lycronisxd/a-shift/basic design/rev1-centering-mechanism.excalidraw.md

---

excalidraw-plugin: parsed
tags: [excalidraw]

---
==⚠  Switch to EXCALIDRAW VIEW in the MORE OPTIONS menu of this document. ⚠== You can decompress Drawing data with the command palette: 'Decompress current Excalidraw file'. For more info check in plugin settings under 'Saving'

# Excalidraw Data

## Text Elements
## Embedded Files
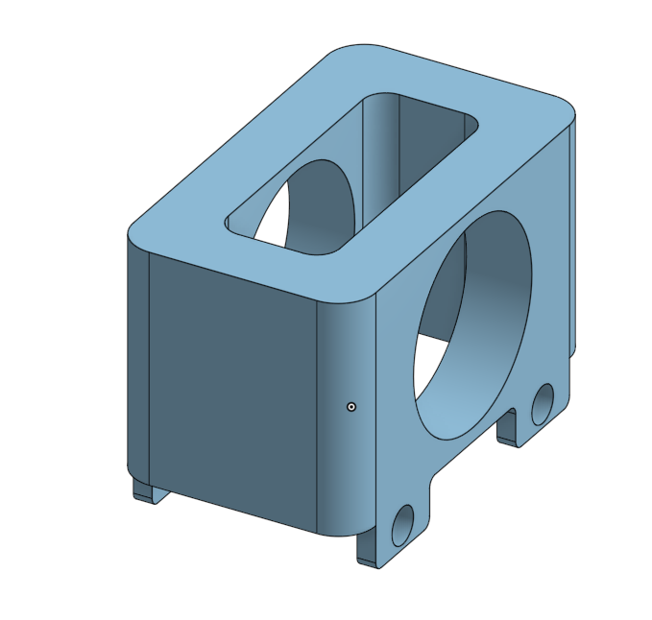
[picture p7: basic design/images/Pasted Image 20260602135400_534.png]
f8c7245b9aaf94fa687d6ef50f577c9f9da9b14b: 

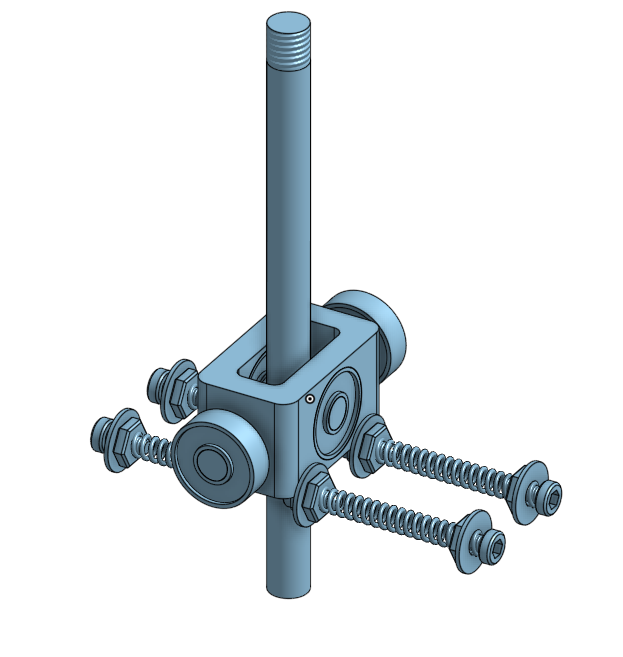
[picture p8: basic design/images/Pasted Image 20260602142242_120.png]
b308996baf1a3101664534b31633d5aba34f77ea: 

%%
## Drawing
```compressed-json
N4KAkARALgngDgUwgLgAQQQDwMYEMA2AlgCYBOuA7hADTgQBuCpAzoQPYB2KqATLZMzYBXUtiRoIACyhQ4zZAHoFAc0JRJQgEYA6bGwC2CgF7N6hbEcK4OCtptbErHALRY8RMpWdx8Q1TdIEfARcZgRmBShcZR5tHgBmbQAOGjoghH0EDihmbgBtcDBQMBKIEm4IAE0ANgA1AFE2TCMAcVSSyFhECsDsKI5lYPbSzG5neJ5q7QAWHh4ABgBOaqTF

6er56YB2flKYMYBGeaSD7S2eaemAVgPF+fj4k4PdyAoSdW4rpLjFra21niLeJXHgHA5JF5SBCEZTSbhgq5XbTVFHVf5JK5LNbVSHWQbiVDzSHMKCkNgAawQAGE2Pg2KQKgBiA4IFks4aQTS4bDk5RkoQcYg0ukMiSk6zMOC4QLZDkQABmhHw+AAyrAhhJBB45SSyZSAOrvSTcPiFASkikINUwDXoLXlSH82EccK5NDPM0QNhS7Bqfbu+ZEz184Rw

ACSxDdqDyAF1IfLyJkI9wOEJlZDCIKsBVcIs5fzBS7mFHih1oPACfEzQBfYkIBDEeHXbZbabxRaLSGMFjsLhoCamsvd1icABynDE8MRSXmNxnO09hGYABF0lAG9x5QQwpDNMJBfVgplslHU+nPUI4MRcOvG+6tjPpvckv9qosrpCiBxySm0/hP2wPIbmgW74GEhS1oUpaQOUEhCC0mD6pgMAwAAWnKXQEhAvT9PicqjGg4zVIkSwHCCQIrNUgKbJ

C/qoM4GynM2NyIiC8RLJCbzEB8/aJIsByXFc7EXNMtzLJCkjQrCUBTkib6BsCqyLBcVxtriAy2kGZa6pawr0kybKskgu7cryBZCrS+liuQHCStKWQyfGSqquqWH2o2xIWgaRomp5epWq5FTufmwjOq68KQt63J+vCgaQiGl4RlGsbxomCDJmgZ7/ouWYEeguAAIIhQKxBFiWZqdBW3BVh0kHafWd68LOSQPPMWyzl2TAjn2qDTO+nU9mOE4EoCGx

JC+QkZiua7AagoE7p6e4lYeGQOaef6Qpe163vCD6bPtPCrAkn6Zj+mUbZ6dJAY180IBBuzQWUjUQLZYYUC0UAABKVBhVUSDheJDJCeXjPEpwHA+AkgoGD7nLRYyItMyRrACiJHIxnE+e66xxFcixJDwraAgcCQExJUlwmgqnIhcCwE9D8R9ZM6l4WgWmlDplJ6aK6DMkZ7ImTyCWCtzFTirZUoyo5nqKsq1q2hAwV+ZahrccaaCDhzXkBTabm0g6

npOpIZURZ6UW+rAsXs5ACXhpG+RxjLaUZagWUZrlOYAELFYW4VoNBlXdP2NZ1rNAmExDEOAgN3XcNMZOesOvbjhwk5oMpSSXMC8QLmWS6rsEO0gduCC7vuxArceOS/ueZZbTeYd7U+T6MX1J3fjX2VlldlI3SX91QYuz2LAAssQI8AIoAPLLsuv1B+gAMacZnogzw1NbBsbWBpsdMHDinp0c4Wzsdo+PAgkbbAm2muvFjqDgskGz48c8ftdvB9lp

JMKU71+/Ilcc4dwEjsQJtcFmmllZc0sjzCAfNDJyi5ELcyotrISklg5OUssXK6yCvrDynpOYIFVjxXgUCdYKyVobUKxs/YP0ij6GKAZrYQFtklB2qVcBJkam7HKxBswSFwFSH2pU6EB3LAvGqJQ6ocwavCcEm9N73A9EOLqvYmwQkTmooaqcCRiWqF8R4H5FzTULrNW6ZdlpHjWp3TaV4G6NQho+e4dxlIdnbmdV2F1u6AV7pufu0iHpDwqNMckz

RiAAFVKgAGl55YSCEQOQK8yxrxRMjR4oIUS3DBpossR8qJbGRPMOYTd45sUxmrbghTiIokZoiC+WxwS5NKN/aS8IDHaHDrMfeb40RtmaZAQGBIWFENQbzQyAtFqmWFhZEUYsbJ2Sllg5y8s9banISQ9WZDCHa1WXg9Z1C/C0OLKbMs5smEPzisGfkdtkqOzLAmLh6UeHeNKJmfheUIC4Dno6cuJt/YVQkSNEOhC5FoBnMUjsGJc6lCTpwDRMdk7D

XhGDIEXwOzxCmgXBARc5ol0sQeaxJ5bEXnsbipx+12wCWuJ2S6p0SU+Ouv4sCd1AmDzzs9KA8xomoRHlSA4FAtgACllxXCFSqIVcBsDyjgJ7AA+nEioCTCBJPwmMBISJ2yTBztUZsZEDHw0IlRJGkwSZtj+BRdeFTSGIm0PEAxBT0aKXjuTH+Ml3QdK6Zk3prZHgQOGeQsZcCJnJNKEgsy5cg3i0WZgpyctAqanwTqbWmzfI7P8nsxNByyxG3+fQ

s2jDLbMPijc9haAUpOyeS7XhecPaCPqCIvN4jMImhBfVWa2wrjVDBG1FRsLtE9XXrfBgA6U5pwfmsRprZ+J9pgqYnF5j8WLXLpXGx5b7mlHruSpuLiJj3GHV+TxNbSg90XSyiSoQAAqWAoAABl6XFxZQPEoj1YLoAKnMXA9RFjMHmJgNgcrb3LgAEqoQQAABTlUKpIKpFUSGVaq4G6r5inGKX8Q6yx/jtWmIa+iVEkSgkAS1OmVEHjWq2cRM+XaM

SzC2IAsSrq2keqRF6npmH+n+u4CM7WQb4FGUQdMlBMD5noPsrKONODKFJo2ffYdRDM12mk4csKJz3QMOikWy5LC2H23XZw7hDK3l1vymGRtYjAUto1m22RYdfiEweHR2lqjBo9QeJirRLmx16ImG2USkxjF53nbiixy6rGrWJXp0l21G7OPbPa/Gn8T0Pq8bXE9viz0LS/lem996O6PvAmyl9wSJD4HfCqAAYvUFUl6CpXAAFakHqFPNguB4jAbY

CPfAcH0AIbCGqwi+9TjjQ7MRL41xAw4cPmMKipx2zTqHTcdY7myxcVIR0pIBiEt7pOJiGFkBWm/33ix2Y3SUTsb9Z6IZXHA3CYkHxyZZZw0zKjQsjB4mZYrITYp7NWt/Kpo1uQhTislM5poXm2dXpC10SONp0tunowbsgI8gz51UswWM18oVZnVOoGbX9Xg1mBBgt6nMAmjxViIvhf2S4lOOBeZNKTl8CQIf5xmn3c9oXCXherpFuuZKYuUqBKsY

EHjDOQFPezzLLTsuYDvcl26z6ijFfQPgIVQqrjgaSJIGACA4Dlf3nKqAo5mDRIABrLjzJCSzPXlQqr60hgbJNcZOK+DvQMeNcMMQWDMWYykDHFLxhTz0q2tm2vtV2iO8xRuZwGVCN17Tju0zY30i7ZYrtsxu3Mu7IaBPIMjbd9A0a3vSweZ93BWaDbaRTbJwHX3gc/cgLmuhEPzmaZhyW0MZaEf6eeWLsoGPcCxN+SVJtFn8c8EJ4rYnYJJjviEv

xWnJoZy0/pxrMGaINhtxMdi4LS7HsrqJTz7vUWHG7Vi2sFDCdu7JePeL9LkvS6ekkDLuXeW8VPsK0rjlFQrjKFN+V7ARYT2aYSQaYfQeIcrNMXAMMeIKAWkbrDAW3RDVeMYTeM+AcMGPdASOjCHfJR+ISe1caV+YEKicjT4TVB1SPaPF1J/Cmd1B+T1E7b1c7WPdPQkTPKycZfmUNTkQTfPLPQvV7MTEvUobBIHKhKvP7GvdNS0cQkHUoJvHHFvK

HK2DvRKeHCtB5Z2F5NHfvD5HMW9bHcqDoQOYFWqUORxC+dYe4N8RffsGiDzbqVfVALtSFXtJzN5ILDLR/ffMLKuO5OxaLRxHddsUSDbZbJLN/W/CACXZlKXfbF/XLTxBXT/V9Z6G0W9TQT6RYIVNreoJIGAZQKAEeIVMMK4eweIBA3rHgiAEGdsM4Gwm4feFqGlAST3btRYGYcaQ6beFDYBMgqmCgiPRpKPZ1WPA7ego7TpJg5PX1Vg5ea7GQ6BA

Q4Nbg3PCNEqF7UTJZCTOQhvRWavSpAHJYihNZSvBQsHZvdTC2aHK5MsHTAIytFHFLLuIzfQwREeIw7gPHBeCfcw0FMOCaB1NECHOFVzVPftTzZFd0Vw9YdYK1bfNnOInwsNA/bnR4vnIIs/QXK+cEUXVHV4u/JlfLFEhI5ga9WXJI5ExXNIioTQckFoEeXAegUgHgAqAqOAQgLYOAeUeUCgS9fAHwKopA+3FAwiJGR4USPqCaKPYiQ6dohIO1WUp

o0bCOAYlwoYx1UYsbcYughPaYpPM7FPeY1mdgk43jHPQWDYkWAvaAIQnYj7eNcvb7c480KQo47ZSQ2QuvCQi4o5cHa4i5dva5TvDQxHBUbQvvd5ARfKUcL4gFEwoFVtf49tSwi4J4S4UEgdaqCGFfaE3gA4e1YpHOOjLFJEkkglCuQ/DEzdfnYI8/QSY4fEl4gCYk9/eIqQRI+XAJMAGRWkiQCeKkCJZgIwT6UgKAVCVCegVSYDAqUgTATAFoSQc

DYUxJUUlJaqJGOje1MiTETOe4PbCAfJOYO1aGWcHcsEfqYPe+MPSgkY6g3U+PZjA007H1DjS7BYjPc020+7Gop7ITFYovYQ5ZJ0qTfYohf7T037b050+vV07CS4pQwMtvO40oB4jhJ43vAk92d4/KKeeM3HMfX4yfMIWaBYW4TEPGG4Ow3gX4PM3RE0WcISVSUSMssxB/Ss1dCLY/TE0/e8Bs1SO4Zs6I2Iisp/Lst/FI3soJb/CQOrT6ZgOVZwF

UEeSQckHgEeAqcYeULYT6dEH6K3fHRAtcmovKc4dAlYKUqibtSYYdY82bX4PzVsEEDEALUoEPcgu1O8p1HUxjQ7Rgw0t8iEwZT8s0r05Yzg1YhBK057W0oCh00vUCs4ghcK4haQ1KvY+CxQqMZQjTW42HUMmspHSM7CvhGMr5Fc4fX2HHH4swz/InMOJmHJbOGijDei8dBYR4E+NiFnLwjiznKs9EjC3i7dBs3VQs4S15IkvxMSrLcknLbsj/aS9

lN5Z6OjOVWoYDT2CgKeaYAqTQYDZwKkcDGAcrOVfQQo1cu3Uy2KQpdiCGTEASd3E4Oy6bE8i+ZqVSTeDOdU284YnymPPyyYgK18lgzjL81Ki0tYmKgCyK+K2NR0yTZK5Nd00hOTXZH0+QxvRCnK5C/KtQ25Ya0Qkqlssqz5XACeAi2q5M+qqfMOM7TYMidxRw9RDWIPZzJw/M8a98YbNihdfq3wrnfwomyALdAXJ8UIzeL4Sa3Q0S9s0kzs+aykx

agrZaorWS9ASoU3MMYDeoIwSoXAeYBAIVTAT2fQOVRYSofAeUeocrK65Ajc7Gb4RmCaUIiGN8Q8vA74Ag1sEmdqNxCHDywYry/67UwG2gp8hgxPUG408GsK6CiK2BX89Y2KwC+0hGxKpG/ZeCiC9KhO047OlKv0lTXGgtPK1QkM9QoqiMqtHQwkvQ8q3AYDKmoiuqtWmzRxFYOYC4eLVqzedqvRGcL4NGe4Pm3fDnQWwa4W3nWsrE/inEjEW4GW+

uuWkLOaik1/ZInsvs5XCACJRYDgU3RCLQBApePCB3Cdb4UETYZSe4LEPqSbPJVAujOIE7M7OYQBZSdU+o2YYiAmFSEEOjYdCYuOJ3LtFGIBNsGHNykK007jfyKG6KqZPPTYuK9O97TOzKout0lWPOnBykLB4qEu05UoVvfGyuwmme4q2uqMgfCJFuxM63KRduhqxxREJYC4FDQ8sE2KLMqEhi90AmTbW4NEMe7wzi6svvMW+swXOjdYCHQ9PvVe7

emS1aioCJJIS9CeGVckOrU+hAPoK7C+8ETozeW4WYAcdYK/PYQ4EmEidsYXbtTOHODwu+D0rtJGXVQ6WYDbTEFDCHEB/sQBABPzfdREOij8uBjgpOy05B602ZOG9BkQpHMvMCnOw4tG2vWC307G/0q4sum4iu+4uHau5HLC0m2tXCr5WoBhssJhki6ffGO4diG4CIyAHhwR7h0dfMwmIESYeOXqnfcRgario/aI6R7EiW/GSixLcXG/KamI+/ak1

I3e6VT2TQSQAqZcCeBAWoKAeIfQT6W9AAR2YFvWgzgH0cMYWIvuw20BQzcwEgxU3ljyPj+CRjJw21hiomam/s6N/oyQAcJhBCBtAdiHAb6kgbBndzjvgd0h/Nicez4NQbTu2IztENSeRpkw9PRozUxv2OypIcgDIaKbQpKZFprueOiOjPJoMsOWquMLqfx2YZkVYbjkzivmWFcZHRc2qkZgHsYs2EEiBEPNZ3YuRIkaGqoYgAmfnubgef3jaZiPm

dlqWdmulyVs3uWfbv7PQAiX0B4HqH1HWflFNxHgOuiWiQiU9nwGUHlCgFGEMoXmwgMdwiBjFN4FmCfgmEZhJlWD3PaM2GSFBHtUuBnCOBF2vI9OBDOGJh7raiBCcUfpaT1OxkSFWHjiT0aS7ThkicgW/JWOTphv4MSbRYwYxaSsLpRtwZxaybSewYQryaQoKaDNQptnJelbKerQWZpZzHQiqtERqtbuqgabIt2wuD9pouUj4c5oEd6nOF1VbA4kR

PFfVc5DROnp4tnr4ofh3QlvkYUZVZXrVflovU1apJJJpN3uOfoCgHJGcEqHAypCgGUH0AOCnkIGmGAzlSpGiU5PtvXJGHhH4m0C+AWEaQjbCP5amyNX/hnG7VEi1QWFEajdIWqXtWImuGYojnGlBefNYyNLmNheiYMmhridTtLYlmAt2PxfSdRq2VxZgvraIeOVLrORUOLQoa700OJpodKsqcbtwFqdKGtz+NptIsahssLPfBndZt4BWAFfBWOFG

JLLEYFtRL8LXS3dFrrMmcpQ2yOGXtbJmtPfEvPZVtZR1d3vJHK31FHAngnnJGiSfaEFqB4CnnJFN0ICMEwGAy4CdawjPvdcdoYO+HakxAQ9cRnU9tQMuDtQfAuDfEAVmAuHVMfg2yWBnBj3fnalmbjyYz/imAMSAWLNARUmI4LciqLfI9htgXhvLZScrYrwbdztrZOMIeH2IbUxbZQoKqropa7brpwsbs0GE9MJHZTI7vkSziMUJhop9cU4YJARw

OZsCyGfU/Xc0+4p4507nt3ecSlPjhoOvyiIWeUYno1Y3ovflqvY1ogCMA4Dqz/bgFqH0CubdZusImZzPiZlWAMSMQxDy/yXtTOHwxWHfBk7Bm/qmEBEBFy6ILmGKWTf21TYnViAaV3kaImEPLYLhcTtI6QaRZQZtNRao4Sorazua+re8ja4yto4bcJe6/Y/Ls4+KcKoG5JupYH2wDG6TODkm7ZYDG2F6enZov1UW/CJPj+AmpXf5olZGckf4+3dG

v2mbnajmCM8uhPakp3ru9gFIFQipFQjDBaCMCiXwGwFN1vTlXJAKnoHK2EQC56FdaMY9b9rtXXn6XGweFeqNUZnuafGS7RH6dHtQ62RB9h9+CjwR4WFS4joK9uHR8Acx/D2x4q8hoRbI6J/ia2LJ/Rca8p5dJa4yYY7raxeU1Y6JchxZ60wJu4/DMG9oaqdwAZ7+XM0YeZdHccQWGOC6uopZqp14FLIH7p3zKZjWBzjUll/Ho7KWiFq0525ld07l

cZrDeO8iKPTO+1730u4WskpUZWpgmehHmObYBJGwGA1UC2GiXqFvRUs9i2FvU9lQhqad/+hd5uY9ffAAXOEDHGjBDDZKsj4rhM+FHgfqFkUMb4JVkHQfg4x14+MQmL7jsbWMUekdamMajphDp7gTMPLrjxI7Z4s+YaZFiT0o4xoGuCoTFlW2xaZN2u9PFjgGR67kM2e/XTtpzx7YD4ai5kUfB30kRd9gOZEQEATDag0U/gLCMEs4QEh+smkETNbu

WVM6T1Rm1dWVvt1V5tRtg2wTXoyhM5r1d+ytffktV15qNNQy4egDyniAxArgqEfUJUCuC1Bj4HACgBEniANtrcLra5ufTd5ohNUJ8KBrfWwy+96IM+b4IGGpQx5oUv1K+r8H+C+4L4YIR8gn13LIhUQ6ITEB2HWBx1EghZOjK3FuAYgZ0eXUZJn0J5EDieCTOrkkxAqF84Kxfejmmjp7ZMsajbLrvmmZ6FNWeZLdnqwL44VM3ijdeULz3qYC86aj

UbVOvC7RkQp2pBEfs4Reo4dhB0/YZgoMV7acl+e3ClM3BhxURY8ijJXtNUWG6CtWl7FZndxgDLh6gl6eoBEiEAUAGI74aYK0HoAHB8AnsUcIYTf6LwP+HgkLhDBB6UUBw6IReoG2+B9RskobNqJ/W/p8RqUQkJHqJBGx4cH4tqeSPcHRTKRmwSrNgpkJziuFJB0zfIfgK4LFDeCpQ3PmQOSYUCmuRfanmlVp750OuFfBga0NbZ9dKGKwxvrsIbrk

1lAAwzvkMIk7wgFgNwZYI8CVYdMH4hZGBjy1nbjoBB68F8C+EGZyCdBm3eftt3DLKD1hjNQMFsM0FpY2yyoxWldws63cjB6AcDGGHKxJBlAtQUgEYFgD6gJ4QgaYLUG5C3pwMBUR1p6FcFBdPuiI5SHEGIjCR+ILlIHgjCEjIgWmjNV3IzGHQwCBIMPQPIgLjYZIER6A2mMcCwGMw/cGQzpNiJyF4iwQBQnjEUP4zFsUWpA4vJUPpGpVIKjHAhnQ

M66V8mepDDjrXy45hke83bXQr20ETGgB23AplrwL5HT4yItwRpJhjF4kxh04gnpihl8wojFRq7eQRp1VFH5F+GovdpsPlJ0pTuqrfUTvzJJGj9BqtQwUfwqDLhLArJFrE4NHCYBnAwGLAAVGtrHN6g0wd7q72+G6pEgcwNsLOFy7bB8YnuE+J0TYhohzgkcaPml2+AZcX42XGGFHgRGiQiugCaiCAgzHgI82lYXMdkLnG5C8YhYgkVFVLE1cS25Q

stuSLEINiTitYsvlQIZH5MmRvXOvh2Mwpdj66PY/KIQB5FDjxOxOdeFGL+CSixRD4WPDOLnYUQRsk7BYRtwgBz8p6C/dUcvxUEbDtR24k7pvz3HaCDxhovflvQMGqMzxYoIwDwFHAtBsAygS9EKiECLBagmAKeIsH0BGBwM5WUgG93eHGVrq/WBgmkmD4gic44ICGMjyPIIwQO8jV8LRghhrB1S6HWpFhwaRNIERUxAjkFRNK2gsROE3EXkIImVc

YmhA4kTnzQbkSqxVEmsXgwOJ4sGhBLHGlXxJbtD22nQtkWwO7ED49G/Y9voOLbqsthh8iQEIzCjzzCOacnESYtyBBLB/Gi4uXmu1kkbsFJgRHdpqNEiqTthR7YzvsMPG6TtWp4p6BUDlTRJdmmACgHACMD0BhycgEeBEmckIBUI5WLHO5OqJeSyIL4GYJHzmAOZm4nuPGEjE/qqRCyGIYpKHxWw3lNSVBMYolJBrMFY6mE6qNhJxFwisp+8QidV2

z4UcyJefcgZRMql0ca2NA+ocx0bGMiWxNfYMswNZGL92RPQ9HM3x/BtSh2PAzqRYU3JgwxsV5QaYPyOiLd3aL1EUWp3l5LCpWKwjcQdy3HLTdxx7fcRd3Wl6C9JJ4gydtIkDygCoMAegDwEkD1A6sgwCgAVBaC1AjAygSoNtQnh9ivRRle6cYxYozA/gqKJSGiCh4wd6IeMRIOsBnRgg6kLRdUpRnfArBVIwLccdy0CZR0XyEMojlDP7Awz8x8Mo

sQgxLEPYShBU0nmSOKmYyah2M0vrQKTn0CGJhMtoW2JJn19OxQ3MmjmC6w0zGWIncfHwI1hHYZOq3SErHHTgnwOZ//diJcA0HSTeZK4+SWqLmkq8VJUeNSRvyUbb8JZOkqWZtNllvoIAl6EePb0QhUhRwpAaoKbiMCjh9A5We9LgC+DUzjZzrU2W70xCOyyIwIOIfI2KQfTfgnSdeG+EzhjjrgseGAetk2zhE94u2MGdHSDnvk08oVdKbDLwn4ic

pBPYicjNq4iY0ZFEygVT2oGpzcZ5fUHE2zY5ZzmRzE0pk1PYkD43J9LQdqXPG5WZhxZFcaNC02BdNeW6cTOBzOIjnAlsKHWQUuINFyTFBFLQWar2Fm6i9hMk5/OZ2PGWctpE8mJKQGUD5EWg0wCJFPFqCjg6sdWDgNOUvTZF9QAHX0fGJNRLtLgH9DNmfMKR3ASYPzMpJHF+rAz7yoM+Pv5TfmzEP5pQTEWHNwkFiEZ/8ggUSNknECyhIChOTR3T

mQK6hdIkqcXSbEtCEFTE9scgu6Fc9m+/nDBQOLLnEVcFjULtDm0MTcsxRt9DmQQpfDdpJRYrSacuJVGdy1xiktYZuKWksLFm4sjsuwqPHSyuF4856PgGAyVBLg5WeUAgB4A3hlwhAPSmwGfyjgoAbQO6SKXkU+Mfu7UC1McHOBkY7ZzgPGJ0RRBD1/+VEIENAKBkh0tSD5V+YHJMXBUvkX8ixZlPwnWKM+hbRFrHJRlOLKxLivGdRLKnyZPFuTZo

blWznEyOhLAxqYEvYHN82A3E+mQCTYaGIfe/wKdjTmmH5lIpCIJityzSUz8FadC5YeuKUkLTmFO4jSWLK0nDySlG0o4VZzu4TxGk0wZgF2miSEACol6UgLek+jEBagcqSoFsBVApBulJlB6VSljb9N8YSErVGfO9qBi+oKwChXNzD6eVw8iygxV/FR5JSZihHUxbAzSmbK4Z2yyOfCz2V5T7FJIwqaAsTmnLSptI/BgXQgX0Tm2jEpgfctJkN8UF

w3cmpcxLnfFh2OC3iWHDGlCi0UU7B8BzPfCthfxjSHmVNIhX8yoVuSoWfkrhWDyilCtZFaPNRXcLOUlQWoAgBaAwAVQW4XzCPGXDzA3RVwZwKOB4ByLaVXaGYE0h952Yfqoyz6UUjlFtgu0GwNZTAL+p8rfKhi4GsYpFVrLzFWQn+VYulX49bFgCg5cArQRKqTlMC/OjRLTkqqvFBM4lq2LuX1SHlZMw1YXMETHM3lNNFht1LQB/ABl4woSdmXTi

AIJeIIXpBsFFZ9V25mS+hdK0YW9ydRvqjked2KUSUylJowyXaEwCVBKgSlIVBQEwA8AYAxAcDEIDv6VAJ4LQT6Cau3nxIeltKiGHEEEnh594vfSUcAO/7tggQGKHJD4N0ULKQZlagVZHSFWBUwaIc1AN/PDlSrEZ+y/KYcs7XOLEa1Y3tecoxquKtV8C4dUTLbasIO2jyqls8sboMhTVCZDqXOq6n8i0AKwAmMkp+Uj9uAIrEad0gPYTSwVkrTdp

6vml5K+5Is+FatLYVXqx5h/OWegHqDyhysKoX9YQAngcAtmbAKkLgGOb6BpgE8Jkp9DTXGNem9zO4NL27SbxiuZ8mHjvAjaX5J0yG3lahvDroaE+4M1ZalKwkNr8Nf83ZVVyI3yq45FY6juRsuXlSU57i9VRRquXeKbliC/xRzyeXNTm+uQTjYRTpk8aGZMJdiAHSXoib040cf5XOwhg2EHg+811Rkumlbdsl3c8WlqMU0FKL1AatTcGoqUVBqg8

oJILUCpDzA6svnCeMQDEWLAWg+KqkFsEqAhLuN8GYDXZri5AIOwFFBDrhzzXf90Y/wZLkYm7Q+bvKYddfqgMC01qUpOYsLZYojmEa5V/5UiUcvi2YNEtrXHGR4po2wLrleNUlmOv1X5ym+jdckVwPanhL3lqZJsBsC+Arcp2NW1maPznY+DmmtqtuW6pmldyT8PcrraevUl+rEVl6jhdeuOGmjFY/ESQPgEcGSBNApuLYAYHwCjh9QzAaYBcNkXU

rPJdm+4EkP+AqQSkh0aDSFLC5UVxls4P/oeTLV6KAal2/LkYpWW1qQt0M+7Vsoi351EGba4jR2sEJFTu1dE1Vd9tS2JbGePi+jbcsY3oUuhrGvLY3SECzqLV86vjX/EvxogWoU7HZbXKRRzs5gywMEPvF3Xrd91rW1cUoOhUKaCdA889UPJJ2lL1N6tCnUKkWCSBMASQYgBQCuD4BiAU8PQPMHAzMBPoR1VCEVHck+iHpJa+5qpCxAID9owuo1Es

DtQQC8YEHXeHlxgER83E8PGcIjzj4BbDs/ojHrMCx5crP5ppPDQ9oI02LCRWumLSRt11dqEtv2yjWqqS31il96WoddXwt0si85rEguQJ3JqejYFDLM1cVv56WrGoR0DlW/BEHiRat46E+AkBRD4TmttC7He1tx2dbFp3Ws9RTMKXE6+tpO+PV/gp0qh4gzAT2PqCFTgYJ4xYerDwGYDP5f8o4RYBxsA1Kp1tbvfeJ0XxgbZM4BiJ8LmqfqEQ8YRX

C4PxGnYFIF83K4Or5v0VoaU2GGoLUrru15iJ96u9VZrpjna7XtpG45YvoHXqq+10Cg3YOsznm6stucliVoVy2oLm+RgB3QTkiXtJr5EMZymLzvqLd/gftKiMdEx0tb3VsmnJfJu9UPhAJv+kSjHsANx6BtGmiebUH1DAZcASQeUMuEwAjwjA0SZwM4FqDYB8AxzLYPgAiQl70Da2mlcY0LKeNnN4IB4G+A177bna/EbNoyqYpzL3GMui7fEIV3JT

sNo+8VarslUcHV91IaOX+QcWkj+DH29fcUeEM/bBDTQjLQDrqlMaGpE62Q0arpKBhFDYnJ3dPifD+6hIGE5HbFFUhkLGV1hVudQvSVv62tYer1UwrairAlNROtaSPMOE3dydt6iAJ7EvSEBUIESMoqQBHgtLnA9QKkCqHJAuBb0bAOlqtptzhG3eSwQpOalQlXy1lMGwpIdHfhey/Gcu6XShvoP+bGD12xXbdpw3j61d2UyLblLsUvbyxqMsjVUf

qNfaoFdRntRvvENb7JDeq3fTIZt1yHyqmgFDN0YrkPxytrlUXlVsuR7bkdzhdhtsHDhKtQVqxww7NM/0yMVJZh5Y9Hv9VnsbDGxtFRTtP5GBogU8eUJNsICYBFg9AY5hQBHjjh5Q9AbkVzodpAcAwVEXMYzCl6e8kjZ8xIBMGNQCC2wrmmgxqQBOy6sj1a0E7kbMUbKCjv8qExrtKMp0dddpPXQIfRM1GqNFU+o6bsy1+KpDAS/Ex0YkBEnU1hW6

mo7t43E43wTTXVAaipOHbFuxXIxKkr3VY7ZjDC8PaYaWM9arDfJlFQKZDUVBagLQZcKbn1AcBFgYYDrJkHmC1B7gVIXkggCNl3GPJqpyAHlCOAnkOwoIb6sorARnykYdjWcLqhGzXwztodJZVWv1I5HIZeR0LWwchOe7ODzpssSQIROVGKeaWr0yvouXVG/TTRnOTiekO8dgzU69AEScqIRnzVShi/XHERBu6o8q64hZckmNe6dEHVEmEsDhIszP

CQejM6HqzPzHOTuZiw1v15Nmd+TOvQbRICpB05FgqEeUNEmYBJBZc8QckBQGIAmCJ4qERYG8NCP3HudX/TOMkFnChNb5uqV5iFKRjKQMOrYXpDm0nMVqgTV27I8KrBMLmVdS5wo46dXOyrYT5RxVYie3OfaS+KW4ozucPOMDAdLR8dQavaMXnZJmwEk8oexh2N4dOcDQ+2AdUPBoUxEKTSyff1zGTDCxrk3mcgvr1CzMFuw89HAxgGeAzgCgPwvw

AFR9AE8bAHKmUAUh8AulBQyqcA6dnRNmIH3EtlJi+ZhNxB+2UCGSDNzyIhYgKcxb81y7/ZmGmOsHK4uhz7TTap7YJYVXxytzBfHcyiYkv7nfT1U5sRIYDMnmgz5TIJYSdnCqX7zHqFxkKxGXDGAwOl+/XoiWxhDbZUx6TQrw9XGG8di08y+Bc0mrHA16xmywnq2MjwYABweUNMCbMkAYAwGA4OSCuDMB5QlIEeNels1f8G9GSDxu+A4atg1FXRCY

PVvOCiCpd8yugxaeWVzmMrtpsfRKodMrnijXBso/lbi3k8irYl2occREOaq/tjRmS80at0sa6rbGz5ESeqBNXejYcZnDnEOi5lEzxSPLmJJlGjjr4D4Jk+mYMPGXgLpl0C+YcJ08mADBZoNUWdgvoBJA+FqeD50+hyo6s0wGAEpVIB1ZFgl6eIPUE0DOBDrIXF8EjCWBGJuzibBuftrFsASn9KGBYEFP+OPXMjz1jizabFWLmMpvFr64UIEsz64T

G5t7QDYpFVCcmu5o3ZJZN0VWzdWJ6q0DtxNnnYbtu+G21CRvRnG4IIDxuREnGVbaTAKm+g8yS6v7tJrJnHSNS/0IhWoFl6m1BessH85rmmiAKCHKzHMrgMAZwKhE9iSB9rhstCzwGwDlZmAnOwi+2cCu1FuALUMLpMsziNJQQTss+UiBODC8bCSxgGe5Qevnbpzfeq0y9dFXrL3r2Vx7VPqIncHZ9rp+rmAspHVDqRtR43QeZtv+ndVDt089Q3PM

H7OjVK0JZDuwV3nkbknR4DZW3KTip+/tudsJERgv79DMxoC0euzNMLD57EGO1Nf6103bLFQFoHAGObRJPYlQT6Mc3z2aBL0nsIQJmGXDlZMA8QI/VDowMPGRbKGUDidmLXjZ8MQ5s4DDhnxwbBBSVwEylcFXMHOLb1/Izxc+vNqSj+tse4bccV8H3tol6oyVZBtonRDGJ7Vb4uXtyXgde+0Ha7ctzb3aZdxnox7ZGHhMnGrFRM2oY5mqRMQ6wQBi

HeHlh2P9Edjk4zUfssIdhf+3rTTZmsJ2QDWxwgFSBHi3oEAwGaoPUCgDlZTc8wegOSGIDEBfQVwG9sLbVOoAXm9zKAbqgzEbYqFNjEg8sBmDWU/gWXdeJFY7vpHzTqtmc/h3VvzmiHWtxtcPehMALKHQlgq7Q8Bv0PxLjD+e+VbgU1SR1lu5jW0fXu9DXb3sG82fr3tCP2kxwCLsuw6viit8Z9h/c3qw6gg5Hs/Em3fZAsqP/g1Bymxo/zNx3abs

13R0ndctCBuIy4aJNMGctCojAqENpVsFIBbAKAPAGzaXs+HBdnHz+zpPxAQ4/DHgbRPNU9IEEQcnwxMdu241IQxsgEZqdiP8DBgPggpqVtsMjEzbdJs2wfO7SCJWCp8xz8RxJ62uSd/XNzaT028VcydQVsnnp6SzqtkvQ2inztgk67btrlO7jLLUrVHTIibB/+k4u/U070RR5IYO5dp+Cs6cCz77Gw4EBw2fuqagDthxOxPKWum9okH0U2iPFqCX

pwM8oA4HAEkCjhL0PAfy6XbL23MEHGIcaJm0Zg+8699s0SJ0gmyiDwQVeyUXGLgGJiiY/EUmMA1R5pih99MTqjgO+d7OWo/3f53WPIdRbntKT/6/n3BdA3ktWTq2wvdyeVW7b7DhFwpeKeUyGrXSvh1gr564bSTe8F6uDw0NDGPzKOmUYTHOCI92r/5pUaHfJdybRrEomlxNYRUv36Xb9xl89GcDzAm6WwFPeYHAzAYhUJMK4EIiMC1AwI74z/iF

0cxxAWoftaiOHiAlfBG9CHH6S+DRtQSn4mXV+C+Hgl5d/ZSEn/qhNahgJJR9ayYDthc3XBxqh5PW1a7yuxbQXJtjGcichcWupLi9o86Oo4eO217SLkM5efmDrP/Xp+9F6ScCktFXpcStdS45l4EvK7/TKGCPoTc0Kk3mZrp2TajELvuTAzyywcOu4jPdWVQWoPa3JAft9AFAIQKsDYDjhcAKeg4BElf4ivNnvogm7jCfCLHsMP09onF2IyLHlgYC

P5YDOjYw9O90fbvbH2eeCqB9yfIfanw/ea2Vds7siPO48YY3AX0+4F2u+Nt2vN3nphh1C+dc5P/tkN48yvdqtsTT3yl0zGi5gfn797KKYCXPj9uRvuAz+jmZvDBhHYwQpLmTWyaUd6dRIUjhThm5U3B7proHnR+B/iAwB5Q+AKkGGE9jKAhUn0fUFsBAyjghULAPWmU9Lu7yG3fUXZ1+MBAJZlIAQhiEG1Fv/82oJ8S5xABgExTMO9SQBglMicBy

+7da0Knj0tcwmDbNr9d0J/AVUi3FTrsqzC73dSeD3nrkHRyI4nKXbpl7rjcp8qeYujskAjYAmfqfczur1UXvkd0D2Jv5Hybka5Hddz2qrPWvYD5LO0f6T37EgWzosFNyLBjmMSIVIzc9hGAqQ5IegJ9CTXxAS7bZhMA1HIBUBbmfjnJDOCzHPn2aPjwIViDPg9IW5OAhEhR9IRheq7Gnh2XD0PL+zwxwfHwYGPGEdQcNBXn6y6d4Pz6RL6Trd8Db

E/VfmHDRzfbVOk+HvV7lLE90paJND42vf+53YlzbB3AN1VJ9IYN+xji2anQIIz0Nc3bjNKXjNESYZ1m9aDVjcANgJmDXEVQCgJhMANbBKDzAKoiOMAPz5MJC+wApwGN8AjoyP6Hm2wUXy8HF8VQwAzgGX4E5BLjD8DUQlX2AHTZvSuq5WlCa2GV98+1fGvsDQ+G1+iOPae2EoCxkLH/0mZi2Qsub5MIS+OgzgcFtOCYoKKsbUUtX1MEeA81pS40b

Np2g98dAvfJQH36Bz99ow4Sgf5HiUGqReCQE2wbHu7iuDR+Sgsf9X779dxJ+PHs+VP9L/mBxAQEuqJbN2aEZ5/VfAv8YLFcn7G+lgY2WdCUCdwWpBRRGeUfGYb8F/m/LUVvz2/b/Xz9fZEO1NS/WBvgZHFjJIIP8t9O/mir03cpILaZd/CkqwY4PKKOC/io8S/pvyH/9Z9QuqJ8btEcBgYlBvclwYPlfsFEGIj/JhBiHalP9C5LZl/iHwL8VKBhg

nE2XIWwJn/b33T9WwF8AYtbgVf31914BPw5YvBYbFNRc/EwjF8h/b4DWBvZbtE2BF2QgmgDOiLVFuBRiXITvdgAuPzQDmwU1CwCs/SzwF8HgKv2b0UMPuTwkSA9XyOAq/WIzv9oWQEHL8bnE4CeA5gMSBYpmAjX1OBHqZnA6IvjchX18c4SvV+BpOB513I6MIQLBBQOBW3XxE+ZJS0s1feohSU8YKPGWA5gYPiUCRA1QMGwM4PTwd8wAL1kjgoGF

6j/9VIJQNiALUbAyiFfUBYFcYSgTbUJgvA5SCXVTXBwLOBtDWMyXUb4OpxMIcYd3AeovZTLj6h/ApwKCD3mPdHcDLAz42bcnqItXnwkAjoBQDLfASEr0RiEfw6J5RfX3jhQOTAOaJJdJ8A2xYgwII7BggxIOKDWVI4HKChlSoOqBqgvZ1qCEgtwOKDOiX7zRh/vKISUDK/V6VDZa/SFHL8fvUP36C+mQYOQCVfVAJ+4MA/f2wDqAsIN6CpgliBmC

/gIQNAC34CAJNdb4DwPWD/WTYImBZgrIPmDl/TpGd81/JP2fcTCG4GuCvZQILHM7gNoLmCLfJv018bfT53BAnZP4H19Hg530/o3vDsEP8Pgz3zV8pfIEOaIQQlED6g3g5gMN9DnXbCEgUQbNkBD0eSdH0CcCc8l1RmAk/30DZwO4G1FGVa/zAAQQO1GxCCkG4DxDpgZgNYDXpItWf0c4Q5038KQrEIAkaQq/1DYGQsW3owjtSUkYty/SkMlocQ2k

LRD6QiEJj81ff+G7QWmfDCEh5wCmweDEgEH0ZgwfTAMyCSgbIJ/9K/O/whQ/WbYHhDAQtUNusNQxrS1DmA3/yxtRzKBmwMmyNX2B9zQpbBIIr/a0KRBpwKVy3h0bPr1VDkQF0M1D3Q6UPz81fQECpDu6UjDBhOGBCSdCzQ+zFdDwfbULABdQkwlPg0QSAVaJvpGbwF9nQhMKDDZwJEO/FJgRmlAQ+oNqEOCKQ+MNB9LQ4MIuDPgtMK+kXEV+HjM5

GSsLzCawt0MLCQwxvzTCkQSGHwMycCARrkOgDsItCuw5MNTCOgHgL+Cu6TAixBTQgMPzDaw7sKyCzQcMjgBAgYsBEBwgCllYB9AKAnXBwMLcOYAdw7gFJAhAcpWW90AG2mwAtcI+l/txFaNTVxNAKeE+gqQUgBnV3Jc7wbBLvLyTMMz4WHh+lIUUnE9wr/WbEfNCYKi3JxVXWTBjYG1fQK+BAVRKUpCKwomHMYSQyn0yt46fixXdivEF0E90Zcrx

ntKvZH2o0JPCGzhcobQpy9dcfDe1DME1AimiJndbNnBAS1UUUfcxHF906YXNQmwAtibH9z/1j1Fn34gTgWl2D0ufHn2SgGwjoCl8RfHsIL8pfK31l80MQBCwItTBkOt8vmfVFnC9fS3yL9VDTjzow8YQmGtCE/Yv0WxS/Of3194/ViEMjAEYyJ8CkQlvzmIkvMP0791fZENciTfW6ylD6wyENzDrg1f2Zw7g9kLGUgoruhCi3fZhhTDLggX0JDBK

c/wvJv/F/wSjM4XAwVEvqScLiiTCMgKWDKA84FGNLfPKN/plgqgMX8FI2UOMCIBQ6EIxYlCwOECVAmqIJhdyRegOA+QvIKOACg3IXRCbI3IL/EBIOLBPhfWTYAZDt/O4AxBEeNxHhI+oorhJhpmc8iOBezPyJ1CcojoFBBY2Wf3OB8DeUPtQbI2/3WBtov3Ef9somSJv8pgU1yzEbgGbGBZ9oz0LGxDor4Cv0yIJENOA1gO70Ck/gLxn7p9IvAOn

Y3gq2WhQkQwpGJDGkObETZwGGyP9595JnHCJ58fGGYDwg2cCepe+fQKD8m/KwMxUckb8wDwVo2KLOiqwpcNjN90WYHGEbIkoPB9mg0W2OB3g/yJlD4o2ICcYRGB4CBB+kIqKb8M1UnEARkuWZXhDmA8ymvlXCbvTv9Vg73w1MmYndQyRX4Ho3xiAo3KJIh/nLdURh9AmyLfB7mRLxOAJgFqPIhmAmK0OhBNOzF8YRIGyLQIvBZuS8FvZEEAZCg2M

wxMj2Ga+j/NvfDEBpg2oWpE1ih0dqMqiBfBEHuZ5owBAeZMCJIOcB/RBgMPtZAn3jBgGQmAKf1rrY0KQlc2Jv3xgZgN3GyFCyN2gZD/eAKV4CCbB4HZU+o3nRVJVgfnR38CYPkKRhA+GIxJ8c4AZDj8lo0AULII2A2P50GQtMRoxRBO4Tagwon2IVtezBDkuBZlBkLRBk4wJ3GgTgy7VriNo853lDFbBdxlipwrfxD8hIeuzSFY+WMK+DJgUDnDg

7hIskWM8Y+eOl9nYwQTrt7qb8y7jT4F2l3RSIFES2AGQtYFfpEOfckAQvBWZlrjM43gIUQR/F2lOi5Y9aN50TGb2338nmM+M6JepR6jnFxoJ/y9iTCNwNA5+dLtGEg4jIOMkFkgM/26R2IFEDphrQ0DUS4nVHF0ldpaHIOuBkQZt0yQcXXmOtDFSGpF6ljTH5gaiBIK+lD8CkZDjfBwQChOeN2oLqKaJ8YC6xyCQraITu9TXFuW2CoE9aLBglSLV

EUhuqCxj6i+E96OfBRglsGtDaAvIQhRm5fzGCpa41CN8jQQFGAmxaY1aIJiNUGGUQiTgbQxkTYgNCO6RdErAKUSWMbERMTkI3hIsTtEjCL0TRfdcMhBNw10B3Dq6fcMPCIME8LPC0AC8KvDc3CoEwBmAckHwBSADgEkVMAM1lIAhAU3AnhRwT2H88R4XhzO9AgX8MoAHpTuJpgHnQRIuAYuAbBUhQOKFEgFEQYmFgicWEiFtCPGfT3V4dXSOjViY

YE4EQTqXUhUh9crfCIE8aHDd2IjzbUTx3drbV11tsMferxojGvP/Wa8iTT4kK1mI4nBGxpmJiypNJoKnxcJcDATR49P3aY2/db7ISOZ9RILDG8c5mUWWs8ppSSO24CYuSKUDrfIXGdRL7GuMF8hAgyMURsDf3V8w+o+5NUiFfSIxviREuP2RCdscEQw5BNZ5OUjBlH2XUilfQFPV8Eos/3ADgQWoP2jzI+yMElS4uFOPg+dPYPkYDg1FLsjRIBEA

xS54taNrjhg6vw4DPNdZKb8DIolKMiwOIwKajhIbWOHpDPfSLRT6UhyMZSsU/qIFD3wIUOWB2Yl/zpSBjElKUDNULMTkY6LFqBMiCUr0LFS6MTFLpjQwr4LmjiYIxFRiUo731FTiUpVNJSCYjX3GianKaK4CA2HIJ+ToU8ig0jeUzomaJ/gUc0Ek+iLuMtT5fGFIBSVU3sO99bgTpA5UyfMCUeo6fKEKUC7Uv1MdS6MZ1Mn97kkUTGwnkkNN9SXw

f1KdTskaAM5TFU8JlMjeU41Mmi3As1MdCaAlyOiEiYaMIfAlA9VP4hNUlqDJ9AQiKJd91/RDiUD+QqdAFTdfAg319QA6cHej4SR83aCJ2cEBCF2wWwllCKUvqW1EF/HVCGC2A0YIMs76GlJMJu/fnSJTDQwdMWAdgnFPAC8UqANlDJUvcl90iMX4FWAhAhFI/9uqFFNlDjUuiyJTolR4CEDgU7F23JJlfWOgD9Qw6N1RAGX1gNSf42uOjTZUzOCe

ToAupJLCGkwsWiFmAqXxgCvQx6IQCUlTSNl8Y0v9Kkdnkw6GuCfGWGFn9nGb+PpjoEtFPeSWEgAWg4f/P6MjCQEZASBAzIuyNwznZL5K0DK/DML9YwQluTQxnIkfxBSH0ruhpM0wt6PjgiXF2iUgwY5jL0t70tEPYznk6GObD8DR6JaYBMlENBTH0jjOnCQYlpx5pNgJonXhpM1jOEzwUqQImVdyN4P0Cy/fRNlisM6cJb8NMsFKfS1fJ8HSRyIc

iy7o94slIN9TMoTPMz5MjwK3IvAoBBjcCbQzP3i701EJcznkpGJBAghKMPaT1M5zLkzAsxoNnBOGHvmFEfMhzL8zZMkTJ6DYrJSFdisA1IXsyCYpLLYytMp0M5Dm3ZJU4Z+IbLK/THMljIiyUsuMKXDOwpMPCz/MyLMBCYeIXXl8z/DDjKzjMkoFyzNMizNzDCkCLjd9EvOixijfMpzMazqs+KMr8+5YEBBANUFYBei4UnrICz9fbtDtRznT+iy5

uiCqM9SC/ZbKazg/RmIClhROLHNROs1VOwyKMkEjwzBo8v0ow/uSI3t8V4zDIuz1onDOuyqMgjJMJPUJdkn40YHbVgyLUeDKw5b5VbJYxfs5yi4Su0QHMKTHkxDNWypga4DHEkI4EAjTP0rrMF8EcmYCFElUiUTRy7kuDN/SQcghPijEcnHJRzuY4pAJygconP/Tg/MnORzNYynLniPEz0C8TtwrcL3DCAA8PwAG4Y8O8TAgc8MSTQk0Zwnl0oIV

GIAoDSQDDBoMUJFYAJ4GJCpB6AS9Ggdd7CMgu9ckiI0DB/HItQmj7MUIMgAj4P1kRyZg2kPwUMQdUkxjpOGbBpjYzBETvji1UnCGUuo+4LY8IaJ0wodfrPpLh9Cre1wyckfEZJddJPKiMx8GvLhya8McIkzjIFkhZmd0TsNYEuAUMGihRBkzYiCSMZwEFSJsb7LJXWhdCYSLCIA8JVnUdLDebwgArk3n3KzbkuFKl9vguXzUjrU2FN2yLUwnLhyv

Zcv11SGU5VIMTysyFNhzY06jGFTRw2tNuDoo6nL7yEMtvP18So5zT/EhGVdN5Sf01vJoxJ/RwP50mKESRt91gMfIeT+8yfPPTkYXf0hhNgdiHBCm8r4MXzd85fLDDAMuHS/EwQJpLAzoA74AAEvjUW0mUi1R/K0D+w9+KnEBAtEBhyd8hDNBzLM2IGsDsYnvk94AC4HLpyBfCmK1DYswMHizyM6cEoylolc0d9aLCLlZCJop4EzhpM4PgzCwEDEC

+yOgNbL6lgnWCW2z8ChdnagiCwY1WzCkIBHlF/Y/1hvS4Ulfy/9YeIei6sBfRpFKD7UH8VJ9nZZgI4Ke0LgvPIkg02O3JznFzT2gPU7vIxzRCyWx6J58KfMr9UhV+CeZ3me4BEKIosQozgJCqfIlIfGKhNw8hIXQv91OCgwtUK1fDbGRgh3LPwPSlgCwoStlC7gqSDVgbHOYhXKR83OACQt/zuET05FJkETCEOMbiPaNOOZx/CqYMRTLZcZQsC9Y

/BXXgzgkSX5j1095g6IoYckIdyMEnogVFjgd3zhSSoigLhJMVfXxyLdDLLnyDCis/PnSR06dM4ChGcoq+lciqopdzRshzMZDKUsYNqiX4sAESLiMJeIPSdshQteyu/eopr8Z03ovKLK/R/SO567BWwhgGQ6qJZS6owTXL9PC5iFvlWIHNnRyxi6XxWLikVlPWKp8i6O4TCFObAzzli5lKOK1i7xiML1sw6FML3cDooJiF0tETiEB0rlinzTgWGGK

R+Jf+neio4gII+L+0h5m+K1fF+jmx+jUSO7p2wYEp78l0r4qHTeCkQKoSRIODX90OogaMFDdfWjAYLY2bhOhRjgFtJbjp/SFkEpSYdgNWz02ZYCxAlgVED74yS3ON+BKSkUVDZVs6bNIwRGH8QNNB45EHmjfpPcnJwAXB4LC4OWZogMQZ8LfLhTQNEuLmyOGAEGeTOY1rJ5jYjF8FviE0h1JzZp0ZYD6KxwxMKtC4Ug6Pv9jo0c3JDRQ6kOBYr/P

GCwTNo9EO8YskWI0BDwYZojRQ1DGjGhzjSm/LtD9PNEHRi1gtLL+8tg+QqMz9ii4CbdyLXD048P6SsMmCTgpmhSLQy/eIjKVCxPJQwUJIdBdKng4XBuBAnCzw9DYA70L/9CkzEKpCuQ60uBVrQi6IEKCbaTjCJh+XMOrDxw+rONLn88OB6RhlX4Dcxmsqv2hQ1SwgmTKHM8MPwD2GUBEAYkgjtyeckJXxmlKEsnLNoz34WZWFxX4AEOD9ZsDbPRB

d/QTVeifuD6NbAvopCUrD7sukrBC9Sv+kUCls4sPoD0YHRItz6c7HPMZikO51+AkQpsPbAWwyTO1SSgVpI1jCyWqPX83ylQI/KJMs2O/KwAPgvgTdDLOG20wQJEO/zZwocPuc+i1sGuDsQWbN+AzsV4vKzpA4kO+jRBS4AsCpCwYzQx0Q+cGBiZA/Cuwx3zDoH+A4gfT01i0RJUPnzaihTMoraMAipoqSgGcBUCJoqUiiEJaJEOdpsRJ4FmyFIDb

DULeKzQshZfsoSun9cciUT8ZD7H4rOAh3D+gzEuAkYrDKvU7rJ0y0YFGHbBIMlSr+L1KwEvjgkQvSqFEz/OfA5ZJKjQuvkZKwSrhSrM4XGuAHwEECJT2Qnivsr+K7QuwqMclytZiiMDypdl20kBIYrpOFSFD9EYyv1crgqvtPZC6K5nACktUa4GirkA1nLLB2c08M5zpWPxN5yjwwJMFzgk4XJvUk7aoC2ohUTO3fVb0VCGwATJFUD1kOACeFHh5

gBAh/DPAK7ywNbUfiuWAqAkmDAiJ2UHg2B+Ak4H6lYxe+GKLMA0oqOce7OOHczbrWHl8C9o7pJHskZdtVh83TBfSRMRPbd1okwbMQ1YcqrD1ymTw8mZMjz5gfChjzdCYn3vzQ/eOAfdXzT70jcJBW+h20QnOdH4js8w9UOTunAvMTzxIy5O59rkyvP195I1iuF9U0wlPTSu87SoL9a86AvhynQ4fKiiN/ZAvh0PstApQq+dNiC1NseEBHRqhND5N

Ig+i5QMepVi1qKaIGs5LNbhJ/HdKwC5/Ag1JgXCwbDcLDC2UNDTuibtAE1XKfeGiL3/JKPiLoA34sS57/WfzTj5y8rOPTBas9J/8ayzDhk4boy8ohqIK9Iv2CsiqQMXKFbdLMYzM0lWt2CN0zIqw4pA98r4rWw+pDSL0Q3FKNrEQKQOEqpaZbml5JgS2r6RDayAONrLM2KtZigq/G2OBmAqarKiyikAs6QsYgKQgL7AoosWDSogqNmqwgx2XayF3

PpkmAhygmIDqY6iYIWrvArzL8C4Ug2oyL3a22sszM6zzOWrJajHOlqkUoWqLrY2Rap8DAne1H5rAimWpCKOgV537jc48BgHB/89gr0K2amwtgKvarMTqRfarSrGzKsibNpqtA+2oMRHauuzLr9i/bJRA5xKQMUzHKZTKRyK3amrYzJ6mgOvKo+W8qYCls8bJprl6rQL3qOExgOmZ3ElVLLyiq3cLyruc/xP5yOcgkBCSyqieVQhVnMMH1AoAAqE/

UIkO9iFQEAeUCuB7+NEHarskzqoelEhXqpWCBq0ZQrdCkJoP39jQ+8q+9w+Y+ofTwuEd0FVXU+vMV8cefLx6T+POfS2r4fP3MR9HXMiJ9MavMZKXt4XU6rxM6Ikp06NKqQn0WSw4AY0TZNPdpkfdsbbpjq1fgZaO6p6fPmUZ8FmfPP7TA8QGpa1y86SNBrg0hfJbzL8wfO/SVIq1IIbXk97MaQ8MnOAGkX/WvN+T3U29Mwa0Q7Bu+T1Gt1IbyU6n

vP2zzG5vKhSrGzRoyqb67Kp8SucnnL5y76oXMvD3656GUB6ASwGVADjKkGAw6sKAF2MnLaYHwAYACeGFcskjXK6rvhUEFiBp2CUObshWQao7AwNZIq2FxoL23VIbQoDLvz6tUUrYtJiE+DOBHKcbHg5uyoKTwE1q6LSocKjMF2E9UfYZP2qKvWjTycGNHfWx9yZeq1dtKaa6vrpndQskmUjEPpy09BiCXkOgSyOHlEaO5H6qZ8/q/tIn4ZGg0Tkb

8gG5LBrqC5OozE9yDyN7y68v5JtSVapQpAiPoo5o7zuU2Gv3i869Wq7ooYlyP6Q3IqinMrZSiYqpTZ0sKLSjw/TKKj9ZSw4oArpwe4st8O0zP0f1hlfyv2L3ivtOXSISr4Oqihdf6TBCL/BEsXTPi8EpRKDG1fNvpEQDfI2wZSlWrhakS7FqQSm0waJFZc4h4E9iSWvFvhbkSpBPLS/pISCWi0RDFtBKEWnFu9SL00c3ZaCbc7J0rpfBlrJbrcoO

JNKGLGgov8I6+lpBLGW8lv2iTUIelfgJsfyUARrYqdMmLoWFpjCiN4y6L6hrolJvODRi4VrTrSinAN+iIwumBvhHzOpBdqwA/OvxTLfWgI/p96y+oxAWaqwp6J9PKGNXqT4NQ1wNFIPZsIKASo5sCqh6tKq+o/a40u0aPk/DPL9nANurP9QJJphUyoC2nKRqMYqYAiDWYwHgwSbGjHIRrM24Aoxjjg4MqTLP8jmNdKOVAUL7MVgKtpf9LSistxDw

mRtu99qYM6wMQhRUIWWB22uPxVL+y6dHVLC2/YuObEavfI5iWsodvayOVbfInar8jmMwLnzHtrDY+2pRppyl81RvV9m218ErK22rFLeTMahNvJjy26YMrasUxevyzs29WKFEv41ED1rTWofyva+sl/wjbUE5im2AY2lWvCj/daQr0sP6WOu98ZwvgJ0TPZUduFbf2+/MGMAO9eCA64/ZDJfz5RBi0spgQIQJX9/2wFkWw+ozmqEZmifJqdV0OoKM

w7/6bDuKio60nxizRxNsCPSAilhP51ZfBOO+y6OwURJDo+RpFo7GEpI2i8LUJjo6AfU/DtNQeatGHnrIOwkPo6eOrDErDXW+AQvqZsK+qxTxO7jpKQpO4oPjqRWLhhUzenUTqH8lOyKRU67MXsq5i2s3mPxDFOujuU7GO48oZzWSpnPxzzOrjv06rOsKvoq4hSKrSqUQTjr+5LO3jsrC7CpY2wxgJPaBYqn2y3z06GO3zvKKm7TMnhCsOUbBC64a

sLos6nOyLuHTK/GyvjgwJBEC86uWFLtU7h0u6mbA4jEEn4CcuiToM6+Orv2UD9Ot+EQ4CCUeoczX/Rzoi78u72MLIzgTpOmY67ZSDK6fO1rvnT/4aiFGkc1QhQS794pru868uwzqqiBsgTSgFMCTfAg6h/UAOIgMyzuOldJ/UDWowNsWZXGbCFIQPNaVg55PvzSgiBN26iyRvNC6vgr5rGDdWzbtm6zu2lou6lunIJu6Z0u7pm7Tunbqe7Fu6+tG

Lb6gXPvqVhfKq8bAenxpFzwPYgGUB9rIVHmBPYZcEkBTBOABgBb0HXE0A4AaJGUACfBJpySkm5x3vykGwdPIUwOJDQQb+AxvWUgn4oSHHFfqZdvIUQK3Avo9I6Ecui9bKWltJgg07CKh81zEiXhNCIqezNtGhDpv7VaG4PLYcGG1o1oi5PPH3mBm6EZq693wJ/WYKxeUSQEaZRTypEq0zL6v2Sc8qRiOSApOIQ2btJLZvLQdmxRvObiOmDsBYvjX

Zp7q/2q3v/obehxvHy4umjGtCX000tspzSmyIw6nEA0x27MOO0ooUHSnaIlrVYljuJCd4f2ga7DE5VqjKQhFCXHj1fDtPRQjuRUJ06ww+WqH1GkGPAEKwo6fPq0iMWfF3K5Ex5xbBxqKYSRabikFrZS6Wq7r7DVKxCtRsFwnINFasW8VrkqHMYZSr1d4SIxkTp/XdMBB90swxir0kNysmjPKvqIvTL4BEH+4Y+8rOTbZlROq7qGoyVrfSEwkmERi

UgsGHZUDQnwMTaim2/PtCH85yvWDgEGpEg0wBckJ984+ligT6KFefsUL4w4mJ8wxhfaPbLUMt/NQ6Xs4Vs7asC4CV39j5faKIyDAkjI56YW3/rp7sCwAb+DgB61rZ7ow0P1GzMq0oDcbcq4HsfqCqgJLB6Sq3xs2Mk7UcGFQkgT2HmBmAEeHKx5gIVC2AzqFUHmBiAPwHlA5e0uw6q/wjbXR5xmh1CnFkuQavDFk6iYD8ZTUF8EKbb+9MpjKBlBE

QL7wuBLh5aB7fNl49R7L3NIbJ7ZVV2qA8zppIjumt1wmSCnSXumTBmzo1gx5ej5Vup/+aMtapZOT8wJAeaJDj0MBrIy0EiVmv9zCIpBI3uHkTe6MDN6BfcGvr7+Oi/InzF2yX0JrUCrIX0bZIreuEyd6wIbt7oO6V2t6hB83p8Gfy5Lpa7purwYdbVu+9NiNuY23pJa3uxouZgEhxLu9i2+sEtxE+i7waKH50yltxKnZbohyHEh6Xx3T787zrg74

GtIdlKL07EF+lQ2d3UKH94gTvB4Ui33T7N6hyofWiRaraMdLdovovHbM2tvKD7Ra7aPFrnSjlOhq9UnlJVrD+30vvz/i+VI791hu5uHKfS4DNKbKwqDuCjXfNGuNKRB6MtN9QhuP3E7WOqPsy5rQm4fv7CYe4fV9JB2fOL7rhyMrv6My260+HnAb4aL63wP7rDKAel+t8TMB0HpfrwevxoqBTNbAFfCDgYDEwBUeurBaAHeW9FMFysQgAOBsejr3

Vzceh6WCdkQN+FlTSIemDAj7qYNhahtC+El6H0G+RGr7jipontyJlC1FaIhG1IXT4PcvCJIaJ7CoX10DqoQ29MmOUXsojxe6iN0Gzq/QYYjL0JiNjzp8CFH+4zEqkwKHuIv+A+o3+6+x17lmiRv17m7Ncv6cS82OyyrgaivIxyq8lWpry/B13tlaGh2YbhyEgNeMuyFUg4b2LIO4ttdH0EmtMsK600KK0arsnRv4gSa9tJxrIW/GoeAiO+3tiHHe

+Ie9j6awEuH7D0rFIw6He7uiTH50llr+F2Wi4DjGYhq+ETGLAtfuuAN+70d07khyTtSHoE+WolsfheOAgHlutWs3SPamgNNrPyi2JbHyO9AOjqZqiYMHqbM1SDszJ0kYO1a6/LUbCDosjyv+kGShut5S8hqcf1Lp27mOHbByplPJrbiymvZTScx8ts68cr2y3GHmHcenAORyEuHMMIvZzGkP6E8eai1ii8d4LwqtztSrhM+8YprzxvcdyjjCp4oE

KzC3sar7txmvraip8/5ikdti1iEMDeU4FvZHvxjoAGL+BlIvGhxx7oqmKmitX2/4JS2LrtaTgVCfYCeijCYF8k43DxhhxhFmNEgDuqOpKLF2eDv6LgRFOPIn04rFIeb2xwuuImuR6IXwleR5woc7JulIcq7+izifQCKDI7V4mf28LtrHBJ7JrAkRJscTOsxulAcgA0BoHsX4QewqpwHUAN+vwGJ5TMHAxiAaJDKJlwbAFqBICKeA4AkgY5n1BOSF

zwgbEmskdQqhO7sp9CvrI3LGFg2dfEv8q0iNyudQ8S3oTHsxwH1R5EO8OGQ70MotX5HcIoryFHNq5QdFGumw3VRNoXVH1hcZR0PMYanbaXvoiz3ehiMGYdJTg8cj5R6rrkCyRbhKQoGOdM+qxvDpwcGjR1ZtMTXc5VnOS5vC0dQGrR+RptHRh/oYdHHzAIbCHZSnqYHzy/Qxo0b/koIePa9GssbTSvR8IftR7G+KIj7dA+CQRij68etkz5pkwghb

c4qFoJrVpwTMayNp/juXGfm2aYzCu0FfPlb18iPyJaM+gtLWmsG0czpqB+hmuxAWKTzr2mZMh6fOnZQvMcWimgn/r2zTGuacemOahNLw7hOwjo+mzMs6b6Lyx99KlJAJtMKBmYZgDPVjim4/v+LTpw6Zv9b+1VuPzs2F7run9p9aZBmf/e6LgClUo6EzgqxrQORnsZsAH1b7UK6P3hjW4RIt74xkscCnoAhscNaWZ+aLZmGhzMYCnScMsY/7X8lD

owyWakjq5nM+2KwVqjW/mcJmHg/yc5mRZ7mblnmZm6JNaUwpSahGcq1SfDJ1J7AfhHcBiHtWZagYlU+hyQaoGIAtgeoEkBnACJGp1PoSwGNhMk4kZYHNct3mBZQOQdNRy/gy2SybYgbomDEr5P9Lb174abJCEERKOaTzVq+QfWqeDPnv6SyvaeyGS9qkXpSnavEPMmS5RphqymWGhiPQ9j9TBT7xifOcUf0HMebjKn0YHbGRTFmg9WWFHB1NxOA7

gIKWLyILVqeUn2p7ZoUb2hu0fVi45rwcHm6+nWdca76mEc8aNJk2a0nSqnSeegkgU3FQgYANgBgBPoKeDNxVAQgFgJKgZgDDBokaoCC8ceqBuMZow8pIBAxpbUU0CorDXx7oA+QdIkLNgv5gFL9K6ytcIgptARrbcyj0os9Ip76x56gFWKZFGPTdpoznQbBKcOq6Nd1wl75LPQbhtOjU7z9IT9DkTGafAhLHYnpmzZMSVBIYbFG8v3cb1qm8840Y

SAkdKPSA8u5svJ7nTevuaiGSWwacnaPR/Yc7yaZ72PoW+p7rMLTJ0CxmxcnRsYa782F7dt96CbWd16RGYDNq3a7sxabY7o+8RZUbhpkdNImvGEUU3h+26X0pbSfVkNiHR58bt9H+8t0dJqUxvdLMMR+jdpd6qk/0Z+mBSwQXzGsQQscvbkZperomBhiBLUM//Q7RMb7piIdPqf/CYfV4CO0jw1K+JpusrrvqVGb/8j+xpMxmglxKJCWeWm/3Jm7/

SmYzhZgNdKtq3a0rIwX1ohsbaifBFqCon+xmiYZN28sWbCn38tDqxTDuopfVnLonJZdpEZp2Oonpq2ifbyElqDKpmUllibbGba8kK2GThk/p/bWJ7peFrNovxehQAlpWbFiAimJbiLQl/fJ39L02fvGEixh6mFmne5MeenUx4xfTGf2oWdVm1lgbrZHHxuCvsXPFjDkiHaKnGtT78DQmFlSQxlAsxqIx2mZH9uR4tJ4WhWxSK6nOigRcTavI15p8

jEBcabDGXZcQfBaox7aez8mKLGdJmDG46d6KpZrMcQEJhVvsumCW66YH84Uius/8fxPqPUWho3OP39/axpcDqqKfvsa0Xp+f2ZrPmrVu+bpinIN+m2W2xfeWqow5d3GjmuUPmjWW6FmWjOWhVrKHSVmfzOwKVtgpJbqhltNqGUBWuNxXqWkaKZX1lxrWaGuWMYVOSJ4lFb79N826fnSmhpxEVXfC/OOpXCJ52tlLy0oUq1Tr+rabxqPhyFaNWrFi

tL+kq08CuH8jfMf0dUAV61ZspbV4UurTnek5uMaOhg/JzTFSrPx6Xpp5hbGj/VhUumiRG5Gr/a/ekReFFZV+dM5rtSgNN3hJ/BRZ3glFhkY1X+OpNaTSI02YAunES9vrhFs1m/w96jor3swDSa+la5WOW40omGQ+5YZWrvY6ft9Z9UJZe9K0ZiJZ2Gymm/18WjisZYE0Jlm/2OGSmppOgC3hwEY+Hh1hmcnWxBz4YgyHo+APaWWF6BLnW7h0WZQz

xZ8KfKXNhhJbJwfQqtPZCWe4jPZ6/MQsq9CD1v/yPXNagMO1qGM5RURBqyuWez6/g/chzDOMvcp4z44PjJqKGhxma8Ze0GPCfAP16cOLCt4f2O6peFlMrFnOyhIFZK+imTog2BlWbITX1oojN3I76YgsS4pA8DfdwUNxGCRCta8WyQGSS9kLEyQKuEh7GiNu9ZI2Vy4XBNrgKs2sejzClxv+6VJyeafrvG02cRGJAZcD2ZiAGAHMB6gdz3ZsIkCX

M0BoQfAGmBEFtXM9m8eoK3dASyAIJjFgWZuBQFgpUpLi5rrJ+VI9m10J2uc9KrJCWNIWDTf9k/gKjB8x2IFmIQE/55d2inFB4UfdMdq0BbUHM5sUbR9MTbQb6bZPffULmz3U3GVGbqxpl/pgnHyalE5OSvper8yKFqQkdkqqfwWapg5ObnI7QTRIKmp5TRanOfKhY8GaF/qZ/bdF/we3aKh8bqPagVkIYsCStxroubxC/utoXnRwZcgDXEckKq3D

UypccwWtj8bPHa+z5cNS+U5tKVDxVysNa2e89lY1S7Vj8s63bUrUrzXpHYbdeSG1sWqyQPqm/xDXbm1dZ1T11oEYsDfltvwh5VIR/rHaANm5cDiGy8kPNWs/LwNjHD2jDbHKanHzFJrjp3VtvTiN5ctGkGN2UIZarp/v2JbnRmTpvKPW8kKn8yV2f1emRY29K7HQK4yOPXy19fp8FN+y9sh2qN6HbCX6ksdaiWf2ijeY2ex6ANaXl15JY22gUpHf

NrKpm/xKW0MspYBmXW4nZY3yNrWvoy25x9ap2m/f7fdb5OtBrTDz6hgPZ3mdl/zETS+z6M3gwpKQIQrQOv/JnWffW7f3l7tnDa0D/Ww1sfBWmXnZ1TYNh0rmxvpmgOnrcapdSeZXk+WpO36yhRHJDHgeSpnqu+zFTG7Gu1MqHpRBjdbtrTd7Xel4Ygw9sW2lh5baSCTdhzDN2SyC3aUDs0iNa4Co1mgPl316pXYlTyS1kqaoq7Hhu6zRdmfDA6c2

RtM6iahsOek6udg+oU6Ctp7f7lpw+nYwxGd0mOV24/RrYoN2/J/K3XSl7/py7pli/2xXr8rte2HThjxdiMaCg5tARn0n3A3wKx+HcJ3C/ONt0aQV72JrWCxtDbUbN2uRcLW181FZ+3S1zHNsKo6mfKL7RI2RYQz9F1bKkXnhlac2H+98Mb2cpAl5r233mw7eFayt4mr32wwtbfFSoZqrPOX+Fyxvwaxp6/YnrvF5WcDGR8/eFH2Ks4me3qX9i5fR

Dcay7ehbTpxxfkX9V97vPJgD2/caHnp0Hfn9Z/SA9/2u/XDqE7R45Lk/3dl2Dv2X1o3Gf3J8Zzj3hXVlnMfQ2IwggIMtcDDVuiGVlvZaIPY9xvrF2OwRPcoPpZtWc9qx+n2ujbj9wGdOXUQRA8sCz204IB9AVs/fQKKQgbLAF3K5UnfhP9wrdacLFhmIFLW5wMVZi5sVRaHimC9ytoLSS0xcALHR8v3agm3ejFI90QhHYK3vl9tODnzPMaFhF/S+

drmH2FiCqvH0K8Jhc0yM7Q4Xbt24ivILZC8ircO7Djw/UUl438Rs3DhvrbMPISgI6s37gODTubdZjjY8auNzSe0nBTLY1Xl8AGQAQANqeyyFRKgcMDDBjmNmynhJAJgePnWBveQj5Uc1yg2DZXW+ZgDD5A8j9ozrNI1IRkE9KLXa+pDlSVYgfMQ8XY/pZ/SkO7N4sU9yYfZOZ9zWmwZKF6wFphw83Up46pgXOHfOb82fXV21uMkF0uZQXp8VSCPk

XqYqbk5JBRbj8xEOIZQbmQ9XXo5FJG/ckacyF80ey2pI3uc6m+hxrpkPep4rdsOJFixvH2itz/aUinjoadUWRt+49YXlGoAq+AV93Q6hrPRhlJMiZ1n44YWh8t/dRqG02NtDH42yacjH/96Mau36l1beROB9z4a6KCJ9CcNXt9nE5nRUTz7dVXCW9FeJP7l8rbJO5VzpKMWi47Zf/Wd94FbxPW1q9M4GhD3E4sDnF8GdQPIZ6k4xraTwfegTXdqY

YlruT0k9FPREhvb6WMdlk5JO2TssZwPcPc1HwOkTmk5ROZTkdblP0duYClPlTjvcSW4dj9IQOnFwxaH6tly3YJiMDuId5Ovt6ffVXG68ruc7h0sA/yHZ9kvYIDHYpIcYSnh5ac4P59gpaaWql2UMGnb5QlZDPA6uiZdG5FzVonGaVoidSiN9wM+uLgJuCbZXYV+v1lKShw0JLW+ox07VWbp7Ev5TBtuf1Y9a44fcZXmSo+W1W4jVTJw6wZlA4I7L

gfkvlDRzMYUeAE2CFLhnKx9s6b1FQ7s/RB9o0dYxmDTv1fmWuhkUWgjRzvU/HPe95xeTX3mEbBmHrdiXVwP1Tig82Hy1jDC97olOc/CXG9/pf/Xdzh/2979I8U9D7YjBYcmHrz/Te9TkD7moFO2zztaPP5T3tZYDqz7lb+G0y24e23+VwfsdUmTm0/KzF1mPHls0MIXELOKTtFd+2+Fhmaz7wON9bz69VxM4NXZ9kKd1zXY+DX6sX/C7Z2nrtzYZ

AHHKbOBRgAyyZf9PI+tM6WzXtvS3e2WwZ5ueWi07hZuWS+7jLL7DylmfeOzF346vK6AtnbvKptlWtZ25OoS6jSgT4nKDPOxpje7GUdi/bWHITpyKWzRdqxlRspxffeYuuF5nDYuls/1sXodsIlvJDHh6i+3gt9hoc935m6+AmwQ2SRaoulpsy+ku0wozacZGVA9OPLUzxy4sqX54zbcuEuNE4z9wVzE9H7HGOwKS5qXc7bBWLVoA+crQCsGP0Cuo

s7EkKorwA92mVaxfo7qoBAwKIqUrwi6xPLA4uqWr667GvROgrmK/Suc2qjuNzL4TJshLcrmMfyvtgJtx36+qqxn3719+y+kWXh5yu36nmSYqOgeEwKPhPLhxE/SvosogmUR+42Gcv3HIx9oQvJg8/p3It4N9IkuPjqS8Riz+rGyWux06/phO3e9gs5ClEG2S5YxI1YYhP1tkQuf6wQ1/syWB2lGpGu/1hC7/7RiAAf/5YBvsaK7C+6QdAvFC7o6G

ye/ViD6jYJo5e0WHMjYDcd4N9CXagtTHFc6iNF4aMWlP98WPBBk6n6V21E2uUtcQZ+9te7QCQ8HOjLiClIzZWnz/DuhRXzlWrUOj44ktYLezq86bWvT4YP7KXKPaGIglW/4bxmtzmdYFimVHvgZNFENm5UKOb9Vq5vHD/2KZmDna/vAvElp6L9xFs/Ws1RnJgy1oLfnO6KLK2l2W6L2IKhW4v8lbmmOZGRU1U7VaCZ/mO1uMOR5z1u9Wsc8iWJz/

WqK5tyLAOMjSYs4Y2jg+pbemH+Yu25hEWNp26n6D8hZZxvQbgmIs2BU+NmCOzh4HYZOrTkC/5iIj0O+iPw7os8pP4L+5pfGUqpitD80LtCc9P/a34qHckI8WyosTY+q+CuiihWIRDWwoQUuOO2+6/rTHr/eP86EsFhMPso2vYfRT9U/2ufyXNNQVkDQ43rfKy7gDrvTIJNBW3byZrjNJnXEJ5+HK0QEaTs4X1BHS9LS4Uiosi8MMFxgDGbghE7ru

HM8+V/ylEPuWaYLAky4cuZFpe+EmI2NiPeaAroBjKu0rhoZhwqMHUiy6BBRKuLvyru+4Lj785IovxTUDYoX2vrufOtityP7mJ70yGIyny/7qQYAfPmnNo3xnypaOxEPI0Ee+vrY74FIxtgboiedR4q+4AO8rlB5pgtTDB7CFnko+66vzLhC/90Q66dh37nyoenXuLh2u/yuKH/TobjznKRvBOmF7lKhPli2IDcrqOhLCl5hpiM5BOgWxIG6oSS6F

Hoy6E75eWKkQU8ZAmZHH3prvgxoFqo8GS4rnlYSC4vdfvb78h627weG+h8w6SruOzOiTu+70ed/M/3IMS1GC579vt506BboJKxhvhmtnRV4SNlxk4PSfr2Fu9wzUNPJEgjYps8E7nz1s+kOfHxLlSrMukFkvP7St28lPczyv18eIngJ/0i8dpJcQCo4hJ/Ce0RSJ+dvslpolyXGHsJ6Wxsn5J9pSQBhAbNQTDu+6Ke/HsNhnqoYrjPg5cl39cKfM

n4p/8f6nl1vT3Ad5YscfUOobrzKjm0S+52hL5Yoe625vpnZVLnIFMafv14bHDixn07omfDH6x5da89nWqZ3li1R71LkuSlAP7ynqMMqfFzwbtcQ+jjR4P7ydr/slmgW2R4fHWohR5Se1b/HfSebn32M/GxsP0J1SrbnteOfRHzrokeMMOhMTu4L2fZdkOuvci67JHoG5ZWvxwO/KywXsR6WN6MQF6LvSr6K50f+h9rsRfIXlF6uDhrhh+WK/niF4

Bei41u65Sr9klqxf/n5F9JfwzyS7jSRH8F/EeaXluo4WtL+e5LSnL/jqpfiXll4sCOCoMdHzXnuR+OKHnhac6vN9rl6q7tns572fsHjE7fvdH8Z4MerH6Z7AAkHqB/pa2n2p5ye01j05XGo4xmKHomaZzSlpHt/V9uLQX6OKZm/cG33i9NumF9r6o4xgui8oBOfHIOHXjM5BuM404HwwL5+EISBeT4G9ZWM4pEBpR5fSQQdSfo4odguZ9jOJAS0U

WN0jg1I0muBe432Uqsz6MCUNTiWmSffxbizqk7vvM31iL/FyJ8Crha7Hks7Y3IRuI4fqp542f1mER+eY/tJAOoGcBbIK4G2p5QKeDMllAY5lTh9AYk2/DIG0o++FY3ZIArc1BP/mfKeB78Rtl+JLGwUQ0uc+O4yDyBNksoP5grlIsYxcImNR3cfNNidFiBOaaaSvfnpUHXNqhsDyKI9H3ycfNnLW9dORTo37Z2GlUbDhAGNPp4LMFuxn2Pz4XLr4

jqpsl0IX66c4+F525laSy2ZJdwdj8Plh488GDG6R98O/R90e9SEPn9tP2WEx5fPz6Xvi8x2HFqA7jPPj3rqm7BJ/47HaVu+6l2wfeNV9I+fRkx/KGutkCehX8t50f63Ipcs4BBeTvBtObLuhC4185ohUK7PlQpDLHuQjnvJNKFRVqAPLuAue9eXdLtD7punSh88d8lHoV7Q/vno7GVWwAEh8lfXkrbdjLwH/scX3kHw9v3XIL3pg0SDix17ajXk0

z53jzP47qlXNF3Ej12X15C9z7SMSfw5PFl3G8PakLoDebGPPsMIU/3b3z9c//P011sG119m83Phblz6KTwv1C9lmDWxWpSbla50YA3X19z8i/iDmwcOfwBmz6LKr1qC4s/0wjhPz2hWGQt0//h23djcon3eoEuxLw+vk+Ynt3emGRdug/j3xd15I96JP+53UEV6mQOnRXcDerUys0v2+nPTXNV8suHa83c0Uk9nErFWKznbcsq9M3Q0ZqGP44qY+

PAweo/aR6oj4Em4ynb/YOv2qV772lTzD7CC4rwaLDq7A6Q+t8jtAVIrSRWCYKu+bAnGMgKPpggtoLkig99brXv8Atu/G6mvYELe9MIKO/h6jg6jPyA0M463tMl+d0DekAwOxB0zkV5BuBv0GIV2VMmfE1v+t+o5Zj0bTR4N8ad6jdlLJUikqj3DnD3dmebZH9dqCt7t4v93TUydEjYaA9Z4fXKv2UtzXw0ubfL2kOinar3Ofmbe5/U1sMMNu8D7c

9PPO9itZ+Yq1yfxJuIZ8m8l/Elvc5l/0YJ6bJXNl6O/rWWviU5WGY32x6dOq3zYeC+w+uq7RfUroi//WTfvX6Rn2X2T8XvjfnX/vOZhva+g3hy636U/4Uzy5PvNh9T/HWcg4N9helE+c+tvw7y0+AvPH14cjL+jegPK01z2He72zT40vJmbNxGC8cfJhDtSeZbl582HVd4PnV21zg57AGkB60Kl2sNwI5mHhnjPc9als2Z84uhd5zShi493/IYPu

6kS+6eedqGK13Z6ub5UvG+6iuVcM2BqO0DdMvQLW/kfvv8hgB/iV281LfCNpHG1Lz/dwrSDDivw9xeOf/++bv3GIoq8K1f6x+Ndt9uHHqIUcbAQd/lf68z9/yv5W+x/pH+TvEs1eqorL/rv4d2e/0x4Qvl/vqov+kcg/+A7m//gNb+Z1jOFp/qn1h/h39RnpP9TEkKxB/rP8Wdmz8C9kxklssT95Ll8Fw/mmMvHsK0sdnJd6kIo98Xso8RLghVgA

UP8eLjodnjkv8CAVACZ/lxUv9iWRtLpy8z/p/8l1E/8zfoFd0Xpb93/vbUkIopVxKqTVA/k68lspZUMIoZUd1Or9I7hH8TFulcdvvFUiUtG9E1s2dgnmTdP9u+0pAfflYZh79Z9lblB0tfQvmOR4ovoLcYvsbdnKup1Mrn0xMCLjsnnmk8YMoYCfcEv1O6qjZqlkzNeZkrVNbp4Fa6tnVPfgBtNZql9nAZVdgstVc+pDoCslhrNHAV4Ct+s1cYYJ

wxsCCqFAgcl8FZsCxEYqyofzOEwMuGcszAZBlnnpYCxrqUFEgYHgS1KiBUdujNQ/htc0svgpHVM1Akgi7dFhrr9FxuldjgiUD/Yuig5fnIDSbmgcRCl/N39qW1cxjatOViPsRCoddevEF00MJP5HPgjdaWr0DyykdcBgZWdLPl68Q3uwUrrs0xaYCStgzp9dIHr8NzmvMCSYvAILSip8rhuc0oBq9dGeqtcHUqNMzmoLN9gQz0gBt6t3DugdzgTg

VLgRzEdgaNdBZn9dJBMNkxhGattHmwD94lOVnGJsJ6tGOYbIhq81gQ0Nwbn3Ih7uRRnNOHc6PgSEjsi9RWmChsDcuSkLXnCsMVrSVevFdFmbhCl8Tg0UDXhit8biEJCbnAFM7gSds7hisbOqw8e6Ky8WAtCCMVowUqbiwUW0sSCcQZa8CQnSCiSgyClQoCCIHj8NwRhitOiDDA+kB5UM8hMBUXiwCLfvldfyoogKxtxk+mDgCN7g9cJQfyDXYs5R

0yOLYzhl5EWLgvdTvvochdDZQkip88x9rxd5hrnVGbuMJ9YgaZhLg0MdQYDw/WMRgDQdQCXlqxcHflaC0SrNlKnr/xsvn6c/uAGcvLrnULDvQk6Slww5UuScDfgW87/kHdHDrRgeaAZZSasMCaWpHFc6pGDemF8AYwSICgLmgCPbgGEvbhbFfcMd0vPgHcY7pZs47lChKwn2ce9v7V1CiSVLZJQoCbMMtXbq184nirUWoG44ykC3BseKLZ8gd2sm

9kUU5IOBx7nOGwNFKWCs/tBk5bg0NxoCHUl6tOgRiBGx7AfLM+ZnECl7t+JuiMq5tUHO5efqFN+ftc8Vajvc43EWRb3Kzcwwpc8JZh/lPmrEBluEO5Zsv7QPIietQBuz0S/p81EgE0QwOE0wjuBzscvqz08vveDcho+CEQATAXwTHgelkX87wcLgIRhuEJ5vEcsBs/VG3jxtm3hIADgBipb0DwAKAPKgtgBwBwMDgAGlBPBPYOpRokAcA7JqSNjG

L4x0CKyVGcJg8eBrMUABFXY8DL7g0uOlxDon/wiWu34AmKjwgsqCA/Ac3B6mkQ1Gmta4CIinMiImnMJjm5twFhoNwbDe9emkgp73sw0ljp0YhOHlMpuAGBuYkzIZBmKIEQBzJqRgQR4JmUAs8gaMm5nVMnBsq5qXK4MOyFB84Psx9ePq79y/DR8h/Oh9pTp8MrIS606Zlt8XkhmMVZrB1faJaDePpJMKuvNsKlkSsCoksDATmtcGXgVteAaBMFLu

ddBJFw9eUqKt2PnUMnll31aAX7RTvkalw1kz8g1nQ9IogqDuvlL8Vfshw1fsH5PLhyo4Xhjkb+tV9/ztOsDPisCeQegDrIX58c+kdxFjHq90LoSdZ9j74P+sikcLnFgPIqS12+iukXtrRs3tqAhOelUM4bnisZVrek6/oLt4zPFsu/N+c61pjtJoQeUG/jNDpfPmDr0slCq/oDtjTq+lE/uetL2mAC8JHWDKgc79b0gdDpmJ2DG9v6VP9qDAGviM

9DoWGFhwc9FNbjdC3Wo19zoUl8mZrUtuMifBTobdDq/j0sjwehlwOP1CMwnRt3tsND3waetEBiBCbtiQc7tthssImmE4ARV8EAWh92oboFvqF1Db1nRlyvrrUJdlLcivnM0IYd1lqfs086fvlcffH79dhloFSYbxlyYdlDlfuedZfjTCv1jT95nvxleUvx9OzvUg4QdJ1aYbT8FntFDk9ot9cDHzDWYWTDBYSFCrPk+NP1nIk2YS098ltD9iVr6c

DfPzD2YfT8e8t6dmttjCyvhs8OfjstXIYCx3ITrD71vAC5rjoswjoRl4Bp+CYYXaN1wZ/0JZsDCBpth819g9DzAdn8MgYqctThh9z9j/4xfsaZXDiJc8PrwcKgXed6bl619CioVP3r/Epfqac9oRTcplrEVuqLMsh9l0CbFj+d9al0sC6kDtUAdacHWtbVs4Xm9eVn1DI6tGd06k1Cs7riCmwX5DBxvK8yrjn4EzpXDLXhlDBXrsCzHlZ8nIRqDE

oXJ924TMDE/NNdFLpw9lLnK0i1qUNJ+KWCx7lFCRVsLD2PviVwoRw9IocPCi3jPDBUnPCiZjQCOXklDazvk8Who2do1vKCCXm6tBSpWlJmpFdzflC0G4UfDxtsKU8hEDsaQSS1GfrmklSkXCxWiXCSWlz8dSuXcDFu48o7pH9jSmeczSgec5lljc21utDbzo2tFPrDME/vDMqnghdeliU0HUGWM1AResdSGZ9SyqL9ovmqd4sPlcCYWgjoLm7C0g

RYDRwXAi6oShdAvj/5AYY+k2oNaE8/l2V7yLgFrYcX9bYf+sy/uOVemCbCGdijDzYYlk6LqRta7DttkYXjD2LvuVy+keUpAmrCFYfxdXoXdD3oTQEJEfTDEAbJcoduak5EeLC6YZLCLLkgCVEUjC71pwihEYoj95NjsI0khkgIdDDA4ZoilEcjttEetFKEV3RqEQYjxMlYjfvudENZl9D5wPldMAcojnEQzNHoRrcgKoYisAd4j1znuQsEVAJ/EY

4jzakEjkEQ4jKNpEjjuvL9UDtdFwkbEjHot4ixtgtEGVhnCLEQEivEQ59RodKtEbskijEdYiqutLDjliJctEd4jtPtqIFREUjAkcJ9B4YvDuETllKkc8l7ITQFVLnOEIBDIDgOjJ9uFpRQl/vpc5wI9IVrkl0JXjRcRLgICDKnPgotiAFPgY1crvpoDErnblXuha9nts5VCrnXULUNC8+4XwCKrre02IU8UQEB7hkVqGCk7uoDxrqolqUPi5cWrG

97HjUDYrItduajtdYbgNF4bvGDiofsVd2v0CV0qdcvgnGCtFpdciYtddFgbtcAUc592CmuMTOuwFYzqx93kYCj2Ci8CxrPzo2Vmm97kSCCuSpDcwENDcqAY1FdkdZ8MVrCCK3BVt+mEyDJxidM8QSHUCbvPh9yEc1qkb6CKbmyDmCpocz/ExcEoZvCBkQSElQZDAOkhFw2Vqh8XQfwV3HPCRCguw827uPcTblSEdbubc8DOyEBXu0CNYRjlPDg7d

EYFmVmAdfdorpfD9aqndGKlFUAgaUj8UVTUiipWCZ0KyUxpFq40wRpUxAcycELt5VSIMjlzUW0NOge6tugTWciirndwuGNUKIEn0+Ti2dearPsTgKpVPUfA9C7kF8nfuHDS7i2CRsIdFK7uUD1PldD/amXdo0W7pFbOUD/Ydgj/ar+NF0n2YWYkhlfETn8xwb2DO4osYvNCnkCEUusiEZrdnYrQl+waWjYZumiwkT2CXYkl49oCYwy0X7DMEWq1G

0WuFx5oD1ONpBDuNrPM8Bskck7BwBagJoBysHbwKALyh9QFPA6sKOBhtGAZCAHuAvwswMR3l7NvhHqVkYK4QGSqiJQxKUk0kJlljNqMJ7rB6QeoaUMCztl5pvn6lQ/A94BjlHIhjuuZqHKMcBkgJDwKJMdkptMds5mlNc5rAt5RvAsGIqNw5IYLwmoL6wH6NHCItoPxnqrw1+GLjYNsDG5TtPqMCFsls9IS3MCWoexmphz5IPjltoPlCE+7kW1LY

fVs4EaycKtvhiF6o5Cf/nfsgoYhkoVpRiGZiRjbsgQdqDvy9iOrGtKIOi0MVonCgitBVsHlctu0l6UE4TEVuMXXtvYumsx0qTBddrnUs4aXsVYXCixoYUjS4UrD/IbJiuYchxvZNKDoTnR9Ggfh1TXm4siXI3CSQSuMJ1mVD3hh81KXmUjrwe1DL4EqkDyMI8R4Zi0L0SIwOEW+lgxEdpnQeQ88ziEJL0fV8DAvhtO4mjBoTp5jLFIhtOkUhUsQD

ysxWt5i0wiHthvqpkcfkFi+VlPVTdomlb0QYhTvmTVUfqyt7dl7sUsTv40sQZjmQbStg9oN9MfiN8cflpiv8nQc1LvOEOwAVjyUUVjGwpYjzalJlFMflFSigFDGsTkirES1jq4WXD2sSrDPEd1jVwjqFYjuBC63gkcZ5kkdizBIAKAOtYxTH+g4AN+AtgLyhyQNYJ9QAVA5UHKho8muj7JsYwhUgKUXNCWEnVKfYnvLfN/RCHN9ULgYF3N/QKMTg

1I6CwgGmse8eId7kyGr7k2mh5thesJDzbDMdoFrKM/0QsduHJ0YeeMBiF1C455GPFhwtmKJ+GrBiCQC3ASSg9Vjjgo5c8sB9jRk/E1HOB8sMRJEcMaZDhfK8cJ9rB8xPiRi6TkRjxunY0nIe0i+drdiupqNi+0RBC4RtBCh0WbM7uOVgtgPKB4gHVhKgJIA89JhZlwPEAR4M4A4CBQBzBMUcPZuuiFNhXYNYM+BsctNEpONzUeBhMoIWBml8MHfJ

ZMOjDHNG688LuU1PgFCiByhyp70TKpBRo5sgFs5s6HJQ0aeJbYUfF+i6Gvu4dBv9jMposdH3gxFW+CPg6EBw1GoHp5vAo1MxRCcjtRkfIgNhBjmTDJIkcXr16pjNg8uB3NJrNhjbjtQsATiTjHjoNNXYf3M/tsHCnFgKjePnadSxkcCSATh9nRl5CY3HmUs8dcDFYc8dqRqPFjumnidFqFCnIRZD5vmWdV4VMCa8ZzCBSgJ8eYT2cyMT6NOalsFf

dNYFiAUY1rGgttw0ZAiyXumkp4el89PmqiWdgftnVqb5roRl83PgF9PQTu1HgYqijtmrjOoYmw5QfQ88Ael818ZjCN8Q5Dnln8t2/L5FXkrviNcfyj79tx98YWfjcLt1CK8VbtSEVl92Qo3i0Po/iF8cesRPr3sffLZ8fQugihrgfDt8bx9gkTV99PgVDxkQyj0vvGjVkrwV5kQPj6wVUC+ikCDl9tNs3SkMNiYEHVRMWwFFFuOkVFk3iOzhHhW8

SOdmVoajykSx8YofXjeTuCjRgbykEsePDLUZr8/4VLD8UdXi5oXYsf2nlEB8qXisHqDMgns0DBTg1s+dBkNKPnuhj1v2t9Yp/Qh1sstmDlgccZiZip1gMopCQisZCT4j3YQgFqZs3tPpl4s6Jlhdt1pTsNCdDMQDgwjcvmAN44el9WThd9c9rojcYZs9D2uYTfYZzs/oT09bCed97CdOEtEaxs0PnYSRDiB1qscOEaoWddhTsIdENtPVcsW8E8Js

4TvYbvtvCdf9EfgZk7loESfYSId5/sf81LsRB4iUTVEiX0Urcm98ICi5p9CTfteDi4Cs6qXV8ic/s6JqxCQsjVdFfunjDYZnjLMr1c0gqhtWEi5COZpgcaDpYFZxggUFxq1C88YJIVofGU0Wpvh/uF/jyPmt1hop1RUsr951cZlkJgMXjOCaJEy8dmVnfO6V8ygu58JoVjkzqOEv5isT3KmsSYJh3C6MTCFBhnmVdiQJiWPrQSiYEsTUCScTPSq1

CI7jvCdVjPgriccSf5nsSCtlqszDA2cniZZly2tMSZHLMS8CYOdBPm3ifiUGU/icMS/duN9wcZN92QnAUr/F0SkCigTBhnDxu8RgSwgj4DDkfBj/AddDnFl3j0CeUSMSZUTsSaBDPEmNiMBvW8oIUElGcbxt0APMA5UCj1okOSBgMEbxzHCPAYCJ9BMANEhKgMoANwMO9dsR6xwOPqFO4tqhxlNONDcocBtUDMAwia9NwJDUk1sOSDnypSDN3r/B

m2kVlN4CVkgOrIMA0NxDV3EoNgFi5sPsR+jxPFKMxIdvoJIdbopIY7iz3JwI2+Djg3cZ8BVgGoYmtJjYxBGr1KwFgEwBJritIdr1kMacdfqvpDqIZKII8Zm4o8SDVY8WZCLYdh9YTlRjjgU41H9qYcoyfYcbmk0iJdhZDNLk6s3mifjEPvjjMCc1DSQQmTqMdGTpgQrZg+IrZfdHcTCMfx00UUb8WPpWSu/PTVYDkzVhVrWTEydu1fUfICROnjjP

jvkD/YozR8YEAFsyd2Ty0RTMPYcQjIyYWSkyRhsAYkQEJfghcpfPzsOLlNCjyqosQOp18GDtUT94vOTu/rN83/t1MXYXIcwfmwcIflYwcfgniDyX98Q6td9bAtv9nYdRjE8XHVrAcYCV+oacLCW5ka6sUTiriG1vvmUhCfkUSS6p+TKDt613CsUFNkW4DZ9pitk4XEsCru+T/yd5l84eksNapZkjAXUgsrsnUofm1jmlsUFN/teSPvrkNkQZsTtv

keSo2ieS6sUmcxSbpV4fqt9srsc8LMej9m9HIEIYtzEIsb1DLiVoF3yrDFRsNEdmKWPDWKaoiBdktCK+oudyCXiUpgSetSDoDFZyf0NhKU7I14dAl80Z7DyHtJSlvj2SpDoAEePlJSV4SJTeTgkj8mkkiM3ppSZKQ3iGyYKsmyelilKRx9PXiWTY3LvBRoKWcBthQS64ZqirVvZiuWgOleKcx0pgulFR4pH40vh5j5Wq/D3KXCcACap9qnv5SWKQ

Wt4oaP5Mya6tp4Qt9Z4VMDdttPisybFS68VpSW4QqjGHmT9I9jKlqSuqicHhCsn1lfCPVqatKoRhSilmGt5SmlCc9gairKYjwUuOu134UL9P4audLUY2TvZM2S4EQAj9zvaD2yc0C9Kb78Q/j88joWHDIEVH8/zu8MJ8boCVWvoCNTnutCvngiLPlLd1bgWiSEXLMDdm7QJoPbDdCQL9Nhvrs6yhtTGytAkpyYQFyDjOsdCXBsC/hwjrCfrD/1rQ

j4NtkJxEV+t6/oJTS/nDDpdpNEVtgb4zoTX8RLrwj6Noxc2KcBUOKWRcyHr5lFoaIjuLoDSYYttFOKVCgiwo4TO/lDTnwDDSQaad9BsXEjGNtDS/xvDE0aaFjm+j0jusuxSUaTjT4KlViukchVcNgjTwASJchkQFIUwRn9VYU9SlySzNO+iJUXZOwxnwIhtBEYnlmkThUOAaJUOacpVDwRXtNwSeDJkfD9BATMihwaoSnod5cdApLTIIipSAAv2T

1KQ5klAe5UEqtpiBNH6jOybFdLyUsjbciOF6yTAcTKe1TTvhoCErobSkghljNFNZT6qeoDFkZbSvHEbT1XjXDmlojFHaTblnaR7sp8dFSzfFYD26ihSk6pp8RpnGTTgfNdkKcv1srq3dghoxiNkTBSirt5lN8VOg7QQH0xFs5VCSX4D65mMjvQaZcffg0MKiVnSfcfhdLlhmxrlj2kers1c+rnv1EBKKDjImXT+MRcisgegEcgfugjmin0G6en0i

gVRCq0vUDHvJRdc6cfduruc02gZvcwol3DN4T3CnrqPSFQTHTj2nHTzmn0CeMidcPIhTjRwkvTjrlfIPIolS/aegcNgTddjLlMsvKRH4yIIC11gcCiFgYXsK4YZiWQewVbgTAMukvr8p9mGDZ9oO11xrO12ifcTyVqZSRCjriNxnriwwl1SfmNEoRCkiijgD35rwYBleyXDIByec0wGW8DrwTzMUvn7RNbj8DBIKLViku5UjCf9ETqQR0RCuKV0G

bP5MGW+DustzSbqQhdQQdBVqZpAIo4JTTpEf9CCQpijwQTQzBJhRtgaSTSMVhuVXdFr5ApNvS//gnsNyWDciUXB1JpqSi5doN8GKa75fKfvFkbnCCSUbqhssTqhHdnPUCQmiDRiIa0XKD5hFGTN8fdr38KbviDL8DSj+jHD8dAlRTk6r3sfstSiHGMYytAjET9MtBMe0exsySWpNYRtPMGcVNj6bNAAwwJUAqBqOBlADLkWcTaw6sMcxLAPqArgM

bR8ISfM95CoF/6LgR1UMoElEDn1ycOGwNNjAJxwe7Q3dLGY0bKfJsvFCVSLitxUchRctSUe8BRg5thjkbY+IQL0IXEJCpjhAsWHFAtvNuaSYbAXNpIQxF+hCDjndLFIaURxFXzO1Aa5hqFlFAblvSQB9jPNxQUtso4wiB2BHYhlsVjKGTrRvsVbRnfc6ySwFBpgKFDTog1iAYjU1mZqcEiTOhgnHPTytsE51mfsyD8d/tesihMn9sllr2pTjuDiJ

lgDtcyB6USEh6aDTEsg4sHmVo9/9nxiAnPczX2g0t+xt2U9AijcOlkHDbme8yWAqFCjUezNgqQIJ7QRr4PibvD06YJjB6aQ8sQawSkbt79MuPtEeviEJvGIogrYlJjPmZ3Tk6oec0dgud0KZCx0ErCUIqbSkf8desjsCj87nrC84BsYSz1tqJuKfmde+FDFvqTj9zKW2kXWnjTMCHWE77vCydVoT9xgNuTdGQCSSWmizyYkf8yfGpd8WQ/C/btjd

olIhiMYkYCOEvh5/6NIc1oZwNyYr1dd+m1czieQ9cOrpi4HhCk4STFlznIgVeQY1SdMa4tzWT71tiUfJViZqV7WaIJHWcv5Csoho93q+V/4Z3tDQriyM/D706eltoIQT4J3egGycWbXZg2cv5p2pf4Z/MMpT8lb9B8V24fegQzpQRgluMp8iT9ib8GaQxAuGaAkhBIG9e9qHCIEWmywumiDHslEI0hKd94EQudVYjZ1ccqjkhRMH93zvqczhpKD2

km4hqXP4Sf/FTDPzsfBTQcZFX8s+ZS2QOyzhtzcTXhLQwOAkAxqTbtyoZ9ITYpGDttM/BiyJhc9PkuzwWtrdzUHe1P6J/tcEXZ92kmasd2Qg9E3msAUERBcj2Udhl2WhUEQpBpgENUD/1m/iGRtfN8Lv6CV/iiIXfDQiRaVc8IpuC1h2VUl5RGOzXqSyzowrh4ZhmkgkcoeMW2bcBhEZLYlKlupfmlWyNQjWygSlIjZOjIiSGTu0M2R5Us2eGxSa

QOFfCfp4HCFO0+ygmzpHEmzZ9tejlGVkJE2kcTv5q6znKnKzbMga59WVXTDWeDxjWfvE/yYnTTXOTENWZp1b5D+JQgXM1q6UayoYnYy1vjajvgc6ybib/MXWrTTDLuiFX6cu1aCg7IBBCtCXoZhyGGewVcORgzs2Q089yghyFIEhyYQQodmYqdkjEPs9GEayzk2RQyFSSk1SfKv0X2ayEZ1l2zsDKAky9o89L1mZ9j2fzEP2VYcRIP6USWQUCfnp

KjoSmezCmQf0J2fzEdUe51qerTdU2VDAKwbxVLyBGlXECz8RUtiztasaEgGImio0X1UU0ch8EOjlyjQnize9tu8TCv+Nc2liyo2blyKuf7Ui0QOCwEGNBezmVyg2flym0T8wWuYlxd/PtE82VWizitTE+pHs582fWzCgUUVhub9lCDB/tJbpuyL2UUVO7mRUsmR6DVbr5zr2ZAkmwctzMmc8xY+PtFXOVLx/atNzA+KMIC8Va0wOWag2WVNz7Cku

wkOXB1V+qYirufZyYwDTjoRnTi3GVSSPGdeEIAKzY9qJj0rgF54wwHKhJAKQB4gEKg6sF+gkgFSAXBEZR5Nl5ISgvDstXHs5Wsvuj6IMkV0CKCAJXM6kRwil574BhxQeIQQKwqVkAaXNVeIGeDm9LG5JihjouesQ0jcSMdXsWMc30VjJzcUlNjSVnNrcXV5bcfMd7cYDiGIsqYX3sFsw4JPwX4PG4YMSVM6vtFs6tOglHSuT47BkHjyXOMyzPAQE

W5EZCFaCZC8trjjq8mKjghr3toQsvj8rlL4O6V2lvmdrz3TnmSq4Q0Ma8ryy3fjjjVocqzQEQQZ3wKosJuYWIJoqCdSAVtTK9luClma2TuAo08TOQuJNbjZDsfjtsJWTrtdyQ5l5UajUlYsUFM6UciWYvldjeWn1iWTVkQfOrxUOVRZQXgosSCOqM2QqtlC2ZtltyodB2WV5jOWcH5uUd2yvOXgUiqa6jlou2lY7kEd47pGyDQtGy8uZLyOgA3cR

ubNzAxPOz4+lOst2cRNoukhIa/Ha1AAfTsXMZx5gLmmtCuqONbXr/l6Ae5U6aV44CaQcUZXuo89nojFQKaXUV8lMBFsLS16jjfBTvqqSfWROw1Xr9JfYvAkAeBwlTvrIzLOcod7Dti4qmhxdBEmGxtQYFzlOMFzPqYqxYEs3BHqG+ki4k1yXYr1zrCK5kD4gk8LwaSFqMH2zQigxM1WizN1BDcic1qk0C2mageaHDxrYjgZFfIHgJaDb9f4m9E3e

VIk3RnOzczkxAsbD+tgVEu8gvqAUj5K1ARGKrxQ3tLi0tonkUlKWD3qMzIwAh8Mr5C3FZiqX1X+T+sAMrNgXEBqge3O1TB4lMB5otOxhono1PzpwxX6BfMM2F4EzMXfdA0TI4XEKt0h+gzTikq955IIxC4SHzVOfhdEPNDcBsrri4HoZ6ERydBk8lv/CQJHAkNBYgluZm9El2P/wzDHpYKEknx0opwLcuFEDzos7RyFEMpweIQYlEmgFs2NT1uzu

AEkMmgRlECIwWIP+VMLo8EI0jPUldhjBDwTw894CMRWmA1Tn2V9JBBBJJUclxFoEnYVPeK4R3LtfBrQqhVtyHKJ9UGBJcArNhakNShvzERgaEbRZDsaag0ObDM/HC2BVzsaYOGDgjv+D3x5orV1EuMbttco0kK4mdMc2Xtko8A0RBom6MljOvhNamG9L4OVN6YO9MRLu11zUd2yQSD4FNauop+dGkIpSmBIl/hMBcYFEIDAnf5sQOIipgGiJCouA

wdsEWEc2mige3A4wmZuIir6FjY/HgTApBm+UZfMjFz4Hhl20WmFvcEqkZKUgJX4G+UBsu9ENFPKFLhVoEIyiZFvGHOAEMYADbUGz1BlEqlrKFIFkMr/QjilShWQprcdyAAhkOFywEsNSzOdul1W5sjFPHDI4kQmkg9PCsBiedShTRpzsKeWcL+mE7Jd1hZc6RTUh5wMTBCKjtsThbJ0qeRcLORWPMnGbTjxsQOjEjnPMR0RPIVQKOAKsJcJ07J7A

R4NEgSiFsAJ4F8AhUN+wL3CUcN0c45AnM9I9oBH5IomjyQOIdoPGDIUsDnjzo2I/BY+LUgM4B8NLTA+ZaLOc5uiLZQaUPriW1Hx56eRUyX0anNBeu+iamZ+i6mZ5sjqr9j0pnnNeeRHkqmESZWzKsc80PaSnaO+4CijRR9buLzvdOOhekA3EGMEhiktn6SleSvw4RPQl0cZhi9RBQsNeeGSteZ4SlTie0CcSVDkQl98DmqmL6xWO0attYVo4dWLc

8VxikojxjWxWJ0exUik+xVh9qMdsyDYZYVI4cBSAiUPRLIlPFFuTWLIiZ8kxWQZF/fMn4y/KotzhplD1/ErEmMW0SGot6dXwKRSMLlyC+sUd0Bzi3ilQiCSgJplig/m+dSWaH9XkfRhe+DuQiSjRsMwhqhCktI4O+bXFdWYJRnAYPUfQuAwl4r2dYuc5VLkQpBrkWuckGbEDwiKAyVAlKVkUSNkjOfxTREVBE8blSiCQUYyh5nzt/WpIzLsfzFRb

tDclbo1oBOY+Sg6f8IYBZ3zmuQG1a7Ovh6OXJyf5oiyGhjuD62qpINFNf0yCpuVKCjuVPmrPyq9ByLZQWF1K+Z5y0UO35FntAKVXlM8woklUIqm+Nq4lHE9+YNEdWljFOxV8Mdud3dpwQJAM4sEJ9UHpZ4dJAIIUjJMnAsohfGHcI+QtcKtQuOZ7vBjdquiijqHljzhseQ9gmH8ETsL/Qkcu0Tb5opLSYufA34GwS77mkgOVunC0RH1F6iF5ymgj

+stuXfdKmlhhuMgtliMEgktEkmJXEn+IGQqoKxzJZQeiCpBUWR8whRIfiMltIcnpDRgl6nG4A8LtcHwKAJXEJHB/dD7xb4p6F+AlyExzNIkcgnfERIL9JA+Iog2/qedaMg5hURA5FSedlyQYstweaERgHqO71BpXUhFjEPRa6ZedPjIdFE8j+s/0nWyncGm4mYtIKHViUgLZAwE2otwlFWVb9ZpQtkvbAiACWqOdEcvqhmoCYw/xJhd2BYDxqIVE

JsOTf0KCOfc6LBbVjSshkwAp8VbrE9RezragxsH7MvHOExg+colm9Bc4xIDNF9ImtlHKJAJMKhgl5xf+sTdrIFM2MxRu2QdyJlOZ5HMHB1L5K8Ng5jFlMKv7pX2ftEohfp4hUnjZI+bH11FA6E9Bd9F3+mkKCihkK5Ah6F9QrdZiCmpE5GNc0npIEcENGdhSCXAifpX+kuqKajmRTqkYrNF5LyH7gt6R6F/mCjcABD8wP6Nf0T8o3pApMjEzpqWz

KMFgJ1EifBVFGs8QEvRgH2hKIRINWUQYhK44tsCxZkTM85IDGjwJBKIzJcaUKhQQQi2diEuWRSKYjB+VGIB1SUyoTLbaVOgJaJX9/eDtgHIsZKshXAiLNtPd+pEqldAj8sTdmOYtUDRg44sHy6KkS0L8CKVvGOPSiEs2FIjC3IWiDgiCYM9JaZeBFB0k39HAs+Z/GG8Euubn81QjtLRxsikt1FDENTG4hfGOqM9oMHzSLNDKhcIjwX5Ipz1Co5Q+

uT+J7Ebn8BsvwNwuP6chnnRVvZDgzgxH9xS/tNlJXMLwUCgtwXWiBwoAdhw4AsHz/RDX46aXZlQfsB1z5FfB3mMfJBjGdT+hTvAwOIvROQXP9ZwAq404ugkWEghxS/owVwmNS5/pACC5/oyEIBAIJGVBbEiNpX4IqpHAi4r15yYnKEtrk9Fa7OGCcKgg50UDup7/EXEGonCJOkA9EnqPp5MukRslhaptOBcWpyYhBkZQY5hSYhGzaLlMAOEslESu

iVz1fL/Rg2FvAg+YJIiNnsK3EK9MA9INc32oh1d0PkUojpMKaMlQrIvDI5aFYm1fcG/4/gvGJuqD5giNtrLhlAlw8+lwr+djqh6YCQl/WK9F1Ci6ynGOBx+6XH4oGOgQXmHKJowtIra/rIq8yvIqSPAJzy4migHZDvAY/jIrfZtoqUbroq5/jc5MVMAyL/DoVNFaYr3aOYqzDAJyQYg/QAAkhFh6K9EhsDmLmwOeQ3KgJznaPrlHnAt0vFRO8EFS

q46kNArtAlazD5EzR9UKErNYgAIIlf4q5/i5Vm3AOZHSUsVa/t4rwlYHxIleTE26qH4aMFgFRbCYrmKI4qhBM4rUlVuRPOTqgd+tZsylXIqnFYoriFU1cPMlRYzDAogl/qwFylWYxKlS0qk2hTFdsPug3OTR1aLkIrA3getL4OTEgQs+Ys4Gy0/GOPyJldXEn9NMq5/qKEOWAyZ9/BwkCRQ3pgnJMrVlWKy0qkkJSYCf9KemjS9lShIVlaIqZla6

KB1qAMaUIIrcYMIqplUcrO2m6L/6MahbStW8wIRKLySRNj3GTKLpsSrhu3qQAuSDbNNAC0AJ4PqA2cahAeAGwBysOVh9AABo9ReLiuzGoJQBBZFFbDkhPcAIVzIjMojijPVuWKl5AOZiCx2YhJOidazuiV6LCvEk5fRc+jGea+jAxSzyaRBbjyIiaSvNre8mmYi4WmVaTlLFxIOmUskmQhBKaKDRVIMVG4erDU4kJFXdhmYltAPihiiFqs1RIoCK

zkpltMcUDVo8blsqxc5CCybxcOgb4MoyULp0ibHTqMoFCjQUaqTlmcyVsnS9CyRarxxcWM9xWKjyXvL4wBNXsk4cEUdtn0jUbKKKdFhViYCYSyTeaagKYTbT3nmFCBfECCwAht80fubyaruJjlFncTaCYi150gljKgsGqbecNMU1b3xe0q/Ck1VWSwqReis1fsSSCd1CIWdzLxuu1snFmJiwBFSVcCQMtpMVulw1dyCi+pGrolu6qq6uK9kWc8NK

JparNCdar14Y6DvVc9CQ+XWKzVdnithJrclIsmSXVWZ06Fn7zN8VuLACWPUrVQdkm/BGrlBU9de6pc12ateLGWbGlP9t6cnmqcjn6YS10UPBSnWg2qDGuCi+zOSzClhf4sQcZTGaqPLysfhTyKSwEH1WDsh+gyzQ1TLDvUu+qKVs7zczvmr8zk5jCEvkinPter9KXFTBUnyz14nciZ/gOdr4SVSA/lZ9mwBVSJogHtmfh8Dz4djx3aC3zDorlDmo

BCkd6Sb5r5G2z7xUNT+xQX458Ql9sOdHyRruPyBofRdQENhhr6dgSa1dRzuWUMCwNQjcINTTTBvgZcRkRvgtaVzVmgWkTmOWP1lAYfJhqaMsJCdYL0rtvzirrODGxgU9ROekrWrlxzsGVDDnueoDNrtqhnkVf0rqXrCtJQddxgT8io+KRzZYbFKJYRzDz6QQUQUdgrX1Uhs/MVBsmJU9d76W9dH6Q4TfMX+J/MYMZf6X2V36bzF2iU5qfNS5r0Dn

/SP6QKKq/MhtfNa5rXub2j3uZKL6cV9ygVZ4zNAPKAlgDDz4gNgAqQLAQYANgBKgAVBlAMj02AOnZImaO9nHATyKIK5Q7ymkJcMCzM71uNgaYoMYJKqaY1DBGIpxCDkM4KLF5dPQROJQHgtyqPEc9sUz3clFM6VeUyGVXFMQFoaTgxezyrcWL1Zjn9ieece5eVbMkJtEFtRmn0YdbuGwxeKclxVRIIuZZkVEcYrzUMZHZZlKx4ZmVTYbjmGSFme3

ih/N8FtIjr5/gpVt0iauKrIhRcuxbx9iNeP4ChRGTqtgby7tTnTglp/4e0B5DxugeqJVtL4tIrb5dIgLNzIX6rGFjOKA/OuKi1TeKetpFTvIj9qWFbBq4gp0FfUN5z/8VviWIP5hw9iDtTaUWo/Om7TyomWk04YtFGVpZS7GKYEJAjnBISZVSn4WDL6TtI5ydRfAGYfhrzzlT1PPqlD2dVRA4CcdD6bsNTy2SlyXdsly8BfEsiyumkgEK8l40RNE

veaLSfVVbtldd4iFySIjDyvCVD2prrRMuxS0bHu94DtLr4Cc792vlP9shCRgFbLzrPejYr7QTRzX/ncSP4SmsU0rYyJadMj35jTqXUUFLN5R4FPaVoDg+GOTHjpS1nxYUFQNh4FI6bYC0KUuMX1VkSFNXBTOlmktz1YerYCj4CUYlWkZlNdDvte5Figtv1d4idg2IobyGgqUEmggyKWggmCQWcurJsoGU+ggIdtZvc1S6YGrNPgMTz2oIcgWrRTQ

SfXrEyh3qSWiKyGzgYFJiRsFe9Y3rOir+LDWsPqEygME4dSmUOuTGygGFPqK2n3r/1gtyJgvwdR9bPrhyrSyjijezu9SPqZ9WdTbERhlS9ZTEK9aLYq9RZcA+ZChEOUitYCgXrpyhOxYJRhzN8BAJ0ohWE4+be1M9ZoDYZe/8BWX4SQKQnStkTnURLvbVu+mqcP6FhT9aU7Tg9QSKpObf8siZICNaVelGrixyT/pNTpwuHynag7TLyXNKG4t2cPd

gQDrdTTFbdfHTFqrBT+OWfUqaU18C6fHysSXFgTYWDDmNaNFK6WJzOOf6wlNcECUGfECy9bv4IJeNgVTtH9brBiguGL3sGOTsTiCu3lBua0CcyhIb6CjwSw0jqVA0vlcOwhnynZCqrZobTrMkfNDBZtWE1DduouNQNFw9bkJ3Md8C1ObT4mZCMMQwTUEXAiEFKJRgUqMNvA8hJYaVodiD6sb/rvgXobiyOobzXhbzxgmMDQiGqTfWZWrkQR4ao+Q

xL8yoT83DTSswjQTEFrltd9NaMi2uk1ExAuoFzAjwbwfBNcd+u3LkjaIE1AmYFyFBkbMAlkaoYHic8Ws4E6gm4FVNS1d+rrJiw9d1FXxRnSDkUSSGDdukTaY+qKdYjE6DVGFiYdL40WV0bmjVnTejZjcTUsLre9oXSE+a0bvYq7rk0uYj5rt0aQEL0bJWgRqqegMb3cJiSejaITkudcA1jVVdJjUsaoGYzBE8vgZsBLsbfAfsbj1gksFdYCBqjeJ

yNNR9C5wU4DbjewaVYToTveWLSC6eBLJrjkadEaDDBoUMoWDQ8j7VnprL+kkavNTpynCUCaPyiCblrgzS2GcbrOGKbqR6bIaXWe5VCfkADiDRlxYEd8DvWQohgjdwFcJeDEmZMfyvDZfADDUlivdrRzSZeVlVDd4byTTQEpkW/Md1CIVzDc4bNOct9PdUybe5WcDHDepyIYlYaB6hJrkDVHZ/NcZ1dce0T1aRP0RTYij4Jf9dF0kOMhTVKbD5Pgz

VKoQz8OdhLW6kgalTR4SMURDcQKsUkv2Qqa4qsKblTZwz1svuhRIkzJQ5sUEtTSFVTTRTcUOc9rnsjabFTXaadTRQz8QUl4CCeSFJTW6aJQWTlyKJIIGTH+ITGev4vdcybaQYSVmUSSVZHBSalGc7quUerEeUT2yQkXRTw4kI1iTfzFXQcKjrKG05KsVbqI8CQbsTQ5kp2ULFrDqLFCaUDSETc3A1hVaCP+cLF0MnQyITTzsCJXezV2beNPftrrl

EAJTSfBFz8mXuzohJprMNuOVhIH2bfUAUz92arq/2erqg7p7cRKoE4JRIgyggcgyFwbbcswfObiXP3wyZvLr1horrc6nOalUguaj5MZieiMLxenPdQ/CrnUIjjv1VlboKJdbE8djbnV4uXJLI9QzMgGYKIpaHFzXOmncoqq+aRjQGsZcZVyTUelyNCjTznUYFK6dVkjbUR6jzpQXcmYK1TudbtLoLUGjYLd6iv6LKF6jbEYTDad9mwWAJk0Qlwb6

AzrUjQUaWdUUVfxru8YwkKJr6YVjYjeVlq0XTA+iK1zXYtRb3DZ/su+TNySagzT2toQQO7hODduSKx9ucsCyqXereLRkybfHtycmf6rXauerDxUUVwJmFIfho5gr7gXDuOrPsB7nMVqZk9QpxMlcU9erVZLduCLEvv4P6MH0bfMpaEKfpbmJYZabKYn1MmaVSBxmeLFwU25JvsN1L4M/jYVrRaMcpPcafJeln8ci18jczqJ7i0UZlBnARWNbTyjf

EFXAuJNmJcPy3vHF032fx1MLS+L5RLrEkGvwEcXPtBE+Lyc/1QQYedUvc4BcfkEBWAFhpv0bT7gGF0QAIIafGSL+Oo/DA1iLrTwfRVq4tDcCWnoFhNcucI0tkhrYj+Co4PPgp4vFakDk1S3dXMb+hjbFgHtiJQHh9q3zTlD+dZ+boHm44lEGxDxbDgR7zQ2DHzbkNUHjVd1SQS1AnD2SjjZUFrCHFrOig3oNFHUgUjG5h60UIaReBebjnuDBi4r5

h0yB9sO0aebhDaNIo4MsUbrcksYxLT9LjTuaGUnubKXjw8s3k8wvmAIVUgQvD5fDcbGXti8AXuha5asubYgdIzOilP40dfwipzceCZzfC8kbbuqUbWGFWEfdsqcio8fgGo9dnvuwhzfDCYRMc91+cTbsBIwb/jQ4VxJfo9LHlJLHqShLddfYaDin090MLv4GRWqzwTQDsWzQ48UEmBI6YHgYo8Hwz+/pibGIIuciniMRCKuM1yNoSaMzY9IMnhfJ

gzbLbXhR7r5aeGbuTR5iyBf0wiCOEwqBYKbjTdqbCnka9moDo01ePqjLAtHrUKZ1KPMWbb4dB/tCFFbagst/q0YqE8+IHuq90CQtyiQ/qOWE/qxNfS0CMDa9k6ngZpeEvr29WPq3ihvF9+cpLZhcqUN6QMDATdU8XXkj9DKoHhaNfvTFgQuwo4vyD1eIl4VXMoojOqqV/6YEsSWiu95wCCJiyBainQt0dlFGT5gsqta77mIlrKA8w41lQDgmBFx6

7UxR67Dj8ThejojWtmwsbICECGYc5tUFEJjNeXbhzLwElIIDxiQsZdMUaihoKnyVZSiDwpeElwBBvCRjyovaeSj3RqTUW0TdhmVAxBK4b+QXzzTRQUtsjxLy7Qm9UcvwECZp79+tRfbi+WZT1CljECkchwz7eQUi+UNqzKZkJ7MA+zC8seVC+YNqqChm9y4jFkWKG/AhlIfdgHdxKS+Rm8LJVf4rJVXcfyrA7L7fA6RVgwlZ7TpsHbpyU9Tbvab4

KC9ZEm/BoaY9J2wqPbQ3HNhMVC3FnEklLrEiKE67b7ge7VLr+9fqYIuDOLLQoiCKQhFqgtdCdW4q5c3OhI40+Qux7NfsqiHZ4wniiYxBHYLLHfFnaHNT5k3ufrN+0clriqtSTYIegBlAMQBqgBwBokMcxU9LehxNjrJiAHpR5QEKhJNvsA+SQRCPWCxAQ6sPRr4PVpftZpsH4N5UOznuk/wX8ZZMNBL5wYdStcZLiprYAipaDSrofE+iWmkyrqmZ

e91Bt9jv0YtrIxXbiVtQ7i1tVvIS5omLX3o4gXqBny9tWKIFgFoYjjZg5DLArygPh1oJmdkg0QmrzPEtjjNeTqrfedRj9VZ9qUygxjTVXHjbTgDrKNWATO1YGdAdY2r/mUl4WEmAgfIXhS/DQ1i/tdHagNUy0eLo9q7fFHb4Xtlazaa3c3tXOKdWQ7zOTqfLJ8YfjD9qRr/WYzDAEbCz6UVfIm7XAiJ2XXSVLav4++QCMYykn0NfPfD/1jvrfQrt

dS1djr6xnDbvHWCjOosYbGjbtSnnU4DZoloba1n5LVqTEDnnb7c2dbVaVZZ86vAXVytnfucZrR86AXV879Iu+bLpZOFFHe40ktZ9zVHd9ywkhIAR4BwBKgCqBlwKhBqgGGBSABoA7HLNjRwCPA7WKaxytfqLFNi4QfUogUWnJECogU476Es3iPhgdtyVW1r+7c+BHwOmQHnJ0dUeHkzxzQOaimY9jSmeNqQncJY3seMcgxRE73NqGKfsY0zstBaT

VtRdVi5ILzNtVaoSCAIVMluKr5EK6SYcSigEBFMzkvIHjg9MHizjvr0AQHmazRp3NrtfMzhWoszzIdDrfgotLR7rWKjmRESLIsjrrIhjqj8e5ENCZjqXVnQq/9hbEiWXbbxunRqGHi/Di1oWr7VUTqN/AhaOjblaJJoOK4irLVwLdYtILTobPIWm7T0lSDljdNbIpbx8D1dBi5dRFDwbWzbsUrpbN0qg4aMrojJ+dmFkoaW7jdlojgWQISa3ZkU6

3QybKKTf84icnrpLY80y3dbayJVHTY9am6hMc3ULApayqYr6gHndXdcAdFEyyoEbT+bNzZ8Wil5nSn4R7aqbM2cagCOaYsJnX8ExsJ/auJeg70scsyTyvKEnTajB1mcTjSCo5yXyjOsM8YB07skyiNDjGa3ZQ5kSogCzenbTB20qSrR2TPUv1d1sw1ZtNszYIVMSmWrOigPrKeoT9SzUFzElmza+TmazjWnocV2TeNgEKN8Bqe2yG2ZCVT2RObQM

saVXOdhyhXbuySnYR7fqQ26swm5jnkqR6oufuy6kcojSdlrcpUWR7z2Uv8wDRqgIDZ786PQR6PLfsVsiX0h8DRnl20uh6AHXeMyDQmFDjjfRF8ZBV0SjBVhCmBLeDSUboOf+6DDiOzgOUB6TNSu68TX2lX3VGb33TTcWTbyaLDbKJsOZe7q2Ragb3TKbBsq8CAbrdctPmg7n7Ywy9TXrkv2n1aKQvpyiGdmyCQlwyzgjEY4lYcT3NYz1zOUzETss

ocqQeIbUTbcTVGcjAr3U9lUYPnqOOepqNFfoyMJV6bFQvBMo9aO6Y9RG6wbgGb/GFKR8gqGbwmH271vmSDscoGaivV1E0zfFd5AuAwCQgV6ABNgQavVQb6GZCaQQU16gzcV6WYSzahdmhKKvRWNCvS16tdRPzqPcBdGvZV7hvcGaTEbZzwOddyKbl17qvUEjj9R8aHOVN7mvTN7NNbeD5vS9z8vRt7uva17WflR78JE27JvUN7NvT16+KYuSezQN

7FvQd7lvaJluWed7oYJd6jvQ30iOeTSe0EjclvSN7RMgrb6vbayQQZ6aLxVl6DfPAb+3Wl7FZRl6xhGD7kifKyxxpSjofaD6PIhldyJdld0Jcj7uYT+q3yeQa+OU+yPTel6UfUl62DSl6ANVD6l2DD7/sqfqygufq53Zj7KfcT6nQhEbTieBTfvVt6CsuWUgjRqSkbm+7qboyCnQsF7j5Ima2kiJK/cfy8eHSO0szUKjvUbmabXQ8F4GT34vgSWb

/QXKRFXO7R+Xl571TfO60/Ph6RXXdkd7fplCHYWCBUjeaBCneb1yufbv7aA6mwcBaHUZlzjLk56f7QVy8LUVyCLYJM7+eF7pXH6ymwb+M82rZQ+latkiUV77nOcdz7Ck8BNjgogRQYdkLOSH6VDnJavCohkdil85g/I6aEvaTFdYrMUfMJpb+jP7qtPmn60ORn6l7lZaUuDZbTLan64vZZ7enEX7twUuDnLdPdZskH7Y/UodvfYFbSgsFbV7p9TP

fS37Q/Uvdh+YG8ejqhyT3QNq4Had8WJe7Q2JQeRh/U/bnfXlaqQnT86SorYqkYb7l7fvb9iknE4NLIFF/ftBlSlr693ShhdYmfcTJZthBFnv7VQTr6hJmVbwxjkgT/Qw7ZTXZ7+dMr63itrkMul8wIOOUgnQpL7NxvVbzwU1b/YlM1Rwl/652j/6HMBeDmrQAGHDV21oBh5rpDh/duraEQtrvy8hfX8FOrZvF4A9/dJAsI7Z8JfSxHYA9VKnqUxr

ZmwiFXmEX+tna1/cK19/PgHakEAwiA/qVcTcVk13XgHPiSA9aA88TGOaz6mA6NaaA0IIsiRvrD9ZwGCA9wGP7ZZlosrO6oGAIHqA0KDhA+nrBjQnyOIRIGWAzwHADXj7gDQT7hrUA9BA1IGiFYJ7faJgQrip80NA5IH0yNIHDybmUUiYj7chjA95rT2gRWFubnLr27YieV7chnxKazbhdpOgD6IYkD7yHscB8Hug8vhTHgNDQb5/9SRzYA1gK/aO

g93aI5rnvUC13rSGwnqA5LjduDTDynd6zHkS9mXt11pOmN7TvTR6tnoTadnkooQzfW66Mo26cg/E8VbTyi3FVOhUbTut4sbraHIuxE2IZwaVzc/r6Wg7aTXmoYHUE0GYJYHbqnp7a/0iEESFsO6pbtcakPda8/HpkzwAteCrjbuaIbUHb6KuMG7XuHbhyc6qUJIpMEtUo6PuQ28UtcOjgVYrB6AIsBRwM4A2ANY4KXTnoKAPoBUIKIBSVDwAj5qL

j+SSFw+kDoLhvF8KVYnbIHqNYCfmNWq5CjdjQWb8zetdVAsDWDEQ3SNqcIv/NH0bz0/RYyqAxeE7WeaVZ2VRzyFtRGLf0ctqcfKq7YxfMB0FMk7Xcak7grPw9cxfU5svvtqAVClwPnI1MzXYBYCxadrinQnlo/ba7I8VjjNVbhivBp07JfIXjM2mOKreTrz56b5gVyQ4ts2KodCoWSFVFueiOWXJrOQxhaDKUlwvjpP5vzuES7YQoaXFh6y2Iee6

51fXscPX6V3ebeSjQUmSbnUPQPeUNNtvRU8YwphcGneibr9UP1TOSHrDEqaHuAm27e9i+0wBT4SvvQStLmXllfmd1klOSMjuOa8zfg46HAQ3RyfmY6HPQymDvQzlk3me6Ggg2TSkKt971mbdkmzXzadEjgqhThkTPstwEsg65jsQAeybQ85jxvXCQSSWzlnGYbNXGVsH0XalqfufKAH+PEB8AIAhwwC0ACAOVg31OVh2IPgAWgNtjUVV5I0seIls

DGQcUJPVrtAm7p3vL6wjtGlwhHs6L3QPc6gnQAsNqgzyptQaTQxZ9jamSJDIFj00zScq7mmQk6LqitoExdiGheSMIbCN4KebRmLB+E6ijwxKrdoKfTkuP3TZVXslfSYaNFVfpCuhoB5rjnMyOprdrWncyH54Ujq1xXP5eQ2s7p8Rs75Q4TqF1SFS5yR1cBakOLQdaosIdV/ifjrU7Vap27IAl3QuyVJc7LbercKS2SanSTk6ivHrkIzAUDlsWrcI

1m18I8jbIWSNj1gyi7/lVKLJsWWHMXegAlyBwAjAPUAtgHKhlwB+xpTF9AqIDlqjAMcxHeDtirHQ24fA+HBzyOigaGfVrsmkl4nbWliIuBHMPSBMasSRxDEJAtVcnSfkmqJOHwQ4AsZw/qTTcaoM5XV9jGhIq6uVWuGeVRuH0Q68pBVYCQTsLnFoMXq6qYD0zpRASBbrJiB/MFr0RmQz4tOIWLlJH2TyamU62chU7tVWvTIan67D9slTxQ0BHW4U

8DQI206nmWx0ioaosK1dKHrDa5TyWsKHErRHrTvjXkZnQv5hQyVbAI/OlfxZ+67ech6HWdfQ8vW8VlmUVGlQ+4stQ2OrH+flGVQxOS2yTlHqndqG2yZlHKVsmGTVVEbE1V4H6nbWK4wzGqb6SiCOo9yG4Pc3qU+RXTq9b2qV1a/toWRFGl1VNHa9W9k7Ipu6UdZNGDCWCyCProddxfadw+uAT86RQyaxt5CyUd811kUizcugd9HxfZTdfC8x0hhR

91usVxdrsPsYcKRbM4Spy7o8NEHoxC6+dYAiLmb1jHRtSMODAh1QJeZji1QLcF2e8NPpKXzgsetzUEZtyeWZKGhUgf1dQ/SzSfgP0FVg2dlxcjHi3f0MuYd6bhzj4LC/FjGcfp0NoST0M9WkTG3WciS7MMTAJraVDxqQPz+PSfsevmDE+vuqS1zsDGU2Q/0GSkdBmFc7dpDXeKwuacNAnnN1io3EJTnSASLnV/S2qZ0bk/vNS4YzsiSI1B7DEjfi

sYaCsA1SnyCbCvLrWqRcerXVrTmVFSTfHcI0aQHz3IfosshJsy/DscLotdj9wGSkpZMaOHGPVYjmPbnqZ8YvyBNSmChNVFHgGTFHakUtlOPdZde+qNH1Y+XTQwzhUXLiYxPBZDr4ox7TLyUqEUlJUEkBeMUcIwHSH6N9QNZfGYgdvc6t+UAawKQzrv1UrGF+gsbsSXnGQPaRH5jbIH5I7VdcjYrHtFsi70Bi4yKSYOiMXaLlnoCwBTWCs5agLUBp

gHioP0GPAhUMNobjFuG5NmLj/whZsgbeFwYjGdh6tYGiq0pwwmaqy1v6MEGW+mTzUAJe71GXPghdNO4uIU9jdSU5ttqtpGL3rCGqvPCH5tdKMYnciGj3KiGTIw1YUVduG7STiGlNnpKjjmskXzPZGTQAiBQrfFbrw4NYxGu5GqQ8ryO4k+G7XS+G7jm+Gk8c67sPnBGAoyszIE1hGUPth8OQxAnMI72cN3SX4FnfESfBIgM3Xtu1bIon5ZxSn4NC

U2K6CsuLUE/gnVo86N2xVHCJWqQmfXYzHWxghHnWrSkaE9+G6Ex9dhLbGcVxWgmCE3HrBnQRSYE6OKp0Nmreobmq6naHq8gnj8tUIohygSRjPXe8SI9tKkqShyV94Qm6dxWN9gXdNESkfBGw3YGqJoyx8arRom0kVnG1E+hq0oZomRQ15iRGKzqTE+zqzE5lGkTSx9jVifCvVqnDfddm6/nTossqQon2SgozLFq4ntDe4nHjp4m2SgUFhpr+KfPg

Vtuo9bTTWaLH9MajqsbTj7JrZC7gGb9GWPgjqY4UknBRCkmS3fWq09dAkEXU9FllkBTt1bID3We/ASoxLtKE1OKW1ks7vPhf7cE2pEoGE/p4NG2Swk3UnYI3AnjaWTqOjfYnIo97F01fqGiyax8U9ojHYw40681aPDgNYHLvgbUSX3SXGQJmXHpk60SsOiEbeE+QGC/KMTMhuHgfHUnHVk16dBCe9GshtsnXad07KWUCzKuYsF5iVI6RDt+6enVS

zFzk9tzyHZaf3XcmjxeAdmPdEaMLsB75k2D6Q1aXGC40W0U1SBq+kwjGCDFDHEsdUn5liqyuTpBrUqeobt2oW6fo2ZSQU/CmKY6jH5VvWdYPe3knuROxFzjB7kitwEl47Vi0U3WdPiZimSvQj97GRP9pWc3jsffjHAsjbbg6dCdcY0OchPiT61NbUbiY1CT5QoIl0xY74WfTF7JzlFxSY7OdBfY4b6encCUA4Kn76NymyY9u7pynhz9/Rf6RjQcL

uhiKmpsvg6jfSvalWVOdhU82Np/db6r7VFKuU6qm9U5b6v7SA7DU2KKa3oWHiQMWHKSaWGdg54z6gDAAWgB5xb0Li7PoKY74gFKAwwMwBNABPB4gOBg2w3cH+I8444SJXo/uH/4qUES1cMKNBkgMFloZY5g3wTaK0aGoCERCP9SvY4HYRbTydSb0k9SSbiEfDpGj49Q1JRgiGz40iHueZfGBmgBiz3KuisQ/fHdw+QRBsLgL5uDsdLBueGhCouxj

tYU72TAAm08uHiMceWL7Xa+HHXSyH4EwImVodAn6k1+H3tZZDCk+FHXcqInDUtBGx06QEqdYVE503EnQ1XNg2Q3DlEEzotM1bymodQgnBE7yk2oxZ8fjvunHjjKzPw7rzJKY8cJ9QNjfaSRru1QVsZje1bejVG7+giTrD2vknAncongIzCyh1X+n7QfSj9o6VsQM2fDtEynzSo2J8003lSvmeO70vvBmunUpiLWg20zdWLqh8QNGaLbPjIMyxaYj

TiT308oa5k5mcrE70LlnZPrEo7ytU1T7qILf4nhpplGU3WQTXnQ0aV+TKGfnT0Ct0yB6d08AiKM4stDWsXj7LTPL28pBnUloO7a3ZDrXed2D43YBnEOCebwYwzGc9c+msddUG9CV66Z0ws6cw9kGJvRpmVo767rvTrr+vbWqMI7xcBQpjSIkY9F23UgmzM1UH8zbwFiOTGHByVhxzM+IzQYnhKGvc5nWIHZnNdi/9ZvpPxCI65me3aYyyvVSmzCc

tGuE2X5yU2YynA8ni/w280J/BrbR/lmmQFQ2KVM3nqks5mnKU8nc64wbNbU43HpRY6mfuWKhk1KbQJ4IQARAFcAKXcoAObBtRLNOGY+I1EyQuPvIAwlhwKwnOIf/k47oWBVL0EgpApOqejmjkxmO+f8Hxw7EHnGCdhhsBiJt4+K6gXPSrQndCGHXMWmr3hyrwxUq7AzJJC0Qw1Y0DPWnkcV15dyMwlCQ1k6202eH3QIypiTXLzdkj/GlmrpD7w6m

5MMI1NgyRclZGn5GwE007KncOqF6aFHbfjXr+Q9VGtmT5mZo1QdYOnd8T0ytCbk6cm+nfqGgs8mrRnXOI43V7DdmUuKpDSMtJSN90SFlmG+o2MmXEfF96oa+yzqdmHevQMwb9ZaHg+QTnisaDF3Y/XLgDhiFq6i6FpPU1QvWgum5UfymCypxjwCXs6LSor7H/UnyxoyHG+ilBzXvYd6UpVStdk6J62zRh7/ijj8Jw7YUk0W77Y0WCnU1WBMvCkZ8

vhd8qUqVdG4U+X5l7r2ZhcP8Bt4d/TNjt+L6JsnF4Bcahp0EQ72jWDsL4GmsurYVEEA9qg+HZbn5/Nbnh0lYGRqjYGEHvrnpYy7nRMeta+pJtb/Zelihs5WEmHrdbPrZNmvc4haQ80dbsBadaBFTCmNc8KE01n7mQNoqFfAnZS2PtBq2ySNbNA6A8xQ35SJk2Xyj0/fd3XiYahcOEnQqYXm4c8XmX/QbbuEuXna4+RH640WGCs9RGis7RGIAFSAl

5oWR6gPoBiiFcBKgMcx4gNEgnxGBBSAKQBFPI1mKtbS6mYCHUfMFyZHbbhh7nPcxjIjNh7nL/sU0wxxsUxBz00xD6VbvHMZsz6KJtfNn+Icyrk5EtnInfpHonRWm73iq7r467YCtBq6uvGpFoBV7jH3F/GcbHogmtp9QXI3KrRmWMx/40WKxxDCx2fEOmQEzHjXs8M74XqsyAc+OnbM1kqoWQm75M/rGg3R34XTj6Do+myiDY1jqHWp2kYM8P90s

2gXWsRSzAWX06sC6gWAI+/dQjT8tCC5QXdHl3rVnRmSX00qnD0+PTaC6+nl4VBrW0jgmXY3QWcY5xn6ddOL9M6wmIUyAjKMyrDoExVGyk0mZb0yNGD2ShnAc3JmV8SftDnUJaSC7+7rMymUiYzG6C1fnmUyl46bouEQk3VbmkLTBtf2WjagdtEnKo7EniLnN7tNctaECaByPwSYTtRApn++ec662dvnXC8LS+ftOatY5dzjQ4aG8vhByf2b4WLC9

pmMw00K2yuYWag/GHBLjQb/nQ4DmgweCZLl1jzapoXhymvqLMykivBBkXDEqoWOkVGHm+kSnHfubrxdfZmm+jVi2beJ82+RVzLdQ5nyaeFjBfqUm9MZp8nQ2FiSi/5KBC/XyKi4OFii0h68U3NkQsUUWqixnnhkzBqPvQ0WOi0h7pc6kXLM7kX7k9QXsi8Ui8i/C93LbaGmsVZmWck3m8s4Qg7U03GaIy3GKgLegBUEYBTcPSATcNgBmAJySYmrK

gEej/VqXWirPgCUF+jAes5bEFI6IDv0zgI0nwGWNzCml4XkPiNmScNAavabAa1I4bjj81K6meWfnZ7BKM19Ne9OVeJCjI1L17850ZwdLaTds8YN+wOjZOGF6SxRGKrP8wKJagrfIhmeSGBIgqqUcUqq0dD5HLRoyG7eZIWYCytCXY0bGoc7AXlPou6gM6Mmg4xJnMihZb3/nyG79dhHBnSIXvswtGac8CmjDWxnTDVHyWndMaBrbMaJQYKG/0ttD

7dZknb+UqWtBfzGzo97GM1mSELoR+cLGRqWelnH0zzSIbXrWzn2nXoFlS8sGRg4zmMqaDbxUX9aLLgKWeltMHfrbMHnS7czxS1NTCFJdbRDVyX28iaXnrVdaAy/qWO2ayWVoWWyHzROqVS9L81S4RHBk60nXtZFmDM5m6Mkb8713RFmyE6mX+OsHnA3f66j9oYanxVKWNoYQWjY6RnvXi0ToWbHy1C7eqeLUEsdSx06vYxgXh6c6NuLRWaHQQWWW

Szwmm4VwFV09SCli/rGDCb9ms9oOXj/EaX1iaxa66XgW+c5OXCM8dHPk75DTxeVEFY1jb4/XWqGE5FIXfpEn50+/sayzjqHMdy0q3Zwnsy7TGhkyLDQU2byUAU7mf6TsyUw0jnALgbmso4BSmc986/ExmXcC4hnHzG+X6Mx+WRc72W+E3x9uizm6NKVwXNcz+Ws3QxmENemWlon8iDGuen0sY+ndrghXKY4qHpC0S5Hy9LH2o3fcrC+hXNPnCyby

2bT8w1lUbU3sXW84Cr280cWJACrJysAhDqgGnYTJkYBvU7UAWqoSp8jo8WvJGBxMVY/psfnrGorMvnwRBHhukRvn75EaWERDeCjQzvmD82NrZs5CXUnGE7Fs6yq2eZbiFXdfm1szVYNs6iWGIvbpzI2k6UYm+4xeMdnnCEuo0cgHjtIbeGbs5SWHw8ZEgyYOnWFAyGbtaOn3w/OlGS1NNMcwdayo6DnPVfFnmCxGWcrsHHG6X5WCM4uXho+Vt+o5

zqny8xniMe5XircBWAk9aGYq8JqDONYXYMxjkPs1jmGZtEjJoxQXftbqd1Q27zv2p6WmC6pnlg4TD/OS+X7Sw8bPAdwaKq2PS1MztTBZrKWjqXYXjQ+gXTLhzmgiy4W9vQTFdnXqWfCxuC/C21WHLh1Wqq1wbVzSCCxK6NWVzdIzcs8o60Xa/VDi+B4kgAgAEVZ9AsiOdQ4AM4BiAPQAOlPUBKgEYBL0BcYOKxfQUJMQkn9ELsUYD4morDG5iEm5

h0UPL5gQzAJ0q+ltUrK5XwS2UzJXfJWFs/7ldI4uGonZzyc5pWn+mpOpspspZ6ABtrMXN31AbSIJ9juBwHUHBWEtjeH8xXeGrK3dnLZEAn6QxqrHKzB9wE+OT4Cy9qry29ntVZenT07OqJ05x8vK0FWbVfjXiK6gNSK9pB9i4VmmcRTpQMObRwMPQBIkpgB9AMuBNAFSACVNEhQgHAByVMdWPWJf57mAMKoUNK0l8yeRFpG1zkitOBLcmgaFWc0k

CuJayVPVRbpK2CGIS59XbXKfmYQ0pW4QzQ0y06aTsTDJ5NK3zyz3OLiIdA2nNXXuGG4gUg7I3Jw4E0SG52EpA3MKQtEa1dnG5vzIPIzCp+ySeHLteQth06AmnK7jWHMuBkbQ7+Gfs1aHKnc+6RZlBHec4FXCa53yo6s8mw6slCSa64bQoeuXTM9njoc+MnDy0Xng1W9WJQ2BXhQsmXTy8NN+kz2qcq91Dq67h8fKyVWn6UlGvpRTCv00u6Bo8yE8

+ZrFdy3VW1C2nWXqMlD264m6EM0SzdEzUSOS8gXCddISy7RQmmqyZkvSzHW0s43WMs6Or/swgW4s8VXV6/B8Y3Ie7ro/jDmE7Om5nSmWRS3AW862yWl8RyXVE7qrz61pyDxVMnw6wuWpiqfWYyTVGcE+8UKjV0EordFXFxRszQNZKWsLe86iqwtGNo1LGo89tHtWUC7rEyC6XTn106xo+d5Sx+mec5uXXwF9HVS4i6b1TD9LWrSktS1QXhSwf1cG

/QXQY9E8yi1kh9nf0NWCwNztjfFjYc63W0G3GWMGwnnM89wWMbsRnnUtvD0Y2Sn/68WXAG8lbiUw8SMYzZKLMeeLaUxnl26fWq+S/0N9E1wFTZZfXqyz+ntU9A3ALf2WlzrNtI0pFThy0vXYWmw33dVJb66TonQ40W0dG8Mac+cWowhT3Xmi4obBrc/j660r9vo1C6eqUhXwEdGWVS4GyY2TOq4ZYNShY2qHyNRTKyNYLH/fo9bFMx4XxY4uyJrY

ezD1o5KtC3LHD1nvrYbTjmULkdzoi/hkMYefjZwZl9mxkk3bC6OV3qWy1aQ486Em7n0sm1fqmabd7V+dRrcc25z4ae17EafE3Q2PPi8c47GSdsetDuS9GLLsEHvvQ6XiykcUom4lkOm/v4um2VWom7NXNg/amFq5RXwPDABKgNzYCoAcBb0LUByzNaw6cO4YaQAVBxUCLWHg0PF0yFRQdblgEl8w3oDLP0gY2X/WWRmgBeOaoG7sQVwwiguI9GiI

wiDiCHueupHpw5CHZwwfGZtb9WQxUuH6mSuHTa1j5fNhbXlLKrlG2MgsifEslGiE3dk8q/HMxQSAXqF+1wON2mKS0U6AE5NFbK2WL7K1jWHXTjWia2O1M6wTWFxYjmTm9i3IOg6G2kW6ruMaDr+y9W6eS4hHIdVOmPk8/XN0xEnaG4rnnK7+q0Yximh0K+qHtTDr963RnENfatg1lmXaE0RnEGyRmgo/+GOC0ASFC6QUMWS8zDUtJnAm0KXeyy/X

C/AUWYc7jrbDYkEldV43FW/x0mo0AS1WzmtRW+w39dTq3qYT4sZdWoGNdWa3ZBUGW/S5BpWoQq3zW3JSfrdyknS0AT8Mzja3qeX9MCF/iEUw43Eg6U3UJSZnzIcY3yNkkHjM3cTHExNtnE51j5i22FSdSSnd4UPqKi4JIeuZLahE7oXyNkQbCzViaYI7MXosRIyiTfhKly2hmjurV6PMz1HGuhBTkosbsPA0pCq3ZUnik2xV3M8W3PMw3Wa9WCyM

Tbm2M215n0MTts7QyuTog2TX8azTamNQCaMc7/Xwq81Wcmz63/yqGWpq90GcEWTmfS6aWXrb14F23qF/HQG3N23lGak+2tBM3eXOo7FX3y1xnQq/G1p27mXCKzLHz2zdkMq6x83nXw3b26mHjC87nTCz6Ho60Dt9W4smHVTtG+M/7dolIe3ECzPWkEZa3wKYdG3TtuaK3asGz1Y80pM7jbiCvO2CWdS3GE7zb4i5nsxweunPeNozvdhHyA0Vh3t2

mj6x3Xrn/y4NG+E23qG9fk0vk8cVeM7mEgA9kIFc+Xz5DmF6e/dZzGO0enKbuyDNDoAwxixeWPDmJ612U/oOGxy2hiy51kqrqi0qtKW3isyngSUQTw1c1zGLX1ysk1I3jUzOcPPV3yuZc3dRxmhrpU6qn1O/Jak/VBNQXmG3yilZbaBRwlSPGdTPW8RMzO/CC+iMAHSi1hm2vrYUDO5BNHzJhdpW9xV1JVODkGvIWwO1PlvO5CxfO7TXlJvTWOYI

zW288zWtjHKgIkM4BlrOSB6gIdBgMPQALxFj0dKAcAnLDURXBPDzbmN7hp2IHt5IMJB9mxMp6lZK4zGCczTm56w5CTGVB+cCZf4G0r2U3v0IMWK6ZK0fmda6V49a4pW57HNrVKwDWf0UDX/mzGKGrBY6n81iXeoOc5UEo7XB+JVMXazKJVUfRDf80jX5VZSHbs2drhcBhi1VWAWHK5i28May3DQbfW8W+FmCWtK47GNgnGW5vW5pvs0wEBOI9u3I

3Waluq6tlAWSoTW2v/LtdXK+JnHWnB3w7u93S28JbsGzvXya3OWeirTHnqziTKG9OLj24m3yfjlT0HgcyL2zyHjE6MaQXXD272x5XRtiZ2Ie3IXRdSNTnO0wmYq9q38q9428e1O2Ee2p8bW993Ka4e0si1cD2Q6TWx8dV2UJLV2nu0dtqe2aq9689qqvvTGau+E3D6+gnTW4T3dW2y8t60QWyewL3nW0FSkC8oXrIZ52tPrK3kof62HdeSF2yxnX

pG9iBo89QW+W8VSBWxWXZgXImWSl4mWiH+bwrXjq7DbXjobizG66sMbUo9hao1Vli2jV0mTC1/jlexxnT226iNyyh2L1Ua37Umo2Ora2ryW1f5YyysboXXPWJxX3VVJVGWGwTece1UQmrHmWMOY19qW/DH32VIIanrfa2N29H3W9td3NPsMGZg1W7GxZn3Y+/VWfeQn2CggX3k+6Tbcm763CE2X2bu8d6/jeO26bRn2ru4X3Cc0Znvoq1D8+833y

+217mzdTSLu0n3a+3G2ciwm2m+6G1u+4UWCzem3SDR23Lu2P3B+y236KW22q24akm2492PQ0W3Fbe22Q+64UHu6pKndTuSeiXm7a29FnQs6lmyPjknIdb6a+0u6by1eun/uxeTI4AbSvmIRhbe0yykKTl7UKSR2mCTXHlAx5k+OSpBX++jrYConqp3CF29ZhRGG4wCrtg1F2k7EYBAgCdRyQBPBpgFgAXuPEAhABWHysFPALJCN32wxfQffMoE/d

BH4LQXa9cVahVRzImw/pGxC5SQxxWm8qT6CJay5xnFkakO9WJXRCHJtVpHC04fGDa8fGja6fGTa/bY/m+bWhu67Z4mnfHMS/lNERD4JtyG/nXzHLpCS+6BOqDi4w3HmLluyjWkW0WLY+I5QaS21M6S5U7oE98cfu7lGdUmPd/xIFmL646sN4fb8M6yXWHgTGthFpRBHNGYOtOWBnGaE4OGomurrB15XVy6GrUNX2386yqsq8/EGKyV4O3Hhr8PHu

IDc6+vW6Ek42/B+YOywUn8b61EPQuV2DGLBuKlqekCZ1pOrj9fJLk60Cl0w1Pyoi0YOZnmoiBYTZrmowd2oYoO2/s7T2tOR/8hvortsflTWWdiETCkiXLbedAWQhyzs98zJyvlp0PD/tZlzA61ymh/QrcDQD8A8OT7yh0kPLFY+TNWSplTEsMPvfC4C2EY6SAs9UO90+YO5I6FloTjYO32gayyfaeS+h4sPKVfONESc+2Hy3P9jh0wOrW2GHF69f

0GBwiSakHaW+6xjFLhzazrh1LVJqxjE9hxynyWQPW/3XP8i411RXk56cClTXVlhxWl/aSDGf+9MP26rMPb5BvWC84XXq82FFsiWMOtgbx32PhMXFh0rW7Mhbn0U6SnOW1f8HA/Yyehwz9924B2VYeKzksa0OiXO0Oi2khW/WiVjQ9o0PLG2hXWi8P8YsQ0PN6ps6rGLUWTQopymR7FiWR452ce6b8WdpyOsftyPsPb42LfSztCU9UW9Phc72i/0X

L2d03bnU38Ri34TVR2VW4m3zt5R2APa3pRGVHeM2YB2LkVQKhA6sKhBb0HAAhADbxL0PoBJcjwBZ0dMBS3LlMp8zS6JcejzBIz0RaviTBLyGjyk2m1Am3L1JjItkIetWWpE7XNgJsAiIu6JmoHbhfhpHFNmomLmmYpppGC0xQ0i09wOS0/CWVsw0zDI+tm78wC3NAEcAIa2N2juAtEhmSpCLs6eHXqg5g9zngslu//nxB8rwv9J1Q7hNoPu5roP/

IzDl2e/b5+yyeXhW/2XeC7lXj04D3aq5cN9y4jqVg6YPxx9uL/MOmTLB9wtGtED93Va92FxwOrMCOjalURI3E4xSFWMfYOdutram9Sg3dxy4PJW/Xc7+x2WPB5g3A6vf2dk7Grq1SKJFi/g2de16E6R7C11izoXRQ4w8C21e2wh7/CIh0Q3oRy4nfy2e3e4cBOSkyLHKo2ahOWp/XIreUCxCf4tfnLBOIrXYa3C2c7Ge203ERx0FNW90Flg8tTUq

7C1re0SUi+zkP1c11FeG6+auzfLCFEeRPH21ROqh3ROSyzh3QibSPpDsROigsHUwClv90R0w36J4FklIyakVh0doM8/xOaffCSqVacPhWde2fcw8F6A+qTCDI7mHe2+32wkAG5Q9JPlJzlajc5QyNUHNkSCPoH+9TJPtJ8H7WO/tdDJ5pPDc9Z0Dxs2zuYlL37ewKtk3UbnrQYYdKIBmEffRpOHJ472xc5eR72YJ3L9eQ8b07wVY7jb5aBbyFa+X

7qNikmixoKiBejtBW6+cFLbCidzsBCTU9ddSnXez0XiJln7wQVpbXpDp2ALTI3KwsvceRWAhUcnlOMNRzrYBSbmCrWbmjuGVO0obI2I2GgG7cxgH/J/0MMe6JjZ+U7Jk6r/ljO8a3dGwN0AbTn1/aC/BEQqyO2rWK22ug91vugt0IDjyP0GwLrPtrrbp4kKx4ElZ3t24r3d+ZvFcSIfytYnhr5p/+nvYty6qUCNVW4HoX3ftQ3J/IfbdMvTAwxzg

jBuUMC/7QG1BO0vF/G4MZjjftaq61g6oUDg74SH3y121da6amw7o+KkYSCN/WUyna3zzaIa6asCJSMAUh39QjbDEm6W3Wx7XZoTlLchG9J8pc+tYXSk0jC+ekZfEhJ1BUzAP9qEWBq+EXz0ovEtYh0RsAr03DEgh28myHm0peypqZg2bMLnTPfW5P47Ck/F/cCf7KZm+Klyg32WNRzUUBY6hyDM+DAARG32+3L88Ap2kYjDzQRsMIjuzcG2oEeXE

vBJT7NvWjTONYAzbBZT17BW4hqm7337oT4tPGJlzJDRiV9ZwmHDZ2KdegljY4a9mF7Q0bqF2IiapHNAEIyqVkgxHU1CoskiGRh6KVMloKThUhEDOOgEM8rjTxbT22FbABlqkGihMyCDqn/ThUc21P2TwzjMxbM25F2DbJfnPaH625djcdozKblsxQpeDf37/hv3AfeUCM1PBjA+Mz9T/n7G/M5KyQ3edEnBZUFTEsLgCo2HHiR+P9EYetF9DhQZF

sHM187oAC989mnoEh7KYhSTL1Ababr+8ets5fq4IJJkLR566bx50/loJPv4dUDJxDojHHH+zAbZSbgECMEfLBNCxAMOIjEGUxRLNaiIE/uBvlroq7Fs4yoHc4zTCclcfkAOo8PJPa4Cd+TTD3hZMBPhdOszjW7bVunRj+BskAdlQHo7/EJ2mjREFcPFnqFQrhtWRehh2RVAJvAV/rQF37NO4ZHLrKkLpCKm+lqjYXqA7eRscYOvgZON3p4NOgvH9

WEQUi32ECMKRh0RSmCsJzxy/bcooiF+Rs1slKUoUBSVZlM4DqF0XrcZzQE1YqigCWnf5RzAQv/bbQuV6v2FSIHtAiyD0H5rqIG6fVVbustnLMuNokXGPxAijeXqIUKLZpOk9Jr6Nxl9LC/2lPWfrlF4FTdKjgY/uMKVJQk3SdFxUFDvuCxWnCOzgWLPX5rnwGQyjab02GSb8JJ3FqUN3SD9fYvPamgEj5AMwUuIJodNUGVI7TI7LAv1ErGNZsNZT

GIZ1hR3N9dO7b/KGxUhH/REOE+6Wc7+SMFZrEuF9HKZDcsTovfIbYCumFA8KfSy/KsXFCskuJglYqtCmljDWkkuUTfJzfyVYFL/ECzKB0+7Ix+ZqM6t7RKPublUhE0vTNcvT+jpZlOYijd/MLXYMygEbJ0GZrel+nrGYrvEvZbQVVabadml+MuwgjqC5GKLbmcGc4Rl8aEel9GP6iUVx/cN1PHnOpOnrvMutl7AVt3vwNoRBJJj+UcuLNa3V1Lfw

EZ/CKxl+zSaSlz0EJlBvgfWBHgV55kvriYxKRQtMKBoqYlE8tGFnAXYukyi6UeHryPM/M+BxjSCuAfC6UBsjqQF3J2lIlzCu9IrmFFSO9FwIqxBMMG4vp9R4u0V/yDm9D24FRJmxFFwZKzF6aEw3pUGJ7S9LMgaYuWgu2FM3pgFgEACbCJ8K0Z3ZIuGV3JBbrBQoNsgcueORIvdF1IuKQmF5BshNB9UOQY+FzQvi9YCF0BCjcPaHzcxF1QuwgYQv

pV06EO3Bd6BCmhgbbgXTWF5gvmsndRWSktEI4G3NP5/AvhRE5DwGJZs6JVBwjx2rSM9Wavv5/qVopUO4S1E8wFG7Qa4F3/wEF4cSLNj1ztyMAg+mKauvV+avDiTxUMmRnkDHluOBPSAPPfmNhfYjfRA8HfQ7FfJqc48/PcwoVLlFA4wCCPoED5x/2k6p9TdAibnCxGLdO4mvP4rqCXN506F/RO69EeK0cQ2zxzA9YldK17mEk4kS5N8HRLOi/Ncx

5ygbOSm9FFfLwF9tiFcgqiabmPTuo3nuXqZ+pebxaSFmUs/znWAoOFmwMTLWp4ll+5+3PUHUiBhpTG4eiIW92AdXOddpPwC+aYweOpBpCxDTO+aXuvpeAevDsmqESwivyZ6lOuLLpnPIYodkwuCWR9HvOAqgnpci554GkgnKRYEqOIblvflyG303Q5wnPjyiDxTuWY3aMMna/9aBubdYnOtPvK5rokLh8mi1E0aQ7OfZ8xBVsnFwKwjtgRqo/o2b

fCbHZ3/yGafGYaYDt1mcK1d7Q5rP4omF4XJQekd3sBucshLPaMPzmO3JIKV59+Y1k0UH+Z3wjBZ6TlaMtjyV2tTNCN39T3tvxvvsqrL44tqZWZXzPECgLPrlz+VdUJvE7hBWNhcDYuUymzP/ygjkQYm2EzUJ4rjSlpv8m/e6Su1OJYHuWFS2UZvjyp3OSak0QM2HZiWEd62Rzdpvg/JU01BVBxh6I8u0q1ZuGCluRcwX0RGk/4W0mpX2XN/FEohT

a0xHpCxLN05v7tqFvvshZt6Qdx2MHY5vZ285vjNz+VypU/EKFES5aM4ZuYt4h30t1p945aOMMBPTSSZw7DYi8H5A0f+VyIGBwlB+VvtqSfqqtzw9lgtEIJdGMqYXUkWl26tlJ561uEx8fksZ11v5wewvvsr1v4x4HwBtz8rSSX8rIB1RGKK6aPnoJgAhAEYADgKQAgjAVB6zNgAWgFsATqNgB9AMcwzWK1J3R08XCIOHhG9IsDO0FqgkBU474BFU

10yIQRBNB7XN8yaAAS5c3f4PRblOLkIlO8rpRtVrWPq2wOT81Uyuu3CWNVL13EQ+pWza4WPhB3SQwQKWOJBz+t0yniXH3MvgNkmxC5Er04EWyt3Ua62PXYk/ZQC+i3ns12PIC0unRtjsPmez6Myd6/Woh24OuQ4cz70/K2V2zK29o62WgCYzvuKqnXbk2cnjVXIXgqwy3ud2FX726wX+d/D2ojXmWNM8e2Xe6BO3e0d2CW5e2y1vVzyuRn5hd6j3

28vH3StmzuVCRtzYm9jGrdhru3jWrqh1RrvNofzb8W/eWR1ZMXKizmKYN3jWKh3GadGfuvIR5EOahzEvcDUJ69A2DP48YcPcfX/2LmzTv6icl6fh7EP+iSiut9QzvEq1gHRBGSa9SsruX25/6AtdCjv/abuJd06Ez/T57xdzzvg/Iva3PU1aa+TP3a6036WO4ny2YspmV6x34aSpX7UOVZ6a/Rd3898H4Qfdj7e67PS690T6G91WXJe+yELPZXvq

/Vh6a9wWXEs8x3jsqZP3x8S32Cx5FH7QanktyX3he/3vvslnuoboaaY9+cP01zu6FU+f6/d/1l7/YhL9ZUHuJffHvxTZkPAQkL7GHpTvCYuny6TdHuj2xnvcwiUvpMrXvYCiHvAAaPvxJ3wbvjbavmnZPXF08kEA93v1UGfPWPAoCOhrSWbE6wE5f+0/OAKX9HhLdh3acz7uwKcCPJbBnVU1+AfwJ/Em4fTGurXsy2mO4svv90ayMR1nmJgt8Of9

5HnHJ3GUH93FOIp8u73oqu6I2Dp2AO07yLSqSbM+b1OWi8+UMK7XbN9+Az5TXtOGGwtP1UzNls9wvvtfqQ3ce99knfTb7OY052xR99kC/VXue9wc6vG7KPJNweMKQb37pR4LGFD7RUAPZp7327H0Ge4VEJrfB7P+Yh7QmxDH9D3r7yPSq3gCWE29Do3zrNs3zfzsE3Ge/ofnzencpO2BdWe7lEYLfnc0LaWz3D53yk0UOhu2uypx2fIeVdTLmo0Q

EflYnVadzutOPzfaCquX+M93n8KuD0H24jwp2vt6ALEK+SO6D1Pk0jwgIMj2Qe3ExsVcj0xblO50V01TkfgBYp38j53riG/J3Kj+ke2uXAfxghUeeuVUfGj8QW0I9u14jxRazCnBzkO/o38Cw8Ud3s8Ukj7OPQolPl/D0rFBKFEeEc2bu5d+q9PD16jQ2D101h/3l/BxBVnD7+bPB+TWG+UWCm+SWD195tMbD1EcDj1NuCwzNuW81AOHUwtv1GNg

BP1J7A+XKOA6BvegtgGGBreBEhMAHKhPoGZHjt15JxgOfL+JFf5Joov7ZXOvhxa0g7zUKKi2tQyPsvFEvD9SwPZK+12z3vFMvmxbZlKyfGwd+WmId4IOod+dVYxSTA4d/JCGCBqiycDRRhs/IPLkO9FyKAAHv4/YNEW72mNB8pwrq1cdgE9t2R01i3yd/dqXXTpF965S2BxywnBHpT3Td8IXpPrcP8y4ftyywBmmc+Kfp8ZKeO1dFHdS3+lG93OP

7QcnzZy23vAM5OOjpsnGJ3eBGsVnn7fkyBMc69kmTx7GDkU9dD769/CLJze22y5eO8wVke/xUJm6yx2WI+44Xfu8Jm71ehOJY8lDne4u3nnU6esGy6fXtwGfbxx2XtdYHyj5M9DLT3EW3oT9TuxZO6hxSJiLd30XRixqfW4Vqf1+xTnhkSGHWocPWMzwb5/Q9xvGC9gX9tkn19+7oyizyKlee1u67d7h3sDWPlex6iv7AzOuSRyXrMsxSnpOcu3w

975nKTQmbL9wLv0TcGGqc66HhMt6W3CZsWFi08Om94ZmIzyxAhqzFG+q1bCAiyEX+jzOXG6V0H/T6uevy3RjLD6ZicLRzuIc36xXG3yOPG7aiDz6QWjz74mpd1BaLxycmLz9VSRWhgezp6nVzz707Lz7mSAK5WeU63ee3zw+e1T0nXXo9Bm+c+lSx6fOfFT1oLI6xaWFT6SFrS2HWbh5+3j65XXd2wu75GzrvPKzsegdY2WICb0mS6aaeGzzy3nt

SeKy29Tq9MyfXE2sr2K64OPVkfg3KLwKeiL392MM8KeyL0c7zLQ/Ww93gmqL+OXmd3K3CcUK26L5heWy6DSRm6i6SwyaOaSRAAhUJ7AWgOSBlwJtY5UGGBlwDbxJANowFgGGB6AEIAQjLgOPWD759DvsENZesVqLBrA0CIHwrGLoHkltFJgD6nyV4+xb92Jxat48mOd43mm94+Q13sfOGjSSpXUTwZGkSwWP1w0WPCyISeQMdfJsgcdmTQEQo340

7R0vPOOVB02OQ8U4M6YCRL8d//pg6xAXQ60S2OT9idf67ImvswvXO2/rEEy/YcXBzxeSoWmT+65zvIc323Bk0LuKr4/zcK24tmiUUOGZmrvH66VW/OSjGGr+Gfic0HyVyUOeVOaosdA4hxfpB7u7eQ12ajYQfVjwhl1jyfzdPYtJj917vPPSvuDOfu6zh+bvSCtIfu96Tnuz99lhJbyixJSOf6LIKXaKvWbrDl/3gG5o3ztmYf2PdTmDr2n5Nj5J

20aS6XjKnnclj/84pz9G7bCuRaRj62yoL1heRq3UfWjw0fd/GBeYL1xakp6Ny5uUDerS1xbij99uIb79fcotDfqj44zrUxcf8s1cexL+o6vQJ7AkgMHE+3h0pysJnpyQFSBKzFsBgMKY6jt1peQuN/iQEmu0F3AQUTseKTeIBBEq1v+VEVkrZVcTEXKdmDI4q5xCHL4fmFBnJXda0Dufqxfn5XZ5e1K/mONK7ieFRpeYBIAFfQcaDLEOBDCbI7wA

puydmluIH5fWtFe3I2MzAC55H9XDCIOx5Qsid6lfOT9TW36+d2f6wS2Ku2leNG1VkwWdAnCr1iDuT09r7fL8Oyr/8ORxT8EeTxz3SO7hnxnQRfXb4BrAhyy3Pb42fQ99M72WwSOcl1We+L7OmaD1CmyYkIWyL6hXkq9IW8SCgWuywdtnGytbr+nmf3V3Iexe4OyXuyJzZY1ru6WbCzLT4NvHjTjPiF38ziLyJaiPWC7jcsY8Ne8k3SZ5Vud1cRaA

rQ1v3jVlzvUsb3cJ0NewLqt6+75KtWM5RO62SPfkK0ZPS2VPeIKzBXpd3Ai573StubwaOwuwIAIu/NvxL/oBixxEh5QJoA8DHoB3PNEh41EIB3OLgBbg8PH7g844b+owVdcoFJrovzpY054UA5rYsnqDIMnq9oXsvMvc8itUUkx3IM+b4nNx7Mbj945wP3myLe9I1VI+u+fGBu0IO8T4SYyIHLfndNvFL/HYHTwyaBVb84Q94MSKlb2SXvqpZX1B

3re6YMBJDb5WLid1U6cLxL2lC22f5T1hfwM81ePz4NGVW9bzx70lbXDwRi5r1IX2R4GHRMixuUg/yXfQ097qDRh2N1R/vYSTiODXK9fxj/7vSfYHvALwMfrlpp8SA6I6O1hAf1C3cn9UxanJ95i8GC1tekzVXzRJbnvOC7Cmk83h7WPfR6KPR5OudcQfHr1fJ5IP7RA+PHfHeX+LTirdzbL2NycfrVeWD5p9NihBNh6FBMH151SFd51yjc9c3S/S

ZbP1yKPJdbLr+inX7AXk8UvbBuzdD/AItc0FancvkULG3NSy77vr7QT/e2igUUcEV/fiJmk/f7+0U17yjeyK2jem3rKLnoF2gEAGhZKgFPAEACqLTcAgBlwBEgtgFEBpgJaxybyGmmszffOqL7EDLC4KpgmjzQ2KBwWouoJU85l0fgwhfsvKo3hfv1O3cqCH7NqwONIy82OBxmOuB912PL/9XwdxLfId75fod6GZ94Eg/p8D3QYjDN2qx4txkuA6

FdXXg+dIT7XdbwtI6YN2VSHy9mTbyTvtVcOOlUyfufnwsP2S7NG7J2vXnd2BHgdRf5II/2eRd8NMjE8tf5jx/XUJyb5kL134OJ+w/wyhruwG8QfkX30bV71C+Vd4Lr1EwVOrr0DtVe79O9r8YdLC31PAD/BexS9dfpfGG3yn4lqjR/NXqn7sGttxfwF0eSBsAHKYUkscwrQMuBL0GvJPoPGKr76GnaXcIEPmIOl+jP2kMmdLXwYNjwlXCSV4zOqQ

7UW3MaMOERWLECXF+u1LkjBhwET212Ad1CWFK8Lesx8tnja4iXVwz5fjI35fJ8ztmy5qqMiCoLEp2Jg/iQ3oFtuvk7zXSdrVuxMy43E9vHsxB82TyHX0rxQ/NyUcD2e2NgXedWfyEzZnbd/2q+9+ePPdxhf5T8D9Xu4cfvz/Xf0IzG+ph9XG1y+5Os36C/7J9Y+P1c3Piryfv/zeVO9yGm++1mB2q37OsLrZDOHW7W+PAWNWEZ+9m2Z/jb2r2Jvx

ykh7nb5M6gl8bu++5bfNMzWe5i8otMNx1vgG6gW5Txbu02/BuxDTsD8z3UPK22zbHbxW2l+2zb/zyAfaz1Sb8Oz+eNH9u++zwM6SFn0wxoHuhHdYWfQXn5amdRoEw+ReuVGUHebDZUauHRmmOzwYFnzxHfrT7JPpwt0PGHq0mT+44H330Y2wZih7Deu2eYs4B/wyh71iuF2UXaB7sf369PdrS2FqbWB+yvRB+T9hDOzS6wz4P6XewbasGcOzu+q7

9VW/xvh/D37dSOb9/0135v2vN+GVXt/UWnSWBu5N3NzIiwxOqzcRu2rOxdXwORZEov7yg21xcZj+/8uMpx+IJqzEx23wi1cxZdryksZ0dA9VN1mEX0MlKzskfIk2P1hubS7uanEF7Pqzb7OelgbrCOaYkJbeHPAGTEfGG3xrW25v3jut+3C56Z/6vXkiAG0lb0QqzT7d5eva54+eNW3UFdr9Ovks9lnfDZ+fqOauvECQR3FARI+MDWn4L++MbXvm

7vBrzpaPe0hGU437gW9n8LEHgF/c1/3FtUMDMe2rzv8yQXTM6qIb2GEVa83nBPfxBMPy4yAvg146vJd5BW/y+lddVwIuFQ+NOTW1V/lV/wvVVxa2hD42CC6Q/u3C/9PIBN1Wnl9UvXiTuekZ4JIU6esvufTNfSJ2Ib5J4aY1XmJSybaOa5gbVl9DXqVRP/RtxP25rHDcWomkJgFNcSTDeP0LsWaZCiAtb7PcuE9FmbTd6Iafx/vgRQ7NFFQ66JgO

+EizIyV/byU1SEjSx3ybqJ3xQzRD4Jpsi97O3vxKC1r86aXvz9/ETe9+ZGfXvvTWD7u2wx/IzUwVO4pRBKQXR/Z30Wbe9s5PLKDU5mKNu1If3O/pfVBUIPdtpPzpj+kfwFyUEmdKWZ59SiN+O+k+QJ2OzYhth21aCLr9Fzlv+9tVv/c0DzfDpNzdeD238j+Ijj/LHnPZgWm03fxqwhcZJf7o+iJfgUZ3W/U+w2/0+9qjvzU0ENFH+CHCydCnzbL/

RfyjdygWJnlf8lU5f2L/raaS/K35r/9PNr+1f6+3byzL+tf6r+Ff8QTkbcaf7mtz+kmVHBhoqhGYfpm/7mvT/JzVFGU35C/9alT/H2YhtR99j/5PUIUNLp+GRT/zFTQaj/KjojB+y5KDnKNtt4RJj26d+5ymUbD+y56pLp03en3OQzlDx0ovIden/j2llf1ve5L5IDn/1QeGHSjz1Wwf5l6hnmX/b+f9/EvUOW7b3lfUQRXvr3aTEsC+tGm/0jff

lUy/Zt8aPWX54zagKbhVAGwBgMMS7TBErk2AMuBjmCziVQGGAtgG6OKbzfeYeCzNDHpSCmcNLWBsq9Jx7U/IZI994vjdkbQhkCXlR1UX9X/zekT5Uzz3uA/TX5fmoH/s/vL5Lejn/A/4bAcBWvHa/1jrNBUULRhwhFSZmTzWOAVFI4SQlzeLW9f4x1vb18zPER4fm5Er00cXyNjb2DfKdNF6jHPL582xRmTPP0p016JfrpTb1XVC5MoglEiQGMQ3

0eONJMkAJ9GcHsQX3WHBEcdFnKPWQsBzxxJGTtCCQJjOOsvjHIzFVM1O0PuCcskSWFwFElYeCYoJ5Myrz9YO3VevjUENmNXx3qifgCWY0EAzEVS6xMfEZNf0wDZMQCDygkA0Qt+MwPbIr8IM1kAtOJxANfVGosGuT5iGQCDQjkA40JNAN8WVHNUKTqTcT59AKEAjBEue0T6DOtO8TQJfN5Bmz85M9dir1sAzgD7AP6rCrcJmhgjWgDLxTk7GdtnC

zs5O4lBixTbOvsOEhKDXTMCtkoAkIDMwh0zQocWPl/HHb8MV06vSM8gexahU78xqgtDLq9fu0uTTJVENnNDM6xMgPd7PTwxiUa0K20OrwyA5IC292YOHj9EgPKAuc8e1TOvCIsChzRfSDpQe06rAICXeWyHRc4T9wqbRJtKF2HKcyJME1O7ZpNAy2SfddV5owH7bPsjAICDJOoL/U77OfsQ6RiHRAsikzX7aA58R2TbL89AX3u7WrZVJXMTZEcI4

TD7a2lTGxZCDWVgX0ULScVm2xC/AKsu6UApc4CVgIYAjTcZS1D7XfsfaTFPG4CDgNp3aF99gOeA3dM1jzp7A6MEzxB1APszb2p3fo9jnVyTHK9aX01uFdNR6wMbXd967zvHCvwsCVz5cxtTgPTfBi9juiqvI98mHxPbIEk6APSxeID6X2A/GJNWV3hqAkDpM10FOykJE0t7b61snxUKWs5oeypKWHt3AMa3BT8nJXkTYJMCHkaAs70iqRNWbXtW+

1nPLRsKA1JfWRsnNUOOeGdFznanIfsVi1LZazspQKwBIpdwyhl7Y/8tRwFjLsFBe0jDT71pi2MPJTM6PxTPFUCsny+UBg4DtlW6DYs0iy2LBrcLqWqaKLVfMTFA8sJAnzMLF/JLQKdUa0CSwltAxzRti3FFHv9Ljzm3aAdxLwOAU3BagE9gHgBL+FNwPl9+ECEAUHkyQHOkaoAF/z6fafNPR1oCLBwh3AzKSDRWtX4rH1J1X0PsDypCDEKaA3VEJ

AAPf+9tSUcvVMcNn3THVy9UTwXDT5s9nyxPA58cT0f/aW9ZJEJGM59G4HRCIsgEa2VvAks3SWeLKvQTtkx3NQcGTyIfBa0wPjRbJK9wCy1Vch86WxP3KdNWgNu7PP9qAItjCRZq+y77eft9uyLxDU9bgLT/F/F4zz1PCF8gQM9vc28PuzBA3P8twJNPaL9aW0PAhClwQKp3Z3cyW17FClsQ/y4TBQJbwIgjPcDRS1rrQpMNwMnKA3klwPmA1gD2c

yFDUftvyRXArRNPu0kzP1sNd3a2F38GHyVbMjsNgLn2HN9t0zzfXqMSey6jWhs34VOvRv8wBQfbNjN7P2+vOBtBJkxfYt9tQVC/Al8xCwEzFQCv3TtPVq01G0KrICcUD2vBDX8XKRozTA9ZTkJ7CkCmG3GLeFNFRyRTMutEYw3PJ41+G04bQkdxv2E7KO9ggL8ArTV8vkEgkTtxIMsJevsxPwGLSO91gNyA3b8XqWkgsSCog2EfJMNjH0TzPiCXv

2lA3A8WGwR/CW12O3ltb9cG22o7aNUez3jNA/sbxwKiBECX33A/ZBszwMO+AYcEfUrnbUt8ILjKRtcaYg46cl9FowD1EEsg9T8guF8MqyI7XL1thzmvcKDbbUigpN8wghAHAAdch2gpK+dfAkSgxIcC32AHRA8EuCY3UncooISg8hthL2ZfUS9+/x+5cDBnhF5AJYBnAGXRZwByQBtHPoBMAAOAFoAOAAazRf9aXTViA3oAOlKKX74btyTiV+UwY

jAkaIQ2bw9IdJkpQTBCD/Y2qFyZH3912VP/IB9mmiNfb6szcWv/UW9qwP4HE6ooxXidPy8CLDf/UFtZoF6cJaYwr12OL6wKTxZmR6g1eD7Agh8BwJefPswPqkDrZ8NA3xSvOADa30nAzh9e31h1A+tNryWjDi8BT0X3Fa9LgJcgn6D4X3WLAGD72zF3JPcr90gnRNJFn2pfWxoHrx8bAJsFTin3SED+IJrvCmEEALpfUr55Nz43a3dGujRg43Z45

yx/eoCqskQAywJu12lNGfsGgOgPMA8k9TBg+cD99VxXC9oaYOhfRcI7NRwDVR8ndzIA/l5GHWP+Ru1noVxbTR9R/VUONRl5ZhcoQqkGrwFzJ8onORt/aCDSCm5RWP9p1nlnJKCUf33ISP9h93hqZZk5PRB+BT0sSnGvME5ISiOvL/ke31VDXgopoKAXZa9rb1oqE2D3hwxyEltvJ2vGcT0rYPIxQR9zDmJ/Ms0DYIgbJM9aKnA9DEpYKgv9OOs9D

nD/ZWCMvFVgj39Vxw9gn8pZYLcqeWC2Lw+HAEDa9jz9TjtozX9YXmltx1NPLHJoOWUPKWCg7h3HfnMhYIxBTeM7IPQzYh4TJyL3NjtfbynLTPcNU1X9EKDkD3zjDyJO7TAEJh0qkhYdGuC/kzrgtSdAsSfPOVFkAyMfRSkEYxeYZmCRHVZgivM2QLWA0VkRQhv3I+ELxQINOuCJ4LSnXEDLxQgDPg4Alwb1cO96RyF1ZHs6YOX1KZ0gP297KGDYS

VIPOaduDzAFOE8QymzvCU4GaSi9Gpc/O1a/C+CrlwPZQ1tZHQvpTYE2YLgRXw9IA3/6C4FJUwNAq9ltdwtKduCq7wybPHNAQi5ghu1e7XK3DqE98RS4OVNnGEodCe0D2R83CuCZsgIdHDU5NyYNCds8HSQQzVMI4AVnZ6lWN35gs90mm1p2fBDnPQgBS3cQgwL3QfcS4LMnCy5/Yx76Uv0KEMUOKhDg4KNtYdclTV//H8pi4Ks5ahD5rh8g5/s6X

279JhDFATQPBhD7+WlcbhClV1kfPfoUlBEQuP1xELVpXTUL+i3gVflx9y0fS5dul2OuBZdSCke/Pe1q4KeuOR0xHWgQ/pBrvzgQ4z0oAwOBe4EFfXglbu0m4Jyg3652DzeBQG5RUzMQz+Ce4Mu/Ba9vPR21Tn1JaDGXCbAXPT4PefcPPUvgn5dfPXNNfz1m3FO9LIlqv2L1UL0w6js7GGkE9SygkA0QQWEZOJCniiyJQ+cSkBXfFJCSUS8cf98vP

1i9SNNhYM3jSj9i5wKQukoikNcoZYt5QIsZXOCNGWKQ1vtFZ2SDetcwblqQjeNKkK9bVLdYt1ZAmRlWkKA5Bz19d0GrZv9CkLzg9pC6m2rvZu8YkLkZURlckL9PQwtFVzBuPz1iYHCQ601ZkJRgvxDSMH4PDz0ZvxC3bpCo+VT3TxClz2C3OdtdkNtOfZCNTQSAs78mkNfpLnNKegc9O78RHzMNMVNoA0OBfSDqkKBRFmDn4IXYEj9bIPm/D5Cbr

i+QlD9Z1y+XOTMOk0sCXhDYDWBQ8KNQUPObWA92ChnpetJoUKiQloNBZnhQpPxoUIPg5E1Zo1BQ75FNl2xg205UUMWwbFDu4PQOAlCoYGVKf+DtPVGXXFC7/S7tRuCeYPeQweDPkNfVHScl7Se/XRDHkOcQiVNPNVIKT79tHyj5G5D3gRkQofd0DjOQsfdekJFgzW4WUM2Qw+4DGQMhRlRizR6rbJDpkMCDcWDv7kfdF70JYMfdNOCrKkVJFQ8QQ

T59DkELPlVQjOCkIJLNbM1ZfVsoeX173SUPXVDM4PKyKdk1fUIUDX1tUM1QpUkxzTNuerQXVxdQtVC3UKvNPY9bDxLBMHIMJUMZaxkFUPtQ269mKiDQxWUQ0PlQoC00uXt9cWxjLnFQ/OD3URQtLw9w8DVeARCuEOYQ+WJCuQruVNFiENn9X31Hin99ApAnGAwQ7kosEPZQr90/fRdoAP1y0MQQytCq4MbzT0CNgxEvMZsSoI7zS9BL0H2MK6REI

TvYUgY5UAjUIwBFgHqAeYBjmFvjUV9+n1pdH/kpPlpaIIduoM+Leoh12Vh4ak8njEhEYR9k01HcYRDNa1WfRE9DXy+rTrsTXx2fDE8xb2gfG/NuVRRLPy95klG7CQc9ZUXYDWt6nEhxLsDbI3uobNRzoKefMACNB1rXVFtNuwJ3TZoPn0egpKDh1QL/G3dEajgjR29CIzgjXYDW6ygw0FD7iSEgvzU+22gwrx9lQzgwpDIpgMy6EwF4q14vFCCWl

hibcu9Ddw+gsnZyP2L7MDCS2lBQjGCmPyaA7Y89VUowvIDEOW1QdDCmzVf1MsIJoijXCndYE0N1Cc9odmYw3otHMxdDdq9+mzxQyp10aVp2FckGMNM5JjCkoKowsIDYgMofEjC5P3UzBq8Im0IwgZMkyUwwtHN48xHbc28kqxA/eq9Jh0tjNMFEMLR7NKsBgJO7JpNDKhhfYRsdmUGAyzD2x1KvCHNaYC/JZsUEa02AqoCXMPpgFsVSAPjON4Dvg

KTvJC8/MO2AoOJh6zmjIA9NyyvAr35Y4NrbAuDy2zVjf6CajwgnOu9IDxzQgutXEHACL6hu6COaSCDUsM6TKVIOQKUTLADlyw3TOqd2dSD2F/wcsOkOSUC5kQiw0T40qxl7CbpwXxiw+w8MrVj+YUl51WlPHD8R/CNAzLpjknILeN8L/XOpNXYENn9vV11b5HgQ/LcK/h+Awj5aLkY1LGDRT1yvcv9QFTmw+jYJNyZ3S0t6HwXKFbDxN0U3WXtuL

1HqQqDe/xZfGCEanwqAMMA4AEwASRRqgE+POrB9qAukZQBiVH1AIl1/QI2bZxxFbApGEko1HkhPJfNxwXgxbtokIm0MAbMtkF9PFeMBkLJnHNNiwLmzeaCj0MWgk9DeB0xPVaC5jirTEGt/NkbA4NNcmBBbJMVxRFNQbuhqx2VvbJ0NkmwMTQFwuA/Q8Rov0MHA8Kx3n1gA3bs4Lw6HBqMLbz3JenCw3wDvbeDYWmWZfk847x1gz3lxWwSzBN90L

xajEUJvwK5wg0N1USPAroCjYNyiJL9hcMGTWF9DMLeORKMCvyRfaXDH+Qs/QqNhQL15QPsi3SIwvDDFfwjRRmD8XzhglIdNQ3JggoltCQw/ddsev2e7I/t21QKbIbcBIMKAsXCi+zW9cHUSIOZA3u8kXR2LOatioJOw3YNObBgAHgAWI3mAZcA7eEaQPhRlwE1wQ6A6sFEHKdD4wLXgBBxwl0V2VypcMBpQaYhusNbArwJd/3D4C998wIrjTY0Zo

JPeXiF/RRhwzMc4cNLTPgcLX1+bMPIAcWOfGW8rqlvQok8gbUX9aWx6nGLpP/86tCqFLqIboIefCytP0Ox3H185hSLyOytRwPug8cDPn3wAu3lQsNRAwKM9GzXPa4CGr0NPMjMkoJgw3LcdMOzfPdtIU2cfIDs5cN+A1w1UMKqjVfCMoLyTYJ93GxBzOKDxhhrfPF9Y937ZEI9aIOQg2XcMq13PKdYxgP6A4jDNd1hjX+Db9wGwhwC4Y0/w9Z0Rx

0fwkJsPpjv3aBIdPyAIr/Cw0Va/KPtsq3AIrdtW+W0A0895o2AI6q0HTy3wgR9p9xHHdJF4pxww62Cn92ozSLF4czQIks8y9xwzerEczmgIv/CPIk3fJVZf8Ilbbel/fzGPDusfMImvP4CZGU+HGO8voM5w7UsfQThvR5k6HxZ3Y8cgLxFRdwc7T1iwkTNvB1bgpo8+y24bfIIJ70sgu3try0/fbQ94XhIAgxpFgKsfSKsjcw18Bl9wp0KPYWNIY

KUNer8ui3SnBKdaUkYgo1MN8PELSW4zCJNZIkCUq1X6awi2p1sIvCs6Em0Iu1koJ2cIqBslAIpHTx8nCPZHee8sCIPZWUDvUlRfOtkgiKRBGi9D4JSPLDVBCNN5aI8Mk0RdDrCMqTPgi3Uaew5g/xsjcKCRSC9NhjfgvccxH0I/MasRt1DdBR8ALzI/JTCKPyt/eiCnC0kgqStm62YgtD89sj4fVflCIJUnHBClySgiUiCvCLoPc2d0O2w5Lh9vH

0ABO0Njz3gIsgFNR3K0BCcL8JM/RfsqPzjRG/C0aSfXKCkACOsAhz86zznqb/CP8KrnXs8D+zWItTCzjxIrCp8Ga3IrX0CMb2OYFqpPoERVZwB9AAtERABSAGIAMEB9tydmJUZLHWnQz0cNfHlcWB5T339wTUk6IHGwOIBIUAlEAJxceXb0Rk1mk1IMXfNW5wQNfPDnsXzTUB8tnyv/UvCcx3NfVbNawKrw6MUn/xh3NhptoKxwnvhXaEvIUVULB

jVvcxglQmS4RbsvaxOOfsDTPG/QxPkqcOxrGnCbb1DvAi9j3VnA7lsxsMZItnsWcNXgnFtXoLddMF8+CKKvTkjd6wZI7lC/oNAg3kto4NLfAUiWSKFIxECIiN1VcN8pSIRfE3stWwPdQUjQkwdPYeC8azlI0TMjPwKTYDCmrzt5Zt9ki1mvJnCOkP8A3b0TQw9dascLkLb7VjceHyqQpj0VDQXfKK9R32KRAuceqzl7YyCw5zDQlOCYiKsvQtsrP

whifc893zOTEpCAyLkIt/trIMc/IENQnk7g75Ca53YnPuCwz39DVYc54Iq/EfZYyId3RZ0LCNqTPJC250wuefV2+Wk6Pz90iOPOcXsKKRbPXMjtR1avc9873wDDNu8PAPKI8nMpiOs/Rj8wgKgpAn8823g5JICkORjPLDkCRTw2N0CoNEZ/Zg0RiMhgUSJcYkYtJ3COML2yJ9ckMnNwkMsv139I4k1dcLIbAkUkyOc/BZ8DCN97UA0ayKvXCKtvc

yUI62C1yIzVEEpFcKqNDYibILjI4QCCUW3IzYjLyNrLQM80aSPIsy0ZLTFIheonyNFw1i8FHU9w0ZsDiwmbXehPoAiQY5hqgFQganQCoGYAKkAXRCpAK4BEBzDAAqAdmFh5Z1gcu20vcyhJlAd/HFw3MWTw4JgHClPGE+kgcL5YTdDJRFSsX8cHmzp5AW8OuyFvWHCQd13cc9DsTxRIjaCa8MbA4Zp68JAxIgNAFyhbY8MDoPbTJTYjWlEFUnC/4

3Jwq6CBCm5Yf191VUJ3GkiPw1pw70iRSJpbCnstfDGwwO8sQL9vZ3ow7yUnfLCKfiZA4ntvXW+gsacfe16NCwd3wJawmP4o+HucQrdNxXTPfO9NN0mw9mcBLzzpfgjEskaImYZK7ww5C2dZEVwvD3tJG0SyGjcKsJEI2v5VILwQthMPT3rLSj15INWw3bCQRh8o7JsjkLS3KEFW7063OGdTtiN2cQjvk0GwlP44NDT+E0CkqMXw7+DU/mNA5uRMq

MrLLv9pty9A1G8fQOuPcS8XQAQAGABqgEvQNgAIkEZJI6g5ACFQHIAlgD8AV7DxXzSQG5ZDnixiducnHWNMaYgGkyR4a+hN5We3BQcYyOy8FRDR/UhI3eMQHxcvGV0WVXhI0Hcz0Lv/S18H/2tfBijixxFxDHC1jh2gtJ1RZxpaVqgXX1drBkVnDT4o0AC+8PAAqkpf0NmZEfCmQ1ZDW7t5yRr/VRY87zQvd7MDCzWQ4DCp7xXJfIduQIPwjmDdQ

IEwkTCOHzPwssjPPwrIy/DQ+TU6awEdX0TKWs0h3wz/NlNRrxwPfyCwWSCQ1YlDGy+RFACRQgYPHw0Vx397cCo36QT3BzsJq2iwtccU93cQ7X1YOzAgwxDd3TX3UEDLwMh1KVCAkIjfDo8HyIrQrFEDTWdQSQiJrUZo7FEBD0Uo8uD4ol5Q/EDdHx5Qq31VENMgwtCxD2wnOoiO9yFoxl820KKgjtCfcM8ZGTZ7WENoesxSAE9gE+9P6ipAIwByQ

FHALR1YwJjwj0cQYDfgTeI94DcwFqBCgyisEKw/wWgddI9JXHVIG7wy+nQeQgxB8iP/TVAFRHmtUmJYL0PeX7c90INfdZ92BzLAuajz8yWgyB8sqHFve/9DnzWotEiTnyNo4FttqKxwxzQjHh4aZW9dXQpPQrsGShlVbvDkawugikiiHwHATUkRKK27DFt2T1pIzACXKyFSA9JolDdGY7shx3QIAOYTIlwMRVh+yybsdy4UlDQ3Ej40ig1fX0sjj

Trqfstegjh4YjAIEnRAReDJC1+KT2QeqC/EJ1QVG1EebmpQEHaSBkUXjlRjW6xn4D36Azh+nRwrABB0AmhuLZJBJH7HX15PeFBnfJ5VJWgTRdZgJHswVFZnSUko8MpN/wcwCARlOGi4IcdHZDR3Zyg5fClI6BNpAmzgFTIYskgEfst5XBRaGh5MGUnTRGICMGwMDTlepDdkW7smrhRuZgU3XxaVaBNwxGU4IXYGtGKyNujZHln8VqBxqArGV9Urf

Gro9yozdjasa5DfYlNQFmZbA1fNfBjNsEIYtiBiGJVNGuiNFGxAMARnmkTYR1QIBEk0WxD9ilrlJedAnCwVOjFm/FYY+jBzYk+SSVCPmD2/VUh6YAQ3cKImTkQCLuiOSOFaNJBqZlCIMcj66NBWXujheH7otuUCQmgkXvgCniORJBJJ6KfiOVCI2CnIyEpZil9QaGBtFC9kaF43MScYefATGKhAxwJznGvodUknVF2ueejFZWLFb/QvTi3IUW1o0

R4Wc5CWAg8YpRR3ak2ETMFg9QItG2QI8BClUHhPGNCYhb0rQVQeFEIsuj1KdO9ryzXon8w2ri8cHC1aMgOgT+g7MDXuNx4MmITycHhsmP9qcFh34GPyMcxNjgxufsIoIkyY0pjJlEzRUxVjXXuodKJ++mKYjeimmJu5QNJIuB+kNGAOmPqYkpiljG6Y7bl/HDa3fqR4zGBGKfxOmKyY0ZjmJX1CPSwxpElcVuwYmLMYEJjSsjCY4v15/W+YNEIYx

C7iQxi+lXsYqI5NbgH0WoJklD2YpqVE4mDYBjd9Yn9KR0ldYglIYrgMEk2/MpAbIiHo25jR6KaYC/074i2TF5iIEjeYq4IZGM7orHkl1EeYkOhDsVeY+6U+IC4XMGIsAhEY8Fi/mJmwAFjsOWgTX5jnmORYolpeiLPgahjAeFoYkEhdYhD8F2innHb8aT4KB07QOuUxqjUtIljApFdo0lia0mBYsh0FEHkYgvxnaNpYkliHMJgJdRjhlH7iMNhCW

On8dlj9yE5Y0IobmOEWL5iHmKXuGljnQKFYtslDGLN2D/ZsRFyw/oopWMIqGVjhpg8Y1bpplH9KPkjhWjZY6Vi3aMYzGup16LmYxi9mJRVYuljhWOQImBciCD9HahJ+WNpafVj6WNBmE/0+jlPSAmx7WOJYtVjGgRdY6D9kUndY3Yi6a32I8LtDiLKojG87ZipAGoAYAFNwIVByQCMAeUActVQgFUBnAGOYAqBJAGUAZ95WoJeIkhUYlEQaODQHz

icdDtw4jCOgLOBEBDF5EajL6DL1JmQF2EIMT54gS2wITvZybSqSUCQpqKcvGajpXWZ5MOiFqOoo5ajK8Iymeii46JlvYuYxB3tfWzAU5wcFCnwjKwBUMZZKIQbHUkiLXX9JUawSFiyQakiduwkoukiq6LSxeSB88SUQOjEv6Mbo2uxm6OmUdkIkGORgaQYmWPACQ7sN1UZYsDhmWM4+Ahi8WLdGLOBX6VPYvDob2IvY/fZyWPRlFujLcIxo69i5G

JYxP9iseVFgxqtAONvYyMZuWMvgJmBBRGciT9jD2PaSdkIPmLFYr5hvmM0iIVJDx23Y2/IHXlsY4xiTmOFDDVjF6M7KOGl7FkEYuFiD2DBiJ6ZZmMaY01jskwg4/ujc4kF1a1jw2GNaGfAmUmw4wm4UGnGI/DBmQmRiKOADMPMhOpilEGGYhLAEN0VIfCQpSHq0Ah5jy0fBYMRA3kWMNwJ4U3vo/yQT8gjXQGijtn+YVypG7nUFZz9wwgeqLMQvH

C04nPU7qAWVW+QoRUCYmNguqAn9RYElTyxSV5x+JBfgJaFEvDMg7OALwzLpYbBnoRhCdB4vqGJSbQNvxFSESu07rBJA5fwQhTyEALdevHwPTpA/wUatdpJE0iPSC6JSYhWnIDlnP2QY+cBCpgvKdGjIOikKPsweA26oWRsO3AYY0Lj1GQO6GGcJmLC44QFg/DEYivoL4EkYmCNikCr8UjxRulhgGPYIKicYqI5RbUn4bqgjAg3XCtIXZC7cR9Dco

lyYuroH6NI8JQJaAksoN2tuqAlKGYoZgBZiNiI5RBcORtJnjH+JUqUFsAQ4yIR0MBZKfgYq3SZoV+hhhixqBZpXc19SAQReRXA0XmDWkl/4f1cnnGUJGfAZAmvgN0YMUC24ypoFIBcCKihXak26LricxR3IVpxeYNQqEkUMylcIbmoYXxwMEKJT/Bm4b7i0AkvwFxAPSm7dZNV02H+yMaBywkIqJQIeKjf9Igp7qDiMFfIm7DcCNqI35xDYJHjYq

jAkVHioZRDzcMIgGGtdRpNtMJY+bOVnlj7kI7RYK0unX4oTGAYtWVI+gL62KniHMBp4mThMWVlCUbiY8GeYZ1AHYJ9GNni9GioMWkICYwlEABBXYlpRGMQO30p4rcgRsGA2dQQpNW546pAAF23UGy0keLl40jwjuEV495N6iBJ6Ls5+0kwIDXiqmi14jlh3IRsbEQIoHUUnE5iM61IsbToFePN4h6ctpzUiM1BtDGwInFs7ePl47XjHeIwtMN4kd

WREHRIkeLwVYEhRuTswOutFuP+4ZbjQJCR419dHpF/4eMwEOCGBCPjG2K9sU2CWPgHuD2holCc0UjwQ8yauO/wU+KHQAXj7tVXlTDh/WAWyCaJKCWT4i+xU+KL45qVGYlL4z2RKRU/pPPiluLGEQvivyNbQiAdvQL7/ZWifuWuwslRTcH/sIkwoAH1ASzQ6sDdEVeYwKIFVX488ByhQJIQGAgXEJldY01G4qgxN/Ua0GG0DNi2QAARxaztlPdoVI

DoHKpBfGNW6dPJ3Lh5vAB9WuzP/A9DBb0v/Ny9ZtV2fK/MaKORIvtir4z8vWTZE6JSdRtMzm3/oRDt8SPkQfEiJBAzEKC4rUNpPAp16TwLol59R0g27a6iy6KDfCuiiAKH8duiz2LfYpdRKW238P+g+6MDpBnDGug+Ym2QcCGQ4fBRKWyxeBejABnRCKFAo0nvY2uj0EmrQvrZI5wIedQRKCCZLRui2GOEYmMR40k2wNyoXEFHoo5NEBLRQJLh6O

jjPA1tykiDNCTjV3hfuWjjeWOfw+Vt7okvoqDZCGPKKUViR6OQ4iVi0Pnvo01A9PFiMbuhLp1iYjZjJBAxeK3Z1OLREfdB82jyBNo1KOJGY6jjScSYgJuDJsywwH5MFcU9kX1it4DqTWgJukBvkXQJd61RmMTjI3mwEJ4AO+1fo9LkaUDQwV81CYFA4ZbhH6IzyEgVMdn8EtwS5fConaITHKHcEpa8/tniE9+ighP+9U8gmZBM4h6ovSLHaFwS36

MCEjwTLMhl8P6RgGJbASITkhOekAIT3BO2tPpc4gAgYxNgoGNMw3ISrBOCyGwTZAlR9O1JshJr8GzYvZFeSAwTcS11BVEB9SldKTzitlWReV5JVBOc0QMQQfnbCEiAUuO9lc/xjy2kEyRNLwUB4YBDSGMtld/Id/CHVI+jDczh0O6o5URBiFtxCxDG4snw2BM+kMW596O4E4LjdAnMYXrx6d1G2WgTXaIYsIStNfTPgdypGGOsIYrhWOKnosQIzs

hFCG4TPhPuEiXYcBPznb8wBNDlRQESCuO+ElyFQOPfYtg8FbE2E04SnAM5ItDit2KG/A7ZlSkwYvpASwkGwMnAEo2v3FDJdiXf9OuwYONhY9hj6lwZpWBjIuNhgbtk5xF0KIuJeBM9kdPIfTXAYpLgGhIeSfdVvWFKyEsJovA26IoSDDjcWbFFhlF1iBQStYiUExeDv6OM4q5YtXAzibQSNhE2YhDdzOK9okaofaM4YigMBOJz6M7MdGiCXHTiNO

P04uDQZeLZA7lcI43VOGoVy0RkE1YT0uPhqWgSnokWKVdDYZmk44QScUV8EzUofWIciP1ji81tEm1jjWiaEigN7BLMbdN1awW54+US+yV0E2OcgP3dEoMSj00Q4xQT7mIUXbX5FQiRybyVkP0CiRkSSCGZEl3A7SiTE7uddAnRNJgShGPhY1gTExLGEZMT4BFTEjdjCV0oEolxBsKdEtiABlBaiQJjz6LrE2TiEuCaCb5IKBKIYp9jg/lO9VsTGx

Or/WDjKWPRgHsSZOMmmfsTFHjhE4Di5D17EscTr6HEbcQSoOJRElQshBPrEuTj2xMt8WMTxRPjE2sSVxL7EucSi7gXE6LwlxKo1FsTZxPXEyfFBxMEEKljsxNLE3MTmmCwEwxJdhKkccOA8xMEeTsT8WOoEsC4nxLLE18TwOPQEjRiJBKWlGmBL7BfE+8SsOMdUOxiqUE7OG8SQJJTEqI0AxNdYneJBsO/Eu8SKxNlOLwTjkh8EwsQYJOfEuCT28

kU4uFin6PKEuBEUJNAktCTushSEgoSkhOnE0cSGxP3E8RlnOMQyKEUchOXEmcS6JPPEh8k7OP84gZRqi1PE9iTAmOpEkMc9/GL/A9lpBKcjfXIWIGndToTHSW6EuDRehJw/NHIJJM48RcIUGNS4xYSUEUUkr01lJLVXAPgcRMYgeRU/RKo1AiTwhPtRTmCNhLYhLYSzhLy3XTjpSCXqQdIkuKhEu4TnzHFnbHJgJUaTHFEF7R+4ADwk01ubeGk0E

j0CIVJECjwdBPJqMB8kjhJSaQs472jC1E8kkKTa2nPgcKS+/kik1UTopO3dfLinJJhE/AE3/CnQZKTY0nWExESLJOREgkVPaOykwajcpJ0kh24cRTxEy+AKKkYkrISd/BngokS24mJSFiTpyIyElzjTOI6E1PCxuU5YUjwCRSM4zISZRIEktkSIeGjCTkSapOlEsukNFDh+VFA04lPpccQTr3f+PAJIAlpaLziHBPa+JKTSpOs48WkZpJWkhkw1p

K9bGyTNOMNE8Y1ihKaISOAGDiR4UG1LROvo9QFfOIHcBzitfGGWHMSyJN8HBr81fyi4t0pvWJe4xwSQhFCBd6TaRM+k0wShmK6YiwTwjRQyf1g/+AyGZ/FgmIVE8MSVDWxEomB9JJRuKI0YZLDEvzAIxK+RBGTKpIMk6zC2OOOYiPA4JXykk4TsuGtpQ5jIJPDGAmS9OXeEnbpuynA4Aed+OlRkrxi7GAlBdLpBIDikhkZAmNA0Rjj7RNZiFz1Yp

ImgeKTAmI2iZ6SUxNek5JDXvHIsR/QIuHl8K6SVhJuk8zkKZMu2aWTLSIZmAwS9OLsksEILGQq4r2wd/EEET/c8hKqE4BBqJJkZbWS5RADXTWIBvlqkmUSWpPK4v+ckhV1k/slYSTuk+ziWwATYAkJTZJEjPWTYSSQaGkThJI0UH70UEn4kQSAgOQ7LDzjiROakixk4uKDklzMniixE3STEZJoZfETJvWpmaRwY5LwMPKTjhJ6QXnjjxIfKFOSEu

JDEXf1qZNuEphiMpJBBHRjc+n+kRzBR7y0+VJor/CVkttdtQXMYinUcXGQ3Jv1FZKlkhuSw/wCCZuSrGN/XD2SHZNuWP0Fvi1a4+UIpPn5zfuTzZNMY42CGiGP47VY9oGPKCeTIUEHktc1SyQ3SfVwoKWU3C5izZKXkqeTNpiSYvDdpeD1KeODF5MEEXeTO+QG4iUQhuI7LbhjJZP4GTuTjUSKQQbj/JFI8NuS65I7kjfADsO/I9tDfyJuPCQBqg

FvQRbR44A4AKkA9q2AwJIAR4D5cGyRUIHAwFoAE6Oy7EeNZ+NGFMhcyk28Yblg6IHJGT3g94F6QfcgmjgY4YyTlONMkxCRTpJjWC6ThqJa7P7c1n2ebYOiYSPLA9OY7+NPQlaCK8IEHOiiX+PWol7DdK3mqTqhv/yfQ//iAVGGUbAgOxkuzOk8sd0IfCATaMEHwkcDoANpLcSi7qNvoind3xLrotSJCBJxYqsSiGNUY1hYFFObkY0w7kk0U9fJyN

gLE0jjKRPc4l9jZGNBYoJc0BKpQHEVWeg9LGjj/xJ5YhOp5BL/BJDjtxKECTcS7mLHo7qFGZPiYn9ifRjJknDj+4go4mNxTRP8kMCQRuNiYzVil6KeAbqFvRKY4wUobZK+CfDiSBIWyMH1hZNvEsiSSkHD2MwTG7iQyPiS5OKrBTJTgZJNYyIVQhIfoghTMIgKUwTiQZNm9Q6SDRPYwSEluZNtY115HqTikZOU/aH8YFXtkQCeFWJSHRMppfyTYz

H9wN2SxvgaU41pZINoODaSrOPVE+7UBOONYqjjRMmKkyzi1RN5gxJStWKiUy2SJpPeiNzifhKMY9jihWDg/CnpZpNWk4tRXFLFE9xTvmOmk5aTMhPHEI5TOlkPE+jiPdR2ky5SdtFzPExSQWLA4gUShdBIUs6x3eJH3S8TRYTHEYoJiFPvyAQIkeB0U3FjqxPUUsIJAVPOkr5SCRMhUgw5PlKcjO75dFIhU7999lN2kq5TYaLGyEjiKRJEYtZSBp

Nc41L0QOI7o89iUBIYk9ZSFpQog5p04RNJUwotxlMWUnui7FMg4pfpmlPqQVpSPhjFjKTFblMJ+PUTvalqUvpBRRKcUuMSPFOgCfBTp3nKUpe4TlPFYxeDRONokvJTABQlUwVStxOFUsNERZPLEjJSFVOHopVSzlP3yYZS4lN72NxSpVO6hTUTglJ1Eie5JVIlEktUqmm2U45jlxw1Uz5iLVMcUzVTTlOUEq0FvWEfAexTmVLqucIgeROfgbugbF

Kb1LlS9Dm5E8OBfVO7oNYNO+ObzEqie+LUdU7CJAFHAckBd5k9gKkBMACFQQuwOAHOw/UB6ABaAaDA6sHJAPCEniNjwsYAjoClJaFASkHwUTrN0FM9QMOp42F68MUly2IvouWTgqje3eggpRLisP+jWajP4osDAHwLwl7FXmzAfW/iPmx67JaiawOjousDY6IbA4scVji2oj/jba3kQXpxQ7VVvRigtDB3UXxgSSOEU8kiWxx9fMRCJFL/Q4fCYB

IeguATx8OgLZFSlFNpmX5SEvFBeFRSa6LUU09S0xOJU5ASWWLPU8kThGKSVR1TMMAQefAT6iORqdMSgJWvlAiDllKXo3pxiIMDUzwTNmMwkyTiBVKdUw1TQNOdE7ARAJx0fPGSoJICUsMJJhPdoM61u6DlE9ZjYZO8YhhEHqgGE4wTMVM6KLxTNmO8LVRFWnGkEFxhhokdzLJTsmN6U/ITEhIP9P1ZdVJ6UyrEuqFlITLpdiSqwnejAxLdYo9NlR

Ny4LPlONLdE76SPRMJXJzivbkooCEEABBwkn8SwJLJUttTXvUv8e+DdxNnEqsE8VN/oxTTpNM7WNiS5VKpBfjT2NK+YGOUNJMbUuQSqDVcEhISjZMY0g0DrpKbUujTDZJ6bFtDkb2Koyp9SqPRvWNT0AEQgCgBysFqAaoBufCMACqoKADDAOrBiACFQSrAwwHJAckR4FOvvcV9a7CbcQbBRoHurAIR3JnNBSxTE+EwDSrsuZK6UnmTZIK1fZ2TuJ

ITYFtiSwOoU2aiO2NhLPcwGFIf4ntjmFOf46tMXbBh3DNjh2Pf/RqBBIElIaZkxRDLYik9TXD+EJ7dc6NUHfOjN1PAArUwCcLpDEMkbqPpLUFTVFNoYlFT4BIchbFSX1KhgcgTN2NiErmdZD0jdF5SSVP7ffdiKWKvE4cSblMZUujj8xPPU68SsUgNUh1Sn1KboocSfFPu1PxSdlOQ0gtIjtN20grYANKzk/3QP2JyQbbTv2MCAo1iGmPME0TItt

K/Yi9T6lKy0xpTRlMcyB7SrtJyCGJTstNfVRATX2P/YoHTFIG6UppSvVP20wCSEdLtEkHTX1VO0lxShlOB0kZSuWzlY6ejd2SVYlKFmNOR0w6dwlII40gSdWKmU77ShONo0nVS8dPmiQySimMKU2ZSvpN3ozgS3/V5g6ZSftOyUp6Tj6NcIfJ5BIDCUsxgIlJe0lJSnRPE4nFF4NMeOG7TjmLu0wecSlKU4sVTiJMrxK1SjmKQ0lB1VZK6IQwStY

mLUVEA10hA0szT6NNiE5t03VIwEhxTWNJVEzaTJlNm059T4WNfU+TSNNKk0ye1k8Tm0x3SFtPuUggIn9CjgGRwKyRPU5vC4VKAYrHlMGTV0+PFA9Kdk3GB7pNdkhaTScQMUnFSndNyXaPSXZLusRtt1tIfU6d1TpKFEsPSKYQsU91SmVLuUnt1UUHXZP3SHUCN01HSrdOKxH+jxsE00t3TbFO7OACSq9MLbGvTJNJoZevT4tQjU3YsDiKqfXviO8

xVAB2YdjBvYCeAhUFNweUAYFN2YfI5JAGXAGABo8MDcEkZniJBgemAAEH6BMnBKWVjTYJhMFIKKbBSJaFzAlTS6JLU07LwPOIhkmmI30MK0qHDD0IookvCqKNGSKrS1oLidVhSB2MbA2SFmKPlvWoJJtk4onqAnwDKmPBIvoni2EATPXx7TcAS92A1QCAQV2PLotdjK6NkiRbTJtMfY7RSF8kj0mAzr1NoY7sTiOId0jhigdivUmhi4DNr4h4Ef1

L4EvZwCIKwMh9itFNwMkulvVJDUjhgw1KQM7AzSDNahbHTlVI0UsFSuxPgMp7TQxKZk0jTKxOQMnAy7iWI014EiFRhYiihDFIRYs9Ma6i1E5xhPnDlRU9imRPAYLMTRDJNEkzZ1WlrvEL8KDKsUv1StuONUxQzJDLfU5xSPFIqU8QytzmUMyz5ENOv9M+TNEjEMk1TdJS0ErDS0ZK2YtgybDI4MohUZmKCUrQzaFS2UzXTwxkV0q9sFDO1Etwz9i

RMMjjiGOKZ04mB4lJf8BgztVLlLKMTeNLz04NS1DOoM51iRNOjEtutpDIzE2QyU/QtbVVT3BOTg3ISE9Pm0v2d99N00g/cLRPEkrSSHhO1VEITtdhMk8VSg4SO0xMNcNP1EjWT+VKPqWoz/lJZhFpTfgXZUvjjpk2pU/t8WhK1idyT2lIZE+9T/2Ls0yllApMGUzOFjdPq+PpSRsEWVDd8LdKb0z1TaVJt0iZTf9x6MnbZ+pPakilS1jOGMsxSOT

QeUuaSnlLJEi7SrxLqM95S2omhUxFTUOKW0oISVtJ9NPLTBAIGUQLimDJTBZbTDsVZEuoT2RNGkkURYVNbqH2ShJJ5RGLikoLo3LoSZuAOFJ6iRhJP08IgHmAm07gyWmFvUh4JITPyA6Eyp8JWZRAzmfXBk5EyoZPlorvio1OOwmNTdgzgAaoAhAGuLcDBUwGaUUgByQCyIU3B2SFNwFUBpgC2guMCTaKLU2riwBDNcWrcrw0rUw2VMSlvkG14bs

XB05tTqoCWkitJHlP2kiHDu1KhI5y922JhLUiIzX3LwpEjR1JYU2rTkXBh3IDFX9PLmVmJlEGAE658Nkm9kI+0DrwAMikMN1N24OK9s4A2AcAzYBMgMmbT7tPe0gHSqWOsM5zRsNLsM50sBTMCU6XhXDNCU5ozbTLg4/KFIjMSM6IzjjIPYy7THRIKMgi15VJqM70zgzJFU5XTCJJU4pf5/tJ9MgQy+jLZUjyTAzI+0i9S7NJiEtIS0zLtM30yG+

jpU6KSczMTMxDZNjKYk7YyizKjM73SRTMOMhwSKzJ20gQzSzLqkzZSvTJOMz7T1pJWM+lSWzKDM+szhiwLM2NIcTMjUlzTo1ObjcDxTcFIATcIkgHqAGAwhAEwABNTRwCngCgBokAoAaFVvGTaol4ingDecAOEmVHkyG7c8+L1RMIgWwANM9vRcjM908LZ/ZAexabML+Nmg094L/xRPOhTB1Pv42/8R1JWomOir0LYU4HF1TOJwQBcRJE7A18xoc

XCvcURshBGIF1RgAOuzXvDRFJAM2bILtRLo/9DjekAww9TJwPRMuRSgMLoWJCz12N8GNCyIyUOw7vj8TJHM3ehRwAiQKZtKgAj8YgAc7CFxTQAebB/qOABNADf4qLSxXxeIlzQyrXL6L4xjlye8U1AIuO5qGEQOsyPM2TBdhO440+iBXUjoEEyiCHkgEyIwTWWfR5ttayv48iib+IrA9y8KtKfMxHCltWRwxSxQa2LHZ3FMcIfjVAA9nGd8JHdXz

DWUY6CthFDYcrDPa3XU/rSTTMXYxSBhtRgsvdSxKNXY2RT0LO/STCz+Fl0Ugli0DKEMnFTQInDOVyzPxJKhHgTUjP4EzAyfLLqTfPTLdKWMrgzaDJrE45TFVOdUxeC3omYMj8S2k3l0rXTraWIM6sS3LPsMx0zbDIQ3eKzYDKoEtpNedPp0yZQaDJIMqKzcdMR06HTSajSsohiMrL0TTpSKrMx0v38PdIwM9HSfRPmiUHTYdNMU29iKlJmU37SGW

N2M7qzeUj4MolJKwlCsxYytGP8MiCT/FO108IyXVN4+WazF4IWskKyFjI9UovT50me06nSh6xSM39SWRLdM3qzslJMaZqybKAfPTLSGrOY40IzoDISMhwTRNIY3F3kpdO8EiDSBpmcst/CbNMIYusy2zItEkzTAeHesjMyUNJjMqozfEK7M9Mz7TIOkhoyS1DqUoGzczKTM1ySseV1zbsoWeJwqBMzKzOmM03TszKeshKzFFKD0sDZKhKzM3esh2

xxsizS0bNMOZ6z+NIWUwsz3LOYE+FivLOWMkqTVjMOs9AzjrPSEq2TJpIusu658DMzErBkqzNL04PprRLUYyvTwrNbqB4yHpOeMsIzzVO3E4oJhpMgYsaTJrOtUlKzUsnoSWppiQn6YXmDkrM8M7XThLMVssSyCoK/kxWif5PEvCAwKAFYjUgATpCt4OrB4eniSfQBmAGWxeUBMQyZMk7d6IDWAX14s/G0MGNlgBM+LMLwCDB5CHdQijDLURySS5

ObAVMRsRMDEMAR33DrU8hSA6Mv4oOjAd1ks+8yIHz+rSrTnzN7Y9aDH9InUsexra2bHFiikhXapZPJDqJlEEhJQPkzyH0k86PAsy6DILNGwKASrtTHA26jLrOQsw9TcrLhMsqz2ryRsq8S3MF+MlQz+bL5YpfDCrKqU4UModMaUlnSrTMJAqIzPROP3YKzZZJ8CK0TL1LHs0Gy9dMGE5hF+SxaMvTTKJIY02YDm7L+UvTTGzOtk+d91jPOU338y9

PcqBlTG9NWs38lJbI5En4zINPtU8Wz/dzgYuZoW4EDBKXMNdPJkq/xcuJGE8OTOPFZs4wyprJ2U6JiaslUkhYTwAiQ9DazklLrgoOzsGKlIIYsySho04qzypKwY9BJwHIMCSBy2dL6s3+z5hLQYi1Aw1jJ0jqzX7Kak9+zFzj7s/HTeA1TwzWyxZWaQskdMHNfVIhJMkBGk5nSWiAwc4IzydM4kvzjHjImM7ejh7MDwPTThTO5snBIBBMcIthymm

B22eZSopP7MksS9hJ44txiWVNaEuGyqNJgk/iygNy0FUVSiJJwRe6zwNNEE8eyr6KbUkcTYNIviab9lHJEE10SFJK+snc8+LJPouRy45X+sspT78g50njSR7NepPDSJaEGEv80EJN9YsTTbHOLYowTi1GCE4xyhdNMc3cpyNLaEqjSYNOl0rCSDBXWFGGyKNKwwKuY/rMqMspTw9JyyZeyP6ImtMRI/HKkchzAIpI7MlKTrdNpszsy+NWZsjqS8V

K2Mx0kM5zakssz6pN3srhyY0TgNCnpynN6ic4yBBiBZdbjEYmz00oT1uMhoriTmHLj0tWkhbNj08v1YClPs74zaHOcqPpyaHN/Jf4z4GN6Qd3A/pMe3Fogx/hALe/UIuNqiaZzxnJzkwkSABDfs5F55bIoFUSySHNfpOYTXYn/s/uDQSQVsvQIlbN6vdgosZNxEnGSNnJEssnxtnJEKc5ykZPxEpL0b7MWc++zCZM0UQsQQx1bwjwIhnMaE9A4jh

LIYmZR7ElacphyHpLZtPLiPhOhEgOyubN90iJ9UGT9sr4SoXOr08lTCnPoYiFz0pMRc/Mz0nOEc85p4XLC4jH8WhNhs0K1pHKpktKT/bIU48xzVdJUNXFyr+nww47sJ7Plkkly0XLJc5HMuOJMc2li4XKLkoESaXKCMs6zmdL+c0hjL/EBcpS0gZMqUopS3nIBcz5zraSAc0jpxXMFcyVzwJMoEhVjHbllcj5zbA1Jkq1T5WJnowjYA2NC7INiN7

xDYtzTdgypAY5hL0AoAegAqQF/UDgBnhC2AABxLHEvQY2BUITXMpfTwxEikUnxKnlcmaqAh4i1MebpPMm1SctjbUAZqMByoYBerFiF/jJFYYSTE0nP0sijkT2m1AdS47KrAhOylLNidFENlTPk8Ysd2mU/M+mhbxgGYEQReFLq0N3QHvj7vQ0zySxEU0uyDuCV6OtSbLKkUnQcZFJrsxyyodTREt4yMEjB1V5lF7MvY7qZG3NuM94z+yyddC2Fnr

PgAk8yMDMpbfyydrID0EPNqrJQM1gyBCSmMiKzSrNQMutUZ3JMyAUz3DKfs3ZT+rKQE+HSZbI8MwIyUdKPsplSJrLkTKByOyyWsnqy+dIZ0inSxdKp07ViM627sopS9rLPc+Zj+OLp0qpSrHMQklxz5DKQc/nT69gwkkQTZdL62W9z2dKicsISylMBszKy4mJI06GzknKJc1Jyt3NXcrwyKJIJs1IS8bJO0sWzGDJb0iTT21NPVPbS93IO07gJOH

Jhc4YVnlPZstIysPyqcgjz/dNhMyKzptOCXQUTmnJFE4EymnND0soTR7JuMjDjoeNbqRjz6nPo8iMzWzOXBKkFAGJKEpjyGnM5U/my1rI482jyhPO4811TF3IopEvTyPPL0u1TdDIiM9DyFNPIoLDzzMSO0TVzidIJTLKSybOxc9uFNPKJ0xVjuAnicomyDPN+EuiVjPPqM2eyCNNBeaVzXtKA80pSxVNA85u1KdKSU1ZTv3LA039zSR3heezyUl

K8c/YT2XMw04gSVlIc8v0zrrKSM4LzFWHc8sLzNVmfcsVzV7Tc80LyfkyAcoDSovPF01CiwfRPcxLzL3Ji8sH0xrI9Ug9zzPMVcrVyMfzXswHTO9UM8v4SrPO8sjGy6DIvspTzHSUHo1DzlPJQ+YKyGvKFU1rygUkHcoxSOvK1UpryLUna8xTzOvIG8l4yG7Pnc5iUWvNG8pGZl3Mq8izylXKj/XdyC9M0Y6Di5vJK87TyFXK084zzriiq8yzzHb

nvcoqzQZLeKPzzrwQC8sRyRdNXoz9zz3JdbOlz1HLespjT6HNB0nlT8NIN0wjS3insEjgSHGDwMR0MCXPCc+GyzqTO84XS4TUEcnKStpM8bH9yXRIUgdTTa9LU8nzy0q2WE+lzbNOhcncgebMwuBRyxG36JTjzhRNicsC5+hPsc/NpXzVs4kFzY9JFs6cJfvP8cyJzk9Lac4WzAAVM8m5YJrSJ8mPSAuJRFXTyhHN9owWyU9Py0xRBxpNU8/+j3+

2p8knzAAX6kl3S+fNgKLHzc9O8uOTyUfMWGMpz5PN5s4vSfdOl8raJofLb0x6RCN3w8pXyanJRs+zTkPO2kxXzIQWV8k3SdfMCcAczu9ODY3vSCTM8ZCeBNAFvQO/hsAC58S9BB811gA4A6sEQ8TEABeUzYpfT2ugy4czx2HSgEJfNwxGHoRXoBUgtQagd342Ak3CTyxJDcyOhMuK+MJ1QbWlwES8yKFP3QqOzocKv07Z8b9KDyROzqtOTs1Ny8f

AOAD3zGtJ2o7TwdGncRdijXMANdACzoOlX+NdTQBNLc4Azy3L0aAIFboNZPfdTR8JQs7K8OFiOskQyGrxHcggzWogTrQ8SivIUwz+zZbNMMmMsVVLSUlMT1VJUw3JSwzNNQ/UiEfLu876z0bLysvRSJHP6MktJBjJbMymyh3Pk0gpzmzJ483fyjFIBU+FSgVIukqzSiVI3crHlakCec32TATI6crOCZPIpCe5zE5Oqk4bz+vMXg8G5+ZLCky/z6C

wCMtdzbZK3kz2THZKi8nQScNKq3MixX2WbGBPlEHNFc0pjHEN4KFrjsGLo5DriHvN5cljSkAuHklAL2uLMMoez/TJHssXNcuHK0OeTu9GE0iLzojPbSO24RZnj8lsIZNNQkuD1qArj8wZl8DHoCsiS4PSP4kgKtliNElMpSJLwk52DfsnQSVAK8AtSU2CSo/P9g7uSPqF7ktgL+Atzk+Ljg5JFggHyI/Nk08iTENztknWTzZNRM0QLI/N/EiuCf/

MDwXySRHJ0CuTTl9wPSIII90AecYPk+AvEC1KTxLVpkhNgfVWwsvEzvcMt8n7kJ4CgAU1hXfKgACJBku2qAKeBnAHpJckBL0AiQXnJ0cPn0pCjKb350eiooHXqbG6DPizWyfuJ5fCFta0U4xA+8y4SuBMIo1HhN5IdqEAKLZN3QwY4pLNT8y/SY7MEhB8yFLMjox/jFTJq0lHDWmRlvEV93+J3DWdSqYGEFeRJWqEr86FtYoD/oODRTqIALASjIL

MKiUsVd1Orczsda3Onw+tyHqO78pJVrjNeMrtzMRPXcmQzArJ+slqIC3TEk/4pSjKfdDPSRjLaM1lSOjNTMkTycPMwE/JySnNlE/YLlvMOC/nzifOZ8w+yzgub0v4z5nPDc5M16RI/82Ky64N2c1BjPoXQctbytvNnohETM5Msk5ZyDll28pVyrbW/8tmSBZI5kpVNCdOq8n4L5Dnbku+SP5PS8q9yPPNo3dQLt5K9kuAL9rOu80goT5NAC9AKMd

IIc1+Tb5P4kBEK8QraszAKxSmpk8wK6ZLwCn1J2BPSC7nSM5K8CYmSHqgBCo1s6Qr3ojIKZV3jk7GTkZK409kKudIDSLkKKpIuc3kLTfK9wpWjXAo7zTQACoCDA+oBqgAQATHop4EvQZQBcAGqAUcBDqDDAHgA4AFosuHkEFOQo1OVLGNj4RSAvSU+LF+g2IWlIbokW6nrU3RyZdKvDIHxX/Kqk9LZw7IKC/7ciguv4u8zSgvjcodTGFIVMl8yx1

LfMp/Tix2n4zEitLPnzAtzf+LObdoKuKN4AKux12VnYsyyS7Ib81XgB/WsjKtzBnGkU+yy63KgM7rzXTMG8ury6GOw8m4KBbKcs/MKJvPmsqbzx6NF0kLzANLIE2ry1/Nqsp9yaNMQCmbzIzJbs3OJT3Pp05sKh8nWM1qykdI6szYK9jPOEznSvvMFCpbywrM7st9Md6M+8q4TsigrC0wDAfIOEnQyRvITE5r5WXO8cg5wFXO3c6CTTWwh8uDSWl

QSZL+z8ZIu/K3YFwo3C5lYAAspk1cLBdMC8x38QxNy8lZSJPUnC/kKRwoPou8Lqwqzkx8K6rPIc0mppXM/C8yF8HPasrlsAPN+0jsKN6K7C42kj3IzrVLzawvWWSCKqwui8rVigNJ5c/EK+XK2U74KrbVOslCK7WJQ8mKzoNKus6xz33IXc0TzuVNPCtxiiOjhE2/zPrMR8+7yDYQoiowyKjOA8ylz6bN48kGyyNOsElJyEbNLfEmyQfNt03mCJ3

Mxs8TT8VOYkmCN+IvhMrGzZPP18/eyeHIj0/MLqPMZ81PSeJMo80qy5Ip+c6WzibNkihEy7guec9o5XnIQMjSLxIqXgo5ytnLfnUhzSd2essOScHPGE9yzuzI+slZzsCEsi0kTYRIGsrxxmc0akrzjcHIr0g4Lbgsfgv+y0HMf8zWEVrML0wn5kuL2cvyLw1Kc0hWijsJcCvCy7uBpMxUBLgB/YfUBkklfEWdETpBVAFoA2SCdciUkwuBRiIRpME

0MvL0cgxxMFKyNRIk0hGAQ5eICkQgpUNkcde0KFXCwqOIRJ+AZKKNzz/yLw9Py4SMz8hEtfQqTsh/S8/LUsl3zmwMv0BDhCoh8dZW80mKl5GUQ3ghLCUYgegozs1YRTTIvwQYLoBLssiAyHLOzC+CDsMkMqdjCfpC+iB+cGrwqi/BQF3BUyGnSL9k2i3EI2IhTnCYIqmizUQ6KaUDrZKkJm9FpCc6K6JUjGZljSov+KUNgyDLeyU6LHotlRD/YOM

yc0T3hKmLB4MyJvoqaCX6L2EMJAgPR6uif1LVAQYoh4M6LwYtV3KjBHbO2if4pO13qdUGLXdAui8vYcCBPyWvZeZ1jaTGKnor+ilmFsCGsXQ5xMyFfIk/Z7osNXLGLnorjNVphSfDh0dKI4YoeisGLfnBJi5PS2lJdwdRdZlzAuGmKEYo5iiGKiEjmyM0othBDYdQErovaSWgpqorrgr+USxSPkrWJsJOcqKWKA9Cg0Fig64McCcBkY2RLWEH81a

VViqqLEYBHHW1B0YCgEBqKl2Cpigvx9orVi2VINYq5C02LuGgZGGtixQp/IpmtxL1NwK4B71HjUS9AWgFNwCJAOAH9i3WihUEOrXAAtgCHY42j7bI18GNhGGL9xTSpf/ycdH3x+pDYCS8hRzBhgIaDSEFjmZiF7sRHmZqLpLJjcucM5LPoU+HDh1KTci+Nga1Us1HDixySdIvysSOj4GV8LtXa0/Y4cxW2OGaLYr0ss81cLTIPUwez9BxziqEIR5

hdi7+S3YoxvBsxpgFIAcrBnAE0AGAAwwBSSJSgWgD1kfUADHTH0rKLHcAlISUg1BPB4eOKj4AgKWNhf6NlSA6dN+JzIaYhHI2j2LOAs4oK4H2T3KlcobQxfcET83m8rzJ7U6EiStJlMs5RytOLin0K8xyqC3Pyagr5VYsd1XRDCz/jUAGy4QjBtTMfcA0zDLMTlKRxa/MAMsASBtI0HLNcMa1G0tvzq7LGCtaKsQjZiumLOYvrciqKvlIPICDQkg

mgTC+LYPVTigL5mvMMQFw5vzAoMNc4BYp+ioWLpDicFLuVsWlIqVFIiYsRijqJsRCnQX8EhdD0o/aKWiFhIQPB+Smz4u+0fUF3HJNopYt4SzfB+EssbWQouFylKKRieEpQpI6K62U9tLtIgBNSMcmIxEoUS26Ln1lQ2fCRh6Ij8Iu4P4n8fa+LbKWiLHAg7rXXwSDZJ2Qi4y+KCWh5Ey2LSYrPNQxBm7CgYAxLmCiviuxLqOXBgRxKT4pcS0FZDE

vcSreIO+Iii3EyhzNwsxatd6GLHWoB9qH80mtwhAAkUDkhfgHcMQgArgG2zO2y/j39EFc5urVfgPrDRlC4Uneiygki8AZjTTDQS6+QwuIVEY2JsvDSlOmAOaQ0YiHBnQofRQoKqFOjsj0LZXS9Cx8yKgrv0pHDy4ofeWZIDgFts6dTGgsxcbs5xyM/0pdSNkk7QYFRceV60mK9LXT+qCIEvSTTC0vIyHzHw6cD7otKSsARykqttC+KXbO7MJ/Qp3

NZ3Qyp1ko6VM1AtcwmfHVAWEjcCSxNbCUOSgmdjkoqS5I0hGgz8DBJEfnXdG5KHWzfgE5KuNTzEfeQFshcYV5L3IjKSuuwrbQ2ieBIIXiAyV6RHWzWS25KPkvuSx51ZsgkSIQQEBBCcswk3ksBSz5LWDgDaXeBTKxSUSFLUUo2SoFLSlwvkTVlJohQaA+s8UruSl206pVh4GX4AKk+ihDooUveSzZKRQi1iqZduaC/ELRpyUphSq20TYtlIR2LGo

vsSphNOUqZSpv0zUkfvPJpUpxRSgFL8UvRS+KJ1OLP5ZYVA/CgjRRQYhC3YjjSoIztuf6QZ4gBYGh9Npn5BZbZrFRkbCfzw1SYgHrkakv4UuKMTUuqS34xzUp1c8AdBzJ701zTO0KordABTcFTgaDwUMD3mFoBgMEIAZwBBFE9gT2B1ABMcZeL6IGkCVCi1In4RUaQAxzo8Zq54YtWlCapo2EfBW1ofzBxZNB8gSyqStH9FXGZwXOK3QpkslpL5q

I6i3Mcfmxz8nqLv4t6SoeMGgptrTFwq7Bv8+5t8SzzciaK8oTNiVuLZkrivFuBwtkWSisV4LO7ijlL4YpoS7GL7qP7HahL2Yv7S2uzYCiuinBLWQg8cBz14/BYS2hK0ileigKR3oq/EKhLZ0oui0USyEq5lS5KREvkSm6LJEvMxPKKh9GtyJhK5/g0S3dLjouBTdhKqpWPlB2RXEpsSkEIb4oESsMYhEr1KXP8L4olcWxLAksfSzzl62hfSs4YQJ

CzWC5LSIAFSyCdtyAyQKDgN+O98f9Lzkq1cIDKPO34KMFK4dAhS95izkvISrdK4MtBSkkpwUqf0W9L30vvSkxKBqQh4BqFemF78FEdT0r4S89KQCORiojLn6WPY4P5CMv3IYjK1EpOi3tLh0rolbRLL7GR5ESR2iTfSoxKPEvYygAD+Zm8pB14D0utSJvDMLlF0R+j8YpO/SxYAYujaVSR5fMKFM4BWmBhgWsppMotbDDKr9BiyNPil7yUyyTLVM

rAFDeJ4UplSLHjMkF3KMmKlUgpiqLEyfKPi8mLnEquS0JzzMqcShoVdx1oCTY47OOjKODozMu8SyzKgUwb6eDQmaC4CAgJcNV8oxzKfEt8yzA00Y299ZmLndgcy7zK7Mt3HKzJMUtowJyMdyAUy6zLQsp8yhLKqUrFi2lLPEpsyizL4ssiQ17x6pNAQbFw7dNURDLLCssBCeWKZQQwSJWLkUp0y3GKVMppCMAVKQmAsnWKRGD1i5WNdMrxi/TK45

ItFTTiH0J/ZJrLYf2sXZUoxDjfnf+hBqL5w4e8esuaysbLAQl6CUkUfeAWtH6FTEuUy0bLKZhFSlukA9HFS6osJMt6ylrLiHmNnGLICeP1QXyzwygOy+bKtstc3e5giWloFTPxOIsuyubLNsrUyvR93nG7MaXjgQUayjbKpMrAFPgp5RByQJ6JuzhECq7LXsv+yobA6yglcWMLHAp1sqKKJQpiiinQjABHgLyw4AF5AY1z4gAjYw2hWQEAQaJAtg

H6S8IK9QspvL1gaUEhlRNgXaADHCigo5nPKXtAB8ndkE7K4sFqiNNtBLIK4NBLaYuJi+OL6koNxV0KmkrT8koLWkvDo+OzFLKYU+/SU3NLSyPIDgB+Pf+KmgpccHrlNOUMrDmRwOE6oV8L5eWgS+vzYEqIfBOMEEqezADDqcO7SwmKpUo6VUmAAGINimWKdigZpAhLrEp2S96KFRFISgDKYMsoSlRtQ0lAysBBeFSoBc+jXQQQyrTLPfnPosHL8Y

swCdtzPKMQcMYUqUgyrL+jhKmlk6CIGRUDyuI1Hpy4YElLCFAAY8mUDothILeBaMpM1drK44hEYQIMkGImy1uBbhXxDety8YHsKKnpaAryojlJV0rYywlEfgCw4XbK7mOduIdKMEoQIsG4Gcr6YL4VshD1aRvKOcqRuVvKtYnzxIwyZ0pYypvK94icC0JLoovCSu7h4gGOYCmgqQGqAcDBzcGtHL1KoAFAwAqBb0AngOVAM3M98+EBnYjmkpXpSD

H983JKYYHNokqKDekKaReIBMr0S+5tR3GTy460Cii/FbNLecuKCvNLO2ILSxEiP4r9CpUzxcvxPSdCK0tmisZo/WIdkcvy44CjCtW9cGNGwVNLpku1vXoLzqI0HYsUrqMrssbS9Bx7S9BLu8spba2LDYtYgC3K10gXS9IC9kvcBGmKoNGOSXiI7iXoSomBGEvaIuq4cCt2Sj6K7iQlICN53/V3nYY1SCsPSh+Z+Hx0WPBVQhSZwYHibG3i4aJRW7

CyEFVstCN9SF3KYYogyzQ1ZMq/aeTLHW09yzDLEMuwysNENMr9wb3LpCvgy2QrlCtRmQjKo4Fo8dGKTwtUKzTK9J1hmc/KEUpMyhrLStmUS6jL83nDbfLKnMspix1tzCoYymjL2vn8y5ui4RC4YFQrFCqwyzs0I8siMB+ZmZAHxDwq5Cs9+RLLoWGSy0vS0striZ3LoYvAyuMo48p5i0lKadWl4FApbgiPTEWLhhhpSlqI6UpYCOgqBQk4Sk6j/d

1wAnCiyspVs94SGEqPSigq5nIKKt/UiiuOUjdLAMsdy/IqLpSqKr8VsCoAcxdKIUuNMJL1KitKy5oqbONNy9WLL7E6KxoruivTaa5Kh8tQK2oTRYsrWXLK+r1iKjWl4iuBMrP0jLWxS+JUZMO8KqLLmoBiylk5K8swS6cIN1ypQFwqgstMiszDtiohisRJKsucyk0MTiuKWF7K/sruiq4r1ZiMy7VxMuFMyg3KUCsRijQrPpC0KtGK2bXAyGQr9C

ohS4UNIis6g2WdwIPuKmTKdGkBijNZMZV6KnZKMCoGK5lYRMvIKo4rz+yoKpdKOioRKmKVRMvw3VqFtkrei9orPfigy1DLYMpqK+3KKEvCykoBCSs3S4kqUPNqKh3LySv6KFDKqSsoSgeLdbKHi9zSygFtHLRgcjingTHLlAG7QB8Rri09gcrBNADgU3ULotM9HIdBX6C4GaJRttGmZLeKojifgdDBWwMqlM/LTyAvy4Yor8pYhWYqE8sIqB/Kk5

lLAmhTQ6LK0tlU34sTckXKuksG7QMKDgDrTGuKtLJVcfAwIMSydIKQKTyCqHwT4wrr840y5osXYiTR4CqDrKuzxtKSg0RKXbPESxRKNxR4ygJKH0sDKggdMSqRK2fZvjg4Kk6DJCr7kcIr1oq+eKjKHCssKtIcjCuMy54rTCt13MEraUgOy12oiegIIZAr2cveKl1ovEuPizLLWoWwSpyNcEtqQcelE0rvkhaLiUSECOsr/pEnSwMQNR2cK6aJDi

pxK6xKiEthIFGBn/nlWdYq/CppK0kq0MtlZDrolipSynFKmUkRKsorV+STabUrgsiFYVMlsio4Ssh08ivVZIlL48vXKxHim8UESn9KWElIlbmK5io3K+NIoYuBK2eNzyvZUy8qjyua+AIr1CumHC8qdSr5ikqEQUtGwNQqDCpnKpLLgWDCKuwr0ypkKSwrRytoFJmKNiuPLc/LWiEvy4f41isgqicrX8TVK2CqNSuH+PYrgxD7KjRRkSpaAmCrdE

rQqnsr9iqwqtwqWSvhyvWyMb2dTAqA6sAQAKeRTcDlQeIBRwDeAaJBxTAQAegBmgAxItJKL6A/oZIB9LGXSxQcCosTiiPh/BSdJJdQw/OxgXgrtyuvSpW9UrHPlbpAgJSJha0Uucu9FSOzH8vdC2NzC4rKC00rhcq6i4tKxcori2oLGwNSSgZLK0rG7erRFKi7TRMxVekNdQRg2Wl90EaLICpAA6AqILPLckkMK7L9KxAruxyXw53LkNi6VNSJWY

vLK2hKHivqQHMqkUsli7QwJ0ulRbNtiIQCyx2zsKrCqrudOysiqwYqSsrvykYrtwUZKuor6SqHiZrVL8AhQfiR8rkpKzKrdxwBygmxiCiLIC7LdWIyqukriquVS3qRVUq+Ya4olytYK1fkqktlEAZgZlGhOZgqsSuPS8NUExBnZfwQYzUaqmMrlyr6KGKxMyEUFG6IKeN7gy9KGCq4S1biGrRMrSqLovDYS+grcipvStLoaYCMOCsINQjh8oicJK

qvSxgq3LRIgS+RL/HQiA8i9qpmqtaqTGyWFS7FNGTMCIarSiuaqx7Ybqvkq2eMHgLeKLqrYyrTWF6qkuAUqjTdR8odS4cyJ8op0T2AOAH0AISAWgBfAEeB5gDgAOHpysBaAfABlwDHgeIAGtIjiryQ2IU3iMX853AVrBBp+yVgVOfwfTjrsPCjTs2EKqIqQSsSkT6qRqr1K4B80x0NK0rTZTJv/DpLs/NFylSyekolyx/NpcqGS1xYgJTF4XOyHI

yyQYpIZuwcqsCyycJgKzXL0xE7i9vyELNZio5KoHXAZZhKxitYSlWLYSrNypeJoFTIyiRKKMtbqPorbYrT4PxK3Eo/SyMrM4VRK/ErHKOsS3DLjEuAyi5YTarwKmYZCquqqtS0qqrJKkRL7audqy98SirGgOcBh+mheJqqxMpWq6cBNV0IqZQlGol9q7Eqv0qSKkKJN8B9q4aqnqspjEQroiujqx6q/aqkSsmq7yuQ1UOrSKlIqnCzx8r/Iu7gZU

EIAeYBCACnga2hLREvQegBJ+LHQ+klNAHFxOizF9IBDU6V6qQNMEX4b5jEgLEQJmjosG2Rl3l+KF5gUvjVGQUzg6AGy/TiH0OpquaCn8vUq2OzBcoTc7Sr38u6ivSq2avxPdEsXcRMqiQcmVyRFIAr04H/MjoKFB15iNDB/3j/zKArZovzyC59/9I7S5K8pav1yzwkCyvrcoMqEquVys2508p/aKDLMIkEA6zZSW32JIRoJoFSEX1hG/SZI7Irej

hnwBkoQLNHSgxoEyriMU8rKwul1KCoZiCvgJmQ+T2US5zRcakgED/Eripc+HRLOMqEy5jK3irnSy9oqysIMO6sxhEktMIINatDK/aFg8slIItQ4sC+chkraSrdq29IMKqrlY3VIAmEymOrk6sx2CPKqvRF5eMR/oohKuTLkytrKxYrIgwXcQKRSaiBKsDKQSvbKgRqFJ3GEBixhlhfKgwqJGtnKwRrpGrXXRq8QKtUSmldnRmCKlQEVIEdM2GYiy

rACEsqMZOJbdhrCvU4alRrXMqTS1srPMsvaExr8MmnQLhrKsV7KwLK4qroa4iEGGoXYJhrHGqIq5xqSKtIazY5yGrIubOlrIMZi3wqWYsPaCTLzEqOwHPpgiUiyxCqwmuQqtBrBMv0SjFKQisAq33SUysphZGKEGrQkVuiUmrnKoCrryo3wG2QdtFE7d/t3ysPKz8qcWz/qvlEKEpBISGjymt5ikESzkufqg8pX6vqah8qPyol2Dsq76sbK9priU

oqaoozBTQAq5YqUyrQS2gp/dCQdLRk8mqxS+cqViuNqi5j0lRTk+0EtGpmagprO9UeSmpxlXHCq0TIEKtCazYrpqvrpQOrO0Fu/XZq6SiQq7eibyrEatOrCiyca2KrfGsd+eBIJ2DRQDDBJokppNzKsshTSncSIeD7Meo4AcLeayxqPMpuAfjLE+Gk4cgVsOTOKuLKLiuGylUhstzLpHGLWmGLKnZ4jGoaIo+LGTFY3Bip4WvGaAxqkWo8RZsq5H

Nr8B/DsyqeK0KrSaXg0DhhRxgRCI5N0V0+kDMqSMtZpSPKAvnnALWl46vEa88iGWtNcJlrwSsTKoGLoSokBWcrVmvSas09vkv4Kv5Lc11tpPcgr3TwnYiYnarQysBjQhK8CUgxrrFr0F6KDarwyq2rvnPlavQ85SH38cCo2csFitdLK6VEiOTpdsHX/GBjk8uNavDwG8s2iwgqOg12inVdisota2GAzhh3S8jLzaSpSrVqlWsD4dRLgys0SvdKC6

T/tLwQaYkiMKVq32mIarRKrAXFaoNrpeOoTa1rZUiIK2pBZ52Ga2Zrd2NH6JNqgKtTSFBq2WrbXRlrPhhdazWrHyOemLvYOWs+GcMrDavwymhDC2qF2YtqEihla6kqbyOpcItqieSDeEoqyCpGq+lrs2urar5LshB+SzWJLH13XMlZG2ujy5lrU6thirNrB2s5a9TKfyv+K7TLfMgjyjtqm2o+KlRLGMo0a/tqG2qrahdrhaVxixFqWQlQNflrQi

sFax6lzitsKsVrUbijaofQPdmbK9zLPmrlaubIPWvUXcCpo4u8au5rgsvOaGrKN8DYwL9puAlOa6LKwXJYwWUgHc2j4OaY+moPKxpq4JScjfPLYfRdpV5wGmvmKim4zwR2yjfB68ols+VrezEe+YQ1WQTuytB5oMjEZCoqhitSq8rKwPT/nXgJUhEi8HYUGipSqkFICOtoqDVK9ZXfUqhqQrB36ZJRv9GZYr81ZSB7QBxhN8E/OBjr6Ej2/AkFH1

ONS/xwrUszSwRYasqY6jBxwAgK5bHlevG8NGmJqssb0N+BxqD46mdYihWp6IqEjjU6Dcjrb8so6qtFUHkhYIxC2WgEFTTrCip6KsZixzDmIWJVDOt6clDq3EHnwdDqluQpGUi465gVs4Dq4iqvKpe5UMF4eR0kkmVUXWJq9mrZtBeVPOqSMSuInCqfa1wqX2uYlDzr6MC864LqqDXea5NKFbCBa9zqA+Ci6oLriMExauaZmxhxa3WJIuq1Enn9Sw

SJaqWISWqS6rTopHW86xdqLCrpa+zqzOv06xjr4kVJq28rR2tM6vTqUQlq6rtq+CsIIAQq2LV06xzqLOqwgymrY6qq65rqnOss6zaZzat4yz9LBup66gzrj4LDav1rbUW668zrpuuE+TNqmuqm61rrMGoCqg1rCqPOPZzTAarCS3OqKdGIAAtx6gBaAfQBL0EWAfAAjHHsARShXfKc8YgA1TK3ys5titxMiDupE0LAiMEJh5NoKNDdE8tNMDUxRU

rryiBIVa3q7G/LjOpUyEeqbzNai/nL80tfisvCEcPNK5SzukstJXpKdK0zc5rTqUDYovEiJeB3UAgIzKyLsvrTEwo1yl59fMBPqofDhgqNvUYLUyutMjaLFasCqmBjx0vrKrsqxeSp662rE0h++YcrtdLRY5pqJsBfqt+cVG3oSz+rxbHM8c8D9KUVYiL4NyrI6H/wCCrja21rMityCUXqjmrMS4oJZuq1q8QrOCtjcJSFdsLzakhq3CJZa65rRu

ptqmgq46pHasQrqGqnKutqU2TkapDLMJlra5krtfkt6+QqHktfAIBhnkv0CZTT6MtAqkjLmGswwLdRrKFd6ujKaWo96pjKL0u7akVq+2v0LFCr8Kq4y3k4EyojqjXqD2Twq9BrkmrlLS5rXctnjaFrbsjECKLrVAT0KpQr5GpCy9QQSNgvge2IgqvnwYlqWog41MhqOWECaqTM/cr6y0lqPykp6X8xWSkPayFrj2rHa9dqh2q8azCqfGvC6rtc92

rSa1LKYmoHajvqnnBPa/prGmpdNNNrBWpva33QbOrmwdhEymo6agZrQgVwA5ej9hm0DbLKpioyK1+kason4IyIfzDjKTfr0iolisYERiFhKHZt3mGSqrTrqirOcuqLrKGF401xp3RB6poq0queBFQJcRJnlG1Qr+tB6qjrHfDzyiuZIOqSCVIrqUuQ4aYr2CiWy/Sw0DkUHQlKYOrc685oIBtLywZly8qGa1JqRmtfpBAapaDLy3bDLLnZauaZXE

Kj5DAb1HmY8bAaMKpiqsLqcKoL8YvKkXkwGpAbsBrxa6+Q6LBv88zl/usQ6wHqW+urKwrLmBoQ69Uk2Bs3a37K6+urylgaeBvgxEvrjCtzK8Cl4Otry1gaRBtlmR4rCuvL6rOrnAoRy4GqtjC0YNgBqgBgAKkA5UAngCJAx4CiSibQ6QAiQFoAwwBR6x7qXCDi4Clq8jX4kGLxW6tzEdurzq1wU6qAMKvJapvqRotSsURrU+uZUfIKGkp5y/Urit

OlM/Wsu2Nv05mqLSrgfVOzwaw4Up7qHHxnQFXpkzCv0Ja1QLO9rUWrnKuTCnoVhKNJ69MKa3MzClBLmepC/BRAhys3wEcrbu2jKukoDLhBCAmNJC2yKwxAtFGOah8T4Xg8Gp/UivQVq3QJpep2izIrqWqXaxwqK8oh4G1q2hswuBPqkmo8lNnLehuIK9PrImuK4NiJmhq2i+Nq7WoE/I+K8Gsa0AhqrWp6G1obRhv4uSP1aWIJao5VlepDnMlrG+

teCI5NsUn8Sstr1WsjDPYbPeAOG6/pXatlavv5zhopa2oI7nRbalgrWGvabYiEXBsuG2G5hWo660Vr1huP6FuRDmzFZAYZdesa6kpsBFML6r2wnI2FjYEaVj1iyi2L8GuL65qV6uquakEarU27/SKLs6uUGg7qtjCgAJIArJEpUIVAqQBaAaoBx83lAIwAJ4HoATQBKgHmAQuxg0up6U8gJ+lMSN9JqjmjSomFm9DjStLh9DgAa81cneTHDQBLYe

Pg4cap2jkLAkpl74slMttjoS0CG1/L5TJnq3SrWaqR6iXKrawxLEdjHEAGXZKt16u0sydi6tGhgefBuysSGskjzLK9K1sdM119Ku6CkEoDKvaKdhtUWa4bzeoOSmnqR0pGhL4bfkrD6/Mq7Rvpi6/DNCtRi2fqyyv1at0a4UuCqsvqXisvq10adipIwrdrsWp3a70a+0t9G7Gy4uqsaxLqgxqwa+0bNTX76tAa+ryP60Abt+qeo0Tq1HhIWfRzt9

ivq0cI88siiabKL/W6ahsrdRvkOIQa9svnS1nqYRFhIWNwCShpiItR/yhpaLm5ByrZ6xbpPzjViD7LvDXtFGYsSioF61mJFKjFzJMQJJCR4BqqRerDlUW1amqAazaYNUtncFFFnAiN6hrqTeroqNjqndmz1F6j6sJz6zwrECUtStqr2kgwFRu9EmrgqlSp4SAPG8hiXJLBG2ZQi+tuiMI8pOsFGtsF6+rRQEPy2hUQefkbJmJk6+ZC4jUWKgVrB+

omPeNMBRpGqIUaZ+pXuNDqF+vDVD8bpOpqub8aF+hvytfrVDCIVZsEHxuAmp8aM8rQKemBHVEv6+8bXcGgmkCbwBvD9ZkIkRRUa1qq5snaqo8a4OprykTphBtUlNcb9UvjEQ1KMOpyqppA7AjVeKQosbFZ6t3kN30hyv9J4rzF0lCpaqrHG9MhSfLT8ZVKIpEB4SLxD7jlSxaQFUu+ylO43HHIUDWUKID/oRsb7staYR7LlOstSqwgtXBhuGP0qx

vNBNm0VOv6qzHgODTYPcDrixtpgGbLPLUi6vEQE2Cw4frLaR0Gys+lmJXjqERgYcEdkycpsxsVi9Gw8yoJiLCYXGAvIYKJUfXTGxTQT+r79WKwHnHqXSKJUfTXK0Dq5/UWNGfAuAWdjb9qoKt1iBhIqUD9HMSpnY1IGg4qXGvimmbjMpvYYZ2NL2o+ahLqfmPSmvZkkpqsKo9qS1jSmhq1Kpqymiecesu3a/7gCqoqmxKbGpvYG2zKoWvymjKaQ2

CKm8jYSpvi6tsrepoamgaaQuu7659qKBswmdqbCpr+ERRkQmrOa+JrmJVmm/qb5puma/drB+rqmhKa5pseTRfrx+tg6lab6po6m8aaJirSKjMawpu3BJuwApqim2JlkOsmK4/rxml1ia6bIpvhOVH1n+uGK3/r+ihemiiA3prk6xjqcxvqytS1XJr90RApGKn+mhWK6sp8m4GafcDcmsGbpODLKTPK9vz6qAqqfpsCm6Kb7YscmoernJoQufybXp

o3uOuCixqmyyybypuOm3abmPXrgybKe9CL1baaCprWmvaaW13sKL8Qi6PAZRh5tchmUCBJMhKaQO7JJBuom6saHwR34gzhjkieKXo0/uu4G/mbchh+qxXo3qsPuE7Kt1AXNHNglUyDHUxI3pgQSUD8wt0w65safWGlcTqrJlxRgZsY4NEhgVSavxHUm1saZHlvaJ2QnhSdKVbJpJs+yofQ5JsRtZ4w5xG94asFSN1tm3sbFUtzOUApZlEV6R7120

h4moHLzchREKOIvpEdJE5jgnBC5SEoA5sH+GHL4sWuFP6QnnEgdNB9RJrA0FVLgEDVS3M48AjGqdH8DLBjEEcbNXHiwccaRJul8MRJGAQSfd+IDIscmAub6quLmyIw58z6zCDZZnM2mQSbC5uEm6E5fhHB4ESRMigZGfOa05qLm9ua9+U7mlxZLTSIqaObocpByvu1B5qZOQOcYjCkmroh5Uq+y6j8KAw7m6ebu5o89bKq1JpbGnWaM4inm4Yo15

tlmzpTTsoVmhsL+hhXmvebIAh7mvSbxZoMmnealni7mi+bAkIgG5mb+AlZm2+boBXvmkebMZq8EJybW3wPtXeaP5tnmxGbtYqzylGa35qHmmebL5tzCLyaoZrzG5u1/5uHmwBajOpf6r6aL+T6qR75yFCxCjVqHpoump6bV7TQCapi/Zht8DstoOqX6uKaRVjqFRUpnzG7aFzrHysqaigN5XCLINxAqFoc9FZrNpoXKjN5RHnAYRmgWAVcgqfqtp

oQdWBUccM6o1CQFpp8Kpab9mqkpb2gykCJXG+hSemCasRaf2p4FLySI8G9CIBF5FvHK5aanJX1MPJUQRUWNW98xyriaiRboPX7CCDQRFk+y0RaNFqMW6Tt1CkdKfWJz4HZkBmKFFtSmo1ZUmgxKXpwbrDz9HAanFvOagKdNUEVsYcIW2TuQlKafFpxjRgp4tO/MKxgnmAmmsgb+ysHiMJapOEVsBbJtdMfayabyBqCStEaQkr26nOrf5PQAV3zXA

GcALzgIkDlQEohUPE+gayQTXMkAfQApcs4qj1ggEHuYb+r93kFqz3Ae+C/lFSAJszj4xwb04C56/aBWmufAVMQWUpPlOIQh3DTAv2iVnxdCyhS/BuaS8erPQsnq70KzSp0qlmrEes2zZ/8gW3Ts5Ub5EGXo3u0DqLKmTWJF2CmS8yti7OSGstzUhp4XSWrkEsp6o9TtVVLatVq4yvkEpxKshmJU5dtV0pJKL3rW2oG6/Ma7RpeWrlquOJ5a0Zqu8

pFtFpVvys66XcbEYnp6xKqwRH6Q/RrMuojGqTF8ho7G30s09mDyq9qypprGuBIFQgRWixbDFvmMuFa6xs7GmIr9ytc6p8rJvNiUbnrelos+Jq4uivw605julpA2LPw+lqdCUTreOsvwfjqRWJJWnpa6Vos+NrLOElHEJpBlbnXS+1Z2VqS8TlbGVsU65lazVLZW2lahVsCyD6aqVtRWgoaMVv2mkDrDpqF/dsbcVoVWlAabA0hYP3A+V31i8KqGe

ov8QPg8YOIhG0CWJq/UsdK9VvBWqdLjdiGmuMbBsP+W46jygShWrPVWpv8q/VqvlthtOQbEUoUG14rNuvdWv0bS+vkGwMayIy708ULyKvZK+UBYKIvEF8AYACny2oBmAB4AUgAVQE+gFUV9AHagYNK67ADEYJx/ynkCEpIvRyEq25shvxVyg+LxwwHG4yJBerIdRCQdhvB6wvCoQ2LwjPyYeoRI6Uai0sWWy0rU7JwHW0qAEuZiXphfUCnYMhQbW

l4VZtKF2KNGsKwzlvNGzvz6MRW6rYrgxohivVqoxuJnZWrb6vLGpnqJ1unWrkScVvRWh+ggBstGiVSJVp56wIMtevDa/dL0QDLWocawOCV6n1qz0uFoj+qT1t9YM9bLMm3W7bq9iN2683zHUr7051KIAGiQIQBL0CgADgBjmE+gDgBqgBSScMAlZEIAWoAp4FvQYDAOapqWhtxUKnQxN0YbKWS8I3I8asuxVwrZAgu1cqL4JpnFRCb+6tw0Ksrup

tsK6tbe1M2fWhSZlqCGrPzS4tgfKW8a00bAufS1lqa0qcA5bW7MdUb6b1m7GFsOBPA6QdbfaxAMxIKB00kUzIaRguyGi5bz6PtWpMa8htaK3ArDep9Wn0aQxtN66DLaGqk2udaIYpKGt5aXhuIxAsaUX14K/3BvhudG60N1NsyrHcbAisuK1dbyuq+Kr0aFNtYymTbDMv9GwNbfJv5ivTa3pX4Go7LXVsU29vICuq9WoNa1NuM2+vYPRsylSLxnN

os2mda/itz6gErzNuHy4dqVxtLZETboxtV67lqoSr+WvTa5epD67TaLDyi2mTblNueGsOrQtvGK6VqaGpuG9K4wVp6aw1aVWqcCCTbl0tBWi1bCtu4A+9aL1tdauVb4VuF4CeFY2vsdPob+Vo/KQVa2mo26kYaE2ta2lpqOVrfqo9aK5XLWn+rBUtXW/2rqhpnibaJV+lS25vLpOwCCVqJ1erOlA/pptq40lPrRCuWGxMaq8p1643qt6JIkgzbXy

uAa2U53evUa5j1hhtWG7rbjxo4ywYbp3QfW59kI+sT67jKrcrxK22qvMrhGxYbAGFnC3LabRrBpeYbwRqHQI5N0tu6qtgqg8v8aqvr58CCah0aktqdGlVsUlveGhEIjc3/gCQrfluo5OdrB2qeccLbkRphGgulfxrYW9f5J2uBWwzax+qVWjcrZGqna4LaZ2rVpbLK5+rswT6kOhuFm7Qq2bQpWttEsNqJSIhVadtM2vzbDWqZ2pihsNtEGkKrvV

oa/Vfrmdp7QQwq1SrEGorrH1sDY59b9XIt8xHKtjCFK2oB+bFHAVwxlAH1ANAcoACVMbzx5gAKgKAAtgGDSxegq/CAYeKx6oXe6mKwOBlnjOaZOlt6gSnah+nn6m6D/ZA3mk2at5vNQQjbH4oCG4HcG1sWo9+Lm1tCGqja6tNDMBYABou08E/I6x1GSp7rG5GSWNZpONuefbjaWtVHWpArRisTGv1a1opvqqnLKtoc9KdNCEvq2hsamSP56m9a6u

mDWSdbzIVz29hghxuG2/XrVWstq2greCv/qmcaPImtG23qIgOr2mpq3AjqajEqk6sy2xvbNemnGlvbZxoStTTae2s66pPYu9sv8HvbuoVAayEqpCsXK49aS9u/qhz0gRu22qfbBttL2/pCgtpBWycq2tslWjra8dq9yvPrH6ppWl+r6VvdGgPrjtpiM9dbiEuz2o/bOhszKmErF1snSorbvNuP25drXSMJxZ5bAVrc2kwrbltkG6zb3Nts244rSg

SiUyZq8/Ss2gNaf9viq5ohrrDh4ePJedoDG3/b9igvitLFGOtJie0Fadtpa1IxWtrZUAPQuoikzewrA+pXanR8NmrKG7ZqSdvx25QqxtrF6wioJepAyhfbJxoDqmobFeu+Wifa+GrIOhXrKDr72x0be2pVbRLbaDom21g7SkQzqoHa3iiqG8g7ahruWs3qG9uXheXq6Dt4Oyz5+Dumm4PruDvF6pxZsiq02qHbpDhj6+HRkiufxBoboivDqjQ7uC

uIOnfaQtupTRIq9DuJNfn9PVo/2u0pLerhIf5qWysBa5CS9trw5L9rfOvEW6otV9sQymw7FVsJWuhaTxORin5r1WlMSe6bZ+pt26nbeJL8OiTjs2ECOpBbPpsBlcI7ze0ekFaEuVtZS3WKcEXPykFroTSosTnN3+sfSOjwJ2GBaqh5z+kBYxmaRmKvgF+bS13WykDJOGDhaqtcmZtKO1bKs5V0ysdyE4yT6MWapBpom/bLGjt8keHFjssPm+WbIY

EVml7a0WqgiDFrbsqbGh7KzZvz6zFRlhT08dWb4t01m8Y7t5ttSw0cyKrZK3YNE1ooAOrBWI1wAfUBP1prcaYBoCCJGrxJddoLU5kyFIWmyRzRR4mOnIARDgA+6yn1d/AclMVU4xE8KXpgoZPW6TIK0BCJm6maJ2Bd2qUyJRvd2k0rYepLi+Hrk3LlG5Za6SFBAQPb+NBSfUFJear5qqpBvvh2wKPa+gpcqh1Ad1KWi3XKKet7c6WDVtia27aK1h

otGmrb82oTrA3qytqXw+hKnkt9641AUo3720PrmH24a+bbbgk3wQEqkRs8GzHaR/KBWww7ydv1I8wr2dp0K/Uj39vEGjoCbioEG9q88NoKynqaPlo22mTaLGve0xPgdNiM2qU7Tipym4ire+p45Aral1vI2FHaR+vwGuI11TsZ68R8UxuTavZMz9vZ6oAbsdoH69hb0qt3W1preeo2mi065mvbha9aZ9qF63hbUBqNO5g66DuUJVhb7TpTKhHa1e

sZOzXrzTtTG61YTDq4KuPqFpvnagcNlxox2xFbI/QYGn21Inwt60nbdxq6m8U62+oea5M7DNugOmzb0MszO/baxTkcOow6kzpIOv8qFDWhG0tl3DvzO7l4Paud6yk7vlKo1Ss7Szpy2sQ77MuLOzk6ePUe2tornts7WI7an9thJG7a5D17OrobJetxOmYb2hoGG08bbuwc2jPqLEuiaocdcGt+2hEaDtoQ8kHb5lTiwYXr2/kr6tc7W5QzalYbmt

vxOiT8tzooanc7KCvE26grSTsyku4am+tCfG3rWztXa3AaBwza6lQ6ODo49Stqo8rR2ss7qDr5avhacUpM2z0aOdu/Ot0702q/2kA7LDoja0hbSUtTOmwrapvAug6bidti6mwI4RATO26SCVtoWgRzoqtym+5qC6Wt28Cayfy1O986dTrgm4rL6uM9GbQMgzvdO9gpd+oqmduIhV29O4M7F6XQcakYtgWCCSfqgLun62/ra5l5ialA4dB9Nci61m

rgZbI6ABoCxRA1DTv4uwWZCBqgGgUEIztR2wi7FCgku2gLmLS76mJa8psom/SaSgVsO3hVGBrYid2TejuTqfo7W9oqy1vqYLsZRTDrHqAmufKrsztAOpibfGFyq1ibj1h5O/86+TqlqaSbvqAHXMTzq33t6zIqSqt4m3RjuahEalk61ttbNRARxJo+XKkEuDufOwfbEwVTmkK7grWbax5LaztnwKk6oruCunDhQrpraz7bxDqF/DVLnGNFsY11it

uty02rWOqyQCNgEsE16gc75JrY6kq6ffN3Olob9zvO2psFLUozSvujrwSl6uq7ZhvruKCbHxumizraztvaur90+quviEybXjVauvE76rrHBAa7UciGun01yrv6unDxBrv1cFWFcSq7OyTbTOr8YLqJQ5QBQ5s65Nry2scFUHjWupk9EvC5bZQ6B9p+G7cEbJpC4riZ4MPUOsM7Ftuy65LrbJsuuurrVtp0Oxy1bCvcm8GaH9pRi3zanLs8tNGbbp

v4CSy6wLqumiKbfpoJm9Lrrsp1I7cF0ppr8buhYYBN6iFqOBolO9+5aMlGgbJBCPMXxBG78NuMu5G7Nqo6IB7YI8EGm4PLNLuQu1ANSpQTyfzAAGGiWzC7VTsOtKWa7quUJFJblLqwu7wNt/AeoDgJF3jGi3YqMLpVOuQ6BumGCRc1aZL9iKm6ebsvfPWaH6G6wg9IxbVuatJbzZvdwS2bFIGtmpS7qbt5u7l4nZuhEA8gfBGB87m6e+pVuqroj1

2zYWrqY/mFunW6rXm9m9RV+JBmXKLU4zqQu+U6Q5omfcfyI5rJ/MU7oLrvOiht45pNa5sBBIG3pZ26wstOGhuIAgj8WNLEApAMi6c7DsrGyn14A7sJVAOcfhD/O767AHPgWiBatkMbOos7yHnhlAhbhRCIWp66zYhjOvkJOFuoDDX0yuPkOiK7TrqLeCQUt1CnEG3wRFtPOkrbzzv2SyRbEHBPtRvS6mhqu6YaZeqIdVmTZ4lUW2FlZ1oC26Q4Qr

Fik4wNeVDuHGa63in7utmTB7odQK4azkoKCQlcg1SUWge6u7seG2Q727uUWvd0n9DUWy9V9qtmq5w157vHuxe7vnUR2uLbQXgpiaRaNZVkWwEbx9t4a4GKM3ikWxu7HwGbu0DVLqp3Kh2RzJUEW46zK7v6IDcTp7oeWs9jGHhxgGFkK7vgxT+6m/GuWyvbX7oAestSCVWdake74XlecW6dspMSZFRs4HuLUfyQOpVzamB6i2mQe/O60HpyuEk667

rKPChaMEjUEYtjRDu2ur7aCHq8of9riHpMIg5Z4rp96xK76zowtQh7aEjsc+k7Y+tuujN5mHvA4Vh7Pzoi2vkIuHuoeoA7k7q5O2B687vIUAu6F1gcuuO7wHvLuyB6q7o9W7/agbuFZDu6VFoPWDe7AgQsOwU7SfhMWqUozFuLIcG7wcqDzZ/Js/V4YqPg9GuFOpzaXFsAiY5IYcESBFb0LHvDuo1Z4lttYkpVNFCgu327QXnMoPche0D2tSKR3H

prKsaI7qB3gTJA/RykcMWEaptduzooZF1EmZfk8AMxutM7sbvIefzoutKcjCBJ4En8ezgbZSmeO18A30LeOjJ6kbqSekBIcntPGYaJA2wieqZMAapfWoGqsRqTsNgB6gDlQLYAs1KpAJXJyQH0AG2ZFgGwAbABlwFO6q2zg0r9oRgpyLC8cOVc5dHlK0DQGSiaCNsdkvCeOixIYnsMuIox/ZDxmibjKICY2n47xRuNfSiiPdu7YkIaEetbW6jbNA

DmASE7tLJLIIZRceRUhTUkKT1ekaWKi3OFqpIb+KLFqonqp0BNG1vzlostM1aLchuT6axKEDvoSKMEH6udGKDKMDpBIGwNCBPJOzZqxljb/X+reCvG2jcq9FxXW2q7Rrr6uvrZrroW22Ehz1oWJX1qVepYCbQ7yauq2tF7L1v8KvM6mzvL2mu60SsyKn3w0joKOrGxyOOt6jK7InvlbCTKmjpjNc/lyToSul5KJoVRaixh0WrqQJ86Trp022xo8W

s2GmMF/Lueu1lq2GrfOxlqh+gMO38qU7tJxfC7xXteNAU7xds0avi6D2ocSxG70zqVe0S6VXvq+a265TqYGmzjYpsgupW6RbvbKg174LuCayM7R+v1e1C7OmvaapLhvvQfiL/E6LqNOoI6QBtCm3BbRXuH6qPK/wR9NGVbtOtcaq87XgnoA6BbSMGhm/16G+ouGhEJ6AJZSp5xkZvZSnBr2XumOtlQLSmjejrLQFvCazo7YWsaOL+azYtnm52LQv

jdBCl69l2zevlKLYvcKgl6reo33cybiZppmpElyzvWEqt6vjqsmqprIXuEO95h2wk+O3I6m3sg6f578VkBepaJ63o+Fat68js6WPE1DEG+e8z4B3qpmzt7TAOW24t6GKn5Sz/bcwj/a+qLc3oZKcrbb9qSqzn0kZrZSrrL7UNVWjdaihqgW+TqM8hgW5WKrToFWyVafJpdenLLMxvWa6fav6pGs6d1lXv4W6eFh9q5G1XkGYote2S6LqqnGkfbMm

JM8om74zttumg6a9rcCD96FHtAurR7jDpz6LNb7nC+iSV7p2tl6hMqbp26ReD6JQ3YOyK7oPpRuQsSl1GxqPB7ZeqxevXqvor3O+F6CPoCuhOqT0sJO7Xq2zqleh3rRbPuW8PBHlv96q/bPepXvQ+7J9ou29Uqo+qobTy68suvG+EbIRv0iHA6T9vhpVc7jztypWlIFXv5214bcLiooRhqOyzahZqbwxpdWtlrc4jTyT/dFPrDG6FaVPsAu/JqtX

r52H26AnvE1H87cdpFSJ1bDGsauU17dSqE+tRq+zsJ27w6XCOEKnyrRbD8q2C6idus+tVI5tp+Wo+77PrQuz4bVqufu6GCAqis+3FEoMpnupj63Poc+71rcXtq2yL6/Pp6utq7MipIWuC6PPqJegq7uzvSuEL64rqd6+h7WXri+m16uWvYe2EhfPoK+7fbaPqS+rL7Abqg+rHbNXv/G1V6sbtpehfpn3t/Oo16TbtTati66vo1Wv8bLTpq+kz66M

RIWu16UGl+kcY1mvtM+1uoQpvFi917evo6+lr7cOoo6m/rMvutegZrv+uQW5wEcLts6iCasD0pWv17Odr+4IXa8zLuC7b6FvsFmKi6q2IcfOMpfXuO+w5dGLvP6rCbnP2AGm97LpsFmZd6m5z7iHi7bXpk4Ib6MkDA6wlUHSsDibwlZXsf6797f+ggGjDIpShd8Y26ppokGqiaxUoMm/J71XooZOWa9LoPkyzEHHoJiky7mJvMum+jKMp82+nbEz

XecVy6TGHcu/TbePul9eUQhvSzWHpA2HtMOjh7vf2iu1K7Yrup+m67ivv3NRrV/ilyuy38i7p5elVs6JsUmpAZUQEtUuh6ceLy+hq7BOu0muxhUvurOoX6XeqSupsFOrtQm7q6trqJKzK767gmu/2IFro+2ls7ThvHBAZT1rp3UTa7WVq1+tS1zroxhFulnknr2xr7rJvuui66zfq96ik6GHs/2PGbQbqCm7l7aTsd+1aaqpvR21k77kxRurZIuZ

sdoz666du+K0m65RH2cSbaRDmAOsXbpPu8DOm6/qqtuxC7dXu0uoFp+bqKmHisJXs/emS66ErFuyg9DZrcwkd1NFE++qAFvvqBaNW7GyBLII40fXuIun/qpc31ujLaeqrknRi6Y3p3e021dnBZiEKoOfUrewd7G3pYLUOaHbqy3Scp5LsGZC+dczndu3eIk5rH3XmbYfpKBXO0eFWEjeBJg2u2yto6JZuqeLOaeQjtaBf7bZPkgawg76Fn8CHTDp

27qwO7o7oMi5Tct/rTyhmo9/vWs4cwkvAPIRubwKhP+tuYz/t3+uzyE7v3m7DdD5u3+82Jpf2btfBbDWkIWzBaa5Jh+gHqq0m0lHFjf/ozu//7Wjr5mm+aljvXvRWBN7yOI9krRwBFKlpRLgD1kJywm6AAcM4wbfI9HWurC1OxgDeJPeE7iSWsZsGaWneAPeHICAZhNLFohUv6XZs1u946CuG46hTrmOvACVZ7aaqfiyUbNnuCGijbb83rAvZ6Eg

EOe+TjRpJpPeJRNRvHQTwVDcz3qxscD6rbio0aMijj2zyqExs266LbLlrHaCqL0535mVh5R7kL2l3DR3sWaixhyVr1OyKqSSqZmX1gQSDmVVF7U9o1OxfbPaq2a2l4YCWOGm5ah9sOaz072iTC+n+68OmDVJF6Azusw5e7Cmrre9D6Avqkq4NVCPq8G1OF2PqYOyBry3ro+r3tYHn+XWP8KYQ5O8r7s+tJ+01shzrAqwP7UDrwO61s0gdY+iD6o/

o82swrbPuHOxTKtPudW0srUgcf24oGYxoBa69qKgZY+oPq/MqQ4V/UiCDNWkVJhHq8Klw7FFtre7bbWLs1WoRoOPASK/07I6s16rL6nAYUOoOqJTXW+23atuJBewg67AbCCKYHQjuMBgF77yEI7S76TOoEJXQHEDpAQaVaq/tW+yMbe7pW+mI6DgbC2hlbj3qZWljqkoMYBsTqlOv8204Gj3sY6i4GJOoXWywH9TqOB2VbYVtrGg971bMWBuzrz3

o32vdb0kKW+shbiVovewEHegaWiLVaBgZ3WsEGbTsCDLxbLFv7Gp06H3orWrvqTVpaBn8dS1udO1EHDLp8EOURDEDKQB6rBxtvWmvqlPu0+8oGBtuJBl06qvsVe+gtkQfLWu9bL9oq6tA673qX2kkHSwXaB92r6QdPWyHUgRuc++IH/atA+zLgxeO8q/DZfKrWyrD6UPv7BQjBmWv5BtypGHhCBk3q/Tti2jj6MzpLOit7OgXCB6+61QfbOoV7Yg

ai6gUGezsqB9IGyvsQ+/oa7tqu28rrMgef2tKsJzoIqkC78gdgOk/YImv2YqJrJhr4GrFryQeRaj0Hxhqz69gaYxGHoFohpIu6ysxLXQYmGkZaubvg0dEGsuAaO0MHuFnDBofqIKr86l7aFhqL6wT6NVshB/oGFshTBxc70wYfJWAaiVrmG/j63trzB8b7rOpCOv4HQRoL6m8aIRsIaw768Op2+zc6xPur6i769geOB24bKGtfGtfNK/qO+jYHYN

1k+rsH+puveqnbKwf7BzsHqelsoCUQaFs6a58b3GsnB6uStGszB/nRswdU+i0IK0jB6xxbEQfa+vT7OvsaB115GaAxB7cHuvrG+lc6agZRW4z6ZvpPBxmlsCADBiVwv4hK+5b6PQYy6soHvQas60WKRwc2+w7bjQcq69K5fgc/Bjy6ogcyKxgG9+ociA/rZQbFBlz6JQcFmFlLbvv9lWKstQd5a5766ote+7i6qtvkOySrDqp++2OTXQkGidK6q7

HcBue7BBuvm9S7q7otqvjKMViR+s7LFZuK2siGJuox+my6WJoDwNV4yxv1O/H7sUS3pJudLooq2qwHc6h4min6dUCp+jbrpNpm2+1CxJoZ+ySaW7uEh/dVsrvZ+6dBOfup6xU791T1Svn7HGGXYnF7XgaMB5X9ZSHL+1SHDwwpK7+7GPt/uoq6VIeUmvSGZDpYajvarQWUhnSHTIbrrLe6rqqT5ayH0a1sh8CG4gflB4yGbIbOWU7zCzpEepVEnI

aUmryGaQej++u5GrtcoTNLtv2vBrPwfaIJB4MG6LVChs1Ks0rRB10DTVvyudNKwoeauzFbkwcjRFCavxqj0gsGfDpwmoCbcoeHBisHemEk63CaurqMMxnb5vr7B1X65rsmujX73gcbB8a76ofV+158LShFW5gGWVs75Pa6QhAOupUqIZqYB8TruoYpKk36U6PsmwaGbgbFW3WIQZswCTLgEZrOBx4HRVsuB2v1YZtBm+aHVJWuBp4HZ9Uqe6XbX1

slC99b2bAxDZcBdGEWAKeA2SRhqsMACiGiaaoBMLD6etloswRNmiOBdXSQ28+QM4BzYSjS06PKiq6L1AcgO58omegK4Rm7lbtvi8/jk/MDo1Src0umWgXKyNs6imUaW1rCGvgG3xEiGidBFugDwBXLCcJ98nPpD/xue/UaCeosso0ae3HSGvjalkq7St56VAbHwnu7h8uJOivbyIYavC37ThpryfrrVNtDfAIH2utUO7KMvPsYO7UHx1vn2vh7gM

M5Bu6yqMt5On4qgoYKBl0bFIfS6lqaKQclSiWH6voSey37VAZ+h4jANAf+h+H7EnvG6NQHlYb+h+uxbDuRWkabFAakh3WHSpv1hmWGlAelO5U62voT2s2GlTu1uqH7FBrHyzEaclogAXCxtZA4AfLVQeQiQF2ZdBq4QeUAQmQLce6H9Wiz1Sa5ErEPyyOVSDAmeo0DA6FkwWd7cmU7O0rb0SvFM0UbpqLYBt3bj0KlGuHqFlp923gG/dsvMdeBDn

vyaI90RorFEKyqq/IkxEDZC7NcjRyrD6qOSdMg+KxZPTGsXnq7ismHVkr02luGvNpHOkj6xztxS9uGiGqo+w9bTYcNh6u70vpWu8dalrvjhzIqjeTjh2u61A12huAGDXKdS8DwImnKzLvMwwEwAfAATBs/W8rBgFLp0U3gG0BOO+2zOPA+YD4UBCq2BUgGY8yto3C5/SnjS5o5FQaB6+gcJvtyy1gGDSvYB/470Ty0qpmruAcvQuBYc4dkkSYBDn

q43dGxbrHm4EuGt6tw0L2Rn4BpPHGH52K42lyqhcGHAoYL+NvJ6wTasToZ3VuH2yqVhiA7IZR1h2cD4DrHe+Yo9LFQEz568EaUYiz5B8rheruHlgd7e1YGlttHOtu7rAdBe72ruhvIRuhGhYUkOibbg6tO2xL6o2zm2or6o6qYR1u6WtuPKoYHwzqZIrwHhga0B0bahEYZO8RGLAZTyok6pEd4R3bDQHtphhxMeEZp+lF7qXqN+sYGoXomBvCGyH

pV+sRM2EY3Kq7imYcsh8yEhDoV6q7ityoOquar6EbmBsK7rEe3ul+719pWB9GBGo05hq+7EIeyTLYHx3oIRss65Qdc+n9pNYcwRpdhsEdNBsnbSXsph7Lacfu/BlkHZ/KKB6/aVMKk+sWH9SPM+rLqstorKihEyQZfBp5ae4fSyoy6FYepivTaZTr1h6xrJTuthnTzpbtiWjJHaevUWrFa7geiR5MaA2iXB7VaL/Sl8RcGfzCzBnVbUEbyRwilmk

c6R5cHukZ7yYJHWZk0BiEGBkdaR9BHAgi1hrBHyiVGBkd6Fmu2BvxGuYoguuAbNgcWR3xHyVvmRiXbdXKl2ueGZdpUG2AcVQBm0IVAOn31ATwxcAFHAK4BysFHgOZsEAHqAUwboNvx6CvREYHb8JldBIZvmFpbyAfUxQy4sbPLYh3azLryq7H7fHVw0YJb2mO8G7nKJlppq5+HU4Y2egE7G1ozhuGGs4fHUvgHjjtR6xigxoFVKXNzG5G/0WdIkT

vue7jaGDjROhAqzRvj28pHB4fsBmmG6IanW2WGtrvC+oyGXgYiq++q2uowh2xHGUf1W5lH/EYghw0H8tu4ht4GFCsAhsA6mUd6ajIHcDptBgT1DAc5RvIG+dpSRhfpJUZFRrJHSgYs+9d6NIalRz9YbweihoMHnAXlRisaHCVjG+w6VUeFR3VHIwaaBg8GYwcNRjlGFUbTCMFGrFr3ek07ChuSWm1HsVq+B4hLD3r3B6MGCCKb1e1Gb6GSWm1aDU

ZhBgEG4QZUgjVH8Qa1RnrbSVsu2QINQ7qlh18HDfsDRyNGQzJyBuJHHTs4/exHQOxSBgbabAehQeYGYgb3uA0H3IdZBrNHGEfQhmxGd7sLRhhHjFleWuv6BDoxtD2qK0ZzR/SGGPtxYwiHX3ucB9hGHtocBsB6aDp0R4XgJTR1R2NG9WzUR5n6+EfNWjd776ujO736LAaNRgdGAIfVB6IGxNrvSrtGdQaSB0h76UY8B5j7mQewBNvaVNrMRlMphP

r7OllHS0ecRj50TxvtB5Pr9QaGnAtGT0cu2yc6mQetB2MH9+XjBv0GHQZlRp0GqNRdBp9G5zqfBmNGPESrKoY71BLhNKsrbwZihvsiiboFezyYjYeGmspGZPvDe+4bFekgx21b22sz+hDH/Ud0+48Gf5yAxzVH7wYvBncHZvpKBhFrlPulhvvq+vpF2zR7aQZ45Sr6BUbnRir7gQcNe89G80cvRwJH/Wtoxs17NQZ4apMruYYjpFjHJfo02p+6gg

dAm1DqNvu/5UxHM6sGc8sHcLqSCNwHDIfXRsTH3wdKhz6llEepR+a4/wc+pFiHNIYF2rnbSLqyJftGVDVO+/fqAQEkhlzbT+rcRzRR/+BxqjuHFIbucu/qAOt+caRNtAaj5Zd77+vh4VSU1MfHRmz1bQjJiqpIZQdIh8bqjavEukvKaBqH0RS66UYIh+UIuBqX+uH7t0erR3W6AAbUuqtJD0acRoL6uGMoh4+be9t4xwIHMIYoh3S6qIYMutjGVQ

YiBim4Usf0utLHIYovR8UGJQUNlT4isfvP5UUG3IaYxihlKscBRuy6EPoiR8ClGsdsupiH7LoSRn8GQQSKxlH6rQbFRirHTLo6xiy7RUZE+yM1MfqBR6b9kkbfR0Y6GIeqx8w7FHuq+1EaiqPRGpQaw1t2DPeZ8AH0AfABuXHJAbt40jiiAZNTwMFngH2Lg0olfafxqZimEv7gPixuOr1hvuq3a72QORuzlQxAW5M2wFZEV427G/ESKcpMFa5cSK

JTHC/S1KoLiieqYYcLSrQYn+K/i/Sqf4sOgf+HDotHEK59OIj0sgCzQ3A5o/FGUhubgAI9K3IyGkmG9cubh6mHiXsKusk6azty+v3ql8OOut36XeQFh3UihYccukWGX0ZgOxd78Mb0yyx7RTusKjx78bJ1erS7Ezs822lG9UYT+rnGhUctRvrjqgdlOgXG6trVWkhKELtFxkm6A0eV++kqZTuJu4D6Btp3R+v6RccVxvV7W0ZyKwL7Cbs5xmXGsP

rAa92hMMBcy+gabbo1xi5qimoDaKejviW1e/nG9cfNx6RKSmutx9VGCkdOGxIGzQYMe24qN0fvRj3GRTs8bJNGt0elRhnH+MtQq7j7A/uFhsYawwcsS2O68fsmOrG6Iobdx1rHRPrPBs1AWsbX2y87TUbCIecA6X15hnO62Wo4a6dAasfI+kV7pvu0aoRqTLP6tYV60+vy+w8qUwS9+wK7ZMeCO8CavBDrxl67X2vk6kCH24gihnPHvfqsxweql6

iz5FvHi8aeuCbK0dH9KM4Ielipx+AbbuU2EF+ApJHCRtPHeseyx4+apMxmx8CkXLo4hkwFRYdmx1EoiOv4hsxh4U1r6lnGrQXnGv1I2IRKx0O6IbqWwvyGFJp7oYXBpmCFXeJ6Xbu1+y1KseQYOZmUNLqA+s3HbUTV+gaq3gg/x03Gk/tWuvqGBRvRrf/HE/u5x/eIAusDwU37E6jAJsXHXrpLWd66shCEfXXGlceitCKbu9GIE7sw4Cbtx7wNff

qAYIQQb/utWwD6ACYgJw61jqtN8HBlm9BwJtAmWboneORglsEXeaqaXcdFuopB9Zoluh5w1YcKR0kC1bv08dqkl4nMekbLPcaBafW60kOUUQjAyxlXxw15W/rUE0AUmmC3xq15R/sTmluQ5slTxgnbM5tn+nObMCBO2yfHm7Sv+4Pa80dF8qg6+YfLtKea+ZWOAzm6K8ezunvG8FtAByu5Ufzn2sRG4+v4eyh6jtH9iezBzPyHR5F6mTo4WpTKwJ

CJceuwUmiZ+7wnVOPoWsu7EBD6lBgIMIqcJ2n6i3lvuzSx77vUMQr71EZ8J/vUVHrXurZNtKSLxqvHWHXNNanoxsBquDDCfIdl621AZWlMxzAIgDsPxxx7pWRsW+KVQiDcqAyLH8fZxqx60RC0U4URXQMh+mW6nHvQcbz7VJGIW0b7fTq8elBivpTCID76miCL+urDYWh+41XgpSkJVQrcHvq36p77yHjoqJLgn5DYiJCQewYbBq77+hmiemIxiP

FSEBLL1gdf6pJ7y4j38VTYVlWVKYN7cxrPelQUinvNXbpEYn2uBwGbQ3s5+MWxIjqiOQipLpMWhyGaQ3tgWk1loJE4pc8geA3aJJ4nvJr+JufU1QnqQUD5KCHbCK4mgZvd6YERheASEpeSj01BJ097t8bFOWKooGEm2N3RWSIeCOEmXieN+OSA50aT6NEnfiZuJkiTghGhYPiqQKiah7YnhyhPIb/ixqgGUeRhWwd7B44mUymjiJpBpGp/uSlKUO

sWJqb64ERCE3bQS0jDYO8aVkcG+iYnx2WmyPX66lVpCad0A2sL+zMhi/t9+Hh52NPRAOZoUisVJ8YnlScmJlQsj4bZ6VcpmGLtO+i64ZSQaPEReAnUeJ97avp6+g50QJF3o8USs4GYhgYmN2QlIDV8pmXuY6FCXSdeGO1JBWnnGZihpLu1O0SS+IB2VXQVthOcOz16AvktevdYQ/CdKcihwRAgSTonqkd2pR8FIPoQEI1aqkZUu59lnaFvkUJG9p

Nu/C2G7YZtldRRRoDwa4BykyazJpe8nfFcCA8o4NMqR0LrkydupLAVW5TOsJ3YKyeZuzTcQYlkCeQCsQAzJhsnKyd8yINgPlIzWTbAM3RNR1JbGyff+BvQcLk4VOfAoqszJjsn7KPTYOboPaB26JrigYeNepbINolHMNLERJGDEFWSNycthkS5FSArGY+0Ljr37QsmuiePJ6LoMuCUgCm7pOkvJycnfMmQyESBa9O20UIG9waZumm6cshfJlQniQ

ie+HzrIyaB+44VaMgxx/2IYcGPsDP6gyaLCexgPHE/5CaBwWsB+vAbjhTDeH1hHMGdtJCRAyYIu44Vt/AAqHAhGdUAptdrsKbfKClIkLo7OBg4sKajJ4H69si9YH5haFT6uKickKajOxAFnjD9HQFQHClKApinoyc0Ra2cHvkOlDJZKKeAp+CprhR5oCuTwpF6B9DHqOTWyWGAdlX2K/olvSaWyFYB3hMSiIeptyGtJkjHgYgkFTDgL7gtCvKHZ8

B1Jh16hKjYdP0dMsjbHIEGC/oMp4b6LKlSaKVIpeCAQKhqBvqVJwyn+ATpBOIxccjCYcyn9KfteqynmOXBYLpUfGA/8IAbtSe8plUmsdtMYWUh2RIRCOZoxiZCpvUmrYtyCaUhMulsPdqqYqa++uKmihITeKpjhlVYsbL0LKdipsL9fXiJaU9dWClR9BSn0rgjKDSol4lPpGxkuvpx2lMq+lBUXbARIAjxZQSnkKY9paCQyCt9YJIxm8da+osnMv

s18dz6fjTVxz/HACf9atUJipUREqqmaCa/xijGYHgECX3Q1Tmmp0an5rhcqHq1/GvNjKXH1ceWpnjlbONM2PeiMBHj+6XHaCZ2p4IRjkjRsK+B+gXbJ78mF+hCsc1Bj4lwYj3YuKeopvpdg5hHaT4m3nygp4imM6Wmyeuw4EgV8FWEnXrEu+Y0Wt2coe+8r9FSpqUmujU+Mc6wLRTDYa96BSaS+8ygcWVS+KQQ2Sa2J2qG1aVQqObBmYgDaQ1pwu

PZJr6bjQiqaMJdHkoRA6qHr+oxpuI06KnRp5GI6ScpphfpA0WZkf/hnlkK3MknriYxJ1upmwRGnOUgpTQ6h497nifBJtWk7CgkVMhItCqS4gknBabiNccF0MCs9F8bcuEmhgWmKSZ45c0Va2lSEUcY1gbbBj4GagUfBamcxxFbsorKCaeBXDdcd1BxlN6pAsgfh296agWdoYtRnEHAZIaT+ScemoCHtcmd61iBIUElICGndSbENc+UWKD0sZIxNF

BEujSm4UK/lAQphsE6y3o0cBq/eklDN/wk0WMoMf0fJgcmo+QjKCDgmcB76Jb9eqavJ3Q0hsFqCA9IOBPRgk3HwCZ2corgkjG4ycDFIdQVxkamyCdtODtw2+PAYaVJdsIvxwx7f6RIgFuxm0hKQH3Gj8aeuIeIqIXR0RHhUfqEJ33Hh8eGCH7G3FRzLFxEyMeCh/lDZHg48Wun4OAUJ0BlnjEyQhNhzsDnpxFFeglHe9iVf6BXpnFyzwQEU56MiU

i3pwWZSLADywbAYsk4J+nGczvwZTxhwGRPpicompv7pjunLvxBiatVTsCMQdunqicPp/5hq7QoHZIpmCbVe9WG9kM/p+DZv6YIIJanK6ZpNEDh0QEn4Q9LMkFAZ9AbhzAn4Q1patUINW2GM6aeuPxw8xMS4U5Uy6fjpxcnbTiTiBLBJJrEdRMGHzu4pihkEHCNhTNgsFUepsV6hKYxWXnRAnHIMGXFCtwjpzP7GGVZUBDQukF3Iw8lA6YpuVgJq6

PQkX8QWFrKpkEEZmOCqDlheXVdO3DGHTooZb3BBKCy4KUoR4gkpuqmJBs1QY5InolYgU+kPaecph00EnlziIfRThIVJi+RJSc9p1RlaLC/uQXQDAhimoxmnKZ8ph01TGCbGQWqcQi0Z2xneseuFI+biscMZvKm0qa1kvAJECiVSW14giuEZj01EcmGwYuV/A14um0npGdB/aCRsuFW6OcR91qCZmRlKMA/k/zAeXWXWlhnoKbJBGGdwAgzCMxgXa

QyZr6nGUTneI6L8Wkdsq6mYsa8EFfSi1H+KbtJymfApHipABBzSDohJRJwZ66ny6ip4p9ijBICJ2BntGJikaFg2WgESHpm+QTSFc81nQKNmuWGn8bXxz4xQZUCNRbBN1nvp9+mhf1ZMuIRHbLmyVpg36fR+q0FphQESeZVA8F1EqQneIZECR1QW6TswYFKDmf1qf+AuqBbAJUqEsAPpoX9H4EFaZm5ab3KBc5m6zQ3XIENeAi4YJrjI/tfRr05T4

HUEzUmQKkWxtMmJ6aDuGNhXaY/jbWkelleZoX9pAgUmZ2kZSEdWtH7IbqtBL1hq5vTmzaknwcvx7UEmrha1fIpoKm9utnGjPvludHhZ3FZCLEAxoCGZ+W4kGhXBLTK82ipZun8QJGuRVR7lEDqZj24CBUIUCsJjDgjJoimqKekhvBVBqMqtLXUnqekh/kFf3hLUEpBhYsSZks1Kmh38DUJ5bE/3QGn2Lv1qNAgninIsLUw4hE8ZrynvGZjuVB5i2

QTyALpnGdCpoX9A0RLRFTI9yADx/MHtWchp3OpmwUcKV8BAGHnR/P7rWZMZ21mm7FjMLKIaUEP6h2mcFq8ujPiOiATXEeisiQtppYmU7hIgPvxtRHs7IAaQ2cFJ+u5tcgAYZRZDETRpmqGOSa/dWrjxqEZi76hgsa2+mmmvpqHoepawAmzRwSQgBqOJvNmG9HcdLqhquM2JlNm82bGen4QPHDeuI5Nyaer+8piTUAl0HuUh+iDe/mmwSaVpr90xE

iu3V2TAeA7tCWne2dTqKzJMKk4BP7bDiRHZjmnuKhKCOblPST4NX5du2fRJgNFwbmpQSn5nGKa4tmn4Sam5UxgeiEPkWwF9ShnZgNE0CEwqluB8MGxEBWme2dnZ9V47Cjh2yn00RClIndnCSbHBGKxr9AxQACEIoZfZyWn+7m1yCaA36DbmJCI6adTZvybWAkCE3udsDBA5r6bgxGdwL1cloichBYnHabUtb3Bd4GGlBRR8Vq8Zm1mDLR4eJAYlr

lpCPSnjGe0Zyy1cOZQh2YmDTp4Zyy1JX30FNejcmtqpn06UOc+MIQKu6BN5JRmGOd1icMJrKG4mbQnxfyVZl96XJosSD+gMwhWyhDc+OdtJyAn/eDCIb2Q03FMm+jnTSdxm0KV9/BGyLmpJGckpx5jfXjZM3BIKziNZ9KninxD8fslBsjBSe4zrGcsp41nICaBCDRQ/+F2eZObLAhjZzIq58DPgIQRaQiU0ywnbOZ9Zt177OfBubQoSyUpGCYI7O

epYzIQgghqQPpBW9VLZ05ih4j90Hmc7ME+GH9nR2f7ucygH0ieMXhLxaZXZ8knb2dZKaYgw/HyaAeVr2dXZlK0cDHM8TroZsiAW5I7Osram9HgEHlF/SNKSuab+lI60pq3IXOJgTxF4GrnU3rjeqG7UrSYY0IhWwJa5kBa2ueYlEDhp2EGiCBUp6wb+7d66udPuPBUAltEqbZEdJIdi+d7S3utiMBV2txj+JPSHgkcxkt683tyGXnRLOcgCbAx5I

dHCdbn5uc255G7UHjcQLK53CAtKQ7nzYuO57wN2ujT6L2xYjDAtA7m7+o25td7TwUXKYJwCbDrlS7mXuaO5t7nvwWGCISsK3C3gFWEeUpXep2L/uffuaQIW5HGacYRE+Nm53lK/ub9uwhRxazu8XpAK+PbCK7nV3uR5hIKbCEyTAVIfubm567nIee8DJSnTvRM46Q6weZzeiHnkefKlB6hIpAYqCLg53uJ55Hns5XuzIfoGTuZ57Hns+X9EEegV7

l6zZN7G/ta53d6i2m7MXMRYHJu/d6bNaeah3R5jrBUUIy4dUHhp5Dm3rUUlJHhxnKx5GAaXWeI53R4NomEgMcRFWDnwNjn5OcxeDeIfzBvBjfBdTE+pvlnuHmBEQcFEuE9kVqnmKcpeU+AIEieMejAfGHnJ/sncGYxtV1pKlT4GUaBhiwXJtpnYWnF4gaCP1x5pT3mJyYTpj6rD7XznJ6ICkAEM1pmYsZfyJ+B/YjXZFTK2WaBaShznzkvII3ZA+

a954PmKAyf5PEJA4jNBQimSGeeptrpN9L8wIuJ9/FHGI3mKLspeRRi4Og0UfTpCfOCpnVmS/rFsHMV+Ca1iJXnfWcvfQNEe+EtkcJcEhrm+imnQOYxtZ2JezC7KVwTXOdi529nLyEyEeDgmYEPMpR8U3t65kXnvHiQUq2jrdXCYLnmaeateIqKCbtjkmTbKZpyOksao4lyCJ1QEjvXtScoO3sv50gUQJB3IXRiI0kOJQf6gseT5n8QPeCcCcOVUG

xqO6gaiBuH50268FQH9d+gXaEWygLGgBYFBKOIxEkkkt0p4eItKD/ngBdgFkPxXYjcnJFL2wmQFmAXcznlcClmfhBREIjBIBcAFyS7h/vpaIhIVhwiCf7h5+ewFsgXqnhCsdOdx2A4mpAWoBdIFr/msKIg4ea1NLBpQrv7p3oUlWR5gcvnEAmYeudjerfmKA2TqLwoM8kfWZ9mN+dEFwp4LNmRpTLg/GE0ijwIwuajiTwpL8GaoSiB1bQlJmxmzO

c6KONNQBuNMImARuYiyoCm2qdXtF/1+yRPSGtlHedIZ0+bedDdoTub35QfJlBmnyaI0p3A7pWrtbto2yPzp+Any7RPIaRqemwloMzjDPsyegIXTGDP8epcI/CGDKonNmdTukHgBLSJaESBsJsVRxzbFmdPmuLgK3DPx5TigDphZ0+bHgnUVKQ4mYBs5n5mg8dXtDNR9/GLZTLp5QjuZ0+bwblPnfDx4NiQyfIWiNNVlffpMCrfnYFnHQef+uSAYh

aoWx7I6hbaF4IRdfG5iVRINmZRZ1O6BYnMCIuInjG04uIXJhdPms0LwDVw3FJU0heZxjIWiNN9XdOdi6f6grgm/boyQfxxivkTmusHTwaOpmamiNNIsCSaWKA+icFqk+bs8tRc5siH6NDdEyJoZiwXr7QsSN1zkwUGwTU63had55u0/HF/SYK1hsHpTEzn8qb5CBBw4Z3/KLa4Rx0cp0zndOaqGINhiyBEkNtS8/SQ5gfmIRcXncNLd0hcx/zn+H

pl8AARxaiCqZNmJ+ZQWsdwFIEHSMnACihLZ6Xn6ScEO4EUBUjhbOKU+aYBmm9nj7ogyJnACmKYoYdnUufZp4+6ThRXOTArbOpZFn4m+RdzunAw8mk2av/xl2dZFvLmwHSQabx6cUp3UGUXRRd3ZkVZHgg4+KCpsBGrkhfnj7o9kdor5RDosXLm0uePul+hGGOGiM1FYSd5FtUW4ibmEppgLwXRgTybrRdfZxSlnYlPupu7F9W+J2rKTRb5CVeUpe

FgqZqBAmN1F30XnjAIMMnBdJyFXYMXSflq4sLZ+Bm8CbxFm2f2B6MXXFVblTFLppTfB86aPOfbu/5go2jFYnmh++azFluJlAmvkbNRvXM15ojmXGaclXIJA3lAQGwg5SHLFvQWERdzLasXyWbR5+sWG+aBp/oZrogjENHjsCA1lOwXK+c1WOUI6BSGi/sX06fcF0e76XXz2NAUwuIZZpyVJ4isecuz1BB22MIWCnq7FxUhEUvAc/aisWcbp0n5kM

j1BPZxINgLdVoXR7pcEnFwiF2307oXfmZbiE3YYhQtu1qwrxfKF/vUiEnIa/eQHnAFSIYXR7spCK5VshBKE04XELlF268XtHtMYNPLN/SuxiYWr8dhaYtR+lBGkqMoqWoWFyCWNRNQqCURJXFe7Yd0mieJZ4VlA0XeXX3AzZLLPe4WW4gHuRzQZuDOtHZq/hfsFzoot4ClJHwrnBVMF3KmtecrFnGMgx39KP/wmKF+cJ/raRfppotpnNEzW9OaDL

BVkqMXpWX1af4l4dH4efUosecP5weIW7WMA3vhOOsnei/mSZqkl6CQ33F+kW+gTevP5iyaa3ulZV5wnGB/Md3M0uoAFrrpoBboFgKcXixhwMNhiQlyEYgWjJbYF0F5/cDIsRiA0WlZ8ayXIBoUu5Pnu2nKSLDBxpCFBFyXEBs/5uyXgmHu4isY04k/TWgX3JfBuUPxb6EsNeHnijpsltyW7JYilu8nlEHLunmbAAekGiVKAp09QdpIURFqiCcwr5

oix6f6jViHiN1sUTKn9fKWoAcKl6Vkx4yGig+4HIjf+0/6FIHP+uyXA0UZF2HgBrwftE7KP/qalweIquQvwXzAckGs3eY7TZsWO6VkX70WkT+q8MdIKSrGtZo0mweJhZVagEsh2HOZQuVLpXEieCJa5pbC4cgxE0ioSE3qvsdctNaXFbDGiD+4oBCuezbAbZvnm1aXZykOljoYfA1AQNfM7vDuyFaXfMCul0ImbRPa6aBhIjtTzYy4npZ+x9aWOh

kxuD2IAZMK3PaXLpd0e16Xz0m9wfWImZz2+/hDppYWO81AxohPISyg9pODEaUh6pYf+xqWn/sRl2R5HwC/aIca8/qoGuKWh/uT526wLZC8YHRIQxBFCCSWF3sRl3oJwJGs2UYhKTAeB1UWXRakbQUUFsnIsDMQ4dALFyb7Zep8EJIRKgipFW0EOxeVZqKV/eHhCZThHoojDQ8m+qbFl8CYS1F7QLMDrioWZ+IWpG3lcSaJnqE48SnyYka+umPGH4

Ti4YpIRp0s4wfGciailHGAvxE9kALc1sPSxtmGXzrGiMLx1BXGoFph94ql+nL7hftJxh+FHgmZCCRJXyeO6Zl6Scdl+qKVwxBTnJSV3JLt+ll6PZaDlv3NvbCbuhDjbzr9usxhfYnQWzEpV+Xphzx7KMF983emenLjRuXGE5Yzl+tJfaGzl12XvevdlwOXlifWwSiEzsxytcOWA5cYeltYlKe4exqUvMaFayHa7ZY6GfQ5XVwy9LYRo+q8J7wHAn

tyY4JUdyau42+HAntSabbRKAc8FNQnSDvblhW5iopLCcPAkYtx+4P6Z5fuiuxh55axHMemlsfIx8fU8mTnl3IED8eRZxCWbRIs2bQxMuBB+H3gIJcQrMNch3FB8RaRvCVXFhH6pGxexq2iykHex/Jm/BdwJp+XwWBflvFiSRTnFzvTgkvtSqp79uqdhwxxTcGIARYBNAGUATaj59NFcD1hm4AvkVFoAJEOusCIY8E6U+EJ3mCFEWti4xBCsVG439

Ta45l1zNn1aHFwPhkuKMhSk/Ijs68ya1r7U2Ei43NmW9pLncU6SnZ6EYZ/h/Z73ZmMqgNxBhGasWAQ57Ua4lXoQEejCuxhlbm6CvUboEej28tyA2lTS0+qH8HEvYDAD6CMAaYBXUx4AZcAOADCaKABpnHKwYDAAHGOYYMKnkbag3nRF1x9moTobBubGUHhX4GJLOjni1t6gZSGmFvsW+DYYx3AdZGlHpAzlJ+H/Br+OtOHOAfI24E6y4t2e1hXMo

uRh7WJHvgjC3DbElFoY3HC0ceOWjHHr7ngR9E64LNxxrML3noeoiKmZ2RiMM+XnoQViBJcJdDosHRoOZyqneVCifsHSExptIcfiXoUclYwRAgg4SEEoXbnBCokFA/l/hQ/KYVy6+wmaaPgqLDdrWjpZpLPltPJwRAvajrpZslomGyo6k1qVrlZLokc0KhqQeENCHPjq4hsOczoOlfqV0ZWgBpspkghUbtfgZn9q201MWCsbXm6Vz/Vgnoj8GRxFs

FZCh4Z1lc6VhpX6OpoFBeXzciZgY5SxIFlSZFiGkzoDTUwwxarsS5WUPOuVpZWtmo1CLkKe+G7OeqLP6CuV76chK2hQD5WyaP2aIajVnL+V8+AAVbuVz+03pG5teUJVlcNSIZWNla6VxpWRD2n8SfhYVatlIpW3Ygm3bJWRDmrp98VuzDBVq4Gr6AJVuB4CoYLSWUhhoqKlfwQARIDEdXhCVdgZCas04m/+f2hYjEhEulWWD3NCs1SBhTiKOCmse

W3dEFWGVfJVuLz0NIGuS2jSSZJV+lWyVehOOAV8bD9YLtEBVdJVrlWo/nq6RTRWQgvZxVWpVeVVm2UikFF/NT6wOHXm2bAYVfg4OFXRNySEa+VvzDNQQcwzU2NVtjrkUnhpD6NXCoNtEccyCltVp0p4VZwqIwV9www+fvJoVfRVk1XMVcUpsixvVYpkhDI3/tw8CziHokkElucvmEF6nILdsOU3CNXMok2VNGlegjcnb1yvbATVxxXI1ZTV+2Gsl

sdh8S83j0WAKAAYmnwAT6B7LAjUckB5gBaAP9BiADqqXp80aovoKiXycCnuJCRKejAiUmIpSQyQVgojCd8mKpAdlwg4Cfhm5C4YGMdQxYg4LgIMptmRf7HIcOjc28yoYeh6+FHPdvmWpFHmFd92lUz/dsvvX/L1lvTgGLoZuHRh7UYHqH/oYyIPXyNMg0aj6pHZImGEEZxxzE6e3PD6S+UnSiAQKz0NxRASN3AqLGR5P/yWYdg1EyL/hBpQZw5nI

mKVnFXA3hEOAitW7IqhvuRTCX5LADWslaA1l358rXyVpudThsRV45X5laobIGE4RFsVUEBRRNeVyFXQfDZuCpW30hBEU1FoyLfncYQQNh9YET99ImqQEIRmmA1CV3AlU3ytQTLgnA8YLllelcfMPaTpwEGwr6Q1PsXXapWfli9Vu5tJlWmVzc61pS+ZluSuFUWVj5dijUeVfgEn4C8EXhkkUugVSq4B1heE/ZXgVwUm2xXq0rT/SkIJakxE1rSLG

SNV+7xKKFy4Shj8Va1VolX9ajVCJ7jjLJfzCFJE1fEqT6WJwuPxvnQfJ1agfowGoiHiQ6IZ8An4fIRkfwHVlzXh1ecHMdWvNbdc/b8dkbtSs3y9oeqep2HNwie4YgAeAGW3K4B/NIngcrBUIFwAT6ATvAQAdkh01qoGtK6/ik3iw4AiMHpGQ+Q/toNMb+haMkO1S1We6AP48FB3WctlWbIVWjqSihXxlpT8iGH84rebOhXQcbfy73bV1ezh9dXc4

d4jTmrTKs6oOIR7FYp8etLB6HRgY0Iy2KgRr18CUYkVnIF5AYnArFXg+GCqWfw2f0pbIZWWVZI2B6hKWxfVrhgcuNw8flWmSLPBBmgd+jYibm1CBMlSEOmJ7LcwXo06W1lVrzieiCqYvk8TUtoKG+ghGAz5Pk8uNYGZKpWiNb5PKjW9Vdo1hhnKW3TCCrXyKCq1kHXytYtV8HXndtpmZJWFxBISf5NchKh1nSyYdfXmzUwMOCyEAHwfruR181XUd

ZHuDz09tbHSQpyNFBBhMHWCdYdOAMR53giJ9158YQB1nHqgdf8ueydXZH6kcDWP7NKhfDWeNb+15nWSS2WuHFMB8Xohe+6Ptf0esNE0Nb1p93MkeJNzOVWntYThqL5Odd+1nydE22u1vn8qSL+spwSaNZkcY2THjhO1wrtJBGyYgQyodatoyiABYQphPbW1DBIIQ7XXOdoCUp6PGAxU4OaZlY7qTjxttaOTcZXqNbnCH4Iq3U21ySTndeN2NNWwG

t9UpUIB7MpxSlXgnCKlXcnp3SU1/WIVNcVYZbWqVZK3dbXQSSJcDrMsCH/oWPXQ9fj1lgHOfR01n9ZWtLEF59oFJrj1tbXM9aXe34jnwER5yDQv8QyVwvXn9GL1ikLBVelVnHy0sxD11bWa9aCXV1X/VbtVpsXuvOb13YlW9YPmpNWHNf3kNPWW9fD1tT0faCGKZLg5mnaVx3X//QdY87ZLNdG6AoowPsGVzUwttd26I5NTYmD4JQdTnL32nlWDt

aFElzphol4m5VwKwjqTM3XeVct155IqeLFBp7jZKhoJKnXmmD11yZQkJuxlIw0XEDv1pls350f1ohcLtdsKWrW2IXq1iXQCrLRVrYQbtdV1uo8+EMUqBrWlddANlXWpjXhvRUqADcT8D9XZ4aNmAtWMb3lAJzxwMGcAfzSKAFxGs6HMiAXkOAAp4EcMKDbG1dqW8SM66IqtObowIi/EcjlC1AGYS3avWGXKNLSxIEsVkFGK3A66KxIOOutdVxWpl

uBx0jb04aBOzOGetZRRvxWfkHRRpTZSYBQ2UPbV4xAKukxpOGVccLYZtaAMwnqQDKF2VvCW/IbhjE7kEYbonvXqVd3gOoacCP0N0cYaVf32Ew30MkFAwGYLDYzCE7B19nvV0eTsdcI3AvX09fohOw3repaWigxJWfkYeMybDbMNnnWwNcNMe0MXDZb1/w2O0QIIQSgEBC+FLGx/1YdKUI3DDexhcnWrVbrlsmH6iGdpXzFYPS/+kfykYgPIAvIFE

A/V7E6OQk1MX7Jb3AGYVQ4DNYYsANX9BcNSKvXXDb71sfW9LC6oISTK9ZCN3vXR9chKAdXFbC8cDfBh9baNhPXw1S8XIaJdBJ0aXo2w9f6N0IoLEm1EGZQ+Bj4LHGDWjbGN2vWEJmMe85w3gm9lQRkajfmNjPWglyaCUvXBVhGRe0C5jZsN9o2Op3JKQgW2Wi3GnIyjjfGN7l5HZGktK7kCGdGNrY2g3j35D9IDykPY5TMrjcWNvW7dVew2GEUvG

EeNovXtjaRlvpBfpv+EWCam9biNvo2vjZFaExbuDai8FLhhQxgCPEHskHhN7VdINchNgw33DeKGWE2dEh4NhE2j6j8NhI3Ptnr44dpp4mGO2I2Vtd71sI2BuheNpyh0zN8NjE3TDaJNtrpbjcdae434MQpN6vXqTe5eIUlXYjTiJ+RwZYpVxk23DYNPIcnjrle9KyMGTcpNzE3RTd+FXlKheocZJlWZ9dZVnQXKp0iMNwhUuPWNj4dmVe913mIEO

MmN/9qAmdmNt0idTad1vU2Au3QIIY2nKHS50vXzdY8YA/W/9cQNzDAM2BbgfVTbTYv1h03w1Vf1p8V39ZLfKCWQDfrHcVWr9e9NkYhfTaDzAM2xVb0sJPo6KgtF9BJG7VqiVKUqp0Y113BRrM6N7fWeje1+LaIuqHIUPrkiKjTNmoWMzcd+LM2b31zN9tIF9eQV2wJHbJVV7jWFddVPcs2HUkrNrt6jJN1VhnXNdcDeMs3dVYrNihKmzaKDJI3jA

z0Oes2Jom7N2YC/nlDYAgJnVcoIwc2l9bN5h1WYUQbtTZiqAr50Lo3khCkp4NW5ph9VsNXISlMYRPkx2VCme0MvVfXN0NXBFM75EM3no27KNGkDzYt5oE9jze4qf/XnTYTyPuRaRTXNq82Nioc9ccEfZv8ka03VzdUSF83fVcwmWR4bZH3QQhjodsvN76hrzYc9XqDyClWNmwgtTetg0C2NzZvNivw5Tb2NlMEDjZyyeC2jzbn2sU3gJAlNz60nz

Z/NsC3XzbvhZC2CatQt/c3nzcItv83iJmWNjU21jaX+NNXWVeNCTNWtcxot6iBNTfotxUq41aSFXbDILZWNsAQYLZHyuHKMRo2xzxkldotczklXUsqAckAIkDCZOrBwMHOkSoA2AGAcPXbO2lctHRIjFUpy+BIpSSdkIUQQVado90399ZoeHPCdlbfyJPw/XKUq2lUWtcmWvnLn8uNKt+HATq928HHP4pLSqHHZkkNYQ57RpGiFEBLXzH/046CWU

iEaE9WS3M9K89WMFcW1lZLOTbqN7k39IZaWjZKtXHlEYI3CTaxNmHNv1fKmMXQF/MRsxK2DTyu1hE0vGHyxTjFTTdn11U3+Ojg11QxHGEb1rhjV9d1NtlXjMXl1wjXw4FFEvfWLdc9Nhwkbdf6VjjWGrZCED02jLY91dI3eRNyaC/6EJgMtpq3urdgKCTWZlCk1rvWGSsat+02RrfRJQeYo9b2Vp6hqVumtvlXXOeYNy0JllYguDq39teGto7We3

V6tgPXRF22tu03VrdEyfjXJlZMqY62urb2tlq3GtFt1iigkIiutwy2brbkg5pXjdaOgN02Vrcv1xI3fnBaVvDSPQMAViLX9kf2h2XbYBzqwW4A4ABOLDgBMAB8AUf8L73qAb1L71CMqwnLxSrygAzhK9AhEwTiBvBbq3rxnpEzlTSw25jS4HXXSNeFJfpA/ZCyCjHWH1acNvg2bLfnVl/LPFdhh7rWQTqWWrStc4dRcSQ2XHD3oxnVe1sJwty43J

UCt/B88YcNGn18XmGS8aRWPKqW1gk3hTfqN27tajZH1643u9eltg6V/CgKtlU2B8rltto37hQlUr63mrd6RI42tbfSqnW3ZrcmWBw2sdbQ5YEoSNYQ4Um2M7iS6U220bHNtwDVLbaeoOYobbfHLO23H1d6cPNXgFeyW8S8R9IgV7AA6sGKWtDxV5Hn/c4B/NKngZHpg0ozgEpTJFXYSjTYjcg8cQ7i2OgdkCqc+1bObRZWWwHfeBTrEpCekIlxL0

klcQcEabbHqgQ3oYaENxy3xkghxly356sJMHgA/XEG1u9Dj8g9Ep7d8S3L8iQQgEH1++yqDlvx6o5akwqiV1YioAMQR5ZKO/IT7KDWSOpCUjbWjlbmVrZWHIX1tqw2v7uw125XcNdtts61HDYdtz/Xn9CttyuYKNeuYzw3E+CgiHw3JddImZM3shFqYtFXeddUkCDXSthNSm2QSzfM8PmN/HDsycXXnyiq+Wq2KDB8nPDWazbqt8xgX7c/tt+3zG

ChiQ3WfBBHklcL0vnp1jXXoP1z/UHWOjlwFQFkJhJbN8B2HIlz/YUnqNY+JtLECjflbMB3UHcQd++2xdecmZ+2qe19mH7Wv7bPLEq2l0h9mx1tvtcqV4h2Mbh11x/Qadb/Vgh3X7d41l7WH7Y1lcwIJ2G0nSm3V7afV6XVizfYdu+2LphSt+h3m9EPtjzRh6KY1wLaH7ddyvB3MNd5SBjXxHe5iU4rDdfQSLFi2lbkdpM2FHZPtqA1eYky6luxv7

fUdo+3NHeY1rPWshhz19KIYIyu1r4xMrVcQZRCKjd5Hd1WNDLRVqx20FieMFCopzcrNvo89ex94BUQXHcwqCo9IDcAN9B4ldecd3phXHai6Oa1rNlznURZgnZ8d0J2/HYK6U43ZsnONubIYnfHEOJ2miP/gQYxwgy/Y9UjAkycd2J2HUnid7E2uDZCl/3AUwQsd/J20ncKdpoixEi+Yfa75sgVAn0ZLHYKdmx2fwuCEBl0A9C1iU4aNfHkd9y5FH

arrYcwTuyPyDGoYI16dhLh+nbpqYYIP5MlofJpGnfu1MZ2bp2Md5MZ9TGlcWmA6fhEhr8rr7bYdnM2BHe3SRHIGAj8YAy5rrB/toh2/7YmtfVBk4iv8KznK4lMAzB39VeB1vZ3LnYl0UF7jncvaKHXjtFcoVuZ3kwzUfoxnnaOd2R2ohN6Vk/IIJFbBOmp9naudl52AXb+2L1Xxh2iUPGwwXaedw525wFedzHYYXa2BKUp1me3SFZ2b4F9wWQINn

dyEv3WcCF9oBTXAZ3JKV/p1nZz1Ql28yjhkAU1NVimdl5gZnZowR16M7cEkYK7klCT40vWeaAQFbanGunWtrUwgGCdUdl2MLWhp8fxuXYgJ1A34AdDY9kr8AFQgF0cp4CcMOABwMH2MWoBCAEqAA4A5UE0AfWhKQD12l7HVlSHQIhk0FIK1tO6RzC/EPwNn5ljV1mIHak9FbLx4RV/t92ph0Ast4J084rnVku2F1fsthFHhDZXV5m3fFb613+HdR

Q7WmXK/WCkce1F91fGihyMWSfGdiJXe7axSkrgwreHt1gjVbZ9155pMrcd+oa2ZrZetw5X3bacNi23Ttaf13/W3bZXts22eHZJaBZ2JHcTaInWvDf3t402vxNYd7M3zqYEEZDLd7Z46KiwezYtbPh2dnYbd5FYhHffosDgD2UodgjWznZodqnW6HZ7djyD/1judxnXjwNodn9WqKDHdoOV4Hawdh52FCI7qAUa+5HxdjAEUdfi0inX+VhZ1vnX13

amFPHWt3bucOhJSHZWZvPpZzbHN+c29jhyCU92iftIwC93uaEoFEcd8Bykdp5rbFX6QfC2FIF/NpLlcHffdv02MAQwtoE8P7dOd+13vLgtdjNWVIAlaft2udfqtmTXwPaYtyD3gPaodt+3NCwld+eG31vA8ZQBq1YV20yYOABckFUBokBVAZNTCABaAOrA7OCBbXAHTjqOezxhTfGcFOzcwIktXLYQ+FRqQGwhoeAotjc3xK2g9hXX/7YhR5SqqF

aI2kOj6apfixdWtns/h5Etv4d9d/Z7bXwDdzFxNBwH9Xy3QEoEVtW9wOFdwK0KVDZgS/GGRbYgCON3paqlt6U2njej/Sq2zTeqtme3UQBSVxHWfmLTd063k3bM9hHXowiR1jUSIzbANnKmvfizdte2VBSl1x7WIUFl1yDLS9eJ199XONcId5D3mHa/umK231fmidB23DyC9gd2Qva/V9PDhHfSttKsJ3ZkcJd3bkW7d39WRHdmw1EB8deSN0+23M

Byt3+gsuAfdp1WvBJ3dgr3Z3FvwoPLHVfHN0r2b3byV0q3yHc/dkNWgPbq90iZ4Nca9oNWCLY496J523fOpiM0RLkA935h9Ii496h3ivZq9hc3hvei9mD39HeE1uc2n3euaEb3B3a9tyLWQFfEvcl0VQCuAYDAiAFxUYOLLsNvQQ6s/GUWxauLyDZC4FGAz4FcQFThY0lzWvj5phQ95otRCYb+xuMQEHB74WJQ60nzY8zZtzclIVoTx2Ea1u+KwY

ZUq6y3i7fa1jSq2kvKCxhXtnu9dlhXJPZ4AV/8ZPbG7fxafWDRhqkwNNmOg47tcgQrh/eqq4ZkBkW2mOJ09i+rx1qGVzHX7beLd8daK3b3toXZD7ERN4d2Z3dp14UMrtfPtxgJYofKMxb3eNZd5ZL2IHY1wqg1WrfY16cAVyXOt93XkOL6vRZXoIknQak827KXgpPXg3PIoT22rge3nMvWflf8i7VVTNc5V6WUKFSSguzWnFajVsozyMU+NtvWgt

cGFSdWEraVthW2IKlkVbERx8eLSR/ddfaIqdx3hzYit+W3oTc313/gCzZixjW2FjfMUz73j9YTmqF2Do1mVkZXp7efGXpWvfZ+9rDX/lcXtoFXA/aP14KXvfZYLKnWSba3tuD1Pfej9kP3iUy1iKp3WncP1qM3vvdP1xM3DHb6drR2tzaD95P2c/czN1sDb7c7dyP2s/aA4kv3NhnZ97B3FzYdKdM3XffeduYgONY/Fjo2lzab9ivqRNZBd+w4nf

eXNnfWuRWDV2F2MXdBQ/v2u/bA9//Z5NZaiG33OzYbNu33gF1Yl9npgxAj9zaYzfcqFR1QLGGRXdTWhuk01yQp1/Yn1y32xgWz1i5Xf5QJKTzWDfZ81qzGvlZNVxikIYo19nNWVCafdElWu9g9BObBq5If95NWn/ZVNEyLF2CNC7soLSklVlX2+FV/m5LGTc0yQEIyPo01V4APDolADhRjHFYgD6LhHibl975WzYt+VyM1YDjhrNPIAab1SjhI0q

ml9nHWFGNDFis50BbSo7ZXr1lMtuzcu5IIIFbkXGPID5TXFra6Mks0F9biwB9CJuLh+A63yWrcFVn7jDnMYVzWR1a0Cfn2ycA918JjAXqHVjK0otW59q5TefZ4DsQOr4AkDn62jddUdjFBRA8HV+QO3NejM9XXF3YS4VQP/NYUD8pW7XaI13QO+A4C10Dtf3eCKVoHaKhYD71E3Ungw292ENYZuQh3aA/lq2UJ7A469ky7MA9IDiinXA/q9sh2WY

nApBAPyGIOE7PrzA/GUSwOfykCDmZRgg5qtwwPFdayxy3Wog4OcWGY6/YYZkJDW7LJ8HzU3dEUDlR3WlZUDs010g4l0NPm4hNY1+6258Ac3D78z7YyDooOzreDVgTWplcV9rhiDNfLCIzWiXFEyP3X9wdg9f92C/Hb15oPMg8J8yPXdle7aDlTeGcqDwoPjNcCyXAPk9YIDld8mg6qD8YOyyhP9p5Xf5TSDlkoxg9aDz5XxKnL19APCsfADoIOkg

42D+X20A4aD+APdg8SDqAPgVaVV1X24A+6D4gOL5l4ibwPBaLRVyo3O9eR/M33nA8+GdvXng6dKSa39DhoDzJk6A9tkgfXnFcEgLm4/NZMD/QOUQqBDrX2ubiT97P3PY0hD+zXgQ7cqcpjg1Z9N9/2ejqhDzZVtfbNad1mN7UGevKLw1cRD6EOgBWdpIqaZPypBT4P7He5TSrlBjeOotY26MUpDjFXqjbotWkOsuHpD/UogA9BVkAPTmINNi9m1F

VUhHSSb/a2D44PWWIAtsGI+0j1kycoUA9v9qtj/OrFD/8oRrOsFhYPTHdP9zCo6pv5NpCJMMB6OZUPzlaWDtUPPmjlN1721/CCKyYOpfa4YQgP4ame956gHGGNDrIkBg8oD4YP37kNDqtI3vbtD+a3Bg/+yT+SQ1tdiyLtxL2iQMur6AB2x3VBqKp3Uekk5UBAcS/h21pO9/HoKwgAQQEoCinDYa73qhTL1c9riXGJq4EsWDdluVdkWcpVJTkOhV

dHCxOH/vf4913b3FbhR912l1enqpm2fFah9tNyeACJGDhXt1dXjav1dAnVGotyKT1SqFr0o3bUNiRW/wUvV2JW3BlJhhJXyYeDfN32StwNtnmHp3dSt2n2u7LPtwI3+daXwtwP/A5d5Fn2jA+Awuv3hA/t9qE3+32Udv635ng8RTY3ATbLGdcPA3k3D933BDSYd1cOg4Wt94ZZzA/bXe69rw4CN1d2gjdPDgz2PDZ3gSt3loXF9wn2qbfc9kfz9B

zvVwt3ifZl9hq9b5mp9qcOGHZAjiO5d3dUkZVw0h2vt6R383XCDi5aOddiDmb3nSwfD2lIUg50D7W3Oreet1zmdLwXd+53sI7laL/Xg4f11tc4sI8mtqCPYDekFFz2CI60DoiOqI9LdiZ3KNcIjyd2Kztrd2+3C7pFSSiOOI9694PpgRkniR9J0NYsDnBFeI9Q14SO9abCDsSO2I5S9pnWvgkXDwpX+Lmq9q93n3cfgNr2GvaXDzr2v3cot+9VZw

6fDoDjJ/cYt+NWh3fS9tK3Il0WV1uY2hT2cLuJJw4S9iyPLTasj5pn2DZVWMyPpw7C15Y7hLdWOzxl5gBgAGcyKAAOAYuwnHFpdUIhAIlwS0tTwsoTimHBgRB7oRrRElV1dOMQNTDenFmYfxHbA1KxcFe/mxeh48mdrR12pw0B9oHHgfZBxsu3l1arDyjbetdrDm9DtoMjMTrxTKp3Y2fH1RuEBl9C0eGfAGSouw8098AD5WQPQbHGADDW9iJI7j

0B5EeBTcDgAODx5gGsEcDA31E1doWx94fRqiDhG9BOtOOJ0xQTinPp/HCcQRK50bGJVfHlgmDkYR8wI8A3ee3Jy5UUQcOYrbe5YXKOnm3yjyGHXXfptkT2uAe8VsqOxDeh9sIK6NuL8s5sNCkmUWQ3gQ2OgjLC2egx9qQGsfZbS0awsuFaMkbSdcriVm9W6eqj8iGIJ+COKfstvaH7SEKduSfo+B994QjJWD0oTetAjnXZXXIS4AFcw1hRELugBf

sSWsqV6lpSUBdgSyA/ssZ79JzfnGyhMsiobLgJvmsvtQPo/VlxjoRgBaupjnzkcaVIMEhI39xrdwPY7ymQ4IeoYY2iODmPowi5j7caeY6+3deM9WjXpkmn+nrInFNkxY5r0BWoU5RXzcDhY3AVEFcGDQIEhwQRI2cCDKkdJ3EXSAkGUjfWie6JNY5fgSZiZhi9YVERlXFNedWPrnQT8E2O1RllIcmI4uP9YGSnxxEHF4g5B621EesoY02X8cGAl6

fHEDDhh3oqRFfNZZzrlQgyfegoIbViXGPRAL6bLLhOerKVPrR96CZQ1FUmiUsk5nbjNeOPeTKStsWJ02Gy4S7jn9Dv8GONLY5tBL6I8/oYgXOO9giuxggwz+zZXZ2PgLh12RlQTYjVJofpF2Fryg5WKQj9joBh4BEltDT7zKBWN23W249QZZOOcRDLUw2ITYh2XQ9WfnDG4gpCJMnVZnBSHVk31yeO9nGnjjFZn8mMFvEQsY4hSHio/BCcKMxghW

SyupIQl46zki50d8sgZ4+J6kHBN/YpT4/ikjSwq9C3j8HIb490nJmZ/an+YSUhL8APM4MFV1Vfjk0VSfHZUC43dWICOKiwLikkVs4ZNinJwCn3Lq3/jy0Od6f0qT4kLYsBBb+OmOuUY5/RrYkRySHIKZOiMUBPEE4gTv+Opcyz9ZFJNLREcIOJ32cwqROayGyHvUXnaLDi/EfmnI0EmYOIDo4HDDb8ghREJ53B/CbenH2wNxIYTshPjo9gFzGqdG

mwRfvx3mK4To6OnqFGDRgoi2M7whkVgNZITw6Pab1ETjOJBOeI8b2USkDCiGRPGE/IT+O6m3DdYkpqVyrUT7hP5E4zedQpinmaYdhgR/CETzpTZE6YTihOiJz1S/kVlSvgNyDLhE7kT5hPcifeXPbmzrSuGpxOrE6Q9NbJVDDnEiN4PPXoTixP1E54Tm6XTyAoMNBbE6ncHbBOLZdwTsaIOqaZlAn5sFQQT6bif4+QTqBPXA4NXZigm7lJwLTkwE

7STyBPPH19eTY59MiSMNQRAQQfjhkZb4+fj/+EEnl/4cJY+pH4Y6+Oqk6fjy+OmY1O5tpIk4JrtVdVKk/8kVpO7p2hp7GqI4AOc1dV0ujpkuQpU31elOpjYZyZoPxjr+m3j8ZOUuK9/OGUTUFPi5BXJ0H4YxeOQRWXjmPAsZViYhYk4OjILcFoJ4+2T4+O62UeCEXgEhPh4f8Xj4BOT5mQzk4llKpoUuN38AVJHKObjz2R1BBHoYPklKbUCTLDe+

GhN4+B3k4Hjr5PyhRrKec1cv2fdvuOb9VbjkFO2ylQwNBYs8Z68SDk146pQSI6guRoRHTIAhXV4TD1kU+mIVFORkU/5Uv5n8gwwepACHmc/cuOeKsrj3+hq4+o5Wrj+ZVemYtF6bweGCuOIhWpTt6YTFTeCYUlwZjVeMZRh46rseWafxHtDKfwP9nQExAo8PAjjrygo444PACD1hX+Yc6snpz+kELDI4/nU6VOwfPf+ShIvhR6QbHgnuYHaTuOF/

UDj1t2gRXUUNRmaWvfdp1kFXF6cAOOs2RHNs8EYYEV6VsJF4KTaOuOiMAbj92OKJLJyHyVcJsyQO4dv5e20EuOXmFmAxLLeVsYSW3XwKszjg2Ol/iDTogdDFwsqlnY3iZVjkWZmiEDTloVtDAgO8dhJbiljg8gtXBH59Ddwql+qlyh+4m+lO2OoUCFj78wBiLzTxXoC07Rl6J5aY5MiemOg9d2Kx2QNPBMtbpAaY5RgOtPtygZj/AE75Ti6XaPa7

DbTw1oDClHiLtP2mx7TnaPrKH7TmtP206HTzmbBLe9DweLfQ4xvYDAKAEWAIQBcADlQIwBbR2UAFoBSAAKgAUA5UEvQUcBJACOkYNKEEgtkDPIloQaVz3AXqFgVESZvZD+4aKRm4/HEB6gN03oBw7BROO2VRzROzj46adWJTOThmFHSw+v0hm2wcYrt5y256vlG2MV3OH/h66Jno0Wj9rTP9OMrHRo5lSgS09WhbfzyLLhQSIHt69XdDYHS+9a5R

G70L5nApBOQuVGIY6tNX8QHz1hjp5xL5X6kGuOrYtOFXdAmaHIzjECAggE0PC1GpZnR12k5wEWMYZ81hP3yFEQIk6blrI2KGwDu+/JJ0EE0QKRhlnljngNX6pxj1LKSY6dqUG17Y+1juDKOeaFSWwTFpYYRT2OCFd6wlBELGHRQVVlu9EY2f3FUOpkkgYjlY+yNNTYKKCgNcBUUccVqByPi4+kagNPP9SAS2fJFBUJp51PXY9yEceCLU6TTSg9br

EyXf2PskGtTyAWweAVsenztohEKZOOd1DA4NP5eDnuyWePNjnnjyVDc46fBIM0bnOdgmQpmqcZ7L6alKYaFFihjtBJcPWDk4mNXF9PihW0Y6YhzPBBDi6nKCInj3wECdiPlyAK8s6qzrC1JKnxaOHQhlCykIn9Ms6SMbLOlewfjsIPikm8Yd/lis+fT8G1nZxc7VJP1Ppbge8gus7QwLLPX0/KKLxONE/KzprO3KmqzxbPgk/0TlxOy5Iqz6qmCs

7Mht6GPGHdU1kIBBBnj1LP+KmJCcopAE5LpqXhLDUizmmBos/pgDl06JkOzoBPnbLuz2/rgZgzQs5qMIpjFsM04E+2z6ekLU/1T4LODuM+T5xdpGo/snGBeeJdTw+T5SNu99BPn7MjgML97btEiRzOFsk26fBOcBTqiLlggKm2q99xWZVkxXIJlojVaN/0P7PDCd2IgGA/jWwNNuioTmMJ+kCy6Utl7oj0zsvjqMH/Fy8hncGc5UcYxxDtKVTPiu

HDiItbuXm1lKlo5GA6IDuCMY6LScTP1yI/TxfXsGi8CQlYuM/hj/JpU3h/BWXPv0/OTRXPwiARjlfJVc+QVuXP7QLQ9g5GanonkfwwF4uiQH+pUteYACHlH2GAwcrBLuv0AIVBqlujDkKPEuBw8AgJ0JAUA07EgTwD4AhiJuw8dM9FWAnStRNh/MQbQ6y89+QJ5/tInYs7UkUaiw4fi3471nqAz66OvFZENyH211drDjiqGw/o2qmBDTBvBxHQOZ

B+ER5La2PU99XL2o6LFMapFpDx9vHGF8mcQUqL0Kcz8ffYxoEvlD3E7+grJGvPg7vcE4n7pmesoJ5K9yCGR0t8285Vmx9kojViqESBoaRfljKWLYQHzh6gh89irJ/RL2dJwVGWTGisOVIIDyhGCFlyKBRH9Nlol8+U4FfOGtuJ+5DIbLroyGjOnYVw+ZfOxhXV69E0c2mbsHd4GSkYA+xYz86A3C/PCUoB8UOIdyDmwVvP9oFrzjvPgovUKa3Itf

FSZt1OVmSnzuvPifuLymDoRSTKdsBn+88/z9vOZ87f+hlPBSkVmunHeCi/lVC21vnHVTn3eCj4gSZQcgThjhmHdjx5iX3B+dByei1KIuOjCMhtAhO2HYAv0UCmar03HOfAkZxgujagh8h4yLFm5FWaOAI2KcGASEgoLjGFNImoLjguXOgfFrkIKNx7ffgvJnnbSfsJ/aEfveDQ9PD4LmAv2C/ELorOWZlFt5RQYjGciRvPLojzKcMZmULaXcbDCD

B5dAkUikF4CJmYtC+7MHOCXyB/MILpS5WdLDQuTC8BUYe0ajvAL0bBIC+o5IwvJ4xdZbQv7lZyQPCpnwCyiXQo/MDU2QBgealR9NxmiMHM8ThJ93eRqAIvto6giUeJUfSYgCiAOGAr18QMpMQgD9E5/cDMFDhc7soz6k96788zhNIue88AGLEULZHhC8foyhVSLlmZ0i97z1H7D87k6THgzVM7K4eh1eGtZbT9KvR5jR244/NFExoviSgQKIHZTq

d7QTFQcXCQ7dKrui/cJlouuNVtaMlYYRDEgLovOqCaLpHh/pDvhYNgy/sBy4/J/OvFrL9kxi8WL+QTRi+aL2UhZi82LvYvBRBrSAIuW+f2KwPiJVN2LhYvji9pmRvO3MGbzlgUDi8UgLYubi9YWMQu0YDZm5YvveFWL0nwo0neL1phgSnHVFLhyLDHEEUC3C/uLuUgW88BLlBc25XQ13LjM1FxwlE3NOR8T+YN584wwTRnrequLueNep3EZmM15w

AbgiYukJgiue6gLQ5VUlkKC7SXqaE2MwIsl/1gs8ZSo55VskoonGCKXW0vkexbycp7oH9lai+52TgTEjfHlcTOHlyRCHh535LKLrXVFFDxB10JH9CfNgoo7rVyL04rt/CZdv3xxGaF8niqqkmfgGrVaLu/EKIRX85hFGLH5XBTaGmJz4HGg5Dry9RGyK6J9Q/SuBIvOkjeMI0vLMlCLqjOzcg8YXNc4eAg2WZPZG0R5WRcOY8nPMTGTS5AQPOC5O

pnnf/OMi8UBO0vBYk4SORhl3SkaIx424mcBMLgPS6MOYxEIy6HoKMu/C8ouzeJ7JMrugfGvEMjLktRoy4CNbMvfC6WwPmmAy4zLkJFjPV/ybucN2YSy2MudpXjL72QrMeOiG+APyi6pz/UyfHtLiIv+XIkjcgoy04SyzUvFXywtd/P7s8GMFRR+ZVbmExl/WALz8bMd1xkZI1Xm3DNePvhpOjFLz61AxElL5v8ukEsLqh10/qaVvkv1o4nSLLGEC

+qSXJnozNFtcERgLO7oEWOuGLwVSihg89DmbDlhZI3zigot89XjhPwnHlteLBiOMznz5IoF89PpIn8WZjwMcYRKegMi+ddR8+RpcfON32wL7+ajjWr0fUoES8A6ZwqLi/luAIJNmsGwTubn8VYL6kZD1Y08RyH4uHvE18ARC5hjrgvyC77iDGFvkiFkWeVBXM0msgv/afOXYEZLNbSXOpUTqpwtVJomcD+CPdAjuGeaO4uvdn4GR9z67gqizgJ2V

EOcGPK6LXDznsCAieTBE4upxDOLmTjPHd2u+f1EUhjwc3W9XjI8MfPm5Anzr91EjAMqSVw9Px4KyYviS76IfzrhgiiOHaJYzCsz0GZcS9pL3tAfmMmN+QCjuABwrBdrfCXLhzBiM88tKyuFo/hHRon5S8tiV3AlS5mhid59UCtovsxRxFP8qIWki9VE5dc/JrkgaoVi5SUQFIrqy4Fk9jE6y6XuVinDV2paPlEuQtluWjAQ2DfcR36QEnCsbEQ3F

VUlV1XZy9RO/vxD/TYCCQzBKCmYLHI3+evLvyvysVQwcz4CWh++FaF9DgVu9UkceMmia2JXqdj4AAZRZXO2UAoy0NxlrHk2Zq6r3erW+YeDzaZwK5USXSWPKOf9TxgLyD8Ef2gpgRfoduJpC/fztmbEcja9+0Xe6QIL6dAiC7QWNpPLQ42r98Otq8MqHauH6Dh4favkBiEt9bHvI5+5eS9k9EWAFpRokDp0eYAqQGmAT6B/PCsEI4Nkbco9+2ybN

nPmRlQmQjnlFurIUAi4r1n27ZbgS3IQy/CLmpxwy9hPXsuXS4R+bOPf06Th1tiU4cAz+tak88Ztpy2P8uqC1y3I8h4AJij67aJPAJxH+1kN5vyLnuLUUoaBbcefHu3uw9V4ZkmqrS0NxBLG4fPqqvODYVCYG/n+FRm58/I7vDx/KFBJrexSEJ66svAxY6ULUj5r5HlRYWOUzVLi/E/LzIv4PglryQVuiH8CLYQYukmDeH9xa5cQSWvla6FhHSu/h

H+KLTkhsC1rpWvBa8fgWvQb6f/aw2uyLExKSLwda7Q+AjBtuh6lCbMglzDeCu6wnp7qylSxPhBiZ+ACmXiZujEu88u7HPc3vNsacrXty9bmRXnyTiBL2Ev4yZz1UOvHpH5LiOvU4Q/LpeJ0S5GhzyIhS+bkUGbCCH/ZOUszK+UyOux2df94IJSpSGTBND7r8IrGXsx/vAGRSvWxS6DNUuvymwdrt4x1u34GdOO40+t8Ouu3MXKbb2vwGSfFWNwT8

7+2WuuS687r8x7Zygz8VIImcFvSDOub6C2/BsjfjQbOIKpoRXSVuOunoh3L1flQdcp6BevKkjgd/qRkq/uof3Tii/rkt9JvMiHVR2QJygUCW2LnY0XLt+hHK/XweNI4AgTYAwJwmBcyq+vwnk0WW9mgK2TrgcBHSXj/GS4Y3Acrt+u7iRHz3zBzikZ1dGCX64lL2lpnlM5r6Ods4B5rxrE/6+vrgBu7kgESC46+zFfSbelwG+XLyBu5C7YLjCvaC

6BFEoviQrKLjJPAomiL92vgi95L+AQTrS3ry4vFbBaG/hJfi+FpUeuCCYYqNC21i2WLkvbUjC+iUsFu65PL8Bkzy47grYRvogXuH+vKMorrjeu75ISruVohG4yrktJRG6NbPOvpvFtY6Evkhf4UkXhq1lRLz8vU68Ebp4pZG4aOXccncCjrwURD0sFN7CMp3A0KepBuG52LuYuei4vZg4vAhMTSI7hNoZgrmIuPa6hAz4zA66/ZeEG3C80LhnmHS

LIb7vYKG+KGtCuv84ELhyEH88+iD0pBmqbaBEvApFElXaJkG+fAVBvhGrMYIu4Ci5dpmwNt841J+IoIYuDiDYu5RAgdOpWiOmgbs6nqek+pPJuZa6mlDSFrE8g6V2vuHtKbmgFkMsqbwpuuVmW94G2otfEvXABNAAYquAAkgAKgVCA0cuiQDax6AEscTAAQgFHAF/SzBtydBzRsETYYr8QwImLIAIJVl1iLspXKuzAL1TYnEvKtcm2Y/LwCB1ItT

CMOeDHePcst8GHzo7a1/tSQffoVsH2M5BTz6sO087x8YMDDnspmJHIP80fcIuGmo+l4jLw2o+Ftszw+AkcdcW3SUYUB2skxC94Ykiv5C4wrlBP784TDuwvT5bwYo2vcG/8ZiFu61UyQTxuFbpd+EJv28+AeZ6F+QTobiviu0k3A9FuFC8Rb1JNli704sr5bTt5rsFuEW5Ib25FVa5nKJ2pGG4pb+FvwFWpb4IjpuJ/p/Wu77VBbplvMW6T2PWvzy

ANrwSvirxh4QOOU68dJMryIm4PKHpBeYP6LjhL1NidJcSu0G/ib9HrJdZ6W6wIhi8Fz/SGsS5A2R3dzIRlbtVuBmA1bx89aW/tSIFLVK9Z4gPgBi7SCPT8v200b0VuDk5VbkDZ9W+tb3JXVW8GLygHhVe9SPVu3W+db0yvPiY5YBrQvqAdby1u5W8Nbu8usfsFCFJoadU/rr8v4U1Prvc5BK1QyTcq2W4iN/lvOW7dhVkvfvF9bBTymW2NbjlRTW

/KBb2u3eeyQP2vAG5Jb6UgyW6jRgEnpZO5Lm+Bpa5xbk56nG6RZrkv0YGPyEYkPG5B8LxuR6+5nOova25chAJugi95icvZm25ozpyucjNsL8uyYW67b6tuW297b0w5gW9hgIdvu25rb0duKYarbyX2R266A+dv2iWjiO4UkBjiFFMraK/cL0wuHC/Lrlyg/BFVRZ4GLen7bqCJB27JL8NuQ7g/srvOekEvgPfrz+S9bq1u5pLSKYWu0Hlfb5/FhW

+bcr+v7W9obgPAqm/y91N5yNzVr+luzW/7ufJvZa4IIGJ9sW8OLhYv3mAOLgpuHubOtBVu4m4ba5VvgO7Q7n+mYnzhb9CuqW+pW5pv0O5ifK3wxC6Jb3GbYO9A7jDurgmvbtxvUO7g7sDumm5sbrYuUO4qLvy6X26gYHlOEqaJLjlvBMNdU79vuO51aPqJ327lb4OvFChcb8hvb29pSONv2i9VRWQue6gY7+bo1zirbz+45/E2yfcPx248LswvKh

3srxBuVy7oWLdvh/gmUccvgJHGzZPmCW4wrkFvphxfzkxjQk5AjnGAyfBaIQgwZC8Zxo4cGiBrL+KvW67JhsZRf8/TLv7DzqooDazv/Gds7jmIAu8wwEsvN28pb+6sF24uHLzu4q7qd3zuTMh0749u8GKISJoIiYBe6hEJj+Wk7wJvZO7faS0vfVOSLpVin25Fr39vGR1mdizKTrneqvd7hO6zEHjvx6QzrohuiMHDwJjvaO/I7kITjy4jeCsISF

k1aEqdy27CznWOw26BRiNuyY8Zibxg6W/zb751o2/RLu2vQqVzb9WuGW5hWL4vlK7CYDqI+W/JtWl25kXSbpWJeyf5KObuxW5oLNLvXXPwe97yUEg0XfOufk1C75lurAopGHfwKS7GgcxTPjJMipWJMm87WbvZ9yc1jbqEgG9JbsLOOO9r9txwi25etfeuJQy274SBeNTI/YdvwbM8Jo7ugO+ColhIV69bmNBJ3y5FbwDumkHtDFruu7Ta7tslxO

6GLwNvFEQQb1+vhohEOM2vHW+9bz9ug1elLm/PzV3Od3oI/W8BXUbAPW/X7bLniQswIJ6dGgTN47JKA25Z78H1iEkds1jOgRnp7y7uZlwWEwnuLS67ViVrDS68YLnvGe/F7vnu9S8Mfa0vZe99bk74me/xsNpu0DZEtn7kgHAvEDgBPU2ckY5hNACGb1CA50WAwUSAhACJrvRWEwJBEIpAXNCIzmiEEGkZoMJVsBAaby3agK+AbodwzNxw2zLuie

PSDuUgi7YKj85uio+AzrrWca9nq0E7Wbd/hwwYObbhIDgJMnUfcMppWNrjgf3owfC+b9DOX8kWiklHWa/OWlBHSdzEL/BvfBhM7xJvuW8ULgtJTu7cJ5gvJ89i7sJvSG79HYdo+UQJaUvuiO5oLvP1EO+eLvYuI/Cp9pbvsDUk7tnDqC7gLtXusuGu7rVMlmUH70rh18/vbu2VL1In7+vP0293b5uuY3HULns54BEwqa4qYe7aseMzvbMwm9fvGN

mJ7iBulWLqbtQRSm/0Bgk0VS8L2NkPgsn8LstOYG/apdE0zO5k4CzvnpbbGhrvRa5VkpXvGFtISNpav2+Qrn9v0gkMZ+zuojgQ4Fdv1k0+M59vGu8vBY0v/e5ZKOUgOu5abmJ8/e9qVWAfQB8xL2PhmO7o7qnytS4c72YV4B7I7oIriu5CrpHglWMQ7vDv4O87NDyvL+5WVn33ICZo7hAeKB4v7sYQr+5oHw3OQbcORieRSQEwATQAhADDADgAWQ

H0AcDBYemOYdQA0IEODTfKbe7ygK6I6hMtFE7slbyNyDFUjkV6OBboVcTPRa2ud/DbE9e0VVTrYtCvffNEFDBIg+4ujwqPBDbD7ptaI+9lGlm2ixx4AR4iObf9oNNsboKhxRJQNlMW6DPujkgj9K8N/m9z7sdbnXRQbtcTNB8Rjudukm98H85K0W9IrzSxHcg3FQjvdB5y448K7eQo7phRZ5XCHmAG9XPab1b2MbzYABABjmFaerYBCADjUItwtg

APvIwBqRpgwC3vT07RgaYheVtnZYbV5B+lpppArY+cYDaOz0QZ7q7ulG8tZjg3pAiNXAgJMYX/006PGktObl12jB9LtkwfEUdKjngH7o9rDhOino9ripDkIKbJPOE7xw0A2IaEXB7+qJ4Bt7frhlmudDZWiocOGSxM7lRtbu6gVDyVCO9CbzCucG9b7/YeCCw4r+iuoS4GmHYf6O4kru9opK+QLkuk9u4ALvvPyHwqbtju9i/77sfDLnS+L6NlMK

gHAFvujh/C7ze6Ie70rwEeMW7ulOhJ/27RL47vt8+MLidu58AMioQqzeNeMqQUaB/+1FTvCu7TKtTdz2/vTtOvwokxHrrvG67ZL31s89dBWZFuO29RbgmU3HCY2ov8isjXSCkegRipHtZ4khDDr7JAYsaFrxVhKR49jKGJse6v6TWMLT3bbpkeeR+p2a3xV0Kx+Nk7xulIHjAfyO6Lr9DAjxOg5Griy25AbgwJK/jFL8UfFR5VrqbuTW5fKXkfCG

5x7gUetR+wmZbu0/3Xr+OvV64TVCDvpu91H/SJ1O6jgTTuT3t5b/jvU2527oGM2i9xHxNunR/Zbl0fDa6aHjEVezF44r0eU2+27w2voR60b2Eem8Xh7/RA9VjI8P4ePcS8A21uMe/kb7ryLh4eLluAo2/R7r8vkx8cyVMfIS+4r69NEx6zHgxvJu/SiO4SzGynE9grCx/RL7MfRu7sCQUIx+91bi1vZW/Vbl3Xl6+2ycxhcePUd11uP28Nb6QJZn

aYHlZWfzCDb5seDW6bZ6GvRxFhrknTye+DblseLSmHMNuUxpDc5Gpv5nabHp1v5W9tk/cvQ5iJgYce1x8Nb8yhlC4ZFVQuOq67Hinuex4313ZucK4Obg6vQNVBHtNveqvKSaYu/xT5joMepi8h7laEQ4nEAmyvKlSNHyDuZu//Nny5GIFBLjvSCAOVH73vVR/KKHKvW/BLZST4625A7+gfHtnqrzWNBnpUThkeuR+FHmZDRMVeptLSmcD8weMa56

0JHz34xeebcbVaKFBNhhPtK+8RHty0sJ5InnFM8J/InqFuER+o8nY20MCpGA7YUJ8hb+EePC+o87JpXpFcCNGwYJ44no9u2PhUF/ookq4KZbqhwGThHoSeq+4Q4iKvi1Cirm+VBJ98bmSeNs4j9X62Aq51b+PSKJ+4nlyuq2uE5c8uR920nkSePx+srxaV+65Wxnbq1sYdhnXuO81vEQ9PLRztEIQBZ8sRVAoev1tqAXQbSh7ESOHhuM44dvbV5B

4gyVBjXEDv8RqZ29DbHhOuekTrY/Hv3W8IaP73KFbjztZ6FoMTz8sPRPduj0YeAwonUngBw4q3VrPOCyF8LjzRYhtR3NCm9WVEV2bX0caGLtwI+w5z7jYfXnq2HiIe9h8hHk4ejh6L779IS+6PqCie9O81rsvveGJv7kpByG7iLrlvTh4an5Tu3a8Cb/qfwm4YnjwuOM4Dr7keMJ8pxCieOM8Q7hxuGG6012JvG+7a4z4vzG+tUMpvZG05H7vOMm

6WiFRvfx5tH65itW/2L61Yox5wTDvv5i+xLxM3ux7lb0yjDG+1HvNuXymzE8ku022e7oF4rR51HykFg/nEbqhvrBthuW8eoe/nd6ca2q5E3FcrBukzH6sfThrNH5Hv2R9g11cfKe4l7iy4wp4tHsTvEZ4/b5GeLJ6fWqyf81Zsn99b5QFOMEeAmSEiSVnRW3n1AJIA5UGOYZQB2cWuEUoe3RblOibAcRAWbtpUsBGeaw7hfqARLk/ufhDKb7ZvVa

z/a5AezS4innoffBuhRtxWE88xr5Kebo5ubu6P0p74Bt/jJh60s+7jBwhCvDWBpxCajjJppBHdKtXLgrdcH7S0uo+JhztL4lZyG4cPD1Nor3vhH8/X8HVKh8j8wLDuamuTXUeHXu6qLwAZhQz+7obufe+pO0EeZi/5hh7uxu4FSNpHUZhxHlT3vZCU74zva+8hHxdvp2+Pzgye1YJuHmgI+R6PruNrGp4hH4EfpwivzpvPIS+C72Ofw59TnssjzO

+sZAZlXC/ank9u4VOCrygwkeDCrmk0uZ65r2BvVMYRriIIEfkrnqTuSm55nxpvahJ9L9IO2RpX7zif0u+DZi+U4jE7n80ubC4mn3uegq8SL8ueLn27n6SfPC7HLp/uC56o2KeflJ5nn8Rl+x8VLwtPF5+hb5eesi4KfTiu2+I3nhEeOp+3nuivm89MLVgeOm4xvZgBlAGLAExxnOHKwEeBINqqUa4tokA4AeoBRFHpn7xUyoiMtD1yBsFdiBzR90

H+YwqJOZ4InnDbD24hLluvIa6Obp12c0rOb2hWLm8610wfQM9xryHHq7fhsHgBAtmRh+dSm4LTFG58HIiBUFDOgrbPVvWeSfErz2qel8J0H+bbc+Ri7rqf4u7eL+Iewh4wSZOeFC9znnMed58uHx4u2p5Hn4SfGifBL3eerh6vbkaeB25ifUBfeF/YX/hfep4K7oReeF7YX9Mekh72R7Xvbq47zaTZ5QEqAKeQqQEmAONav0C0AB3P5gFQgeYApo

5n4j1giyFIXKZgdI5sGu+hHOaNlG/UctNS8cCuq5MzIAAIYx0yEE7B1y6iETnKmtZ8GqFHR6uD72BfQ+6xrkDP6GlENuWe/FanU7Kfno8AS4/iIWzWSUQGrBgloAnp8F8FtumvS871vQessccNns+q8+92HnweNB/Qbv4vja9trya3LNeyb2oIlNutr/mupa+Gn+pvW57gb4vu8l4Frt03SO7lrvP7zZ93z0IVUTM97/7vQG+N2IwuLZ8ibj4vDp

+tHjWuK+53z8/OrZ82750eQx89VCVuGTD6X86eoZ+/rlzLul5aX0ZfBfnvrhjpu2mzHo2uba7qX36ez69RWJJ3UK8Vr/JfS2ULb3euS2/7HNduj883wDKtm/HmnjxEE57KLl2kCR4EXm9uDp6J7p3Zw4GHr1jukO6qOuru4LeyLme4Qcgx3VZElK5Arq+VqOQ8r+EKOe4WFG8fxl7fHvucBe5nKY7ifzHRnu6eCe8V7+ufkYgR+e+3WlcoocoIw5

idLzCoG58mi1W4M273bi0EULudLole+5GpHnrve64Ebgle80ddL5247R5EdXkzDY+y9SlfMV+JXlkf36GWYwLoJoEacqXuDS5TnDyV167cCCdtYYEqcwIV8OjQiZFeXWnuXtruhdilLrmQfMERgIFeWdgVXgmwlV7eXzFQPl6wmyv5NV6zWSNP266Hr/VeAHdZH8VeHCklXwUv9R/5HqtIJWhZXsvxDEHZXg3xUZ/Drlcruu4DyuleIAM5LpduZ2

+uXk8nyIDP7+ySvh/fR1Pn126uX5cUnbPyaJWVamgazrJHN+6zgDG4op52wPnuD879XmjPrl74770eJl/KFYHvTl/jEfhjPe++LgmwIqcLKS+R8FDyrvl0GojqbwIuXl+XHv6yd699rwteQh5zn2GA816bXu9ozl9uL4ZfLZ5mXoHvO1+LbltfIxmeH/3AGDg7Xn2uu1+HX905Bu5VHt+cJ15B7veuNOuBTW8fBO6nJ1kfzR/dX0mp+i647v+u06

5OFQ+uHl6iTUXuee4cBBtPKzWLrvVf6g0Dns9vg589H6nuVV4AYACQS51xgJuv2S6kbx9cVS8hXrIRoV5/8E5fm1/ICQVf9S526EVfN1kTX8yeeOQFngefYB6ZT11eN17hnj/xxjVirxzB4q+djN1fskAnr7T0XcBulUnw0N/g39sfEN/rL10C43CcYZgdezbZHwjeCJqHLlOOtm95LzdeMN7Yb8uonF5Kye1nex/Q3yjf7vQjSLVBO4kLlgGFw1

8uX+ouu5M77hkE4gyPLydeh18A33OpbF5Tt7/R/8OJHzNuatxS7tPxpN9ZiWTfIGXdHu9fOi6k3nFiIK/sXxmgb1/jbjovL2+DWwG3Q1oUX99b9QE+gOkAsei4QCeBlAAVFWcymSGiQMQBsAB1CxCiicsq1WMwV83fmFpgJDIWbykJyFF8wSuVRoD30r7vz64GZAGHf4BarjQ7MjsRlB133F8hRqy2xZ/4NgYe3XcNrBy2So7MH+GG7m7UsngBUa

tCXrHCI/GTS8mvN6sEV6+BKejQhoRSPSsIX5YeG4ndojwfqp6bh0heAh7L75qfTZ8Zbwae2t7iH6hffl85IwvvUAOKb55eXmHlr5Pbpp/QnwINIh4oXxIe99v+kJae8W9Ss0Ie9B5iH0bYgG84byxv1SQbz1he0x4GtpEFNp4btN9d2whgrySvkS6NH4Ru5G93HDvuel8PsfEfHp9UbkRvix4g7igx/dNydvrZy4lhXtwqQ83/bynJCplSKXWv3t

8iDOXvO0Bpkvsx0R9e35NvXx4+3p6Sf1lxX7m1cDFO3vRv1G7MBVku2Va//KceSx7O3/Rup24073ejz4Hh3q7ZMd8obvlfCFCosSdI9t64bjbfAaS3XBUerKjggn4eyd/W3kUDKB5q7q+QGOxQ82bf6G/m32efPNcOS8EQBysZH0hWRR7F8qXv9M6nQXeBBt/EXoIuxp6wHqWhEvA2XFo2jJ4Mi2ziJ2dl3+a0pJ6XnlSKL5Wy7y9J0FjTGzXfvJ

Rfb3xhGF5s7mheFgb13+AQDd5ZbjhYd+7X7oXZWnOV395hVd44Xope9+4FElNoRd4cded8W5+5rsn9H++53/OuUyuP7mufeZ6kCdOe347StVxBf+647yAexa9/r+Ue6qRp3x2qGl+AlJpeWu+4BM7mSO/QH0Dv9YmvBXhvihWJisf06B4e57PeDN+vkSJSljAL3pPfxRO6hP0fUR5B3yz3K9+L3yxZ17sSFCWhft5GLzPfCm8b3zAlYx/vWeMe8B

8aXuvaNi9AQfTxrt4aLjvei95G3/hZFt+iHz3fb+4ab6peWp7bX3rff+mrnu/u255Aep2ee87a/fktrd5ybjG43t7UVPb9wfCoLpfeT3YxnkNvrg8PU7/FX15JH/duPO8z+G/eFN/JXrXvJXcNcq3zwMDgAYcg9vGqASQBPoFqATQbUIHiASoBUIHYAUm9T05YSeNNDBJREIo6vc5qca4Jo+F0tl2R04vD4TBub66+sf2Q2ebVj0xJP/2u3EWfPF

4h62ta2oo614qPKw6y35FGgl+h9yZu4fYbts8phte2W1HcgwXjMayNi891n2rezgmz79yqAW8lt+fD6p/7X8dbhF8uH/Me7eS7zt7v/MA+7sOeet95OIBuPMt/lCseZS2AXwHf/R7RHi/0xt4F32afz8JxX2NerSwr3+tvHG/qHyOfsd5JLP26Sx6OnwZe0wlD3hjKHYlW86eEgZ/6JBGvdsB7JmmJbp9PHi/eiy8UNgV2iUiU3wkDFG7pLtKu+r

fhIRxLNSh8PiyvoVcf6mTi1Gdenx7v3p+gdKqvq67+kazZpK7kPP6eq66oWtT1JEj1tNies54X7sXumS4JjZav/aDnEYxulI4HX8TfQe+XXo49f+QxQCTE2Vd9XqOfYe8ELhs3KKCuVDxF2N9R72woCK9x3R8xZp2PJ21fE57ylugvuEiTTy3H2VCAqA/usG9/X3KImK9L8n4QMImo5VA+AG6nyKY+hj5wP9JbVscyW7230DfZKq4AcXUC0rAdys

ARVA2hSAFHAep7qgAQgSyRT07REZprLKEfMd0GQa47lo/Ir18zwz4Bn+cIdEggry+q18UQ9Upq1Cihm5C+sPA+kt68XwweQ++MHvxfw+8QXyPuLB/WongAHuuoPhvC9PGQ6F5u/zPG1gUQ9HvufLu2ZkqHWiZkB13q37qP0l68HmvvJD9yXyQ/wR6YXk3fUu97XyJvup+rz0/fMO7WnhJvqT8JPtAfvl4bnVMl6p+YX6ceRx9TX1k+459kBbnv/W

5MLvnvut8Gn5hed27fXrNuUyvAyC5ee24g3r5Z+t+4CUPfeF+1coOEFd9hJQgeJ55oXSPfRD4yLvP6kB+g3rMRlt88tIffrp41VkQNEu5Q3up3xUfEF8jdvZGMb2PhEjvYGB74g2uF4Q7u5l4Ezvw+EOCZCg0xIi9zrmkvru7rgl4/hy8TSZtwdl8M3i9u29eY3wgxWN+9PlkvF+/ZL8o/sQp+4T4iDy+r74cp1O7HrxpJ+c0vL4kIuVid1tGlDV

/6PxQ9qq5zPlgpRj+rBEnvIG563Z8uHokXH43DP19XnryvxsG5o3Qvqz/R0Sr2cskf7vMp55/aJOkUry+LP2goGV4vqfsuincLP3s+0ChLP70vzQ4+U5XLt2mU3TcfzssauZDfPS+QBVFXGjfdoeBJE0kiXRc/ay4pmxgphIGHqGSSm56+RSLuCeK4579mHT5WGoaKJv0b0JMucy8rlNw/Au645q8/vC9IMAsvRsGgHwWegjzzLm8/Xz+rk7QJ85

7OzBeesN+/P6zk3z8p3ss/D+/QOdgZgL6KlauT017qPwTfUy+LLoLv48fk7j0f+mZ4NaPpzT5x2NXuxe957zc+zT6XP1ofNDSjHtOvnO9nyGGv+yirrcHfdK7vtAY1Wy9DLycfZ89dPtQw6L/IvicfKL8UP09fme8iXcceHS7hr09vQz8j9duOyL7CL9i/uYnwkmke+G767mU+paYIv7c/yNnzP7Ve28aQv08/t6UoHgce/0iHHoC+fC5AvhcGMV

82CZ+myy4XHg+4zbmPZtMuou6C7sQ0N1x/uT0+sq/WEpLxL4GYqRVhfYOsvj0/6Zbsvjce1BUQLm2QiN7cvzKucGOdgg8fBq94VXy+Pl/8vqUgGj8vHhwcsj5L19KvbL4Cv968rorcCS3HxylCvjKu4hQivzCZ02Fn6fyvI4ANPzGTAIj8vjK+Xs8gnvifhlE/VW/q4r/cvhK/MJ9isbCfSJ5dX21Aqr/CvytUjq9B1bpWfhDSv+K/Mr7a6IbA5s

hjldRJyAIcxwq+wr+KvmF9IScUmksJaYCQjpq+bL+qvnq+Buk+MSYoNbsxUVBlXL9Gvg0wFr6Fztxxvj4FSbha4JQcv/c+dLNJkr4+m4L2vpCQDr73PtKoZJKa4jnOED4TTL25TCrPn1If2SqEAY5gyQAQAZwAhUDCZAILg4kaQWgYR4GG0GE/nc89HQ7XYFUyVZ6XmXX8n0R5+FLXotSpn5i45CcuX+4REEQ+qi4krgweYF5I2wYfQT4QXgJfU8

/Kj+5uPzOJrkDFMBHtm2tLQEtbtmLZnF0qCGmue8MSX75uy8+ALbXKA3y4P8K3rh5pP2W2fG83n6jzLcv53pq0Z0BbcvyajT9sbgYwVGxLHm0/yLDtPwVvYWjDHu1vox+KGpoeR+5aH5j0hT6OHqjvom1JXpfv4z5THzhfBoPaGtM+WG9/yNgsKJ7LC3zJ5j9J7mYY6m7tn0W0W5AoqXSleRJq1DyVUb633jDSZNcRv5/uXaH3FTfeMm9dv6dd/z

/GzJ2/vb/e732+TN4yWoBWVvZ9tjG8J4FEAIwBlwGUAU6ghWAiQQ2Rl0RZIaJBNAFj7swbPD99ifmZDKngEfzeYeDi6NZf3aPvkLM+NOVIgF3jEJCg300upnhOjhLe+Pfin9GuJZ/aioYfPXZGHr+H/0T8VjSyk6K0stybdV6Vvb3Fol+A4Bg5CMD21Fg+at6cGYtlnawa30GOcM+XOoAvw57a3gdyVT+Hc/LvJd8n39renh7QngXeBb8IE9HeEd

+06QgTZb6THgxveD4BL6bZgj9CFA5fw574PqVsHu5JCaI/oTcPbpeeOM4Ij0GfKiiILv39bl7J1ijfE6+VmW2e6T7TiCHYDO/LPiY/BrdOn7vvEdmAfiBvQH6TjEFfK2ZUrvPt055lLhcY5V5jeIxuQS6mZW9IPK63UJQXmbkJLnNeSS7z7bB+Hb8S4l1uXD7RXiXY+x5q1NUvSH7vbv2eZ+6AfsY+0D9hmeTeyV45Ly9p8z5dpT1ee69PLn1e3n

fw38KeuaQEfncuEsG3r06r37+dLg+vhS7a7y3fCYwZLiUpVWgyrOUfxS/GP9+uw2/vvsMcYj8ED7IvkH7RiW3jz96GL5hmkH9p7jmaXx5ov9IzC23rPtkPpSDx3tRuD75XnhUuGz5sftnfdD+Wnj3Z1L7Xn5x+kW63v/m+BQ6PnnIvb84xem5fdb8onkPedH5MfwQQST7wbzxb8z9kfyU/+N+lPmOfwzjlPsTeeH/4bvh/lT9X7vfeS949HrTfMn

+d323fh+7xLxWW4IMKX9Mnil6YvgDuvy/3X+3vyn5d37vfgK/gftYuV+4KfiGLnb/2nhtehl9afwXD/7/1L+k/8n7qfwp/aF7L7m+/uphSfzqfhT/bX9m/Wt7z9YJ+Ywctnqk+QI/af97vXl5Ajq2+AH44zw4eIR6635peRl8Wf4efun4GnoEepn7EX7mf+FTa3rZ+FC9GfoA83+4n4GPe/74b7vp/AH6pWWdewJ7blRSvGn5+L6DuAUy+n56ezD

772r2fSS5XX/7eKd+9iFNeqe5Ldgx/GDY5B32e6x9N9OCDqS+sIIu/xlBYfx/e2H7JHjIysMKwR/APUn6kvvuukn4Ev7Qw9l9YgOnZhH/Dr0R/ZYwrX55Yfke3Dsl+UTagLu+j814A3zIM6X/g0Bl/nQYSfmtulH/Y3jjraj4jXrfu6N4Q33l/ZF9xnjY/8Z/A8A4AoDHHRSmep4HAwWkBZTAMmEg3mAG23cQeQb7ygcIu4vWgqWJRKcqJcFfMCQ

RCK5xgytdZf3++QUZ7P7M+xz49oDG/+h+BP7G+pZ+Tzr13bm4Jv3LebSSXqv/Lzn3U2dz15uFK3gkjkY+ENJYeJ78f8NyrTRs8HslHx+4XvgbeOF57nrhffnpVWvm/+M78f+tzFp453xtuiT8Gn65+RnRkb/HfEd+Sf6++z75sPkF+wS6/vrJ6oX/diBVu618Ittw6775hgTR/oTdrX1xufYRDPyuu+mFLBzVuPh4WL0Nfsj8ZLxR/Cfiun2xuzp

5KP7RrvGEkfyOuYS+MbsSAOjqNiQ8fHJZdpW7eJb5+kTB/oi0nfx8Bp3+tpI+/qn4Y1LmUhX6aI8F+sZ8HJ41/ym2jXjR/5J+M39dfN34I3k1+5dU1v9kuMX7nrn++u68kv3rv8X6P1VPmKvesIcd+DD/TPy8h2X+bNt+/ScA/vqR/Si8VX6M/ZTmSP5t//xeUf/+uLb8iPo9/KS/7fYx+fGFvz5ff4akVv4p//xHP7+2+aH63UWjOm9+Yv7Me/z

7nngC+py8olqsf5l6yJNU/v+41P/SkvZ9Bf03esu/eh0+I5GDGXgh/Id9NPzC/CL68P7Nfgx4vNXLioL50v9V9j7uov/WuAd50k5q/927/uwT/+W+E/jfdDr+uv46+mP64/lj/GZqcLt4/moAE/6j/ZG0owF8Tq9FhCcT/1P4XkxM/RAi3H3T+C36snIs+LX8S9vaq9P9iP81/y749oF/f0PYOhxeGrgHlASQAZtGwheIA1LyO8dWQGzGBABAB2F

ZRt+iz1X9j4OMd3BJFiMxeOkH8wP3BfuHeiS3Iq799L3focw/oHXi/OEnubf4+Tm+S32m3Lo7st9LePXfLtvG/HX7GH+5vVX4K3rSyfHa070VVnSqaj4tn6KVpvw5a7nrKnzNgnbRIXk2fJwLn74n6l75Cfnm/xd/Lfj2gIGu8fqPf3+84+VqeZt/H3n+nv+TZPk5/iW9efsr4+Cc23qN+ZJ5/HgZeVu5tnobeG37+35j/zGRHXyout99Wf1RGox

+zH3t+ti4gfgrZwX8K3Ytf1u97Nc+/fT+Vv5/Fxb+BLvUzgZ50WFD/zK8vv/B+FP9ov6XUs+WJLYgezv7Xf6GeVCq+/7F+l4jIfmcfRx52Eh7ugggm7YH+in5e/uIVtWzC34l+iL/02t9Xq3+Pf/EfA196YcLeSX5yfzTeT38KBhH/ce6R/7h+8X95KWfFo18h/n7+eG4ff71fSe2QzCH/vv6iqUsEDb80ZI2+76+u/rPGkf9hngje0Eh3HynvmG

cUv4D+x71vHix/xzyYfpBv79d77v8f/H90f4/jroWlH2juyfw8fhs+sslQngb+7n4PJjs+kb89vtXfub5Enz/uSu9VEpVj2kd7Lwc/PuNn3iXfYi/XvpAfi4l+xoEdOO5RburcfTWS/mpwkP5nXnuh3Z7PLp3/uKwYvk+15P4h3qT+5rfovii/4dBdPqp/0S9k620vvf+D/13+wX5LfuLdW6md/33+Vl/Z/j+AXbUT/kP/ExLenmt+gl2t/+j+uF

KUClH+nu60f6XfTf49P6D/Uf9g/rPSu1YN/4ge/O0L/h+/+301/j2+34HL/ov/H76V/q/utL8d+ev/s/522eD+eiDp7uv+s/7R/vv/wn4Q/wf/7P6Nzp2GGICuARDxLJA5rZgB9AGAwZcAPwjDAeoBIkg18YNKUuBW6FTXSwaij58wAxC1skK1/c7Q4cAeKu7clXkaQeBp78f/Zf6tfyHrbLYZq5aDMt/BP8wefXdrDwvzM87CXyUov/1720aLvX

4kEa6Y3bJ4l6013q/pErEhW+vNmv5CbWFDBN/GP+ZMM634yd12/iwXLJeM/tgh7WN2ZPofkOQut6INB6oAJHfky7W0+z5RH9y77wqfmj3MP+pH8ep5nP2zgBc/Z7+o/c4IKB7zX3m1vDH+Cnc8R4bBS93pQAoA6vDdH36k/0j3hAPc6uoaIE16HCkNvncubgB5/89bSCv25/p2PfIuf/duO6iALhFL0fMouSl8hO5SAMa7jIA2PeKj9mH7CAP/7i

oA8w+Y/8B/6y/w0AdIAvgB2gDr/66APK0HOnUzePoct7wY3i7zOBgCgA4Cs6sDYAFn/OcGK4AgGAJ4BvHmIAFTPLf+mSAUEiIDF1KKBfEGu3/BDHxVU138GJVXDQXN8J25YsUSkKffRqYaX8AfYZfyB9ja/NLePA4Mt6kHxf/tlvJ1+lcUVZCHPUMqBagaRCVJgEM58KS8NsNKf1+AMc77QcH2Dfo1vNmuzW8gW7hvyMNtwfMN+Mz9agEhd3GfsM

/NN+eb96gGdbwNPFEAq6u86dWSqLp3ZKpgAFAG5IBUICBGEFIHVgGAA8lskgBGADgAKbgfAA8EJPAFeuX/9IfIXQwhrsf55RCjl8DUgC80yB9NyBQP2XLnPGVMQAXdn+w/GEgpoWHOKeYo1G76JT0lnjl/CsOH8NUp7t32rwoGFHgAuitP/5Y4XMWF10UVU+QDUdCH5GLZsUAr/QpHQ/Xy4n39KqG/bwesXch+5z3zmftPPLr+nSxbn4AD0IEm7P

FUes39jta/PxNHvglMx+Qn8aP7J7UhnqQAt0+TJFTv47bSe/pd3JW++Jca/CECWoAdN4AkuOb8tl7lL0nChffckBQy95n6Un0m/qG2AkBqH9aQEPP0Vbth3F++HJ81x6s01Wnk8/TkBf39SP5bfz2nis/Tp+II8TP5oALIHkU3CX+T09kQEfPy97hW3Utu038TAjZ4wP3u9/R7+jXRyu7/9ygHjh/LEBLF8+26rfyl3vOkHdez7c917cnxBAZP3T

i+/J9uL6U41hfpvnQ8+GAIwgFcTxEnqKfStebYQ9giR7wd/jvfBfuEIkq17ugOA7nNvFN+TDcM16Rr1gDKBPGb+Cb8bEScv39XuevI1uMoCoO4e7B5fhS/fN+zH8A/7ThHzPkqxTj+/v90QEXr3QwHCIWm8Sp9l4RWf20fltvTOet9cqP7igIcfp5XTv+nB0TD5Lfz37B3/QcenB04QFgTwRAcViKx+jYDU3bs71xboGAtsBjj9qwFciTjfsikCM

BrPc+wEdgJ6nj1/Q0BbFR2wGaX04Ord3UEBlj9RwEzgPF9vh/Ts+AF9YAEofDa/g/3AXuq4CA75mgKZbvOA8TywG8Ve7rgJ1vvN/UJ+/PlCV5cr0MvvqAi3+w28dT5xf0HnhyPTUBInd7n4J/yj/mJfRj+Lj84J4T7x1PtWXQSQjZ8A0g4kmbAeGAul8IVhWmCHAKvipafe7UwEDlQH3nwggQS0G/sz19I77slUskJhYN8I8oBagBbABgAJ7DVsM

lQA6sDsAFwADAAYG+AX866pnNmOSA5ocsIcH0gt4LNwi/ptgBlQGGAT/5b8WU3CIJLnUu2AeqIyVSwnskoOFW5Ts7/6EHyh6ldHO1+2NdUgHkHwk9rWHBtWJX8AEqOaFJjqmlM56//8A7CrLivZiVPVQ2SS8FpD4iTrBszXEGOA4djZ5QAKUnrr/AyKU6Z4AGjT3XvlOmJN+3YD9D5MkVW3hY3baeeIDHji4gNTfsc/E8BLAQ7IE9rzPAcd2Nn+z

Q8Of7OxkdAVoXNyBn39h/6V/zLfvW/XfY8P9yIASNwBnnVcUde4xNjyzd10iDEO/Yc+2p44H5fP2igTSPWKB4M8zTy2H2vxC+/Kd+ov5eQbgvzV9mjCLKBy78coEwvx7/iP/U/EhUCPSQEBCkzBwAmn+MYDr97/+AUfhccdE0rR8JAGQEkq9E2/O+SC5cdgHqAKu/h5A2nKzsYGwFLgIzHrqAvD+Tf8uz6pkj3vlm/ex+Qu8y54UfxJ0qofHPcrx

daP6Tn0XoPn/KJ+/jM2t4iXzbLi7/QgBWT9iAGR/yD/mJfRyB8v9O95W/3T/o5AzMB5j9BJhbQJ9/hn/SF+qK9oX4tlzYvg6XRyBGP8iX6E/2Y9DdA6P+z79E15hQQFnjb/U+IjkCD17SPy+5kANcj+pXdjV5i/wtvgN8acBjZ9BkRfr3Z7j+vbwk/f8T3qmALlpBmwGVejkZjdgC/0UBJaXaXuoG8P36CANagfNcPGBwq918Dbt1Qvrj/Ui++l8

mV4g/05Pk6SBleiNduV4NPxWLqWvS7+v4N+57V3xRmkKArU+UUC5Wodzxg3lffYk+E58Pz7cwNuHuyAvlEHGcvoEfgMunsLfLYuHb8ZAyHQL4vu/WY0BuRQR+b4XzY/rWXbxE9UDO6gOAlznOgcY8+gZc2Wh6j0u2GnvI+IqDIHT7vpVQ6KEecUcjA8154q/zvpBfIKnKh9g3abhtDxge7vQeUa19Cr4IbRfFONnG9oSsCwy5H913Por4RUkh+Qf

eiRdweoIisS8gqDJg4HqmxSaGHA5fw849BRCLj2lRCQxTsuFIIE4EcxFcvhwwAI+jkZLr4hwPjgUn1JtoScCslZLrTTgW+hDOBRcCO2jnnxaGkNFcEUMpp04GhwKrgQO0COBHh9/dCe1zsQo3AwuBHkppYHKwI7LhXApuBPcD3YEux0L6HgFLaOA8Du4HD/AVPpcPc42+cC44HfmGbgenXQhuZsCdpRzwK7LsLaVfoue9nxK/RWP5LHA9eBmcCDG

h+jy4vjVKBuBE8CF4EHD1rAd9PdmBb/Uu4HnwK9vpFAl2ep8CC4F3wKOfhCPdN+NJo94GVwJBJqvfeteYLlP4GDwJrauA/RyB6zdS/RV2Fo3rgAud+9s0hr54M19mKAgkcut18BQECZxWDkVXdc+4EsYf40APApDOXR5wxVc0EECXyYAfevB00FhdmfjPcSR3rGfcU+AQcDP49xHOygusVh+Wt8Uypmv243gI8HbWja8vV68P1p/hQyXQuzYwVhz

QsCPDtT/NhBMYDot5DtEwyg3EXF+nAD3f4/l2FAWIfRX6SulaV78IP3VP1XXmBTqBSEFinzv3vzEFTekFcPSY4/wTbnk/K0E6iDE8iaIPQQUo3Bse9zQ9EFudwMbogg/RAaiCdN52LzMQeB3dB+D39oEH2oVMQVBXHmBaN9EAGu/kQrm1EbmojDE5v4QgPqxrb+So+e1dTzQ2QKDuANkXauF1dgkHsVwpPpK3d+B1+MhC64V0z4mk3bb+LtNH4Gi

/QC9G/Oaiun09Jf4vTyKKFMfLhgRPQepSAz3e3h9/YtC2hgOh4pcHucLN3Zi+addxwRYOGSWC1OKpBuoCakHqVy4KG4qbVAKK8W4AmgPVgZn6X4iUZtsvZdzg6QaLaNWBdlMOOZJmlcrm+xQZBu69ukGOWjUnrlfViIkyCukEjIPCmkqLBSeLEFa4iqwN0MNMg4G6KyD0uSnvkaQTCPJIwE9wxJ53tAkntMxVUBEO8SkH9czYCN9ECig924Yx7u/

znXgrA0IokE8bkG+zSPTO8PdABTyCjpiITx8ENT0IFQNa9eQFKt02frVxIrIIpIv2gq30ufhhXWJBH445q74SFMSAtTBqcMADNMSwoNrzgigw7emI93EGHWiOrogUE6ui10g75iH0xQc/6K+g9i84Y6K8WYzvYgqBBnVVpsgDMEtQFgUIHY5yCaL7qgI+qn1fLmIyigZ6jF5jygZfvFk2K+l5mihVycMqSArPGxiDEbRhvBOnLy6GcoXWMg57aIL

x/ojaL4+SOQA0jCiALbnwg9J+7CCKGyxVA3TMzMLxwVP9ZEHKoJjAVOIAMItSBbKrFswkvtqgvruKqCDBanEzQiBAITHWxSkTUGxuDNQdHaGHg8lch/hlB1EQbVA0J4S2UT8j8hwbaq6guRBEd1sFK8xBhEHFCP9eSqDTUG6oPM4hLoD1keCRFqQ1QN9QRULJUgDh8jFTm5B9QTqgswBYd8gbbyLz6AbsGZzepuBbAGFDyEQEkAQqA5yNoT5zxSu

AJ5YLf+DkQf+ANwRNFNcdVYB40RjTCfMx3UNfDLfiyGQXk62xiNimZsFiEf4Dto6ANWZdDEA4sO8ecLgHN3xxvsMPMg+gS9RIH3N2O9hJAwN2kXMMkC//xUhMNqT6OSbMIeA/AKxPjimSqenB8Q36AtxqJCp3ScBi+9hYEc1wNAevfcEBz98YjKDgO2UHLKbyBfjdYJ4BgPMgZPiIt+ObddG5TQOzHk8vCWB608vR6/IIp7qZRdZ+fIDg1TOQI63

g5A1Mkf6Dr6rqPwr/h9PeyBKc9GQFX2yrfm3/F2ugKDsO7N91NbKB/M5cWXk5YFd90cgTrAnI+3b8qL4ZQIK+A1A+xeTUDhphHwKtAZr3Ez48j98MHNwG5UpTAqVB6P8Ha6YYIIwZHPfl+Sa9cMEsFHIwcfkNMMrL8ef6kYLwweNLCjBGxYoYHYNy4wSxgnjBbGCwn4lgP4GLPAwTBdGDeMEwwMXAXDAkKBK9wq66xeVRUu7fcaBA+JSoEBQI1tP

7fF/u7kDCQH9QNVPtX/Igewwpef4ft3mJuDA1USsj8P664fx7Lj8ARleCPwLMG3bwx3tm/aXeTMDlSDXoOTfregziSl4CDL7q3w1AUKPbe+w4CR3Scr28wRZgwyBa98dT40wLswekrS9BKk9Xd7jzwo/vZgucBFoDNMEEf13AXz7bIuYC8DeKz90CHtgAlzQiGxzb4CYNOfkHvH3g7GCz378l04wYVg+gBlRMowGZrwEQWf/LUBr4DL35kINUQbh

3ZjuXe8CzqtKzhfgw/FrBWe9175cgKRnnz3E6BP4Cx9okfyQQd1g06Bef1bt6mH2vgdR3BvevWCYIFTiGO/pN5WbBef1ln4EoNFAWA/Ub+ye864JwYKb7tiHVlihe8B95zfx6XpK3fZ+M2DNsFV71pPk8/BDBeFIlQGdL0uwUq3a7BVBZbsHJVEiuJFA8Q+T2CHkEtgICwYd/NDB0JwGUFogIanJfAv5+02D+Cz7f3MQSNgyxBxb9za5ahGckkYZ

PrBmM8+e6Iv29so/XFF+UO9p+4+8DgyoD/PMm0P9tzRXv3IQZEfCn+jP8GMECbyYwZS/R2uvoDH74tQK0Co3XV0BNL8B2zdQPF/iUfRdehR9RMHHz1LAbezOC+jGClH6DQLkwVl7JHu57816484IdgYj3O9+iGxp4EnzzLASLg+jeDy59+7gX1UfrSnfd+iGwcYE2r0PXm13fJmVOC7l5yALVwU23YMBW/dSz66ryjBNevFhBzOCW1764I7rmavb

0Bt+9n94Pr2Zkk+vdVeYjdb17UYMABOnPAFeaq8Z35EYI17ru/RLILuDisFu4OtpDu/PnuV/9H16Arxnfv9gn0eypc2e5YFCRgea8Z7BUes7b7YbCjwSdnbGob2DCUE4VAhXojApPB92D4MF7YOSwYivLlmpxVFl57P0gwSuuBFemMC35yCPGG/hZcX3eZeD+Rx0gOOwXzcYvBcRpSYEgb3JgSxiXp+D2Cc8EzQOV7jL3B7aKeD1sEcry8wbTAt3

+8oCws6LYOUxpzA+L+G8Y3v4XIKZQYXGd8BfcC6YFrjy9wbJfTWB8Vc0kQe4IV7hrAuMua+CclIabydwXmXGxK1sCgkS0ILjPgHvS2Bnm56h5BIn/XlOvCjyjsC/RyNHAy4L1IbekGuDfL4+wNI3p2aF/BT8D54EbwIA/q13LVegv8KQgBnxo3kqHWQBquD/8FI3CwQWufNLi0nRlcGrl2cXsQg0Sqv+CDR5Gr1i9GuXBAhobcpT5cvxjAbOfLy+

yZ8F1jX4Ik3tm3RfGc58c2A0ILRfnQgihBJBDDy717ElQUZvNOuOBCkz5bjzxOBvgvC+Ol0qCE6nBxfGDgyghuBCmCGUEgk/rmvPcuPBDqEFSHzDAaPgxyBDBDDP7CENcQTt/fvB+foiEGsbxd1oXghZ+jeCpagRnxcXogQnN++6CQQRqEPQIUcmB28OhCFCFvdkrwYj9ShB3l8OCGq3wgweIQrM+jCDJ+DMILnvmTzG4WofgOlaTL2iQQ3gxyB+

49JEGzEyMMt+gjvBXNxnEEGIOlakAgrm4YSDzq79A1p4hdMbJBP08/UKEFwiQeEQnUBByDIcFNgjyQQXnRsq/20WCECn2U6hVFcpBr0hJHp74LoIcp1YSu8ZNwCjGoNKPkuvFMqtSDUOqoKV6tMTgntu9qCWQ7z+laQQ0g8je0uDysELMV6QUKEJK4Jld455a4PAIaMgtOKek8kIgPngg/oZ3ArBLk1fK7UYD15vMg0AhIMCUCEzIJyvpMQwKuzR

CEN6tENxmnJPRxYoJc1kEMzEwIdGAx36axDAJ6EryPTKKfK3B/mA1LRJV04biU6UoWVGD8iGlV3aKsauIUEWxoOsF2gKFQc/6H5Bw9R3/R4nADwZpiTiBYKDsMA7AU+IZ1XOq+QjBfajLfy78P8QkV+6x8I76bH12DHVgYDAPAAqlDHMFOoCcGKAA5KhkITHMHPcBPALKev1cEeS9IFjYCJ0LVOlOVNFCPyValL9wdDa98ATujK2TGgHcIUAYEgx

1K5xYDmmJ02SBeeUc4gHeLyxvokA7Mc1wDwfZieytfBQfWsOf8VYT6BXk70IbLXmqSnsAAFzgFrZNrPVDO9N90M7kGGLogCAiW2bN8eD7T7wvILXNRLB8/c6QEZzy4rkd5aAsm4DTkpBEP3nk6AwCu0h84x4DQX1IT5AkSel0COW6z4ObnoegibBFiCFYJiLwnAevfWseTxDaAE/wLvAVMGcghp+C9kxnoK9AVuXFohxMCm9Q+kICwUHgtqUBtcf

zAFVQ2LjegkEhNHlZoHJF1kfqZAhtuHmC3wEBwMYvvY3dzB0ZCwIF/5xLLvaA/bBXYDEyEZkPWvulfL0+nYDXH6c70cLhs3MBBgNcBu6fYJAgcZcUu+NVdxz43YJrIbBAtI+aBdVR53MWrISPgu7BkJRJq64F0Bjkh6ebBL2CJC6eIJVIA6ERI+w1pRCHdkKCnIEg2IhtQR+l5XwNomhePODSBzcuUEjQiLAYH7eJBK5D4YzrkIqPjEQsIhc5DAN

SREOjIfkfJCu3iC+iDzkOBwbRNXshwnF+yEXkNlAWYxekaiHV2q7fv1wAVNggquzZ9/W6tn3SxEDg+8h8UQDCFWF1XIXmqI8hm0Ng4GOXycIf8bQ8hcYCpf5rcxGvkWQ8vBd5D4wERl0dPkLNANofv9dK6pgI8CFufVDexn8UwHZgLc5gLA/U+i5w7SFZZQnwQH3CUCzICXv6sgI58kAPLC0Xh8QMEwYMAHtgPYAesHsBqRIYNaGFYzGihZv9y15

CYK6iNJgi8BfZcuKGLv11wUmvd8+ep9Pz584NFwU9A0S+fcCVcEzEJEVke9FS+g19lV4BP30CBDFamAU4hS4FLj0I3CjA2/OalDQKFHX3GgujAv3QgQRw4BYC1gQYGfGOO9oZH+7OaB0slAhCv0aBDDCFAbw06P95Sw01n8y76uYjbPgv0S0utg9HK4V+1G3FWfT8h4mQnKF6NBcoX5Qw68vqRYi5CsA15qWNbyhTxhfKFOTmvIQZwW8hzlRYqGh

UKcnJIXU8hY5CGdqpUKo0q5Q8I4M5D9yEWfzZXDlQ+Kho1klyH7NwcHIBQvOexlDbKGfnGq3NwXIiuSWMMATEP0w/soSTA+DBcQgjQ72UoTL/HDqkx96C4a81YrlR2HVekH8Kz62FCmPgNQro2TPsF6g8vxaquNQliuk1Cm5TVYJDAYsffqh81C8EhmOUHXi9aBJMnvEKEopXxqcK3/Bv+FgQdqHJX1RQKlfZP+fUC0P6uPjk+hmURBmoxBQ/4JE

OzHpzOPa+p9JFeh3UNmXiNA3ccFRDcLj0kLXXhpSHchPUN5/R0kMBeqY3IChUFDjp65RFpIbzEFvQ8ZF/qFedkBoVDQpzM1KYuCEWmzzYgjQ36hUT04/6Fbi+oUDQ6GhQR8U/6XUMSnA+PCj4t1Drx4CXw6gexQq6hz1Cnx5vUKZwQWvbahwldiaGvUNJobe/aXBF791XgVRROocW3KahGAJ8sEwP3ZoUlfOKhXNC+pIqlxwfiskNqhc1DGC7rUO

CoT5Qk7ORuZ2qETUKloSLAsShU+D2j6UVwyQcKwBc+cl94q4u0nqoYRXc5cKhpeP4vn10vudscqhwhdM+JGX0IwB2UDOURFQQiEAgEKoU+6f+Bk8Czq520OILgeQkYOq585y4TQFGsolQ3SWrcxUCHwEMMIR2bF9KfZDqRaTejM/uXfANogV8Bq5RUJCviaCekaX0QnVDqlBQqKgXL5g6BcOyHabz1KDYg6KO/OYPyH6IKCodEQ8JB+5CbOZmv3c

obmfFEO3CQFaFsV3soQHQgChQ3IHx7WslLJMOGG1WKCCLyhFUNZYrpPFt2EyC2DwyfycvhBQ7ZBkVddkESZ1FTBpQjQoWlCbiG5V2lSJVXM4GilDqBbWxEQngYqO3M1K8DoHPQMDgbAGEau9mAxq4A0wfAbAPe5M69Ceq4CBDt3gJQsv+BgYIxCX+AWrudYWeeO4DtMEn0Iv6InwRLwF9DKwFUDyGgTfQ+auKscH6H+PzD3g7EG9+R0w5q5n0Lfo

WR1VQBGo8sFYZgJBQd7afeh41dRf5x7zobjEKWAM89DLwQ/fBFAuqPaneMDCUrSZqF3rqcg+nBVO9494oMOWQQPQoCezn4QyGf0MhBgVVbK+flcFiE2cyoflWAscB2zF+iGd0LQ3DJgqhhz9DtwQGVz6QZ0QgGmZmC1eY6dVkrihuAZgvARRKFcwPyvma0YSuDdDY3BN0MVgSvQ1MhZForop8V2FEIURR3whsDsyEX+h2oTIwv+g3hCS4Gj0Kl4L

IQ+Wha1Cq6GxXzmvv5fAAh2jDJaG6MIeCEAQzZuVZDckGrUOMYVKRQqu2CD1z5YYHLocxXaxhd2RXRSMEPOylBAsahVjDOqE2MPrIX2fTyhGORlGHdmH4rnIw032j5C2q4YJAgSM0xVNOQTDZGFGGQ8IZFQo8ehqcAaFwaDkrrww1zmlTRg6E3kNDoUvcFhhHRDjK6LXQyoV4grKhfRDPx5mT3SYYUw0chxf5/OqkMImIQQAxYh05C9yGu0Lbof+

PHZB+DC9Dim0ISQayUcehkpA8q6JykkKB0wrchAJDiPAb0OLlItdAZhlVDysS/0MvIP/Qpau4zCduhVUIr8NigrEA5e9Tq6F+03IRMwvB4rUoIeI2nSIqHMw82hyf0A+Dh13wwNqQZ2hQSDLU5vWnjTKyg3+gmjJTmGzkOaYdyg1E6SpUK55EKhPIUUwqphhLweUFPMJrUkHQnAuWTC/aGvPAmMPY+YRYtE0FEEqF26QNW7UXmS19Doqn+GpIUoX

aOhiTDIQpQsKFiFSQ2yglZ8nkh50JAqIs8CkhMZoUuAaf1cYZIQmJQP44kWGUkJtPhp/f8hVDoFmHkkLfSCSw3Fh4G55CG10Mn/mwPY3Oz0BPoB95mmAGKYB/gr7Bbc6RqBVAFb3LYAygAkgA11TFKoF/dlgEZRnEqz4BL0tUcfhu8800brE5HTDvh/GyhzaZk+5A+BePgaYFT+1BNGSFnR2ZIUCfHxeIJ9BIH+LxtxGlPcdBuW8CcqKzwASvabf

5w5Nd5DYAqDulF+0X/+Y980M6uDxb5k89bQ2M99Nh4tfwTrA/A//gVo1UMHtvyywQ0A5RBxxCiCFIAJqAcmg6S+BL8XKzNAMUysw3Fn+hfNAZjL3yWIQLg59iO6D177AwMA/oaPCpejpCml680NvZqFgy3+TS8dKET/3t/tyPX0hRgDr843/zRgcWw4UepbDIGFqAMZwUtg0shPYCCG5gEKTnv6A9Mh4fZmf5icjjYUyfKMh4fYY0HpPxkvjB3PM

heh9oyGMANyftKgoW+w7C3H6A710wRBwNMhZkDoyGYgISIWnXBMhI7CdgJ3f1hLuO/edh+ZDaJr4oO1PvXvRthSZCrd4hPwWnpGQ9thSCQkUHbsLXYSFhHbBotpHsFnYKOijuwpBIP5D4wGdkI6XkOQle8XBCEKHQUIQbCiPYHeRGc/sH8EIQSHQnZ0hD5cMcFoUI5biL/N0etBCwz4yq0xoc7cK4hsHCDqG9/znODBw5gB3FCfQFugIBTmOwqmB

Z1ICCGg9wQ4XkQpDhQlD4L4iUOieI8QsDhzxDZsq/QMBGjXvf9h45pZKHpsPtXpMgmuwB49yg5m3wZwdDAz9hVmDVzbGANRgdOlSbBdYD1fIC90VYR6fGKiseCx8G+ZGsoYCoMTh9yCuyGkQkZYefPdkqwDRb0CP8AngHAAef89YAJ4DaaBscE5YeoAdJlT06BvAWqmMRb/4AY5gEDIwHfUuPaIZ+VitPOSfGX2cNzGd72grofaGR526gn2ghu+A

Gcm77EHxbvnl/Q1hdwDUSIZT3LSmawmXK8oQAsq13mVvIVhMN2qfcROiS/WLcgkvUAB0btKGYRcNVVP2HYyEg4cPWGRv3rwVOgMk+e6DBp4+YOadO3g7PBUjxKO6yP1WwVKUWUe0WCaQyJ73OwZgPGJuBXC+US230gocaPRCh5I9kkEigJRLuvdVUEc4APnBycJLXqBXZw+QyDNkHqeBd+NIfC7+3z9tGwnr2IwYa3Onenz82YFjcNzZLaAsDhSP

9QI4UoJjriGffBB7tYikEbf3RoYjOV9etODSYgXyxhXltwkGhjWDMOGWxAO4Z59KMeC3cQZ6lEO7XgpHOP+y+DqOHCUKzXmCQ3P4S1CBX6IjQvvso3CSh/pCNPqgcO+kBAdN8U/OCysEhsFQ4Y7g64hW5MSi7YuHlVuqSa5oiHD0OEQ8Kz8FDwn0cJANHnh44MU3vbOMUeeYCzGyPLyOIU/vTBSylCMsFbWhpXqwg9J+qA9ewGMMLhgcTwtJ+fXc

yeHNni0wZ7fKnhJP9+u4pUKFXi3g+1IjPCxEG08OooYPgyLBHPDvV5c8I1agRQhL+fPDeH4C8MsCIn/FHhmEcQ0Hq9SQ3l53f8B8S4Wogi8NJ4V7TNMu8EDFIRK8Jp4U+fNj4E0QhooRQ1fviTwzXhr+DgS4vii4dDrAlRBLdcxDSO0JfgTZ9NDhBCD/MbUb3MYb4wUHhgl87eEUMnJYSQg8jh95d/uGRtwq9PmsDeuzLMu4gCoN7QD7w/WoKdCn

yEwylN4Yi/WdhX3CEK6iCDeYT4gur2D0CuT5fmnWYfMwx6MEOCruH13CWPoCoYnqmhEl2HhjwR7mOCDmhgtCmfz7IIL4Zj3Xi0dSCqiFbXDL4XLfTPh29xcmFGVwynGKAo7hjv0amHqT3Oki78MPB5NptuHxczQYQhKMrm4v5XiJAcJYPNlXNgIZV80JB0JG74XrzY7hFfhqJ4LjRxTDtPWd+938TG6wBiWYVCgK7EQ7sVuFRE2WKNSgo5h7Pddr

gbsPwAb3w0XmIqDW7AjxyZ5sisbfhJ/CQ+anXwevr8fbcs1p8V+GrcK9mvqgzik/T0mewqrGv4bPwwkhQ2cTGAASHAiiwEI/hkt8d+Gr2l9eCSKcnAaPFH+Hf8OkOO0PEmozNNFjDAawtIam3G/hy800AhxCm1IKQJDG4FiD6+GCHQlIILpSxKhNtuOG6gNwEbA9dRQgDYnhgRg3WQfdwxHBjwRtorFkB2BoftQ+BFFDru4h8OFZMdgcg4w0oaWp

UNgo4d7wsmO4NxCzSUkIEKAM2G3hYPDiOHaSxDqLCIFygaowSV5NYIt4YPEd5mF1MLQh3k3f6KnzKGKXbCkwFRSlmwLOUKQQyYkiNSJgJfIS2sKhOMlJl46id3lXj0QrrS8ScC1CBOCaptNBUUe/GDJcEqCm75ogzXLo6n0a5Q6ANRgV3/FQU1SBUbBL1H6lriiShhT9DecHvwhl8L62au0azMORx2wOV/l4Ik1k9jA2WiHyD6lirJcYAQuCYhFt

TiK4MA3al2Hfhx6QpCM4OiRMIHesZgc0RBxECERpfYIRp5wLEi+FAYCH1UD/0tsDYYHC4NPOHJAP+g1PQxSZKjkLYXoA/+EY6tNL6fEwU+sMQkB+HOC9lRWp3gxAlpYf4sT8rArBzCY4rItY0IGn0uf4J100ESRJTxgmloQojIZ1UETGwjQRhgixTiRCD3SJMXYZQsgjzeH48NelOcdC8ogJ4pgSZNVt4TogoUmfa5F9ZZdAU+n9w8bupbIIMg1O

FuVtyTRz6n3C2BFCkzuoJooHvoXmQkEhB8ILrtKTMKOWawXGDEkUGQfTAh7haVZoYgu8Nh4F3EF7hcMpjHoy2hdlB1nWvhGPdSBFpVnlcM5QI3YO+dAmKWYJIEZNbMpIlACznCbcR1jvnwuvhOIi+EiBHhXUhAdcO4OAiSRESCiXUHOJADoXcQqREqyn1MGy/HaKwA8XfiMiPKFLRkCNgY5Q/HgMiIz4TiIizYzMcsuJtzAentCIpe8cXE/UiCxC

loKw2FgRSjdXhGabn/1pKQNzoIHDo170PwB4bgqTpS+HRtOhxxGd4fggs4RYNJ+wgRLQv8BlEcmMnpDfWwfr3VTg1zThgn0h71hqdzUEZ+/HqIMFMlMr72wI5r0gc1epWCRH5rCLcJKvkSHuHy4b9QmwLkobI/F2gEXFyIDhsEVmu8gnoR0D9b2ao5F+IqqyIPyFbgqu6yYLqEe/8BoWP69jKI9MMk5NuArX+xoRaRQtZEYgCxAFJQnvwk2gcMJE

gC6veLAsVhCDBfCn/GNwlE3+2pcDE400gIwPCQBXweBhYWS6nwEYbIQ6uI8aYwQoM525lusqUihsA8OxGTzkvZpJIRyu0Cpt6H6n0HESagRkoqMdnoZOx3nwavQoSoObQBlAaoGJlFBSJ1O84jJGGgGm38O9KH6QstZFNYbiMovkJULkY6g8xAhCpDnESmQw8R/AImIAGxEQ7MFUc8REjDLxGTIiXBC/0H5wlDFe4ELiP4BLI8cMY5fVVZzmx3T/

p+AyZEZxQr6F41H3EReI8S+FlRTuaHiyHfiGOe8R0lCPxESAnR4J3EbISF+ABlTviM3EVjtK8Y1KBYfwlgjuHP+IpViIGx0HCK9Gs5LiiJXeR9D6xEF0mUCAq+ah66UpSJScUMc7hRI2iwhTJQ5SZTXNjiWIyj+Fpc8FRfeUsmsBZTMRKmCAL66lxPIBVaF/MbIoflg5CMUBBUZZ+acIJ96YutFaEZWwzL6qTQZd4O73w3Pp3BwRt7N+kBv+DwML

O4cvBsz802F/4MsERsidNgDLomci4kHdEUDwz0R6gJHgiiGnutGyHDXhMvCwGLpTR+cGRraO8OqQT8HmiK8PvIwYn8GfhHMDo9R2EccQi0RVC5y4gcJG7DLWUZdaL7teBG3CK36DDwMgqe/gAq48CK94RFInq4vQRASgRxgE0FbaMKR8UiH25Ib0Kpl0FCEq8kdmBEvCKhzrnbFZIs5Rc0RNnAKkdCuWYoOW5ScDg/W+EbKIrPG8oj5EISClK6vw

EYb4gfC6pHB8I/si1meVYVaRXlhtSPKkSIUHwMUnxPpCWrGfMMCIpfBfPcbHQZ3TUEsTKXa4YoicTSzYHQpp8kMGIbKw5pFR8nPiIhELXiIfkypH40Jj4boaFXiAR5ITx7Nk94ejghqRtpwiPBfGFYYgHgdmMRHD4eHnNFQiG+TO2hkEhUeFyCL2Eec0NbIcyplXAsPEOGtMI8yRv9I0E42IMRSkM8EYRoDIw3i8jHIoBywKkEyQiohH9gPwZFrF

cFh0vBkGi8SPp4TmIvTkOBhm5A1ajPZLRIpihtFDZCFUUEeKIJxB2o2sC0JGPiIxRLMURKI56DrVYvDi1oRafFmSTzEiZSmGw6IOHA8y+J58KbqMMj2FFxuAN4PZQvWTXnz4/saBXz0IgRCkjBWhr5j70Q2hyZdEFScMn1MMxcUUkMX9uZHPnzFkV6I9dc1iUZKT4dBUamMoUWRt59xZG8MxEpjpESDiMIUm2jqyILLgrImuSncpqmgB9ADJsv4B

Rhll8YQRqk0nShAxMvanndV8E0yJhBG2zBLgx60K3AojnHETXfGEErN1AJ66GHRkVjIsiRgOcZGSccxaWquhc6K/8oDMHqnxOwKoyWR4/wgnYqIj3cEXxwlB+KrZE7bveGqbvkggMRTHD2u4UQybsI7kKdwu8RTJE/31mEaD+GXw+jx4sAxvU3gdLwrf8eNxgRCL0Hw8O9ra6RpwiJ2FS1BPKL8g1MwKQovgg/CN2kQ1jWuSogh07TKLkREV+XZE

RXDEw1wsxAGUNQPNlY0/DR+G9M1PIMiLA9gvHdgBF6mVQEd0HCooc2wG1CbgUXkavwsP8udwY3BfYRiyDBcGARWZpYqhamVeTi5iA+Ro78QBHLyKjmjpKeDQsBsX5JX8IvkUvI2fhhUR6KgoPT7JDm5B+ReADL5HPyKLrq4QEJ6sNksQRTyPUXARKJiAqsceUz5ymIEQkQ4eRwrQwAjEJB8KEBuWNsv7CdpGnSPtQltHEko4zQkUjAaxuEZlImO4

fEA4pCWc1hnMsIgQBsbDi5Eys37CPxXTxwIPDbR72iMNvo6Iq800s5IYAcBC1QHLKAwRXpw2eZpYls6GMdFSRcuCeoH61FqQVP8Ww8gYh1QSySNSESWaGKwezczaEwAj52GNA/iRXpxz5AFz0SuFK3CORsZDVRLRyONRMHMO2mc/Qo5wByNL/uRI21Et3sP4hCpA8cHQnNsRk+Dn4AVgivoIzgG8GY5MlFR4SLYtO10H8q9psXO6wSO2gSTI6C0q

FNSsifKm1DgCOA8R4Ej3UT8giz8Df6FG45KdiZF+KKSIYzERGAWhQ65SgSIfEWEoscEBAN4uhCzXQeCiOOxR5TE6ZbLHy6IW+0T2Rp5RE0QEYF7pPVCccQYiobMG6KKDkX2zaCQt9AQhbqW2gVGxItRRvvoJSAFWnEvhDwSv4YkjM0T2My6VlHAPQMicjy2EmANEUanUDNQfTA2si/0DoTpGI+XBx3J0eDe8BJTvogwuRrNDSFGp1DUOL3XORuNn

NFPorCNSCLMoui0P3EpBy8mVPpHq0fthhvCiiiZbmPZGhud9Cz0jdhH+SLUrnxAaloEBdbcqiCIhEc3IgJhmxRWdZbZGuxMdItURKCiAmExWEsUB0o5wu20iLqHdyMgJvGzazY30hp2JjSP6wRPcXnQ/KdzPAUMSxBKtIvyalypaZSmU3wrESIpERk1s9nAP23PgOjYOFsg8j5u4oqI1TlMXJEUelEkVFDyJRUS7zBg4Aeg3/RD8MJUdio/VSqIi

54zfUGZwNMxDkRS9wXxZ7oCcjH4IXFElKjHSTQKNFDhYua+Q1uoSxggqIRwRPcQKWvXgtqHdVwFUXK3UER6/o0kAjTmc5nEUXa4Xci3lHr+kFEfy3Ra0ErhG5FiCNukStNC6IEc07AhZ418kXjws5Rfk1z5CfEWFBs3RPVonbDVlFGyM2EHesaAUYCCqBFLwJbYdnI3IY3vlgbSSOSoUW3XVSR2fIezDuEF/EBbzSIRtQjelFrFlPgMzJOHQNj1Q

pErgOzEcnzFEQpip4ugGs0HZKRIkpRshCSrp4p0UOAHzLTkpiiA+5JqN3gLplWjwXARzYJKKmyUeYogwMX0g8CycszpfOuIsCRAEj37jYLjCDvTSOHQKSjfFFVqO8DPOzYxRqio7hIuKNugU2o4a0CQoqeQNxAEeM61QtRWaiw8DCxHxTimIOzu2MjPuJDqJ9klfABpMSwwdFF1iNKUc/6LzmlPQgs5otGUUXFg5IutSj37gdUVG6JmwZOoRI4+J

GWd2z5HwUZ84cRgI1Y3J2KEfbAwNRRbRFjAt+HXuo3EPSiIZCZf5ySPfuKRYABg/o5iTTCKI8EcnI0IMJqUyVGABD/4NwouthUH9PmiAixwthmhL1C9gieFH1sNl5u3RVwSOKIURBAaJGoY4I3R4xOc+FQJsD1lEhokYhKGiTeatLUFBMQ+feRUGjgNGjEJ15ngEFuwN8V1RhYaN6EZe+T3YIXMX27na0TERTw5MRmLwrMjJvDRuGBIboRLSis+Y

w327KK2iT2Q49IZFFHqOWKE1cfmU9dglOKsSMjkRR/LdRujw2spTMmGlGu0Z1qtYicB6LqIxtOgIHf0iiAFFR3DkHUTMWaumFd1ukRyiA7UcH/LtRiNpQQRcj3A5MAqcmIWFCnZEqPBvXEV0Pe4xwjMyEPn1ZkSo8JjmQ6A5aaOp1FCPmXazkVqj6tAoJGD4WkIKPgud51GEpwMIIJe+FCiFksBmCXyG1gepQ4y+DZUfNGqs1DEWbxYCQ9HJCyHx

Xw8YW10QNEz+hx7T7vHeQbNfIq+FoIfxy520tkCKIJxA7HkB2j6UNk/qYEZYo/ogHqijyWICrGcceB3hpe6HjkJlQeooXKqfIkI1Y+9Aq0c1o0YM58pPihPJG99F1ojroTWjwKEtaOjtD0qWw89qIZ8A1r260aNo0YMoGgGLBBdmsIOk9Zfws2ibr6jBldnDI3aVUGJcOYhraLk/rmcE4UkUg76BlcNBQmMoVLR1V90tEw8UhFBAIaaoDRwQ2QXy

GTgSZfSiAIc06kiKQF3IBvFGtewWintFWqPTIJmoaJQLThh3RqyJ5kUbQ/j+UcRUIhUlFPKDfFJmRM9CYr7JqiREN7aHzA1hA0Y6OaIsvo+fBSUHnVcwQe0GriJZo6mRJPx6WgamCdQdiEKpI0CorNF46OqeCf9fq+/Mxw4A46MdkWTojzEDcshiSWPGusObHUnRvGFczgA5XetjEoAz8/sDYlHGaOjtC/QVBoA4BKXoExgrUbzojMBPRAeKp5Yk

+DG8qfsRE4jRgykWEhYLeMJuCRYiM1EDiPl0c2TLZMWT951HKaKTUXDwC+Q9SAOx7ZiGflJJozdRLq8btH9UW20FhsJImXQ4sxHN/2T5kzIX1IxqB2MK0rUY0UEI5jRRGl3qDgzFgbjp4AUcAajODq0tGKzqLYV02dcNgOgiKP90V6wCxmrG5TsBdKJUoW0I8u0FydBdEfRRKxkRAb9RRbDTCa0OiiOIXpIZ4ObC7PICxDQ4lKQCCURGoc9HaSgS

eCgyXI21TQY9HPqOvUbC0LqgHvBouBvpBq4aHo1PRceiARZOMWmYWu7HboSMiUsERWDs8r1BQYwcmsLPDVKJN0aoos3REtBSgiT6xz4nqMDGI2mjMRbvCQEUVfFVCRrOisgaCHTAYBlwBgIKnspSL+d2ZkUbAoSkGYF12R/gnt6EnHWBBarC+CqZe3IWtbOCtyzshDhq2MKgIfzKP7BXJMW5BOijxlo2yJTKNn9Q5j3MKqGOmEbqc7SQ7GAi6MEQ

eHw7uWPLIi673eC3LHCIaSUYfDwmGAGNzujm0SKWk6iI/4gPVBYYePcFhSTCUXx9jx8YPUPJxgoUj4mFgsOioWXEKwStcxlEBCURNiM5wrLg/jCiJzQ5zZUC7QAa8+4oSDE75z5CLdTbNgEcBskChVHBaLQYor2GbxqYAJsE6XJ0PFW+GTDfmFJULoMRwY6pAyShmFykxETaHwYr2QfzCyDFhExl8DzQVy6CDNxDGIGOCvhCwoicdIo78qliM6oN

JKJQxMdCVDH0LRarj8LaRwIjAkR7/6MgMV8YHlky1dvGBKcyoCJ2yXQullBXy5eCD5CNVuFuAeQgJkocSl8YeZ/P7BdvEIpToCksoJByfFhVCCPoaOGOtpl7IJjyMz5K2T0sKodAAQp5gCTxjWJu4FIRjfoz2hDjCM3jiKIuSnp4YLI1+jICGJGI/0QlaeRRlshptHv6yP0cp/U/R2Rj6yQv+howLokBCBNa9VWEQF3ePjwKL6Qlrs3+ZjyKG0T3

QubRPAp3hQ9IAAEH/RM4YeWiNr7qJCLFkbXcYwabZcDD3aJHoSFo57RpPxsEg6JCa2B90JdoD2jNKF3qiIdN7gK2iU4whwg1rwNkd5oxYxb28/FxLYEn6BbI7fR0XcaHS9BBmYIhGEOGVMjadFs6NYdN7Xe/wPK12zY+KMrURmA72QFshAAI5lyN0dPo2XRXsjSfgGywvhtJzTNgFrIZ9GfGImUIrUexaprhw2hKaOYoSpootoHjAiUoiiLcJtXJ

cYAgmie9EtxDViPDEOG6QLDXdElCPd0aPdNAgHeUvhILsG6EWHovu6XNNCogjmCmiHLKYvRpPxzRTeUhdWNRgA1eFginVH+SnjZqRAHVAcHReDj/HmNfmso7iWQY5C9hkJFHGEQqZZRxCjVhF2S1yCBX0CDgw6tTKJwX3UEZaouyWG0RseRvx1diIvifkxj94SFFWqJmUCvmIfQhZdwuAOrxoUcqYuyWknMsWIMQnUEL2cC1RRMoVTGH2mxADmbB

eWzXc6TGyPw/2L8UI4oQaxK15FCPJMdpLTVAXURCkp5CHKbk+okx+L6jTJboCOOtA7IFi6vuikxHV6IoDAQYAViGGBMshLYHXUV/3U3Rah1ApaS0A48IAvPsRQvCclFFS0t4pDkDFRqEjUlFFS2uFM3oEyiPtELWRL6Mu0Xq2X4O/pQhuYT8Fy0ZbItHRTj0r/pqlz0SFpyGLRj2i4tF2SxPlsrBEduZcdGzHzGNC0T1LByg5wp4NhC6QlTqJ/Ar

RPUtMhDCiCF0hbsCFIPRi4KH/cB6lrI8CbA6DwpPiDmP0YWJ/HqWqDxT9LYuFlKpbfc7R/l9izGzQgHuE5QGe4GXIlzH5aL6MUasf0Q3qBXgR6bC3MbBQtLRjDw4jB2cMvMb84a8xQ5jTzEeR1gBhmgywBWx9TcCSAB4AJgAaNQjJk1cjc5GiAL6IbNQh8dM6GiJyKZG8wbKqrGc/pDnZSjhmeiH9YNzFXmiSMUamC84f+AwZoTkqCY1P/DQrQE+

mN8jSqP/wjopyQ24B4nsO77Q+ydzlOgrrwWwgd/TBK2wII3Ie24mhiV0E/N3EUjErKqe2kgSQA3gBJMhUARAAgoBMwAf/wpEOUwBUASQBsAAUKHKIIsAXAAuAB5QBrAC3AByoLR0wDRMQAgND+AIAQSSx14BIFYCQGIgcwAdwABIBY/Cd+Dr6OGQbAAZIBLmAEkHEvH4AKeAmegw4qs4igALK/c1yl6AUICVABaAKhASLSwrDSIEk4AS5rS0CPw9

GBcMDkQFL1panBpWoGx/kZRyWUYlI0VNKQPg3gpqSWSUD9uMZaHi8AT4EHxoVqyQgSBVwCUp4yzyNYaRY2sOP+UguFdeCy4Ts8UVUlN86tCIyQyCLV/bu28XD6a7qbAhGoeQae+WkCwY5z3wMHJ25bdimIlpgoN2QgDh2JVjyGIkf1j1WMiso1Y+3SLEVHtIumQZsq23ejkA4VBrJH+ULEhMYLreBXkgoroHG2sv35czGotlcIoWqUPsna9D0xMI

gDmIauSM8vwSFVau7xcFwPRWs2Gsxd8Km1kL7K4CV+xl4wPSOcEUvgpGeVi6L7cb8KO3l5vLLpWJAeRw68KYjlNn6peSCXJk1XcKj1ly7RJeUA0s9YhiKBpg0NJYWiVTMBFD+qlfxyfJSOVynJd5eAKjIl7VHjAB4inTZMGx+1l0QBEjil8gb5YNhXYt4vLOC0hsfJFLnyNvg6HIYBT2ZOxybSKd9l1PJGpjJ0k7jRYc0kliHLK2WxsVhFXGxvsc

3IpjCUcikqyYmxUjEQorvBQvKFqQyMSBAV/vCTmNCsfs5NmxioFlAq5iRB4j70bmxaDlebGsSVlUpExGtewtiPgqi2Ko1NIJMTk/ZJzyCzPwsiu5FKyKQPc2IDrxTurDgmZWxdNiP7JJOXYiqFabWkp7QiHLHOS1sqBjczSSHlk9GCSTGcnLOHnyB/k0pFW2NvsggxYThBxkvOL1yjxsVM5HSKhNiSYFNuDw0m+kGy4A6jPjKeClFzhUrOVqmSAg

7EUtVbEWyJcOx/xIYwEO2JeckQLOzulwUBlBY2NP6MbY4yK4ygilEC+TusCnY8+kvkUPgrkdwxse05HOxSENhQpIyWMiBHIkPSXHlsugymiJksfHGlSRXcJPJV2LntqYFTB4zklL5QojnF8oeZZuxs+4vJJeswhSvbIpRUndiEZGSoVrkvjMSVeDy4uFRD2Pf9DpdMTqEjFa4YV2ME8k3YyVCAViUYBBWLdgY3Y4US1dj7vRKMVXsUjqBexdTlN7

FjkiQgVCQzxkSehNsSHMAjUNnoYgASQAqRqckGwACd4AqAGd8JB6p92mFNso+DE8Wlc1pn+DCVGQuehISz5y2IVClGIMIuJk4Hx8XsZBSOhNOIpey8oMNTgH/p3FnoOgrzhw6DW76joPxvoV/XLeNpVngE933GaBpYYJWw1EKTyUdFGgNMyB1hUpDXB7SCN42lerI2elVjxgolWXBUv4gwo2ghlj/ILYLasSQZCGi36kMzSjuQPsjv5YaxkrUlwq

f+V9gpNYzMS01jvDIuGV8Mp6ZdKqf4IDrFlp2WRrICPhy/rF3rH3hUiUi6eJfysgkV/KGTho0g+nGey6slwbJNGW7/lP5csSGLlsbIzGXGMtUWVDS6gk4ly72QOUntJGWxmTk9PKQNmvsvf5aLiztiLlI1mTQVBiZSuWhztsTKV0nxsW6+V80wTBa7H/BVQZNg5FWxddhgpJghV/8i5fbkKIoV8DBv/WACgPJVEyN8k7qYCyTmlJWfGMGejE4YjJ

yQsYLvY1OKo1lkApCBXa4th/eKI5cl1VZBs1k9EwFNeSJGAN3xNySkCnXInj0+8lzsrjiCzZET+QQKbXE3jZHUIvkniIu5srZpiApAOIPSEdQipi/jBwHFX0Q6cYA4k/i2XD1Xi9OJdkOnNAZx4JDw74pD2QgbsGMMAtQAFLyayCgVg8eT6AUABHJAFQFt4LqgYvQW/9Kghv+GyAcCHOJkgxBHAiMDXU6uXvWL+gdiZKjq006zOZsGpxOpRs8oB1

jc4WcAjzhcDi4F4kHxuAUlYvzh/bEMp7I23SsfD7aTgGGQ4M6vN2RPoIwUJ2nnFGLFl50lCAbPMhxeJ8gQGfq3g+JHpRhxirlCWxrRT78vw4+DCKil0OItWPjXqN1VQyfVtZ3CC4ToihGQsRxYIk+wQXpihCnt5WC26/obmLiONJccd0AGxPhQrrHreRq8hkZe6xAllEQrueRdPMY46YSl/h2XErKTDPMDYolyoNiVHFXeTUcTTZaxxKC16XGiuO

D0ovYw+xnKZGbHeszDsZc4mOxizp5XF3+QWcp7Y3aqQoF6rJU2JJsXymWmxJIkEmLLE21cWSFamxTZQ7sqhRWlsZkeVVxMDlGyoh2TAKpTYk1xurjRDgCuVVcnHbDEKZ7kpXGFjRdceQxN1xOXldrGUQHGyt64oVy8mFT5ofWKzkqHJUBycDlQ7J2eTDcZMoUOSUtjWbHpYmlcqHJAJxdNjDXGhuLkceG4iYOadibnIU2L9cQhFeRxuwNPHGrE0A

crG4gNxyHVFXFRCHVpu2FWGxHrjrMFZ2OTsVaoyVxCWUp7Fb2KJsfQ5J1xAnkD7EgMW7sVaxDtxSokNfJI2N9Ok45D0SwE02g5keU18qM1awK4coMfzC+Rh8pAITRyq4kJbEq+XbUvEKBPwmkkWmBblhXcYppVxyNnlXvIlmQyEiL5aMRdPkDkL2BkRsWXpA9u0NifaJhwRo8pXY2Vxttjjgp6X058kXYo2R9RAXbHsa33WqM5R2xJbinS6i8SOK

FxnReCGtkTbFRfzW+hc4qtxeythhL6uO84jtvNzmlbj/wE+CyFCrA5O1xEDkxMZweODsT6uINxnzlmgJWxSjsUq4hDxegUQnEGBSXmjh4sDx8Hjvywx+k8MiWQBJx9VNcPHgePw8SiFWexVXEMZSh2OaIHh48jx+4wd7EgiBnFMXNShyrHi6PHseP8ock4upYsAUrAQsmKNkgB4ygiTclFgTfejm4fFTM/y0KlTNgCBS3ZvKYsiKMmt33EYqRQqC

1xNK0rjELvI5OWRcjqnBw4M8l9EDmeCANmk5LJycogb3EAOOaZhmzUzx/FxzbFUSUCYlZ44zxATFBsJ4+XcckMJFCo1AUnEDIcFkEhpJEoym7j/+a8FC88RLYy8Ei7i9xKsHiC8UuEbzxPGR72G8BX5sS9JfjsRnj/GKUUEi9mvBa1x08lcuDOeJS8f9Y1Gx5e9iqpaeJcYgUgXTxrnlM3FxuNo9AV422MwV0H7JAhVK8ndkApxKTj73b7BR9UlQ

ZSygWOROPEqMUYOBb0YjySPdQUKKMXScVx4tiWj+5u/J5zSACuIxJjxJgpEXHysWRcT+UdIm4IV4sCqHFm8T5JYjxh6lwXIhcXSkjGA6EI/zk5XJQqKeolt411x8vgvQ7mAIXTp+Y3YMEdsNtwqgAKgOPFH9AVwAzjD6gAtchQATlwMBAdnHVbmmvrSIkxgnli/HB3znfkfcJReMrPkcpIVpEi3i2pOdxqvkQYZdqVRrkVpFLeCQD4rFJANy/s//

fL+ss9jWEZALINhRYsscC2QmkyY9V5tsckZsA9rD0T7SA3+jr8AqvQmkJyrGpcO0gfn3EqEFilmvGuvE/otFZXIUvRQ35QwGUxcfL4OqxMtlvgqLeRtMl1YmDxUcUy3H12O7Cs5FWpA8EUMvIDQT/El5FI8SPOlcvG4GAu3nOFUCKWTFPXFd+GgikE/Zwy4NiJfHfwibCnIfPrYT1isibPhRnCmhFVaxbPjKMqvWPQeDMDFax0IU9fFGx3XcV9ZQ

uOOEVafGvsXF/M95fHy+7jyIqsOKmsfRhMJy/jkhXFz1m68fuTIR89njqhLYeLzCmv5DqxYri2fIbeO3cRCCY4y9DiRvFIuV58rezCxSC1i2RpBE2d0vO4m02xLiP1LVqiZshh5Hdxp1iTfGzuMPcUn4mNxpXjy3GJ+JB8e64+nSsvjIwx9mQGcgzY/txiK0ffFm6QdcUjpJ1xetjJHKCuPKtv6JbjSiEkx3HWeRe8h548gK1jlO/FURWX8pb4xq

kw9l+/HX4QN8X+5eF4AEUQjIh5in8XsyEvxG9Ey/GK+MxCqxAXlxhbjNvKrWMpccvNMtx6clreqzWJx0hp5a6xG3kxwrjWWsPpN5FPxeAk0/HruTh0jf5ZmhFywNrFe1UwqAn49nxNkUKvJdeKd8Wi48vENVisXH3XmG8UKuXKyjPjxL7YuIwsnV5ZhxLxkAAlyMCACSbPf/x6IkmfGtWLIXl/42AJynZj7Hiv13oMpAIwaYIBLsIDAL0ADorY2g

xAAJ4AtQAJyliQi+gam4lSAQcBH2vk0Tyx4NxOBiAIywkrRCY3xe3lTfFAlic8cl4oA2vEDYrH4WOE9vqwsE+8PjkrH3AIynovVTSyna1F3D7ymwcerPayqD8BBs4cbSUgRp7Bm+yS9LYgsWI3QRUAjJeuGdn/HA2W6sSP5TqyrykXIqTeJ6oNN4hkqe/i9DKr+ThMqAE9ay3PiiOJDWOEMpH4m7yakRqIpwBCGMpYFZ3xxSlonJiqXvyPYEhYKX

viJHKEuUo0u74q9i7/jZDICOPX7K3pVdxh9lKfFvvmfzknY5UEF9kqZiIBF45mTY4DxebjRHHW+JiCVKHXSSwdkcGIoeMSCU0wOnxHCcW7FreJLkrqg8lxC3kZz6j2PicXwxd2qNXij/EceP68R142uahQTavFqegSCJYxRegQmtivKs+I8OBV4lTxxXj//KH+OZcc3NJLxfVQXPFRBMdFKwKSQoR/EsvG2eMmMlNnPFxrXjLxj9BJs8Y9QEIJlB

kqfFoejmCSZ4hYJUzj00Gv7wXhrvQFwAjkhUIA1QTYABPAS9ASbQ4ABXAAngGAYaoAo+k68KZ3yr0Aq4WIuMQhk+50QEDwOrEJIwA4A9krwWJtQA6FO3wKERxfFYhRRrrHnJ5xsDi61pDoK4CbjfXzhJFi+Al8A0eRug4gBKO7xxQ6yG2G0pFwwRgimhIcjguLkCYAuSABZPi2cKaKRMCWtFOhxnDiN/pz31Rcf4E0FCluVcXGhqRmCXPfIgSfwR

W/genyFXJIWWfxTriPcrxeNFkivRazS/njkYiBeNnctQ4lM+zG5XJLmoEs7DOot8S+kUPESb2UmktXJaBMXbjPlKKeJgYuAxLvQhhiJiT++PACcz4h5E0Rj4BBVFFFqCwxVsK69kqlxAqF9nFt+Khq2KRA1JWY1LsYnJVWRoIlU/EQiRNCXNKCJxqsiDwpMuOVcrf1U0JeIk7QkneWtCXpJM0JLvw3QkbBLM3pmgzxkwWl9QChAGOYChCS9A2zBi

9AcACFQLgAcrAy4BRwD5byICfArLS2FZwqHhYxEoCaHNLDAT8R0NL6Wz/BNEEwsRaUdUeA8VFYwj7QO5sbATiNocBMSmAlY6WeDr8EfEpWPubhENDm2D7QtkzqjWT7hSeXpwc2cfo5zsVKnmAA1sEJglgY4s303QXUAkfy+IThDJTBSuBnw42Qy7DiGrxjWNw8sKGVWyHHEdAnJVHzUcj/HRxr4l5wn6eEXCTKpZ+4/ElV7K/+Kp/s4Ep+irgSOH

GWBIfxnT5MwwE1jPfGJcHHcep4o4yPdRzwlWMArcfUJfpytWDyQkteOfZgm47M2wGkpgkUhJsYYt4gwKCUlJgmWKWmCTYwnEKmT5pPKfhJfCXV4qAKhTjKZx4BQp8UsEsIJDQSLGJdG2Q3IsEuIylIS+gmdOOGcWQFO1SOYTD5ArYOC8dlxfScQwTsgmHOHbSLc4lJiAtUiImvsRIibYUVpxRYThuLYROGCbhExB4tESr5KHeLTQb6Ek7xnjJmAA

sAElyGGAcDAwWkp4AxrXUvMwACeAWlBlQqaXmfsWc2SpmalNSvTjCEOcS4QN9RnaAOXpj/GikEfxMaQOrVrKIrxm1sSSJB5xdd9jm6xANwsda/XVhtr8Kwn2vzbvhCE/zhfANFRquv0bDn7QXNECV4n0KD30rkCvcV3KaITVIGsqSDfs89JQJ+J9Cjb12So8jQ4sqMuilA/EthQ8ssIxUnAxxkz7oaMxv0OeFQ8KUElLwpX+R0aCw9CVqB3ke7L7

BTj8ayUbaxk/kxAozuNTduf4w6xPjA1HJKON9OnUEmhIwKU1ZK2SU0cZpPRG09ASFWLnWKscWz5FBaGvjZfKa+VrmgDY+Gxp/k73ES+VrcUJxdqJtQkqHJS2XPsqSFBvxonMw3IfSXB4PX4nmSnbi4gnGRWRsePqY1xw0T2wipuJ0iXg5eaJk0TRObTRNzcbNEi7ufDk++aHOU2cptE4dx7fjnHJt5XvCV8ZYZyfIUObEnRIuCkz5RtxmODPy79A

gtlpf2KexrfjfDr4SHNiGn7B/GYoSOpIaSXlsdnNNrepNkGolmOXVsVMJTWxPH4oPKUaRg8rYWOxy7nihhLRmT3CRj5WnyiHkChLn4xtCj4JBSAZnjrHE3uO0CioFMWS7/wjOKgJEJQuhrV9yx0SZHEUSJ9sVfoJrUtLRkIomuIQcqJ4vcgBddvDQ+ewgild5IQ+N1NSPGi5zFeHF5E6xb0kPbEE2L/NPS41mJAVQNolK2QzsSlEhLymKF7Ioq2M

l4VzElmJljizXF52IvKAR3WfxtMS7pG6STYgD71X2QxMSbrKkxKeuNiJdWJJkVC8roSS88pD5B2ew+NSGL1lVL2IjwDoUuukNHEGcVRcjHgNux+XtPAl/eWJcji5amSsUohGJcyKD8aD5HLOHd0+7ExxBYWs9EiUEJQSqPFVyWs4dRQiIJWvgZ7FjeJcoPPY2xxAJl7HFpOPg2AN4opK9+4c3EnOXoQfV44Tx2GwriSjCWWiV3JRoJSES5uS5xLW

cvTYus0w8kBjDk4H8YCXEhyKj7c1ImWc1iXqzTJaJEclBnFrsg0ifH/PVxqzla4kA23YiRYAhAGuwZkICoQGAwGv/RCABwAxAAQwHAVo/Yuxwn4Qt/7qklxgAKEX521kY6ICMQB+4C7IHKWbHJikpz+Wy4ummK9xGTkTgHNa3S/oZE+/+dNtsv4w+I5Idc3KsJvATLIl+K1WWkqNHKevyVwUHk12BcZcgbxcC403Il7sFcoOJZDSBfYTvImwuJki

gH4yGkYIC/ImlWWCicAEtfyvkD1IoAJLBLt35cKJFNlOHF9WLe0qFEqmyfKEV+xjhJ68cqUAaxF7FHfEOBI/8cL4osKNbiiIoARJK7qkLQEKsUS1bJVulgiWoZNQw6rFt/HawT32tmExiJX/URXKYhUFiWO0D5iOESmEnheQIirdZbDyoQTqEmBOQesqIJbBJ7gTWogCJJUcqokZiKx/kEEmOeRV0vuExxBXEV8wqgJJv8OVEo6SENkVMIqJL5Ul

VEwKJIAS9AlN+K8CRE5J7KDoCpbDdnA0Zg5EPTSAriIYmGJMoGqexRKJ3D1UcHbBWb8ZYktsa9/jlXAT2nx/BYkgxJZqk8okSOJK+B4k/7y+1iSXHrdGqUmDZO2JWfiGAnwpg0SY0ZLRJtaMKgm9BI7nBS5ORJ7c1t/EunlRido5Rh4ybiiiZrhRvCl0EjNx/rid/HVJkusfm4wXx+SSZYlK+LKYkUkpEKHZZqQnFJLoSSV4vJJx7kpfFhJKKCUG

pY0JTST6gnnaXocbAkzIJNLigklUOJvUryEmDu3iTaXH9llj8ZtYtxJ33YEXE3hIntEQ9d+iIiVgEk8hIdIlAqZ9uagh7EkXiQZsj35HqxPwgZxSSSSwwFqEpBJLVkWzKRRP6CLx0Jqx4CSAomI2WMSdskoyIkMj5kn9JO6AUd43oBnESfuTkgBVAJoAJiMOdgVQBzaGnysBgD6AcqB6ADAYAOYKKVdzeqNt2WAN6GL3Lc+C/aT3hkuCZqGLZqu4

j4JFGAQ4m8MU+kH0gVMQ1LkCNYlhME9s/FcsJZ8TErGXxM+cSnZPgGUYcUfF3oSdkNJwVOJmCwIp6o+xvgHMUCUhBC9HWHLDx5JpiE29WdYUG7IQJP4Pj15Bhxo4SewqKwUCitOEpKC2Xl58LKxLggr8VFkJujiMwGiRWfKLI2BtStgTfToSpKUSTrpGpSUSSkVKKJMASQ4SWvxLE9ZwFBRNVSVzdCvxKC05UnapIkitWZQ5SXyCXLIqpLdLkHE1

cJkqT8VoNuI1iFPZM1JCriHwnnRMtSfKkoDxM0TZUlapJfslB4jyKRgT2rEGpMJiArE98J4fiCQlWBOe5s6EnGSQaSjwntvXMksyFIEyb/icEkkhMDcb44sbiIodd3LpRJh4VGkpNJJMkAkmWhIKib8FJkKZycU0nStSGSZf4smipLkEXIZgJKiXEkx3waKTcYm5JILcZ2UF2uNaSHjG/BLL8at44uS5aSVXHV+MZCkiJLNJgvwdokPngDcjaEh5

y7/ltHHZRKA5ljRc1xLNjA0naaXFsdvElxxksSdbFM53Xcb9EnkIaItRokAyXGiTqrYGJv1jTHF9RMdSb85Xdx3fjYYnXRIUirakw9J9viPPFmOPRUteEqGJbjl9dKXpP38scFVLxC9Q/EmG2PqiT7EgkUr6Sg0FqpNRsvT5bpUrvi4bJvpKthIqkyqJ/6TwYm4V2qgQkkhGJvjl9bEuMCAydYE16yyjjDzrqpIPZmIkvRy6MS7PG/pNPcRofZcJ

46SMYls+SxidO4vDJiUksXI2OLH8cbEtGJpsTfMi7xNnZLS5GwJy/lL3F/eM2kljE9HypkkH3FNmTKiTbEiqJoSS9PFCRQR3GDEnYKAxl7WhfrlycvxkzMyhNk/0nsZKuWLZUd9JvEUpMmucVKAl9ElkKswElMnTyivSaKZa5SvGS7bETBAtSSJk5FyMmSqfKRxOLsXjE4pyHGS/OafGWocgekvTJfGS1MnxxIeConE6zJ2mSrnLk2K2iWng0zJ0

mTuUrNxO9SVpkkpyBmT/QgBpPCsZL5RxxxqTxJbhOOHSbHYqFSvsgZQkl6zDSaKFFnhHylz/IQMETSX8FZNJDO07pLlJTtmkzE51xmaS34AM7Vo8WR4jDxOWTY0n2tWLcdPyUtJTLkO0lFAiMirm40WJ5WS8gmVZLhQl6k9ZydWT20l4uXQOF8Eh6ggAdOXKQuSDgdGks5Oockm0kioUpCu/pBRUmspcgmtZJpcnzJFQmrPQTC5dZLLSW1khWSPD

Fx7GJOJayVy5AjWi2Sx7EJOJRSatknrJqaC1j7TOI/Mf3EzxkkgBJ0RUgHrAE2YfQAVxYMuwtAEvQNEgU4QnOI67aSROsVuK4chqvUhaogrALkNnxAXtA6CisNqFNDlscRPP6Jw1Eujh9ZK2EjdBR5xMDjIfHGRLZIXKZEdBwkCx0E1hNy3rRtO+JX/8lmJRKVVnnS6H/Sf/BRoDtgUIcUVYlSBH8TolDuDzlIazfeN2/8SGrF+pKoYmckgZJCiS

oEml/kmCs3BBPsO4S9kn0OJHCbh8JnJQLE/Al/qS/xMSE9BJE4lOcmEGTbbs+E5YJfOT40lc5Jp8VkEm3xN7DPfFjuS2UhJ8W1YfpQRckiJMVNuZCDxi6UQHBJeoEVyQFZAXJ0vi0bGW3zQSdrk8qyOrimbH65JlyYbkx1xUjEhwmJ6QZyfiA/tJRGoOUms5PT4kdEm6yu0Tz8iTJKfCpdEl3J19VaQoe5JOshKkk+aD6ZVomNKUb8eV5ZYKqZI2

om3MxYcdf5QaxcQErVJy5O6GHxYduyIviCEkx5KO0HHkkrRIhwBUnTuTAicLkmKJDoSCwEN6VCCfi4h0y9aTMvLOCQ5SSGk5mJZSTWEnyKXtSdTEvsKwqSOdLThQgSKPEVcJuITq3xZJPO8rHHRuiRyTFsAUwKEEkE5NJJEUSTElJ+G3boo4yey9gTbEkrJJrHqxk6LgE+TlkmzJOtidDE+9Jbug58kzJNJyipBcDJ/iSpklOaCSiXh/E8JGbBV8

m75JcyjRktVO3RlpklH5IPcUEEuvSZ4Tz8l2JNGgRO4odxz7Elklr5NWSdK47txzHlD8l35JIof1Es+ylfiEonz5PXyWq462xEGxP8lT5ISysLE02xQ+SrknRRLTidVkk5yeqScQl6BNdSZtEhApOiTFwnaRJbiVcDLzJqtjayQepMWiU1ksuJjOT1kkV5I7jgQU9nWPOSPAnzpLziZgUwhJheS0IlbEjIKV/idhJjCTYgnpxMgKVb4iXJyQTnMn

xBLQXD6EvuJUrtdgxXAAKgGPAHgAKoAIkCEADBVJqFegA+oAhADaaFNwPzYH/K8YTmswB4HqsjZsH/+uGA08g15SqIczgJmu7eh/BIbEzHkXDTG12Y+SbpIYpLpqlik5fQCDifOFc8iviV84vZ67EAsgFo2EhgM3bRT2EvBwNb+ynfiQdwYkofyNifHq8jS4TpA1CyaBSVZJ7sSOsrMmW7sFBTREl1hXACc25SiJiARqImqBKhsuUEuQxihsw97Q

V25SbI40RwtISNcnH+I9Uo5rI1x6XjSEl55IzASO4z/wxZBjujy+KAkpkZCtIcOCBYlyxIQyRyErQupNRZ/ExgO+sRoubtWsPBG8n0hQDSLu4mlAKStOlFZRNkckF5XyiIOQ4MkX6gLPkbErRyAzBj3GVCQMKdCUJPoG4SB8lTFIr6hJoI7AhhT5ikmFI0cphkyQQrU1TZGFRPHyXwU47xR2SfuTHMAOAAdQIwAxyM+bDWjkVMP6HeoAH6AVdroL

wMXsoUuAW2ad1z4ASA0KQTowHgsFQceIe9xKKRhrNZQ/shsYmoST0cf8E6BxaNdnnHAhPgcaCE2HJPAT8Um9RUrimDAAQGfSB7JrqjSOghrPBViU0RPCkM11WDJ5E11hFVjZ771uVuSboExcJDJZECmLhMpyQ3Zf3JYYZQilwdBoLDuEtwJWuSLwnM5ODSV4fCgpjJSOclR5KwSU14uCJReS+bIi+LyKbQPBhJxESy47Y6XDYGNowZJSQTcwlsrF

nCduFA/xRRSMbi/hVW0kRpZJJx1jZYnhmyyUi/AQmOZOldUEARU9QU2cEfxv0k+0kEBVH8W0DUVJOUTe/Ed+LKKTwI3DJvs5FOEvX0EKfqASQATQANjpPgHcMDKgA4AxABpgDLbifYDArJQpzjgsshNRDA/tgTO2QpGB2/QylX3ZKSQ9xg/zkLYk49T4sECWb6xsiSEYlmFJfhh4rKwpcPjwQnckMR8QZVbpuLUF+SHy3j9SL/wYJWjjoWwmi2mR

ClVvHWe498AY7RiGZvqJRX+JW6C4XFgJNZSeck7589uTrcmFGwiKcrk+spieTC8m+6B9YQYElDiROMAAr9xDw4uwZbxS9+9oDg+GQkMrpKXuygeSCHLMnT4csXNEVJVRTTjTU4x00m2JZ9JFMNVgoqJ2RiFhwNn2UGS2Mmr+SoZvaYjeWDMwZ8kHhJ48j3knjqcMTGIqJJNAKQvkq8pTnkbylpRLGSemk+8pCZT9yndJMCSUdY18psZl3ymtBN18

eS5eGJv5TjRIiuN3HPGUn8ps+T0AqEEBFYJc+HpYp5T5EnjcM2wFqYRFSWQgo0ZwVIL/vdE7NqNodvylVGTPKeD5dcGYVgxVzH4PXcQ0UrIoP0SAcm3lG5UpuUpSSO5TrJJ3pMGEj2E/Xxs6S5xIwZMcSVhgGnaW8TmKkkZIIMmf4f2mMGkl3H9iXGkgTEqGAAoSBdJjpOXKZL3IbOIHj/bGiVOMCuJU5jGAJQGYkaoFX9myFS6JPHiv3Hx2Mcck

7k9N0PHiICl+4CIEVwkt9y2K5GsldxMCcTlZX4pyKRi5ohRRYoH7oaOc65FzKmkGCfdHrEjVAJkVxfze5IoChZUh2h5sTUWgxlLJ7vZUoypAl0EureVMf1r5UrSpp6QI3TIBPM3uB4LnE+oAzHAqhVnAP+oH9QMNsEuy6LygAGg4kiBeAM6XQU5zLxOgETPRsrgZsC6q3R5m0xEIBuVlDymy8kB8dp4RFJy2TOszg5LBKUCEog+rzjvOFplJsKbC

Ur/KhJgHgD/w3/AaScJsJcw8NRpEFBqpmWUyUheOTZAnuRKdfFhnchx+JS1or2jAQCXcZXkMbbknqKYJLBYjyk1pJ8+FK0mOhPnwrUU9KMnRSOQrfeU2qZ55SYpEiS1w57lIgqazjTfJ6vUVyQn5JAZDJhQdxZekFymnROjsQQYI1KgZQ4CliWQlPjXEwJxI6Tx1rM2LCsTdGK4Ge3ifXEHeKeooNkibSpVT8DAznx/CY/HPiKamdPpBGyXn8ISF

UoJFwkA9IPRl0SGVUuGpocSEam2lNmcZ4yLzSnsBmAAqgHhtggQICxPJI/jzqSO5qBLFNqWg0RY0zcKnTml7VV2U/xY/lzD8ybkCcEdNMYAgX5jgiHhxDN2GIBOFiYrGlhKE9tik9khuKTzIkZlIRyfCUpGGHNt42D9SDASkn3c56TUcOzhN6GAAXTfEzwxViqFqwSENvOxYqAAnFiJADcWMcAAMAECgAljum4klGWAFyAHlwrWBy9QN6OmAN03R

VgzghK3BcgEZgDpQLYAIQAdQCaWJDrDpY3WY+ljvQB94Fs8MaIDG8B4Q3wgxhNzAOKYf0CmgArgAj8VZcFAAREAW/8SJgOHx3lCnRaeMP0p/MDNF1YilYrOmA4vNG7TlVxztkNgV5ogpIgVxJlNhRklPUyJQkCYSkWRLsKawreIAWU9fnE0H3QeLoYFEph/5joLSCm0KLSkuLhZ1Eyp785yYEclw1ixeJT3WEBFPHWvH4H04W5YBV62EiqgbrAgM

xktxdnDCLks7M9CN0m1CTH2S7slRSL3U3CuCzDX/AoSGGfMikRSBTCY56nj1No6EvU5qgw9T1EoCVwLxq5aBep1dhyt7Lv0xZhjEHhUK5xvDTYiEnSKpuHjI4mdAdGT1IvqQfUpZS/VF58zbwGzqSelPepFm4dZpi+KwtO0kV02w91P6nT1KvqdNsAbYTNRx6m71L0/F/U3dkA+IcChoiJ/lIcNB+p+9Tv6lVfCxAIukE+pCDTz6lINOgaem9SgG

N9scSwANMgaUA0heppXxLJp0SmTKhA0qepl9TiGkCCzhENOwU+pVZ516m1tCwfq/QfJ4iVEOUiMNP7qZjsV+OjLoHYir1Ovqq84QhpVDTg1iD1Pm6MPUk169BMsGl8NO1qoA0oRp7ZVn8hv4xrvlI0pIYS9SzAjwPAXqfOzBRpp5QlGmu0jSMRaFUy87nEv5SM7H/4bZVJYuqm4BoLINIzGN/LK2UT8g4QRaCSl9nawrUy7nEtyBJvH9KLW0EQEG

AhVZxwgnQ6M40/gIrjT6GnIEWT4CNgRa07nELJSYECYtmVowkCWMMX05eNIzGKE0/5IlBAJ8agCF2Vqw0zhpFCY7UjwxGcCKCxY0sDmh+gYl0yYaRmMdJpmJQChFsNNhtGxbcAQ/9Sj0gblHLCJnQ8BpPG5tmyRnnwwEekR8EqOQeDjirmxgd6wVTYJ8pGmmKdGaaVzOfMRETTpAgqQCBUqk0zyEvTTcsFH2nQlq/HEtQBYjFSkIq2mTtcfaG4CY

j3+yNzmgYM4aBepEXM2brYuBdlMO6DRpYfgtGnrNPJlKzKAJEETTvxZM5C2wPg0nYICTwVlai+wSaYfuJZuu9YRCRSjga2Fc0v9INzSCCSQC1PpKfTCxpAyx4OoisBv5v/U8vcSMphjogkBGaeDqX5pJZBMyAAtNuyt1TQvIk0Uozz6KiEac7BSLwELSC9HdNIGWAi0p+pDfsI/RP1J2CBi07+pKlR97hKCinuAvU1CoUDTtGnNgmSKMfrJxuJLS

8Wkz1NsKOhwQs0wzSaWlSkkRaZhMQy0OFs+iAmNNxaSy0zFpmEx9OY4Tiyady0slp/21naZSC3ecIK0liY4LT3mCotOHdFf4CKh80kTiGzNM1hFK0/5p5DTh0ggSBbkGr2PLESrTyfEvNN6KQuwd5pVURfij2Olk6Ak0y5pCrhXmnC8FuaVVEJqRQ05noQbNKOac2ECJpcQglSC4yxnUbYGI9IhzT+mJOtNlabf4OMwsWRvmm54nmaX+kRZpvrSj

Xi4GHqOME0ppppipxmltNJXyB8wIT4uaJsGkSTCqaac8Pxp/21uu7JGAX8Bc0xToqbS1Hjz1KB2HrY6VwQYJnCkhNJxYmE0s14srTRuJJr2cSly0jMYPjTMkAFtMunNdNRbAGOMN6mWNImfNY0nmmSzS+kz83V6/i/AfRpcjTdnB7NOJafSgtUmxiwUYAStKCRtlfR+p+LSMLT1GO+6DGyAgk7ZUj6Lg8FefGnUjC0aAQppQ10Taacw0oZp8DSc4

Q3WiZFP6uZMqk9cOmm+LhmaTnCfUwsM5MyhmtJwaQfJbtWPbTNVh33nLhuigcquKDTs6aqgn0aXTUNGRlLVzxgetLG+IE0/ZpX7YJSCYHRfEqW0sJS9jTx5Hv1KH2KB0wF62CoYmnsEkJ5HIzEpU/200kC7YEBcugEIFc6CMZGm8tKH2KdzNuITMwc2mCpNiqBmwVqaw2sdWkSo0OcLKkGnO56RSOmvTCo+Nh0qlYZjSl1BztJbWLs5dkoovpKOl

b+ODcmTcLJpnnwCMCcCwiTlO07eiUTSDvFPtOqtIJ00TOYkAROmvwRyaczKONp56RQxbJXwD0O2017huDSNZT4NM8+Mp0p4wqnT8mnBUQf6OUqQ1pLawdOl4uwLaRRUfdpdrTtOmCdV06em05wEq7T/Z6ytIs2PCQWzp5nTF/bdGwDHv40rfwpnSdRJqdJO+lSEdtmZ3MvOmrQh86Xp00FpidNO2kLXQ3aSZ0mzpZnS/Omd03LafE04zpeUZQul2

dNi9EjKUeiJTSUumxdN86fp0/VCr3guBbbNJJfKl0tzp+tRfmle8EraSS+KTpgKhPOkLMNNiNi0tjpeUZqunhVToaQsw01mHM076kkvg46SP4LjpVaIh6Jz9AsNP9tfQ4w2AY7EUdNOYm2zSRijnSv2wEdK+oER0xDpON0j8ifUFo6UPsPfk8pj4NBpVCeaTH9eVpY4hFWkgdM7cGc4UPWm3ThrQatJczBLLZ1pGpgK3D7kwTCMA053mhV99KYwd

M1WL+0h4aQfkbulmPGdoAUUVjk/20fpTnGz5mFG01/h4PBHbJQtOWdl5QZvej9c0WnVPATaTxvc2IwXTWXQalOHope0mf6tlB68jwyPpQXgqB7IlUUKmkaEyR6XMUfjp87TykiLtPCadx0+GoRbSQRC8NP+2iTlEjw0QhWul92jVCAOYM/q2jSnqAWZKA0qh0mnpFIxUMhqNPpQX20oRoA7S8unYz0l2qK/SEhKAS7uAHADUXrUAKS20YTgMAQK2

qwG4YXCEzgBmsCYkKcsRlUu5g9RMpmThWHdotDgVFRxK53FrKixUHs0cFYmMIh1mJZdI4NssLK7keHTRlqSWVFnkfEviBD/9OAn51INYc1UoupBKSS6kKz2RyVjhYFYkMAwHiJmERCW3hGUQlilEwiYlJbgJtkZvyvhTynSk+OZSWOlXDpgbSR/J78hEdFY7P7pnhIOGlHJiPqSh0wdpA9TKpRNtJDElB0t+pR3TddyJ9JzhNP4Dxp4nSiekf1OM

LjvU0GYYnSRpTF9PHLFvUy58y3SovioNKfZiz0zepJMda+naNOxFA+0zrpVExdGk89OC6YM0jeodrTr6lvTFY6XS0oXevvU62lsGV46ZPrI3pmFDh2nMyFHaYm2CWIQPSHghxNIzVuD0/8KoQlhpyjtJPdIro0NpvMF7GaJh0r6edsF5p2o1EBFV9JNKRNEAxU37TISgdUyzqTn0+Vsfa5cygn/CT6ZSuOFs3z1XulAEjFsCWnBppw7pPChCMEvF

Gs0odUn/TpmDf9OyKBN051hTHTkKplNMB6Wq06i25SRJdDatKHVKo8RqU795ZWm1cVkCAf0iDpoXwoBkytLvhCxgR1AdmA72kFQI06Y+01AZ/UlyFDhXDv6WJ8WuR859OulprBO6UZ2THpRAyO+ladKNaeC8KgISsUz+kq7C6IDQMlgZ3KDjogUDM4GQh0agZH0NaBmsDKkSBf4DgZS9clwg/kkvaZt0Y1ps3Tu2mCDM8iB9zGQZinTRMT0DPc7I

wMv7YKgyFOnJdKOmGQM5ec4/TtBnSDN0Gc60vrR+AyDWlr9NJxDoMozpZgyFJEyviL6VIM3yQpgzUBmzFDGqEt09/p1gyTBm2DOHdEnEJaYhotT2n8P2cGT4M0AZvxFJulGDKAJMIMvBptjS2Wm+xGcoKGo3nppWwohmadJiGeGqBlpdFMD2kufGwGSgMpXsvnFq4jHJHi6aVsIAZLgzztg39Oz6UoM0qEyzCQhli5mFaeD/C/pqGw3GkPkM4SMn

AzAZzXx6hmIwEaGfFEYNpn3lKBmbOySaZf0zoZpjDYFSnckwTAvUn1IFfTS2lllApyOc0+bpTICJhmpDJnGLP09KI8/TAOkfDCCaXX08TyY/SIBl1WSA6Vv0yrEkt8Rqjz4ECGQVsTf8m/Tgmk6wnqaQj00Qyv9TJIxDBiAGWg0pvpQ1kX6l8dOn6fbyTLwYXENukVDPeltdfKfpMPSnF6BHGg6b0MnFs6XQh+nVgnJach0vRpiQyQJ4sdLBGUcm

GPps+A4+kAdKQ6d309BpwjT0+mFDMa6Mn0yEZwXS0AKwJG1QK30jBpkfTk2ndihr6TR07Rpi9SW+lkjPUaTwqKkZu1wQRmJLFhGYbuPPpMTEs+m79K0aMyM0Ic/4xUbitDO7qVt0NYZwHSzIgcjM7keg4DAZswz6nRCjPP6YfkfvpRuxQVoCV1+kCC0w4aFVNP2l5NPC6W6RUkZK9TFRlIDPKaccMzDsKIyWekHckJtMgMrQZZ549RlX9MLKtwMk

QZxHTXPKT9PQiMF0tkxvkgLnweOCsGdB6AvpGPSYBl87GDmGyoLmIu7S/Vi7DPOGeYI8IgnTSrhmNUnmGRJ0oFINDSpr5HDOdGY+JfoZDQy7RkxsAOGbC0nUZcnTUGk79E+GXLKWaUKTSFmEEA1WNtAMiJpUMjLOkyjOiLMQM0QZtsDCxmqjNmyiWM3gZeo5K9A4ii/uMmMvd+wQyQBl6j0DGRe0n0ZPR9wiC4CjG6aoIqsZYoyQNwYP2p6QaM7I

ZxozfMiZjKZaZLcB/pLn1xxneXB6FM2MyHSG/SKWbx9OYxoI0s3p3qR6RmwB1GGbAuSGSSVxcenV9MpGRqM1BkhjTAunY5L0IWMCJCIUXSR+nMdBUaYiMzwZUfIV+mE9NMaaCMzcZ92dPmnwzAZ6acM95K6Yy0g6JBXKGdk0hvpX7SoRkV/ljYO/kMW4YYytiEWjOiGUCMogOBXTDhlFdPa+ImM+sZ0Yz7ULH9JaGQsMzYZ93SoJnrJnBabcMr3+

kuhMpTPjKHksi0nCZUwyzmk2NMwmR37ZJSbEBLxmABkS6av0pQZ5UomcC/jO36VHwNkZqaF97jtj2HdA602CZcLSgBRCJH+htF0voJtQz/ajpDMDNFZ06/pf85b+lKDLCKNIKbUSfWdQrD0q2paeN0sIZ4AywJm/9PUSBhnJEZR01/BlmGHdGQhMMAZQogIhndqO26QQMvQZFJVvaAkhACGUhMm9RGgzkHC6TPGKPYM0UZ5Ey+Bm2UAEGXfCAwZ3

1BDJmI2ne6dnNM0ZdRQbJlndKUGd+YEtSx1oFRmZxj4gC5MqbpzrwQ47dtGu6f9tR+ApWVPul92isEo9zHIZK+R9QiaySj6QULWKwJ/TJhnEmwF7uHXA8ZIANF3iPsUGGVWSXTcR2A3xmUsKsyFQ5YxpD3SypnRTOJ0ZlMso8C7SIAmljOTVCAkfDAOPSixkirBamZiJasZDMlkpnxYByGa/dOBOHylTJklzUGmSwkEcZZR40emYYDGmc606tp7P

Slxmui0c5pH0IQQdUy5fG09KWmZpMlaZGpS9ciONObadlM1CZTkyqhhbtLWmd2M7niwQgccLQ9KqmWdMloaF0zDpxXTJsoDdMj3CPQCVjp+hJ+5JLkOAAo4B6AAy5CeEKbgegAKoBagAn8A8CswAKqiOZS1X7aeFnPh88dvklrEWXT6BB4qpXJBBmtx8rFZ+DIsmTpM9jyaaUIRk99JGijVUiHxmX9Ut7Q+P5qZWEwWpq1EeSF4+HiAA8U4m+oOI

MSgjKhosU5E3dgk6BacqSAw7CcpA4apO6A0Ha0WLGqTC4usphRtvZoPCOYXDtM8UZ6IzSpkeBEwaUJMlWK1HSDxlK9SJGbeMtUZ+4yy+kLTHVGWI05jpT4zGukytmVmULMpUpNoyUenr7E1mXLMj98O5A/6l2TJ0acz3HGZ93d2hlP9KV7NjM1EZP7JexmqTJtmY8MzKSA4zdxmS4VNGYBMhfoM7TJGlJ9Mdman0tvGk2wQIi1NMbVO7MisZcl1h

hlfNOomezuEOZdXTyumSkEq6eA8aOZfXTSFT/9MVmW7Ms2Ztsy5/TaTIQGXrMhWZWsy/JrmTPgGXC0nOZ+IzaRkY1JPsT9yZgAt2EsiCVAE0ADrtRNitQACPZJAGXAA7nWoA21go7bX81bqg8uKPgt2NBGAD3C8rpGIcHWHvdJUirdH8kP6MleMcrTlC47dOtafvEqKxh8TuamYpI4BqmUlIBhdShamQhJLqSEvcupDeEE8gPDW8tiVMHBxTUcBF

LGmF7oNIEkvO7MznEBoOzGyWsPTSBJPiKHGTVNTSCI0wWZBsyzMISjI1mbnMp+Z6L4X5lJxhvqZBMpQZ/MzVLQw9NOGYuMvOZ/MVP5l1vn/GSqM7MZo9T/5mtj2kGY6M6aZ1oZQFl99KzGdqjKWZqcyOfIrNOeoCrM/LaqCyNhmO+CsaQQnRQZKCzS+m4LMAIbAqIpptXSiFkEjKTQjG01ppy7TOMSm+CjGcO6Tka1zSrWl0LIThAwsuCZFEyGun

EjJNGenM/UZqtDCWkCR2AWQEw32Zosz1XgiTP8YAP01WZDIzNxmmdjiGbdrd9p0iyNxnqzIpKvpMn4+J0yGZLPDN+GUcmNGZhcyGxnazJ+GbaMkVpbgzd/DVxB4mcSmEeZ9PSRWkOTJLaX2M0e6BfSwlwc9O+qsZMywZgUzh5mOLLHmXUUPAZxq5XFmvTIeSe9Mp5JHeYnPAWuS/sJegK4AcABfgDq7WIAGGAKAAW2J89B7w0eKc44MnwVGA/6Au

rHeydPGZzp18AKDp5Hl16VvxIoUDUDeumJSBKCHD0ndpegyQSkHxIMifPM8wpi8yoSmIOLhycg48mZalkUar/wzHxm1cWQ2wf4D1ZNBEyyILKWLhIACm6lgAKDuiMQJlJKgSGGnoalEacIst4eiDSJZnb7FAWaIlWWZCzDJ6m0jIoabO0nhZrBF9ZnX6LxGcvUrBZuoy+Fm+TMmWOssqtEoiy7RlYjPNmZq0GEZsizyOiJzNrOJYspxZlyzdlkez

LXgn6MkhZ4VErlna/EtmXsspEE38yUhkaLNkJFUMucZ13QqMAsCm+Wb/M5IZJAy6RmArOmzmCsm1enYzM9EHTNWRF8sqFZX65yxmHDT4Zi3nYFZ9nSHs5TdL1WAiszvpSnoBAjLDM8WWuMiFZt9SrRnXfXPGeu0yOZA5YcVmkrO+BPeM+OZ8Ky0VmIrPdoT+M3fp2KzGVm4rMIQRl07SIxyyjll1dJQmRGgtCZa6ZXll0/VqGVyCYVZiTEJJlMTL

uWcfUp2ZY4JUMAddP6mYcrA5ZvEzPib12AEmfsst+ZbXSJFnjjPD6MqsmhhD94Ehl2jKmWUQ0pSZmAgDJkbTOIVOLMk1ZdU0s5lFzJL6ZQ0nFpnzQ3BmrNLQWfSlB+Z6/F35kUBnMGT4s3bps9SxlmPzMpYQ3ofLOmgyTZkT0Vtaa8Mv+ZfdTKWF+tJNWffMkWZoczvHiQ9NuzvwsiPpK4ympnR2g6mcE4V/orwz4RlFsSsWaz0mG6+RQSFlH1OK

NAXPSlhh9prpkprOwjOcs9NZsD1+brYYH+mM604eZtMBPGk/LLUWLNM+/wsgz98jvDIbgp5MwQ6d0z9pkWrPGGQ4Mw/pRYt9aTcrKpavcMxvpfsz2BF2x0jCONMnMZ32SUvzdTOFZC+01KZdTTVBlsLP8lKAUfEGy6ze+mejL6kIx0ttZH+x9ulCLO0aUgs7zxYPTApnodJwuGhzMRZbxEMJmBTOG6RmwO9ZwXSBGmrR0wWRMsoUCHHT51kRNN2a

XP05aZUjYpOkBtMpWac0rtpkgzAnqCdTIdHCsujsiXTlMin9OJjAriZCoB7TmJmAjKfWUhsvk2Yky/yGmKi+FDUgKRZJbsM6lNGylWRrNGFpiEzApmkWGXIU9xE2ZzCyNZYmtWPWRRs/ZuVGyImmktIDXMBEdsZTgj6lrIKx9aaUMyVZrEyS3Zi2EY2dxsgCalLTgpaKTNSlAJsrjZnCy6jxCJC2WV+s+Go+SyWCiFLPpaRGIRlpmQysnotZEU2Q

hsuRZ+SCzrDqLPI2Rpst7WWmzMJgTdNGkhxMnH4CmzDNm5TNgGbas/RZbxQLNnKcCM2aJiZ1Zn6zPVnybIM2Q5sqzZdRR7BnGZTsWfC8BjZkmy7VknGzNMoYM7YZJxNONkOpCE2eq0xBwp3SnRnkbMI2YxM1lZVURwplbDOPWfr05DZWGyaTbXBHw2VFKDDZhvSYenxTI+6VbMyDZ5406txDrJjWbI0joYwGzznAqLJFaOlM61ZlWywNCm9Jq2Xq

g0pioIhtlnLEx/WVesoHYYrD3ERJeBnWcsTejpbbSxFlmoERmcms/rZOMYCOmnvlkmSvkcqZMUyCJnSslW6VmzG+KMPTM2kVTNimTj8ZTc6+BcwF7DOKGJms5HpsnSuxZoyMooAAMlfIe2yupkJrI1EsbHX9ZVbTkpmk9I56TeLEHpL0z6eLY5CzECZTOTZm7TVpn3TJg2etZW7ZWrh7tkCLVGmV00m7ZL2y7tmAbLKPOO001wpWQTZlpxDZ6TeM

8tZT0yRzAfLJLmltMuHZBay6em3LMOnCjsotZrmzPthnbOzWX8MrHZ+ayopm9oDm2c1smNgsqRjpmBTKRlksYNrZJCzxeIU7IFWces8rZq4y5fEttMp2VLmcNZfwyEdklTIu2aSBeQZ7AzFVklzW52S9M62I7kzXJmXTmF2bKs7wMNizomlgTIv5MVMkXZmcz0ZnZzMumeLWZ6ZUuzICZqLKxWarshXZGuyv3T9dJTmXTsitZ6uzxtlfuhf6QpM9

VZcvjJdmm7NTqHkMqjOGfTHplq7MR2Q8suA6ZQzEtmO7N12Tbs0SGPLSydnW7Jd2TAo/lZdGyq2l+7N52c3uPExIbTvtkMyRD2QswziUO/TI9ms7KOmYzspQZ/Sjc5oPjMOmQzsoPZFsDIukUrIZ6YtM1HZPBp8VmKNP+2iT0v7ZYOym8GYrJMaadszNa+2yV1kmZORWd1s2bZjUzVlmJZAPWV2M+PZIrRG9mVTN2VN4M/5Zyaok1nksy92baDQ0

Z2oznWk9bKh6XrsnQ8fyyu1nFDHDaQVM9rZcXj3lnDbOp2dYLD1ZlLD9+m2LLl2cvsufZ72y5SyhjN9aXVsirZSrInlkM9OZ2bWsyExDizI2l07NP2c3s+xZbKtL9kn7IP2Y6st8xyQ9DskCFJVopfwZQANIBlADToijUPKABXIDJANAAFQCpAESk30pM+YN4h42FI8IFJHYqN25INDA9y7qOOXQkMqXgWxb/uNH5NGEYy2HWdAtnm9NIoi1Fa3p

J8SCLFC5XecXikx3pcJSsynxACoPjCEwN2hFR18AhtXQfBrAGVULYTf1Yt0gD6Q94f3MwyyqrFxrLHqf7s0nJsQ9I1mldJZOLMs3g5GIyEFnxrMJGcQsnHZqayqFm6rM1WZKhTZZqjTCVmfLLVmTfsj4c14zsdkorP+GUYgIxZhyz6RRMl0t2W+qV0ZxsyrJlXx0J5KWs6bZiI099nPqhrWZSsl92i+zQ9kU6R1ma7MnVIWoy8xluLIL6S2sxwZ7

ojDOkgDLDWD2s1A5YEzxgCt7NhWaFsxwi5hyNRwuzNr2QvssjYHQz4xljjLU2dkRHJpDwykdkFjOlGbYc+vpyozURmZiNnGcGM27a1EAZbREznjGVM0oPkhhyT9iqPFyOYOMgUc9ey7ZmHjV5UUHMnCULDTpxlZe08OdPsmsZYRyUjlpgO9YG3si1Z/hz2jmBHLbWQmMjAISYz8xnt9J4Gb5s62CBRze9mOHOH2c4crcZQyh8Jk1bOsOZEcorZqZ

cA5mR8DEWUIVcw5/mphRAUUAhQJ5stlsNwzYtmSoVTaWhs8FZlhzxDnfZGmTvEMxKZYqz7lmtHLT8IHsxzZKZw9VkirNY2XfLcaZPdSRDlQgTd2e3st45nBybjnqvDyGVS03Q50CY3RaoLm3qSQsoE5BuzwhSurPoxHn0vohBedA0iV7Iv2DCcyViDRCfIjt7MEOVwcmaacAyAwSHdKGDFAsqNZ5WIHJlUGBPGWiMn45gayyBncJCe2Yic945mAp

otkP0FANibM9E5vxywXhxfgVCPscvnqtrTLhlqDNGWaSc+LEs+y7vD5rL9WTycu26RBBIGZlrIIaVQs4nZHCVNWJQnIpGSXMwqZWPT8MAaUPd2d5RcVZqd1btkXmkP6WysmRZZ+ya9FbTJdoNCITo53wyiSKaHMYFBTs4q6kgzfbjH7Ph2WrsvuQkizXhlrHJHWTyMxSkXPTmemJHKVGcAMrI5ilIIdlCNDyOZqMyY5OAyy4j49J2wNAsyW4oKyO

VlFvAXacGc/E5HhzOTlbrMUpLNMo/WE6y5ZQ0NJk6eEcso8d0z4elcnN/+LWM1M5TJygQiYqEztlJs5o5879qekPbLz6MVwLrZjI4KjnaPTnWZDs9dZZYzkjmUsK2jonkVPJphyGznILMIlugQP9pL3TvpExHOy2QFOHdZp3ou9lVnMbORtswc5V3SLllyjhzORQsweIcHSR/BF7OTOdOc0s5RUsVAjqknW6QicjVe3Ryj1nXrMW2Zh09MZMZzN1

lFHPhqEpTK+QCgyLTngyn9OcNMjoY3XTWoD3HImOcOM2zZk/ipOn3UEfWROM2MZURzKWFpbJTAvSQu0ZfIyzhk77KNAYRs3bolxzORmL9MfOUW0fzZi9A1BAOHNfiFosk05WT1gRAafBH2YDo1FZ2pylDlGNmOcbgcSyZgOiTlkZzPfhLRYdbsZXZp5kqnOuOWvs3ZuEbAI4CKTKkOXKc+fZw5R6GYFyTN2FYc3NZoJzTjm/xGWNjFnPTZ4pzS5n

1rD8puNQCPZnRzFlnynON+MNyFsaSeAjVk0jKEuf+sDaI6jc8OgZbMWHBJc2i5hiQQhKpx3fDvSss+pOCzWLkjrDPBEcaIsg4xylFQKXIAuaIkOaIkXBY1n2rO4udkRdLoH9VXvZWHMEuYpctw8y/M5WYaTPJGbZcwy5OMwwkGi2jxZDscpVZ0hyPQhvRA8qGiEf8ogqyvhi8rOD5OpQnF2n305LlCrNIuaFcoli8cQIFnHHMUOZpcnxE3tAASjW

VJguUExOC5KPTqyipND0CCGwJM5LIzDFlZXKI9F+I6Xg20Qmjm8tAXGesMpK5Egs7mJF9SLOQg2dY5RHp/mCwmOu2fNyeTpIQzyhS+vEC6LnzJfp95zcxkBnJtlF1cp1C7tQTZmKfXtmb/MqIU2fsezlyygCOducuOUxKCdWi71SsOX0c2hpB2zUz6LMWtZFVc3s5dRzYjm3Ukm7u1VezcnRyf6C6XM9OTBsD5gWsskqaC7OLERXsoI5qZ8n6ZZa

OI8AJchzpfazh7z3XPZQY80++pM7TVDlNyjtSKyUSzZQVzVyr0E2+uaX8bQRYQgPJkCXK+uUTswzcj4JbrSkCVWOe+sxriZezcfIw3OSWHDco1Zz1zbrm0zgyofaKH8530ixjmnXOHKG9DP96hqztrnVnN+pAk8BmALwz4xkpnJnObRccZRt9lWFn5jJOFDCsua5RGxvtY0BhwGT2M5gZIxzpqGgCzcNo2swHRi6yjRngXJfSX7HbmcdEy3zk2HI

WYQ7on9YPeg3+korMAWVtcz9JdMt3cCsCjmORHcMC5R5y4RQmoBOJNRrDc5q3cTjnS3P3FrEYee0ypyGliqnN8yLQEDMoVsgxLkbLMeORJ+A1coQo8tmiHIlOVeUf9KvWzKTnqXLEOdLc15wXLBx7FqXO5OSGct8oWlNt4AhrMGOXicvg57/wSghHyFIwNUM9hp1JyVLhGJyeau608kZjJzpbmqW0L2KPM55ZadyipI0s07Pkm01O5EdyhDlxzl8

Zs/AN/UMpyc7m0ijVCMByPMompz47lCnMUpk3YJ1qaYz9bnGDiROTTSKZ2+Mw7Tl2jMruXpcTxg2/9aY7pXO+OUHcvS42LdxpaZdPEuRpc6W5zsQHKkgbErOUl0e257AIcDDKEzfaUxczZZLFzpbn+iCJwrcKE7Z0qyU+kYnIZNHvyX7GBKznlmoXOUWehcgT0L/ozgj92KuuWfc8xpF9y2Vx/xHCsD0clC56hyqbkLLKKio6kFLZKFzh5lujK1u

QPUQExf/swukK3MquQKMlKhQ2AHvZYtXtOcOsxyZSgyx3AIjKOxLrM6J4Utz7OkwzjcWCZMwY5xQyOrmxXH9BNOxCZpbVyp9nsbJ4Qp8YSzCS7TBjlOHIGueVTSWUa7QGLDyHML8BQ8q85/VMikBV6Cd2Locsa53Ny21lFqH6ocaYKiZqdywzk0rM6chuuHCe4eAWdnKDJ72QTcuI0VmQoKm2Tm12bACcR5RDydqa++B2lLLcgG5JDTDzlwPM20L

tgYdcXxy1HklDK35NcKIXqAwz4xk2DK8ORsiO1Id8lztmKjP4eTzctlchQtlhTkQGJOVzc4Y5nDzA/K3ZB+sZFc+h5l5z4Fk3UyEXLI9T25Btx2rmmPN/BuNEOHQddgVdk4NnfOYsciq4U8pM+KuO1eOTA8jfZcDzE1bbJG5EVmcn8UoDyVhkVXGgkJJpUVZoFy/7lwPMqaCQsNsCYpyCrnGnKKuVV+FXikq1iNkkXJlWYPsgT0pFhzoqSOnPOXu

Mmi5rlyOiSsqCZdvFcihp5lz2vzHYHmiKowjx5w9z8TkbXDuoIkEb0Zrxze7mvtS+yWn0Ea5ETSkGI+BgSfBBsXe5RITDG62YxRfuLYYT47dyUUKKZEqEWRMieEWzzp6TU3m7MMIsLUyHByR7mL0hvXH+McG5InEi7kH3LknO07BomeGysvCS9QOeZ4aBJ4gRQhdJWME2eQnc9YEX0hObRvNKlSbc8345aIRQeDpOkhaUvQl55PzyzgReJSslBjM

kJBNJpXnB9SCbkIT0tuiIsUttlnrJQTK88qPkYXgK0itMFb6RayAy5SVyqkgKuFPis/cUVQ3lzWnlEvOpgEP0EpASeyrjm1PLueQdzVB4oggFVkvUC1Oefcol5DQt7mLH4lOeTkEN+52izUGSUYHNtC8wKI5WIJFblgPLekYtxFZc+woBNBUNhQeb/SKV5R9ggum9nCweUE854EQ2BBChj+C+eUOM/q5jDzngTuaCPKGyNH+y5ozxrkxwMSMN49W

yZO09dHnYPJxcuoUPIQHpzxVwHnL0eXpyVfIV0IU7lEalmuR9cuFytFhGc7VbPJeUvAlm5Xrz8GQKi2hMlnc0hGzNzMOAv3KHjpbxQNyFhoPXlbnKDeeANP54migIAK8vM3OYG8sbpkWdrL4OSll2eqCEx5EjzwGbtlHJMAacqRiQxzLRk2PO6DqMKDK0CbIcSw6vLwtJQ8jFEPDwMVyiTOeeQE8wh5cZyHvwXRHncFT02GyTZxGrkU3GnJs/EfC

QEGTLTn8jMyeSIzGXw1Q18nn8rE1uUoMlJQH2ExxAntKX4fy8+C5vDNt/CG/lvaca8g25iVyY9knkBxnM8LM7MW8cQrkwgnDzmtrN8ZBLyp7nJZ3S6OYEdc5aByzLmSXLd4ZqgG9idso03mB3OGeaiCAbIfkhbznOFMFOec87QhkQsIgiPrOj/FkLetoBGNW3lrRSosMBURiA0FzwPnvPRnqF+vJ5gMrTo/yb6W18BgciF59bkskC+z1bjlPcC95

3tzl7GG+HcuJioGBC3TyH3lJM0sUXiJRi5pCNcLkT7KlqPocA44WRRT+nsvPvuUlc4PgRSB3azmrKkYkacjQ55Tz9ULu3VY8aBMsP4+hycJmsgl9Jiv8OMZYryMnlI3PaZqmTPaAgczZXlmHMdORW8qrc5CiFRCyXNg+YX4B/pRjyY9lPSFvkXn0EpUKrzAnkFvPLqAPofqafjNKCB1vOFuf/cra8ArMb/SFHOZXhBM9FZ28i7soPVAymf689h5z

jz6Jm86GsXE4genpRpiHPlMrK2ZiKgqJiLoc3PllvJ/mVCBctm2vEWJmvvL6ufW8vV5SzMGe4QyLQ2Wzcdt5VnzPYIWJFYDp5ctl5yDyFjl1PJgUcgc3UELWlOPnr7NzeVCBAr5Q7NPhmjvP/OUlczFQ9FQUDlFfME+Xsc7x5SqJyvmWilsqqU87j5a1yg7itfN8OTFRQ25ZXyMvkUQCy+Zx89cZzHy6ulO4F3QBvgIvp9Lz97m/HIzWpN84b5nb

J17mu3IuZoN89c203yF7k+XIOKY8ko4pHeZ9QAjwE9gH5/MMAkgBTcAtAHoAK5vXWgtjh6ACbMHiAE8A9KpVHtRZw+4A3TF+IIuIPczeoBS4hnOIN4gno6pBM4oxzF7ijPMxLec8zqFY81IsKeKMRqpy8z0ylkzMzKT/FeIAxEDN5kgYliVFZHBT2+lktDBP117QMwcuNxO2ir5k/xLdYTVPdLhA8x8p59xQ80GXMjbG4AB7kBfIDgAHAANUADcA

r3DQAEkgJkACoARAA2kC7AAYAIQABAAyEICD6MgF5INz88QeEABsAAiAClgDEsjIAaoBZ5kqVT5+QL8hyAQvz9ACewCqWSJYcX54+ZJfnrgFXkGWEyAA/PyFfnZACl+SL836s8vzBflK/K1+bD4n7AOvzFfkZAHawH12I35GvylfkR23v/Ob8qAAUvz9j7ZAHKwFwgJUATwSWflq/N1+RkAe35UAAVQDecBGgOzAG35UvyN6BPiBhAD1AGIgwDQR

CD+/L1+VEAccgc5AyQAUAEkgC3wQzAEfyMgD1AEFADH8tgAcfyQgDPQGlALH84YASfz9ABp/P5IEZQcyAufy3fnG/NXkGlAdrAtoBj0CKwDdqcqAQLY/YAxxAOaGwwLkzQhqNfyyQDKgB+gCvFGIxbGARTLU2UgAEYANgABgAr3DtMAIAJeELjAcQBFcB5/NN+SC2ROiufy+QAkAG9+UYAAkA1fz5/nEADVALrgT4ALPzV/kjwDYAPwgFP5XTdgg

DqcCY0CQAMZAj0BPYC0gFbjMoALkAAAAKEYYBZAdgD3/OoAISAUDgAABKOUAD4hlABQEFgQHwoG/5bown/l//JVvESAZ/5VwA3/mT/NL+dkAfX5CAAI7ZQAF7AM2OHHwD4gswBgqh1qe14DAAHAAD/mzQBCSJCAPwwKqBweiQgDQBQz802YkUAhAAlq0zACaOSEA+gBpQCUgCOPk8gXAFnoAKAWUmSYAPv8zQAh/ynUpegAosq6wXGpaAK4AA7/L

3+WgC5gF+wgvkB9AEIAIwAGqi8BAUAWgHPF+SSAAwANliF4DlAO0kAmAAwAKoB0gBCAsH4AaIXnIJIACoBCApEBYP8rrARljP8AQAEcAMwAdAFNIBsgA3oBHgFkAe3Q6rBZJDvIF4sfzkepQMoBx0CoAvQBUXQLSEnsAbAUDACYBSwCwgFhQAtITHGGIAOXkFUAXALOSAeAr4BV4CxnELPy9wB/mOUBTACzgAPAKsIB6AGyALgATMAEABwAB1QH4

sSWAasAIABqwBAAA
```
%%
