lycronisxd/a-shift/basic design/rev1-shift-mechanism.excalidraw.md

---

excalidraw-plugin: parsed
tags: [excalidraw]

---
==⚠  Switch to EXCALIDRAW VIEW in the MORE OPTIONS menu of this document. ⚠== You can decompress Drawing data with the command palette: 'Decompress current Excalidraw file'. For more info check in plugin settings under 'Saving'

# Excalidraw Data

## Text Elements
## Embedded Files
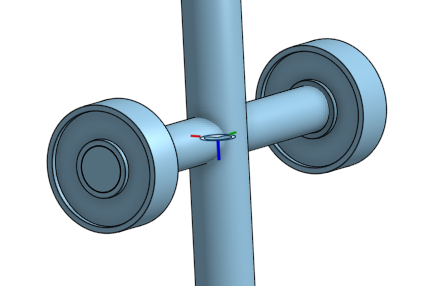
[picture p9: basic design/images/Pasted Image 20260602081555_804.png]
6c5930cf3dd5e4db766de4f270957b8e253dd756: 

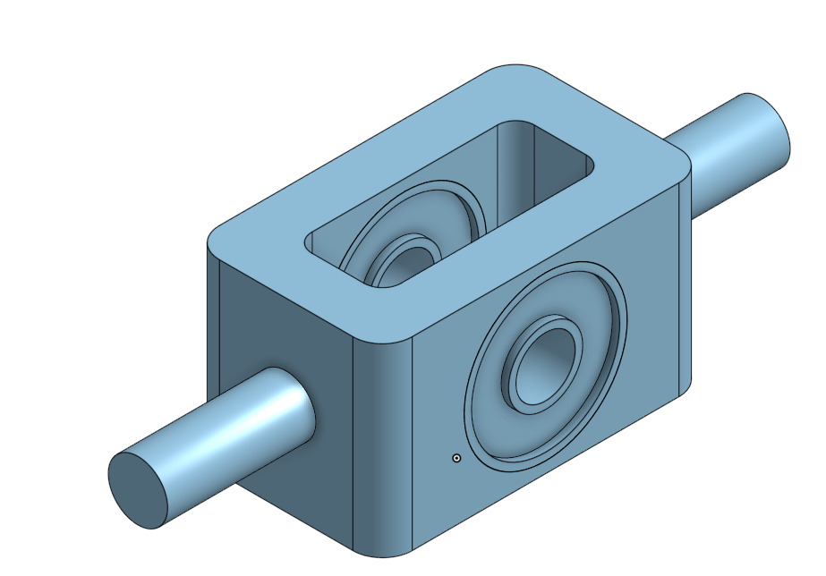
[picture p10: basic design/images/Pasted Image 20260602115310_071.png]
e10d4e89164e3038f68c5ba7f61fe71a9fc83959: 

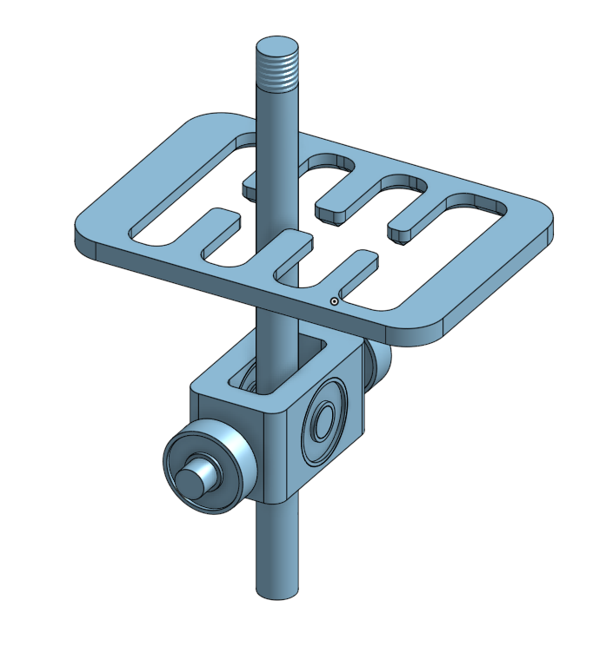
[picture p11: basic design/images/Pasted Image 20260602120044_715.png]
39c1952d884292da36e1c6d54deca9728bf79590: 

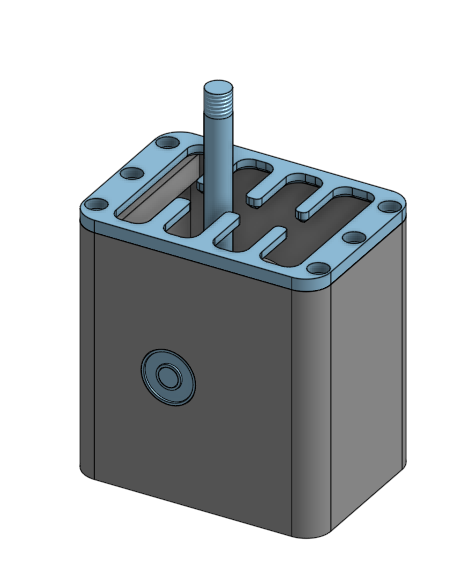
[picture p12: basic design/images/Pasted Image 20260602124540_501.png]
9b7d256a5d4b7ceee044efed4e8c3d3d9002930f: 

%%
## Drawing
```compressed-json
N4KAkARALgngDgUwgLgAQQQDwMYEMA2AlgCYBOuA7hADTgQBuCpAzoQPYB2KqATLZMzYBXUtiRoIACyhQ4zZAHoFAc0JRJQgEYA6bGwC2CgF7N6hbEcK4OCtptbErHALRY8RMpWdx8Q1TdIEfARcZgRmBShcZR5tHgBmbQAOGjoghH0EDihmbgBtcDBQMBKIEm4IADEAJUd8fAB2YigAQWYKABkKJKTNADMAST7NVJLIWEQKvsCETyp+UsxuZ3iE

7QBOAEYAFm2ABgA2dZ4eQ551hcgYZZPY7YaehoaDgFZt+IaXg8uIChJ1bibBraQ5JA73TY8A6vSHxH6SBCEZTSbjnZINPZA07rBrbHhA3Y/azKYLcPY/ZhQUhsADWCAAwmx8GxSBUAMSbBCczmjUqaXDYGnKalCDjERnM1kSKnWZhwXCBbK8yB9Qj1ADKsFJEkEHmVEEp1LpAHV/pJURSqbSEJqYNr0Lryj8RciOOFcmhNj82PLsGprp69uTCpBh

cI4ANiB7UHkALo/aa4TKR7gcIT1H6EMVYCq4Pb6kVit3MaNpjMhg0IWbcD47bZJHi4n6MFjsLhoA4NZtMVicABynDEgKSLwb8R63wrhGYABF0lBq2g+gQwj9NMIxQBRYKZbLRuM/IRwYi4BfEQEPPbj8e7D58CtEDg01Pp/A/ZmCxeoZf4VcVuBsFmOT5CGYAFGMJTBhBYB7KB8ageBEF7NoDSbJCV4vPEnYnAc+JwqBMFwZcYEEZs2h4jw+wYg0

8S7C8lE8C8xGERB8EQYhYyxJs8TxC8GLrEk7wjmC6xMQRsGscRHElLEgn3Li9FoXsgnrHsXbiURCEEYkLy6TiSR7HxSTxGhkLMRJYxsWM0lgDpemXkZJlofe0HIah6G8VhDQ4dsOKaexBHbHEnabEkmwvOs2y6R8FziShzkYV5Pl+ZJWnQUF+nji83GQs82wHEkzFkRR47eQchlvI247+dZBEvNoBWib5ewUUCV6FaR5EnKVUIVXiNFJDVJQ2fVj

VvKprUYuOzFcTxEVqTijZHAkLxDSR0EHORQafIxDzrPE6yvKJM3aNxvGqQ0i3PMcvFrTZm37Gp9FGfth0RWJ0GybsTxRfimzKW8zx3QRD3bc9e0HUdH0QXZEUOQ8TmLcD0HAqZokHGhXy4TxHXpcFqEYw8mzQjwDabMjEGo2h6OYyTOPMRlCOvCZxkjhCFNjMCY7hW9CQjpik7QaNSRNRNJxtaJHMlFzCQ868fMvALzGg09u0iwdClS2AMsmRF8t

ZUrBFU5sNPhXTkWralAUo8kst6/RBvE8xOvcQJB2+fsJtay79sK4b0FJNomHvO8Hy4cT0KDVbtUB0HtGrLxBw8Yxo6CxB6xxFF9GoUGLUNuCWuB8HCdfMnulgsxGfozRhxefxeKF3H7wrUnqzl2nYz/Q1nZbO85XlYx1XR8NBFF/HLdl6nRVkTFaF7TRjGhQ0jfFxPbdT6RsR7Kp8QC39XxhTwK/j4nk8V5vySYor2VGZd+Xk8P60QWPzen+v5/Q

dxQeQgVPRhe5ANj6v1Lu/DuJQdhxD5scbYoVQ40UtpZKSo8m4l1binD+EEIH7UVqJUSN8k4jiAags+YCwDhQavlRsh09o9CDOsIha90GkOJtoXiuJjL4j4v9aEDC35MKKsCUE0IjgHUqqTeIvCQH8NIsCJ4AkMT3FwuCfaR9H42RfsQ0BRVA6+X+pVXOb0viSLQe3IqGdTgnD4jRAqJtTgHGMSQsxGxuK7B2P3RWUdEFpWfigxhpiCKnAapRcEvk

cQfFop4koVkR6x1Xnw/xn0Z68UEiOWi28MYSLUUbW2uteaO1IScEE9wryWMuo2byCColIJtmjL4tNsbTQCbET4Y4+KRVeC1K83tTrUzqWbBpuMIKUVOgZbGFVTj5UqWAaJT8xgqx2i9SG70ZpBVCmcXeukJmvC1sLUWLVxZTUGZxIKIs1mdkuleXCNEdkNRFuNfZ+JDkzVGleTEV5wotOOKorx1sIKM1ZtlEyS18pHJki83e/1dafJOFrf5WUcrA

oKjNTaJkYGRSvLgwy+VYX41CjzLOMVkWsJ2CbfYojVJvHsVk6CsN9KGQRqZFyQzBGDxxHxJOOVDpay+vJX6SkVJqRmiyzCbLngmRMly6lQzTpzX4oJLKIloacVkVhUc3Egx1gbFrYqJwqJqVor9PESqZI6PkikrCYJcTLylWMNyCVPLYShHhGapqnjmoKp2e4WsoJDNdQ8esFrPXWp+THCCzg7UeUwo6zsYUXXkTNQGj1VqtbOB1QkT1ijW6GRmh

ncKIsejhPmpCFNs02Hb3lSOY4Scc2nVHAJYy8DVLFptSUZwPKfqKX+mzZ4Na831sLU275VTvFjGcEFKEqE0UFSeECQ6va60FsbZiId0zqlhrhVnLFkV7jbHnfmht51l0pt2fcya29jVgDRH2xdh7m0hpiWG+Z4N1Y4hojWpIGIsTb1xI83YKbjamyxpRbK77P3eW/XiAk2x/05PQnsKEA83qgcxOBnEkHcTQZbWAZwGi/Hgnwp9DOH6UPYh/VBlN

uH4n4eQ1+tDv7MOWRDNEiAcBAglhEOEfIzHWD6HTKeBAAAFNjzAOPcCpEIBA8JQgABUsBQA6FmZ8S4VwIEKAAXwWMUUo5QJB9AQDSSQSRSAAHlcCSAAJrMgAPr0CEAACTYNUXARhlD6gmOIdA0wqxzH1EsNAbawSQP+pFAS2UIRKogAGVAba1gmyDBkh4pxvJMsgH8Zo5o0D5UgWK3SQZKLcSOVIREyIoA1mBCIxGWEth8VokSDgJIPM+oEFaOkE

oWTsm5FyJAa4BRCkLOKJk7XpTkA4HKBUWRSsJjVPgW09oDRMidBWQ01pTTpYtEtlrNotQefm3qZ0whXTukBN6X0/pARBh+GGI8kZ9zMcTMmc8aAyxvinNmPz6BcCbALBuYgxZSyvgpN57grcnijgwZAFsvZ2yoGhN2Vs/ZBwebnjAtJkVMyznnF+H8f4xgQHXKKYg24MgTdu4eY8/HHuoCBAZa8glFahXfIpl85ZccfjpJT7Hkn/yAT3CBX5trzI

prTV5b60IeLZo0lhttMqy0CSEhFKEBGkIptpfDYykJdqC6l0+tWr0nhK9tfFNCDa+YmVwjAmDtSMb9OA16OK7lQp3mvMTfLFHfFUfeEVLqfMyp9SqpE1dI7W1Vy+DXJO5zt7rFip/b3PVyq6X6kPe9szW1d2hHtKK8lMZmQCTLvi5b5f5qF1vHee9aZglBZe5I30FJ/QBoooXOlcrKSOPleDxNK+0tHJRD2KGgRC/HT73qCf/fMS7w2XY6KgT96l

+Q8EVzqH7qvOpPGE7ibU4jqTfEQvBEeohAh7KpML0bty+NXYUUd8oUuvzMX4TDoG5KCe5qZ7Jaz/MfB3a1iwrHEOMrLa+qlpyp6xUJ6E39nFaIMYqo3hQpBJnYekTYsJd5yluIjgS1kJzdcJso5IJ83g4DuYDpjIQtPZQDk8bIYsikppSljhQdd1kE4kpEvh3gS1mlu82F2lFZPcCJzEs5Gx/ogx6xzgV0ZkyC1h8pXocQKothK4NhQ8u0fd60A9

hCCI21VlRkSk8RxVsYip0Ce4dgsJDh4MsYS0TkthRk5FLkH8yEZ4LkBJlJbwYFcIS1wU3koUF0ipZJMR6xg5fIeg+4nCGpXlIUPk3DSIMpeI1IMYKJmYIoS0UUSUf0EMo9dIipRpKFLoY1606FYjiUYEEjoQkiL0gQQQPV8jREKJjIS1hUPgngk5JptFyItgsVTg6FXgjEpdGwQRB4ngxU6jSJ39uoykDpSZQpKiUJVUwpd5PCvCZp0DglF5sCGI

qVSDlCOjrE1VJjNUL1CkWpKDdpqDPgGNh1+dW1Vjxj1UpiRwZpEgxC0UsCBD4Ng0jjQ1R1TjXgJiNVdhLiAlVCDDVgNCUCEhRi1j3iLitiTCzlzCsIqogSziNjPitiXlzgKV4NLURZHjA9jjsNXj1iPjpiAk4i0UyVMVKUYS3jzjNihVOjMJujaiDlSScTQTKTgTyTPihC10XiqiaTaIDk40a8OkEgcQQlDiMTniTiCSCQcIjg8E91DoRx+4o9t5

hSlDoI21nCgi+IQjCN0QSMIN6NjDkhTDDhITq1tJkJ1jy58RB4LUS1riREo8MQ9I7caUyJBC9I2DnhMRFD2STiklu8P1LTDInox8t5l93hlI1k8ohcq4XFID4EYFfDgz4oPZoRQpMJ4MSCniH1R1QoGi9E8QDE3iL0eIuoMkrwNCMYRYhcUU+IA1OEc5YdtJVlwkcYLk6dtlZ8m9GwW92l28kVGzq8RwgREN18ljMyU9sM0JWEbCDI5JaITYx96p

7I/pIZxwwoU1uDNkc5+COEx9NouyJowRaIFFbopcXZmiEN0zXhdyNgyY7CNV9o7Dj1bk9kX8izNoBJ8Q7zMQHzBIVcg57IDJHINc+Ix9yt9pKsjgPlaIU0I1TgHVksY0nSYYwKeJqYqsoKlTvSYIjc4Ko0ELnVtIUKILqsaJMKg8q85IO068BUV9kKGpwK0LIKasyLMS4VBygU8o+yaUiLGKSLoKsMddFk3pjpCL6LUKECmLSKHEtFRKKteKMLtV

rCthqj/p8QKyiyeKJK+KWLRSyEPDwpDIPkP1IoeJryPyu1HoEDHysM580jF95EBJrz9y85ajjypllTMFZFr9FZb8BoizFy4Zlz78egH5ljP4dFGj9EWj6JO8ArFo0IVyQrtUIq8zmj0kYqFz/z4rXYCE1zWImMfhWN3QONScltCBeN8B+MhNirAgxNSAJMpNmBZNMB5MmdlNfxVMSgNNCgtNIAdN0B6AAAhPoSoSQeIfAUgekPYGAAAKU3EIGkz7

AAEc7MIwABFNzeAHbLzWYcgeYCsd7VNCKIJOnHYnEc6n4KLNtHMv6VCUcbyVCcpH4NLAETLDONSfLPLFxKPSieEYrFENANEYjWjMjO6urBrMkS0I0BkQbKUdADkLrHkHrQUK7MUNrOG6AEbMbRUSbCsVUDUbbCoR0c8KGlbM0dbXHZbOkWbHbYm77PwSQP7Y7CsH0AUM7QMJrCAK7CMKMLjBMcgB7ZnF7XHLMYgHMCQXAHgemosI7J7AHJbIHNAA

yZ4ReBs3HSHNsbgAyOHKHAcDgIcT0OpPERqWgkWjHYIM8bgTnNcH7InXcYCNAA8CsI8E8S2z0S8WnKKS6JCyAR8JTVAZ7d8NgT8DnFTQqnnB2mMciprSCGCnCxKaNAi1yIXb3PVUi36KPU25XdovPOVQvI4C9CyMcsg1XQChlYmaPbOsK9dXFMKCKAlQSWi21FNNiwFXKefSvIukUrM1tJ/MWR5dqcyeO+C5KdEjy0dQSiGHEJ2e3e1PC0ey3Xpa

3IDemTqEqf0+PSqAadczOTcvgvOKELOziave4EyniKPUSa5KXEPTsXecPJ4ZSL4mlf8uGMu9XE2byIXJS7iGdXs1MhmDYJmTCR3NmJg2ffS6+Iyu+UykGf/BZKegmAfDYcI54HYHCNMlLEoDROBcOaEHSnuic1IhfDI4yyvG+sPOubeHYS/IRS1eiUOUmaeKcrYanMJeYserC1NLygSVSUmard6SvL+Q/DEESNvP6S/OREWFE/h0SQRohqhEh6/I

XFKpogsjKmRYoivTsehniXeL08i1NFRqK9Kxh0iFR3EZdeRbvCR6/Xh05PSUcGYoJfKSfMJUi9yzhooyRuxmRxxppCgkpPY8pRiKs1hGsjhD5bhApFg1pO+DpD4Dxgx2y4hmha/FZEZdZcZFqds6u7MwfA6DXcVSiBedJ05fOCKWxK+3J1PCBwy2+M+olVFPCEcSiOuz+8BkEUvF3cvHPT6Ak5p+htptkgx8hu+yhnoLYqo0VDlCVUc7u8cnDd3B

gjeT6FVaETEBKjCQSOZ8e1tADPpFexpT6P1d1S1P9KXPuh5NqI531eNN1RNM5/BhZ8dEKOui2TCRu3khNYyJNc56prEk+qi/lZqJuk1O5/1H5x5lOiiNOg1eiTOr5+5yFjNb1RFiFwNDDb1Ye+eidWNAJNZ8qUyXeZJbFGy2PDNZ4JOVpzBy9AljZ9VElnZrC0tfPOXLKKtSwqEHIgZ1pj5YZzE9tWvflQGApNU95DUkWGFLDUu+ldXUpUp0wqEC

p6gzJf5l5ydE2adVCdI9Js5BILJyZHFNfKdD9bVudfxlpFaOJxWBJnFTKTdM/HdGaX0lJYOdJUK4uwKQB4yB1j2J1vo8A++KA+MxsG5MaZ/A5c9eo3RNST2c4D9axrDS518gRTRpNHR8XfRzE5NyNkSz+eR9I1JgSMNu5CNgevNzBTskR1vAeNCEtl83NwokvEpPQ/Ye4Btet09Rt6Q6uMZiPXuO1hGX17dJsbJfAt2ELA6DM+ZmydVklWUmdHV2

Bx6eBl9RBrDOdk1xd81vGTKZmEBt4MB/5mVoC+V7SF+ulICj+/l3Sk9hlM9z6QFs+qdy+1Vz15+3SV+2VoFTXXPM6eaS6B65aE8/5wVvlLtEVr3de33EfberDMDztevHtP9uaC6K6YDxJgVwFoViDxRMfC9tXRGdp0D7D8DpD0hOdt5hur1aVgjt+n9kCuqZ8g+EcbKcM7fDd3FLds10hfZ5eumHhTj+10/P10d6CDc7OfegQguASuB59PXN9Uib

+1hheLAjh8is8vLdZ84K80iKt7ssRutrDSjBg6jUI5BnBd6fBLKbVHQjPQGdyQ/VN2h7RyiXR5SbVZtiFcOM2Q+JxCxT/C1E2anbVfJjev3AaGaLeYpVYIJp4EJmysIxWVBqIzCCKKLlCVgtpSZZfTD3SoooRffaEQ/J+oZH4sZTZbJvLgh0Qu0iQx0tF05lF+D8r9Q2WKEzlk5h55r0DsV1wyVmlq9BdA9ItG9mrzkmo7kx5GjVDUG8KblXNYbg

dTwyvIGsDUjdDeb6Vs0iYi0yETCSGGbjbx5Lb49nb7iPbq0ndoZIjdb3U6fdygq/8YTEqvmsqiqqql72qtAcTLnXHSQGTOTBTJ8K2lTdTTTKcSnCAAADWM0qDYAoAE0kDeFmqszYAAGkAA1FoTQAAVQaA6Fx82smF0xmB8x+EOo1woVpIWiAIeEupuAgVaJoiJnrDrsKxeoy1QBMjiGODdLaQ9IZwrARCRABt4HFPRXJUMsK2JHtE5qpphslA60R

u6wrH5BRv63RoqBlFG3lBxv1Hxpm0Jp1AWxJo22htW1et4FJupuN4dFN/psOxLGZtx1Zr9FgHO05u5puze9x3uwQBTDlpZ20ze1zHiGlt+1loDvlspsVqpwgIV22Z1s1sBqboYB7DbD1oNqpxcY+BFlwnRznAtqxzDrV9tp3BJ199KBdopwvBp1ZnviF9Zzauj+D99uDvZ1B46vDqAn3Gjq13+bTVhboiRKPtjvg9zoLwVQLoH/felUopw/I6Hvc

lwqSkPpSjVe9dohE+3SBBOgX7I8HOnd2bABzfLaLLo+/bQlQKwz4/qQFKigAb3eAYBVvGkukSFmY7Lbak7C1lGdrn7Z4g8C7XCdr5CnaedOmgRHzgfF6bpxd6knXONJyeY2RIQl8AyjfAeDQNLCaeXQn3AMKDws2+XJLhETQZKtzo7hSAd533gxo32M7UiAW3sqkMioYXaBLAh4jURtUu+LRjtAYZyNqeCjItoQIIY5kY2xjXmIIy4HCJXoYiN4N

ylmKUI7iAhDWNG0ir5loqpMblC61JjeR0IyXQotGQNRuJDgHiblDEytbsFcuTjDAq4xZ7b9uUrXP4u1y0L+MdigTNpME2q7jlGIARCFOK2hSDczBbBHLra3g4TceiPJAJLaUigmw7iWqUIWMTJJwlT6g3crvq0q6Gt4Oi3fdMt23gKsISFyKEn8zn6cRbu35YLu8ieoBI+uwRAblrB56ukIo7pQlqtwl5El5oWBOoS6T56NCBezQxpvOzaEUoRi+

Ve9Cxi+6cZHa3GcqnxgXDVV2M33VAL90arNVWqIPdqmEHB49VIeFQF4JuDszo8+gmAGbPQBqD6ABMUABoDOAExJBKA5oH4O5imBk89qvmZYJCDIjYICslUHoGpQZ7+Y4s5ET4GhHuB6xroBuX4OTUBpddkWVqP6qL1Kyp8qSGsdlOKk1bg05eNvRXkNnhqdYkaavXrKjQGxK9hssoPXhNgN7TYaaRNB3hiMt5c8UsBoTbJSJN57YKwLoRmlHx9oQ

A3e7NKnBdgrDe9eakw/mkmAD6U5A6r2MWu9ggC4BtgEfJmkH2FqlAwgX4fYoCPBzp94c0OfEMnwRz60PMMCNZLLEKzTgi+CAN2t+FL6458cW4CvrziFHO1yc5o6nO1BvD4ZORftIWkHRDpd8ccpQACL3z5y6UY6LEQfuSwwyUs/iDYZiKmljzhdYOSeYoTJEn5stK0iuaMSyzQ5AcbongmyAh2oqQcVipHRDt2iZbkVN2mrU1rOlIRjpa6+KaKI3

S1iT012inFUk2L1wX5b+8BQDObEf7KE7+Nud2DmLoInxTOnBFUtg3YG4NI4f/GQrfQAEP1IoNLZwP/3vr1wxu45VAdvCgHUC/OyhScrPBU5twl4oXSBHHgi43NsytTDAcZXvjapqy7CVYJE0ODViIE3USVvGTgQgdExZCIxmoPSqldsy942sk+ME6D8DBkGcEKDlfQvjuGxGRROv1WCmCAmsXdwTQWjEmw4gH+KxEFx/yliBWUQqdg6QqbpiXWXh

VHBkm5TVCJWjlFYlENuKwI4hoHMIbSWm4rFwSZhAoVcloEn9SY4LJrjCJWJTNPgYqTlHhN0q8Sa8/E+4OmKEnIjRJcEJ7rjiKrzCJhMYKYR91mHjC6qDVYXoDxarA9/anOTYSUF6plAoelQCgNgEEB9B1Q5mTHgMHpAvALJfYGcLgGqDo82AAwYnttSeGUAXh/mT4ChCeivJjaVEQrFdXxBBRmeefHYCFT8a45Oe3AcsQux46wiSsqIKERi0JAVh

ZejWDEVrwkAI1Os+odXn1h+wFT0AOvbGmSKmwE07QtNakebzJprZAaGIpkfbxZG442R8oqnCdjZoe8Oal2EUDzVKp+8Baooz0RKPFofYXgcoqPuKNj5fgzYGKPSIVg1qcBhwOojgFnyRwGQ9CisE4IX0xyh1u+ZfAnHbUr72jccNfJ0R7Qb42J3RLfBaaUDZwl9TpSkiOn30xLBiu6J/YMcLjjGVRM8WLFfgnQQpEx9+NeQ/tlGP5YVYKYMnCBDL

HYgDCCYAqPNqlTpqR9UI/BFsOJDiTi1KMnUMTCyxnp14WaOUiHZ17j6EB4HzblDLgxiHB/oxMQDp8CKj6dRGtbD1nQMfbYESUIKClPIhSL8DC2+aJRhPz5kwIBZhkIWWY1zKqN1BQg8crShvCrAWoLDZDp9HkEhJ7S4SDscewvaqyJkGs6Jpl1iYWCQhBsz9vtHlTGy54BSVIRsnohVcjWIUbjlWOeQ+CXCNQr5K7I1YpSPZ+LREdMxREFQ/Z87L

VoHNWYJCGSdYMpOHPdlLtjmfE7rpi047GsKx27ApJlN+ZKlFJfo8YaNKVHTDKqmkmqh5iWG6SmqQPFvkZK6oQ8RaUPaoEkGIBwA1qAAKyswvA4ANIerOjxeDmYBMMATsFAC4D3Ctqjw7zM8Ip7LARw3cQkoZChKHROREUrCEFPKTbRSY28MEYlLQDwyR6TqbiGlLF6c1cpkNJqa1lhrK9ipyNMqQTgqmY0SR42JULVKN71SqRnUpUZtlpEU0v50N

dqbtkWxdSDs7I53p6D6nu8osfBIaeGB95XTSg/vQPq30VF9VQ+EtA4HNLAXILAcKojpBjHnxbSkpW0naedkYhXxRInNE0cdJ9F/c+Q5fYnHaLUlk5XaS0u6TeGraM41h2Ch8B3zem+jIA/oxhdJBsg/SQZc9NfuHEsK/S4Z2LCRUnSrpRJ85AiwuVXwEAlzPu5c7SbQsgAA9q5+k2uWD3rlbDG5FQaTLjzszMBjQmPY0JgHoBQBoeUAAYMaGYDtz

cALQPYFAA2rjySenmXyftVxyHUooyQQtE9DCh8EO4kWRnptDUiHw9B7wUcBFl3k59TxWwbqNxGKarBj58I3gFkP7RLpchOU+rOiIvmYiMaRUrrCVPxGa8r5xI3Xs/Nxp+8KRdvQBWb0prfyIR1vEpQArpr7YGaPUzkdyIGm8ivew0uBUwrxrjSkFz01BZKNzANBMF/2NvpWFYXZQLuB0whR2CPoajdaiOQED/j0Q/ojpxfE6fwrxz0L7aRcyADdN

YX192F3kQrB6IVFejO+6w7RSxk+mBiCGoiqXPvJxaIVoxvyiRb5HU6YkYxJURsGTBCof0AVsi6NMCpLR55xUqcdqI7hhWgyD5yiEFbpWlyUUIkokVYMonBBorxFcKjft+JWCGzbZ6s+2cSsjRAqyVPMmuhnIDlJyw0gK0lVioIY1jhO18UTmP2wzsqEK8Ki5l/37oSwL04aWFUKoZUn9nAZ/cVbP0ZUT05OuuDWC2IUVKq9mXYg5j2MLqL0Yh/Hb

GBbGX4krpVnKhZv2JXrGq16b4mDlvQTGarsMlq3VSdH/aZilo2Y/Vd2KNW9jeZUM4sTDJTRti1VnLIsfmK9ja4VVQlfXPh2tmEdqYxHclcGtfSWE52hMMKCTEujcTOG8q/iMflxTprN8Walulv2HbfR+VcKfdq/yPbkrkpkc1lWMFzVGk/y1so2dSqHJ/4V28nDWMTARW4r6w+K9fkSuyRoxECDxVCGkiHEqkWWSKsECiuMhwFR1SccdS4kMjQtu

oEK/EFCpxDMQJxYcQmcgOUKCrEZeLcTvAN4KID84h61yNoW7je08BtMh1SfyH6ky4Wo/JhgePnhHiP09Ms6IzMZkszcJFArcVQJ6brjcxJ9MKFLMagyyP0FAvaZA3qa3jaOukQls8B+bpKaWr4qBPlnlSFo6h/5NDQVCwiYbmBFnc9HgjNg2chOQ7Hfq4lBZkIGBijYtjRp9Z0bciRUICREy4TPjGxUahBjPU/hcbHxPG0Cd+OTUExnOJRO0jIOv

UQQJNgmzylfnkQ7ElEz+PjV2tVXT1mEv4tKuIO6RW57+q9T+P0UC42ItgDwAzUvSM0XjwE4E6DcYI86djDNA42zZem1k2C9ZU6ymNqsNUJA3N+IVhMkm0EBk9BVmg1TZtW7RddiqEipOFu9X+aotZs8wcEM+DxadVAyK4uRFbwxCGJ4GkddZtc2rdHZBrHJt+OdWZbviBpfITvC4npa/NxmoZFRP8H1bIt/QheVLw6HObCthzVbrJJEmzMNNYMLT

ZJqDmGEkRA2zVp22/5PIxtrKYSTMym2sbt+vK3fgxo6LjaQ58k9OY6g1xXhkkNE6OZtoW0ojJUVsr4ChmI0ZJDpQc5kkkPjkSzPi/MmDRFDg23bYSuJB7SRz/XcJmZPcOxEyQ+1TEvt34l9dRDfW4zo5d2z7ccDEV0rE6R897YkJh35ab1ASHOVCx+VSqT1PtMFpJNTlFDHVkq9FX8qRnJz8d0IwnbGCUVjDy5lyg0OorLkqStFywmuVwrrlgBuq

Jk7YRIAODYB1QQgegIgD2AdBKgAAWU+wtBzMLQMXesHwAcAWg3kyebtT8kzzMsiQJmQJDxQlIICvw6LPiAzi1EgiycTsBLgSkdLAtc0CvBAXkS/Vhe/1bJfsDjgzlwQo4eDHiBl5FK8pJSh+eUtxFWiql5UmpZVKxqkiX5eNJpe/OZFAK/5zUq3vSIV7dLGpwCvpRyIgU8joF/I0ZYKPGVjSRRUymPiH1mUS0UgvSmWlgumXLLKcH9FxpQg2Uw5O

R607abss9BTcgwaZI5WaL4VvLrRhOW0ZHSdrXTHRNyl0SpBI2cL/ale16ScreWCKB9/fSXP82PW4tcdZCWMXasTxKyUBmM8HXRETiDc887q66CtAxkkzd9UUffZDN5QBqG8E/H7UzIFg04xxfyLflWqyjsxHt9YZ7VI1e0MaJOF67cofXpmSy3EP+2WZ/Cpl6F+442rfee1Q2XaMNqwJ4PBqvh1NMB7SbmSfzrWVjUkZG7BBRt0hUbCEO2/2ZHNw

OkRhNdZKJoOzY2rb6NKg/6BY0hBWNGJ34k/HQY40BtlKQbOMqmTEkEN2DW6egwElImpJ9gy86bWKrzUZdLWQQ+JmlqTaiqrm0hyIdluiGiQ8tkh5Q1Gyq1lMjSnE6ErJ003Rr1VnEZrXWilb/MKttudrTyy/18RUdPmlzUBiiir6Nt82uSYNu60RabcrhwHesyJZbNSWVh3zffz8Po6U5lO81TZB9h5JBy5wflUN2yFLo705W2DL7HhQJGju93O6

t0m5gZH4jFMmlOdwSZG7bw+0PI3bDiOH4ijN3bUiDU27ebOY6R6o8wcSO5Kb0o3So7kn1iFHEjdLQI4y26NywHYfRyksds8NLaQj+R1o1kaqFez1SLWzsTMd6M1HEjJW9IWVsdXWHwjn0aLW4LKTxcmj0sUI74ZAwBIPNoSWwfrPE38bmx2A8xnGxYOOG5kdxhTtgMoMgT+D45JtRW07gcya27eTA1hV+OFFIDD6mA1oZTZ4z44+6iOHJrGCCHHW

e/ZdsNujW9rltZazg7uyAYsx39qEGgytqEPYmYYl/K9kjExPsaUTfq6/fmNv2b8eVxJ6k5gnX3D57VsBnE7QaZMMbpFZY0tVSYY3E7TIJuZ3ObmBPkVQT6E1k5vU31Qnu2hY/9nnQVQsb/mEm0wycTDXCt6Ttx4wwg3VPYZx8PeKfNq1a1nHV9NYtfIWpJhkxhjBRtY9GLTUb5rTHHf5hog5SnIIitR0dJWpf74nxTmJchhiCdTRQzdYaUE4pWYb

lo7CIcecsoQk03HHVm4rptAI9SV5nAAGMdcgUnXaoATPZP6NGJdgEF3Y4hbVEQwlS7x5InhCVSZxMSRFOBymm/CDhXLRj/9W5A+kTNB2mbsJ5mgHcoXIZyFSoChTQUFtTg+sjg/pflcuNnE5wxwpDHoMOat3EaxCE5ls9OYHNznFCNO5SSJjYyqKGdGkwTFpJ+71U3luilYQZJoXGSigPOh0MaAaAdyKAlQGahwGnDEA+gcADoGLukybBpMuAVXr

jgeGk8p5qug6lrVRgXb8oBKlTnrpixRTIQIKVw/LHojPULdBE+0pIUVIRYRe6UtAPUL57e1q2x5NEd7raXQ1fdOI/83yED33zg9j8upfr1flJ7P5zWC3hbranNKelrIkBf0vT1DLM9uOAUfTsQVijC9My6adKPWALLJpi06vfFlQhswIlTe4HJzSb0kLDaSRbeBYk73mjraZ0m0QwoH3MZrl1ethSpB3IPgnpoliANPpoU98hFC+5OrPh33YyL9X

wGlrydBWlp/1f2spL/kX3kr20eKzCEOv5UeXsVKsqlbogUiKrZV2BxdgdBNXw6zVQat4yGqg66pX1OMyKF6oy2JbXVqHBaFmJP2nkWjqx/2KSbjX0cE1Lx1tG6ZZiNFroFa2sfXXrE0d/mU54DMAR3QIYzYzEE9L/EIPsd/T2Kjcl1Z/Qpkvgi6nrbqp3qdWP03Via6Qgk5iFmDB0FmLNczzzXxrGMSa0p2YZzw0S366I32d3pjXjaO15hLmcM7D

WuVo1ra+dd6sUGwmD4qg7xuvqnX7rPV3ayZswmlIv8tiQ4G7mLjumGrreZ1iOddbkTuIOVhrQFsCHZcOkZKJ8uGykM6HPo5h2oVLjivasErSOwlpsyGM51+1dyAlb5GHValr0I3QdKiwCSlCGjepO/TxG8sCxfLpCXeEHAmKfAyj7wCoyhou1DlEDlQ50rzz2JtRLULUbNRKaUPQnhbrpAiy3mPKmnetY+LoaLcIsS2iEINxg2DdNIc2f6pcKWTz

clsBnpzQZzAmmS2J03Zu6GKnVhRwH2cs84UWASUNrTJHb0NVqwpGdsKzk0U/h/Gwy1HDBHQdXnMvGbE+BbF+mnw3lg4YgEIa0DN4mBp9A2POyMhg/K61zJkNZdrWnSY2/l3TtAmrBwSTzaRQ5OYJ8mqS9rsUxFj+csJ+uHs4DcS4pLCm6S9tpXU7iSC6GbnTNieO6gV2imrdvA+EVwSEHS4xBwfuXebt/E9oKB9AVAwwM92BSk9qu23fARUy5ypF

bBLDsbu92l7A9rgvAJWvnA1rww8e03bSVT3q7yM8VKAKnywzyKqAuO9eKwGdq0TCDBM8+qvFz3Q4T/XEwew/2D8Q73TMO8kS9Zr4qOrV465/EAcpnw7sagClf2vYRmYoUZn27GZpNYCX2NWWznepFiZ4Z0Ttg/W6sKserir/zQM/BnNsbJ8rh6QDiQ6/GOq6roUUG16fATOWyZo/W09UfKudw2HEO7K94YS2NaeHZ+ly+TIROP5pb8pmPCI/YeZ0

E5mcnGyvbX0yO+H4j2yIRoQMkakDDGsHaI44eM2SND+wDb2ekcZXz9Yj0/WY9EeX6UOND9Dp6qwzBiMxxD4/fQ7+nUOAO9j0h4otGHbnXu8CtRQebmE7mK5J51nfovZ2GLOdDc7TFDxnAHBBqYuloNgAABauPdYG5M0AUA1q6oAAOJJAlqHQczP4tKCAXfFwFkp5AHeywgSyGhph8olqwVgIpsWVSEzLz5JYbt5ulqVTlgk+Umz9+LJaiEP0uOMO

xF8+aRetDkWVelSjXkHqJEh6n5DFiPXVLmycWJnJoNi10o4vJ7Sg3UtPSzVOx8W+RAl7PUJcmUiWllotcS24qktPKFaX4bGO214hbKlLgNMEapZb3x90iSBTp9pnNpd6Z9Ntc6f3vp3GW6+o++nM/t9qWWllNl15XZfn3fSYrMiknRIrJ0arn1vDvfW5eRfkUvLv2x/WWSkXAGnt0GqRo9VCsEb4DAtrR0LYxdYV1W4sE4Ptqs64vWK3rPEMCIdK

HliXRh1+/cbZe6Udj5xlUsvsxWa36r2tlhwKux3r9IHcA6uGbZThUOj1sr8VzZSpks8fqwk0xqK7VfCqAHlA0OwfC4phpdHsj/h4a8ftz3KUUplR1lbUdCNm8nMgu3uKxcZ1LXoOpLpjHQ07F8ogp5x7Q9cfHHGN1PcszsU/S+qw0gbrx247tv3j6IpMKWccDHDpjhnQbjDvWdBBlR2n4UVcmm6IcZuHHg/Xp8+PYHNmFTBVot948TOlvfKFb6de

m9jePdfHKigJ/uZmGHnNFx5nSf9z0mrDDJUTrndeZMUSAUnVmesEYGkyEA4AmgBADACWqY8Un7c3J/oDgApPLFSuoCyrsqcQBqn2xbJv5vOQFR6REUp3YdCjwsxD2Og+kUkvtu4OHO2eekdhbF67BL4gzAUtOljZjO95+U2i37souQBSpBIh+VVLD0NKEFke1Zzs5Ytx66R7FqPR1Jj2QA9nWCgZYc6gXHPSgglvc8JektF7rng1W59wpks1hiNr

TenhWFefi9iFnzoEKTc+DwZtL3eoF/pYuV7mwX7tW5fzBgSc1HlJHl6bwsBfc4AxjtBy/S+jpG54LR+PNBqQY2OmiYzpm6+OQjTSfByCS4SX1ckcD1f+jjqTwxHU8jhNPV912KjJLN6eHcBnm+EZ8Y5nrgMCAwAx2cTOx5N1MBIEUx6etsJIL+wYYodBaiWOEgrnqFT54YMKyTGpd4RxusSxuedgHnxJBDZC26Cnov6uaLOvKjjhUVVWs5G100KA

lP9JdwdYSv6PByTt2287Y0MisWao3Lt4GtbZO4huIrzcaldFe0jXEoQBlcKM9HODKfZ2XHBR6mUsK8QsqOgnKquR69etGTyJhjR8DErEUFKlJjg8ybGAHRbYRwB4nOSrTfGRo2nhVYFBdK+Q+GmdXECIjlPn8GY7wunrWCM+pIhtqsEw6mtiAhRzkyrjZhF5OPCn0N4IctCtAZiJBxwpMcqOdXSVvftYOSZSJ0mUjYhEd6UIKIqUOCuGElbwENy/

HET7QDi50VfW+7h+u7ZPSPmcXNatTnXGwDMWH+ihx+I/37WFG+pBTeQKFGnMP999S0hjEZcQ2D9PA+8dtOdAoJyQyEz4Xaxs2fGRPB452dslA33gFPn1+9Z8jDMytOlSfTp4ydvgnomHt6ef7cXnXlV50yf1QgCY9tgbAY0Oj3mpi7CAM1XHtsFwCY8lq7cgCH0EfNbvynO7/yVTlwhBxjaQZ3OP9CheRL/MW6jYCcBFi4JXg5+FC909HDEpAOQa

Q0ddx0UO7UQ+xlCYcYqQ/vUA8vTbFM5vl4jZnNF+Z3Reqnh7GlKzhqcxYZGsXunCexkds5L+ofow6H/qZh5GWwKc9g+hBec/w9iWpRuAekMR8r3KiTLVEarHF9KDUf1RHzvUYCAu5reCEzH4T1aPOWXTc91fYfSZe49scjgE+9v9ZaE+2WRP9lpF/5aJ1iv0Xo6MVwa/JXmu4WNjvV6i45V9rvoQV0m4dEnOn+ZVnDbG/R6UdCmkrC9LG/ycW+Cm

X/eV2VVdTAVwP9ZVawyEdx+dq1iMyrRTUi8h8GU39wgbeOC1tPTRI01NcOIGHesCfBawus4HL9nJNE1InWp9GiYLD/h6fF/Wf48TbtHG8VSe9wthOfUXzAB4zEN1TQ7ODn3wcufG2HHYzPcAVnwlKFB3sI0HOAXs8ADdszUdU0AQO9shApRyTNtxMDS/ovbGchkD2Zb+ChA/4f+GFZFA5B2kCYzWQOIEUudBnOhtA6cmjMNvYWXnwBBJfG3gTA1S

F0DzAjRiERSiJqAD9c7LlXoDhfJ91TZJGBRBVoGnD2zYCcHBgM4CmAkQVUE9NeWBB8pzdGBp8yAgtH5UMJbgwc0OkKILutCfL62YR7NIwRSDkAvuElc0Awu1r1dZdxhhs2tC42cYdZNxjsESrZwzpgAtLQX9IkvBQ3atJTEQwS9Gg04DC1f/ZlXrVcbeLyt1EvToOS8pcRrzVlmoDGHBsBgjoMDJmggK0BYH/EK0mDgtaYK6D2rfFyMd/tPyy1kK

g4u2qD2rC/2xcC+LgxcRkgkwSx0b/cGVPVMELILbwcgxx1C8xBSIIC9h+VyyODP4WCV8C1NFRBS9DHADU2DmESQWcCxECok/0oNUA0Fk3tfNhFlGBAyBsDQQ7/QhCdHAwMiIjAmIj5siNQW2QNzON8VYE8NeBHkcWVPoMrY1A3+BCoAEMezYM+vQkNkDoHHcVSNHVd/xohZA5Ti/V2GQkyxMlvEoH7NIfQcz/h2QgU2kJRAtsyQF+Q//13UlmWs2

oYFvbk2AFr7XgPRlpQqbymsJKJAhnRszRUL9ZOQ5gNSs0MENyRNNQhjSbVdPTfh6DKxJkK08UbbQ2NDKQybwNCLQ0tlRtrQx1VaDP+S0LPQnQk/jVNLCI0KAD3vaa0q1XQh0KtDfQ0H1qCAwygN/tX+Ak2WMqjWAIo5X9X0xoCJXJhylcmrKgL/towsh3gF08RiGMhl8Glh9NqAwGFoCFXUPCVcQzfNXTCowksM7h2A4IJF8CwhMKLD/7UHSkDlA

vQPtCG2HTxDCH7VAyfsGmVEzu837EN17DZ7JDUTsnDRilVCJ1fYBHD87fMxM8izSdgVDT7D4Q+QCoP107BZQ0z2LM+AwfjLMrKSsxKRxQ+gklDHXICXiVA/AH0FR97IUKk4r1es0kY+nctwAkuQtcx5CNzbVC7M67b/BMdSwkKA/Dr8ec3g5tZcEDCgKHOiFvV08amWgMCBJCRaRNWDvArwJ0KCNwEaZSExa5qtDiVq1sBcE3Qi4I+IUMJciccB/

wKIVCPvV8IumUyF6jRNzpxd4eS3IiYI/ASojj2VW355AOPWEYioDZiKfUsKYsmNoK6WUj0IkiHtlkJAIoc2lYTkLwgfoYECw35VWze8KANpWd8lvJBIe8g2RSEGszLg6zaVlzRImJtEuRgsbcKXC0ZO+1YozSDL16hWYWuEsIMzZdSzNZw2FEe8CYGsk5dmZC9BYDYURcmJhwsdWDBgX7IcLXZKfMsXfJVyB4EzV74LYIggfQ2FFCjHgMECuRIo0

hBiiZfbujl8QnBX0Z0u3ZnVV9wnAd0vMjFbnVHd0AbYGkx4gKADF16ANaigBtgQamwBNABoDF1nADgGkwBgDgAGB5lbxR8kKnZ3wQJglRNzwRr8cm1KAz3WICGIJUTGAgjQ/K3hgDRje03t04RJKUDgSNHCHOA1RYn0KUIaX9x91/3Cixmc75NGloswPepXJEi/D+WQ9S/OD1/lYPW3kQ8WlR3lAVa/Xiwb8YFa7Gb87sNvzucRaNBQ+wZwHvyss

+/VEBiUE8H+Hr1fnCHAz5dRbPlChTgArCDMZ/Hfzn9gXAy1Bdl/cF1pwwsc4A38vowT29F4XXf0RcgxQVy+UAGS0ydNcIG03uCmON0MbYabbgJRldwlcO/Ej/K4NrC71JiMfUQfA4NeCsNTslJDNAiDh+DmbDvCJdvA7yjLdwkD9BB8eUMEOlkKXQoMqDrjBrw0caXa7SxCk7LCP0NatQwxNC3Zfr3INydb5iykQw9/wNiYYZpB2B2kdSiQItvCb

1o0xQ7SDioRvRKjypVTHUJjVtIIjHUCGwY4HVQMTN2JAD3jc7w2BLveSyMhMIW71XYg47n06Z9gcn1Y5gozEi9CGYbyJx8aicQ28g1HZOMCg4owgkuQn/JWxJhdjP5HKxFYD/A9JLoNy0LjzcEVz+RloyAidQ2UGGJDDZohWDaMGYeuI1xcIJuIbAW40qzmj24wKE7jVonuNDZUo5jD8ddzdt0V9S5bKJCcWdKuXPMDFDqi18bzCAFyd25ZgGwAl

qYgBeAJdIQHR5ceafE0BBqA4AoAYAATAd8IAHanJ5QLN52Qh/4dgVkZZ0b6xGjGeKKV0gWeKDTikOeC3TWZoCT1ChJAOQZ0BoHBBiFy8wRM+W2j1nUpWvkKlW+RA8jo0PROjGLKvwuiFeH+VaktnO6LWddnbi32dXeDD095XokaVw9PogTw79cwTcH+illQGM9BGZKEFadFLSGOhxWY7ZUz46PBsEbBCSBGPxikYtjwX8W/K5TRiuPCF06DHpLhS

n1t/PhL9EPlMT339HLdqxZjzTVTxFN1cMU3XVKITKx5jaVR3G8hRTV3Bzp/2NL3nVLCL/z0TTcF3Atwibe/wHVgrIr10S1Es3EMT2rU2MwhHEp3HUSXE8lRdC2VKTycSrEmsNbRs4xRPJVhXVfTCsuVcJPSsEAv3GBkpcFH0IIEmeJSkJc8A/gDUI1dq0SS1rdH2IlQHJ73JiqENwIWZsktHzeAMfTsK7Zuw3INR9kkipIK0fDFejE1iAj63SDM1

QUJ4JhQh8OwDNrNpKuQP1b2kPE2QhJKbhak3JNSTP4ecKM5oA/uLbi5jT+GIFh7azgpCidVuMyNpXArmk1pBCiFkEag/0JsM5ZUQT/F9NEVRpizvY4MMFbgs4NcS//GUPKDrBK4y80W1N0kq8CQLYlEM3WCQyMTUvC7jnUMvBdRcEYuKgg8FNEl4LS43goZHhts7S2WZjM7c2VS0Q3ZfUYJEjOiVy0UkD23WC/g1myy0biNFIEIqXfm3Q1aXdWMh

TktOQxtZZghkPxgmXOChJY3DKFItlKUrA1uSlQtoKt0yJcQwxhTvCulZiZIS42KC9gnU35dXoKGBrs/rHCRC4BHXK0gCyED4NU11+fzylTYbPgUsDRZByhB81k/mDgDwEFgVw04ENSE4c4wme0Q10DZDWmNYwuaO4dwEFkMOthk81J6NLU7VLAAVxShgHYYwh1L9gnUvdRVp4TZMI9NGrZUMEdmkk/kYd/UnW0DCuwn/hDDQ05hzTDIw9/RrUGHF

BFQCA0uA3gcr2G/ldNk0/INTT0HRfiP4/U2NI8cj9TN2M5s0lMIKCbVWJJHx4k+1JGNPU5hGlM4k3ZLrS7TK1KrxC3Zt0NTHUgpAwCAYTJLSMVjHtPwDL2cukzTB0i1IbTSYgpMU8F8YpJiNZk/JEqSZtZtXdT60pdMHCo4ntVtj6Yj1I3Td0ncOXCzIoV0XStUpa3PUukpSKzTgbHNPDTMEPCNgiWI78Qk4cw0cCQJ4pTBBtS2GNThnFFXChxTg

j7ZhE/skNLlKwxyHYM3hYsIVQOEYDOLmUF9AOGKGoI6kQokWSrOIgxHC2wswKogkQ8jSWT0MpB1MCfbNSB0cmNQQQgEQNY120ZCiT41E150i+Gtdxw7AUBCZNHZMdcpk1fU2SEoljMsRHXCe3PtgkNmQ0YfA+VOURFU1cN4gfXDcPuBPIMWJU14JUTMdcDwh8iPDMlITOvxPghVPPDnrWiOTdeCWTLgk/A9TRspJBIrhhAtQrxnUyRMozJLcGzZ8

MljCiOVPkzrM0HV001GXVyU1hMpzImhkqeWUeD1Gd4LTYgQ1jJ8yjkiIP8zMEGjPrI6M8Kl8zjkyIIsC7KZjS5jXMxWUHtLOSjVHsRwutybNXwshF1SPxdgQNTjM2zIli/KaDOddATcRmKynw0rKyhysrshdcqsxjFbc6dPcxniNFHKMWEwnReLZ1B3FeMKiR3WJwqBNwKzDF0ZwdHjgAqQUgEIADgduUqAeAczDF0ZqATAEwOgGaivib46eTvje

AbKHjRzydDRD8mnRnmQhVydlH20t1Sjy6creFb3zgvkQGGUhVULCzj9DaaEJIZYQtu2lEvdcZ1j1L5XPwA99oxBNz9jopZ0L835aDxL8MEzZxgSmLC6Jr8XeUoEGUXorPSb8znfPQucUFMoB+jpRSoBoSMcuhN4Bfk9WXygwYlSxYS1LePgIIfqKMSnB/nHS0tE6FZGPY923Tjx6dV/APz48YXDHLhcLRd6VkTRPKOgUSJPdl1ND4rT/1UTPE5xO

sSGTe2LuTr/YUwlzAk6uLys3XaDjZNZTMtJvSK03NOjdkxCtFThX8LMJiDSA8tHiC03dJLpMsA/cP4FHoYKxlkzE/ULW0s3PfEepiuSEFyy5VHbwxAPQ5llAiv9CCJxc4zd2P9jvxYZGy9HBCBILMuxTMzVDHI+Dj9RoZKEmjEtItuB0jWIkW3Yi2UGP2Dx3w2cyAiQfWiBlRvIRcQO53dF8UwzUHRwmUi4gfiBcojyQej3FaQhQOlYdEFqBvhpM

ghBgR0JPmI0Dp8QWN0iekLhAMjDHT/2w0SIvVPLcGvL2OWhGIYpB+YQHOgORDSBaImPSCGFbx9c4sSFEZkR80jOsCV85WT0jB8lwi3z0JHfMyI4Q5rNl9J41SSESO3WeOV8FhSuT7c9FfKM18Bs7Xyh4DgNajYBNwXHgMgEASQFx44ATHgOBiAAYEALmAdUHiB1QDbL8VnfCdBBBvhD3TUpQkLZWadA4DvHOthKBDGmiueEgOZkTcn1hATuePcn4

gBM8PDcQU/NPzItdo6ZwQTqlIHOQSQcyDzOjo9VpR+yEATBM6VoctBLYKUPfBLQ9no4hORy3o1HMFocYyhIlpcnXHJwVq9OeBRIlEMGOYTNRcnP25bCa6GNFacljz0s+9FGI48RE1nLET4WbGIoSt/PGJ5zTlOfS+kiYsAM4ZVPKzzzQ69Wx1ZY9cxVDjpLPD3Ws9HC1fBnSM1OdLcLGUDwocKIU140Djt0/wuchAiwO2CK3wu8MvUr08lTsLIi7

Ziw1G83znpD3HcznwNDAsgWiykIfTLsyBoSzSpi9jZCWBSjjOHVX5o0Y/xkh2JLWMuQdY0HXddwUwbn61FtM7RDyGZAl2Mcool2z7QCoC7SlI3rEjhANpZX/THwSjS7gO41HGWIRDYNabwtjkya2Ioc/ZGlJZdpSfsh/pdGYyjsIW0ykInRVi1DnnyYYKSNSRcQPNDUhQoHdOijnyCmKPsiYD+n8phvIKlyogk0/huKt8NHzCU2UJylIL/XcgqDt

HVEJJhgSCzSz+KSNAEpP4IAtzTXl9yMgvBKri5oyHSp07SBBLoETsH+KESrBnLSw06VxhLfi9EvhL8fLOFfS8wu8EyolyBKmCpXY59OzDsIN9PzCx8E4upJZI5WkuKiS1DTpLSS7yEZKByZkvOL5LHZi3M23Rf0CclfI8y6ze3UoDPNesgqOidjFIbIkABMFoDgAYgbYEqB1gbACSBzMTYE3BNAegBmoYAQgGMxMeKQq6jldW+ICVUQSKB6QsIWt

nrw4An3311lIOIHGgWmc6HjIIlJJUZCiQ2P0Wj6E562AlRNCJSgTU/P9z+y9ougrmcsRPP3A9TosHOL90E9pXL8EPcHNhz+Cp6IOd6/IQpOcUcshLRzN/K50787MaQvudq9SDEmRjaevSb5h/MnM+dikNjmedeE8wp715/IRSMt9C50QxiIVCJX48pEswt0sPpfnOEVxIYmJU81Xaooop/VC3MxLlHKxzJkr/Cq3TTy6Ck2Jk5yy/wDzvCgmEKTK

Y1cq0TzHBcsRMmwjMNeLMUnyyA1N07tV1CSXL/TJdEQ0SLnFVxKhmmLINWYrGLKZdmO4jOY68tliXtcA0wRUimAQxSXy28rmL6s/mN7zAEdEM0c1YnDJxDx8/DSgrVY9JRJTO4VDIyyCEPUKpDeg2QNPzaEc/L2K9Y6kM40Ay7jXrIZy70pwrXsmhHeyCQ7CrSyCDZZMwqRcxR3oq8MzLIUkWs+Xzayso+/NCdJSnRXV9l4jYTfy14+Hmh5MANah

aBWgTQAHlBqDqPR4lqZQGHkxdIjzNLt3C0sWAMpWRGYMIiCaOylccM9yChnoOwNSViWVTKuyuebmOaKiC1T32h7ItUPX9No4pRgSM/eBKz8DowkWjLgcmqWWd4y86N4LLojZ2TLsE1MoCq4c8BUzLIFbMuw9TnPMrEKTCwstzAvJMvUj4K9AGLj4f6FfkVh69JQp2Vx/DsEiJDIDpCbKByhnIES2y5hVr5REjGIhQwRXsqstuc0qoEU5EgXOsLQk

x1WDFzEuyunCUCPfJEVxy3lJlcHcbqpXUqsZ4O0TrK1V2Gro8idXHTnPe1x0SpqpdR6qxq8eMKphSm/PaymdeeNyiesiJz6zhKuUqKiFS9ACswoAOzAaBcAGamNAlqdHiEACeSoHoA+wUAoExiAbAFZA1Kx3w0qqnGsDRBb6EjWpIB4GC04RWEfIk4RSodJRwKrS2tF4ZLoS9x0EgBBaJwteAVotO1gyr7OgT2C1yv90qLbP0OiGCxZx8rQcmHIC

rIc4Ku4KcEmDwgBwq3qUiqM9LD1DBYq9tzw9xCzHOL0PsdbJSqepXvzj4ksHYFThEa9WhYTgcF51rL8qinKlj1ZDQtNE6c3nKA9Wywy0qrbpVf2SQeyznOeUtCwcr382qoXOxVArOxMf9ho5uhGDKVJryitqvKANrUsKnA3cSbCgxmNgP0PfG+9eIRKwsSDEqXLCSwfAyEegGwKhmwEm0+MSiCdYcHx9qofUNUVMp+YSALoNrN4E+t2kpwqVMo6g

3PJU0g3AI2iP2Bxgnxe8PQgCC8C2n3ICmrMmNnSikneiNz8CunzjSuTKbyFw6wzwIIcAoheEpYXKLYBrqgguuq4CfNHgMZi+qvcVrrH3euphM8MKUP2C+6xgJpZuQ3PIkiR6tuv7qO6tmOgjPyjCPas86uIMIL6Mlbm8J60KiBjqzrBDHTriQw/HAryQ1gNKS6kvJIWTyNbIuZhci0dAdrPvcQ1aQEslJl3yUrUIpTUpNLjO2SeMktVtC1tfItqy

pY55Iq8zaqr0KIUs8L00SkDSFTCUQvANgC4YoAUmGJ6IOmOuDA2U4Kc1dysFIYh9BNBuyDrkjopGLfyyENQakgvBowabQ/1GKZ88BJWEDO4G4PcRyG7Y1ONlbC5NcQrkxhpDTsSotNYb0GrmM1dEMxsGQynEUhvYauY4DNNSJwuhtwbRGnMzUDq2PMzQgHguLJioTxNcPZRva+BCYySs+t0AabKBNwD9dM1CGIqvPWohRJNWMTNB0uBHN2i8PmFV

MSzqKrImKzs3RXBsb83bEJw0CshCpsy5EY4CjxLY8cGfEZ7DlJ8I1InsJSozoRC37hsBcvKEDK8wfnCaeISJtrh7ymc3kI+QmygSbt+COGSbFwm+z3CXM3MgibsodZhNINoOBiQN1mesEgpHwuGqRJ/G0ZHjDf6+jSdyN6XN1saR07vEnxPYZuDvFtMgxsti9MhOsjr9ckcKUyKzB+mPDZ6Y3AVyNE7e0Xt+Mvezlzv/OV1kaYMxrMUbK3OxyKs4

3e+y84ZyB6lIxoxO9nfoVy0HX4bamrm3CgHTZq3eZ2FdkqxgKkLkqXF+rCZjY5D4V4s1T6casU8i+XQKJFTlkPsWYaZrVjU5dhJQyCP5I8sMIf4mK3bWZd2U80wgCLYb8tfK/y2+qBafVEcKaLsGyFv2TBxFBrRaoWvFqctwVaL2C8h/YAOFSNYROL1r5gg2sWDlCF5tY4u0N4RLVmKgb2uaqwv0x/qZc1lJVJKOOsQ+Y2rK2qaaSTb0xubqOMei

FLWs6eJ4rxSx/KlLBKyJ36yjqwbL6ooeTcD2AZwGkHoBlAPYHXA3FUgEx4ZwPAGUBMefABeBqgGAp6i1dYgrIhzkeC1fh4sYGudKZ80LBWhohdUSSUhuWGovo7wNBiIKuWVFFJQVpClGJynKkiyxqaCzPwD08azyoxpvKgv2YK/K1gv1Aya+PRTKEysKvTL4cyAERzoqxmtzLma8hMr1EqiWnR4Sy0jzQA5EUmF7jRazUWBxG9MWuhjJ1bZlwIac

mWs1qyqnQqZyRSiABZzOy1/hJRjCvspeVmyhFysKSYu2sFzj6TtO2bEUgarcM+0ksXGrzHbFvySty4up3LGihavoZGIH+znzmwzMIIbSXcENAr97XtnnF+IYeuPaby09rfKIDD8ohMCI4YpPbRi1FutT9rIZJ/T4QkCvvb/yo1yAdAKglIxDiUnR3EabxUDN1jksPbUOKm2NARNSIO14sZdLSWlNZc9OEkJ7zj6lYpQ61io4tQrTxd8TYEvGihsE

gqG7lxhkyNOCs8b8QkFrI7wWijvQ7D6zDq0DaOrl3o7aG8BAAqbED23+RQW6hohb3yheqfan0qlP0g+O8jo47nU6cz7YFxa9tE7KGtjpoalHBSLiKnPZlLE66OpTuMi8mpmPk7SOxToE6I0qpKjSaDcTvY6lHY5qI4eOjl007DOlk1VzEAuDmlz9OsFq06lq5ZvVdnOszrc7G3c3K1NLckju867OsVs5akw35q3T36wPLfr12EI0Ja3NdM1gwTI8

zyzD7PEkuJZuSk61iLHPNR3AzzbQDNXML2x8rdTDXCjMA6qM9CQfSeIrmL4zK7RZrNcv01TmPE9GvpqTcBmoxobyAOlM0PgvwwNljJnnGAknM5A0DTSKMUl1iXNxzR6kFMhuyjO674OOiT2guEQgxfEuO2btA5yuCfBtluiPdo67SurrvSLmWDGwSiKux9sojeIvF0jssoaO30qw0FTuy7uUAlmxBGIKtE/9CzHTp7qodW0se6FcRytbEg8mcokl

22HvC+CjIDlvjSwu0DldQs64Hsuyw0SzuqtuUSHqB71+EHs2bPHOdoR67mKHuR6Yek/31dX/PF0R7dgaHs7o8ekMIB7EsInux7VuJt3R648zHqR7lEFHozqCA5cqICeJQnsoRGenHrF8jy6sIx7voLHq57K8H5oh76eynqF7A06VKRa6egXoZ7fIJns7qGYo9P57Ae8Xvl7ueqTqy7xAhbhhqHiX1oRrx66TsvanynXp5g9e+GsiksNSrq/LqIs3

qoQLe/1r2tP1W1O/bQORbh9aHewWv/bduukIxT3e83rR9LesCuY6+8t3t177ewPsd6L6qjqI6aOsPrt64ayPq978OmPrxC3HKVq4qZWoJzlbusp/KXilWw6uHd38ioCSAjABAHR5BqTYCsx25eIDF1SAfQAur8AOzFycBMZgBNKrWp3xta20K8BQhLES2PRgpivXWhBAGIvK+81vHvChrAwdmPXtaIbBFKapS57KpxwOu+A+yQyqgsmco2typjaP

K0D0YKiapNpJrU2pMvTaQqzNoeieLOmqOdG/EQriqJpVmtLaPsDoAralRDKp/Yoeqso2aha5Qro8vIV6C3wSq+nPlrGcwRPbKWFFfwhdG6NPnqrYXaRLHaCYidpU9Ry/qouCcdXRKThGidFHzxXi5RLtduoCljFxqWALxFxM0SMSXFhcfAapZ8UslhKgKB0gYLdZUYZtcKDHZwvzo/jDUwjqUxEZuvKgWTAOrEWWROq4G+bFnrlZf2XzqnL/O8iv

FaIHM3PEHeB0UNlydcvzrkHFDM5N28xB2kwkHI4y8tG11BngfI4lcwcRkGNB5Qdi7cW61UbcOBlwujq1088m04kMFXLwHwxAgaoG602wcQxdOJZuJgCmOHywH3+Rgl5dr0kcVrMoXSCAXa/BszlMc9yvRzkcNcoIe0iQhycuMH9B2IeARghwbzJMx097p8RTw+IdTUpBwVujSJQ3If3b4UDiiQtwhhIZPQJwHuD8aISrCmTzGICIfk0/uiodsj0W

6FtaHtwttODymG7mDcHLyC9E+aBYYY36GdOC9BjTUwgwfMHshlANvTPXQEr+6Tw2Ya1zW8blJUNYkZYZxK1HB3OEMNhvIJWH5h5lLAcBW9hSWH9hrYYJThBhjgY0JhtAO4H80gsT2HECA4efKlBpfhM9uh/7t1zWBwYdPSvmogdoHqWSXoa1pepfQXbgRozVBHmY8EYvKRtHoYyKjO6ocT63EfFp57ModinbpnocIsqL8KaHxf1jhlqwKHsRhGUP

l0hyqwQc5q2VSsr31NJNkHkh/YKxbIdaVHv0sU19FYDqRpkfgCsGmIYZGd2mkdcgwh4lrXKHXJAYcGohi12f8pPdAeCxZwz9GJGMVeRWzIwxUXEoHWDDqtwH00JwdVGPbHAdR6BBpgd3LiBiMSBG9RxgesGX2pIZLF6B2XCsHk6x1Th6H2HXMsGfh8OXAcCh60ZYHp+O0fU6eWu0LFGjR5wbVGT+XxNx6HcaUZ8G5RpVMhGLakMQnSgULTncHC6Q

UcCHUh4oarTuRw4fqGihlPISHTylmzZH7msQKQEr9PQeXawMi9MUijakoDh6K6QscvSqxsAH5bCRu5vLGte4sbtiAUBFGeAsR1sc6TKx/lSqGEo5EbqHyKW7vECG67QfhGsxnIZzG2hwlqhHeh2WFGH7BmpDMHqWghk04KHRMa6GuHKcfIoFNXjj+Hhh8LsnHNIrhsmGVBoMJlsZh84djT5B3lpEC+x1Tu2H8h04dvCnxu7qEHR0kQds9/wihkAE

gKt4atHz20PBk61xH4M9Gk6i9BdSAJgEa1G6B98b3pnxiopJH/lGExTTVh4osnDGk4FqX0JxuEZnLgxQcegjahwiZKGMRpaB7G8J9drxRmxhsSwnlvDIffpKRlF1NVUB2kctGRWOCZVGEJvNOhltTeascGeJk0cfYWRs8tBwIJ/UZn5bHYWJ7gJJ/LweG8OGSa6K5JplL4imJ64eodZJ1mRhb5LE4c+ZlJjYJ0n7xv0dEmmbFSeMnLxyNPWHmR8y

aMmCxk8YImSxxSYC6mG+cZjG8xTQajGBxaYcYnyRjNKyHESpcYTGBh6dL0m6JoVsXH4xrcdCmOx0ocxGEuVwZCmxhypKRGL6FEZsHkplceaHouvccxJNxi8hSmGkwRwXHIS9ocMHipqXvXHxyA8YhGfJ6qe29VBmyeaN3JkNxDG/QnCYxaOKy/I2r1JMUu7cJStX2fyNfZstXjiormhgAkgdHiSAZwZQGYBceaoHwABgegHWBBqegHpBcAavtcxP

q6+NgKu+pEk6JeoTwhtijax0prE0Gfmv9IEmPFEn7eAJdpBYiCnmFYQnoCdTiDkLcNu+ybo2BMKkIy9ysByvKvfsTaVQKDzP6aRKHPYLD+3pSd4MywhKzLBpYQtISi2/Mvv6sc3ADF1n+gQDj4MYKxl48qyn7prLv+8WrY5P2NmAAG5as5WAGKqh0TAH0Y1mFd1QzaF0kSGq2Aaar3lIcvE9ja6iYFGUBlfVRHZy8UdUc+Z/gbNHvRuGWcn+J1yb

+k1XRUerGNJ6/kCnQhnmckUwp2idub6JsEaVmZZxsZZSDQlCYVG8RkIspbtNPWb+UtZxFoan0xiav5GbxzRCYQV26IelcxxkUOoHhRj1wSC17YiLAFS4e2YlGBkuwPbC5yHiCFiLJtkeNT47LAWDn7J0HEo7q0yqBsRI51kejnMilBhRCyBNEO+07JxOcEyhNEipE0yKhOfEns5pTRc4eBZOGljOiqOaLn27bRv6cisjOd+DC5nBu4M+u6Al7iC5

/MaTntgjAnmJWSDWHbnANTuaGQGgm9xmCQ3PMYHmq5mSAT8yig4n7nVJrYgZSEUueZ0mcU1vDWtxUGuAjiDHbSdDndDQ0nORtY22zxcK5rOYRIFjPwQsMgKsSY7nJ5y9Au6WmL/S+Hr5iecmZERLkkmhl53eY+7kdYHS3t65necHneipbnyUFZjtMznG5mjB0y0yeS0/nAF6sYmLu8fbkSbYF2+dWAQQZfApj2kASDU7mWe6YuhEySdEOg3RSDEQ

kFJw/genWvEsgZZyyJh3uHyF/BY2LmyQcx2KtjHiTwWbwmlCdjxDLr2wXXhukZoozKVSMsoHyNogtHSxihe4pZveSmYo6F4sQkWYYFvIR928m8BPL2F6bynzvhX2O85ZF6inkXETCyJd0ooAyAM8dF4FgYX0oC73VlPINxFkYUF4/GcjiYVyM+pTuDoufn55371YQGwOdSB9VgEEP/mQ5uBcbGefeiA3Dn0aG23mAl2+aCVim94E1YJMn9QiXK54

/D3IloXiDLj8sUhcwarZzkbF9S4/gl2hA0dEp9nVHDuNBr4La3E6RebLJdXaclxsfepM4vgjwgfCHsMZHpXXyBQhEDcuA+o8fF2YFmRRuqBdJ8BWuCdt/UTFr5Hal3bIs1YEIGUDsXFwSb6W3Zvq0e9xEWhG9pwI0BY5HpXN4BBBkuDQxCXFcDZdaWBxoKFQYo8CvH2hmoOTsxdxlrZfqhpMl3HKhpGHBfvsjlvq02g7kL4GoQ9ZTMZeWblgcfKx

9DR8VbyubYpf6WhYZaNnRawPCC10b61hz+W+rd6m6844tVFOBqS+ZYzGBxjOAsZDBSKHlRfIUFcWWQYZCCUX9cfpGmTt212bEdlYMiBdxARdQJrbLoOxepX0QApmygykQDKZWQYRIB05YuRiAnRJkJ+fAWb5jyNh8/mjWCDnEl0+eVgTly4rRIgwJ+M5WNoO5fjYVED4AMIt5/xaSXlYd5Ydh5VvRHBbYVsBYbnhV5WGBADbcEHFgiei2bMnjVl+

eVhA4bhPTwEItbzJ6T5iBZBhDdCQgfF18d4FdW3FleaNhiVyHyZhjINVbHm3Vk1aNgaV0lAogk/OJtcWhVu1aNhYgVua9nGwE4D/mE121fcWjYRICf81KWEPHBCYRVcpgopA4lpSZzRlclX3VlGGiV9IbhL0RoCcNf9Wv5ymHeWKMyKCA4ngEtc5gHVuUOLNHoK+cTWc1lGEN0PmLFGI1UkVRZbXAlgyFBqybNHxUQwcHtawYyIEgSLziYPOFEWs

1gBdvmGwBoiM8zlydjBAV1sAGMhMJNDAOh+CA1ENXx5kdefg817EB3RawahtPXBIBqBE1v0QcyqYd1yJfGH6oWEyR9uEd3WnXh1gNYDholJHzd1pMshVvWI1pNYg2UIV4B0FZGJVkFXs18DefhgQRRD54PYetA0Fq1yNYDh0CkKnOB3kHOFAW71zDbGAegA0nApGhvDVHBT11SFYQB6DVEB9iNZjbIgMMRg2UgXA8Jc1WpVrgjuBoobhCdRIJZtb

A3W1sYEOgQQCIopR1cUqGY3NoZLF+h3oS5F2LHVKjek2uQ9AvhIiFlJFgRmNwODlJ4MIIV1RQNjDZ02yEIMGrz5UYwQB8Z0U9b4Ibye/HjJMUA6Gc2e+2EHESmQvwK82jKqKAbjurM2C836oahHOoC6OwjRW2FmddvnGDVhB3hLUfoohQvN9AvIVXkLryKLBNmtfvSM4B2EvodoLYHS9nNruBWh18PhgIRWFu21eWlOZCHaQsIaTi0dDVzZYSDUB

C1AXhuE93WQbeljFengNdOGuSRGDe4A9tWt6eCMqzNj3UEhbEMZcpXrZzuHIQ8IHykrizoOuYpWFlqlaU5NoJOAqYi167w+ACVzbc/gcycFuGJJcl3EO35t61MDhGrV1h05E065bm3al9CFOhTCLYCrROUy7ee3AkUvHLgQlGfGqWHZhIMKQ24ShAasmoFpfhXN4RICtQRIOXD3LIdp7Y2TvBNqASBcQCVE6RXisbc3hNob7rohF5MASx3atqB2B

BiWZQJdx90L7eR2btw+VjqwkLrUB3fZzeAzhfVtFH9zwoqnYSD2bStHCid0N4SJ2odyZNiAt8BAkBgsYR12J3K2GHdbzAfUSAzWZy7HcmT6oH+FlIhEXEHaKOq6WYNnwEIb1Zhp8ePCREQfMVy1mf6YKEXkKUO+kh8TZuRW12yEccFuQEjSAjwV9uyT01nbd2L1OhF5C7jOKREEMON33dp3QzU2V/lEzXNdt3ewEYEIOGCZ4fFLm9zXdtidJHmBY

XbHzqOw1f92I9xIBTJuvKllzhNNqWfD3mBIKDvB5ejvH0TLDaEYL3QieqAeyJurFCMW1HdPeYFcdgwgmsTIKhmt2EdCPeBBHkRhMah1cbtYs8E95WdCJgQFNxg2lWQ9g73cRiPcDh0B9ErFQN5P3a12I9jOHCI1Iz1EeRnl76WX2UiZCDOAWoSDDh8oQKfdWj3dxWCvwp7K1BJgfl7fcr382YqDkgSueXEImd9+gS4gB+gQn5Q8vLmcwR6IDYFBA

l4MYOAif9zuEwgGoQ0RwhKxesD5nwoIvcEJcwoQ2wGUiavbbYj7VqBjQYD3SEy4eYNuChQdm6dvAQvgbLSsCz8tPZSJUYCxnlXCp6rY5nCDrmBaZ2oExAlWQDwg6Lh78c5HGt052FPoFV9l6ZygTcnrZYPGNNg9XFOD0Bcb36BEQ7rgxDk/cT36BCg8egSkbThoPb9ofZN2iD+xusC091/fzYHoZ+tIPuptKKvzMo7PoGn5WgSuGmhKzqhVbi+iQ

EIBNgYgFycUnPYF7k+wZwCsxiATHnbkoAZwAEx6QBAGMw+gDvu+q93ZYFd9BZfSEbpICD7Kupc0O2WqJFUQ7VKA73LjtgckasXnXx40IEQzXmS6r0+yto0Mp2jwy2gr+n6CgGcJqgZ6+JBn/Ko/rL8T+imtCrz+ghIRyiE+GZzKb+pGfiqS21Gb7AMZqvT2V+4YxYxAqyi8XYSoYjzFlhcuanLNoO22fy7aLpKmaH0aZ6qrpnIiLZWgGuclmcAG2

Z7Wsnb2q/PbUPbdyJLHK79pCClHvBzAcjGNZw4/9qaB+CcIHB9jzq1nhZzgYNGK9m4/Fmb9SWZq3BdxcuAaxgk2U52VZxOU83et7Ja2XPc89CBPYR9E3Q2d5v8JanqYHyKXwAfSTas2ETk4z6GsplQ/El4N/4I6SkJz8Zy38xjE5s2Z6ses/nST/cUIyhA5g5vafysA2IbO4Fbpd2sOQhsZOdHPmKn9vhXODg32Tu8vcazxEfHjmf2u9vfbQ3VVM

YFxZC0YZOBTgLMK4XcmEG/36TlFqZPwEcBpOSZT1U50dTNPFCUg1VlUxVPf28U8SCXEZAqgkaiZFuNO1Ty9GHnQtYYK1PrT9bRiZEI3+HI8+F29rfabT2rnEIiJOwOtX5+V9qIb1tMBP+IOuK07FPvTxEgkJGoQUig0Izr0/W1xSPIilIDvBM+DPxjLokm4P50U8TPGuAnVdX+Ts9ops60MaxnILGrTeArIz6bwQWyYK0g9PZT4s5hg2InoUj9PS

dM45OCFgZtCX0Bl0yNPqzsfDa9SybkhI1KyXM4zP+yFJGBULkQwgu4OzuU+BLq8rcSqa68+JXnOmz5bxUjPyNSO/INI9c7/blvRReBFG6OUgrN9z8U5uzvYwQj9ivhos4POxfAxZbwjF93QI3HTgc728Q41vKvWD4ZNHHPOzwKD+8vFwH29pfFvk6DP/zhnwl8k3CdD89AJ8C4XPETVONiX78V3v7O8znOOQYC0WrQLi/zhC7F9h4+H2SLM428/g

uNzsXyxXOlt3QqQAz4+jvPxT3bM6CtddvXgRpfN8/QuhYd4Wnw6cTl1mXw1ui5tOwD8+gqYdrHeEnRzzgS5OXsZ+aB238iEi89OJzoWE2g2BFMjVWu48S8ND3lvBEmJT6GKjAv5LiC+iiIVrNUepTPATe/FRg42SZkEVlCDJRXEXFfxlLhm2RAarLolfIgb4cMllY44xy7bVxg1fQxgWV6rFnQM1rCG8vKvFy42huVw6C3wlESVl0haKs0J9KSgc

EHihzljEH20q1qDojkErpR1eAuoHhgTgvcxeXivRc7VeSBE3QY5G3qiEyb/qQYM1dqILVyKRcZqr3Yfk1A4ULA/Q2jU5DUm+TEVq1CjgeiimhnZN9MC9mr0Vulho17dBOA416zt6uGNVCGCV4fNVEeX3dUa61CaIF0tqrFcMXHxWNQmq5Rg81i1ZFjGDgHZI6iTB8c5g61t1HuZ4uCs59Gq60ycpgzV2GNxXEFqSl2uWr3tY2AjUCrloQuD50MhO

3NOdca2L3GKDbhgD78SbVAb7jY/Qw4X6HwcQfSG8rxz1n/E7XfVj5DXUrJ4ztm1ENrFDuJOEPEENOFh3Kc0iSNmckwGU3FZM9DFh0eEN0vfJ/2MvZIrQacnhNty4c8D6EMNqmuCIyr/g0UFJH6KOb6m/E4VN3VGMqbWYPwMG3NPRBDjAOC9w8Qv9CW8EZDgBqDWWE4CMh2vTBzqeVyIDUnZ3gIQfqHrAG7DW8EdJb50sPhy19fHAoQ3KEsEYytiT

MJksoYNKwprb6eHq3ILPleYvfZbyZYbjtsaOnRYuCxmAwPbZ26U4YdjAfiotWPuLi6bb8LeKZIUK9w1IFb6eG23kkH9H6h78IO/KnJbnMlu2vCe7cNXg7qB3q3Mtt9PgQUMRO+h2QQT7pPd6PIAnLuoHZXaDMPgZC8x267/8tJ32oOwgp360Vu+ZOWd8JDvg5LBO7XTPh9mTIhWWVpwspwkbtORLJk6XaC3I8AaJnKhhp1Iu5ToXvdGQzmUBeXvL

rXHbAE0lrwYy8rbo8ZXuZvaeh/Q60WjULTUw9mVX3ohPgibv/XK+8rSFkh+McWIKyVifvtc1CrHulocCK3UU8+5rS7xWJPZkIgwWhDl23UGcpfTOS4liubQiTPeiOvBtKjz2qfWksebYHlDOr258tDjFwQfaB/QfgHqvZQhcVpRC8GwQHLrQfcwjB6b2g4FvZ2s29lut7GOSgh91hmBbvaxAjgPvZMgQw/B6ofCHhZNH2k3Jm22h9Eih9S6YH/h7

LtV9uW6NJ0MLfd0peH+ktYf6BPfdwgD9z8nRRj9ph4ea+H5R/zY3IBeF5RKWBI0AeJHvR9/2H91xEcW/kkN0UfSSuB/zZ395DJiEoLPB8oelHhx9/3YgVSBsQYbiZHBvHVOx+of6BOA9MJCYaek6DTHlh88fQDlA/ahtNEODj2TbcR+ifCiLA8BFGhQeCgpbH9x/se0nvQ5IO8Kw1aCfJH0A/oOYltHfKTy9wJ9yfgn/NikOOD42j+uT+Ep/MfQD

3g+El+D+tEEOaSlJ90eYn8BHKg5N01nrBHbD21aeBnshCGei8zbtTg2Vnh9qfSnwZ+KgDRCiHxUMMHJ7Lr8603IoMVn7I/OBcjkcNHr8HLOE409n0gXWe6IeDI4D3IU54oM3IJElKg5noEB7CYmmM0kbBnh58vcE2MEHmeCM/2awyzoTjT32l4dhDGf/nwQPefsBY6noiuEBh4mZRt1I7w7CDjp7he3pxF867qBNI/zZUX16YEOhCDPoyjuK0w86

zzDqQEVaDq6w6L614/UuIAKACgBpBNgTHmUB4gPsB4AhAYgAaAhAE30wBKgFJ2COtsy0tb1/9syrOA2809xrA7Ia/n7hM8CqFunbhr+6Kw/S1AAYuhljlDZW6cSgrDLoy/7MjKc/co/ot9+4GZYKkPUmuP7LKjNpqOoZx6JzauRVo+GUSEsZRvyWahKtRnjMPo/xzLioSDOBcqlPm54IsMf2hjyoBSGSQyZ05V70FjxWupmqqgwtpwdBYY4ssmZm

Af7Ltjyws+VEBqduxUkUkJBVm3RlsaUTZXZFOXTUbUWaSYsWo1DqmrVGi9Txy37bqeG/EVOARUW10k5gmFxBuBsT9LvC70p4O8ObPo7/Tt7Iu8sgjo311A14pxVSL+84lPND9VP7fGzyd84z02Lu1fO5g/i51PfrMzV/DDbld4nfxTwJG7nFBMcHx7PLKs/YuhkOiXXnNioq47e533d4xtPbtYJPeFL25gp1jYpt6k3STvCxThsENs5Ps5g5t56L

qxoc+oX00WhaFGNttdppRUS2vOKQ1z84IT2i37SEUW286xBUX5RnFgQ+LFzOBTcL6HdBYnaDxsYcXkN3YGcXEUkn1jjFr3H2rfsKJWYnLolnyNmZ4lpfZo/BqrLBtk84qrHkfhBJooPLclhqDLijUL/HTx0N4BlVrTE0pZWjG+Spbg3jE35PS8woAFPSgKLrRy6XqLvi9sSSbelsU+Ol5T6ouZ8tT+ky6WhxLqhiV3FYlgdLk6/tHTagE7eS+rEz

6/164FbZNjramdDNjG1QZYHhhljV6o+dhsa9P53P+DE8/qcKj/am/PzCQ8/1XoL7anITtgdC+7EAL4i/Rlww4njepikFlazD3PoVbLDgvqpeYnNVoqBeMUgEkB5p5gDWo7MUgENLjQAYAEw2ABoA4AGgaTF3cynXaetbts3iWsiC6PaHkRYCI7LQAsD17RNgOEYJDzDPSi3XW7KITbqOMA2u06aCIsNfu1eylX6e37/p+NsBmIPY1+TbTX2o6uiI

qho9BmuLVPQELL+pHPaPEZ3tpdfuj9mulFL4rmvml0qr8AmRYYgtFJz62qto+zA3pHH20UyIxbDeWyymajeljmN4HaeoJPkTfJ9ZmZTfyZtN/kSdazme4PuZm45gOjloWe+GvR+dp5mMP/EdeZ9JyKYOPlmjH8PLZry7YrfqYq8cjYzuzEmpHif1cc1ucYIn7rebZht5PWwT1dqp+/xsCcfo0T+E4A/PbHQIDmUcPS5vebT6brK7VutC6ff/jORt

gygTYDugqcoefpT7Y542hi31J6lyJSMkLwfoqr6jBmw6YOulKfrCn6U4IroOuFr1/HA1M1c5eBUzts6GO+U/N/S53xat+DOm348zxYnRqi/VB8cw4zssl8Pd/SftSi10lGsLOXeibo2dFTDk8ILcyNUzO8EYNTp4K9u6giQRrmffnu/AQO7C37LmU/qZ9znXrR2405j75hFwrDfqKfXSz0zX9TnmYeDGnv90g+oqyFGj5vz+w5/sNDhP7u9OZPMX

pvJS7iSiR9zDgNZM196onvh57+nemk6hff0ssP/TNkOyr9nIXwOZa3zm7VyEbBOnuBn6vZpOHgy3GBf52sUm9n4mZ/nl59Q4PyfaG3/je3f5sokX6CaN7Hy0/6tc+wr+w+eyT6CJX+5+lrfYzGIp/9PhVGiTPXCNGmTOH+AX1BzpOiZjGaEbioOvf3kCI3V6abCB0ybXQ4yy/T7eTjWnQLjTJg2cC52kv3WaWO1j+4WQV+Qpzjmyv3vs34X+sdgS

w0i+VS4SBB66zc1yg/XRQqOqUvq5f21+IEQqCYEVUoISDSeVFTFkhNx4kvuT/uLAOMa4TDzm1Bng4Y3THM8iFygvAJesXxiQkrgnksDaCjM1GWz+EgPg4ZgnLWEtjR2YgMDK+c0UByWmUBr8BIybAJnec3TUMrdkW6HBF0BkpySy3KHm6dyDuoJgLL+S+XoBoHEsBl9E68OxBjmOAKV+J5UcBxgJcBjHVr+11gsBhgIW61gO8BUDh7eTf0ABPEjG

+YAlNYyfgvgPvQ7+IeUiBE3xiBD7Uf+ns2f+9ggyYJ7iiBW3Qv+hXXGYlN2ZYiQNKgk30Hq8SEbemETOQG3WKByQMV60U0Kmb0AyBlQPG+1QPp+hszFWxswqBG92aB0QNaBaI19GjuU6BoIG6BOQJHS8alrGgwKyBSQN6BRq0gmggzW6mQKqBPQMKISPwmBiwJGBmbxq4ngKCB0knc6OIxx0/gJuIgQOcBOwLoC3HyriBgMOBVgOOBAbhR+qYjX+

mgMtY2gIKuRg1LGXE00BUgJgIBp0AoLwJcm/3X2M0gK+BDM3YGDA04GHLEkBxSABBcqCBBE5DOB8ay02/wM+BUIL1U7wIhBiINkBMVkJe/jl7aW1TniKvkGmeURGmHOmpe40yswlQH0AzgCMA+gA4A2QC2AVwigAmAGUA7ciMAkUCEAArxAsQr1QA613wwk4ihQHqD10RB13gU+ErQcWCP+FYDvcBgn+87eFfQOPSVeyNTCCqVEj+WryKOOr0W+u

NR36SCQqOa3yqOJr3uiYM26cnIkT0PBSaOh31hmUVTaOMVULaZ32LaVlgf60oi8U+33L0iyjxyWM3YQaPh2A9eirmYx2b04tWtMWjHpEVCmOUiMXmOILj0Kyx1jerMBogATWHa4P1HarMyh+rVT2OutS5Uuo32OnjFhB7ljfe1i1E+/yQCG27wM+GnyM+qYIMY+tQLBZNlCsyY3JUFl2a8MY2USrLUIqdFSrSAY21G3LXuue13s6QkxIGDxxaC0X

y2ItwLmBSandi+pheOto1YCBd0DOnEwEm4AWj+owKqspSBgwY4BDqYDzDqJQw5CIYQS6C4O9qS4L9qxb20Mpb1BUp9XGSflxaGIyWDgYyXKS59VqBcGHqBOJy5UB4PPBEyUfGhJ216J4O5ISSUPBx/yK67byySoyTfB94I4ybzw28NSV/BKSVgB7fwgBL4I90OST/Bjfy/soC0WYp4OAh9SWj6iv1HeQEKghIENsBpAOaenDGDqm4Mh824PoEegN

oQB2z2SNP0lukWQEBMySjuH9UgkP8CVOhq2cAQJWrmCpzohh+AYhIXwXepmTYhLYLOuD12YhzuVYhsIDrBpBmyuNEK4hQkJNqraleSLXhzmXnlIqlELzBBXnsSZYLUB8kKGKf7x+S2YPk+0LyIhNODXBVlR4+Q7yyKdAOMCcHw86E5VHygMncBaHzRcg1SdciRFBAvtS3e6o1iBff3iBLkOO2SgUBe4hxhGZ6jyBsE2Z+1jg3Kj4LZuzs0Z265Wi

KoPixOMUzGGh20MhAGGROmRHjgcUOChjah7BKUMihPnws+j2w22hkMZCGuxyhYKUMhDo12gGUIP0QEzeB4UMOCNLBKhfEDKhwJ3686REpO3Pyyhfq3fe3P3DMuF0HeB43Uu24WXGN4OVkKsTV+yFRuG2Y0aGD2wZc1KRw6sHQ/BrqS/BRvwOK50GRePPxH+gEPeuvn1HCCHRX6awzRsNfwchv8GaIM5SYhNANtUauVQhjk3u8mENRCW92nBnnj4B

OfyXuDfzN+5D0VO3EJSGzwy2G/9XrcF0AH+Sjwy6AWRqy30LW2NTz6ef0Kw0mAOD+LT1NsE/0gyOmliyQfz4a7MS1cSGS3+4fwVBisghe9gV9samVCwtWR+hNlAAh2MNt+L0MEhyp0TMhMMk6LCDkh/APUh5MK8hqDkoqZgIcaJEMH4FMP0CtALsBpkNZh9MJUCyc2S4JkOaemIKni2ILS+pLwy+Fh3z6lLzGmJ1QgAkYB4AHQGUA0mGqALQE3Ac

AHbk2pXR4rfSswC7nVAs0h2mm2XZBmlSVo4FiAIVLHTUO6h6+qAHuAV+BtY4tgeyCQC2UXrUfeBl19KyNWGQZTBcYecEdw701xwc32VBC3xKOS3zKOK301BcZUhmJSk4KBoMr8lNWr82bR2+LRzhmDrwRmTrw+iyM1del3zckHrzj4vHiZsIPy/6UOE2kVHibaEx2Zk3CBZgP31Y83bRAGStRH0cb1tKEiTB+yb1jBqbxaqw5TR0RYNUO5kMGqMx

SdOshzQmzPW/G1w3qhJP1kYQ43SmI4wp+6YJ3GZVh/W6KwmqhkNbe4E0I23RSAylAhgQwSBtkoe1i27UMusaAMqy5K0rOq730yPjE68tiy6h87xUYNslzC4URCu58JNO4Ehbm8ZF/Id8O9OXAOYBUUAxubF3F+U81KKcXFnmL8PW057wYo4SCveX8JdhNRUyBHug3Cr7F6he81gQX3i/0xkB6eh8J3e3p3YknsMQRvEAJenFSJeWfX6mYsP4q5Ly

y+UsJEq400wAn+UswlkkIAfYHCgRgBnAI1Fx4goHVAYumNAbIN3c72CjwmcFcona1lQEr0ywOiDBADEDsQgFAfBqWAt0zsIug8FgDad73Bi+R2cqkbWKO0bTVBy3214q3zDhRoL1BVvCjh/8g0R+32hmtrzza5oILaHRytBacIu+1zmgKN3zSqtCQyqBIFDWFyzBi9Ine+WtATwMbArh2hUjeqMTDBQP3msecGjBTcM7azVXZmBB1jGHkLOO4e0R

+fyz5mNYzw+ISKbGasxx+YsxhOAmjImHw13GqSLs8H42fBQh2pOylF/oalG8SYeyH2FkPYyfcIshhfw4BPx0pWhkIsyPDGkYp8KY2gUPnKqULs06727Mm7wV2U8PuSwSCYB/uU/h62yKhLSNtO7QRHmqwV/WGwSf0nLEXm8hn0+jZ3liqhhuIF7xARGqzF+5LikRWXlGQUCIMg1cAbOsxXmRGsT0MB83qKR8zZOpF32RTWnPm/XHveqyMkRdunRs

lyJ9k1T2p0OCKxBm1VFhO1XxBe1Rfyo01IRMsJcOM4EqizgAGAmAEx42AGcAa1Fx47cj7A7cgOAzgBmoVmGoS+sL2m22TngYxADuOwHR26aH5BJyDh27bBrIpcFumuXRe8T2WVe2xCBSf8LbavsIxqhRxcqm/RxqQHmos+NQNe+fi1BhvHDhMCUjhlrxTa1rwv6poPpq1/VO+zr2tBlzlRm0mCzh93zfSpcHJaXoO4AtcQhihM2z4aGyUgqkHcR/

CSrhixyX83iNMsVqAZm1lnVqPCgh+FhVbh+H2OOZBBTBfiWY+Y7wMhQyK/8ewN5mHbyUhhtUlGlqKAaTl2s+MkItRxSLwBoKjcSZiVrBv/lmutKjtRiFGRsfvzUGnqK7hY72OhoSKnBULWLihuBdRpEIS08aLhWSOwkC0SUMmp81fqRsw9ifEy+OM5UYhg4LJGS5WYmcEJC+8SIlaPENXB5EzbolE0SmVtTZarnwkcTUyhOkkJeSIDRs+ySLXYeU

xpaxNkK8KkMqmIIyo+0uBk+WkMy81PxKmw6OtRkUO3uNkKqKg1VnRZkODRE5QaG/gz5mq6Pwwsh3x+WJRnG40O0O6PxzeiE1Ch3SSqhhqGmBi8MVIo21reYJmn6aQI/+y8PxOf/0yqqlEVyD6OxSrkPABQHTfR55UmSe8Lr+zUOYQNXX7se0FgRyEIKYCzRAxACKuhac0o2EiMHeyTAN+lSOPmR8Luh4gKDKoGOLmdvwzY7Agwx1c28Y9SMzquGP

VO8MMj+RGLIQBAJwkdiAAxwjRjIlANbmY8VPRu7S2Ib8L6RaP3g+h6K7mPSL9yh9GvgQs2m+QwW6uoKnNRnEH4xo81BS88KGRlumWCoyIdOGkKzByKhzBSwT9IMmMExvaPU+/aKf8SmK8WKmNYCVYPNqzGMYB3GPpmumKs+dsg9RnEBYxPGP6R0yCFh1+T6md+Rz6hCOlK+1VlKxIJlhNIFwAj1UIAuPGh4S1DYAewGcAg1HpAxmGh4mPAbAHAH0

A0PDYRvUXqE9OAsocFG+geuneAtDz2gpuhyglsUSU4iJQx/3EX6WPjJ8CPgTis32pR6/V+yKoMDhyiODhqiNDhqCRjhiZTqOFr1P6Vrz0RNr3jhubXte/FgtBJiKFRZiJtBqMyJ4ViKdBMhUBAoz0+W8bHr0u8Fo84tQQIcuwVQqqODBuhWZyHZW1RB3HpEGxw1qcxyCRuxwzeHcKDEhbw4xSYJOO7GOu6CaIR+TSLfUrP3gCTYImiLW2vRHjikm

e4NxO/7zZscs3GBxJxXhO4LPQ5P1xO2WOwmxt3LmP2Jk2FY2QmUGL/+M/35+ZGPsh8jT8BIOKhCTMPYB/2NQROjghhCOIHek7z3ecxAPeApELOiON1YahHDyAJGk+O8MzO1JGzO4sCuWuCyexMpE6MrTlgxlOO0gLZ2/emeU6RfIwux1YybIkYOYWdOAF2c21ZxtkCg+K5xi4XMVuxiHy2gJK0QISCNm24H15xa+TDsTlxeg9aLnhLP2mBTunHW5

Dzd0QiMlxWDV5xke3G+h3lRusSPy4wuMw+fngv0FKGnQiSN+WPOOVxhHycWvHjmWhUKtm2uMAu14R8W5SDp+x+FJ8ccQKxCeE1xjuOVxnuIo+FPhbcPU2laIsJJeHyLJezmO+RRINy+ZkgqAmgGkwSQGNA0mG2AAwGiA5mD2AXh0wACACswzgHh4mgH0A0WJtabiANI+GE8IUmQiwUWFyuCeGw+CuAKYH2S9a0XClIiuEik+eGfci/TJRMWkOMRw

DT4fsNpRiiK36FWKjKIcMNelRzZRuiI5RHSm0R1oHZReCQO+MMwThZoKThJ3xThwoi6OvWIzhmPHFRlOBuujRChAHoPecxcMBAFpAyQKqPba1ChkSQA3Kq/301RgP2WxF9H8Rmx0NRs+mNRISNNRUzTU8nhUih7+Ph+ERRk8URXcsFYPmWUDS3UMDXJaqaM1GwkxcGWaxE+CmO0hMSSuxXYJvajqM0+7YMgJnYOgJlnykhHaPMxSYmdG7LEVwxVx

YqQzVBBhBPWhWoWHB8uDBBmNxXSMX0oJBBPuBGt0dq5D2dqvYPwJdwPzu8BGYJX3g/ILtUbBgI0wJnDQQh6EKQh4SK9RrxTvBGEI2B45FTq21kesO2IIYshIesr8SVGUSPLGWz1XqFAVUJaaLH++RHLqBdR+BEsyges4liCBBS0JraBiRoCxXqZhMnMFaIgcuhNMJFdVB6nYzKGIKAcJxuScJDLQBubjw0JNhOjEPUKYeu9UWsOLRp+pU2nGr4JE

JF4IJaa42R8P4MiJoiK1USJXyQ3RkXB+EOUokeSSJZ6XC03BIfqP3kBamRP+GF0L1MZiUXR/zBC+64MnSyRPIJgpnNmukyyuJVyi6OaJ7Rq+VMx1YIlUiN24GCwULBYZm8JEExMSimOUIrdC7GHdCIGQXjAJS4jsJRI16WIBJi8sDV0GvwLh0n+KCKS4m02VGIYmNbzUJQh1tRqEzwgkSI7Bxo0EJSSJtWswOoJQh1qhfuwahLKgKhRxIjCrYOaa

6xO1C0XVnhCI1+xVU1I+Jnn6hbGL/xhni8KDPw9w+6ICK/+OSKBJ2PR8RWAJYxPc8hvX8hbbyHW8mL+S8BKX+DthCCcF3zBGmIbGuSLBxA6SwJ7aPdRMYwxJWMKxJRw3rBokI/Rw3S/RznV4hbYLb+cQPAhZRJ7BMEKQ0oC2jR9kPyIjkMOh2RPvqrBLAq3JychM5UkJohIl+h9R5J7JMCJcdTwCgpysh50MH4xzwbCrgMlJIpxK6bkN84prmwB8

pO9RedhJCCRjDIATQKUYGLVJWO2IEqqGROR4jlJI7wVJoOnkYNuTVkjQm5JPjx5OzkOfUJmVehbuTg6DGVNSGy2RxYALJJ3HXIBZ0F9qBuhqIKpI/avP28hC5jYQUjBcCSBHdm5J2RJ4IObxVLH5q8MURJNzyfccZJ+oCZK9o4BIf+Qvlnq6RVsxJh3wREePFhRCMlhrmNjxOvghRM4B4A9ABScRgCswM4CgA1QBgA1QEIAmgB4AxmAXADQCswRe

JRR3kAaI26EPcBtnCkwOAtiV8FvA7xH2xYiP1BfMS1J6XTuQj0ydJpMMgSxWPm+cCXpReOEZRcbSqxo+NZR1R25REcKnxXKM2+PKOaObWMThHWOMRgqNTh6+JFRGcNYRA2M38nrw0MRWzE4BMwLhvXzT4ziN6+aSAeo6ogDBALiDBV+PVRN+OESWqO48eUG1ooP038jVRbhwSJh+ltTCRl2IEJQYxuJM7RBBeuVOJcP3HBrwMnBqFNlm/k3vYpUI

eJPn1YuWFKCmdQLsGA0JEUZw1tma6IeJTsw4QixPsKABPIiKZIIcTFKSKvxIW2PML0CHFKBJXFM46oQNghfFJ+JkUJZJwpPiwIlK/xxAOHeZ0Kc67x2+J0lOgxy+VGJpLXGJylLS4hyxJa0DUhJppLkpX2K4+2lNAJulPXqY4XdJqlJ0psXhSKYEPJJ62xmJZLSw0bMIspxlKsprFPrCqZOmJEJNcpR6KLGjFM8palJMpB6U+JzlNmJWZK9CIVIc

pK4PY0pFPBJAVO8pA8PjUc4P8pllLmJtkxtGVBLIJ9c1gJfyQUQvaXYJ33UJxcJPS8uVNdq4YzJ8jCU6Jhn3+8PJnOOGAzjiFVK/GPlx8eESSIJH/iDROxLMuenUpJH11bQ6e25Snv3ap+s0NWKsH+qVUHDsv41DGp2KYJnJN4JyIPtSqRN9qJPTDGFx3qpBuI3GXtQh8i1IQJyFI9s/JPbYnx2nKQCDPBIcA16+UOMJOATkJKhL6BdxJ3Q7JSCJ

4pLKaTxOKerSVwC8hN+xiUOIhE0NHGJhI8JBhNKBo4mepvhM8JfkNAmxvUXE1z3cppnmn+BJI2WMpMpKgjDgB6tzOaMZPcgBBFtJbJMkpBMJ4pP5NgqKEPkpdMJDJRGWoBRkJTmnMOwh99kJhxGX1+aqWIhrz2xp2GTUBl4Spywb3IySpNDwy0KphrkQO0KbhZpZ/zQERqB8eusFYkskK5pdaB5pwMOfUM5O3Qc5Ji+CGJppekNWaP8FnJy+HnJh

ELhxSUMlaLyOFhbyPDxeIMjxFLzLJ8pTy+ZbQ2m9AAoAM4Hbk2wGh4KsKPAHQHR4GgD6AKTm78SKJa+HIIG+nuzR24UAnQ3eErxDbTiAIz2sQIKGDgmWP1BF4W5p14TT4L7myUtSKkYfDAaRnugKOJWO+m2InKxDKNjau/WqxvlVnxX005RjWP3JKen0RrWLte55IZqXNCZqpiJvJGOVtBuACixD5NZq+OXtIqGlShMqNwsh+IVRu0h8eh7HdB5+

MDBl+Ipm1+K8Rd+PApxGigG+qNZwWx0h+r+PgpMaNsK+niSKcnlFGng2YpNngACy+0zB2VLk+46IjRwaN2JDqK6JA6KWaO9M6psqj0xoDUXpNdEDR0hLIIrUMSsy6PVJXKhC+9BI4J2aPaBuaOwpCxMjUT1JnBV/CSpVEONwM1MfqI8KxuraJmSG4M2py4K7R7xnnB+rDwhvtXSJaSJnhDENwh4DIIhmSKfBYUM9qYDNDqqDLZ+YNPmhqyQ2p2DP

gZnkNngKlF7IhSKnBWDK3BxDO96bNJ9JJVioZaRPd2iNLghzJNKRn9JzR+plHyfdhbskGJuSl9IvqxkLJpcENPpnaJFpaGI0BD71HRcBK3pncAohtMNlUiRSBJC9Oehi71DgOGLOxI/F5xC707s6jJZhNyPgxaf3t+GjKg6i0NmWNEN0ZujH0Z/10agtxU+KCajkB1MIehmfzlpMIWXwLfw2SQGN4ZY5xTGH0O4aYGJ4ZF9mP4+ZOJehZL1pxZKj

xhIKHc5ZKh4uTmkw2rT7A9IBScFABUq9L22AQgEF0YulmyfQERRFYCa+BsPYRQMRZ2ddDZ4VyC+AlKLfib1H/25DxTcs521EYoI6UN9PSO2SjW4V8AMaaZDVopQD7xCiLKxSiLTp6oIJqO5PURtWLNe9WNtehoJGZxoIXxZ5KXxF5LLploO6xldMzAqM3Mw2+O4AGGAhAE4BJyk2Oz4BKl5UsiP/JstXDeCtUHpytVH0M6F8gj+PWxgFJ2OhMUTB

sPyKRkaNvpHVIBJTzP4J9x0OJluMC8cVNSptF34WlULspXlN+ZzaLDReaj6JsnzE+PlPrGz5WkZ8JNkZb4WhJS8LEWXROqp0NL5+Z0EqpBYNRZEpLNJ99MGh2BIBO4Vwiy8gPQxJBnqJxBJ+sAXHaRANkkGbLXNCbKWkx9p1UxAhh1mVJJkgaFnq480DCJPV36BPVMvQMiJmuvLN8+7hhJx4QkeQq13W0GOiDQErJlIZZxDqMrNpsNEXaZd9EkGA

jLqMwNCgWKrKS+61VDxOtLCZD+QiZBtNfyNhzXivh3WA1QHoA6oAoA2wFIAAmBmoCAHiAmAE3ACADN8SQHhRPZI5B+rE92GSGI+/NXxmVwD9p2gitQjWxS2eRzvcXjKCZj0wox9dnRqidNXJP01TpG5PTpGoKGZNWMaOmiIaxu3yaxBdJaxtNT5RV/Ude70TXxd/XTh1zn5eddJMK+OWeuzuTWkwtQ7An5KPxVbQKgEIDz4c2KApniNDBQ9POZeU

DqqY9NxizcMnpcFPuZCFMUZvkIOxZqLHZk1KeOx9LTBRlNCpS4j6p3ySKpkLMPpLzP7eKBO6JU7KPpDENEZuBKGqU1IbRxJIaJChOeYznwpZYhMjRVaIFClsxqWN+2xUHEJWB7VmjRT9IKpL9Ii6b9L8mJaKHhHDNfp+pkmJ+b09qcaLlR11PimdaNHB7QxTRjxM4ZSDIg5wHNDCMRNKCZphopeGC+poKgzRaDNBJnHwWY0aIvR4NJ/Z77K4ZHs3

o8YAjhBsqg4h39DIZBSI9qROg4hLJwCCFFXqyUOLgybaP+OZmLxJ7DIfefaOUhmmMFOgTOXs69P6JCJMEZpNKwhcEOFwQLKzJWCBE510LnRlwQ4yuFQVpDxNcZb2XcZjxzvpHGXkZuf0nhLOOmBnNIkZCkMrOdOPEZ6gIM5bCwBxgzxJZkjPMuQ0Ku0I0NUhNMK05ulGQ6uvzQ6sOOnetNMd+rnWC6hB10hqnLpJLaNlpJAJk5RRJfQYfwCZu9j4

ZQqXaBYXL2hTHOl+8f3DCbfzdJN4huh1EKfRlHNfRRt2lSbmlw5+DLKmaXIw5vlLBJ+XNxabmlqJmf06hWXOVSNaOGJVEzSMBXL+Og8OAokd1K51PXypmFLcmrXOeZGKiJgO0Ji+2xKGpfXIlU5A3gmwXENWvHWt+knRHR6FJdGJBjMZ6xQsGM3NR+OvxN+rnMUG/zNwp5FDsgIHRgqhhPzRZGPHeE4O+Ox8yM563KO5zOKtxEqk8mJgwUp6nL25

h1IeJh3Jwpx3NBU4nJ+ZWZOm56VOW5e9MM+B9KdGS3KgmrqKapYjLNcyoxIGY3OEh5LLapuwLXZ3QSPZ57K3ZsPIvyRhxS+73H1ZfFSGmpZONZbmONp6AHwACsPwA1QEqA0PCEAa1D2A2ADWma1C/yfYBpAcqmcAHrKNhO2QegCWN7ia1nlQQ/RdIAdJDZYhhDpVvAVerf1lBGR09JH00xqX02xqgHiTZAzOZRsZTTZe30nx+oKPJuoOaxvKMXx/

KMLZohRLZ5iM78uADWZ6lhnQgpCcRdbKthvr3GOw4AigF7jGxPdIApfdIjeIYMWxYFPOZwXT1RSbyfxA7KNRQ7O2x47Kmad3KvpI5V95q7J65g1QG5psxnZZbx05EqkXZUjKJxMPMG5P3NLBPHNOBdxx4mEPJY5bqMsuEwX9GtAxT5NyTpZiVxhBSfPB5ylCvZDsUT5+xLFw2fJ8S9JMz5o3KL5pyVBZu0MR5sfKfZRaPPpFLV/ZUiiAJsqmZJj7

IHBX9JIJGFMypvfOg5B1K8mzfL75CVNnBRFO7BAXIv4BFJ/Ga4KaZnJlA53YwVxsVlZZfLMq5wrSFZfVyLRkPJBOSjnK5qfKapRLMROoROHRp9JP5mJ0qJ/MGeJnDBLBaJP5UG6NQ5NLVO5gOLbGJ6PP8RuNwZn4ICCwmNXst6OI5dlR1Gfs2fR5DOo5uPx95IQOS520M0Zi1V/RazX3h3ONyhQyO4ZEXJ8Z4yNZGVJwjZ/HO/RWAo5honOoxatP

c5inLexj6OM5akMc5NXDxO76OJhajKsZiO2QFYlKMZ2GOsZEAtQmFkOYFXdhMZZFNT+abEsZujDXBf/NlSfAvT+AgvExSuIcyIguMZrArv51Ap/RmGO4ELArXBqxO5+OjNEF3ApsxWtLsxqX11pBrKcxRrJ+RJrPGmB8SMAm4CSAxmHGowWIaA7cj2A0PGqAuTkpAI2U5qeTInk6lUFejPN4IYTEpQbbAG+6XEthrvhzgsByEg6qEnJ4ImnJf6Ou

sC5KT+d+A4WXTJXJ/sLXJEvOA8lWNqULKOGZ6bIPJCvLzpx5OV5p5OLpszNLpOHk6OmvI3x1zhGAFbJ5qX4EYI/vxlB1Hm98X5Jhwk6hp8bbP7pwFNOZtcIjB+fHWOfbPb4z+PHa6b2op/vO3p7AsGqqnjKpq1LghQgpG5UBJQpBjCEFL7I65o7MtR39NPYU/ISKk7JA5WJhipVIy6RRnVoJ7I12F71LAiSUOf57gUOF5FKvBlFIOFO7QXhQOO3I

mS0/5NwpQFcNPYpS6JGF/4PpphJNnpywtMpW0JCwMBy5OdpN5JZSLshYXBHe+NLYFgfI4yQXJgx4LLHRCn1/2vnJkFJ3M0hMjIRFcjIDKTNPFp2ONRJ9iWxZtAvEhZMJP4F/Iz5BIudJRIsmhufNkCi5IPwEkIpJ1aNUZhIuGpOoRi5eGNd+tcxa5ZEMT+gMI5FVf1L+OMMbM5bnxhKY2OpR5G5F7IqFFEtNQeF1OUJAITTYTIvcJ+hJ2exnKxFE

dIhp7dVCCMIpUpGrhRpXgRxZ+lK5ilNOJpm0N7eSNIJpq0IZppJJm6rJ3y45/1mhAUMVJn6PK6/1LSGrNKdF2LyOFA6k+pLWztFkDJDUbou9JHooJ+QrO2FdtiNF8njPZVYkxhfPyppHE2e5Cu3DFd2OGaiwrDF9NNjFkQ0QJnzIp+iYveZMwuwRIeMz6YePR5C8Tz6MpWx5MTIqApwCEA0PGkwzgA6AMAAGAYukqAuAHiACAF2EykGkwxmHRmLt

M76rX1k2sjGfWViFFweulxAl8Bl2Msm0EYbQsqZWCkWWlAwoAbW1kPcwEImeCVB/eN6Zg+P6ZKiNSFMvKzpE+PYKudKzZ+dLnxhdLzZqvILZycKLZEyh6xt5Ouc2AF153PDUiKBCnFb5L9ejBh2ZSOBugen2lqF+LgGaqI7Z9vK7Zcby10atRd51zL7p8YLbheRSGFAuG957wtk57E1/x6nPglK+m2pHzNmFQmI2FMwIEGKYrD5l3KTFpBMYJjwr

wluYowJ6EuxUlP2mB/qN5GxEpPZZBAolEfLXpYHy1x0wLBUOhKYlfuKu5ai3EFejl5xFpix+EU30hX/JC6CMAomnFCiC9EujEHRPYlEgv8Jx4ILePwpVIpRPWFCkrDQq6PKB8kvEJq5nf5xXO+FmkpOsiLI5+fM0CCqQMAF96K2JuSNAFalFTIRkuF+e3R1GmEtTQdHJBF5phNFYQJuxc7MipHXWgF8AKypgnPhZE5A451nIJZbHOG5gUq6pDIoX

yZ9lq6C8CZul0L3E2Apg2SuUg5qaASlMUvdSC1IgZkUp3sEGIeFSaWEJZSSkJWUvma0UtylUMJlFe9Sm6qUtKlqDyBpf1KKl4GJKlo2xeFc9VTwVUtG2bMPQkbUoDFM3SDJE5C6lfNO8ltrnilUUuAx1Uvvsr/z3EYUufUYXFWA51A9I06C7yEQuY54mTFuMSw4QcHNTQU0rtslpPb01pNFBdAURp4QPjcmIvDpc6im6h0pa23vzvw8vxqYQlMYy

IWQj+qWS8lt/3ulNlGjZHSPQkF0rkEzjER891HlWz4svEd0okat619Ie0HPQGhHd0n0qBlCdlvWLp2Xkbp1ZgUMu8lzfwuBdXD9OmFiRlL0uBlGQMORxpDMSkOKl+TWRDyd7zTMBMvQB93UREGXlhuy6E6lI0t4ZY0oFY/8QcI6OwXwlUrplU9gZl4kiZlLMj7gVCDZlQjNIBlfxl6nE0Tyw0oFlRgSFl8fVLOW1nLOg3QqR0sVyUcrO9q6Ek05/

3TpsmrIuKpMtVlOvQ1ZyrM1l6Ek4Flv224etjSWdZwO4WeQnIhsoz+xsvNIiCyu4MEmiFflDqEtZ0tI5spfEyOJ1ln6A1lDET3EHstt60sth2IdXQkfstF6/zNFldARDlIeW5lgCVZlwcpIxGMMIiVpE5sX3iYChjHjlEDXg44pAgIdCCgwBssdl1Gl64DyOokpMqtlDv0wiuMs4k+MtLlkMMKBmsSORiBBVllnNM5tcrDy4CQJxJ+SIhRfx4kHL

PRlvk1al+AollGKR7lGFj7lfUvZlGSgxScMvwUE4ERlk0qWl8XNA4U8qQik60xlZlJhlaZI5YreKTJB0psp9DMXlRSHjJj4kzJZAwo5+SPXwBQLxcTePTJR8rbxBXVBpV/wvlArCvlm8sTJH3LUlTP33l2TGvlW8o+5SkvhBB8u/lr8qXE1tw3lLeKAVskuJuoCozJt8q8JLaIMpXgmflYCuPlzhOX5IxNRlvpxHlMYz4l4UwSRZPWHlekAxlyhE

sJjQLxxbco6493LMWUorxctRXrlN0oBY+VLeOWmxJlGowxWFMvG0VMrygNMpj5IfNvW0cpZlfMtb5eOhFl3+M9lbTKTc0C2rKJ2MvZNst24dsrdlqErzFnQnTyrZ0FI37hIlBxLIlq+RDI+6lwc45nRJYPI0VHtjQWk6EeAs6CM8nCAUVpEqMVQ5y3ELkVsYlisMVdQnZxCRitIpeQcVgYyMVJxWnOrTkXgfBIzFO1LqETsUxABKlh2HGQMVHirq

E/OMPIMH1kC4SubBVeWcoAuIUQsSoL5jirWqz3F1Z9mI6yRZP0FxCMNpx1Vx5LGAQAg1GYA6PBIAAwEti1QH2Aa1A7JxrXMwrIJ7FIR3ew7AgaI8sGNwZyzT4UWDQWhBCiu2cH/gCbFumrkrv+YIijpsqM0uqGi+WG9i2U3TLF5dKKSFm5IzpqbN3FkzIzZ4zOjhGQpzZKvJmZavIvFGvIL0N4s78WbQJw3NTu+lOGOFjUG7p+cL9e9YHfFE/nKE

BSJaFtvIWxvbX7aplgaao9NAlBqLd5L+I95gwtolsEqhF3XNJ0eLO30Twsih2m3kmjGMMh13PpGGArPKH7zlmv9IMZk7yGJZQzq52JJ25dnKAZ+wpW5qHQW5rxKHRmFTVZNGzGhdFP859fNlpRHI3sUJBcZLDL5FXzVcBfHNbsHjISCCnL85vTy7+LD3+hLvzqRcdMIx6hPH+EGRVcP1goBwbAG66/2RhgjVRh/QUZZM3wlVAjUuaC8zJSCNg4IL

Ww6l8xnS83smokTyNTFhNN5hR2hny9HklY+yDEau8qDFQiqRYr7z5pNJPZpRZBdlSC0hg3UrK65qtsg2ipVouiuwW1xN2a0MufsjCw5x2xTbII4Qul5JThg3Cz5WvC1jsWMphloFFnFdlW0okarXlvqppQB+RAIR+WCwCar+F39g/OuuMD8+uK9VFP2DVgUEI+MZ1/CWjxv+iaoHCkF158oSzVgofILVPqsrVfyBSWOWHSWKOFNVyMvv+1sI6Q+y

BqwJRBe5toobVWavSgw8Uk+4hmecTqpgcy0PaWTMDWUytD0+E6qxey0PP2HsH/gipEriOqoppnwqUcqr3C+usEi+8qouai/yFgyy1ZgytFMI6aoFVEeCFV0IMEu5KHXw80Cqu2jyAeZJTqgf3jvVIl2XwfcQKJ7aW2WMwT2W4m1BOVXLKCQsEkuJsGwW6sBBYsUuKJfVjuWC8A/wvUAJgoCxC+WBxg28GuDer2NOuEUuiiSl3lQKl0/QI1zm500K

WhF6CIOylwSwy6E5lLRNV+tnO0cbywNIEytvoUyrIxRBw+WnD2uMd7KoF5nNP44ys+WjGtn6eci0FBZIcx6X1yVWPMMFOPLjxumBnAVmBmomPEt82AFx4NIGx4ggC2AjL3MFesJcFPima+vYo5B11GF2B8CygF93VgQ/XKwvhBw+UJDnqYQvj0oZycECQCjZvXToxIbF7x8QrXFAcL6ZkvK3FCziWVxNT3FOdMPJ2QqV5myryFhiOXxnWKvJxbP2

VVdNRm20wdBqVUGxpZWUsiiE6QhvJe+VOGyqRcPbpw2MgYg8EoUmhQ2xrQv/FLyqWx3HhCoupJekPQtMK3yv6F0P2HZM9Pw+wfNshSB2r5iise5CwsH5iFI1MFUM25ISIpUc/O/Z1x2v4K1PpQmICOaiKrWFjzK8GdVOG15pn/Z6szspWfJoZYrQJGuCskmIswlUJFJhZAPJGakkvShZCzkW5ix6JM/NCuHaI7UsCopVdRP35O2qO11RKu152p2h

8XU35If1fpTqQ9y12qNuH1OMWvz1u11kxAZcY0uF24zO1P2oexBDHfl1Yke1ZUqyR7YxVI4OpqlWMF+pyosO1d2svVjhLqlF9JDFjrheFdzz5a6/NupWNL1VULxQVWwsdcFMPv+2CtVmlaOtVdDN3E2OuW1FOvLVmatJ15xMVp+0PtJV4AoVN3MTMYIrOhNiHZ1sKs51slMQCPOtNGBEpa2WoowYHo2wl7WumlA8rIEH3OmFVitLMncqSOjfOBVW

OzDpYtKPwc1NB06uqvCrHCBVNuxa2OuqpyHNJ75iZiN1KbmWhL7MYVz6nN1mupH5FlGFF2upOlGur11aaSuG8s0gBotN11U6tfGc2rN1zuu91lYREltaLElnuowwp0qXVvRIQBJMNpFdmr9FHQJsyLENj1c41a5LTVohyeunhPaTT1TIuQ5ZQI/lTuq88qotd1hXOhZYetvALuuWhF6Ov+Beq91xupvRJkupV3s0bs4stl11lJtVVGQXsbgNHeDJ

OxlNlEBFGNPlWPevXlA0qjVSav/aHap9Fu8up1sXMJlB8OfUJOuwEW0vvsmOo5p/UsNycOqVFa9XC5OUvGedwvHGvHIi5lGvHIBUyuFjHNn19fzRgH2vkKhRCX1ScUFu4+tH1Pkohu3hK9JlGXDsCrJCB7evf1N2tBxBJKOlfJipFb/zvRTesyul2pAmD5XyBF2sahefIYpOkq25rRN0Qp2vreeepnKojKQNl4M+Gx2us+6BtP5f2KwNdshwNSVz

klQUpxJBBs1k1xTgV+eQQNJshq5rhLDkjVNeShBu1mtOvsJZLLANE/IpGoC0X579PoWVCvZcxKrwJW2ut1WFE5ukQ1YVAjiv1qJ311nexGG2JwYliaM7+6DKvUg1NV1iou2eW+tB5qSoiVOovZ8kNKx1/3K+5z9Lx1FoqBewuoH5hEsTMhavmJRhM71+pN51ZYxWlJAkFlKxKXaALKABSurTMMKocNljXlF5IrMSXhrcNjpPzl7uQCN3Wvy4upzC

UkKDlQ9hsCNdtnAk5p0+A0EhiNYRpq4omL0EyRv7VNXGnmcXB7xGRr+BZsldOM8pQihYi61mRoQVBRvhlRRq3CZhoypFhu7lahkIkmCuG5cStIGBwLRlTRpUNjWraNGCoIVo8p/xZXEyBOXnblN7KB2JCt+IZCucExxPuxY8xs1EeTd1TXIw1Wm1mNwxs3K5OtYN8wNblYZ0mNtxNQVbhImBQxvIV8epi6CQMGN+OMONE6Oy50sWWN5xowN6SLGN

6XgmNceuQNyzHz1SxtONjxssIsBqw5uYmuN2xsBxBkur1bxs2NtmtwiAAsb1dRuZY+Cq5ZeJIX18ETVQlRuQi1RpIZJhv/1T8t/hqElyNVoudVcV0EBIyKZZcHS/1OJtA4i4sxxygl+FpotRN4RsDYCRrhg5BqS5j+pRlYEnXeepyiN5aDP15Moya6cvEE7JsQFNTVxhbv0ZVh+tG2NItdyTxrLs48sSlzXUL1EepQyEprSlVuXVpTAgP1O+s/+/

MM5hknLX1XrgF1fuCF12+salzOtZJB0N5OgppVNI+orVQ6vFN2Uv1NlOqdF0+uwBTKvlNrYU+F9/zJlvJuMN//1pO2Ai+lOhpzJjtn0N9JvNNlJsUJP1M315hO7ehJs2eG+vUNYZvxJ6LKDNMhL31UOvvSYJtn6Zko5VShsPo9oofogJqEJcQxkoJev7GfgxWYtxrjCRZvBwHUzwNmUxih2UzaB77OaJx+tgwnxI+xZPyj+0UOvBQepcJ7dD2NSU

2rNHg0x+OCrp1f2qbN8xrGBa1IbNbZtP1cYvzSkGqrN7ZvwlI4NkNvZuWBmxKHNchukN0+0XNc5oBVPCu1ZGSsLFerOE1BCMx5ZYvE1FYokAU7jWo9WCSANfRaAVmB4Ag1Fbkg1B4A+gA6A7clx4qlU013UR01jPNTQAkBsuDhBCwV8ElYSWNSIbiHQ0ny0Dpgyro5RBSf5y5LjZCQoTZ7muSFw+O3JaQtl52bP3F/msPFOQqC1JoLPFx3zC1q+K

vFSzKmknfjuEsWpOVNiPu+5SHDsPRRbp3PDbpeVWhi9aG7iTrSt5RzN++A9M7ZZzNpwf8FMMzvMbhrvMCRtzIQGfyq957cIvZ27L2J4Hx5Gt3PeFMSXENA2sgFaVNmBwhvj2bzLzRD3KUt8lpHNVVkWNkItV1tBq7N9Bu0tgKuxVJby+JyltrNp42cllb1wmAyPBO/KkP5pAuo2FZreJp6wCJYi1+BzZvP4jl0SpogwoNSOsyuebwMmewosthJlE

lSFiMtiKARuVfNWNIVotxd+vH5/ZrWNUxIDiw/N0tnBqmGHk1cNKRvHN1/OS4oalKNfJPPGz9xUt0xrrG/YwUtjlt0J/4xhJ1VtvZGOpTNJHMAJESJ9NWajvRIivdNlksCSnRvnRWO2gt3Cq6NNpu9Jdpo2JZfPiVjotGtqcvl1aSuR5yX0yVOguLFu1VLFLmPLFRtMk16AE0ALQFCA1QHbkpADswKTjF0AwHwAuPE0A8PGUAS1AcFQR0aV7gp+q

fwlk2jMnLgxlAVIfxkdKu2VQoLNioQdYBG+3Tn4i7XmJYNC0vsOWOVew/RaYvUGbZ+iRQqciIjasyoHx65OQt+rxHxaFuWVGyswtWQuwtgWuPFubLr8BQoFRRFrz0JFu+iGcMIA94tUo2rAG+KWvfJ3PGe+TFo8w6r2MokirKAeWpuZTyp7aN+VeVJWqrQDygq1MFMHZW2LEtDzNx+k2plG02rQGQ2qUQWlImtvE00N0tqQJhnKEN0k2sN+3L210

5WuadLPzVTnMjFDamCSu/LYNjUItlCXUv1xwu9FH+rDQJ+sTGZttHQDFKP1vXgENE5CcpNBIstq8szVSGritZri51jnXgVjU3O1HcsVNJAqi5dZodlPIslFX6uCmS5pIkeJrlV2jyK5DYxUIdcrxl0YsBepOuxIIJE2IBpokp3PxWADOKaE7Zxso8sqOaTJSbu/JUog2er8NRzU0ocavm8TJoC4LJuXwbJsGJ+3mw+R3jEI/3TSNQZEGJAePjin7

BPKvxrFN3pgIuYETSIwSG5QyZyiIqZ2OAkkpPVq5AWg2uko2UrIEk0Opw1fcHI1Pm2dlJssmKiTUklWK1suhJDxWoCzQW8qzL2FyqOg/hMiuVLEsQ/K1eAqBqA+gNpA+wNsfQOqxwgoIEquA+2PYt9rLI99s/8YNvKuL9qhtmtILFuCKLFh5pyVx5rWtp5o2tOviWokgB4AUAHVA9ABeAHQHoANIFIAg1EGomABEA+AEqA6oGcODPPut0WEcWEfg

voibk8I+0sqZ0WG2W4eCiu1CDags4Vum29wDa2RoxNFsKpR8Ftc1iQoByKQq81KNp81KysyFWiMV5uCT4K8+IMR7WMKF5dMWZJQoOVuYGfAFQtOVWtAFIpUDotdQobZmWs9ADhE/Y3JEeVJzO4tHQpIihoiuZXyuEtEEpNRyEv7h4ltltMlulc/Ru0JVjudRB7KJ0EKtvmDWpkNS7N3WWuqJ0iuwsdtjr6225uGtGko0taBMGRpHLwpWEuTFUutY

mg2qm1WAxWFhFLqh0xIW1tuyZ1CTpr5tu1m1iVsexitpi+6TpxF8Ytze2PxDClhPydAkr8telv9ZmwuipL40ANcUyJ1VtoqdHBlDFPLJupWoRh1UtkoN+E3u892srwQw1v5bTvr5gN1JVm6Kdt2hhy5iZr8p5Kp+1ozoMleHImdwDJNuzVqAFXTrRZoZOGdn2IRpU+ptFLLPttQysZJdTrt288qJl4UuvZepuAx6AqOdJfPFNLeu1FoBugNjMOIF

7KqpS1TvIFDnNpZ8POh5tAv4FGgqJJIkOPZPKsFFMQsKdL2PKdP4i5NhZFKdnBrFSG7xpZ4LoCmNGIgIjmvFVqtokGCsV6RVmP0+eToZZymPxNq2teOStqHmUdoExkuKuxY3K0xgwTExKTuT5i2r5ShmO4BH8KJdiTuwED8IRdvhG4mhfPd2TLrFVLLvSVSklR5lNHeR4TNE1J5pjxkDqh4kKIRRLCPiA+gEQdfQAaAmPGkwQgCswdmHiAdvjYAe

DtCOfwjAOU1x7xrTmEgztjOmrvjbwkPnhqkYLT44oOpNPkQtOdJsF5LTKXlCMr+Iq4p6Zbmo3FHmq4dMZRQSqNrl56NoEdAWqEd1NTjhp4u2V54pXxl4sJtUjqi1GcPwAZNsvoWBFH8RvL8FVytN5vXzoYsj20df33aF4A1pwXyBYd5Ws+V49L6F8AwGFfvP+V/itSdRVo25ZRtBV0tpJd8xuB5Q5BxdI4KipDTo9OGLrCtu4OVifWvlmgaSv1yU

P1tRFRdFuQz2do4UmQtuUvWIPm4NgpLohQIpFJ9IuOdlprxp3tpqds7tAOSIqc+2ztt1Z0sHdIpqVOj8q1t2zswBO7q2d2/LXetdsiNy+E68g7viNFrsSNlp1WdLZoViS4pwIajkRupLpWCsmJsZ/TqS0rgkT8+xBQefTsmdSWgQiCJvdOSzsBSXeJ/dT7pf1mLu0x2LtvdA9AC0JJtgQy4t/d2bEg9IqrNOV7tpNM5WfdcDQ/wddpfWvv3/dgfz

UYB7pqm9+rZF/Jt5FIXL1wK9y3dJXCPurU0Zpp0t5pQGvqmrAP9tDzrKmE5oB1wnLVNBAtnNk5vgFk7oH1JVt3RCSAf1biGigG3AXdzxpMQxZupJVOs2dCZu0l6JKcll6rqtIjFyytkv7+anp3+mnsdt0pN1FA9WRNHpt4p7psxJLpv09wdg2djlK3VGaopN0TVs9fepJCmdrZ1v+vRZGy371RpsH1WJrslthtxZoEL2kw7rVko7tVNThuuhelK9

t1XRl1y+Q0pXMItJHhsY9LuuY9Nev05gTUZF5IpI9KAlVlX0Mo9ieoEhGerRhYXjegmXvS9S5MhdeHusBfJv+dZWW6RCgkQ9j7oel6MPC8L7p0xjXqK98WVA9BxnA9PXSpZP4WC4Sqq/dM82Q9VJu4MNJqSNnXu/d5SGG9wgkvdkEmvddJpkg7duZZG4lm98kEw9LXpg981p1Z+5qyV21QFdYDujx0TJFdFQDQg+tHWA6oGUAm4AfNmwE0AAmGeq

PACMAHQGYAuTndet1sNh+Ds2lNKwaa1QuUyfCIoda622RAqHAophFumZ1MemC+oddcNvXFCNoWVKbJ4dB/V81gVQ4KWFohmiPppquNp2Vwbr2V6OWWZGcMLxcjqotlOE3sf8CZt1HlJ9jbKpw9HkjBPj1TdXFoAlPFtZg0CAftjM0EtYEt/FfOQFtRbu8dEBMzF0x259/M159rVocdOUMF97ismtMBMl1dCtCNFbv75tRuLR7uv0tuC2Ktjbu5MM

Lridc10bNchrV98/Nz1LxtedPztSkULMLNvbvrUFsqr1JXtWNicgtl9tguWpkpANRvyh5OtpWhJntn+rVKd9Nvvf+9vsedbzqd95vqgNVxPPSynqqdPvrN9YzuK5ITLwRIDv29BIKsO0sMKVUAD7AbwDYAfQDdA28XWAHAHiAxoF0gHABeApAABRarsp4PPDKYkFHSIaZFQKYRzuAjyx9iaPhNdt0wkOINrdhcgoROMNs+mSPvF5nDpQt24vddvD

rRtfmoxtqPr4duFumZ+Qsx9hFpDdrfmvF4buucY8gott30J9x+J6A51C3EOVVuV9CW9oZClp9bQt0dGbsZ9iREMdebqq1Bbpq1nvKFtoTpcdG5rU5LzJYVNVsv9Q1OtGXPxf2pxxeITfodJEfuAd2Suj9XyKiZyrQk1Ovkx4g1DgAS1BnAcAHMw2pRnA6wDgA6oHpAlQE3AHQD7A1QH0Ar3s/N5pTut6roIdLCHs8dyHiweChgs81wdIjMm3kZMH

l+Vmq54OTqIKQ3nsgYavhY5D0h9bfrmVHfqRtqFp3FPfs9dffu9dmNt9d6PsEKRiPmZXWOvJYbtx91zlVdBPudBX4EmQA3mCK9FpuVGWrptgIGTgSBAfIm/sK1HNuK1o+gfISJpzdrPqMd+WpMdb+KMlkfJ4F+fLYlWxJUFGSLO5GDmIdvTowlT/s6130GfYlgYYh9fth6F7H0g1EHFg26DMdWszJ1CVsElvx2ElnZpit3EqZ20OuY4A1jeaLLSX

ZqlrxdbfPi4BTDzCP6HXZ3lsBarU0SDRhIyJBVuPG7ViKd+RIyD9ZpLoQLs/8/PI41p7JYN7o0y6WcEPsf/TghZAf0l7NIP2RCwrEkPJ8Dx3Qb1qZq99a/NKDb4xVI5DA4IZNmxmJlsPZA5ukG5QYTwkFCPsvjSaDBTvSDe6SyJcPKGDZQd+6K7H0SphHoieXM4Y2Qex16IxD1aCqyDBQZeB9gaSIVgfCsewbFGilsrBJweLdzgY7dFdHnNcvtdR

o5qUcZ1NSD+aIbqzBmAY7KCopJRvLdh4y49Aw2eDatvANKOsX9/weRdbnpWdnHO+DQTVaIwXoGgAQWl9gGOi9mlJBDvA0S9uuuS9jjtytC3uEFIdoBdyIfeGMWVCyxHtYCVuuiDrSNG9GHugk69OmN97sxxtaTkxUQboJS3uJDfYMVQGXC/lL8uPlQQZKWFrHhN08ut0pduklQO1XmPRoqYXIbBWAxuBNECTFDhKwOR+80TtkQepDcCOwiFhCpDa

2ryEyocQIu5p5di1rR5Ufr0FB3u/9hfTPN6AE8OAEDF02AFvNUeDYAptOh4M4EGoM1BpAfQHLab3sKZfwkC0vdnCITMnrow5P8wmrv5q5cED618EGVnnvtJESlGVmWF91JwLiFbDsddHDr1eTKORtzAYR9g/q9dmbIH9vfr9dIjqLpIWrmZRQorpAgdItuYDgAZNoUQNDQTeCbuhwtDS9BKhVtS20G/FvdPZ97bLt5RWod5mbvFw3Qtzd/bOMdU9

Nq1Njp59O1MEViQxbd/PrQNWIb7DzBpD9pCHHDIX3HDCUJNtn2r7NKuv8dq5ojtQ1v6tnQ1ODEmJCd31KD91/v3K5wPX1ehOjNk5icdGGWdN/hsxDCu0Gtytq0tVnvb1Y1oNMY2vid9OtNFn/mSdL4ab+n/hydGdqndbFpp1/EpW1TnqFJv4azt34e5dBch1DfLt0FGPJj92Xzj9m1ogA8QE3AmADYAuPHiA5mEkAMAGMwnIGYA2wD6ASQDWocTJ

bFBfteEStxrawkEPIuDj1dV1CGeezLgwm3WOxJAe4AuXPbxyr1B1tAYV47fvjDW5K79TBXW+2dKR9B4vTDrAczDJ4ox9QbrH92PoLKqMyWoZNv9ITUFBiMgb9epwFX9qAB9iKBBlBhzOEtbNurh0bwZ9JEQkyHOU7DvQsP9WtTuZJ/pHZkTu3Zg4dmtHisHDJIZi+BgexJCvuBdtkY5QtfJudfbpLdlLrrVu7qPdYvuuxQ3PXNp+2ZFxN2CjpI03

NAnv59FttimAfNUN70MZ+L4lN1EOozNcdra1EJp3DkOuUNXwfO5lVufG6toAjg5pqe0zuT6raFRVCU0jNEBoAmECug5tVvZ+i4hCJk6Mqj6nsvRjUfct4EeUUkEeLk0EZLFmXzE1wroKVCEb8O9ICJ5ygH0ADQD6AzciMASYDWofQEkAbABnAkWJIjfwkxAxKEMoVukIkuAcSAbuT7w2EFKIt00/eGeUF4hWHDDKNRjkadvhIHEfT89Ae4jiyvh9

/EcR9abTTDX0wEjXAaO++bV4D4WuItBYeJt1zg+qs/usRogZ3xCUUSgdbWptTJ2rDdHmhDFZH+gSgebDKgdbDjPqogHYa0DB/u7Dvyq59p/vw+rWzMdE5QcjrASEF74eUlekqX5q4NxjC6PKm3LOsDJMeTNrQdX+jgcwlsZvBDxMcCd8nttNinonZKkondDWTdNATqstNAKudSIbeFZluedzjOFjhloFFBRSvWFxMK9fmRrl6lv5j5GIc1nLufhp

loljnGLq9CxDpDjzMVjneK69U3ol2fgZ/hshhVVuXGhOn0ChNjDxct1m3dhcocrlpixRDGqsCIF80xsXlrSD+JG5YUdkfm2vqcgwLpFZ1RDFZ2UMpFhUeGDBqtFZLEiDjABpDjCweZQ50ZZIXhAit2weeg/hljk8JCCjSOlTjCcao926RTjF0azjLHqrer82h0oJHpV7aVTt8cYt9Nswwm0rnLjSQkrj/xvvlc0JaKccbrjZ4dIZZ8rFMucYrjbc

ZAuHcfywxOIDjEcZ7CVhqGQ980GYeQZ8BPMbr+nsk1VixkvmneodNzPogRFcpwiqpskyGjU7ySobqKmofztYbkPCEzR6AuOPGNWxopF99n0arXQO87XQtjDRvQsjpDLtZXp5D8KRmRVXqljB2s4gTDqT803o3EV0qZCsQpExBLvJd8TVBdWAOpd+73q9nVja9cscEYHLt4MXLqAThIaellLNrshALWJ8CcelzXtljyjXljFP3elNLJy9odp69yCc

oxqgtLlXzriNbSL698goxFTjIUBNdqITMbOppbjORFOCYoTKCdUFntp1NIKtYaj8ObiEXs4TWOxgT/XV7iPJv/Rb0uVjsCf3qAZtdt30owIqLuMxr+pF+HMdq9eDFpdQYbBDDMJkTXGNUT0II99wBoyjLCdFVEiZ0cVKraD+iZG9tGM5dkieDJJho2WgifoxYHWs9hCfFSDCZ892nroTziY+l5Js/DTiahdVCZOhKEPNJiZlwTfiZJpvHuC57id8

TVJx/j0sZ8T1LJCT8oPa9KjTEThiaETViaVjvXrYTCuzsTTmppD4Ce1jz6myTvCag9ZLrGRWm0sx8iYm9Q3umK5SbpdcKRS0z8dxNi5mEBHVzSTPp0aNd8ZRB1EDRBthDBI7xpPjsMoqNfIfdOR8YeN/Se6N7SehNvSZXjKof2NZxr+Ny8btjq8fLliyeORiRgFZlEiLl/ghnjzsauRG6oFYY8d5YorE2T88cTl0BAGgpEXBiYKGOTrsajlCQjUe

fPGe62yd8EuyYxSHPWB6KQgTt9seoiusvEV9EUkVECMlDBOPXttsrNlW9oWR7Ro6TZ3A3tcirBT18bEIEyatjPjkAdryN29uIP1DsEZIRRgplhuPDq++gAGA2AGNA9ABl05mDBA+AGcANIBAKxoAOAM/oAsrgq+qqAcOouVwxQ5UBUgB3moIMFkodHHx042rE6QvPMsq8/xRhV8YX6yrz055erRDf8Zb9ovLoD8NvmVybMGZ90e1BG3yxtbAeejS

Ptej/rvEjBFsvJBNon9RNoI8nflyAIgaGxoCRJgcc3r0+wFUjEyAnF3CThjzyoRjgEqRjHun39XYZ0DPYYsjdWs7h1kZGNzSO3Dnqav9svoYJrzK9TmltH5clrv9mVtWFz4bDTPCuKdgEbVjBupV9jrEadfqfDTrbtfIfcK1m4VNgFR2wJV0Y19xjVsz1fsCODhlLTRuvtdF36NnWgztOFXgjkFgSx6dhVPcddlq6mFadvmWaetjgS1adWHDi2HZ

u6puOvbTqCyfDbUKs2gS3SjDab/W4UZDRLafkNwvopxUm0CWn3IZDnP3HTOUfEWjuoVtw6ecdYEf7T62px1kca7Tc6ecdUkvO0mKto1jROe1qBps5mIRqJ0f1xVLLnzQbUeVSnnP467KGmD/2r+D2ce00r6eCpCXOhaX6a19w93SRf6aXNLKqAz7Zt+heTwfTkWlqt5YXJkZiU8tyNOgikqq5sQqdHQR6YQzckwVVshG+1czs3MgmtCZeoZgjX/t

j9vyMKV9AD6AYtD7APmIaAAmAGASQGXEzgHwAxAB8xmPEx4X2BdDzvjbQsmxeeDYDcswXDroMFhbyKiGO8y0DsYt0wzW6CyDpRKRvwRBTnDXooXDRWJjDUPqddMPrlT0vO79yYYzDT0bWVOiJTDwjrEj3AdC12qfH9KoGFRU/s78WoP6wlFqBjzEYPg8WA/S8qOptrTFUjxeSTc0qK0j+Wp0jGqNApDqeljXtOdTJkfRjnPoktWMZTT6sf5906Iz

BD6MmR9kcvDg4fOJg4f/ZE0ASzW/EityceglILNHhJEx/wuYKe1BHJyzJXM1uyUrGFQ2t8GAGcQZ4tuidVx2/ERQfsdUTtFtpWcUNx6PMqEaJFtEY0xA6/3f+kUPMS4wum1e/wy5ncfc6rWcuO7WZGtPUrTMxWcqzI2Y/DsEI1GgvuZ1cXIXCpfPQJc1q1NajV9cuHym6LRvltz6jZVHwFmzASqlN90K+M+2bQlwpobMJ8P5szRq0N4vqCTrCeIT

SUeuzrRuSTFidgT3XyWzc2YYBsiaMxQWzIGW2azF4kiEBNug6u6IvGty2e0Nn8vJRsWgqZtjo+z+8pNj2dgSGrErBzN2YiBkCIB82yJqwJ2Za18wOmTDcua1Cuvg4zCvxzK2a02BycfmEurW1bCsNV5yYe+nhpZD5o1uTxcYpINRu+5ocqNii7xuBDCoZzWmw6MVNhW4eRuBTExCagMXGvcAuelYbqswWy5k4eYuePYCxSIWsSxIWr5Of9xVrqEQ

HylINiB5s/XPhDTisLyWxVbIQWwlUxCskivJWLtun0nMRuePYXC3PQ4apoDRCoKDkSqXO26AHUfK2hzFhPtzVeXMoBtye6O0CXEFufMuldvQobSFG11wbHNNkHt2bbGQ+4uM3jKpD9z9oxTVG+UMiZWtHQseeJFU+Tuys+VrAwea/ZHuo3Yj5zVxxiydTduZDzXBqbteuNw+htpTzDLksWXs1RQnD3Nz7ubVYxaq9ypaurElebLEzuO8WIF3EQWe

ZcjXBq7t3uMIMPeYWNoeZjiEvhrVRkFt2vWuzzivpCi2WG0YP8Em27uTbzrFFziV6w4+s4UNzDebYMI6oqWY6tdz2GCeDG7CU+GSBU+++MGJ2ts1tBDGXVpnwc+cuwmJF+aw9nF1U2HeC0SPsKZUk4Z2QJ6v6gySqpYBUYN9UYqTYb6twQ96tEugpkPzZRNh8uyxvg4mywV4BYhusGrVktwHQ1m6YfzOyGXt9cNUugXj/zjvsvzPxh41bGu+WthN

QLSbABW5yCBWXtC6zcBedCiK0NIqPnTI9+Y1tWHp3tZZD3tIcC/DxBdVMxK2Q+NEDJWnTKW1H+YEoNKzKZP8C8WxlGwLVvqOhZEBhuTUEAoGzEmQ4hYNtR0JTWg5CXgPMGdkfivfz/+aahAlHPtvKxCWVqBm1HBfE0oq3fZpOqoLnoRlW8kagszREMLjBcbESl1481CC/iBKgULAfsbEdV3CI7CgD8V1IPzRhcBKDqx1RA0FEQxuFcLpvqOhbV2E

gj1FxWFmh3TdhYEonq2ogAaB9WiOfMLTtyDWvcUhY7Ak/6mhZwLS9wmuX+mRIcMHtyfhchKUhbvoRi03W3nv/DWhdwLMRhTWH4mwQ6a0t51RdyL3sG5WFthra26B8LZOokL3sDLWSPijwmCwb5ZUZKLTtwA2CUR9wzuDfz/BZqLS90uutbUbWskVCLZoVqLRsCeuk2wDQOH1iLAhasMfa0PSveA+5qRY04bV2Nou5yLUyxazkhcBOy3atacbHDhq

FxZ44hcDXWqDA3WQBDlIDxYALrpjuAoWDhquDhtk1YiOLmJGRu2IGIw3cSGIDBZ2L1WYA2ocCA2+AmjzORd6LxnEg2WcB/+ZCnYLcRddM2G2P0Z+H7QRBYxL1WdJuOlW4ewWABLu6ejStN0XkT1rNgZ+c2DR7r/4a61mlGEBioMQkJ1ApnpL/5t42pbC3UrJf/8f/BE2wDB9eh9DTMrUL/420ddyDhHjY7CB5LqvrAyiQFNYMaH1QtTJ3ThPzAy3

NxJ9/6mW20perqYGQA2ucEHI0mUjBypbpLYGWiUzkBnlnKVc9tJeadPD2w2TNjqQ3DwVw9+ZVLZDj02XhAM2BRa1LuszAyJmwGK1pImQ0xZGLzpefS+Wz2jnqEqYTpeNL0pOQgEKjDIkQQ4OnpYGB0pO42YD2qIiuHVQYBbJLtnDuA6EHXhy6igBCZfuJ0pO2jgXkMofm1/z5+aDLiZhagbvjqQuqDIwlBczLGrnC2G4QQIqKzBqBZdyItnG22Kt

yNEsbHYLlZefUzpXciv2z5Wb2cR1QOqOe+WwFIViHhYm6zMSnafy4tt2KabuWCoKGd7ou2tZhdrQ1IV2j0YnsGwzOKoJhvtxwMZy2fEn/gXLwgggQB0lfB02z54YOo3LrYXqgS2xcYUPiwINUfPTilGTuu2wrwRkERz8GfJhpOwhABIEXkGzDfLQdsUoN21bwd2yf8cGeINlhuQgfGfe2h9HSQoFZstZ/yLugoMpQRTDSThaMgVZ/ztaaDB4YZy3

GgEqj/LH9jGiM+W7ijBjwQS4lIrdtjWAlyGEQ30CwIlysfQsFY/sMO3bYUpH06kPhQrBE084QUCigF0CwR6SANQvFdhOnnAbuZm3R2cWCogYlZSREleSAUGk5SgiPyIcle7RV4dx2H2zpdqZsFMtFd2a7dxvA3tT5qUeDUr1HqvDgcAZNGgZiDqFYAcNO3DgdO3gQdyNYruFYAcfdzOKvDFd0ZSFMrYRT71D8Ve0vUAvogTG8rCetB0PPHHuGqDs

I8XT0rFPzQWl7g1gdhDjpjUckNvzxzMAlfOKskX1wPNiSr84ev1OZmV269zV2ZNmyrcmdyrfet3uZSQumFiAlUsmZROKVb71o+21YRqDRISCOKrtVc+DkyVvuybgIGNbVarmRFROoXGT2hHTT61Va7EyVfarZdgQeZ0H24bqCVYvVdoQ/VcS4Re0ziGhkQBsXDmr8mdC49UBX6H+AgkwkHWrpVfHszeyetbqFOQwCtGrOVYWr49nYeZUFlIbsBee

+1curXrln2kMGeAC+wfo16eNtJVcernOukej9HTIF9DQwD1bqr+4QMel+xIGQNfGroB0serhiEe7xeSDSJwurwNYtJTj2D8ZMC7QJRPOrX1aRrQAO8eoIElRCMCTzWqk+rbVdGamewgO6gRnQ++aNtCNaxrkNcIOcTwJuU3AwKENdGaW1eKaviynoAMqJrNNZJrpZgKe8tKqL5tsxrvNfztCh15OhUw+rPNb6r2NZ2z5TzgoPLhnyLNdLMIh2Rjl

6iVr+do6eW+UoYkteC4iNbprUzxBeIz0gGzkGrENVelr+tc3WvfXtIDfFDgh8fhrutdprI4Vd8XtPf09TH+TTqmFr5tadrskB22JHJCoyuu5rDtZFrg/GSuR+HRgxHyVYCLU9r81Zlr8bgyg09HN5qTG5V0RKDrXtbvED0BiE3CQPw36HVrIddRg9EUFBTZkXDgdeK2jtbvEXMDRQ2/ALI2FbNrMdYtrBUH/I4qBpwvj365tdY2rejSrgtFtjqrJ

BYrKddLrwdcsaM8CB8KcEOMI1eJradeMyXEFsVHdArwf8ZLrY1ayyOkFRQSCLDOe2ftr/dYnrJbnHQSv2ogtWlzrljQygHzGapErCsr89b1rWWRRQKtDd0tJGC4+9drcgiHms+ClxIVNbbrB1csaRcG+8E0EvAbqDvrjpPMQn5DBuF+myYv9btsl0GQYeAzeEOWrTMr9e+rz6jnW+GB5syG2mYIDfvsYUDCYufFJQ45ni6MDdjrqDa3gbxAuKRVR

IiY9alrddZHC+626IbyAtWJGjoV1NdTrZDeSo1xG+E8RFUg7PPXrC9eSoqyEzoLz3OKIiBQbFP3fWkVAzU/K2cdODYtrc8nDgDwHZrxSHdrdDY3rDDYyaKKFmljwHvI7mT7rHDYyagiDsueA2qw0gcUl0dfbr8TVkQ0UEK24uJe1YjfIbuaC5I4sFqqJDfobhjZcyRGEX96eHVxZKH4b4RvQIGqCDM+uOLrHtfHrCjbAkM8ASo3JCKq/pB1r8jYc

bQSa3gliGqInLkjw7jZm9zSHYE68K7zE1LPrZdbelqyDqQykDKglcSxDcjY0bYEkXIUjfOKIG1TlFja/Ce5DRICBA4+Td2CrxxqCT2lTbL/qH6SZ6bArb0tzQBqBtkunxgrLlZDytm1Q0YIHVQNWATw9TYnjWsneEZSBHphpDHL1lb4rIEVWQbuTWsMl1Pr2GHPLXgmrLE+H2QPivVgaZnWbuYjIjRQSqCIKH3L4VpAi5WF/gEpFdgDwD2b95bKT

71ArsXTVtk85bubnAKIwL5xpwZsASUpzbbdmgneES0NegAsGoQPzfTTggMe8EIG7i6gWzEILdpiggL+8b6TwY/xWzdqGdebzLAgQ39c0ahV2wr+zZEMe5HeQoyH1Wn8RhbvlsEB75D0I02xG2W+HaJqLbxcGEjOozgOGuc9bWbNLaflxKzA95SDXrIQbe1IeUC0tE3a8lRf4IxLfFUpgikL1BDGGTRb4L65e5b8IMe8GKFQouDgv0k5hxbexj+8T

tiSg+Cid9r2qCtPLdh84m1LhpNlub0rZ4kwyBZ4LjFjq1KjvLRreZY3gk+IkcDsIi7ENb2rfhBSl1/03TD9YlradbxrfeWOcAyeZMBEYQrbBZigLNWXCXCiy4XybyrchSDqwuWXCTNw2MEdbE5dME71GyYRnknWPlADbv2vhBSbckzqbazt4Orf9B5o/96KaIzcEZIzCEc1AuPCgAVZKMAHAFTxRgD2AAwHbk15rCglQBagy0f10XGZmrvGfPVvt

PUs5EAJUWMlQo2EDEzeIG/gTIUp6IgMjpHeNizIvJpRsYcQtzrsRtCYaYD6mYejumcEjKPpejaPo1TBmdzDEjv4DkWsEDnfgaVAMfi1lbSpwgiMOQZ+IrDqIBVJkMfFqa0VDwtRFtT7NtAGPmaIB2RZZ90FInp7vKCzUEsuDUisVj44YizMWbcW0WfSzQ4aSD/7fwp2ecdGIWa1tnQaSz4HfKjYHMHDxExqG2WYnTvXI/TH7MVm4hKSlcHKolf2r

bS+pkI7eUs2G/jMktcEp09YNJMrfjvXD7Vtt91Ku/xnfN1VvcZzgVHIiSLHe9V94d6lpHY/sg6qUcfHbtsE0sQlVHdPsVptOdgna47FP29c3/03CNVIUN8XvY9nLco7UIrL1FAqnD0nfy4pCZU7AHbE7PhvwxfKsJYSY0U7t2YyT92cw7XCbQ98LpVj5YNM7nAJpd78KGRQncvl6Js/jdnbw76CqNsG8w2QHfPs7Lcs2R6OfPQJHa07NXCJzonbU

7mcs9jl3XJzdHbk5VObOTY+RNVlnZPKC9uzgKXdEVwXEaIQKHzgGXZkVrsGvcGEESxcXf2B0rBztvQk9IeXdlz6Cx0VWCxEgmnf87W3LlzeDCaYP9A870ivftVC3VzUGinYJnc87x7HZxeudYbBuaq75lyLtZxTNzo3ftG43ZZKH1Epc0rCtzcu2oDDY3HDeJUVInxD54itfA7a8k9zxizhgibjizAeckognbqESH1gOKH2m2cWfjzQ+WPy23bTz

PGREYmeaQ7eedd0BebUblkbLE1eewQteYT5wwsi7jeeVuFdGbztiBpLf3fijarH7z1nh7tfVvi7G7GCW6gV58E+b9RoXfHIdH1ohdaEmIQfJc7K+bnzdKwHgESGnTHXbYMq+ewuX3mWhSOeYleoTyWPasE+6JT3DPEtX5DLh3zSkD3zg3WvRsKHqWRplohEqGcd9Eo572nxPzunwezl3J2Qdn1XVnazvz9PfYcRqB2Q/nzsQe6sugUvfOxjPYlMT

+Ys2WQN58Sva0ZKvezYX+Y3kZNmazPjo4lOyCALwlzN61RC17Z6LamkBYWg0BbU0V2ZF7SbAQLAXAQ1QIAd7UuJ17ulFI1uGtXtWBc3DEgrQL9Gt417GrZ74fJ2QpBf1wn5AoLv2bD7SbCMugpAMLxi0NtfPaTYNBcNEecUEIlvaYxOyGYLOK1Ges/Sz72DUbEQhcEaIhYZWI+XZ7ghYCu5rbix8hf97DPZDcrvhoaqhfeguFEL7MvYEoJhe0GpO

pT7qpksLReWsLGqHb7nvYIYw/RJQ6SH1wCMFB7RvYD7AlA8LtsMpbcNaWzlPcbEARYhB14DqcpMsr7qpgSLsbHUSdYHxl2/fK06RYhUFqCyLLkqP72xjKLi1wzUxpvr70vZH7x+vqLsCEaLyWADr+7KJ72xnaLGyE6LdEGrE2PaFcB12+uAkRPc42ZR7MRn6LglaiuEZMJ7SEtv44xbpgMN3VwAZY/7cA6sM7a1Lwna1/uC7PAHaxaj2GxZ6Vo8v

P9pXd2LX116gCBHOLa4dh7VhjHWATUpQAKF07vVNwHAcGeLhMGz2W6ynDTxY6WLPFd0yBCcrcHZB13xcPWPDCiBnA+M4j63LQXuXGDlyY9TulDnkgG1cMcJZapSJaQ27KAcKEbmUHmJYBEy0BxLCOoEH45Fo2bnjI2xJeQr4Hdo2gfm0ieGhW7f/BOyjyEhg8ZAhgg4a2Ald2MHmyG/wHjpae3G1cQWMi5L7tfHDxwFZubeyUQQpacHYpZhAEpfk

Qejf59+0HRAr1eVoQxG+B4HetKYOBCoGpaNITg91LYDzCwtgg0L+g5sgsmw2YNbWbZ6SEtL0Q+FuuuOZc8n18b/g9tLqqHV+iRpkH/g9dLlaEjgHpaSHPpaianQX9LkWbIcIZbKgYZbFbNkds2MZbvoMVHjL4HZc2PDCN0dyAmgHg7tsq0bSuDaBzc6ZaGHxZetJH/gX2qw+CUuwByb3CFo7UHZs2gW1rLxTAgkPQ7Oaj5ZgEP5YP7Qw+7LKwd7L

6uyGH6W3N7iPaTcjw+SAuUCcuDxS5rsg4vL0ZYkykBHz4ENRsjXcAa2YES2uphoOHzkFBqx5dsIqlYmHX8EGSa1nLzdtchHi2wu4z5aoYr5fhHn5eUo35f9Q+WbDFFlcZbi4ikrBI4ppxTMchJEQ9QyLaYHjXYLV6FfBlMzCmuMPZIHwdnIrlKG68tvZQHxA/tRADg4robfh2+wD59S4fo7ADkkraO2buslaoHrI8sN9UBCoOw9lISiGBdPI8nTA

DgMrKSH2QFxX2HYPeXDlhrsr+N0Os9DBZHvI+DsblbZ2PGK8r0o5NHiZm52/ldl2O8BkHKo6w7adjHu/EAnukVbAHdI7zswuzJg2CGBEeDGNHqo9Cr3j2B9IjA90CRNQH+nZtHc90eW4cA2Y+TYAHwggLys3YyrpFDz5To6s7lbHyrnDw3unqENtiY43Euuwy8BMHN2YqEDHzo9Cr5VeumkGCqr5Y8zH/xgarEpCM1uQ9pH/Xa9c8FcXkwDGIdsU

jrHBpNfuMIHJCP+FgHUY+mlP9xuukEkiI+pgzHBpMGruIU/Ew4/+7XrkmrqFE/w5TF7Hm1YQKVWGIwh7HjdOo9FHXriOrByhubqSnXHiXGur69zurxNOnHoXGer1CAJKi+1PHINeKIqK2vAjqFKjkY8XHQANBrxTCv2tDYLHKAl2yozxhreuX/7zA68e/+36KSCIJrYuTAnoBzJrxi0gOlNdqzaA4tJoT0sQgFA9gL2v/H9AgZraB3FgzbMfHFpL

ZrSDylir0G+H14/zt/NbcZpQ5FH1A4tJYtaoO2nFXpXo+EEfEEUr6hYVrVNewn9TyDgT/ljYatatHQY6ABmteCw2tcInZusNrP0GNrikbijuo5t1Xz3RGt4Dcask/3HZuq4gc0S9ojNs9HbY7UnyQF9rdlX9r2k8/7Nup0gVqHhYcSWR7LE43EodcrQyKXQYKiVgngz3jrd1Gtr8iGTrrY+Mn8bi2rNewkyPGmQnI4/jcGdYge51hwQzE50nNuvz

r+qBEr4SF8bFE7zr1eAQIH8JaI2Fe4nEWSLgIn2br8n365qU7kZ5iDLxpKCgk3I5yngz07rInAWIvdY8nKE9rc6BHFsvDBzLwo8qnAU/vsfZOCwERBBQs9bCnnk+anS9dikzzna4jA4/H4PYPrMhBIiXoZaQqzbinljUvrmBFGQ3JFvrgk4rH99eIeCUUBQSaBwHVk5QEYDfFgJSEDsZftAnG07MY6BHxkb0A4iCY8cnP4nwbVFz0QBCGyn505hi

V+E/Q8PhA+f47un76zA1uRDuooyDIdtE5lHcDaUb8bGIw35He7g07kndtg/QmXBFQ3Zgy8+0/CnYM6sbk3BsbwSoXHQ06CTnjZQw6ZFw+sU+Kn5GKSbxdu+tbcE6nVU4KTWTcZkG9DybMM66nOCcEQdCAD8gn3fHk06CTOiEC8Do++owvY97Y8wGbJrmGb8CCprvff6bkze5ts8GUCw/Y5nj3i/r/Xt1ubM5X7IEWuILNiR8erdD7jveJNJyC0SB

NzywuzZFncgj3IRzeuMvUop7xvfOb3cDJCJC0iOms5Aiy0VhC2IBRWcrxZzgPJAiDzY1wTzdfgFOdxdwOq8EXcFWnusFAHTaPoVWTrHmk5F1QSCP1WpkE4lXObdnuYknIm9kaETaDY1Ls4XNYLYoQBMEEIjUDyJi3MMN/YK02X8GSQtpUgskRBpHvs/TnaloFYECEOAl9Fzg6V1in+Mc0EJy2VomLfwEnOb9nmgjuW723er7Ti1z9OfDnuLcwkLM

Af018DSbBc8XTmgjJbQkClkyWB4zcc9m5oHCKI5tkirfMHOQE89ZzIeRzITNncgF7hlGC87tnU8/eop9AZbHCCZbC6YqtggKxWFTBkrKcCjDz/rDnY80CQkOaT8A04PnlOcUBX3q9p1uGWuLUA3nGc+NborfTWvMAQofAw7nV89lbF7wVbwcHfnRc/EkawD3V6rcA0f88vnpgl1bpDw2YBrdAX3OeNbJyyburugNuuiBgXjc8UBdyyqaG4WNrGvX

vnrs6vnLrZEB4cHdbyC87nexm9bjBms8A9DpzsC6DbHNimuojD1w2C8LnKC+tbwbdYXreHYXZs8XlUbYiQaSkQHAi55bWbf5uObalnBs8XlWKzzQfkTuLSudBz0s4cBxKy7IF3A8rXWb5nWmx54BWBO4jCQ0CYi50XUhY9gdiCTgjnCMX3cpTW/cAYg163jIli8hN3K3ksHLbuo/RQcXeLmLIbsAqEhRVxW7i/wkUUkXEESGA2Fivv7yvbHmQ3ln

CQkCPIF9j8X4kjXk0ryfhbbD3Z+s9n7DgPeW5SBTIy0AnFsS82BZqypH9XB5pOS68E9uzIU9HkWIwjCKXuYnt2y8jDgciDvwlS8iEhukea7yA42/c5SXDffsEJ2QbQAKF88MfaVnCQLXWIWCQHCkZtO7S4f7MxqkLmuk0s9vfd7Ki4SBKaw/847Y6um2dj7a3QWXY7bB2yy8sX+bdRTvFV6jEsKFdR3sGjOvnbk0PHwA2sOUANYvoAPABmog1BgA

kgCncm4FIA6wHR4nUWQDbgve9aAa7gdeTzcYMqD6/grNI3YyEgCjHTWt0z/2FMQiQF+kpyAEmtdzEcv+Tcauj1BRlTDAaXbvEaNeiqYEjWmaLpEzIzDb0fzZWqc+jOqZMzk/sPbuYHoA94rsQrZG+E9egmpd7ez4nDxJQs8pmOP4tZmnmZApfbVUDG/chQMfgEtX7fzdZkdEtmMY+7PWomz9Waqznjpc873L6XyOaezUfOXZAxPezB2d2DwUvVkl

/IHnkvoYhDHNtnr7IDR/kZXTH9On5YaIGp+q5sN+HMvKrItsDuUaTRlxqHztbpl944jiJBUrFFtq8YN9q5u6L1MupreeoN9slLqUZs0J9eZVXiBrdX2ZBzFMee9Xdbo6YEZo+L2hf2CI8ZmLrRdnwM0rWiqisxz5+fxLnjp2li8kYuxRfTXVI1o9c8GjXqxYjlwCeBnPRcULUZHAIkoIDJlLGFLoxeLBtrqqNGZdzXd/JoVxpCXgha4LRgbRJQ2c

qoYC8FrXza+LB8eQDU4coRL5a5GC9qsHg3ebTXkJaJ0h9owWfDClzeJZnXJ9JsVkiKQbRC8BL4ViCV6SiDQTa+XX6waiVrlHryLRcRLWQa3OFlHUiRVQ7XKuCO71WD1nm665U4edby53fFxaS2vXIwQPy6AxaQ6RAanvhYHXoKkvOzbNmlhBhCw2xdmLLdEfOIKFi46GHfXriVLzYty6FlcRdXJ2uDXZUerzIqFCbi9quDpBvbUqG4PzNuIwwn1E

VIyG+wNeG7HQBG+I+vHmI3Jq5VtriQ7zwF2UodLgvnW2pwlPqMh7uPnTHbkdlXtanh74+e/rFWbFXU2drUqcXGi1RFVQJ3axszaoEYGz19iE6d3priSk3sjBk39TLENN/tcS1PYxnFyEg5pgZbog9tGeVyEk62uaxsnPao3TSwvOW+aJ006souc6suZNEx8Dx6DF7Zn0c+saaKjZHMc3t+bZW0VtD1FzDl7gXzkQXm52DPiSfzdYGK2BJVX0aHeH

GBaPBX4iBGx59HzQJGuY4aU1Imx6GntsW+hXCW7GgSW97ggpTwzkfsLbhGdWth3p/9xocQjg1BF0ewHpAmgDVACAHbkxmA6ALwCswBwE3A6ZlIAiunYzXfRW8fcH6+8tl10lsLYn8X3N2u237gYmf96EfTvAjQym+ACfSNM7aTpXEdKOnfu4dSYdXbmmfNe2mZnxW7azDAbpH9EkaMzUkZRmGcN3clmbn91mara4GGBz5qZN53oOhibPH4YWhOZt

sx1ZtOjvp9ejrqpvbOMjlWsCz5kcFtwq+npoq7azY7yEFf2+GzAO8ZjLRor5GIdhZm9JBzEHdNXEIdxFTqJHSdq4LRo4fjCVIqB5rq8aakZfODga5oN5lpGdUQTB9m6TeDvIP1rZa4D9fUP/T/DL1XMnpIQxfIUGb/KyjcBp9RZJfvKQIZ9YoaInLblI1FAQXI554Y53wDNlpqnsNXnO9MpQXtIw/3n53+wvRpXnq6QdfJF3epP89ku+dtfMLC9s

Irl3Au7Y97nK7lb/hZ3RAv0OpDD35ihcYT5gKP5GO+N3ZGTj5D/PN38OPXZ+9N+71Cdr1FuuZDkO5XZxLOlNFeoJjjMfXdRJsMDnEL8N5sYUF6etFNAv21OYkP93P+oBhEovsy2VrAaJa7ceoMIgzmCYRhSdoABjLuZNp7q+B82fP1cLogka3spDu8fnw4biPCKI5Ia6Hrm9mHpfjADQMxYCYWIfc2ezNnaMTuSdr3R7wBzENnG6IgNaTTIfBBXS

cXQ6IOKTr7uW9uYiUB+iGbgAaA290docBAQKuBS3XH3hLu6NRgOsBTqSkxWLon3SKZR5XUdFKBGf2XJZMOXxW+O9EgCt86PBpAFADgAVmATxdgrF07cgoAPoFOAYgCWA7W+2y3fRh2ffVCQ5TNhT5Dsclyt3nwJlHzwkPkdhHSmExsK8ywpedzV5edjZ8iKUzcYfm3jAbRXY+L3JOFtTDa29uiuK+3b70Z4DeYckdB7cLDEtHv3J7cfJGVRUQkKF

rZqWskDDQu7rpLmfbukYB++kdMIprH8zH29dTGMeCzP297DtVNFtktuktsOcMDo6eR+KuYeJRMY61E4fA3xFJx1yaenpEbZglj1NqjDxNfrPbqEOMUdihDxNgtfMxttwAvANLUZmdvu+alSieYPzvsxJ4hwUTvnqU5dKqU5IYeBFSnI4TgdRgOYuri9gh+U5zMJljosdoTvu/zXp8ZCRMdNfjfBt2xXMd4FOId/jTHxpjncH3dllp0tSCY8T0Ltv

9YWaka5IfL3+e/jT/Vqb3rJHyTVkdCP+LqmCrXsiPjWrZDN8+69mR4SPj8cKN/IYb2mEraTt8dFDeR7k5IyYON2MFstW8doVQadSPZhmuT1yJ1jjR5kgY9slIBRFqPYccHjTNYCPrMZkg/8Tzj9cdw7Ax8vQC9oydXyhKPispll8rIqPCEvVZXsr1lMC3mPKEt1sIKddl59Ef9gR+rG5XZ/eRu0wlc69q7UuaLXqnaiP1YzlzCPdLgm3m6PMMA/t

I5wrIPkJ8PtkEG7LZGG75TNuPy3hm7JduKPzx4oDcMGCVIjfrHox8Vja3YPIR69g+8R8qPKJRvI252EWTkE+P1Y1vX1dujTWR5FxbbGPOeKPDwiJ9sgn66zUdOBoQOJ8A3mizwgAsG2PYx5VxATXzzHzZxPOuIO8oB+O8px707Isb+QIB5w+jJ5y3yKe1puy8cxBoeIzWKcKVLQEGobaEwASQHwA0PA6ASQHVANIG1aHQBnAmwBnAfYFwAwgfeX9

Kc+XlPD/NJSGEowNlaBjpVMgIIFmqmlkEa09gaZ5fn/nRBSs3OnznVSPkRXG/WRXt0bh9S24xXj0dW32K/WVIkbxX+Fo+jGB/3bOPuwPW1qDAZNqWgi8FgO9ejYSDQsuKqcBZg/oJZtNvKe3LYbfbsGxAlqMZdTNzN0Dv2/0DbB/+3fM3HDP0nOn/0mSjKR9TTQTrU3qJ872Wkz/WGadt2Rm6hPIUdid8/KrPeQ06DfuoMtCabimqWcf7yAw+OeO

9BbtZ7kOUh/fL2aau2UHMHPjGOHPzloctBaYQZlqWLTG4kl2JKs1yFwyHPtSy+NhsdLT6h/qjawa+ZvjpSBy/z0T7kvXPxnp6tszTHP320cTy5+R2AnYD33MYWzc+qqRdjpNN0UrOdDuKnPPHvXjfrks2i6bSy757529bp+G1u41pf59R+9nLFjWVMVDHzvUFzCcydnC9lpsEguzAjCAvUEyI9CcrAvaoZw94R9wkiF+213CeZdqsYl9aF41jKia

c71mO3hMF/eSU27fdpF6/PlSYpRm2rIvdSfJSZseYG4F7PehgKWRm80Kp1F41iZyC2RwXc4vLF+OQnyaWTqF5IXTya1VSxhEvDbo9jrXZi7GaiwvrIbm0iXeNVFEHkvpIdpYLcdxIIx7Cdol4iML71+YQ6a4vdRkpsy3Fikql7oJdNne2QRDdxzF4IvMMBKMwucGu30DMvRZD2Pqit/e66cMvy3glzC670VTJ8EN9F+0gzXeIWeEFhJnl8A+XXcG

LPXaSIzl55KmxTePLCzROYV5ePJuYm7rJVeNL56FDk5zIkqV81lF3IfPjsWG8VAfjY3xu9T3Icg+jufPwsVxny15+rG5669z+3Z8iNV9sgyJ5kWF5/5UT67FxHeSQFO55hg13bTVsu9PPuJXu7M+Ue7R7UVxmV/SgL3efOJizavwcRzV7J9btTV8j2JuO+7Ni0aRkl//PH5xWv1izEI61/wvOl/SgTeYAOXyGE+Al7F89G+/QjG78W+16kvDPmx8

A+ao++MbI+Y+Yl8SPZivgUCQun04fI4ZHev6UGbV8+d6gDsP4vtl8RMJPfziZPcSvZ18bG1PYE+hS1CvUN/rAZS2CQLPe3kv17+QJm7LBr0zZQS14xv9N05Qg+5K7/Z/RvBp657LbIeKjZ4ZguN+575N46j6URRTS1q33K1r6ju+6ND++/QAmPAkwhAAaARgChR0p6gAxwGMwMAHVAm4CEArUT+iD+901n5G2HgFYSoHyHL9myhlQfKxgIbSBIiB

0aCvCuZCv0iOaPsiJmV0qeh9sqal5iYZXbzp7XbWK623OK49PqB/xX3p73bEWr9Pv0alEmgExAUbq4SSJFptykdERdK48wx3kJISufu3LK+2ObK/TdtMyGI2XfoPfNp/bX26FXPw/dTKo/k3ZZ+hPKk4v9fZ/MdMOaVXk54mvBhsHnNl5F1MueQJkHew3veYdj+IdHX1IVdGUwenXWhcA1DvuaDFZax3XVI7P1Latbf7o136beoXOUwytiwaaJj0

IY9bTZsrRHa4cU4+ircg6rTvTe7veUey6YzYV2JiZatU976zfcfhLczfEro2cUTzzRZbGpIQF08brv1pdC9Wv3IEld8d91d/cNynZuBfB7y9igq4Fd86rnnJoQT/4mRnButiTlCdJO2M/Rx+UDkTtSdKvDrk0Tb9++zaiZtW7jrDJK+8JdFZ6SW3e/1jaEinNsO55bbnfA99Z/610D/hzFggSGAh+NbyqoRzTZ+jjAHJ0XbF+ARHF58twrdmTHxq

bTHQ0If/ScLTBsFnPPxr6TIJpop1cemKfds+NYfpKv3F9IVZD8RJjHdMTt6wYfIAv6zFDIC7x8ZofrifchqOcBTNxqkTr4fuN1R/7t/iYalknfn37F987j57kfDwKzsSD4j2iIdsPqD8QfOXASG9h5t3jSdlVwD9QxJnIUZPuUc7rGIsZkF57ChSYTIAovgvZ8LQTTXuK9kgsM79jAQv1WSj3/h+QvGcvPvdAoEF3j81OKXpMfkrZBdt98Cfx9/u

dA04STUCd3vAsNkCkcptHBzo/bxGLCfcf2mzjJICfaT7vDCnvBhce/nv7Hd6tSe9IxDHc6zuT9SfSScPDGh/fH0T6wT8e8Z36JLgvBGPcfvjJQ5WjVcfvjFbNGQa4ZOnbDtMwcKtIF+cPnXLP5jjKOzpLILjLqj13iGJB8zJJsP5NKStnd7ndsj+8ZTJJb5k8dvPrxWZJJh/St7fMMPbicDt2gy4Zp8oKfJ5/2fI2kI5CzrTNQz6ajWZqRZA9/Kz

RvuBxraUHvbQ2/VlD/7ds43IfN/Oepu4aON4ze/5CK57PsLYM9dMaAFAW/RV8+v2svD8XvPPWbPkx43E14ca5/lqjTlhoE79ur510usFj+9//vlZ4L3kT/W0taYJvTh6DKDVtGN0er8f7Aim7cDeATuWWxnppwb3QidmbIJ6anxc4ovt8xfvH8dgfhN6En9RsWRuD8UfXL8WnIj9Yfgj4i7KM54kArMpfzLGFQxEWUvwM5fvQx+7jJL4lGKvUtV+

l5AfWaP9lbtiLQUQ7+ZVq7D6wNEsv3i+m8g6cFzs6s2Ph3HbPScc7P9OOUVjOOOjHTvkrZXdtfudvdr9abqE3l49V9XdofcwzUcxistiLXYumhvYRZjcYdF5l3VvMl6t6Fz/aDfEXDfgb7b1OT/dfSZHlzEb6H1MAuq7hCwDfJC15iST9eKfr76DGt8hqypqfPB9tjfWb9i9cz9vYpb81vkz5pp2u6a7NXfdVdXelzxj407SioaEdr76ELb5edpr

9Nl5r+t9PT8y7hr44oOjkaffKuafIeV5zJl51fvh9sYTT4cfIeQmPSOLyf8QiZzl0aKfKF5DyZOYzUmT4qfxMu1vWGmCTqCZONoj/mT6SfoTHSPkffL8XkkLriTR7//lg3tovN76fvDpLMfX2e0TODXM7MbN9J9L9bmjL7PfGF7vfVL/KfmnoSfQRpLmSgp3f2Cfy4u2ZHf52bnfe1/51mL93H/EIvvejJ7CqUqXjwgvA/l9+HjqL67foF+yf7Ma

w08svyfL6IGzJzuWfpH7AFHGVv1Cj3hX1Ua8TwlOo7P/N2fwj9h1VUfqt7D899ZieDNJUahJIb5hJE9/31INI4/tz5Bh9T/kiTD7EeEn+9fLwyE/SZouFxHe+fMn8HReafk/2UbTTQL/TNmHMrqqCvBf0opU/8VoKddUbwZNUJNfzH4BfIaY51g5Yuf4KoJfRz1s/WGkLPm6vbjxz/7jAr+BP4ZpyfNkZYZgY/jviT83vkQuJz4Oa1NEneWfWOYJ

zjhr3vyH9BzXB8Q/0nJgxVC9GaK7qS/aes+dV9//nle6BhDc7IvkCeUaIRsy/Yic/fnibTn2d6ZNKSd/fJ4cK/xJvMfaLoi/JOZ4kTIb8/vkayNMD4Nj9kemRqqslfHi5wfqFGWRtx2MDx7+FfcxuxfoD9IfIr54NtG5ONuOboVKD4O6+77Bf1r/uRs8ZdjXyHwfgbdA4W76dSw95q4W38PGKQai7Ml4fm27/QmPr4S7Mr4uTZDCk/536NVl35uf

l6Ju/NOeS7XH/3Pj36S7heaPPUL5PK0r9u/tOdTf/wtOTF37+/az/P1o9ui7x35XuGH8o2e3/LflGwlfNb6lOSGIFYra8rlAz7GfQ34EfI38D36X7J6nX4lslj+kFuP7a/ED8j3vKrcf878znrL5cfs77HfFP4c7b7+Iv1P7J/HT8fvmSePh8H+Sy1L6Z/sdPJ/CH7A/WGJw/7P9p/fP+OlNCeJfdj45/iupPvQv95/UXrC/kbNUZOP6z36ALR/V

nJRfyMtkC2su6tX39h/HWc6tMlPl/OAsqfm5+spGv/U/mZqEftJLufM59BNIL8ufBWeufG59M/UGtACTwzofLv+jiFxsJV6cc0/JLYpJjd/W/Gbbuuen+VxkYdXdwetq50wLm/Ld6l3kD6m/uWYOf4dQPT9HpiJSr8FmZWZt/3X6BLo96z/dH5+fkI5nvoL4mHhf5HXP04ijK97slzX8n1Gv6r/yv8QF9X5C/8X7CTiX+C/KOe2lKX9b/3G/91Yv

7IqDf7b/zU6kFEH87/22dAb+crfjsX/TviZmCPtf6K/577wTgk/8/BSfETDL/m7U86p/uf9SN6/8/vbszhNT8a6/maMbmu//qT+/6s/6L+tbaD7UfcD+a5l776/eD7s3xn687Cj+vflr8j/4S96/Pnef/A5/abk+95ft//5fXv7U/R/8r31tqA9IlPxv/D/8QAJChWO1piiARP/9P/1pjPc87fR4/Ypd3/0veSADuKVc/Mj8+H1c7bR9EbC9NK88

VHz3/fH8Qfw5NCHN2WxJ/GfVSAKXnLf8KPyCZb+8iLwsfFXdov1sTO7MXEzc5fXc63wEbLn8ALwN3Dx8KPVDtVX9m5QH/bD80P0EA0x977Bg/MQDKBQ3EWZ9NfyblcQCZOzlNTD9RU1bfM01XbSkAq8NrPR4AzgDFy0hfBe95OQ8NEz8WPyYAuJ8jAMs/RZ9F41AWWC0lH0o/DP8i03wAs38f0wqmKAUGTRWfZK02Y2mtD2xed0wA6j9E41f/Hh9

9APLvASUgDSQA8bkw/3u/TQ9vfXmDLoMoANL1Mlla7zd/M794gIrvUADnnyCA3BViHyJaYK0UgMCtBNtltAD/F/80VSW/HY0CgKM/Ep1YPXDRT9l3dSRVBP8znzLdPV96uVT/OP9bw2L+JT91X0P/BKN/iTT/L+8Y7WhZboCd/xKffX9+gIscbX99AOGA/RwprWtFJz8VzXV/VwDxgNktAL9fAQzsbf8RgLTsHN92gOFWBeM0BSUcGs9Qv2KlSTs

0X28NTQUuT20FXUN8t233SJl+T1/9KHhJACskGAB6xVx4RsVcABScaYBHwDF0THh6QAOAVZkJbx/NToJToEnwZlw1vF4WPXQXnjiAeCx2UDegA0Q+UwvAOD9hfxOjRfpYDQlTXW9OIxujaA9UV0W3Y29x8VNvV09zb3dPDC09MxxtHdtxHQWZX09pI0u+J28paCNTBLVPQBw+Dlt3bw2kXCwwYw4SKbEcNgFIP8lYz0bDArV4Y1fbGg9oNxRjPld

TIw59KO9dD1zPTCVs3hORQ3EjY2o+I7E6L0bTQm9kUlPWccN4QxizZX0Fp08/DYNLHSuxDZB0gIlaPv9xcDqJBICs72wla68G7ytfTiUz72f1TLcx4VImIfMkXwFuMKMD73dkG7wnAKIHEUs7AOr+FFtm72z/Rc8KOyXvYokQM3XrXKxXDADA/Rtfg0UPXxk6HyTyUe9zfzjtZQ8LPwY/B1dRPSGdYF9EAPBNMxI4wO5hHwCOO1AzK4U7PU/DHMD

LbSAjJYDXXH0bIDkDSSUA7+09bRWlH88zijbvZL9FTTSYbe9e0z3TfLhsvSbAsmNDs1S9EJ8ydzIMFZFa3EH/QX9HQP1iPsCgjXafeOlbQMn5ZF9RwJp/WX8JwJ/pcbVnkROAoTVzgKZvA5dwHQGjVVoEI2cACgAf8iswNaZF3Ce9NgBlAAoAKABjMCMAG4QjfDbbX80WdmigRJpafDetKBRRxS8gYjQ3e2bgX60reGsJYGlhUzdhBV97tFyHSVN

Z20gPedsVM0NvZds+IxNvFbcxmTdPHTMUD023TVMbbxJAu28yQPEsJ29w+CpAs9sUCCvWBu1r20BoekCrt29vYPxoVi2UdzNHtzTdbf0Q7yXWaG01sW0DNM83U2+3GO9K3RlXESYSz1SXebVTs1uDRecPLyhvXYCuIJBvEDlIrW7NfO93Yy//c1d3oHwNXDczxlE9eFgffwsA3extGBkg/DpMX0llS0DfbXw/QZ8qbhXYYnd1wl8bGp9k9349bj0

hkBqTKj5rAJovDE01HBMguFM15lwfJEhzqUM/AY0Zvya6Q8M2dzDNLtcSFgh/SfZkdXh1DQ1lUCpIIH8HkDUNf1cu4z/AyqNnIOK8Vd9pMmDxdfcdvQZvFcDPkUK3Q0McvjZvCAAlqC+AATBNABYzBxR1QCSAFJwXgDWoGkAUnHOEdYArMDvFH4CPvSxAPK48EHMXMgs/vT+A7TgjUDvApftkjg6UME9oPjcocgMzu0BgKPNORGRA66N7TzRAniM

MQPAgrEDIIO2+XECYIMtvOCCiQPxtYzNdphJXf088cFbbdCCX+lYUXG46ZhGOJkDE3W54IxYsmmIgjkDWV3jPe1NeQJobcO9v2x+VX9tJD359JwM0KVy/Cl0rFSv/GoCRfQHDe/9mxm8yW6DDFQdfe4w0b0U/O40c71uvWhl3RR93XiCDr0oA3mMbr02vWgCjfzBg4C8EfxN3Da9oYIgvQn8voJSfdBNwnzM5SEN0L0iTF99kMXRgwi9370evads

ZVSAfQBMhIJeDR+Nj/w1sJF1HY0sgkyhrIMGLYu9gJllDGrQZkzdjUmDlvx2TH2QqDWLzMS854yLwL8YHg3VDbeNkALDzC4MJQ2G/IFM+YLKdHYDYAI3mGyCfY07dMmDGL2rTYWCuYNMg9zs5YJuDZRM8YINAnICLMVq/FgEdQNDjUvcf30SXC91WAIvfCoDmpmRgpx8sn1qA2E5IPyj+Xu8CQxRgm2DOPXDtLc1Sf2q9AuVqs1JVOT0Z334A6Pd

egKqtdd8fHxpKPj97YL1/UICn30yTFPdPTRz3HhM4EydNfHVZ/ln3YmCUX3vDJgI9Y0m9GggF1TA0Bi9TYyVgy39AKmFDbzsf6FlgtQD7PSqPOZM3DwHVCfUBYPqPPMDhlW5g1b921QZNe/5XILsMEplHXDjXQY9fIN+/fyCK/196YnE/IJUvAeDc4IzjYY8e4xd9fn58zkp0Fr8NxBL/AlFdL3ZzM5g54PyHej9OP0NiVV8V4MBpAT81xCpxPnN

8KnE/VKN2jFdsPJRD0EPg3M1UxnzNIy9gFnPgqwCfYPLNS9ALL3KEYd9IowMgmrxP0CHfXKBORUd/YoxoU1BTR1VsOydSQ6MVFUSNI6EyPQuPBt9Jcz0VCD0Z+UTII+1oEIjVC2Dhi1dVJN9M3xCvBSDwrxAHSK9hInbvYMVrS0HOCK8hIk1zIlVqd3NiNBDgr3SUTBDUEIzfShDbbV+fNmwq3yoQl0CYxjzfZN843zfg2KNyENoQgt96EILNfKN

ArwoQ3hDd9TDgwRCeEIjfCOC0wMIQ7BDiEN67HOCRumkQ9rxuu1wQoNVB1Xv+f618FBwQkhC/PW51QaoNEMEiDXM5ENxfDgD3+wLyOK9OcWDAzsDgnzZsV48LEOygLL8ORVivJhYA1UsQiJNb325+MxDnEP1zexD69x4MVJNpvFsQlxCfELX/dI98TScQ/1VvEJPKPH8EmHCQobsdig8BG+NOWX9OIshAkMiQyR8q4MG8NXMtEKMQwuUVvxeTLs5

83wkQw79A3wh/RhCoEJ8vJBCmJDfmUnFhaWbOZ18BeD1gBLtej16IP+CNjwdVPy91L3Cgy0ctSANfF+Dv4JVfdFg1X0VZYy8QFlN6W+D5oEJrcY9IjCykVeDhkPGQmnEgoM0vMeZ1ZWWPd2sRWWHgvZNb2AnXQfppLxKQ8eMPIKhTNpD6zibgq5F88lcve186j3lDNPJ23xdfYrRqHylDfLte3wdVdYx7kPFgw5DZFQAQlFJUALvAOmDHkM3tFyC

8fwLgnpClj1+TfWVVYNyPfV8QULoiMFDCYOg9Vfcec1Pg6nE6EBTg0pN2emmQoZDcYO+zR69fwJR0OODcL2mKZiQ+jzxQ2zswfyO/ceNMgmX/Sr8NkzyQx5ED30pQk2DCcwW/TWCsUJmNIS9VkxRQyi9a5Rm/CfpwUINjHGUVk0KERIxAUK4fNlDBUOLg9i8y4JxzAVDzcBeQmb8RUO5Q47F2j3B/fZCJQJq4FH9D5jCgoHR07WWTJmCxULmQrV8

acWpQ9mDtVRqhbZCtjyNQ55NaUJVsepCOIg6Q9uCvYxO/GlAmEL4Q2ONxtHfmCIQaUCyQ2RDor1OTZpCPUOOKXXN4ry5xCmUukMntAq9KA2tzZbtpikXfH4p1u2dzZ6BpiknfEBZY0KdzKq8v4zDzM1CwzR27IRZL123We0ZM0PavFq83rmq7BBCKkNtzSRY5KDnFVq9OuwEiO+1Rzgs6DqDlFmm2HXNzEKCQ3xsOr0jzLq9AlUKvSNDir3avRtC

Lu3AFPiJD11XOFsdbIAHQrqCHc0SVaJU2oPRPZ9dOoK7Q2m9jDnwzWKD9aTyVda1jlyh4CgBceHwATsBceCHkGcAKABeAQ0oGxUx4YzBbMGJgK8DjcH2sN4tr4G3kPXQvWXSEfaAHWiqaNW8k3yuPXs4+CyAPKnBD3zotHqCkV31vFFcBoLddIaD4D2VTddt+/U3bNdtPT0DdAlcfTyQg/bcUIMMgCldsmAiIeT569GV1L29gcDVCcTZKDy8zDld

EYyRHfzQToP5XIUDBVxFA8mNNBzkxOUCDhye5Au88hyLzGDsArQYwlotDQJYwtHUAgxX5OYcDGAi3ceExBz/pYZ8N/xKSUq0v7ggJOZcWknz/NKkH/V9XUT9WowP/Ek4sYNe5BeCpfUvDWwJjz3c/Dg0r2B0Pero9ALc/aF8hD1StGKBi8C0AwoDjLXElXz949ShgYzCa/1U/IrRrMLmA6c8G0nsw800lHBqzZzD1AIefQAwvD3cCBF8G41kwnM1

PGF8w//k7f2jfJJgjnywA/TCLJS+/VuoQsLoVLT1aYG/1Zep14L3gxj9XpSSwyTCbz1B/CCE/GWvuIt9lH1AZLp91H0N/ZlVrV0JVGwC6ALNXZm4IYJKw4XcwcCyzCgo8sNsAqndOMKitRrCKsJz5TB9QrRBg0RNlVyYw/udXTR6wxSF6MMEpCfU8QwZg/6DAxUBg2VRTwwCAvTCx3hmwl79QgOlDHNMGdwzNbzCFmC8dBc9yOwvGaiV8r1SA0s1

BQ2CDXNM7MMOwsq8O72i5MSDTsPFDNKEvQPIlec9+IO2DQSCJVylAiQ9GpxZPG7DPW1CdZNQrMJkPG9NHjiGzWUYRtUcwqolDRiegxIC5PzeguyNPMIPodbCINEvne78AsOxg87lZsIiw3N8RYI8At/UpsODjKu9ZAlo/K/N3bXtNbYDqEKk5Zv8K/gzufxt5M20ApH8T0jDAms0LOR7/IQDvQLzND/g/nXsfGMCEglHfcn8zAITAzBBQP3mHQz0

WpVCfZ2Dd33NFKeCIR1QaYr8Ij0mA1e8o4PuzBuDGMllwr98iwJZ1XklFcPNg8TsAkzshX9CFdlkAtXCpcNWzBL8YvWDg1GC7bF1wiX9af1ifYRkCfyUFS3DROQ0AnRDBdTshLX81gOAjYT0qcK5iMw9DoXKwyGDFgJVwr3CSANBgtODvP1Sw3vVpcMr/dLlAgNHghRDFsLTA+RCi4Kd/B+VVEPTgw3ptJVhwkPDo1Whw+4hcP1rg078IcJdwoT0

vPR+DXIMFdk9wv8NjsN60B3D+E0yA6T1LnUNwzSkPoP+aPBCfOQbA9/tvsMuwkOsA9Tr1BvClkCbw7ENPH2ljQP9e8N0gxUFAXz9/TswzYPn/JfkBIIGDW7MYjzz3GogAtyewpf858MtdTHcWsKXwnZcYoL29Itt4oKuAkrdtgAwjTcA13B4AZgAmgBeAOUAZwDswXWEZqHiAOSorwPfWXDQ6YDsRc+dHSgdhT3YhjjVWQRpMMKSUQA9ToxJw1Xd

g/AdKf9C7T0Awh095UydPYaCRIzNvafFkDwmg/TM0D0MzQlcZoPO+UoVHb0OAe8Vv8DfA+zN6LRU3F8VNoLiwJ6AB1F2gh7c4zzIg57cd/SRHYpoSMMFAzbFhQL/bS6COIMrQE0CXiV1feMU+ZkSzW65QnVewmCBiH1cQwwMMwITvBY9VsKazeyVnj10TUyVzkBxPeLDlSQOPMQi4ARJIVY9U7x12A51LECkIqH81CMRDBwgNCOKwyLlWj3ew5Qj

AvwHgVQjTDxUI4oCLoPEffsIFCJyRFboZ8JYIwSkeO1wzJcCV0O3wgrdmb3XAo5dNwJOXXKC9gDKVUgAjAHVAFKCWgDYANgA1qGqAaTBlABScXUp78I/rHV1miGdkSRNX8IwkXwhzu0gkXRhoQM9Ac4Vv0OA7Gbd42RTpJC1YfXAIzECwMN9daAjBHSpqGDDttzgw229voywPB2948TUge8VGiEx2ZPp6LVUdWQNPQC6IAWR6w2t5TkCg73IglY4

kR39bKClWagjvM6C6CPMIlg9Y72xnIQUGZwyvH1N1p1hnbc8tw2lXYJ0r0TBVFYjliK1DCCNooLOAlwiLgIMFDcDbDnQAQgBraWYACxQ7MEx4PsAZqEwAIwAHMFycTYApdG/yU0pVT201JpVlgBanfBBIomEuCJQosAYgChAVoG3kfQgXcDEzRBVoFQIUZplUQCa/HIiELTyIhdsCiLUzUDCdQRKInECYCK2waDCrby9PdA9qiNDdWoj9U3qI0vQ

8D3rpDKo6cCAwS7cxlVUjTVgqg00jPaDA7wOgnkCXty/+fkCRiNOg6rUEwXdTXM9hgP30ZH5QOyJcXg9vg2iRcz8hDg4IhvZUpmtA7LdwiiWJGhpMP3CSCUjl6SwIA/l8/llI+ekmHFk/Jc8AnUlIwchMP1UPFQ8xnRdQqdkNSPlIkElfKT1IjycDSJVI4HDZg3VIuUjzSIAAs0wlSOUZG0jzsLyzSBoJOUbCLYNauU0VBZgZ1AhZBVdEX0nA5QV

EVB9IoTkpMJUmSZEBOSDI/yVsZwXTPyVod26zErNmELlXDelXd2Y3G6DEyJjIi8MLQOewqLwUqUOLRstdsPspdSlAdQ13IyUKm0UIicoCm3PrJq8KiQopQsCwES7eeCFmcLJVBaEiNU1IVSVowNY6LzkX0xyDGsj30wmdOxkYpC27UMC3YNzAqyZ+yKJgQcjnK1D+dvCVIOgHO4pYlCILAcsRDQgQv9cffSPvDSDu71S/IBCKZwBw9aMPbFENM49

QZzz+R2CQyImRXkiWENn5PrCf4LeJMF9PSPUQETDW/iINJ6lwM3S6GlgZSKfVMx53JzPWe8jigxQEAVMpVTXLKTppnV06CF9Z4H1wc6BD/lt/VMDOH3lw4GUQgNjwuZolnwV/T79I8IVNSCx940WHdZ0QNHXheFMP7k7A6AFL4wC9VuDLpU0YaxpkAWUncT0GdRa2TJokmgWlUklsKJEQXCi3EOffVeEsKPKWTeFRthsfNJMosJQo8fCKvxyTCPC

5sK2IzqMdiKgjZa04oLcIordWb03QioAxdHtpJahpdDR4PsB4gFwAdUBlwEkAfQAUoL2AegByV1KgtANyN39pM6BVgzJsWZtX8JVxHJs4agO8YIhCUWhhCDJHnkemAu1oSPYdYCCDb081EDD0V0gI/ECIMPYDYSNPKIqInMNiQL4DBDDS2TQIySwloMxmJaQP6G2gcFpzUyptZkDFUUjwKEhSUDww9ldObRdEP0cUM15XZkjSMNoI8jD6CPYwsv9

h9lowzbDJiLole7CQZ1UnabCX/QpnImdZBS41WYj1g0vTWlwFiMpnbFRnOVW5e9NO/3B3Nfl7bSRzYl0PI0r5dp1OqP6oonR9yLTvUt1EOW9uPcc6JwIZb9UnUijIhh0VgK5I7LDIwIDTTedyVBqze6CFwM4YDajF3V5LZaifX27wlNQY6h0eDx5fhjLA46jn1UmeAQiJMM5Vfp5cgV3gwyUekmYeO6i4KOgop6iTqMT3Yz19Dwuosx5JnmkIk1w

ogh2olwDAzRg5WajV4VGw0rDgNW6w6HEx+Q3IgPDBsJo5VD1ZIIgxZ88dd32KFsiOqOqw3QiOg1haVDpMaOho5aVsd0JSGjUZBx2dUPC8wUF+HRxLPSzIvbD/nwjwRHDXuTKo66idhSlAv+UlhW7PW0iXDGCQlmNg0ydIxP8+ZjbTQQi1jxEguoCcT0Fo44CooKAdAts9iNXAnfd3CL33aSiJAEGoDgADgH0ACXRjMGqAIwBjQCSAI4R8ADF0fAA

eABpAew5yLVpTLTUCmQ4ze3ZPCGC4A5QyFB7bHbIU1gVINph8wkkDL0oH83s1SXCiAVtPUrFlMxco110E2l3JJEiqalKIn11yiIxI2DCEIMComoj7bzxIiQAnbza3QkjK2V5qRJpDK1iohkCXfApIngtdhwOZGkjyZj6I8giKILSWDKjqILRjRg9zoMggQcNgxGQ7bzcU71o+FLNHsNsIos9zj3g5LkUcTxKeXMIpCJeFAggpCO9NQa8Eglk7dRo

diE8gJq8PDyr3ZzY+cKRwymjw4JhxCXC5/yIBcSCg1wpQj2jNLDd9a31gk2Xok30Vi0Xo2ej16K29Pc0paJ5PETU+TxLbAU8EIzWoUgBiAGUAXP1NAEwAeIBNAHVATAAGgDAKLAAGgCvw3A9TaK/NN4jffC3LINAMBCf8HldfiOLIZnxTcDSWO7c73BX1ElE3YS2/Q9gvaOTpCABdXn6gu6MICOKIoOiUSLKI2OFJoIQI3dtEIKjo5CC0CI/NFPR

HQXwPJaQDUAB8RsolIzTo9ACsMM2Ua3BSZnYtbSM6SJrhCgi7KhCLYYiTClGI1kjIJQmIhiDBs2XpASkjAxlXbUCwPgLIwKkjQIfnfMjXSLzvDEMuOVJsURA5wMjTAMjpGMPoWRihwIDkZ0COsJxwjssWwK5Ucd1Ay3rvMjkkaM9Az7CDGFGoqVsjGLQ5LgkAGWpwOsDoGT0YFBk5SCbvMxjsVH5JNLhNGLXBJQkMgg+LNRiU6g9XWUU5GPV9GTD

QoMkY2VRPwNR1FMiyv3P8cBi9QMEY6epdDTrqf01TSJ6zDg9Z8EiY8DtjJV9NE55loXFAiQIQmL0HJl8D5AVA96xapVyY/mZxMOCYkM1jww2AleEd6jFJN6lWCINXdajHVzPqMdCaxm0wtFpGGUWpcpkXN2igDK5AOX/pJ2otdFOpOujhiSXwzhgTGLeKK0D6sInhe9kDGMfIqcje8O5UMhDcDUuNQ3cvIxLNLPVTd2cuUkUq4ySAuHcN2R5sC/5

U8IDIl3cw4AqnQCiHqIZou7CPJULI3c8OrSWwoRiJGIEo1HCXSKlXVj9gHGuFbMiXKWBZbt4IaPEYl5j4aJholmMNSL4Y1AUUaIMPPmEawKHopTlncJcPWECucLMhIFimBVhYmRh7SNEpMp9hcKg/M4UrmJEYqRoPaMA/WdkPmPnZYlDeDDftekN+iRS4FF0WUNt3X7llGMxQ2l1z+WoNNVdX7wYAw+h6WJx3RlijIMigha0RKO6jMSi10P6jDwi

jiJh4JMBjMDYAe1kuXigKGcB6QGIAaoAMQAEwZQBnAENTF4jzaK76GAgDT2xgYBhhEEoYqBRUBDAEV6tBizgoKsMf8MnZb9Cd1Xi+BXtV+hc1OdtYSJAg1yj/aPSFKAjUGJDo9Bj4COtvLEjsGJxI6OiJCgDPZ2kE6MqFSnBVyCplaft6LWFHKhjhlBiULRhkqODvAYibZG4cTKi2GJZIo/02SPog8cNpx0HDVNiPPxB3MQi/s1vItUDF2na5CJ0

5hRKPVTDxYzRPTTD/GJLY/I9LfTHXPmM2j21mRcjC2OePbgj02JFozp0HiXFouwjm6KajPmYFDwaBJQ92yKEOVc8dSL4/GA5tDzUPL6iYaRgOIXdfdy2fX3c8cPdTSyFwRRrwrhj/8OYAzA4V3UowngCA7UP8L3d5AOkAzmMdjyw/fL1g9w3YyWM8YTTwpO8hCKtgxJMtL2bYmeiAP0UwrN5GY1W9VfCT2MIvB90IEwrYxO80j0MfVOD2aLGPTOC

qkyFmDl8+UIeJQpBcANVVIWZLYya1Fh9MfzeQ7g91UOZg7g91k1A4jo9EiDwQIWZCUJzOIQ5a4yWQoWZF3yFmJNDb0GgOUDiVkNBQlY8ziUzQjpDgxBAQjt887TOJD18m3yo4gpDubSIbG49+D3uPIG0wWJpQVJD3j31rajjvjzNzaJFFux4Wch5okRHQmD58DmnpbNC4T3UiO898Phm8StCq7WrQwwMO0JfXRdCziTxPOXFCT34PDRYfYlJPCOB

2CKmvVxsMWPdTOk9m7TzVMwNETHQ3b85p0BHA0J0R2ye8W3F3InYIi69XcWYI+zj2N1+laDi/kF43V68iYDIOD69v4DdEFC4l4Cxw/D4ssC1dNJY8sBRwMdim1Uwudj4683YImG8Clj7VSzj8LiRvQi40iAC4rT45u0aWb6gEliFI4/NZ1W6WKj4iJnc3NdU78z5mU1j5exGWSYVMJWq4vzc6uMbY8riJe0TcV9jibxnVU2USuM93Z49LT0F7a09

37E3w3Yi0U1cItcDJKMSgxWj0AGh4dHh4gGwAF4BTBXbkdUAzMG8AQYBiACqiGcBjQHwY0pw6U1eIhlNXhBiHCdYJkFPoeMgwRCuoSOcK/k2QJLVoVFNPePQ4MQPOb9CIuKWgPHtJtjgtCA89bx9ooDDEGKKIwOiIckdYjgNQ6IwY11jECPgwnBjEMLQI8W9fWPkdT0AxwFnCXhgcqku3cnIn/FbgM5ZI2P6I8ME2eXt3ONiR2k+3XKiuGNFA549

8eIPYpyNWz0rYliDSXxro7uEqqJxPHuFqziavZfNJQMPPFK17N1mvUzDAgxZ4ltjHX17o6vChcVZoxUj2eJChS6j800zveeooKPpjYeivOHootj4hYPkwhDYKKPs9ZzZNTXXTGjDa8NWUAejfzynTKQDnNmrlcuZu0xl/Fn8NeMK9K+F7qGEgZzZgk3txWdMN0ybmF7N/ENPWJlitYNt4wHNlzEm6W3jgOOugIdNlePfjC/8l5gN46mCS4J+Qu1C

7uN3eaWDS4N+QusjB3lDyQLtZ6x2RMjFbY3gRNth5PgOeW3jkOO3TWwwHUKCFW3ifvye/EeCU+LxsL7pubSBQk8ihNk3gwZDt4Nt4wjiJkNpxZP8aMC/g6y8c+NaQoXNCu08gSvjLeOtQ10geGAbQKi5T1iOPRt9F1y74phCy1ThVIjY7jyIQwxCfyJl4+9Yvj11zUu58F3wULviBOLSvOE5l004WHtClu3jYSzYPeNqvCq8Nuz5WKpou+LqvPbs

m4nX4pfi6KEU4wPNi0MH42XjDzlFxTtDrwDC47TlGeKv4iPM1ONv4oXijsOW8Pq9N8khQOnjhr3uyOfJX+LOw/RZndAXzdr54zUYgnq8rOKw+MvNGTyWvL7sdrwLoHniH+LF8I68ezFEIg9iHOMQ1YHsWjxJ4r9jETGdxJhJqVDZ4Wk9POMKxIgTGfD43ZWhaT0+vPtBJiEJfA8jSeNBvXHtD6he42k9/r2e4oG8hKLpvbk8t8JG4/Yj10IgdSbi

8cHoAIwBNADmmAYBBqHR2TcAoAEx4PYB25D2tATAlqBxyXSjDqCSwVzZOHnmgDpxgahw1CzR3iAUDf8C73DbAhv0MjnVVVh03uJRAvqCg4QW3Nyi4Dx+4urFRoNRI9VNAeMxI4HjsSN1TH6MY6IDPXJkCGLi1Ihjq9DcsYCQNoOhweoUKfTjiYPxGZFR4/Ojo2NkiYgNi6NTPcCU6IOjvQnixjyA7MqilQPs/EDsq+IzY+mDHhjoE6ajvnUMwrrC

uRlLPU0D/AJWAiYCZyNbvVaidV22fIO1GCKqExoDBMMqE1jcacMKw2oSmhPWpV596gLYI96EVqNP/I4CUox0/Q4DYjW+pURDehKGEin5lMM6E+pjRcPUw/TDo/3rVZPDNqKnAuisTMNGEvK0UBAsw1YS8NzJolLlWhILY+tUbMNU3Rq0YKJ2EzITy4PzAiYcNhKmokKNjhJX6QvsFgP47A4TRGJIXG4SQsCCY5YTHhOTzCzcHhIcw1jCH/3Sfd0l

XGJeE2zcuWw/dOv8t7xBE/90wRKC/Lu9Rzz2AxCjl7DnvBCjLAMgzVj1bcPC9QMDvf2MQwp49IRREwuN1OxedXET7LW7/UZ9e/27It9NwwKCfDTsCwN7ItfcuWP3o7gS9l1loy4Dj6OuAioAwkBmofQBsAHpAGyQnJHtZaTBvDlIAKzBpMDgAbsUlWORRXTV3aR42PhcgLTDQgyobgFg1QDhBK2SQQwhTXUaZeHtoLh7gIGoISMBoc/Y0kB3QSiN

wfATpUwTeoNAIhBjHT2+4pVNkSKggsaD1t3RIxwTw6LdYyOiPWNwY+ojFBMh4+f1vyRZTRogySMhEPCCVCjeERAga4HCEhM8aDya8VbFebQTYgVdC3Qowx7koyKB3QHCL+xmAv9idyJidTZoAHyEYhl03hNwlGVdq3TDXDt0HoNkFeHCD72Z4xMiobwWYlrD9P2LBc08iyIPLXZjhsOwwHb8vSIJgoWsDv16w3vNX0zAAuYND70KDftit+QIQkYM

dPyV3fHctJQk/N9lTxjvlWTDIgK75Zci0mNuY+CiBMIiba/V0JHCw3wCGGWHI9+DU8BXEjjsbGPJEunCJyCnYonR2Ix26BN9ssMSjF20JH3eo6ADzxO8TQpjzmPdyAbCAWM8dUdjFpUMIheUImIFwma11CP4Cc8NaZR0I1GikmCCwseU/xLE5buCx5SQ/MTlS8MFrPJgNHwrfdwJLD1wBFyVZAKQYcCTaZXAkoXAHKMilNCTZ8AMEj20YJLE5Vw9

8ZSQk2fBok3vEoiT9gmF5TCS68M0fTxhtcNQkqiTYJI2w59j5vRfEL8S1ggQ9Zvc2ZWAkktAoSPqlSwDmCGJ/TE1eJKJw9ohLY0IVOgI52JEIUSSiB22EtN8ArAQ4vVCd5UcAtYJ4fx3lZPDRiDdQmpCgRChlNST2iBxQ3+YT5V0wp5j2iBjQ3uoo32l46dQZj0DlZWVag0nErc8ANwLQicSqnwCCGjj3SE4iAcToAJVwBjjF1yjApMCC+OTzS48

eziGIKOsOhJVwDjiv7UJE5tMsgx44+JDERKiklK9ZuwFKaxiRgnn43K8UFUbvFXAUpMSk4sS/hMrBbdcQlTW9L1d8xK2ogxh/jwkIHdcrUC5sLMSAN3E42dC053TEs9dYTwvXXc4r11zYlXBz1y/IKygfCxTYhTiGKCrQ0ig5N1mQmPMjzhaQLE8KzFqEsBdH12GkwOwpG2XUdAJMyJPpTTibwHlxC8ii7w/XVbwSTxvOS4lsKhVwXTjrzm84QfD

WAkpPQxZjOOF6Nis3/CM4t7tunUpjYdEzOKgEsQgKd2AzLGw2TxbtYF1B2Kekz85TcUw3c+cYilHE96STcQw3H85vpOzJJEkGwhboazizcS2sZZ1U9xboCjc3IivgV5jbKUs3WGSSPml3UMMYZMB7Ij44ZL+o+CTrISxsZGS7cU13ExCCd1c4rvNjRWhYyzcSZMY3Y0UCJJboSmSsVSdg62CRcNisOmTT0zCPTGCC0WSxf7xO8ypk9bR2JN7mFvd

tGJZkpjdFvSp/WmTPFhdxUmTnTmJ/f+E6N3Fk7mT6ZNYveFMyj2SQluhiBJ9xOuDjSB7wVWTyPm7tG08nY0tQk1DtZPuvKHs9ZJ6Pd1DxWSxsNWTTZNjjUND6OStkjyZy+MNQy2SdZIevS2wlWVBQvdjO7Rdkk2TWEPOQ5oQjZPyxH2SiyACkwChezjHePLEvcSDkxRDhzk44gOTI5Mo+FJD4pP5KNkpnZONkhOSQ1TKk/KTQcA5k+2SNKFjVM/j

+KFcSXOSx8AnQghA0ljjkwPFCsTHwXaStFkyDHjdvZPTkwKALpJpPVOTA5Mbk43EgCABk83EF+WLkotUMZKc4q+AK5N1kmMYI5Mrkn3Eh5NdklOIguOQuHbZHIPrkqC5SOk1ErMlWPgDY0nsJAnF8XnwNRPSIZeTkuN7VIcYc5MZ8LeTYLkpvEm9TN3y4nuTD5MXk7eSaWGvzez4KuLZWbWSF5Pd8Y+SBlmcQeSxM8GAwabZDpPVEq+SX5JA1HZZ

be2fnA5ZH5M3k3+StRKFgBAsHlnVnHC4i5Mvk5+TwFOw1IPsCCyY1VuT45KDxPqx4+yhWUy5NV17kjaAuC3O7HgssYDk4tjcG5PQUkGApCyZCWrjgrgPktOSyFIiuXngL7T5WT1Br7QnkqOSQYEsLRqA0rgVWVBSx5OtkuZAHCxJLSftxnXrk2hSq5NquIOB6rlagK1YxZK5khjcFZLmQCIt7qE6uGIsZFKAuS695FOlgE/tSoCNQM/BVFIlknmT

nYGv7V7sBWwFDWWTZFPUU1mTKYGf7MfRs4AzWejkhZOJpUcVtGHzILIscm2qDfGT3ImdgeYsG1j6gC+C3/A8U+GS8B2dkUlBhIDsHdeTwZK+kua4Ti3IHZ9CSYGYfddAIlMBkm4ZWByxAYrYOBzBkyASGT3uk0eBobh4HOG53IAJ3Z6S81V3UCQdUbhfWB0gIN2d0J84TpN3UaEs5oEUHAeAh0IMYI6TqlMuk3dQVNmQ2A3Ru8BYUtaT84A2k/aT

R4EJLYwdp8D8UkqTFpIJPWK5d1BM2H6hfGiaePNwdpIHyZf4JlL54SuAGS1cHZksqY3CscZTNJxWUlm5GdzXBGXFQ8C04yZSuCDlLGohv6wSHBZSEsOOU3ZTxOEyHVvJFIAqYUxTKwW2U5aTK4HKHNTYKFFVQCQJDlKWUnZTz0Q6HMzZsuAs2K5TZcSWkvaBz0T6HKa5r+H5qUZSANymkk84pUXdmerZAR3c2B9URGQRU0aS350pkNYdfNg1gJRA

VcExUmaSxpMpkC4dj3DzQRKid2SJU085sVIgMW4dHcHuHM0UT6WpUpFTtCCeHXLAe4GKQBuiSpJZU2aS2VPeHQRoIJBqbXTFeVJJU47Y/h2XLSrYi1hFU0XFMT2JU2lTP0i3LHaAYbhrgL4UeVNlUkaT5VLa2AbZL3DVQWNg2enWDUVSFVIW2CbZ9WEAbL3wZVIxPTVSaVLa2GO4IQH20VMgh7iyDI1S2tggrey4WmGgrQlSNVOmkm1Tp4ApHX+A

qRxEgZySXVPcIfCsBaSbuD6gemNnXENSK7gYrPBhgRDxQH5Si0JjNDogydk7uTBYAnhPpZNTgdgsrDrwXHmXQPNCs1PzkySgYzXZsWKRu8DR8Agg/JIsJbNTR7iDgN0cIq3lQN58Y81rUvTgQx1lQIxYfKGpwx9d2pJ3OTqTLrDSrdlAL9EzrEziS6F7U+E8WpKV2YJRNAgN2NlAogmk4pqT+1PZkbvZZ1OArFlNnJPHU3NDLrFn2H2Ig2Gd2DdT

GpI6kkRZAMQ7HWAkfdjR8NqTD1L7U49TmBH7HYPYu0C3hA9cr1InUnws6wCnIcb5imiumTZCe1OfUrdTmBCweLccHSDogPC9Z103U5qTX1KCUO+AVKzIeeJTk8zA0pdTQiCOrZ8Q83GCwMd4F1KPUjSI2Hn98RuhYuFaIVVCFmHQ069TMNNCIW8dzFza7ELBkd3g0m9SVHmfHdR5RbQH40DTf1PA0gv5oayf2QzVKNKY0hDTHHggneT44NUIEkYI

qNOI0/Ng0JwQOM/A0NME0ydTf9mInTJ53gzj6SsEJNNfUjQ59d0LWS9TzKAw0yTTQDgaebogmnhEZGqSJbGoySScwXnwcA9Tp0IhPMdDMjiseNZ5DnkvU0zTR0OoyUydgRDI2EfAoLx/U2zSJOOoycdBhQRsQMCId2T00+JRONG8nDhBVyCpyXzTHc1ag/TTONArrJhwurCDaDjS3NNqktKdG6wLwfU5m2Rs0mvIklQi0igxSp15UcqcflL808zT

5rg1gKwtW8VAEohU8pJEbSqSZECnrC6AZ625UgDdytN3XV9T1rmAYANBKoHFQHdkGtIqkprTD6wNgQituxmR3TrSCpIEQUaAOkHlnfIhTCBVwQbTs5IEQB+syMEvWc3AOtOG8QE9GtIBCWRBsFhTgYVg0NMyky4oBEH/rSFBcwiAbH5TttMfgtZAKEDSQKg4JKAykpOSrpxO0tBtnnHS8A+BitgYxSsFjtJ00S6dWSiIbO5ArtMhsHK8spPCoJht

/4AJQH5xvtOyvBKSdtLMYDKA9EGEbINB8NJLoV7TtEFGgR5BByCPXVpiLCXh0sxh/p0AtHjZOUJKk9HTwqGMbcFIMUTlIK7TW0MiQ7RB4ZwX2fTjJOMfXaKSucXJ0xStJWAnUCzZ0r3WDWnTIOX+ER5YQhVsZZI8SpLCk+tCzEGibLM44m2Ao9YM+dMePMxBriEnwQyhWnB4LTyT30MCk2Tc+iBJnLtBcm0voZHcQ5NY43Ai6GiqbCLYHcAzUHdk

NdOuPLXS7NGpnR+gp7AmgA3TykM9fdEkcQHigZpsiLjl00tDrdISCThETgja0jNY6OMrBLySYEJmIM0guZw2QOMhnJPOQtySJm0AYL5AE2Di3ZtTYemD0i2U4KC2gLwZulPlQAWSCNJj0gpBqyzNLZZtE4GK4FXBU9JmIRchhKwekDNYQNJPpXPSLjG1ncEBIUB0uPlYc9JtQpnEZiAubY2doVhubGvSbkIaQ2PTt4E6YY3Aqmmapc9jo9Nr0sBD

nWDNIDRdSUDIUC1YVcAckkQx/m3egQFsK6Eg6SsEJ9MSQeFsfmEL3POcDlIX0oeYa531QAphcoDkvdohSOOhQkJ81KG7nWLw5cH0SZBFpsP30oBtD9OnnFOBZ5yLWZQVLJPbYIOURDGWiLyBqYBp8MfiLJNPgpWVjVMW9bedvaFPwPedlBRMkxJB/9P4YA1YksBLQEAyh5mPnFhgxYFGDBiFyehL4oNAouDZbcB8o9I5IDS99JNQMgER0DMQMvSS

45FlEyFIn5yqaZqBHkE/06NwCDLsDAIQv5zW8ChxMBnUkrM5A41OY7qBiUFCne+4o6myIINoUzkzoIgz341Vbdgz5Vk4M9ogVJMhSeBd2vEQXIUt/CBpQk1CouDQXH29zW2agYkN5JJlQqLg8FwSiZQJ4rH1IE99pH0vQLlgeYA6uChcPAxEkxJDe5Q8mLlgOriegPNAGF34kwD0hk3zgZ04eFwFIUud1wn4kh99mHUcMlhdnDMkoTtdXeMEkyNt

eeBIY+PB5q2UFHiSAjLQOU4swcAeINAgKgnfYsk09jAkXe+BTi0T4sAgV8OYkqLg5F0DsCLYU8gYhDCRcWO5+cTNPpzJsLNRGhlyMiiTIUkyMlSBl/lKMmxh/YJq9BIz4oCyM6ozQsNe5EiStiHZsfqAkZ00XcnEkmAIkq4g1F0/QQ9AerAkCFQCCRMiEAYyujK3GHozXuQwks94JjI0XKYyRjLNwi2MaVn+8afADF2+EJBhToUdwtwxdFzWMl3I

FCACCcSkQIxondllVjL9bFXY/4COM0CTZYGrwEkcxcEc4YzCFhMiEExd7jLI083iwsJ/EyIRrFzOANQQYzHElZ8TvjIkU34zmiH+M46irxMiEJxdqcEiNJu41wSPEi2MoTJubIlhfzgKwnsiipgRM2E8/GjAiL9Y1wTGYt/CctA0MdFJ29CHEtZ0riACXeiQiTJIvHXd7bRWgLaARUEaCLeh6OW1tPPlaTNnCAggdBEZMlZiGwQtjcky8UichQ6T

mTKlgvNZq/WROHEz7g0lgq4hhTLqabEy3GHFMiF1ITOryaEzkTLhffIMVYIxM3ggkTISoFEzaRO29ekThuMZE8SixuISg+CMdfFx4UgB8AB2Aa1kpBKz9aTAZqCEAbYAZqGMwFoAXgGh4N5d36JQDdU8yPG7gDXAboAKwUY5fiJ1xd6c2EDQYGicmIyVoIZSd4BGUj7JTo05kn2J4sAIEkvdIAGAI72ioDwsEmA9BoPco5BjfuOtE+wSNtxdYpwS

sGKdE1wTcSK9YhaDniK8EqzNjU05BfU56xDDPVOj8INlRWxBDyGhzf28Gw32gsgiQxJe3KxBk6yx4mMEceOjEvKiSqIzYmyMhJSHM0b9MBW5+VISuNWJ4lX5iaKvTAaSwgO2dZz9+DUWY/y9pMI/TC1cjVnXM8Z9EuSTEVd5nyMMITvAvhPY/B+hbKKn+Z6C400Tgi0V0xRKA+uiW4JBo0UjJmJ1wizgIWPQA2ZjYROJEn3MKW2oIVfQJz37Avw8

6sgtIwokmKLZ/XPC1SP6bPWDIIiPRQXiwH0hBPvcRPxajC5jNgVMMjo0E8MgNdJCiHxjwt6jckONQlpAjukeY1cTNv2VQq7pgdjXhNijVyHMkm2TPuk0sb7oaQjIsjeEKLNvWN5N1+BcYf79GTQnfcPpE+j9aap8e6PMuM1Cp10E9KeNHxOJFb3TgQLawieVE33EQuN9vzzk7dXia0KUQ7JDEzIFjL/41eLOKHXNXWBkiPtB+B2bwrXdu1OVkKbT

TAV0s/PIFNOYQcmTU8wHyVNVN8m/QOUURAOtlY9gf+IzzVohQvCN4qWIRf0+7D6Su5MhkjGD3EPIqK2SWTJqTXjEN2CoEjHt/Iig9dvcWkxNiPTciLmCQPODoUloExtQWuPM+QBFvkI4vWXs35PV7LZsUB1j47Zh4+O9hLwCbex9Ye5hozBOQ2lDA+zI1H+hl0Gn7JVCyUJIs8PsAiGqgi1TGPE1QkmAaLOe6HPtOiFoLDPtH4NeIe5MnugapTgs

3LjzQFi5hF0G4fDiq+1pWa/gjUGfEVbhHZMcaVUxlC1WUDq53oFsQfeCchCZJBaz/6TULFazFWV6Q7Lt+kJ0LBhS9Cyvtavi+kNr44wt0FnfZYGdWmSy7Ky8SWMBKfvsj7H5bQYtxihNlBy9EoCZJZVZL3AB8DUTBvHsvRviRUHsLf4CEqHQGAfpTUNes/6y1yJENJ+0IbUboNHZpvD9kz3T/C2ryN+9QcAzUOHjBEKd0pt8s4kUUlpNoiy1Cbvj

EENE4+IsBrj37M3A9CGm8L1DR+LUcDEAtoAyLM/sw1liQ6fiuMj+fTmAjFNAYanBdDM8Q2wQOCGZspe5v+2W020p44B5KH7SwdJZ0jTggBwLWIQzrcBTQyq9Nu134+AdPFkQHIIsMUUEWSKQD+MBEWDTpYAwHV5AsB1erVfQepPEoJTjz+O2MPYtvXg6cJLBq5IsshPNDHHzuaJSK9M/ic/AlF1xPK2ybuy/42/haB27GReTJmmTVVbx081GvCQl

riwXWUG5cwkrwI6TgBICaVuAuB0wEWG5s4FRpBmADFnDs2adDVjQbaOy8oFjshKg5r3pPBa8R8wDgIQc2kBEHG2RM7PM48vNC4G5Wb9AkEUPkMCJg4m2vFrT4BNLs/3xJBzOAV6AnUmWvIAhVr12vEHx31gTJCI4UyD/fdASge2Ovb9SDBzqU92BMILkgBmBkBNLVQuBkSzxuWA5miz+QSeyQe2ns1QcUNm6U0Zs+5Ke8EtUl7OM4LEsdBzw2b4Q

CwjwE+MzdEH4010wIzPI2IyIALnFk/AST7MzU+oZz7JMHR4Mj7IMIW+zHCMlo+m99TN5PDFN8lU8IqHgKUw4AY0ArMA4ACgA+wDswPiBpMDswKzBqxXWANahtgGUAZ0MxRNdpRnkanGNoTfs/6Lu3X4jDBzBwW4A5yG2uQZU/9jtJfGs8wmRbb9D9ELrQ8XTHKKtYuBjVQU3FP2i1EXQtI8UVUyQPNEjYIPzMh0TnBPdY4szPWLZqJDDkqndEk7d

KfSPsf196zNlRN74KfW4eFecQ2JIg0gi6fU7MphjZ42oI/szj/WTY4eFf8RTE8Vc0YIHec5EpFXUcoTcMVVl+SxSdHJ6zBrNAuls6VuBSqRKzDRylyPcA0Y9dHIv1fZJIOXjE3rNuhIOoj/FjHKsc5fUkYUwze5QfPyn1XjsoROWAi9jy/1Qo9yNxmkjce+9XHW8afvCBnFCXHoDyv2t4yr97/RDmPFicAO7wJ4FWmAzIxHELUPEvVsjPhOLzFV9

BenV6ftdOsJVM9Y8PkL7fUkt3SLoNfPJnULXvCZj0OwymAbteSk0sjHsSKzOkrblS5JUWCKTEtFhQBOyrIgjsonoOxJ+ggHsQoGsQO0h0dkFMNzC4e1IU1jgNpQmePUJWBKYEoG9HJN09PUJh4iM8EjRstxaDUXj0gSTYXzcEvk1ePcQtxPPlNqYgCw5QfLBIJ1JlCXjyLInAQ1YUNR4LJRBoFPOlNRC7nIj7BeBGrK0XCSTXLgKxYayBCDIGfuj

1szUsg6yeVluAfQsIQD9tNCjlMgmaE0jmAnn7E6lfBAmnNQV7flHUqNYekFM+QoswkDzlMcD+VSsMSAcK1gfU9CQzeKtuO2zZIlcif1g6Ak4o6NI87N+LZcIViQCsqkzyKHBnVkDdB28gk4g/DOT0/Icwhx3QakhOgkRzH04/eJmeKB5mhxmU42gaWOjccrheL2j4jVxcVLsDOdSr73QRBBFtIXP0+Yd2VJHLPpV0xGT41sIdVOwQcCIrUBWJKBj

YdKU4IkcfmCKqByBYyPWQvuDs+ODsASsH1WIbPFB0xx6svPj1AmrUvSh9R0IMTrx6PCu5May07HbU+KtSOlOQdMRZrLhUvOwV1PN2NdSeKxWIINyNlkD2RxZQJnTwfTDOM3qMGvi7rOmlJasP1NL2QLw0zHZsdYg3rKb40Lhrq0FBL2c4YiOaP6zvoHes0Lhfq3e2fCx0MKIVNiJ2+ISYCgT87W/HIx5r9nNzOtz80Abc3vSoa3IgR/Y3cmf2I5p

RLKJs/cIUa1jqaigzEgJsstDNbMY0EdzP9nRrAdyhEKKQ4dyeNKIcwUFBTDYQ9BCEyORrZdyoJ2IctdzanI4E5dC8txlow0y5aPG4k0yoeCEATHhceAQACgA9gCEAXJw7MGMwKzABgD2AATAOABEE40BNwHiAa75EHO/NfB1YEA5sOjAHsnAwfgdEiPQIBVBQcDJPN6073EyI06MroIAg2bdUQLTM9ECrBIDoy0SUGJzMtBi0yntEyoiI6K+jZ0S

wePqI5wUKzOO3KszOgnMmFHjyGOhwBHjPnET6R5ZqSJII3oiGGL0jF7cMkETM3syAkVLo8Yjy6PA7PM82rRrY/QjpQOnZXIzzhTyYnc0rsLgFHITrhKXQ3l0eWMZvE9zmRMxTVkSJADF0IQAOgA6AcdxjMGYAczB7ACswGByKADWmB9yNWjbbIcgkNjeINzh/2FkRX4i58CB7GtoD+xaIu9xJyGQ2GKhbBE9ICBjX3F84xHt/OJgYubdkPOAwu1i

GHIQPJhzoINtE1hzCQMwYgKj8PK4cl0TY6J8Ism1YTFntYg9qbXB0isNyckOhTOJgGzoYjzNmPOoPVjzJxUUcrjzceJ482jDAd2WwwyEU2LvWMDtaMMq80WI3HMscvRzKqOnMrM9gd2eSE9NhZKE8uxyuTJJJNRz3HIa8tGjVyJSVOW1/s0fXRqjduXUVRv8T6VG8jRSOvN68+bDA+JtOJxyTHIh3YdYqvIvZTryJPMmqHrz6vMzYonjMz348oWi

lCPKo5O8M73GXGf9fJQjI2MicY3y8O3c47Su88rw0+VVXLZiZ+3J4h312DUsdM4MogO7EpJyxvxndC50UyPqkzDUl3UtXLoTZnVj/G8NQ01tgqehNzLowqB8rnxtXRjDVpKefI1IEfOHze+D8pTqSfakUfIeDO6kamO6LenjePz9XPwlspPKAlMCQZL1FX4SSfKvMsXD0SxKc3D8o12J8y8zZgIfMhnzXN2E7dYCWfPWNOETkRI58tK0DcNWlY0l

F4GwLEsSlO0oQK0ls1yF8nKTPzLFTZml95y3THw0k9VdyLUJvA0l86cC6jMAsinzGfKA/dFjinOiAls9yE3yM0ktYX2sfelCBugl8ynyyk0gs2Asw/0AfMGVIyUhlHnysH1QfdkMkFT0gM3zNfPP/Owzl5QcMt3zWfJ6/JWSkkLEknIthfKBNMWCxHxGLI3z+UN1Q2hs5fKYVa5N8LI1833z9k2Is+wxFUJXI3XzSnLDjDZDfc2PMvFw+FV5lAic

sfMlggZCE8i6zfHyvBEf0y8BrJPB86z9mWEv0iRU6c3mkviJ+LPNc+z82326EO18Q9IMNAHz7RkHctKNW/PFzBdzpLNicgYD5LM0Q71D+uTu88y5KbKivW6d9vOm7QvIXFRLyGKyF/0GkgNCpzlfQHxVAUAic47z7RgMsuLM9/Lq8ybNc3xMsgKMR/y25VtTvI0i/cy5OnMu7cbz+/0xIQ5TLLMuQayzxpK4XLbkNFmbgSjR8VWug8JiGQkg3cjw

hEUmE2HysDHg3S5BENxi+FHdYUESU7uTEdwx3JyJ+5MI3AmTYApQ3ciohZOh3B9dUez8sx4M8yLYMTzzn0CZbN0C1WGCsvyIO7VJjNksgrOnkr68aBIy3RxiBDEU3e6g6IEV0338CHzVYOKILKOFMR0iPsLyA1gLMLnYC43BOAvfM7/82DA03BIwtN37nRsTZ2Cis4e1vh1kPF1z2lly4r6hZ+mgQB6SwMyPzAXtiuOWrFQKRyLKJRKznN3efPdE

0rIs0DKzX8xTw36SyiVS3OiJ0tyNIuICyiVN7GGRB0AjgVncvIMLkiG4be3GpZ1yQ4CcC0M0n3VA1TFAVmxp9ZMlIaUPwHZBIFMec6RhA7C53XMkvAPQLPDVKrOYQUdjA+1Y1SZV+NShkmQI6rP7gSPsPnJs9JOC0UB2QePtXq02ZSrt1EzSCuPsiHQKC+Swigs/1E8SyiTT7FwhEtCxDf6i95QhuXPsZdmapIN9vmNcAxsR8FI8QA5Q/3xkkgH9

VTBL7dyALVj6cQRhIJMkLAK4qFPy6fUUdjOL7SYK2VizdKDITAOEZRsQNrJb7OXYMIF1/YFz07kvtZhStgtVMXQtQXOOsmGCHD0bELvsRtGBnPR9AL077FK4B+yes63113XRDT0JPrNSQa3AYyyw0R4Ku3KSuART6UFikDVAvfl8NJclAbPBtCq5/7TD3IEK5+wkUiAgpFLNbfBNcQwEoNfsnViWudGyPYM8PDm4cbKiLAdRzMnHopOJd+29WSIg

onxxC3Sh+rh7xUmyfViifCI1TIDPdO/ihXBP7ENZCsg/fXD0M90q9W/h8iwocYOBKNHK9ZkLz3VZCha5+4DiwLdRKYSYkivdb+GsU79BGEiFHXmTYjNpDdNDc1g2uAWztrk5YPmSkPWpsiWyjriLWZJ9hkVCQ+FDISjxc9K4VdJ2Arvdb+D1C1xSxC15Q7OCFbKLWONtlbKBksDjeQy98v4hvYG8Us4o+oEmeO0Lv8HsMx0Lb+G1swUERtj1s4UM

EUw+adYtOvEC8eJQsYnBTEUNEU22MYMLNkD+ILBEdgIYfb2A9ixTuY7sHZFeQ8M5b+GiUtywNkF+uTlgVDPzuD2y3iFOLdoLsrMFg5OzA7JBuEoywcA1kr5NXTArC33Yl1iUs/lkAiDWiUEB7SGnQLgd11nYHLwgjk0QwZvN2woK46rNclJjs5Ahqz1Q48bS0zmM4alyj1iiBdrQJSDQ4ycLXTDLszKB9lmROAeNzZK0YgwdSlJiULUz5ekWQ/ST

C4CikR8QEqANuA3l9wsIM3akR7NikIkzOuHRQs5ho0hns2BB8bnnsziBvXOqzDpSHDBiEcphD9LfChhxd7Nw2IZcuEhngq1UtB2Zc/eygIv1Q3FYrJM4IxlyH7KjM2VlZj29qQuBplPo2A+AYSxms7/TEIpgigMxbB2yaNfMMUUG4Ovy/kzweNZTDyGoIUMgXrKOQqYp2SwwwWR4qoLAeSiLynOeQvktWbghM2Wx2/NuQ0UtToDwYEN5wMGCsVvi

OIoq7dy8WnjOUuIdFS2BnbvjAvBPtBiT8hzVLVIduEE1LDGz8wgJUU5AjoD/4e5T9SxyHYOT5dNDkoYhPZKFuOTY3cgrwbhY+DMgQwhYP0L0iqB4PlOYMPezgRO4Q7s5dIrY4shxrIp04XDY7IuW8MXTQPjIcWod8FGvgV9APEM8i/8SAzGaHUEzGEkxcyhZa0M/tetC/+EBUlLQLNmjk4D5oorAyKFTeCB9WHBBYkKDQg3NbOGjLfEcHNktQYmk

ubLiQwNVsotUEucgZh320YWzQdOTksWzxhOTLYDzlhwhQDOTBjIq0wtT5h2zLCZAf4GJYT5YU0PC0yE8zmjWHWNyCiyWLGE94tP002zgBorw0zAjJnkI0+E9iFPy4HvofWCqwOwhitmh3A2y5vGU4qssjhwcMXBhgixjVU/iS1Ix1LaKyoDUoXaK50KYrRFTZpNs4I6LK7NOin2zrlPBU3mDpSTJUmogKVPDgCzpXlO04p6Lpbki2ChRG6CLID6L

HorOaelSgtLVuQbwAYr0s38jgYtVuZWhkHxrk/Tjp7x1uRg5wLUaiz2J1pL04m85bOERi+/SUtiBwya8qlOpPGa9pSSxi5LZUkFxiv5Bm5MJinUy96I/s0Sj5PL5Ylm8JuN/sioBM8SgAM61KgHOETcA7BWwAOzB4MEGoUgBtgBOEe8lf3M/oq2EYdh4LMQxcqV7rV/D7dmumNbwbWGRweV56wsXWMG54QNJRV3iDiB88pDyh8XTM1Dz7WM8o4Oj

/uOdY8LygeMLMqLziVz1TUsynbyQDEjzAYyrM7oglArwgifwkvLioj75YQGmXGM9GPPbM2RzDoJe3JupwxPe3dhjE2M4Y4rzLoLFA1Rz+fVMDdIT0TiztRbyPHNORVHFxTjjIo/z56LPpYf9hvNR7QUy9QLP8lcz+xNK/Q+dQfOV3POKxGNOfOKUi4ueEn9NkpR4g12C+n3bSGHz4/36E59VPyLriloCoYSKY1lzHw3yc9q02KUFwqfNEfKp8/Q9

YN0I/Ua171zrXGKt2fKtLZsD0PwrAwETm9RUswFz/XCSkkJyi9wfofmpF4qCfIvVg3jXi/8z+8PdyCQLjcI69GEShArM7WejSThwrce9Psy0TJzsusz3i2FDwrMm6WKSEH3tCu11oGwMbN+tsH398swy7G0XE2BsuUOlQjGsKcLfi8V9mjxfi2nD9a3tQ2S8ghWpEikStNge6VqzGEh8kxsjkwIXfcFgS/KXEZmja/Mwi6CLJzHQSvFwiIphQtsj

fJMNWbNymIvtlEcTj4Lb8r95c7SdsjqwzArDfK3SsbInE0KDJLP9fOhClxByY9ndpWGn8lRDGEucC319BuyZs4RApugSC43N1/PMIWc4x0NnE7uLUdNsgKbSg+Q8CKIKp0PS0mdD1ZG2csnzXhWPYE/zTJNiYhRLpWAv8s1xhEuPYG/yE3PkSik5+8nXyV2zJkMkSoILpEsA3P2ya9nJ7JmNoZNzzIAT+nKTs5cS+dw3YUAKLUD/olyVYTU8Sjyy

bOK8sugI/EpGcuxVKN08U48SiP1hQNAL8ZQPErAwrZI2lRoLRfgZCBJKXJRnYlJKyBL84+T5huXSS+JLMkq887JKXxILwtGSKApiWKgLQrPEk5z0QI3IqRZyF82WcueVXcMLw2KJ4uPCiRKJ/1CKSv3DMaTVYEQKJe2BWDpLDTRKStVgpAquQZfz6pX1JfnsFAvbwJQLtLKAkzXCkOiK4rriyoF/EuZLRewaIO+TWuKV8hdjdENeKBriDnKwVLZL

Zgr2c9KyLnMys/5ztTWFOTz9JlixAE5KTArok0nChY3MCk6hv83VkcstKJPuS6iSJTDOcoFAHCAojCFyiZJ2QNwLP2A8CsM0jqEMApNhfAukuROBt5TNcT4KQwnuc5xJHlj4YCIK9xFhSsqyfewqsruJG5Xd3cVM4UvwLZIKPYCxSx3c1RSTYPFK+NQJSvcQaZJILeqzMguBWLRdKUrKJfIKo/CT7B2UFfPohdqz0yHT7K9YAfDzlVlK3oRqCmy4

QpE+WJmQ+4B5So9i2UoEoboKPLiuHU5iuGEBC5PU5gomsnyJR9L1nP3cIQsGC+YKgrmmCugJ6UvE0NYKlrI2CiRLVUvlS7YLGFLBcgCjZUoAstdMLCwus7QZS1xHo7L8zgtuCx6zrcGesilKx/y+C5gJPrJUQQRFF5Krld1KObi9S3xYKYlFcuOVynxRcjaAfgq4QA24QK19lZd9VTGhs0EK4bNDS7Xz3CyhC58tGrld0ZNLGZPDS1q5kbKRCtGz

J82Hwjd8kbPauTEKymBclIkLR+wxC5RSbpj3EbXDGxDxCpIsCQqm6etLb+DpCzIsGbLrSifDML15C6mACi0DIIotCXO7SlJz8pjZsrukKeiHSg3zvYDFCxaBW8BybSdKT4ofYjcYZ0purSUKh0rSMkUKrDH5snddBbIcS4UK4j3K0NUKNwkYOXQzfzXNdWI8b3Vxc5W59EFNCxXsu0o3Sg9LtjAQHa0LncCBks9KH0svS8rRnQt48EGJhuX3Sz9L

tjB9CtdVsB3TEZUKGvVv4dYsHYU2LESIViDAyj9jSB1lgM2yPqAts2DLpQryTWUKUYCzCn65NkVAytDKtYwwyymAsMrSEWhA0oyNCmgc+PjDgQOxeoHaC66hRZOM4JWLg7OrClYh1YoIymjYGMqrCpsLyCHcMtWCZPI33W/JV0MNZPgTDiLXifAB6ADYAbYA1qCWoRrclqHpAHgBqgAVPdYAaQHOEaqJ8wCUE4/EFrKB8WOkHSms8jKB6UBEQb6B

UVlB9ETcboDE3YrgiCiYhBDzciOocxNlF2388+hyPXX1iv7ifKMYc0SNjYoLMyLyiV1mgi2KeHLQIn9ybYtPbZaDKcGegLGRZEWo8csM8CIbMmkDpMigBboiOLUrhZQN6SKYYmogEiJiEgLNCvIHMvHicT2SErFj4qQjiwMj4RTJHeOK9mPt3MczGuWP5J7zSssPKJ51+fR0Y7hjmAstgurK+aLqAwcMxwXyoq/lbGKIZI44jqUQhTHyDh3cY4Ik

kh3KYwKDi/w/Es4dRcIHii4SzVUyYoETSdVpfETsrhOtHaXU3xFmlNs5U1yCc7l9TcPI0I0kfNMF81qSsRLF8u3JxJx2za3JdpXF84fzmijL1DeL95wize+NaRU2S9MEHEJ9+LPslqMcfRJM7Uoey2f972OkXfcNfUypNA3z35zaElb0TfNsfMuLzDVvWeQRfpUBnXrdQcruDAx8XoHBlfVgZkuIXMHKoFRvlGL91V3CdSizPeM98hGVijRhywNN

xk2VkwPywmI1XDCy2H2r8s/9qFVFQ2hsq4vm/GQy8LO7A2nLzuhyIGMgc5QwwKqSuZUplZOU42A5y8bgY5GZlfPy/317iprkCxIJ6FBLh11L8wUiOLL7QH/SA10vIzLtvZVkbOYStkP/gzY8BLMLvEXLipIf80vS8xPlygfzMbO8kwvz5wKWE+t8TFWWXH4tzTGVy1fJV1wuKddcs3Kly+fyQ+PqgqMlCpL1yppynctcVUZKg/JV8viIvFQ38vLA

t/J98znzd/KW08qT22FsLWnzFEuXOZRL4ukLCP+x7hOHQzjTqNInit/Q2YATy8/zi1O0oFBVU8vGgCgzH+PnQptCE3MZaQax3mjqED/zgNxhkcnti8vCDPs4//KqUqDddUG6gbDMwg2ZaWvKsDH/8wb4SoHqbDAyxfC8S7nSkNz7vUWj/Ev+kwJKsNz9Az6CN2ACUyZ4z4vb5aJK5ZLkU0C5u8vG5VJKl8thQPAK1YH3navLW8qQ6YzL/NDrsWKc

t8qGsLyIguNE3ffKHGPRgV5pt8oPc2TzN9wEywV15aKkopmKD93iAGagZqDWoJIAYAAaAZJwz6LOqFJxMACWocdwfMRM87wQLtDqQX4sjVQfQ8wcuK0iINfwG8SyxHHFtRN5EdqKWoE6ijCBPQWTM2Bj4GL88r7jESPQ87My7BKw8o5U2HNw8x0SzYq8ytwTLYr2Ae0F/Mp8E5iN5IGD8FsyyfVGOBoUdXX6DCJRpHKY8jsyfYqYYmchIKWb4AOL

IxLIwjLKQ4rayngjThOw4/vyKeMXaRvyFY1rYq3LDsQpPa3yyyJY+IZiigJCPQTzuCKEFdtj7z0p7T59CrXdxVUi7xiHPXnFtSOMK89FksIe/Mwr69R2cmlUrCpRwwiyTvLCXBGSmgvGvU7z08NkkvQim6IfE2tg6tO8PA9iQWOLfDQi1sykyY7x+j0VjK4KPOWUKjTld2PJPcIqB3yiKvXjlpA+M0LNS2N5wrn8pCNbSqQqKWPffaniWMt+PA9j

3QvJgl1z5hWD4/r9qeIlcoLsYEQSKy5DawoO8vGMSZWp4vb9qeMz4978c0q4YnDiS41A438KO2KSMM+DtXyN2E6y9rOiuaJFS3JFzJy9+DwRs4SLQnQnc63SmOLEQlhLhEOiRLhLtEP4PNnSPj1WK67SbNyE4lfiROKnc6jjUSllsl3MRSJhPNTSiNLmi2rU1oukWY2yO2NU4hdDUPh04l2z+rya4g9jbEoe7YDydvIpPCmKPdHa4iAT5rxekjpD

b2IgEmuyfuzcs6mMKTxiSn4qxfHXyt69P2MvYxsZiAu+vTz9ASrF8WpLAbzkPHmja2JXkrC5wbw3zSErobz4+fJY95KE+PErEbwk+XfNt5FYyt7Cm6PkCzOJMb3xvHri0BIWS0/MelgE8pujb5PF7KvTf+Xq4/ZzzWLxKq5Ln8w17ZVyG2IPY6LdSOhkidO4+StN7YrZzexTc3SUxj1/VKAsgFPQGPkrfAvA1C5YrUrlKxWN4Upd7ZAsGSvlKmIL

fexhc5EruNSQU/FK88qpK1IrG1Dec8gt2UC5KxtjGUsT7Fa5YSuFo6KI0+2RWQ+AW8ALRIQVjqGxWOy58+yZUzUra2KGeElZCFMyXL0rMJX8uWlYmOnL7PEr/LmkLGvs5C1J3LQq9UpcndQs9SsVjJOBDrKOCqPxYyvOC6NRStPWyicpkrnksO4LICA1QWMqXgtVWQq5QSsfY548x+0cLMgsp+1jKp+1JiDb2a+A77OFKsY8G624ScHRCCEWs2Mr

q0oSMLq50yqDKxtL9+zf4Z0rDvJpsoUdT+2I0MNZu2PyLb/AB0rCQBcq+QoqLZa5suKsUt3wX+ywRN/sBirlCnLUYqGAXNLjtYAls6oVp5TaKkQrpYBNC2sBHqPkPZ9LJi3VwDPzBzO1gb9LFi2SK6elngEvgTAc/QpPcbtjIMoNQQgdSuOdgZMKb7EHWbti7bLOLTNR10WuLMuJbiyorLjjn4BSU14t0lKUPYcK07L4HY4rc7IPWfOy/iyLWddF

SlNBLcYMWbKvKs9Yjws4QL9ZjKCjUjtjAsFxuaDZVOGDc2rVAsG7GVBhA7A0HddF/wtdaEJpLyrEK4jYRkEPgSMyKNhPK8wc4qwY2UOA9iswlEWBwDkpLPRBqS1iK2tiWNkfENK4BYHSQdzjZCsE85wctTyZLXzx1Cqbo5wdsdJEYfjYGjw0q/ksghxgLWQiD2JiHCOAwsBdwSIcLKrGPGId5SwuUpUtW6LkijNQFItXSLIquCA0i7IdmyF0qy0q

uQlNLIyLih1wQMIqFKo+U0W4GK1bonyL7Szd7LATG6ICq51Jmhz1gZtlv8BUPQFSc9hTsIUqQkU4RUPAEMHcrdNY8Spc2EYc8oo4OIqrbNimHMqLMUGHRKYUFhxTLeLgZmA9S40rVKHIgHMtUCqgBMrznhWQK3Msuovis5RdliO0Ibqr2qqdUqmLtQ25Y2/Lj3Ppih/LGYsFY40AbfGYATYBBqEIADoAWgBbkcnl4gFMANqJw0FrpYWK9uMywaMs

sQBWsK4xlIAfQ5a8nIHtUqDRwwunFNABbdPEqxxYZZAfoMMNF+gA8oRsHljMnTWLzBO1ilDyAvIcylzKDYucyoLzXMq2VEgqOHKLM82KKCp8y+ojLWjCo/o5DaGKafzRYYyo8msA3rQaFCvSbCwBlVsyeiK9irf0IhPR4uXB211YY7Hj0suUchIS8SpTYwHdzp2NK08NOqrs/btMaavKhfkiNvOKhB3LKqJ5IoWyLzMT8l/kVvNq8qfCzQMzBWSZ

VvK4C4si3HVDInmqmstbYuVcBarFqpZjMRMlq0Wr2av2wm39+avlqhIYpnLh3SejM8I/5KRiECoQsk39Z3lD3AiztxOveA2qqgqiS42qnTjYsuCEaeNPeTLCqAO1qhOKhflYkimiTapV4gAiHkudqi2qTgqXwFzSmxK41UYyCP3tqjWqEYJtw82r3zgZk69jmQz9qzIqParDqo2C/EKpQ0OqbatATS+LWMX1qz2rYUJKTHHTj3i41ADjaLzTq2Or

sctUfHR8d2Sm8wxz2WRSs3ztWvIMc9ryI+KenKPisHDbRNrziaVLC+uDG6urq5urNXNnXUuqa6qaKtuqkKjLq9S8iIktcniqp8ybq9bQqDPzjImix6uAi/S8q6v7qmurZrNMvPurhoQHq66zk3IOU7uqCoso45HdN6vhs/vT/ZOXqkmiCot78gErtuXbq+YpB/KzfOeqV6va8/RDlEJWK3rDp6r9VIqKsosPq+cysr1OKBKTnlK7q6jV36uX4iND

V+MqQqerz6pls7fiE0Ovqo+rpvEE084qCNN3qvaLepKNslwKf6rnM0DoS5Ov45/jm0Lfq1BrUYvMSp4qIGr/q3q9fbLeKhtA0NLgapuT8Yte7FuTH6pAa7NUs7P+Knerf6uwajuSrFlrsun8GqMYasbzDrwxkreyTr3waphq/kAhKrBrOGp84mZye7T4a4RrETGhK/zjxGum8tHtfIkRK0hqOGtka1Er8exdc0eqaGr+veLi180S4oRrZGt3k2ns

yNzPq+eriaVJKyAhR1QpKn5SyGpy42kq8bx57EzElGoHqvriNAvnVXRqB6vZKpzdKuNca9rz+SuMC2cJnJKsa6KJp7VWWc9VGKtgahxrvGqlKkAtP1Rkatxq3Av/VJRBIbJKkgJrG1FVK85ZZ+iaqoxqb6uJpbUq0NVtykRlkmsfwA0qMUoI1ahrjGo0uU0qyUvNKjuKUGokax/BrSqj7W0qYmu8ah0rCgu/qybzwmuyat0rjBA9KpErMmsga6y5

fStYLWfommuJpYMruCy9nfBQOZKmhFzlv/KSuIYLoyseAaoNpmtW5WZrmAgoUsohZCyBEUnc2qLxVZaEm+xULfVK0yuEhebk9msOC3YLjvFai5pTlmt2akVYbUpG0AsrNCxOa25qSyudSuDBw5Oua3DoPIkrKgq51VgJ3GzoDOnMckGAfgqcLPPgjSom5AFr7/h/tfVh3kAHSjsrmdw06CFrLCE7AKEKF+zHnAUyEWq85QFqNoERC85BkQtX8/wM

guixa3NLS0prSvqrfCwxa/joiWrmQMcqybInK5rDCWvv+acrg1g7SipTdVxc6SlrGWsXKuLA/Ip7y8lqFOkxazlq1yqWuXk4WwQZa2yJrFLTWPcrRWrMcxlr+bKPKrospmopa7lwqWulgM8qLVgvKqIJdkDHIiYhNQqcU5QFTQpvYrVqPihikJyBnYAfK0qBX0rXBI1qfYhNa3Vq3ytdC1gJrWrnI9LEvFO/KnWzfypzYiETtWpdaoJSLEEAql9h

h0Sda+xlTWqNgUCqzPHAqtlqxWpAqsgdCWFiUq5BpWsRa52BaBwwnVNsTIATagVrLCCBuG4t29AQq9NqOWsza5CruwuJ0yNqZWoLa7gcRwpnQNprqTP5a/Nrd1GnCguz8KpLaxNrR4GXChGBVwvFuJtqM2pKUhuyylLuodyAOd29akNqA4FKU59Y+2pgasggg2tta1fQu7M/WMJAqKvYhd4obWv84zUL5BxhLBpSQNgHa41rl2unamez6KrbgUJq

J2sXa51qh2ufgD8LWKrUiLPBN2qXanVrp2s4qllyR6sna7dqplP4qoksozKi3I9rg2pXalCLLB3Qiq9rj2pXaikso0Fkqtyx32tsZLdqb2srgXCLlKs3WWUgF2rA669qfWvE4NZSd4DcHGIQ/2s/a1fR9Ku8HQyrKoHxa0xjZyIw6yuBTKrE2NTRNWo/aqdrK4DCHGyru4nmsODr8+HA6xDr04FEihUsmQi3kR1ryOqfarm4ObHVLDyqknmmY+Dr

/2sw6nyqMUT8qscTmsq4IIKqihzUiUKqxOtLi9OAIqqe6VaUJAhw5GKr6h0dLWTroNS4IZKr3SzSqyrC5Opk2DKq/S1byAIJ0OXTgKFT43PDLCaii4jg5YqrcorjLbogrOpriDjIKqtRUphx0VMc6g5IIDDqipYc0y3oiDzr2dPgwVqqOosVwNArwOTLA7QhcVNLLfFSjStM62sI5SwNQXYdS51wcHcS7TEHiCAx4up2HSwzxzCqa6siS/nmiCAw

jh2C2essTOr+GNLr70jJUtpgKW05cFLrZjA2SQyBvovSIX6L5bNRMvLqyutrCKGLGVLghT5o2utXsYmL0SlJikirsMCBo+9JVXMy2PlZstgaYn0DcsIgMEzYPhxUWNlApmNvBb8j3ZinLURBQcHYHBiFhuoW2CVSKtkBHDq5cghywsq1tuq+ucPAmtgyQTbrluungJVSDNWXUR8UDup6Ez9Ijy062AO4jFnu61xzjtm1cobZ9VICCLbrrUlDuSko

jyGXMQGjLuqU4U1TryzRQRoY3upeGaeBHy3RHC1ZMRymKgxhfuqsIO1Sc4HlbT+IT6hB647YcRwKwfm55UCh6z6ElOAArdyALGDTIPRACet9A67Ydlj3nEkc0dgu6qbqjuqp6nO4PVKQSw8Sses/Sf1SC0Hz4ESA4TPZ65k54Kze2WxAeCQLRZHqXtkwHTCtMNF56hnrRML0oMNSnugjU+5QJAlF6kHYKK05HSuJnytHQZXqNdFtKeNS1RGmMpxi

+es46fkc4dm4rT1qCEu2wxnq9KBtcoStnZDc2JXrDer0ocUcm7gx2T2AKeum6/8o5RyUrVSqlRzghZXrNKxZY6+BUzTHeZXr1R0wXYytfeod6t3I5NjixfFQC1JF6yPreJGOi2A5DRyrapHqE+rNHAULPKxqig3rpeofIu3Z4KyqaSxB3TCxQN3rLevVQMq4PyHtHFpdS+pl6nKB61MjwRtShIBr6vPr0lH9pA3RnnC5sKdyGyNvGd3r/jF9ciQh

/XKjC2VRReuLIXKl4sE/IOeBm+o2SZMd1wmHUu/Mg6lK6+ZJK2EHUtOyJUFoiGrrVjB66u3Zsx1V2X5gASti6nXYd+o3CPfqC0TYZI/rcx3V2U/rVnynUvXYSxxFQMVB0Ooo6vTg5R2LHTdZ7+qxy3Rj2WuVal00ixxnU0scP+r5ar/rwWhVau3Yqx0BEGsdDCGOalsjVmpQIN3wKqwgGswi3cw6azk4wBsxidCBEBuqap+rJklDcgGTLdjN65XM

dasrYHAbvzjwGuEM8TkFqnXZiBot2Awh8Bv6qn7LeYkbHc+5mq2p0hZgphVPuRqtcwhXCgEUd1Md2H+AfKGkSpRlUWPZkHgaMDCVYJmQ1iIJYzyUOq0S2LqsL7Tha6C8kyN9I/4xOqxYS2Lh5Bs41dTE8RWETUIhT1OsWbsdiOPu88rLoRV0GrsckiCXqzyNuTLLsO9T37iHHQd1I9ljsuxBFEDAtfqkA/lCIMcdwMAnHZwaNzIBaBZJ3BscG2PZ

ORRyJLklQiFnHeCo5NKimDKUTqpCGuIAU9lj6Fga7yPR89HxesrLsbx56cGCYPRB7SBx8vpJamJ1SVIbl0Hi4DIaOXMBDXhKQHgoUb+DPyETrdUUoguYESats9jVkLpL+4qxhG8zUKlqG4rZ6hqXS+F8pspQyNNyS9lWrIez1hJecwvZ31N6Gr9TRtilpW8AVaUC5ADTa9h3HaNyCOhWylNcuGSCUGvYVNFmG0L1tstrIGzrINMAtRvKO8Gyq6D8

TsqzXQ7KiHm2rXYb+ilG2dd1yUoWSQ8d6UGPHaRKjUsV8pEIbhqsQRf17hraMrDSe9hzHS8cwmjj3LDSx9k62PDTDXLZknyy/hqTcAEbXEUdcCUF/SQ/oGtdmBFI016sqWHerb+9Icq4U74dYpA/WO8c3qw4EOHLbfLEQCMdLYjCYP6skSAvoMQ9Wv2d86BV0coJGtfYk+wBrUkbyjRxyxtdmBF+reasAazQwQnKA/NHlKkaPEBpGkkb6H3TC098

DKFo031k4fDTanVCNQwrIEjJVHiO4jR4yUBPKQ7oQn0FGyPsW3O7iaYos5UNdKrxWVWbcn6BjHiqa/2MOFS+8MvDu3KAnNjTi2qqQtYgBcqhIAvz79h7cuiA+3IduENDvlJ5lS0a+gr/2A1RR3P5QJizxcvzEUv9CDhnctGsHsmL8iXLiP1xrSCdwyUFBMZDcHCwi1lUQxuEgMMaD2p2sqFCr9N/0xjR4JzQ1KA4FZXdkg/TkxtgOVjY7sgwnaIR

UDWb86F4RNLd0MTTUDR1y3/YSxvzGrQj9crACxrZxUGI+ZA4ikG2bJmsMDgH8s3KzWCM8eTlcJwuWfCcJuvtGG3K7FX0gJsaNbI5rF9BFuuVkZxVi8nFwL3LYnmwOKlhSJ3dgVA0/crES3xV8nmIOAWsBr3MuA/z82AYnJQ4B4EKdPTTJbjYnBF5GDjLgB5rNziTyoTTf9hVrfidtyDqEPRLNNN4nL7xKDjzgU7tZVKhIZlx3KwL+W8bXxoMG8y5

P10N2H9cnbKemWF48Xm6efPJy8oOeSvKDNOGeKSdwXmcS8dYG8oYgUIIhnk9IeCbjNKgCyASEN3puWWk0JtBeUZ5MJuHyzuTR8qBky2sZnhElJSd1BtR7KfLqMnOeX8JaYEua1igHFL+o/y4rHgYmr5tfLNEakVBONHUnBWBNJzWWNfLuJrz5F3A9J2ecAydv8DJajeSY3T2kYJV851Em5sy/a0kmvUJd8vYENYgYzUzKmsgitgsnZpKprmk3RgL

jdKmeTzT3oBCQdBgGXJx7TbpuG34C5QCbJxMmiOtRtNhQHpLT6D6SigxnJx5gfSA3Jx46YZL01jRG3K5Huz5gXXVxuRM3PLjZ+idwwLSE4EX9FNwgpvUCxZLxvgC0oKQgtMim8RB+e0640/N3IsGeIKcUAWzrIoaOLkwkeugf6CSIPHMhNEinGuB78BinQwLp8EnwCOARJEi0mVAopzKm6xBP8xOoSFdzZXi3WqabyyrrZKc4UrsCsDVl0EcCigw

otIuWMuJ0kGe050JAUs2QZtkNCE40dKcm6zACryLXAqQ2GIRBaTh1VQUG61E2AJoguCCir3sIUuWmw01ONDynMMgCp0SNfYar81CCo6YkUr6C/q4lGO/IPPcTprwLEZAV7WKaqqypngOmiFBO1mOm6IKKmpD7fabgoEOm96bW+3SC08tREEX9DSbXppumwqcvANILGTQQZoSCfq42UBy0nusn3SMuNEh5eifrQRg4Zq7rICcyYCfdWoL9tJxgSck

Sp0AYMqdEZvZSzkc8ZqLWVPy2oFuQU3Q6p38eLwCWgqC2NoKsNBpspNAtxADIdOL7oElS8CIfywEQIet1/U/iagggRvk0IYLJrOVSiQQ+ZtSUAWbuEizidZrArnZWc8z3gmq0tqcEZVWCjmxFrNTK7azFZs92GrT2p18K0ftz7Tc4f4K9EAEQJWaxJQrwR1LtoCJ6akhQ1ndrcqDWpzNmvWaaphMLK2bQWvLhKrTbYBRIXPYAOEdSgUoy4gUgB2y

TZo9mreR29G9mgSgXgqA6nfTqnz7Jf0lYQgwsDm5I0pMVf4KBEB6nVrTV63jmsq5n7UhtJNKZEBTmlet+p3TmkEK/7Wzm94Jt6wprBaBLkFTS81YYQqfbGRBS5ql8WrRV+zzS3Fq0bMk5UcV8VH5gPrSelNVMHFrUbIroVuaRtN5UEJZm8Wxsm8glFKHKizRhtO7gQea0ONT63EL6KClILpZAyBo9AebcbhnmrOJPVgXmt3Ql5oBCaacEDhvrbPq

NxnSLMDVr+Hi4aHdTPP3Ua+s5pwPm4/U2QrIEeXobOqeABApjvEqLOsBKSu1gIxSpl0FC6kVZtPvgTnS6IGpsj+bsZnbwb/AZtOWnV3IMWCDuFdKJQvnSmRAYiLjMp/S3UDaLeUKd0sVCgRA4FrI2BBb+xshKbdKCVEFs3R8tpwAbA7Sy/SQW/NZ1QqGbL349tJ2naFDqbJvKytZqRSrgWLgVoiQWDhoxi0Vsl9KnypHfBhaIG02PFhaNOHNapAd

UUCRxI6d44BOnUVAnQs6YKSdr0EvcbRBhFsQbBpCW4nbWO5AK6C4QdrwZFrO0uRbTp3EWsm5imicBVRazGBngSlAMIBPtC8bpYBjCh2A3OCMKfRb0Gwe04xbbbJiG35JroCMoMBoDFrbwROBVIpMW7WAiMpzCwCgHjBcWmxb3FrsW4vJsMvgAoI93tMIbUexe8LAbZmBPbOLC8GEwlpzgCJarbkLCqjKHjW0QZpAV4qenGhtywvnWSsLGwpj+dJb

Hp2obfBRk7MLatJSewrSWh6cqGxoWAAa0Gy7CspbGoKCPAHTIpFnQBKtkfHQq3gd8HAeMJpaWG1aWqOyVVI6WuOyIdNe2aIRKay+nZOy87O2gBBp5JrenbhtRltLncZacKsmWspBplsh08Fo3quBEeuzSMH2QC5rmRyGW16qlEDMneuyUbh3C8jSwGlWWpa4RG2R8ciqiWFPClWhtEHOW6HTDluM4a5aTwu2RO5ahlvenHhtr6yqWKEtWEFDga8L

7iAeMLhsRls+neZbC4CvCtnhAVu0QbpbciGG7DAbaKqA2Ujo57Pf7e6dKG24Qapbk7MfCpFbKoBRW/dZumvCWm6dkfCxWyDAcVpj+WRalkE0WlQdcbifC5FaJBEoWwBtiFpUHFiqulPKYffNQQKGiGEAIFuXs5lavwon2DnCf5qfrKYg35uYqzpTeVrw0gRBd5svmyDBr5vUQM9qWVr5WgRAetI7mwPx+tO5W0VbUNnFW2ubM4DLmziQ1Vs/CjVb

17K1mmOavZo1Kxly5VrFWw1bPKAlm/bhUJCFmmjZzVoNWtlaMZuJmz/ZzIIdWteynVpmmgrA5pq2mkHV3VtZW2GbBps6mkaaHwpXs+VbNVqE0TKas62K4b9A9VtXsgNb4pv8m4LSoprjW8NbLVrkZYybw61S4cya5B39WhVaKDAc07Saa0kxWsNaLVqdWvibXa3QMRHqgSzzWiNaIsgUnSibba07s2tb01pReZ6ZOnnheE3imVvVWj1bWVV/GxQ5

/xoYcFta2VrYnICtGJwPG1Nay1tZVKicVOS3GodbS1sdW1lUextbGrBb6hmHW1lVUxqQLdMbJ1sXWlIgYxpXc+MbENh5W3db6BFY0u0bTRvfChdbe1t32IUbD9kl4CQk72vAi0mj2lmpG/6teRsLgR9bAIufW+Eb7xyRGneztBwAi7iriAUEeHDT0GEPYcyC4Ioo2f9TiHjIMlCbzhuQil9rhlKg2oh4Vhu3HRgKENqMHQSrL7IWSHoaVq1GGjDb

SNiw2yZC9CG9Muoa0qD5JSDbsNpSG0B5yhsKG6NJKNuI2kdsPGjiG5HwGNv0CPwaY9kiIPjqQdTY229T3hwHHEPZInmM4FCKrSA7wERBLrBUGvoM1Bs7skTaDuDE2hWbK2BEGvdT+Bt2pWTbB2xEgJYLsBsAYJsdmBtY2ujZRNupHTTaiBrN2XAaaBtU2/Ta5NsM2ne44BurHAMh4VrU2s3ANNus28aBbNvQGzljdTJpiuTy78qPopTyStyADGkB

NwBOAKzBOgGqAKABgtqgAGkBBdFycA4A+gHLM7bizaPFE5Bzs3NGnDi8WGLlEzLB9DI0iJQQhl3/3fUFvNlDC0+g5XMnbEVNaJMocoCDrWN9oywSfqpYDRzLMPKdY7DziCv8o6aC9t2Co+ojLEX4csjyHqvxbH0T4+ACExHjIXBmnYMTuCoogtmAk8w48oS1iaqTY0mrqiq285OK7CsP8wTcj+PsmZ+9mvITEmX4ymoscubbTGWgGzJjVtucc37z

6d0qywQLRIMcjUuMsJ3OnZHr6qMyjZ6iwYSOyk8yYMy1S97yihJs/bRKx6juEqprHEv1VLvycXzDwxdVQ52T/GbLMnIdqnsJ5soIG4HatgNBYvxiGz1ni1XjAXN/+XXLqgK1yg4bC93Qo0AEjcvkYsPV8KJ/MoPLefO3itXz3chj8rXzs0p18/ISNerJDBJzElxx2x3y0Wzb3ZpN74od8vXzXOw+BXvcekyp2xna0TUeBEfdIxGKLKpyKo3ZGz+K

0pL5qsUaywuwzLLdGnL3fenK6sI9bTLMGnInG3MQDXMnMG+LXUOpzVoqaK3acxmU7kydc5Ucldp8gsZytdpe6a6TlkM4s/Xp/l1LAhDk/kJhTdXK2mMKwxN8Dcp905Qg1aroSqSyy3wd25brVcxH4mfzqzDd2zhKPdu4SgcTG4s8VKfjwiHwXbotWngNUrbkmShac98QyEo+ol8ju0OnzYrYY9oD2qPLwTzryeLow9qMVTRLug0WeO8AHxszy+cV

/do/IoxUjEvNMDPay8seKqyzBSCT2ovby9tuyYhrHsmr2rlUeOj6cllMI7NJ1MvbEJssiVva3EpskpySsJr88OTaHDB0WlZznf0nyhALwksCUugIJhLny8xS3OPxlafbpnNEUkxtVEo4fMXjpnJevApLrsuOck58GQgRK6gLtJN1uG5zH1NnzLV02BIVqs1xrnIYsxijiexaSiYtn5qztIbpJeLHyRyaCSsh8d6ck0AP2ssgj9p46antfR3aQS1B

rxKY/IZKMuKHtEZLyJ36CgMqyxGCmxQLQkCRyiA6kNV0C58lADt2dI5K4vhq4rz5QpRzfCqaBStOSjpL1nyam4NL9e3vwSxLvCrfE50IvkvgsPYbuxjwOrLCICwAUwqz/UGKshpLiwMOdYMYdptrgFaaXxC+ciBSARARS6BTkUsqS18TWDpBMIprMC2emlKUKwMBmhqzaUrOSriSqUoyC95yZDruSmsCmlOzYFpqKgtkbEnCVDp2StPtPtS5Sx+D

QUpPvdqzsVlZgOxAz5z+S7ESOPRENboKYbmYoCCK6Ahg/BVKDNyVS0YLCUq7AiYLpCymChTbAJBiK1Wbm+0OatvsUUt8OgSgUyrULQI7tUoHAtD9GxDOaphTjvFFS1D96BQtm1+k7UviKvvsnUpUQF1Lk+1SO8TRA0u+s31L4jvJfH2r7oAEUzCCkiH3YAo6lfwEoFsqp2ChIKWIS5UiOxI7IQqrmy1ZYQrdS2yyxBQRCpube5vH6Co6rH0bmklr

x5s2S7I7AShpa8kKpumGOyEp20vpsh0hejsRg3kLhvnZsxLA/Uuxc8d9tjGsUxf0pG3VkcY6kWPjpJBactT54L2lKJizSwgNr4UPIPmyQ4l2rKWzNQrTlGNgXLJvhJe5aFoNC4467jrOO72B+FptCqbpL4X+8Y3jsT29CiRaFiwda547vjqliX470Bzda30Ku1grS+WQXjtBO8rQAKs+IF9hONy+OnjMQTtvhBDLUUACac2zrsuRO047YTpNsmNr

SXI2ZahKEkxhOtE7ytGTaj+ECxsOUWNLbjuBO+46rixyWhsKVYqBOlE76TuM4UpbN1nKWmk6MBjpO1472TvLajCrOlpZO3E6yToYcetq8KtJlHE6fjtFOkNJW2ors3Bhp3wnIKU7UTr5JQiqpB2bs92VoTt5OvE6Q0muWnuyKyEG6ZU62TtdMEezohCjzQ06tTtZOvk7XTGJW58L3+xuOnk6rTp1Otdar1u/CzU7aTqdOmU76hk/WoDbhTulOija

6Nh/aq3Q/TpVOwuBAOsMcfBBxDpJO7U6vTtHGKDr7ByXgalduTtEnT06oHmQ62JZwokn2s1wjTutO59IvB2g0O6g/iE0OnM7nTtHGLlzeIvI8sgYSztjOgMxmOucqu1LqzqgeNyr18Ec0RFzGzr/4STrzSwo0Ks7LTpFOqB4fIujdA4hRAWTOk47/Tpii/4CB1FmUg5ZhuXbO5KKJFOSwYYLYVJHyWc6oyzs2WMsxh26IEM7jTrOabzrUy0aqqE6

PTr7OrMsgupQKkLrE4GXO3s6xzulcte4/iEK2lpA752jO1M7xopvOnvA4anvOz47LztDO3jLxqv4yyarBMv5YhWin8vQAEIj25AEwfABjQBeA9CNsAAoAXw5zMFIAGwUYAGncNtst5ACIc9AnbEwIToIH0JY1EmBAvA4IYNZ6HXta39L7KJEnbeQI8GIDDArfPK+quzLM6Rq2v6qnMqgwsLzgaqa29Xlb+hLMyGrYvLFRGGr8chhkBKIP4TBifi0

Iz3PoINog2I4K7GqEssYYkbaFkAK82iCmDxfKjkjxCt93Zczp6Wpq/g8Wavs4pQqhSNUKvnaHiV4w5Lc22PV2z8rDdu7Yo8ZeWuDER3bBDw72gdiLCqnE0J1xCPnEjErBPO4owSjJyoshS/acKOP2sErwitySwMrHLu4OhbLDvICK/LCiJW+ZHMiZKWCKjeMrUUlXUK7N2KsO7MThGNyyh3d3DueY6K7Ffz6O+5i/mI9g+x8aysxYyQbrmLSKw86

rzt+YlK7gRuYo8MiCsqJYlf8yrrRFJULILMCstMiLvM5YR3iJukdwKq64WWh3XOqocwkCb0jyroVg02MYUntq4rKGxn5cp/87OKrExRjN2QBTSPjoEQbq3ZibvNlQ0wgMESVcsgbxrr+5Jo9JdpuTAa65rtT4iBKGGpw3Xy4h4OHq/xq2WIqyzpDqLIeTfqyiaNY5R7y3DG6K9hq9ruapVayUjEHW9pr7rsZY5+ChitlKpJrjrv1s0YrHLzJ26pq

rrv2um182+I7clpAMmoZYk66ZiqxsrrzfnS8vS+qMEK7Et7yPIt92h+rBgy+85+qBEsyXGG6EeTZxTYrcr2xu950YYGE4m3Mu+q1Xcq99yEOKwZgpmuqyy8bdu0MIJuJSbszi2SgEGoLk9eSmbppQEvaCbvpZO6L9In6vTVd2bsIauvaRr3eKrm68+TDs1xKbIlFux4MilLAPKW7q7LbsuAS2Gquamm6kBO4azAScIDlumOIl9pZKtG6kbqhK/JK

wln5ulW74SsoC6gSwHnea427HuNerJZz0Sss3AW6GBLY+VpLHVm4QTW70oH0awpYyNzJu4m85uzpKuxrXbo64g9o/7G2a+27H8EQOtrjEbtudPqweSpGWOnB/brc+Y5KfkpMCuO7H8D17cUqOUDtWz/rJ4r6sSJqP1UfVZrCs7rqgOJq7e2AUtlqC7v/k05Y1SvSahflddx4O1DUkCzyaundzrkKah6bZRgXwX1ZG7r4hZu6kgsqatm77bTYnBQ6

bSpVoDu62WVP4XQ6USC5Sjy7WqJru10qBUrz7fe1h7r5ZSMrhC3pWRZqF7t8+OMqmQgTKrZr0WtXM5gINrLfST2YW8DXuvq4YjrBcrua+xLLu+TQ8yoQYDxbyxMvuuZAHrIyO6mAAStqy3K4Cbm9Swg6ABrvurDV+FKBsiftnCyZM+20oWtbKwltqJsPauBDxFNLgVFrvCxJMqRxc0p7K/VA+yuNwWB7zkmxa0ebcbKxCslqtW3l3SmApjrnK1lr

asLB8ymAuWoxc3lrsHoqElGAx0vo0VpAUHsqA6WAJWtf7OxSNOtd/SmA1WpAHLhJmHs9/UtZr0qgHIYtWGWv6ymB3jstazh60rCNgQi6m1hEeyLpa1nBO4DLXq1xMgR7PrkQyzE7kMqaq6NEHgBjaqCr42r06zTrR1goylNqGByjRBR6sGFgquhAc2oWgfh6bHLPWVgdXZRO4pmRJHpw7Kx6BToGW5B7tHpYemjZxTuPWK/rLHvPWUjB5TrUoN+a

Z8ryzbtqUbiIqjU77Hv1MGdqDdBlkBoNi9NGYox6z1hHs2EtGlMMe7x7d2tRLG1hwnszas9qdrAvapzZIaKK0XdR/wqVOYjIMUA86mVJDB0I2i+z0kDKewG5v2pTyRjYF+oa5GjZwzqpLEDqanrIYeM6n/ETOsB6MRKhomTZ8zs5LIyr2nqI6wIcSOqkM/J7JqJk2KjqSUBo69HZhntOU2IdtWClIQIV5nvE4Zs60h242i1RboTuU56YshxE6w0t

Vnvk6wyKpOpMitcFWssCq3voKh1RWSM9Dnpk2VTqcoAaHErr2mMyldOBtOtaHeT500UIZahlbdj/NUzZMqu6HGxjIhqpdZ1JzOoGHQqq1xI6y757cIhyixugHiBqZWgaPa2eenBlawhRUtzY3Op3gLrqvnqYZXCJdzoaq8VAmquQZTrLcIiGqs87PlkBe2BkXnri6l87ZXPfO8l6UGWBeyFBpb0S67LrPnqRehl76uoY2IyhDbFnm7FRCXqhe7Qh

myz2kFRBPSsnuqJIsXrgZd3Ylbl0IEGKYYsxetl7JXr665GK+vPtqcV7KXtXsUbqf+z6VOl6iXv5Us25PhwW6+PrEhvKSZIbawlW64oIRIBnINCEnVxNe61IduoBHYKhSdz2pDXolIBO6xrZ84Ga2apjshtfUpzztyx+YPRhREE9e16lvXqe6+SwTyzFwQN7PV362A09dVN1ckbYI3t8YkO5iHgB65EdUgh8YjxjQetoeB2Ea2gh61gJ+soepT9J

Yevu0/MhArlTe8qUBsuO2VHrX9zFQVdaRmDTe8t7P0hx6vbYfywYhdhKYzSKII8hkcGArcnrbxKPDYbLjtmNc4L18yDp6mLD0mNlJI1ykNjl2AXpjvHiGrRLR3vJ8jnqe3MpHbnrloBHetRLBcJe2BCshes+2ZJjRsvcIBkcmoCZHUaaqRkBMqBx2RzB2KitAYFsCCbKoHG164RAQkD16kYzjBP/KY3quKzibT67XuSfe5k5rev1QW3raiBGM30V

67lOgIMwH6HUaSAgnjLoZF1V9uEUrOsBvesSIcD6AYKbYf3qWAQJ2Z9D4PsmwpthQ+qMrLUcQJK6G9whc1MzVAtFGgsg+xPradgHURyt/3sGGzeB9R2T6+nYeXp8wyj6oHAz6jytNJ0I+0HbOOiY+9nYZVuelZnzGPr7bdytOPsI+0CTy+tikXCBSjLWQAJ6IDp/6vytK+sjwSMzWPvHiythpPvzgWT7q+o7IBT7/jFdHVSh2DhmnJYz5huTXD0g

1ssrYH0d2+rF2PBgtjNNwfT748C4ZWKtQxwSrU5BkJM8LGEAdsps60frUMLOAUuF9IUzXW3IbST04GMdx+o8+9CTDhu8+76cddkHU72oPkDTHMTlYUvZkML6UCuwkHmxQmGxSmXzOTnP6wqsASoeGszIUvrXuHMc0vsI+94bn+uy+3frN7kI+8oz/jBf6v/r7+uyuxiTh0tUFX/r9dlLHKr66JRsfPoK15Bc28Aa7NuJDCHLZnKhytEbWvt1YtAa

qq24kkcxcRohlGZLYBra+gb7IBvaIUEib5WhShscTNvCiG5tGa1sMp+LGRr04HAbFvt8II+wbSBQs3o12OQ2+1EhSOh+Wxx1uH3W+7TbEsE4QcpkaQq5UFuq8ZWXU876uEk68VohiQ3lGy6xGBse+pulrvq9I177hBod2UQb91K4MvZCSLN++k9x/vpU2xgyDuG5yrhVpBtHsqTaA/CiCbEgLRpiuLnZJNqIWaTaoDK9G4VgfRryyEwaJUDMGuyS

9agr82WU+Nr0QPQb8frhDPBKfZRfufjbUNDGcoFysg23qvjag9jjcsMsW9MEi21CT1Jp+ln76fq90+hLDcup+5n7b6As60KSSyFsVRxZAOEEYGNzWiCF+1n7kpIX86caXcqZ+2NyZfp5+2dcVxpnONcbmBA42zwbH7hGCWRLoRW1+pwbdfoak0aLJbnsG6PYdfs2esdSwtIy0s37QhtT2XTEs9uo25jbhq1U0nNDmNNKGtIaChuieg5THxtyGmjb

0hp9+r1Sn+LuK2/yFkjyG2jag/pGCEvaahu9MlccXhqVYUFTrj2/XBdg+6OXHIFAE/tJ3Yk9P/JA3VfV0/umrRLAs/qgmr/zV9Vw2z9Sy9no5DvLoNyby0Igy/ozc2LgMlN1xHCbIJEC5Ov6+hvo5aAKgkrLsaYbVhuA09eTaJug21DagNPr2PRT5ZMXylDafmF7+kf6sbBiS6DbThrg2lpgQFJCWLJKmW35qGDbeGAX+u6br6VUm0zKdIKywfgb

bhteG+jl6AvmsQStDJpLxA/6XhtOrFug2AqsmvFBlAP3+3ucTq1SUFugnJrECpEIC3O3kM2A9F103EA79Nx8mwDFP/ufQ+0sEXrHQaA6pktgOvuigAaLciXdjNximtKb9AmgB7/7YAZaCaO6MDtBG0Da+VokCfkqQt2qmjlAMAfH2QEaUt2amtLd2+JQyEDbCAdcRY9AepoVIN4QFRuthf4bcNKoBi5hxpuX++wgCAfBGg5CfElYB4FK+6J/WrEa

mqu2WU5ZIUs4OuEaMRvn2REbsRpaCM6bEUruQPoKX1u5Gt9bMhouYUQ78NWemrkaiRtZGq1rSUu+m0IhmRp5G5QGWgmRmtDAaYBZTG9b99lZgNfgijoZaXGaddFKgAv4tRt/HEx4LmAZmoVKCQocBi/Yfx0zQZwGn2RFmlw7prJSIM9bYayYm7FQN7tZWTVLvDt9G17ZymVncnkIg1FCO1vtNgrf2bdy4xtYZU+7jgu40whyd3PDG7XBr7rXYS4K

wDgrIJmQH3DS4BiFkrhzRAoGqxsQOU/qOFL9mrOBvmxCeXMb0J2qBoNRw5pI0SObiP2XW9A4a3tBUesqDlD+CmNL82GInBcbOa1P6hNKi5ot7HCd5xrHGsidT+o8LdNKfrTxJJTTxEHtslqyogm7K4TNujoZe5YGfmCiEtR51gcHKvGySMj3GglQB4FJ3Jlrv8BYYZ7wz5pPGhg4i1nPGpBlAFoFCvFAcKjlrM8bcDkeBvkLP5peBlIh+1svUf9A

cFq2uHbY0nhIuuypHqqQZI9LC1nIWlIhQQcoYL+69WpvS28qzQpxedtatazIupBkhHo4WmEHUQdEndEH/0HEe4aKUQfoiNEHwQfxB/46fFKIung4cQdIu0kHvzr1M2mLvNu/sjdCgLogATYBceEkAMXRMAH0ASQBjQAAc9YABgAOASoAYAD7AOJl8ADWoSkCXiMfACXlqnF/VB7IsZFanG1NLYS9pVjZa4HDIe6gP2TDMq2FIxVc+b9CuyBDiVZR

sFn4ChTNjRIAwj7iwCIRIzMybBNGZAgr6tqIKtzL2HNNizzKUCOkdWLyt8QrZXqhxgDpTIdBh3HCo6vQSSKEgMGJF71DYxwaoyQY8gO9c6Jy82/EGfUegFRAmSPjY7KiRLWEK3ir+fR7Am2pOWBpst6BqYHIWuugOBMpABUAoACWqsUAswFcwVmosgGIAQsHHAHqwR8kogFIAVoBSAGpACgAEQFwAbhyywZaAesGEeCbB7hyAIHwAGABlADTo1mZ

FPJ/swVjKqENoyoBtgCjAQagWgFycTcAGXhgABAB1gFNaATANNXdMiQApQd6iXiQPyF8IXRBUUHlvNLVtoyDMe7IfBTw6TUHfUQDaQKQf93VkaBA3dFe42G13uNTMqi6cCstBvArbBKCqbyiGLrgI+0GQasdB5AjTM1JXWLydqpoKtAAPQegAL0GQwB9B2Gq1IyinUshxsVA8lgqr4EXMIbbEstpmT2BaVmkuuITZLsyyiO7VGLfM2lhwtniUS8H

P5LnWxcC0ojzB2sGKweLBzfwywfIhqsH66RrBusGGwc7ByiGxQDbBhiGQgC7BpkBewf7B7Y5BweZBwVjAtvKiBAA+wGMwYjz4tp2wIIAiADkAaUHAQC5YQ/5f4AXgYIcQQL/2NWQ8FG0EadB3wLpEPPygEhIcmMyC1G3KLXTLMphI6zL8iNUzI29cCsxXei61UzzMz8HmLt2VVi7uHNtBJ29vgITo4CGynG9BqszBtUSaexckatwsAN4KfXo8elA

nUA9i8MHjmS4KpCGVjk9gcFI0Ic5AniH+BJZBjoBpgH0APXxLzSvicSGZ3DCAXqJkrnRKLeRwImpwf8CulSG8ayzkCmDgbyCTwcsWQfaKkCsoxAr+7NJClATwDw8wLatYgxG2CZgsoDT4MwTTROwK80SzIZdPOrbDYoa26yGxHWa2uyGYvIDPctlnIdAgECGfFDch6kDeAGKQFUSAhMhI+syVClPOs0sgobbM2kjQoYku8KGUVF1RVLKGDxuZGKH

hMvGmXABnAFwABoBqgE0AeIAYAB/yOzABMBGoCnlNgFmoTcBRoZXB9ABUockh53wvyvSUXLA3kDE2SAqTNnVzNBBOEF/ibpxW7MXkKFBF4A1IC09F7JOvFPwGodEee5RUkCM8KzKsCofBzqGnwfMhnqGAavAwvyiBoZYu4oU2LochvYAdeXdB8aHXIbAhqszoCGZnRGqcIO54fu1Q2IJAOm4pYtEu9aHvYrCh8MEiSGM1Qmq+zPy1A6GBWLXieyR

1QGb6fwiZwBnAczAjSmNAGagooDwAN6pOLt2qz0zcLFJ2TOIKmnAiKuzLYWqIanrs8HQ0anB1IYUdHCqaXNnCxAq6X1z3VfCPqvah1GHCiK6h7EDMYffB3yiw6K/BjzKfwbmguojYvPKFDrbpoa9pLlxJ0BGOP0TPnC4eCdZEIc2h9mHXBE9vXaHA4qjEkmqYxL7PbdFGsuZPdD4CZqO836cdCo4lO7aURWji6qjmX2+xQgaxqOxzEg1AboeutOK

EXq9u7OGr/POdQ7b+GLi/YMYdvGNXRVdTsw9/HvD3ewrhp25tns1Ayf9q4ry62uKuN2zike9pevszYEFUyO0/IB4h/nxytajio0J8r8CScuLiqstDPTRpbVcJpM6G+nyKcr6E94SiKN5ywsd1PuB8qYSlsv2AluxtGFXhgCc94yhcrhTs/M7ijvCkvrH2aVxhcux8sl9xISV8jALNp2CNMDcE11eyqBNB4uPijC9NLFfh5fCKdvurFRiwi3oArWC

Z4pCQ1Wo6duHOieKOwLIAzWUZAVZ29sDyAogRuCzoEYhE4Wq4c1W+xE1BTG4I0o8ORqwVdBHrjQ2lbBH0wo2lHXaFkyj8gmrD4v7vWPz1rvj8yciPzJ4kBXaH4pgS3uCs+MdHQhHTrpas866Y0FNrIy7hZQp6TnpkyEnMP8yeJCJ+5/SzduGfBXK9ZSAIbpysgL4s1XKkFit2xIl1xJpE+0YKxut2tEze2JLQ+ddndKgS1RG6Ert2sSzEwMQSl1z

13MoQtBLexIHGlG7yKM16kxHiRX4S4PaVp2rEHBKH/PV+zfy35UsRviIdxvdXIP0U9vC09Pbrvw9zd36uNPcR2hL7Rj9+7DA3pMMS9BrQ/rMSFiNy9twayvb8myiR/vIhbt/4hvbe9r1qzvbD4G72myIR9p/5LCam/rAC3CaJVHiRtVhO/rHy7PJh2LH2xzjEAoiS7PaykdCS8X6J9unykxLYyQ3YFibhuQMS3ALhJpHyNpGMko32/AKhEtGy4/K

ykrNu0gL9Ev6R0pKLXSGR3nsQkpv20/abbtRQdxKcgoxZDdhc4iduhSBtRxDXDxLuktf2zTdZhym6KZGGQm8midR5kZRNaKbJkrM3ORK9kawMJkqzcxHyC5GQTDDuzZLbkdV7ML4zWJju/ZLHkezYNXsbkp8FI5GxcI8W0UrnkoN7Eg64kpBMCg6TkvZQHJLzzzoO0eYJprkgU9KkkukSoQGpLl2mqfxP9s8AkILeDqgU8IKhcvgOtFLHprEO5bo

CALKJHQG9ZFy7bj7pE3kOwFYGmqasmg67auDGdQ61kE0Ovy7G1DHuugtuUuYOoSzCaOoLWe7TDrFeXmcmUaSuLmbegsG6flG1mu4i1KKRgoCB4aVtjP4TOYLPDoWCuxTBuhxkqUldUrVmzazlrNMi2ZKu9UCTT0J0gb2CqVGVkpuCioHSZSVR7VGRDTyBvXA7UrIk86yXmqfusDUWJLwkxsRcjp9So1Azkqwk1UwnUcIO7kcIip0A0fsE5oGB647

vUYhioFqM5phs1+0puhI/Jo7JFJaOmuaHDrBS1Ux5gYauH60QUv9q9SCRDR7m51YUQphS4I7u5vQestKJ5qCOhnCFAOJC0Y7m0rcO6xCG0pJs/ELybIKOhUU20tps2crQ1jz62VLeUrpFcrQSHuXKulK5UuPY+Y676EWO1Nw2jrFSvlK20b5CvtG4UeiTU1b8pigWudL8m3tS3L1D0uQW3BbUFrdSy1KPUvWuUhbj0o1ClyVx0dXRx463FKxc6Jz

V0cxBwRb90bV8idGhXAJB04ylTrjSr9KZHt1skKBjjpifP47tkXdayE6F0q+y72B4Tugy16A30fZkpML7FqQy5LBrsujq/E6gluIynxaf0Z8s72Bklq9smjK8jMXSvkl2MryWiDHSrv5OupbOTsOcilyavr5Jdpb8lIzsrtKp0v5O1OznHsLS/9K8N33WHwhcKuPWddKy93nwsjGPHoNhzDGP0slmIbiGQb/O+/Kz3NLbHXwXgMkAMdBqgAOAOAB

NgF8AYgAxdD6AZgAj8MckfEATPN2yLawubAGiYC01Ycj2Hwg21T9msmKpyS0RaL7ECosyii6tYtocqrb7MtouwGr/qpthlzKcYZLpQaH8YfshrHInbxKgt2GMIO/QfQxHYshES1Nt0As0L0xMariyjxFuQMDhgdp4+IkyKKG4wXiEyOG6iqx7O6dRPIThxbKLeMUG4MjnvOVfa7zfuRKy/hiPvM0cwa6qvzpqhg0cCSwVFS6LBu68s7lGzml+vZ1

DuTyx1DRqEMvh/0i64akejXK7QPw7S3K1Lrz+MGiodvgfMjtIISdXKIlw/Mjy0UkvXsqciP81CoCgonyJ4vSkruLrEojLCsSMBs+2jsImwIGx37by8BHi3nawOTjw1MxRdrFI8XamfMooxbGnzICcksDxyyl2yLcIduLfNbHZdufM/AwNhvWlc0xdLvFI/bLTsuOGxBGxdrl24x8rst0rKsD14qY9fed22JYxrza2MZ82ocG14jh4aTAVaKVhCLb

0eHR4XJxKt2wAbAAmyWeXPhyXod24+WGf0MC2bkE11VsVB9D9xGBUVJQK8CsBA6MY/sNh4ZBBK320JRahc1Nhs0GzRIth9GHuoZtB3qG7QaYu3GHbIYsx4aGFoKOVQhiiSKWkCiAVpHCyhzNXxRIclgrz7noYdgqc6JCh1mHvMbukWcIaZ38x2Cky6OTB0Qq+PMWI9w8lLtq1a+8JCpkKkJF5Cv3YxQqI/JculQr62M8uoMqDLuTBTCV+EZ8upuj

7EcuYmiVYgON9XbDdCqwstfazceThwuCXCpZo43HbasDwu3H2Zz4TC5LIrvD5GK7rAeX7a3GiXzV/J3HzcdRCs9jfA3txq9jH0atxmSVvLJQxsPGG+wquhOqo8bcKjOqB93eY53HzQplk4K7/cdJScDimLzjxpwqIwsDC5bCIPlFg2DiMwuzx7Xspkz/i5WrltoKMzurWauj5Pphk/N30uWrK8YKQTDi6SBFqpvGZ6vvCivGJzIKQRernrtqorOH

4FmkR+s586qTq2yBJioR++byL6ud2hG71apdqyfjSdN44yOqB8eSvEWzqos7XSfGeooy0vqLkGrzhtVcZotk4xRrXrshu7NT0d02Y/WzObo2YwllIbo/4xPMS6u+u+OyKGumvb4rL8fT5THwZbo5PU/Gr8bfxj6T27Lrsl/Hrrons8fasZIFMy27BGvUY9G67rzbkoPFk7pNumJYGPlQuO277bSxKhLiYFIvun+7ePm7VWG9UuOPu+TxwAbM3aBA

cCZPk1KbdPh1uxGiIHqFgMO7+hprEwuLoomC3bi5P5MZudXciHsbUIJqz1TntWh6GstvVYAtc7vfe/jrVIP/kv9Vi7uVKpgmaCZSaxaazlkagKu6OCZQQ73s8UbUB0Dr+CcQU7u6Q+2kJmL5+7spRrILVCZI1TBSTLgIINVTQVGQ1LpqySGuerQnlYG6C+SAJmvHa6gm23WZWRVKJUaF+0wnyFI1S+Waazr4JnB65kASBg1L2OvIJq+67mvzKujr

3CaSuDhS5VnSuMtECcKSub5q0dl+axwmI0r/ukFqmypEJmwng0bdKPVZYWrI6nwm5kATR6ubA2vCJ5gJ00eRCwQHciYbrAY6jge8JxQnqWsrRptKD+xiJ3B760fpC+crEievGVmy0XIjraa4aieaJ4b51ypFaxom4Hs5gBh7dyqYenonUHtYe+UL5Wr/7Qgm5QvXRqEHi1lLu9AntYF3RpCzT2XttQKQrQsfKwRaJieke8uyKQYke2YmgfNfK29H

fyt4J7Rjp7s5gYMKXrj9bJBruqN3u9R7FxFja2Nsj3ura3OLKYGTaidYDHo2J5+BEMZVi94maNg5O29DFWt3ulOz+ltwx6tap7vttcjGfixnC/4tviawYVtqebDsXNRrasuBLNdU0bi4Qd5qwSeuW0Kdv1n5usEnEnvXa7AD4WoBJtJ7B6Ng2aEmz1hbW/SKOMPvurBgfTvw2P5qwSbY2/4mniZo2Op6xKqt0UkmpKsZkTG80fEYJ/O65icUqtjY

VKtg60knNKsZLNJYdKuFJgZ6fByGeoYm6HudSSUmcOpIWdomuQmI6wUswIiVJ51Jyzov0PiLPca2x5gmuQjrO+IcU3HVJ5Ice8g2eq1rcidEgXZ7+0gNLOaBjSck6pQzFNlFehZgQvlk2VTZIqu+U40n7nodLeKqeMItJt57UqqM2Vx7G8Ogmf0nDNlie4xiWRR8G156yrnx7YFTimEkezczcqsdQRc7KToTJqMmUXrXO0YdHNiOJ7DlIycpVVF7

phw82Cx65mLBMXF6GotUevMmwTGQKgWA7wCjQZTrKyYi6l86ousFII0q28MpVQrrHZ2K6tMnKVWei89rEqOLJi7CeyYa62W5othSeksntCA66nud1dm7JsExFXpxiwbrAnpO2sEwNXpeHHoHQgYbJymRZusFUqyVLblue9V6BVPNubGZbSYmehP5tCDNemcsNur3Jqwg7XpXLKrYwuq65OrZXXrBHcgpb7vOeqwhruu0EEBF9Cd5e5uGFtie6/24

fPFe6k8ndzKsIT7q9VL1cjfrh0kTe8x6vuogpiF724ZXuBEcWGEGIoHrIKZnuT9IweqoW3jxh0QWoit6wQPCIHuBAUD86/ajoeqU4Qt7ltg0McXApeot62vryEGgQNHr47iwejPaYev98e1T0epGqm6ibtqeaJO4P1i/LPHq1GuYponq/lpJ6tky3kFzeobK+sc/SYnrO3rJ6nNbbrAkp8eGqetO2HVqxTF+y9wIT3s/SY1yztkCSNSmNsI0phbY

3VNGeFnq1GrGxhwJ+3oneoyn4WFZ6qkZP3utSTnrGfWpHa4zcPqU4eynA1JXejpgc8OO2Vynl3qdJuiU2PqsIbynFR18p/VH4RLq6BbZAqccphz7YdpCK+Hb/ygF6lMIPtmqe2fBgARUyFIoGRz+2Uu5NwrolDTHC7hFeCqARuDLubCTO8OxFUNTwDnDUixhFepoYQdGC103gOXrGhAqppNxajM9gzT1AtBRCeqmqIEap2fBSvs46M97KK1t7f66

z0v+yzeBeqbV6iHYK1z4o03zhqdY2Dkdwdkve9ogOWPcIEanZqYGp5fdrdCd40BH/yiWpi96VqZm+1vFKRpV6mantqeUFBtdUEcWp6anz3v6p5QUpJLxJA6mLqfV65QVTvtPe86m+qfup/Ug5ULOp0HYXqbGpkQy4/IVG26mvqbmptYJaEampz6nRqcBpgKwWitlfFIotqcup0kherNosj6nVeuWp4AzMfog4bH6qeFBp5GmS0EERqvzNqeepsGm

Vqcp+22b/qYJptfSh8eCsM+b6Kx16+97mKx+UpRGjesruO96mK0TUx3T1EYYS2NTqaeZp+M4Rglqc9whb3sYrBNTuaayDZYreuz5pxmmBaYfeknT+7hsR4rggMhfes5Y33oOUxxGA8ou4MWnYdlfehHZJtNDyrOSwOnlpwUdiMi1p+yBltIqk9whv3pxgQkzXYDS06PKj10lubHHbXLxxy2mBNKvGjTTOOjNpu1yhcxvXfPbmKFNpty4d4Hdpx2n

nVPCRwvLYATdph2nEmvhUoOnB0JDp32nccYtptci3sYmqngSmRIOIvmHxpmqAPP0GgGPAOzAHQ1x4XPEGgAQAHgBTl2YAeANPBNEhj0zXQ3PbPTZbMwwEAXkulV4kTh5WG2WgOLAdYaVoT4mQ7KIKRFGlpo4O2S4CcfvB3TGdYuq2jTMHWOthyyG7RMa2qnGsfSGhwjzYvIl5I7dbYvdhwza/GmditOiGsNS8ujwu0C/WbAjmYYjBjaGWPJ39WcI

9hpFx/m1uPPFxo7ahPLtRaOHssuDxmOGxMO9xtbzZvMIFWbbFtsfptAlG4YnoufH+w1rh9LGv8df83vCi4f8vX/y8hL1umHd64smhGkzi2ILiq5hq4bKyuALvBogC8Nc8NzfJu+GgLPbSQgLvYNz6tpYcAqPg2PbDzIOk3rHFKfGY2gKEzTbisM1mEcaR1GlW8O1xjcRQ109Fb2qXXKI+5aEe2ItrUCSmGbnCdeGvyMIS3bH+7F3hzWqmdyIEF8z

ZLM0aLwLjwyl/SFywnLR2m5ipEouG4qmk3Dq60ZHT4aJS1lNUgtM9Xx8b4apoxz0onPx2gk1qgoM7HeLXSU6Cm+9tfMtqvL8EYVRk8w8QLJwkD+HJ4wGS8xneKO/h40Vxgv/hllCXcYQkwB81qeauriiTUc8/d0LCjxPcVZsV2NMA9BUEU2Jy5Sz3kpki3PGics5Gxw7xvyRUAwCjDuF22hUSEcRFeJmcLINkhnLTLJkZjd1ikLcglVDYZsyZp4K

pXwYR1XbwQuNSs0azrr6s9hGSme7RtnNXgXRp7dGyehxp7Mb6mdERj2TsxsrS5WQixqno65D2frr0jGCKvR5CtRHjj3t2tmT+ma++sPN++Jz3Mb0AMuJFEWmmwqNhqZm8N0KizG6fCyZY99iedIcRgchvFQDyrMlVmZlCvhLNmf9ywwgdmbIy7cbtaYq0jlCyWpag237P3RyPEDiNEudplZm8iodzU4qX1NNkBkaijzz2/aKs8oKPID0OEF9fG/z

OWCg46JHebtiRgpAgWYSRxhJ69qcsjZEi8ZqPCFnp8iSR6FnGYPFG8bkW9oeyHvbkWbLCnJGDvGb+nS5tk1bC2M50NBNiYpHbQvHCie0eOgH+3ZDciHHtXgyeOhaRucKeDJCwOln58osU3ghX5g0kwOMTYiwC88K043X26tUV/vHqrAztUIh7A26N8slZO8LpWTGR9HsSAtvmJAypJBNiFRqXuIQirBLmksduu/aoB0gWVZCx3Tf+nZHNWbI4kEm

BDB1Zlyb6+LNfZiKN2AORpJ0C0ImShpYYDtcG9iLKEqEisd08Cfy4/Wy3VSki1SLwma0+YgmbNws6N1mVIuK2T1noonuRqfGHIs10ikn47rQOvzcMMeH4yKKHj3mm50JPkcTu75GIooBtKKLHj2wO3xqUCoyiuxD9a3+Rog7l1As6ZWnxEtOcoLR78EoOyRdE5NESjX6t/JN7UtnznJ+S8FGmouNpgqSAUoAU9wLJps5s/LTre3EJkQG9ppGipRK

zNO7Z4QHkUYCC8q8XmYPx9FH7ljCCi6b2r2ganZLVAbiC+BrDbNZuxILKoPxS0lGObu9Ui6KzzgpR6Q6vaA4INBqrVJ9UpFSpDppS/dnkxt+U/E8dlIRuelG9pE7wOGKMYtT7DqzOUrsYNmwH2e0WJ9mOUr0O19mH8dVxShrKYq5R7FZWgracAsIvip4qsZqDKG5m/1Ai7KTPLoUtLyXu8VGprMjgGDncWfg52WavDpmS26TUOcb7dDn5UcEICtR

ikdGupOJPCZhkAsJCOeGpXVG4jq2vEiaIZM+AYalzUY1gYGdqoYHkj8rR+wY5xaBQ7LAJ61Gl4Feau1GPFln2rvM1KqTiR+6oLD45rW6oCZIEsOaKoKDS6C4UB1Hk4eTG+z9R6NLNQukmgxoYLhZTQGzx+yjS2EIVOaQueAm55MBKcYGs5smB9KA9ObiWBAnPQiyJ6NGwzTka/TnBwsBKKzmM0ps5/68ouJA2JdikrnyJluaCwhc576GMlmmfQ4H

MHoZgMG91836OyItSWoZgI1mvaArR0kKq0d9WCLmtkdECnZHvYDwextG2lki5k3L8phS5pmw2lgORke1RQu3Kt5boFqxDJxrYptIJyEop0fRQLENb5O00tbx0sStuQEHw8FqIb0I7Phq5ptAnIHq5hdGgQfP2iNnYND4IEZs74BIWw64N0ehB1+SplnoJ+vZWOeP1BYm70tymsbmP5Im5q25pue3VVgnEvIvVKwwj0ZVsuqAVubWWNbnytA25oGS

uCbN7B9UcyZiMC9HvQhzumUqFFvJBl0KE8EvRhUqnoBhR+wgtFo7WQ4nwtx4ByabLiaduT9HCBzz5e7n22Z9sD9H8Bygyn7nt1XYO/wKl7lNs5R7AMcNCMHms9I6Qm4nvrjAxkJbH8Fh5uHUl7mgx2Ja+rFR52S4GTuBuJk726cLuntmR2YQxxk7lYoJ58u6kUe7pzh5r8r4ynEEDTKmqjjGT6J18IwBSAHiAM0yMeGLKHaY3ofShm1opKsq2T5Z

ECAFkPXQIUEB7NMgU3HAtQZV8vsME6Ol6md7p5yjPuLRh6wTnwetB18HVUwtvW2GcPJshyemacenpgM8brTGhiCAJoYmOcmHpod40w2aRHKraH2GpsTroTSwkzuZXNaGd6f5xvenkIbOAaNnP2yyomgjT3ONMzjGoeHVAYgAWgEckehE3WW08loA1qHWAATBpMBqiSoBjMC24z0GtNW55qSH3aFRgW4A+YBGvBpbHSgiQF0pFEEkm2sBORDvcKXn

vwIyOWXmytrvB+XnzQdMhknGrYbJxrGHOAzthrXnJIynp1rbYvJi1QCHUABch0CGxgHAh/HIQkCB7FoiyfWmLemGhmy6esMGHeb5xnGq5HJd5+fAv0NDhwQqjTL3wpKDlSmwABoA2AGKcfYAPzE3AduQeAEkAc+IPgMwAYsMdpjXBm1pbdLNLax4/HmlROun4K0wITdA9GCuqpqDunCZc7Esn1tYjZGo5GvKS8Mg5eYq2hXnicaV5jGHq+eMxwGr

TMbxtPGH8wwJhqzG9gBNoufEGcbb50mGO+YGyX0HhsW9qPRgv0LJ9INiGhS4Scs4pHN5xzi1x+eG2raHHuyMjFM80spkusXHvlFAix/mv1oLCPfbzbtzBuiHqIZLBkwoqIdFoCiHaIfzBliGOwbYhpiH/efbBxsGOBdZqbsHOIehwAcGU6cAuwViWgDswF80ZqCWoYzALaTswCLFcnEwAGcAB5ClYzYB9eahxw/ntsk4RaN0wsDUiAQ7yHSQIcWT

IK3irT28klCw6uOJp3o9IKIbpeaSkK5GBuONB28G2ocJxjqHv+bQ83/nVeeYchwTx6bMx4AXMD0sx8kCZBOI8dvnJoZN5jCC3e0S8nrbmDApIhK41FXt5rGqWYZwFtmGfMZiUTwgj6cjvIrzT6ZvpuUn/zToisOAGIsCgGwXuuJoF/MG6Bc4F4oWWBdrBtgWeBebBzgWKhcYhvgWOIb7BwQXuIeEFx/LBWLF0WoBMeBeATHgOAEGoNagTfCPw6vo

ZTyOAYgAJQahx5VjH9w/oVjYhyAuc2apTuK1oE5YuEGK4aWkDZk1BzbDdQdyUfop5SB8eOqHW/QcFvumXXT0xmi6h6dq2v/nR6cYu4LUJ6Yb5nXmm+YDPWR1bMcCy6wWhyDfSZenAhJo88Wp14RxWq9s/nE9iuIXxLud58KHRJxSyiMSEwfTPXsNPAy6yycqtZnFyfRJkB0voMEWBvxQhdZnayo5o8q1J4b9xxy1BhO/JnK7aaKqA1DYummOmI4y

yqIU8XwoS6g284c80GZpo8ASMs2AZK37zsuHPZhGxlwAEis0ZqlXUJPHKRaihJXpTInzx2pYN0X16rEW2RdCRtPH0RfUPdcwhoi5FuRmhOlO6cSUyqNMp8HFSRbPPL/UhOaNx7EWRsI3qLptfCCaq4qj9nSY6En0AEAy5pUW2RcshOcdCsiDx5UXQkzdq2+7NRcDRqUWpQNFTUxpfPFruOUWNkmYyL+pqr0dFjnDgjTXJvkWhRfDq0PHBRdfPO9i

0dhugFNwvaTFFl3TpGgYaa0XEBPc0PDKkjwY0tEX/Rf/jbUK59zdF7I9yALi0FMWyYIMMuKqZ3q9xhMXy6txSQkyOZtpF2pZa6tGTdrhpyO3YmwNL0BUMhopKxeRFta7/q0DIRzZ7Ob/Y3mjOIFaEENppeDhF9cLNJIJ+nXGqxY6Ki8LuxaXgmogry0FIGsbWSrbPEs5ueoGKBUhw2dIq3oqNhdLnLYWCONPgpcXBimDSBOnfzqTphTzmhZmqteI

8U3bkIQAZqBJ5eUBBMGUAKAA2AHoATQB8AHiADoABICvQqSqfCGobJtAomD10QLByXASYJEztWDEzZsTXYTF4ME84Si42j/mjIbhIkyGwIMr5kaC3BZC82AiNec8FoAXqcZAF3wWkMMjdLi6Mqk6QD0xQsqN5dyL6YZ8ieExMBe+Fx3n4hYFx+vgDRCEMlIWxiLSF0gXDA0ACTg9JSQhFUJ0Y3Fp6eXHGarOJF7FTmkEPQnb1LtC6YsIquNCDS/K

j8v0u6LpgKtswvESZtptmHBhCZEdmrs8HKp8RryrdarBpXkW5z3WIkAUv2gM5uYiIoVN/SyturwGqiUkjReI6VwrNJdYqNDJ2Kh94t3cSRMZw6C8N+MPYz+oyiFcCMejgExCBqgVdeIjx6ODKYJLvXWCHkgFSPvGkcOHDT3juMv2IDAblQN6uhHMiIaV9HGDFZIJM2IQUST8lya7MmE2MdF16xNu+gwxeWuCltmC0mZOTFmCAQzrxoNpJeGJIW7H

NhObxkrxJjAD41UDv5n9sLqLtmCyEpSZi+PlZ6qWsQ16KpFDpErSlxY8dSDowcjB3JfGw5bwSjC5sOchyjD0uWKWx8f3qxGzksfrEqG6pc3d44/i4bsIWN+8BvGWKMyXkboEienBNkHhYWUCppdxuhfGdijWlrVYP6r5KG7S8r1WIyqLP6rXx8OLlvGJuqNCiT3OlvtCiT1RKICXlsZuK26WwSi42sTjHczuliEotxbp5r+zi2182pKDSADWoYmB

AA2CI3Hh9AE2AUgBCnE3ANagjAGOtOzAjACvA2GJuOoHJE2sx8tfw8xBCCGm2WJQcmmuq7nh0cIe4sDmjRPsFk0THBfNhi0Gf+dJx6CWbRNglkzG6+YuF3bdG+a15eoj8fTuF+AX9qqq2P29qPEYKin11puYBAOG/hfZhqkKrK3G2tn0AsYwh0ir5LrUckaoszBzsl8qAZBHeRpDQOLzwMm4Hshyod4kB4RsQQFA5SCDMdgjdIc3aD1LK6N56Sta

+JbGgaWVTUyqa4MQJNFFG+Q8uxEoQTSwxNrJa4MRXunlCRCqtsPUZMQhjNMcPE3HHnwcumNN1DySwYlhXRcnF8s92H0XqZ9ovZanFibC39Rym/y6TdkRpOfS6xeE8sCouvjroI6B9yr1JfSXw9vcPYgQ51GAICDgU5eSZ3Sze8P+kZ0W7JYeJ7GNHMkMyCbSlOUwBPsWFCvCKs3jgqdFfRKqjYd4aanj+UmObecXz6drYjq6k/AwGkorDAT5M1AT

/2OTsLZB/KvoEq5N1rp9JlIrR5bvmFnK8pfaEGFz5hVRqMrxgsbcMCerRkGp42671KqboxcW/nrnFg6XdJZNZp5Dh8ezTYqEY9KltRgUaoV78tc9z5eY42aXSYrjFpOH6BoSi5aWeFiW2oviA0M2l7i45+LxugUou+KdiZ4oxvD3416Wnpfuli3jrJf3x5qTwyf3TFvjmbuXZg6Ku+KPOGIJ9VNcJ5yWMhJ5uz5YW51mh1+Xctnf432z1vAh69uW

WpZwV27I8FaF6uS5BpZaUgmLn8ayl0EM8Yr/Zp/HIYQ+l/l0d8Iko73mmeY/yPoALhEogaHgkgDYASaZcnAoAKPBRsgoAOC6JeXyZRLayoIO4jkcD9jvgWRkUZY2AZ8l7iljs29tXaKN88gNz10dwMtx1RG0xz6r+6e+q/TGjhbouken1eaplzXmaZaQIlrb6Zdi8mlNIBe8ExnHq9F88eRBmCuwlxto1HSthXuJf4x5l3Lz96dMgZRAKJY4Y0x1

xJYlxsUCpPAllytqS5cnlnASefUlJOWX5JZUtRWXHSb44otiKoV0YWk9cUAJgUrVhFM8KxKq48tf4PUWS01NFk9BjZcwID7ayqPNlnSW8xc7Y62XfYhS2N9YUEESaHvEV+EmlnaWELN9lnadtpbflkXiKIkfSdzmtzPWl530EKrcUghWN8fcK+exp6NVJNOWUSSDq12qs5csMrtb7vP5g4x9IwWmXQFB1YNcjWCR48E9+BgyJYPlMtmSnnGXwW0p

23WnzVyNwJFWnfiBI7O2V2F0oPSLWSiYZZANgmONC6q4SFId/Hl0p3rxVFZhZ9X5gCCG3O5WYgIbFyYgpPjOgP+nwgKpZuCgeyBpkb5WChJ7gtYhUlGMEP2mwgLeV6cWxOjdkICnsgOCAhMay8DsCFWgwpajjdPyazhNlTpT1CkX+5IDUVftZ0bFTJoMoazp4VfIQo+1qAx4zIFB9fVJ2imyqFkAp1ZZg/RxV2JDfVlY4SYhtYOJVtfzc7kY8Zhi

aRbKAjIDw0KKLL3wWUx6aIlXhVfJuq9ocNmqwQFXKVdputGthviq2cFWgZIXUjRXcHk5Pd+yuBM/sw+imQdihwVjsHSTxSQBiAD8xPYArMGYAZQBlAEpBOcBzMBzxW4XRhfEVtANsQB7c5PqL2xiB4XmwG11rIZsyyvCQYMNNSWlpSYb3POjpLxnuoMtY8rbQJZtYuhzDheW3YemTheMVgAXqZa8FxCWfBdpxp28VT1b5v1jmI2ZgFInxsTEc1xW

4iM5cAiXgoewF34WvFeQhzGBVaX4KwgW9ofQhkgWK6IE3bM9HuS43LqiEqqnl3qiGXRxPZHLJ52XlveHhzJR8pHcu1fJF7AS4SvIeldIelZmI+ZAtII+DEeXIlb8bUhtImxHVl0rlEd3ExJXnj2762il1JV7V9ySbAu3V6pGx4YLqCKk8ruzILpGRfQeY4JKNkcBZDK6L9shRmAl0yNRRqYC4RWqu1eUxd0oqmKWUWW0GxSTy8Uk9N9WU4rVXTaU

qkoH1LFXhcgG8/pKXPUXM3e6ANcaS1nUINaZJ/uVpUddxkrGDkplRuBnhuVDVjkl+mMAZMZLFd3SlCl7kXvg1g1GRRR6yohdkNcQ1jrGg3q4OwDWZdx3g3t7JKezISCTgNfmi3d72UZsZtKg1VTTFK8ch3WhDcXcEXoYZiFHAvW4139WzhMbg7j7X1bnasYaA1YmGvPgJ/P0oMTXYQwNNZWlpNf4179WR3Xk1ukHPNsTp+nn/zoZi89yKgFVo+By

EADswfoBNAGwjaoAAiMmyGcB1QAQAJ29kLqc8yDncPX0IIzaA2QVhmeANhZ9ZejzVRLy25ssZbii2P6KiChFJ9ZTfPDyObRWzYd0V6i7vNQMVwzGLIYTV7GGk1YQl7XmkJbTVvYB9+aZliCH6nHerZR0jeUN7UNje4jlwSoKvhZLV+LKvMd5lnzHBtQH5mfngRcCxuS6t0Xjhq+nk8YbliqiH5ejx0oT08vjiqZWf/NJy1DXE0y9LaoSlybwZlxz

SKaCpSndQ4MFVPLpIgbOY2ySMXgXh8OXV7zXjQRnYqeXdFJn5fMQBcxcyKLmZ4DHGv1p2oHN6dpg4ssWHkKlQ4hHvTl7xjMbiMDtgfQhcVhqhNYr9a1KksYFE9tRivpT0Yu84cipKWc0ayLjfObbVF/bu1T/2kFBVmxwB8bnppNrZrY9vkqoO3xt1Cb3ZxprxrIXwPjY06GF6djnIwUdR6Tm8jpDSyB6o0YzSqj4+yV/fZqsOCHznDHWGiwGJwQh

AefiI/1rfWgP5AkHJufUQNU6m7IKYTSI26eXWYTbAzvqe9CLu2qk9VpwQ4BdcgIcCUAOkFOw+QVHgIkmYNgyek0tjnq7O3BAaWAqegSqqnthpGF71zsc2EJ8OSbpuFv6m7ialGVy7zpLuSDrJheg6jjYenogMbzWforluW+YAtZQ6jZSqPiluXXSRyb81rghkOu0qzAj3NupinVXWMZ3FhnnWFeU8yqR1gHMwaLaOgC5EpIBBqG2AfABlAAGABaM

UnFIAegAEQDbbXWB40Dl2Vjh/UGWFqLBXEGKIRgh0kHsrW9wOlB9KslBgOfcBi08HFOc1RTNS+c/58vmIJdJlqvnyZdzMsen+oeTVhLXU1d15haDZIzQlpaQWXBah54XpIeeF8nIo9adwYgjCtc8xu1MEhcFxueALUD8VoOKAlahVSTEuJWYGe9WI00yGJ9W2rryGJppkFZrTFa6Esb1x+A0cdxB5Z2XN1a4+geFgeT3ZchmgRDGZmiYnQJwhnFH

kENgvf1LysYceotL0kH+u59k4MsRF9alwuvNCnvEUiTw14F6MEfRldJp5qUf16s8axYzu9kXIXuxehlmaWZMoET0IiRaxiMdBxeoM7rL4iRuuiVntTKax0UVWsafgxFC+c3MG9BmgDbPqEA28EvblvN60k2IS01mj5cUNe6ksDfHxrIa06gvqnRG5lZG12jWCGfGl8cxGvuKG7wKBIodZ/Y98GdCYwfGqIuQWTyC6DbRVw46D9OMJEhmT4JGQoji

fCQPV4pi5WYLOKoa3tvHg+OMQdHGymGkexeYMruC/HL60apC5DZeEoaUzZM0kpSWUBH8p/2MNwo0NiUkFhvmlb04W8b+gXjItsqc+gNBVUFkNiONdDfYArRIjhp8+tQ3lDasQ+7HLDaZraw3A90JFXLJtDfUNx1xuqZYRzOMpDa/h42DJqdql0Q2L4s7U8uBURp7xhA2p32liUGUYB1G+k+Cfk24N1HKf5TBs1g3PudScj0KHQs7wQg2gmeVk7hB

4ELZp5cwaDd21qR9MkKoWchz42aFfWFnObO20kVCdDMG8AyynJa8EfMLN8eUS7fHUc3epk4q/EefQ3u1qcsG8Fq9pJZqKnCJD2YLyi7ty5JiZlY0FFkjp19cd9dKNjJDLbPui5ZTpYig4jxD32avgN/8P4skIAo3yGroV4zigpd2p8BVaGuLs6ASUQUPlVI35bq/OWjmiOfEkLr6SZkiNwAmKkYn2xUhv33jqynar7IE5nmTWfws7D421FNdxE7m

cL1s7fjm/jclk5EbuvoeN3439FJGhME37jf+lCjgAlJeNnEb4jcRyitQETd1GuI27Aja0+3zmGs+kn84bjbJGsQgOQxgVTD4/irzVfnbtjZahd/GxCHJNx0gWoTA5oKXHqfJix/H9jdZQro2fbIe1vaSNjdJQoH7H5n7nS9mblOliKoh9Rp5ys6Kb+IlxQMbspemNkP6m0ImNyFCxFWhQqn6T+JZupighjYPl/5CLZUuKqtDVTapVoo2JujfIK8a

rCc9Q0X611zaQTD9wFYoHXN8i2c1+/tnrabs0zxGt8Ys6LtnPmeVN75n/6oBPMPLs5OBZw/JP+MmQm7Xm2c9NtJHk22r+2o3v5bw6xsZCOcLZwNCc2b1CF7WY2dTZuNnfVtR7Wf75ioO8BXS28oZcKRrCkqUioZn2riEmnpHa1VyyFyTHWYGRybU98rGcu1VyabYNngK9JqU3RgK24EeugQ3VWcHMO+4YYg7xyVmeAssmls3f11AN5IRPteGmxLn

jWdHjFnLGWb8IDdh0ufW0avGGXHHNmsKNUL7N3OABza9oAMKictf14QKEud6Sxc33lYONIwglkd4Cu/7uzZwR9uWsSr4C1s3hjdWTEs3ezjUmg5WSrMNkqVnT8vLNv/XOjwAN8827zavNxS8/UOMNvM3+WYKS/+gJDfu0euWRGu1uuDlGpcQNnyXWKBXyzg2NZUPN8C2SVdAQg+qRWcAt11mdIs10pDpoLbjNmOSv7SEmhC2jpb2l1kpl8u4muDk

/TY9NkFZF9ok56HsbTdT29zTMLdItwfMYFfWi7U3JGtFZifNCzYBZuY2RGvzNpi3/osWUq9mXoDHdHf6z8stsjk3a5IGZ6ZGv8IYCpUTlcXpNqns1zecmjc2STboask3zWb/+6Kzvh1ukrJSpZcRMZ1npkoI5gJLrjbucygnQ7LRNp900Aci+R42wkrhkxE3HkohXUgGIx2Y5ypG6EB8Connu6bm+1W6njfMtqprZCYwLeQnTLbqRty2kZoj8FGb

TAcsFheygCaI3dy3XAan8KAxvLcxk0K2cZtnutPXIrY3ssy2YrZp5n87Ppb1V76WvsfGma4RuEDgAc1kOgBJ5QUGOAHVADgBcADtVngAfWMdVpBz8HWvAXvop0DNwN5BdweKQSBAwdji3TscxMyFNqH69XT/wgvmkzPDVnPXI1cq2gen9FdjV44Wi9cIKqZlRHTL1y4XEtcr1p29/o0zVqHjueCJZo/BHMdQAT4W2cc2gtmBzZTb10fnS1eK18tX

/hdnQC1MuYc484gWT6eoluOXAO3pqtNjI4oW2nwZN3MDqj+mZvPjIsFqQ7oF9TtWsIcsGjrXURZzUXImvDRDgTJ7DgIBt4CmtbhgZs/G0KY9AmF8BvKn6gcYq4a10H6im9q7dSsie3tPMyhxoQVYZ1d6pGesCxSINRf0p4LC53tM8TG2hseUZnGkr3pkN0XdBNfE1sm33PRcZ42g6Po2w2ymzRb3vZSCnxOY1mw3a3yDRqfa2bfMl8PUXdQ9gBG3

dHk/IjL7VlGopnvqy+vzXLKmyRJHuU9i3fkBtmW2csh3uuDW+8K0ZkZrYPwAsm9jrau/hGyWg90y+rvH4VRITLtHdbbVx6Iqz4dkZiQIphRsPFm2O2NI1uOZ6bZklry7+aUpttTXYlYxw7E1Z1bhKrfXCbcCVn6S1sLCqwTy1JXOAHE9SyKEOKdWDnl5BXhaQkXlUT34SSqwZjtjh1a4IuG3PPzNluBhp1Y9IeyrFYwxt4+WhkUztwfXIoURAppX

u8extuIoPUvv5bjl0SU7ozm3sKS2u4oKQ4ANp7+nX8ecKxLDXvMju6xmeSXf2t30RJpNRu23dqLLhgJn1TS8A3Im+7ecNYnCI0d618Tr2bcR/B2CHyZVFU6V+bfdA/kUZ7b5tqprReolthZ4y3vzelD8dbZFtpg3imOFtyfrBse53KpmjbczAmxMj7e3tqPDbVTPt/e3/hIzwskVBIUlt4GjVsbux2e2PtqE+0e2ufO2A93CuGfC/ZYLh7aREz+2

Zgp1Nbu2saOUAsw927f/tyHaKbZ/Vqm3lcPWfRu3WLcJwyB3x2JjFAE3BLLgdwIK66i7o2B3s914Zj1LJPszan2DA7eE1hXCPiWG133D0HYnRQptQq3YZ0O38VHXCCO2N7xYOzUKo7fht7B2Vfx7t7UsNcNCpk08yAr2orh3ufKrYsu8Ydo02AXy4OQoqURnzcEux+w2wba/xiR3bDeC++X0HvN8uFK36Qfexh3XtNemq3TWJABmoevp1gGcAXHg

4eE2ANahCAHIAMIikgDtZJagxdACqMRWqrbQDcQxWNg8GjlBQRCSxQKQLEDQwOnAkSCtdJ2FjmOixrIjQdoMhpyjc9aJxkmWXBbJl5H1IMNOFj8HKcamt2mWrhcsVgM9FWIWtj0SXfCiuMgtVraliwS64sT2rLLzSIKd5g62+Zfv+nm0BCsq1kWX0hcSE3WNqvz3Vyb8W4qa1+YiumOpIM+XDpdHwnlJylaChSKE2yf/46qEtAtrIu9WGrpJt7DI

J9ah3BwCiKMGd5MiDCKYdz89R9cft+Xis7bEpc/5TpfsIiD6psMYVnqNk6aEy1OmZYWNAfQAeIEqAA4AswBScfQAN+eMwTuQlqHbJSoAbiLbbOOIe3MQaIynMBCSxTMrc8nRKFvAVCRWF2DznqrB3RbUAnaoclGGwtcfBgvWoJfCdt8HInbgl0vX4temtivXrhYWgizMfsErM92Gzk0WsnrbXhehiahpGPC3prAWitc71kiX2oANEOfI+9fDhqba

gsayVqeXFvIetpdWAro+dsM3siMv8iMRW1aWIx+W7/MCjdTW7dbUdrTX2Mad1vzaKAGNAY0AEACMAXHh5YStVyoBsACScaHgxdDswfAApwcudxIINDHjHXFYgrec1txWNdACrbOXYamsov9Jr1WDV9ZknoRMEgmXTQb2F2zK/ndCdwvXAXbV5vECTFfgl0f1YnZmtyF2nb2PbJJ2BHKr9LPSetrUbYMGjmfR2dkDCJbH5stWowY6FHF2gxUFlmiC

61fOtiujglYPRL/WphUv7Ml28Yyp42Z3CHB3hBZ2SmJkXRwqunflAkJA55goGjuX8mNTdqLNparPpzW21kSRypxykmLD47Ry+4ZOJRUWqNRqa6bzm4oh8oBnhwPHc71dNYEP1x+G99dCjBZ9/A0ni6rGt4rbh1Lql+sMY7gLrfzmSC+H47bqxgq0t+tTBlz58TYMHB3rhco314yDp3aZypnCxbZl67tX2WHLdpT1bqNu2zv9omIHhovbG1fKpdS2

fbZwZl9U+spsotG3uMJNsNV2z3YxBXLd3/Q+x/VXDoZlhIQAUnHR4Gah6QDlYpagAiIaAdHh0zGdZQag7MFmjTnm5YYrpwStbYD9asqBGCFpXGPWwGxkbfwZQsDfXG7jLKi8+vaURlUX6QxHhEJAln539haGtmNWIILjVsa3bQYmt7MMzFZB4gjzrXa0osm0cm0lBTDCwsqt55i15AzW/HJ2ZHOIlkrXu9biWOMGiarOtqiWG1b2ygOW51au2zXH

BPIZF0vHrrdpFjvtG8b+CdN3PuW3MmOrR8ak95JyOhtVMyt2B6rk9pvGoBpma8nsdNxlJhrKVPe7xuW26pPk9gtFcKe+21T34Kelt3MWOl3eogPaU4dBUIlEKwms98iU/yJ1cJakfFYltC67PHUZtltXhqKpGGwi2uRwXWNcFDcGEtYTIkuHio8yl9cbd/z3BpRUtwUz3MN7eVQ2djXAR8/x5CO+HbQqAJIC94qYqHc8dHz3unYUR7z20vZp3WcZ

qbe8hIu37hSOMxz2HDCu/Xg3V3o3+JDIfHJrttaEksMvd4lFnCvNmyz3d3Ztxlr3vwQwZ0iyHCIhthe2Zta66ei2S6yDAmzqfPb09/r2dxEG9hsT4nplFzEWlid3uz23ggrmDJ5rhGf9XVW3ivbzgI0q83a7eQ3GbvvIGnN2OGf0RxAy9ve659rLV1dZF/eXaGc3rUOWp5ZS9gT22SvXvfsW0BNjt7iW9GPUutHcRDw1x8Q8HvfdTW73DLtASlWW

PZZK9mA5qaOttxxmLD00Iwbr/pFRSyuXr0bsPfdLQ1iA46WS35vmFfMLGiuHN//XFwqTdq3seWcnqwyXS8bRYVBLRnaUGmSBGmbovKLH/JWusxXKUcQ3ZfEVWpa4NoBtyOOQJD9WsDe3qzFlCvFp97qXKzcAQ3eixqtUdzTWvpd3wlkSStwKcA4AZqEIATHg7MFwAegAs/R4AGjMkgH0AGAB6wDswWUQ1MsDAJLh8+B4YNwc/vUSaRWyvaHToZob

NQf5co4EZ90QK3Zn0MumVPq3dhbL54J2K+f+dvD3jXfcFqyHonbBdy12IXfidhaDDtxhd0jz3YfsttlN5of4RCkiYqF0QWhiYhY8xv8V9re9d7xWebAxqirXPeZBF9kissvjd1IS2aoSGKczl8bT94HaFzPW2rJqFOxnTbFXlva5fRf8wGd3umcyY/1EJsTyH72w7ELs5/Id/Yb3OOxr9puGCiS360v3F3cO6mXr/B1Pdpr2RssQzbxy5XwPVBf5

avcLKzz8ZvZgnA6dTapC9+z3hBCy9ybKHCNP8osXx/bGzX+nVEMi957ET4as9Ff2tpOyuFQ3vh24I/oK4vesteZsb7fV6/b9zdqP9g97svegS74SK1X39ndFGyK3VlbHYve+HAUWH/csIp/3rLurlzQ32GcKR6h2hDs1Chb37hqh/fp3FkerAwRmF4va9+4aUqZXim6mXnMx2/pp6T10M44zhPUey66UisMI1gpow0rsaf5LfEPjgy6bs0Ygshn9

/ckRYltHq4M3/JpNttbG+5pnOk0gRwEFY9wwDo/90nLH3VyW5cK87Y32qCKYDpXCf/1bwVgOV7lIx/7otgQ9cilCmMa1VukSNNe3F1l3Psd4hteIBYuwATAAriJaASoBiAGNAXHglqFuXIQB9ADWoFJxBqDPAkzyv4GKQcgdWksMoYXnddkfoeYgksFMHLGW82bTuwUFHpmRa9MtC6wnyC33s9at9oJ2nBZCdvWLDFfjV013E1dMVmJ3zFbpl1Aj

6iLfomxXYXbPbCsws8Du3dmXFoc+cKWJgVFDeRj3OCrydyP2K1fPwEhzY/aUcgl3qtedKy+nkJUvpxiUS8ex9wv2wzZ09/W3G0iTEu66sBr9IrK1PrZyxqrL2sfAJ4Bmq6MC3MgnyieO2w/2h+UHJ34YwaKvJ8y7h+od6v30ZMNRtgDJxtacusj9rJW/EnILmhpVFkGjG8HYZrQ7QA6tRSAOj4etwpd5xJR6tkPHan3Gp+xm13gmptuZpvoCYeBH

EhxKKTPH+rumw66my8aj8rWSfqYoRn8KoDZRwCH6s/PoNo6MYlYCsZizlEFYs5+rMou5o2dd6aeavL2nrivWDS+WYObUtkRlrEZ5s2Wmp5MGRkKys6q3XM5nd1yIJ6zcChadp037K8EO56UrjubcN5PNgkbB1s9nty2D+sY3X12ZWeMqDblr7NDSHLMe7JFn5NHn7bF20Wsb+sAQdOC6HJtBnYDla3/sKg3Rk1y2UZKNgF4n6ByygC2WRFOotvPk

EVpRLYkmBddgU9i3+Nz2U0TZVSY2WyTdGBLqSk72QXvnO/KqIerEuLGxpzcpkOcnSYrkp55hNLZ8If8FUerjuR1SD3YPzfIXNApBppGmjqYc3NZKOSr0CqBxqPocrCTJ2IUTZl/M/GvZkVL69+uPQJ0PBSuIBQ36AhuIBwg6rA8Y288cvhv72K1rU7p/zawP6BE3WxCdJ0HYhMMOXkojD3cagPsUOU4H2Qr9D6C4Aw81/BtabaxxgTVq4w8BRzX8

fa3Emi1BlJo9DhO7nQ817Vyb5FZcnDybHaita4NnONCjW7awPEA5kk0O4poGmuqbSpqbMAJ6SuYQB2qa7A+inOMgVHdEDtK2jzXvdjZ3ClWMwXJwD4lx4X8wOACdMowAjAG2ADgBNwA4AGFENWmhqoD3nfGiUdTI5yGCVHOw7aLCwYlBfnjWeKWJPNfj0ImnVYrlBHM7sCJC1omXfncV5w12AXaEjf/nYtZ8Dl32/A7idgIPYvOuAGvXZLDYQGLK

PQSb19emRTAMoTxWkg/+FisoPsjSDybbg4rKdsmr88d5xCryqqLTYkkUqMLtu426U2JnDMb3RCty6sz2UwcEphrXchM4YVt6Egg+ymJiCbcFwzT39gkZtrb25ijQ+zHCVpM1yvJWNsIA+3IDtsb4wmL23JUOo/XBOI5E18HDwLMy9hj6EALnE7CzEvaEjjwCn9uv2wSPPKYJosg7cvZkjxB3AisjXJZ3ZTXCu+TtCvYZhe3Cd3te25Ellg6iOnt7

AmPNw+xhjOwFtzd3MroIxEyPTPcAzQ3jeTpKNlsTp7fyux07Tjrsj8fKuHqCPT86pG3SJloPlbZ5/O9dB5OqD2G76cIslotHjieNuq0WYCbmD1Szjft1ulu2QHaWasKORUZndsK4Trvwdz/GG7boo7/a0o4AJw2rMuUuupR384ZuY1fbdnLbE/KO1V36D//Ggbow5ZPbE6q1ttmj+8cz90SWE/hHxrW3fvd29rjUzsZAVsa7l8f/Zair6o/a16Dt

EduYjkQhhlZpMSmjmo/ARXpWTPdnx9OqyePmI8aOu3ijI2iP53jIjmT2tbaoj6jCDPav0MaPSRe1xV8Zeo+zE9PH8EN2NSb3jStaj91MQFW9tg72l3cwmXO3TAq4puPbcBVUFBfbDBukhaAPWKKv2/83ag40YkZX2LPfdQImtRYmdzt3wWNADwVXtmMG1lXiVDtBj4QirPbUg9H9pDZpt2GPfceWE2f2jI78j8nX/mMCc1nCLI/8j/h2AHfMjozs

cY758yGO1bZnAtGP6wLEZkAFV4tRjpIryY9CcymO8SWvDrmIcqccjlM7nI65iVw8QPw8jsg3+wOIDzmOCrtcst+yRA+Zd/n30rcF9n6WBBKEhvsArMEwASQArMGZBZbIqtyyZYQByER4ASHGy6Y+XCumcyDagUIWcuwOafkEiiC8GKDcERu+nQ32fvsNh+H3JGi+diNXMPf1dh8P3A6i1oxWvA9fD812dtw/Dq133fadvWGXfw5rAbSFtkX997ng

XFfaI3kR5UGCsTDDt6c9diP3vM2jB0AxFw39dkujOPaTBi62NJfx9u6393eb4h/0Ao1pdtrWnrblxkg0Kg7qY4ALi/aVt4d2UPQ9+O1n4vdgR+oS/sX61nczQbYP9iWrkDeuj6Vxg7fINwYPJ/ic1073v01J8rG3NaphcmUXJg4m1phK2Hfr/DB2dEtxjhZoeGeQd5mMInzpj1Knmvcm9ve3zMlk1p22UAd0ZrRmzGendcfChqYV3A0VXjZ4TY0U

xdQnF/AOU6oD6jSkj48p/MgP1qa4o9+3731RBFnbDg55t6XzsRV3/XxnvfNK9WPUtL2f11CyA8dltyY2w/J8jqWNP45UMpJmcWKZCqkL8PWycnmDKEdAT8WBuQoQdseXcLKl2yZmKQwR9xlDrg8EDmjGoJFQTnn3tiL59sQOBfZYV+fmBBJScTQBNgBpAZhEWgCuhoQBqgE3AA4AaQHpAbYAaQHMwCApQqM3D4vEVNnoKvJsby20y2VFD7VCwW0b

dbjPDyyo41yyIznCyY4w9mhysPb0VnD2PKI8D/D3yccI9rbd6+dd90kDZrf+gMm0ybAlsUM9vIZ/QyIXY2ALoJm1w472tzF2WPdIljFFzA80DAUD0g9gjpOO21b492l8wsf49qyXNo/Oyl7LkVUTim7LCNXU9/7bs1jDIrxOVmo09iBnyhL1JtPzDMNegse39Oszu1LMEXrfJxcmh8qR8qCmhyL6fNowDzOPdgJGlDRhc2z2LbBX2zrNUHeEj6r2

pVQaRpL2ExX2sMCjzeRta5ZLuHcTNgYaUY4iO9o6yE29VBSPU8DETmmPAdpPR3yPWk6Zd04D7dfEDscORBbXidHgKohpAfQB25A1KL/I1qEkAdUB8AGkwSoAaQDLiUUTKrb/cux2xYqvcVc5IiH1jvfYb4C7iJSBog01Bu+rskJgyqwXAaCjciRObMvhI233Hw/t958PgXbNd0F2LXbdjt32vw62tNCANE9F2IC4MMKiDqbF5YGxAdZP4g7EuyOO

CMIdTUedYQjxdoQqI4cyDl22AGfziqp2C49AZul22nbM/a4NmpeQj5p2Nv3cTm04c7fRTv/Qw/Q9S2rKh7cHlQd0b48rhjIm/YOapgj0KHoDFyDGq/Zqumvd+ZKvIvzRtNyeZiuKgLeiQg1mGzVv1+Y2PjTO23sLEE+qGblOHzYXCz6Pb/abj4rwOWaHjEMCqLJ/mOOQcxYF4tr3v5n8NmVPoY7lT595l4LDLGjXDI5CN2eC5/m5t18Lbg8pdmiO

Jj0pd6f35U7zjcIar/afthw3xU4gdvbG3zY3CqeK1I42zAVOJwqFTqd5Z46gDiOx0fcfNzH2pfOcN/WScnL5T6+GMvXOD8Ub1JdH/dW3ekwaNkxmR8Opg4JnNlJm9LDGlzcwRjmdarvBVVlPYja21q+P1tBOZ2+Oe9ygRh+PPJYxxcBM692QRrI3n4uQTi9Kh5V2+yZM9cJ7Sg7WUWbhCp2U0E95TlFbV7e5NnJngfsRjyyW+cqHqxhHiPzjRxnN

ymYRp3+2CU64Rh4Z0aZFR3orZcrYsjxbJ06jG+B2jdplyudO6vYGdzV8oIqf03GnOlakZiMa108r85Mbyo5qZsdO87YsKxYncxFgSthHlOmPTz+PIaYuTO6PQSRLt4Gn+EK8wsnpwu0B9mHCyelaN3B330/5G3Qz87ZpN6tPP05fj35nRnUOYwDPPQoq9u8T/ZwzTjxnsU4BNT+Omro73YxN5GePjn+9VEzEpcMUnGdQz+N8EPr3j/FDp05a2Zr6

+6POS223IRuBy+QGNHytt/Xz4Ma0jixm2AL+dQBORwlK2kq63JZozkr9DIJjF7LbjfO3j0lIApbuZuxmgjZByjPGi6viYNlODmxTTj5NI07CN5ljXdHBVV77YLO6TfNPqrPiIDH2XU71jA4PoQS8NzlnQM+yNnH2zU8hNKtPkkLbNs4p6jdD8098RDa1TyPz608gipFDD1qHNmqyU/L4N+ZC5rNuTHtPimaszg+DKNjPTipmdgKjc7dOp07cztay

WmYVNtZCfM4t2gBDY9JCzwZme+OGZlVOt4LVT5hLCkKH8zVOZkKISkWnDk8lThVOGvFSzugkJ6rNTlZ3eWI0dxnnndYgAMXRoeAEwScHf8gN8aTBk8W2AcIA1qACOHYBbXfVjtU9NY/Ix2KqIoPMWxSHtesdwMMLHlic1vZPQQ5codPAA2mgM3q2nA8JlvV3zk/z1y5PRrYd9mCWWHKid84XfA5I96Ly1E5GF4IPvfbsx+0hBiwmxHRPKGIjPReT

gfR2t2IWiJa9dqOOfXbVbf8DoI4Tj8FPMId49uEryapDdqXH9RYu92OHDyOPeFP2k/y2aD1Qt/pyjfqOQGZqdrqOGo7LY6HbCHvL9ztj2o1honZ9cmkdl/zq4OWf93oOuva4iYToelZoS+6OGSh+jsTk8bbNFtioMKnojkX5epRTRuGP5I8f1G/2hcOJ2mYPf/Y4yehpHNHElQAOoPQ5Sd1gXI/7lB1PQitTF9AyJPoBckIqwA6ODoTOKUnZGTnO

N41Wbflz+5eiMxNcBGaijoXOh5ZdkMXOWc+5z+yDy8eSpg+HxGapjzFnW6v2CRYOqzGvNiS9z/AFz+Tstc8ylnXPp4r9TnmCJ5fIlLQ3JzdS9jf3jc9W/KgnVJKp1XqVvBHHl23OdMIWRnYCLc5s9hSnmDebCp3Ofuod6x3Pm0+dzldWe3ZrjDsXOtCwe59lQ8+JILB7astcg4Now86XxoHPbM4GETsWOKdbFzuXF5a8MKOH44f9jLbRM86Z9qql

P1eV2yr7JtA6Q/+m/DYng8rHNzJ7NrS9keurzkKCSht/N3DiL7edFE1Pu4w2xxbN0s4rz61ODgJHF5AzoDeOyywIDsukd3VO9L07xpw2X7cSMDeWKflXtwzP/rtnRp7Le87qlwxnidtnzn4aMA9XzocPhY/wT0WPCE6F9pKCtaL7AKABKgGUAGkABgD7AMU8rwE+waTBkI2cAIPWTPJps8Yh42AK2PhS9T0CkGc5I3AqQfVB6HXbRnlqUPdJRAYw

CbDVQLPWTQZAIu8OpE/C1hVNZE4djzwPxoJBd5337k+Wz8GrQBfJA7iB4vOYUvvmjeVghin1IpGTgWUhVoeOziOOTE/yd0rW2VhMgUFOcqMTj4N2CeKT9tN39vdW7Bt2sFRb9+DtQNZX8u5zcid6oyUkH7ZvGWA2IxwXTEtIvtIPt6ob0dvH14ePwRMpJnPK6WqexpL1N8v4lplpwfCnco2GcA74Rv7DOA8jCkJmhupQQSSWI4ENN9LOkfoEVWd6

RI8txqfyzEbSzwGUfmP9zP4Pk0bQqEexcc9QOtV4Fezd5k4hW5euMEgOfjGx55y2sSHZcuFLbAYTgewH0xFRSQsXJJuiOrMrzmvBctiQsIiVYRCsHqErm1HXFgau5DPOpjGHRvtKlyt/zmSQ7k3pYSqWuC+aJ5IvuWoeq/w0AC4Dsf+BN8+6Tll2CE7n5vfOBBPiAIQA+gHpAczApXTNpe6oDhGIAB6GbfAKcHSi2E9a+OGb9QJzHN4AsUBBAteR

AEnrgOlAezLNdLjP/xeyUBdSRdl3LKWLbw4mz8CXYD2mzuRPZs4pl+bO4C8Wz98PEC/IK5AuUIJ1Ke8UdhwIcC3mVXkYtF2L1mShIMzZi1d2tjF2X2yxdlRZ9u3Y97mHrs4yD27PDAzjvIoOZiKYLr0Xw8fWyov2Do7vpmLH0/2mjguq6Bpe8x62Zo7CY/gv5mNQjj0YIS/sao/HzTHbQA4MqivqD2KPzA0RLma60Cb2Jp7k0S7Ie8okES/UZBwN

1Sb4LkZwBC9BzpInzPdix0kumibPp7+69iahFyxJyhgCjnG7tLxRyiqOCo5StK0xbijm89qPvveGj1/kmRfsqWaoxOVHMq6PaKWsp2y7renpu923l1cWds2rSBXTdm231chejjLHCZMsOnUmvo4gJujPA8eJw6nOUgh7vBxyWU4CYB1oxbnuUVJPPyNLFso2xDd0jqlm486jzyeDr3piz7sYzNnHFr/Wkkodz9YWd5YrsebGK8D1ZoLP7zItTuy8

ufY6Q/B3Cjed68MhlaChjqYP/S+mly2Jb5YwYDz12GbIctNmY1nbzzULCos+D5hnxI42lrxDF8a9L3qU0y+jNmODxse44qM220Ic/HSOx3qNN2NmaFmMMpyCG88rL+M3qy6/15Hru+LDIeT4IiF6fBCm2bFyN2uPtNwvD6hDt5dnFz0uI9wdL/kh8VPPwPZ0NM6tT7LHAo+nl3KXBhHpQQ5W84eX1hBO3bwOkVEhI5ZxF2d2z5kQwZEhmxZlUPLO

6YoKz9l2koMNooQBirbKiI/PGt1HAf/1JAHWAOcHpMDi2uPmP6L2q3gBAsCc0kObtmGqwEECOiCm2LRILUClkdIjeAH4Dk32jk6thQj4jjDJ6nW9LffGz633XA4uT+2PwMKMxm5PvA5djqojOHKQL5CXHb02AN0S7Xfch9VBCpv9j8qBVI2OFdQJJAyMTq4uqD3AjvmX8eyKdmtWw4bBTp4vRZe5Iqtx7HDzuwwND8pVhgH2ZaqM0XOXOlaKj8Sb

rDwI6NOWpS4Cu0hNA84r9qeXVqYZzvzwWxdqdnPHkWciLyphxUAMKxfOCdGaNuHDa8fsihLPFScejtmwrpdCwF+nFVctIMmBpi+Ad8cE/s9uKwvKyMVsSkhWq0BxFP7Ow7LOAK9ppILGV3vKf8cVuoaO00nzjly2CYAgriFBxK6EPAv2uGqe8PyvKrNvTGaFqOZYakEqnPnRo7xOgQ+zsuNOM4tirgJPj8ATspyvMRyId7ba4q9FNjBrWVaCrpU3

YFZIoClXcaM+apqKirwMr/xObmtiQqNAW53LgcKviNRDLqLP1tN0mfKugFgNQ4JU8q522ouNbSgyLrZhVWRraiTodgKgYtfW2I5CT7KzFK5VYMM3n2QCL6KXglUz+LuX9iGpsrV3v2MDsMQwSh1krxly/c+cLvWQMDZz2oW2bHwWeRr3244wT/jOewjK96VU46vjgumlQKMNLM5Yj7Bjxhwd5scg+g6u2k+UTXYI371erkooeM5+gb+2kKMEzogC

Z9ZQEOnOFK6OgJSvKXY1z72yk8/bT+wwRq8SurHbBmiSz35h1K5xhXxpe4BjYkJ9sDdKMPqXMuqjTxBMdTZzNwREGM4TTlNmdrA2N8NUcM6BNkVW0MF7QiquavwID0+PujeMr0k9ptjMrxMXgEe21jan88s6vG8A5M/vj6EFflL8aNDApSEo2Yfd8yFH3VaK081sridB5924Dijg0q6uQDKvKNmArtgO5LZONm4hNja4D6fcVa6ZNj5gxNmcrzKu

Q8mVr4BDP10Frxk8RdL98zWunARArwhraYFNrwk3gmRvd6Wj1HbZdohOWQZpAS/cX8o6AYgAPFHXcXJwpMtlj+8XM8VlhxZORYrb2AERpml58G3RFIfIrVs7VIcdqW6YLMr/wnUuPEFOT4yHQIIWLhCurRJgL0LyFs7wtB0GHYYsVp5O8cE2AR8vMwygFrNX6En558EiaYaW8emGrEDDuI7Ow/fmxa4vTE+xdzk66YauzwN2uPYmHKK7PmJ2ZoJO

PLymdxrlOmmzqCVXkWXixhsYS49vYBguzqKnCUaobEpnrstNadw3oid3IKK6VqrpB3Vk1sQwQmm3qJt2aISCyb+o96/ltghMj67ZkhBoEh3gsbUvwxZpzk/WuGWTrhh3R+2m99pn7oGm9ouWXAn9lkuKdHsD3A+uP64looWOSi5Fj0cOMrckD8aYRWIoAVnmNWmUASoA1qHMwJahjQCqLl4AJKmMwMrPQ9cnIGGIC6wSYXG5+i7lLA55KWCMoTGB

QfQ+a+FobKlTrsCX064zMu32Zs+uTmLXa+bfDhAuXBIwrtNXNgEA93Cu4XfjwKiAOZdS1ICPxak3BrllctQ9d4xOW6+IL7vX+Qo+VOivZ+cTBm7OmK9WPbIP5toOHW635G5GjmrKiG9N+A4cdmrvTfTDfpAPLxkHgG4NVteI5o1AKCxQeAD7AQgBKt2NAZuQgwAgc4unY+aN58unnfB19gcdBEStiXVEoFDRAPwTepxxdn0pNQdayk1jUmskJ5qA

YV1mL2CviZfgrwLzEK+i1p2PaG9QrvDynQd/B+aDSE7Vj4R1y68Wt4N5F/QxquoVji82g49KcqB5xgRuKK/ww1KiVFkB8WuvO685A+P2VHNjEymqZiJll3eOdo5YlAI0KyAQjliUHRkxgJpvH4Y5L8RBka/099vGmwIkLjW2lG77rZkXZTeAajbayRKS6MlA78aU99ryN1a0LyOAmTOSrvGiE3NgNT0WSgxKr4huUkbBpLpuOMKC6Z35rbWsurZu

+3YpTvZvpnQOb/Dqjm+zybSUVm7IIDp2EEvxkOEw5m5nJ19Nxm/20K8mx1akMXbmCGSaepAaYO1abkG2ZUg4LxdjGnocjy7F6JZRzt8my/LIIN8n6RbfJ+HOcIV/J8Z3vYjJCFjpIc4i6TcyF3h/rgJ7H6W2r0ihXC+vpf5rOyMM3KXPU7EGDMxkw/s7zyQ2XU/Ua0ZuD5d6lw2xVUHmjwd59EOfl8NUuS+XxwCXgFYKl4z3C7ZyriJH4E4LnDOP

djapPf9mqFb9F5rWcTZZ4VMgpGzabqK3Qq5ceu7PpS6CWbiaaqswlVTnyBKKDiSVITbH+s6yKRb+LnyuWZAqQMnqRM7TElxPVa7uko0Pig4UwijgqTcpGbRu73d0bh93ClU0AEANceD2AYzBubxMd+kAK+g4ASkE+wDBRX7HQ9YsM76y8GD0mu2icxo/kqyVdYEgsKC1xI+/Qh2Xu6lIbqNWDhYi1ka2li+obyJuAeOib0grYm6dh9wTi65EhpJv

bFcToqoV/Xr0D7ZkqPJUKK3R+bEbr+hjd6eEbsxOt8giwUpvhZfrV8DsFG5azAJJ3oALtkoPZs1Bb6n3q7fezXtuU4uXLjHLy4unLpkuV3ZHh4P85ierdmvyy/bJL8wNN4esctt3vm77iuHzquQPvDput2iaxtv2m0ZyVhNJlP1jqTrHs8sTCQ9gD2/upHIbmW1uwgnyKDa9zuJPl727j4m3B8vvbxoaEY+ER0JXXpim1+3OQEo5F5Lp1/ZXhsZu

3uk+roWsu6mV6LpPlwLtbsWPMrZlhXAAjNb2AaTAlqG2AdJwjhH0AXABBgD7AegB0eHoAduRXYZDrl8uICBsuVFYADMfiH4jhsRh2Q8hulgAyPPmp8UuGtzG/8JL/SQMgm5cDkJups8zrjDzs68pllCu7k9djzYvnQbMzePFNgAQc1huQhcBqKPoIsr2UQP2XcAOebOi8m471oRuqK9K12MgCBasTmCOB9ax9pjEhMI0r+VdosYkroiPfJeZ93P2

WqIrd3fGTruxnWrLsZyM917PGtc2ro16TqU7oIg3I3u79iiOZrQDqdkwnq8CThXHGHY5RzbG8nKOVuYblsss++lAedrB6U9v1hrMNk7HGoyGbo0OEMSHzkL6NC+LgWZvpxHHzpe3JzFhbs+NMmauG91cakakL3XUMu+Obh6ipxNtb52uJA70b8aY4AD7AaTByraWoegAOAHrJCSprFD2AKZO9nd2d0PWwDlG2nYdBFpIc1xvsNhraP8vm2RVzu/m

reFBh3E2YAqqhpC55nh4JDKjGO4Gtr/m3A7CbrOv5E5r5jNuuO7QrsGqti8wr/jun+m9jmkCiWHirKspVMdDY1M45u1yb9vXw/aIL+TuRG9omcgvJG8YruCPjbcqSFvKPLiTKiMr3YgozzsqM7cS6HToyNyEFXDkR6qmFRGksHqmFTTkv9apq7FuICEI+4UvCisYvQGvRPemBf3OMpakYSMX6tclTiqW+q7xK4C2TLwyNu73EqqLNts5GNYuKoD5

mW5cryFOV8aqiq6c/babo9luCSjWOPK94rq+YyYuTK87uVmuAGaHrrmuxTbJ9lnvqxklrqqB8Fdydftuda4y8dKvqsANrlBF4d1QJX4r5LfLzKj5d2RHk8CuDW/8roxVF681bs9U/WsgV6euwvZHk+2Toe8Edr639brFDmBoO7ceDMbuXngm7pDoTibF8I3v04m/QHZLcibka8buM4nscpeBMNdTnP5ALe84VaehwDeANzHxXe5N7ne324tt743v

7e8tLisuXe+nku3ure6A7hi29e6BEWw19DcGOeTxMzej7i7G7Ddi7+TmHry179w2g0+BNmtoFoBV7kjOxi71b57wQzA1wb98q1xhG5DnjjbNbxKuI52G+5E2oyV/ZgXuFa6F7kWvBk20z+7XGEilriMvL0DOD0Y3ua9V7tVD+jdVst3Jma+woyBPm4JTQt6XOW9+V/1PTEO20sno1RseWDUbqq/QoeGbBTa5yn+gU5Qvl+G6wzb1Gzq2aoQRsvHu

vBA6t9fuRTeBQtqXQaF4VNfvqZQzggovKpf+6I/ur+8G4Yau7+8v7zhUM4PYkCauqoG37+/vX+/Ez0ZA0hG51zHvOcvYVXfvYrItkZ/vgB+P76H6Vq8hsC0sNq6T8oNoe10X7t6vHklIoAhWX0+iPb+G4B/EkdAfWkQ9o2xBR+9OQ0LwmDElLZ4O3jTZNv50NMmUQI1vVc7u+1K7jGQCr80uFjboH7DEGB+775geuBVYH/TP1C8Jz+sgv9Z8ZoDP

0Zt3YvgfDjeQVTtP4fGmKEQfiTex/dQUGB8kHjwuY6UoH4P2UjaON8OriB6sYO1CMTYRyuvv2A+/wfAekTcxNhI2Hq9DT2lsa+4MHlE2tMWkrllMyek0Hu3yZkoWr8pBpihsHrE27B+iQtu1TB60H7E3C8Yq4AAfHB/cH2we1k2aPB+v3Zz8H5wfRU48MSbQEXuX3Eb7zB7xsXqvVaht82vvPB7arvoq2uYkHgBUiTY8L66y6vHo8LTOy0+Bunpm

LBYGTd5mV5RTN9hCdK42NEzPObIJ7smuie+m/P+Kl+8goFfuCB45g7C3Tc1ZKOfuWcsQH3OVyLYn75/vzRqdG2OVGa6H79VAWa+jQ1GmAYGx+zU2jbL96TMaGffdrKYez+KMVRn6eW6sr2saCa4bGSyvB0Piz0xVvKA5MxY2zYDtr4WuW0J+Q53K3FRwag4eMFaOHkRLRnkOZ6020FalIGvQrh8tzWEPQlX2H9BXHh4voZ5mejevGnBXba8uHz4f

m8hmNrq83h4eHoWuAR/ss9aSc/pgmnvu2e96c+vKAAq7ylYeth8DN5CbER4rQl02+WDhHpCaER5r+9EfCq8xHsDvnCKK7vpOWhbXiduR9AGkwGAAu5BhRSoBmG8IAMXRcoLF0MXQyu/R4HDums+hxiump2CnICWwqHROi0NuwDnR2FWl1YDNUsTN4M4isrW8dy6bF9cvgC51d0Au5i/Ib3WK5u7Y7hbuXw6ib5buYm8dh7zKHIc2ABZP1s/npjCD

6ZlDCnrb0m+wLoFtuHnWt9zGa28SDs7PvFaMMq7vym+m2nJEXO8VL7g9KncEPBd2/CrGPQ0w8RZzqVJXPvamPZ487IhWqZFO+S+BkjmIl6gv4sgVP0kvVkXu/s/hRhXvkBqCabeut6g9SvpqCGvGVsIbUx4Kapm3AmePTDRq85awDrKuUq7UBO0WPQo8W8FqCW7kAkxo0kHtF8sf8W+fTSmEiU5BMQe2rUb+j85uh3lT6fVI4UsHtrevN6nVF7se

SU68/WUvP67ce4N8AIknqWGvWg8iTkUvEo1vrl58f2/yaSHzRx8IZyETqU5VmTdv0zbnbqkv/s5rd5sfBx+nDdguam8i9ErGlcdRTlBC77okL1rWve3YL5hHo0Vy6pLpFx9r99dukk/2LX9vt24e6ixH4u4JkCOBJvayTx7a9m48R7q0yk7ur2LvUc8HE5vOXVTAnjyTu85/t7PbAJ6Xi1HbIa4AnwJH+f1aaVxpOMtS7rgD1853V03G+M7eN4I3

0k/AnoBHRzA5r7CtMJ9b3S+PoM5j26CecE+EovBORw9AdEkf9xfGmJcO4AAEwOrcxdHxAJahmG9ytiFEOADvctahg6/ZHsYWOQXKSDpZLYhw0ryH0tuiwS0mU4HMXe6hn0LphxvEGFJJQJVLoEDldtYXe+m/wZWgbyyKrEvnnA+m7vPWM66VH/AqVR+Qr52P1R6zbzUeIau1H3o4tu5Vee2y29gu3VSN64BGUsCObR4rVo6BvfCbb0XGg3dSYtdZ

CYCHsJ1AZFdX/P94HYSUgMjYGquhBbqSRkDCwSAg2oG5GwrKp7qG+d5oGGDu12jDL63oLNzgqNzoVFNjbSwsQSME5PkFbVJiIqH3UKBE3iHaClNjSp5Vocqfhri9wJmRS7irQTdQ8k72bz9hgVEUgQDJG0ganoKerkHcVneg2p7ZQS0g7KjypKDKDCAJgV7t+p5rxHaBVrAxr2Ke3e2WexcQjPBiw6fB3GB+gZNdSYnanN4ReBEDZk9XwDhxsPX2

Cbhm564okBa8GUudg3mB7pzywZVY4eu0NUfynoqpe4FygCxBFAgyIAGAKUisZs9QBp+mnzqfjMIsYfDALVg6VRU7Lp92bPtzYxx+nr3FGtiRIeawxgsvgNHZbDqUQQNQOmF+nvuB37qhnsjRyHgSoLxYZ8iRsRGfwZ/+nuyriKisYU9v9EEnH/cSBUr+nlGepSzlkdWQnuhCwXBAOjcCwsmfkZ8hnymefrGVRChQmqxzcMGf4fAhngGfVuHgrB6h

bG04QDFFnp6un3LADTkG4F0gb1kYINlBc9u/El6frp/FnjLgdODagH9BoZy1DuiV0CBWn7fg1p4uoVQxwySvrLJdqB/dXT6eOp+GnrLR9Z8wIQ2eF+rDEwqeO7mTG7HHEIm+oc1sv7syn+A4YzHiwTlg7lhUplgkEojVL9csTp+XUTh5Y2ESMXe4NkANUSdAmrm6CTaecC9mlJfcAVi5cffAxeZMxVMg3EDeEB0gzdLjQRitbyxntU3PdvdhAMiX

Ip5g4TOe8GGzn8B4Aq6ccLFZfPB0nwkggy+KIT1z3YsSwZurK5+0nmJQa56fmB2FP0BaYT763ZPuUAb5W59JQDpDtowYOWOyC0DhgGtBe57UKXSfS864RUjY9CF8WHZnm577nqPWKNJuQAOe76D88dnLFWQnn6ueB5/AQtVYHQ6SICZgAKPrpkufSjLLnjO4mvBqZfCcp2GLn5RAz5+2RAKu7p6vnk6K1kZ7gungtJuYW3vDqp/NwAHxkNjWQ0Of

pdNkIaRTyxhNnoafbSk9kL/RHNq+8X2eFnlAXmaejk0gXsTahRweM4ovwO+JH+1vxw4QjBoBCAEvctvppMCGoaoA7BWMwY0A+gFOd6HhqERsx3DuYcYu0Cd6/9yDUn0NosBFW6ZY1UCmFsTMvZ7dye5RE63+8M8GAiATnx6gk54Tbwa3pE+Tb3D2qG43bcye1R/gL7juGG7W7phvrYr1HgLLmZbS1IcVr6w9BT5PmLTW8P0F3J8BT6OPhEDG2nyf

j6e7rg4cCzwaniqB+anuBg/v6IK4gUaf0NTwYJnP0hd1LKOoEYZMVJ2WiDX3nrdRIpHhqEYy658an4Kf3FfFCXVif55WnTJWdhW6nnBA/F/a8/LZRg2gYI7j1Z4VMDue3PLknz9gmGAyISyJtmFe8Jt4El9TIJJeOaTlLKSs4Z6VYMjdrF5+XLuervtYBPnhv8G5ILNQyyD/IbJfefBOrc6Al32pn83lX9x/3Wpfh5/KQUef5Jr0idKgiglGQZOe

Ol4aXsefygixANK5P4n24dWB2l6GuTpekEXznd0MEutsXkJB25YpUOpeR59mXqWTlZ4NEf6ea3Em81ZeZl8aX82fb4Etnn/Adl7Ro6Oe55+z2Q5fMBGOXv1qQCfOXtKel92F2ZeQtl4JuU5flbvuX3Aul90lnnYdFl6J6am6Pl9jntPSgPq7ICqB+F8mXqOfLmxjny5eA2GVRUITJ8H6X1loAV+hXnOYrGFaYGrB6rerulKetp8+Xgv5/fHhNKpe

HyEAH0KOkV/Sn8U0fZ6mst+47l8hXi5fSV7b+JGeeZ89VC26SV8Qp5W5gZ6TcfGx51Ninrochl/znKJfKUBiXg/Y4l7DXPZeeV9GhQJeDPGK4EJeGqJFXm5sDl9gYdxeYYn76Ju4pl+5X2Vfhl8/4PRhU4GcX2KQrapvOmRtSl+e+jafqV4eX9fH8587n56Ayl/w4FOeg2ASn95Aurr1X81ecl7YJGxfbcomnpywwl4bn/xfOoFMXwgwL9HI7kTy

PV6anxueeTBzPGyUfF56n5qeWliZkbRg7KknwCaIpTEDXiJeWp7wJcKetPuIyTbnTgUTX3qftW+JFOaebV/TngtAE18Cn8Jfs1+TX5g1mV6SjLNfI19XnlvBTp6DnzefM1+LXz1ec16XI/efAUEPn78si1/rnoNe+p87ES+e75/8ewtLw15LX6tey0l1YkpBM4kaCJwcX6CiXMzItk/qnwmAzF79XvMsZxDan18dVeKdsV1QXV/Gn5FWEMy1ng6f

1p/PYa1f4p/Tn1FAIzHlnsWeRGAICmefUp5xX89fRZ7en5WgtPE1Xy1AGVh1X+9eEe8vX8HwGNEynx8RsZq8XiAR6V7xn1GfkEHFX2qepV+9VIDeKZ8VOvlf/XBMoWJe2GeMWPPh4EHhnhoLNZ/AwSqXGFpf+GGfkN/30ZDZmEDtaCGBD4HSXuVvqHaQ36OyQOq7IkIEoN8hn6ppG7HRnvRceM3a71QJyN4KX/DfFdQqX53MTA+34NGfoF4pXmEB

kv04341VvhB43wiEKl8SnIpIal+a6SIdkNg2YMv0CZ4TYNFfIwU3WHsIVIguaz9A83DaZopAHk1pn+uhFU+IxamftoE+KGBbWZ5JLbwUfCGMEHzJDN4WgPPgTN7Yz0ZeQ5rBX476l/2VRZJAfZ+7hb5e44ldXv5eeulc3urChR27hJ5fIiFFm4txx8L83icAAt92M56xHakaGE5f9N6VjcLf3N7cMNKtn4guZMHATyn5nidBLrwYrAIfEF6dqGBf

vpQ4efiBOJCGugBeBiEJr6WvcTW3X+Ew37yJQcpIP8Dz4DC7O+/mXn5fvN9q3j2N6t/K3preAHW1VgBvt86AbyDuQG5lhZB1qgGqATAB1gHbkbAAOADF0ZgBnAE3AY4AqR/iAdHhcAH6xDovRJ5Q1U2Fwni+WXANdW3QgBAh/4EBEQZUel40sDmfstdOjRxfilrOn4OfBF5m70JvfqugLsyeaG6W7qReVu7IK3ju/weeTvzKFF9oKm6r00B4yKsp

fIdcVkJZshzotcivZO8orjyf/hcjgJ7y449iEspuqteeL5zwq1+DXkDtU1/TIdNegZPoL49e058DIQtekOxvX7FfAV67XoiRzF42crOJuR7dn3cPMZdB5H1ewsA+YDaKyphtn4R5pNfhLvVevN53X+xfYN8Gn+BeC3Gq3uxfDRVZXpwtjBFMXT/xil9a3jnfTVQqp83oXnmYwt3MU565sLbOPCh7CGO4XoDygKaB9ElG1eXf0FbvgI/BVN5vIHgQ

NnN1gWIskV8rQXzfgsHZn6+EaMou3uteN55dL47eLd/uoK3fnph9V9efzp4E1Jwij3PQXwbeSu5lhJbeRk44ANahmAFwAAYBpMA6AAYBpBI6ATABmAAGAOBvqCuEnp1X3sD1gPSd0fH1YVocBMwWXMsFbSltkOArunHynv1lNiwOkGJ5dQbK32GeMLrDVsbPdXeCb+8PnBdY70yfli+L1s4W86/th8zH3Y6Lr0hO494LbkIP7haraTZkwhJ0T2uu

IzxnyCAhuF7+Tn4WAU8Kb6bY3ZCgjoEW4/YR36RvQxGR3r1fn6Gx3geh5YphZLJfSl+ugI1fZ55NX39QN94tXrff5V8oIRVfQkG4eAjQZV66XsVe0fCCX4rhIVWs5C/f1l6giL9BMN+6gNgukBYOIGZhNu2FkcTfexuWWsteLt4/36+w+VicQNmeOCEt3vcjuR5/Sz+IQoBrjTzfE4Han2We3YjVWKA/2UBAIIVCVJ5eXwQh4t8ynlA+9bJrjeFt

rl9i3x74+NGQPxtZUD6SoqrRbiAO3y6YdoG6QZuB8977K9vAz5jy3n2eUF77Xm+UfNIoUEJc68c630velbxIPhRAyD7wPkOe3fB+cRrf+D9k4Ug+KoHIPkPPRD4a38KIJD9onzgS+t4Ynz/1vd4dbhCN4gFIATAAWgEIAduQWgGUAFoByE7Fd5QBDhFN8JUprHZ24kSfGeQqYf8h80GDeFi0/vRwwI8KL2upr79BAK4dn6isamwLoY8HTo08XRjx

llsEaDTDowxALlMyq9/ALg13a95fB+vfxrZPJJvflE4eT1RPrXc2ADcOhO+73raDiqQtHuoV81aDji9wTKlZxy0fsvNrb87v62/DsN7dxG5KdltvjF+J3iNfg16MlMXf2d/hMexfOqiHntlZtd8WnzyuY8EX36ZvWj/mnxXfdd4xkbo+rx23rGnwykCw41xZ995HrZUcRj/B2IREsi9lmB/e5V5CDNeert7TkE0IbiHrtVZReJWt3wOfbd4g9TVf

FuhiUbqBqWxWP+tev9ddnr5B3Z+p3lFtTj72Pug/EC1tnnUklW2d3y7ezj/Mghogyp9/nuqevCVuPt3fV16mn02fwF7TXFawc+/GPqeG2BygsIKTgCE13wcgFd/OoJXeP16F34PxFxFF3tnexp6aPyXe9UHt6GXe2lwCn7tek15B2mGeOVcNIOW4bIxOQMnt/XCSwOtBlgVp30neGd/b/atzxxfV3zmy815PXwMgz185NZpfeDLpn7dVnd61Xt9e

B1DN3he4e1T8eOAgmd8c1u+Ayeky31VSsESdsIGTv54lX5DYyWsCQUZfBZ7lPxDO2B1eQbOdX9+HMKDLvk9yi5kJBd7SXtvBSN//lekOqDmDhle5mkFxnlGe6N8n3Ngh+ukFBU/6WN/yXlDfCl74D56w/R3wr50/zOHJX0pcBN/8BB0/oCCdPhtfERR/3gle1ojwVT0/HT8kHSma1N8GYdFeVN8DPlW9gz9jPhIILKxxZ7k+9N9ZQ24hFIHAoHw+

cGlhX8zfbCD6N3M/2+qqwZJeRl4eoRzeJl+c32uUyz+8PvBByLygy+A+ZZ4c6zCIGz/zPps+lZ+eXkLe3l/wkaM/Uz8iHdA/Nl77P+LeIFxTPlHA0z6uXmLfRsRGlvTOgz6nP4c/0mCoPnhsjFm8Zgg+vT5DP1PybW29n6Be2D/3lc0+SkEtPgpAS9/EPxSAkJCPPsYIr2iKl9+eDC32OyDO9T8TcA0/KSDvPxOeMK11Pg1B9T/s2HYDZ9kRbJ/P

vaES7mr9VT6RnIWfbQr/PywIISYjgLmJ7d7APx3fRrO7gSC/D1mgvqzfMz90314SIjEYrGjq2kBQv6TfFN+kiVChLdQgvzZccL6Avp3VUV4Ivo3fb55IvwC/bCMK73pOMF/6T8aZzMH+llJxuIGwACHiocfKoaIBE+ZVeQLqt5D9X0PB9lZgsKuA2YEfEAxOjPQG7rnhqSBDiL3xZb3aENRXbB0DIIitt5EcD0I/YGMHp6vfZu/u38JvHY9gL25O

Xt41HwuuXQeeT9ra0j6UXt3sUAj5gD/pMm8iytLUdXJrybReJ95RLDWDq1eU7m5k8wagAIQBowCKVIsGqwdqkEtkIAD50RoRyeT6AeIBiAF3iBABxwYaiaEAxaDwjfcg+IE0AJIAC6cwgCK+ubFTadwAPMGkgXHQPWGYwd6ofQE38XmGmL5lhTHhoeFycPYB4A2s1gTBNgFwAXABNwCw7m5s7MGtVttt8FBlQRjc/oHTWBhe22H98P96HKG3QA6M

WdlgOWe0M4n4tU6Nhdk6CG2a1kF+Mm7ejJ4obxYuHt5iPgj24j+H9BI+eO7ib52Hnk6EnzveNs/SPkchLeiyPuN1aPaRwMfoOqfwLpuumwzO7yHf2YbcsSxB7R7n327uwRh7tcFIHudkt8LMekAeIIBakUpicyEcp5sOntjhtKySnqgVQcC/wA1uWUzQj3NfM2At08SgPmDizRStCWDvocRUyC2SzbbPHvniUU3Rz3eJC71k9YHQXSCxVMaYHHu0

Amg0MOwMEXu22QmBT996Lt3swBwJvjHNCDIRe5aINTMVHInoHw0lUam+0LuJv3alFK380KewVe5wHVm+ib9PoXjWzSHkgKoMQUDo5mFQ+b7CwAW/2pT4+ZWgNmDnUqNu3XAingNmJkKBQWRoE4FCQYjAacG1rpUYlb9jc1pxVb8bsW2tlxcQyxHNo1g5S1oh9b4gDt3xVngxnr8UpTF1vi2+9VmkZ4Pw18xQK9AQ2ewdvghUKhEfCb/dz7mKVlVL

3r+z2L2+Db6ATeawwkBEuJ77mjU9vlW/mpaFvnOxbSg3nw/tiuD+vi1SIp+HMDpAc4EhWgmB9kt+vh9tU79UoS8/gBrbYL5AdBCSjZO+87+fXAu+DAVpap0vP1Oc78u+m4krv17uBz9xsnUkmi02zBu/ARCbvjFIMoFv7G2Wp+3znGMRO7/+v1ZRm7+wHuOBsIH3uCRy4Udzvxu/XDCrvoiyqGErEdCB7lFAnu1pCILnv0e+MUm22GLgjSC3wFqs

3XGHv/O+x775y4SQ1JrPoT4opTCPv7u+Mem+SoAhJizbYK++N767v+e+T7/L873Brbr9X28An75xWl++t7516Dfy68FPxTD8h7+fvke+075tldsNC0E9QFEgf75Tvm++nX25BDxAuEH5gBxLZ77/viB/qu18FA/YjrcMDw++wH+PvoxUWCFVQCX6C6EHv9e/f7/Afhe/jC7Ii3Bz4tyxgOB+K79fvwPa2dlNYNaIDRA7jmEFr7+YfnXM6MHXhCaB

hKEYfze/MH9OZ2GEhiHlWL/P8H8ofwh+Hc3iQ9hAYlGxmIR+MH+of+0Zk7hodOL6HCHAO9B+qH7fvsPNUYAu1sRg1ogv7bh//790Smy4jvCNEb5KlH50f4vbnpjY4HPvRzGMfgh+EH7CRudQh96mKXZbG3GZcN9InIFhCc3By9tkiAfwT9Ice6XBvH8mvvx+me+dswJ/hr+/QKcdxr4NWXx/x+vd33re0F4Yv9Q/MF518MIjjgBmoLskOgH0AfEA

08QHkIQBCADswegAYAEsPhLbbHfewdAZWIsziZLh8+GF5ljYcWcQyI5Sc9+s1G8hKi19iBlB0RU0n2NY8wnN39KL9J5grpjutL7u3gzHdL/Y71YuDL/WL+hv0K9kXtRPVt/MviCGL3E7bBvXMsDaIk4vMsB7xEh1ju8uL8HeCm85XNsheCGn34p3Z99Kd2xOXln1OC4ohZ6fKWG/Ib4lsaG/JbkDv5W/Lb4V7icAJbEzoU8tZaWefvW+nb4I0d5/

NcxCE0wvWHGTvvlBiuAhAu1h07k9ING+4Dfifnx/jcHb0TvvSb+dELjJ9WAalm2EQb7knp0qQjH9+Mshl5E/Ci/hM2Ev6g+N9o+z/ETeK9MoaAac5Szcflpg2yDWsCMwtPp3QDf7R9yf4KF+2BHF2U1UQr3TQQChXYBpYJS5kNNgQQwg1vGw3kE7cNQhUDlK/8BTIIFcfofywZXfrb6BEW2+kfCukm65qGjGDIvJ6zCtnISAwIgdIadqHHdy0Ia4

doB+GiVBlVoIQNBhcgUSpjrZ0lCDL0S+YqH1QMQ5I3wc4FpsFUAst6gDz0GN4jHtGPAI3mW/Xp9eCzulC74Fqamf01itP/Cm8Bh5f+4H4IgA0D0g7q9voCgQiUni4XMsa/X8BDq4OZX8ae6hVAhLgPNxGtniIHM+WWOsQcm0lkvQ6EE7f4G00W6sMgWAlGmdcof8lCBAjb+bxHcGsB/778t/+7/VwM+be7/z4CqB155rLk41G366f5t+dIUPYctA

wRwxRD/2qtG7fpHS8TGIqSPA+VlRWCQge746fhfux36rf7bZ+34hAipAJ1AyBUKR28nzf9QGl352HFd/doG371VtCYDkKAaB3dm72N1/wKC9hKa4I3+ZkKN/K+u6fJDYQUHMaeCGCFa3LWNgI5AfIY0UIVjdgSrhszVxbtoI3X4FjspJVBT7uTwhD6AD8I63yAVpfu1+dNLpQt1p5YBwVDxaMJEOmjUz08ASoci8M78U6mcr0+/cj41+cEEojM1+

ZDAIDRq5awFhF4rJNX4pm7ccot+Tf5ZXNFi0vFhBg/BrHTyBAxI+TLXQElCC2LEB7F/IQLulVJ++O774PYyXv/CwiUk2QVRpnG3bfrGQh+w9jSCRsmAKwOEn25a/gUV/eZUvAbrwmSBqwDdR/SAmLQDeR6QaWRhITOduYb5K8LPsue4bhdkw0C1B1ow1Rtr4soYtgWu+thK3LHKHlL4l+uNBktgSMMcX2UAZfzTdYNpZfxVk+n98EDSxYaTd8Opd

ZlNs4zlgWdlYXHz+KFCsJeRWkK0tf2aUoje8/+8CcEF/SC1/p0Ctf2L/Qv/i/i+D6L7KLr3nXa8FYuANHgOx4IwAZqCGASQBN4mMwTQAaQDvFgTBoeAwUVX3OQVWjDlBtXXYQTpUfY5M2WEpzCAucg6NFyEAycR/XkFGv1D3olC5xeR/womWFqbubY8mz4yedL/m7xa+FE+Wvya2Ni5kX97f4m6ZeF2929EH8MM9Ad6DjxNTYNDRdmTvTu7k7q6+

fMdLgPhsTrYm2x4ubE7TYv3Sb4ETgF6/+5wezp6/rv/DsV6/DcHu/i7RHv86P0Hkrn5MuLe+Ggvevv5Mbn+K6T/kTH7Bhk6BvH7cnM4oh+85X+5/1GUxgNzR46xz2dl+VEz/Id5+QhURvhx7+X5TIQV/Yt6maqx5hEHTQRBcnLTBAyCh8+CHITARsAf/IfZ7574eVfexfVgOkKAhm2Urt5VQomCqgYAbTliYYLT7EC3vgfe4YMFxf2fodrD2H9Do

S4FsYixAA0Ht6kTfk4BG2c4uPgs6YTbtp34PBgtEq4CS/5N+dOHqIXD+B34y8ef2dMK0+35/pGEG4OO+Q4DX432p2RmM/xhbQll5fpWei78Df0u+Zg8F/8Hxhf/bitYBW78tnBc7rf5WgIX/3dHt/3u/On7HfyJ+ANZBO4uBOvEOsIlAqGFYbFQFFxCtRASscYGNv1FBoGKDkCxAnwo2jRtz9ggj/iOyfqGj/nc/jGxNdLARvgjFzmt/U//5qHc+

IVnG+NZRFSCQRJBhc/99MzPBJ8+T34B/KEC6uMv/I/9rf/P+T4NjWZxTBWhMp5P+vpwr/mP+tSEAfnZPTPDE5Dv+o/6b/mtAW/4OINv/cjMH/xv/K/8c/9EpTPFr/izR6/5T/rv/0/8y4TP+L76NK6t+G/7z/6f/JP93v7CAvFni333/won9/gMMhwXz05xSBCA+YVPHPHT+8V3/bf/d/lyCBK1zfwxxgmHk+m3/jFgf/9A/UGEu0SPAHDNyM43/

Q35mf11/m74CWwBNwE+JCrx0wgQ2DTe8t84sIgf1ygEOQEKAc5wd3oOcBFvm6cNW2vt9EeZ6wFTeumSMlAyX8Yv7CyG4/hw/Jje9i9FmBi/25vpL/FjerSUNjqz6SNKvTfHQQDU85m66PgAAdy/daMh5AYMAqv3wDKkocKIPbBFf5M6QBKsi/dXYfo4UMC9wy/IkgYT8ghMBI4ApyWb5Ez/TeYyWxJOjsPCJ/svIOIcdI1D2q+r1NbKsoKn+n/A1

AFN3A0ARdsANEbL8Q47o3wAYOxNad+t1A6z5XNRx/gJwfH++HAof66MBh/pyvZH+CN82yAOPThfmD/A0Q+98kf5zqBR/s4Arhkv39rn5O2BN6CbUWwBjz8Segvf2DeD7iAMiwN8OthYv1GFAioKIBiAJ4DAhYwlvrTfMgaYT9xKARPw9vlr/R2+3t8nLBA/wO4NY/GR+TlhPv5vCG+/mXfZx+PD8sdBhAJu/h3fcoBpj9zJTaP0KAY9fEewD38Ig

EFAJcfo0UYoB/38ZUoUP3gfhUA0MQeQCe+wNAPaAZWcNIBiT9pr5SP16AXUAjoo8QD/SCJAKcftI/YYBua9HAGu8yC2CE/M2+Qd8Y74zXAMAWjfGY6qrhkgHs3z40ApFe/APt5l1Dg3ybhjz/MmwfLBJniXfzzcK9/CIBjcAxAG/aBrXBELTqAoL9FIDgv2ugDOIVnYHU5L6B/vjfVHxsB5+7XMelYK/yi/ngA5X+XrATAF8bDMAexrLIBXt8+GB

8v29MtK/ZmQsr8IBBcv1M/urLbn4dADxAEIAKqHGrfO/+H/8MnLRkhQAaHeUW+k7tP/Z+/3jgAH/cKK1G8tP75YB0/mWvLBAon8QzDjmEdqjeQNt+zIDM6CKZHlfjx/YgB3IoMAGNDCe6AvHHd+rt8oQJ9F3/fnggQD+WNcfb6uy0wAbKQc2e6+ASeqIPUpdrIgfkBblgsAGeyDwoIewWlWCbAfDbEoFxhNgsQ+4xXg4/6kdAT/ng7EzY6uw834V

MCbpDP/VBgValMFjzHyVjMh/JZ6iACx0JogF7/r9oSnIPXQnQEIANRpC5eBAo6AstXTNh0g/ra/U1skRdN+7YP3o0JgMDLeIAD9f5a6EN/gQsKNAAvBEjjWD06YJ+wZaAM6BFH6ULD0YGEoEVArhhjaDDmDdfqNiDMBknRiyC0Px+SqFgbc2a/5CwHpgK3KJGbVh+8XA0MAqP021tWA/YgFtweSj1gKLyC6FfMUKT8iR5pP13zuLHFkGzgBMABpQ

XSgtgAPw4poBjMAcAEx4JuAF4AwDk2ADrAEa+FYfBPewOBz1h2wi3QDyhaSe9jsvIDZwGIyGYddq2q/9z76hwA+2BaeLI4MMQoQFzwBNjqN/SROtsca94mT2iPmm3fS+nHdDL5WT2Mvnx3WOimwAhYpLP09eBtpbkgTrtA46bP2GUD3iNhoTl9Dn5BbGLMHdfc5+3Hs9XBVALe/kvsGCBrQC9gHNALuAUj4V1YMwCDW4giF+zJ0AgIBAP9LPjBAP

OqnAdPwBX39UNIvjEsAdjAfGwyaNCIElAOIgTcgbQBCkAEoCKnVAfgsAgG+3SALgH4v0CFM0aAYBydkHHbYgOeAbfzJUYnEDEv6ggOTfiebU4EAkCsaRQALlvvedTiUowCEX6muVkaAp/IBISfZWd4yQKmvqHgXpok7959jPnC/LoWIFSBsIQ1IGcmlV/gaAy6qnEo0IExAIETKPNLeQoYCjoAuGlMgXMA69+P/9o35Tjn+AVIwaH+ebgrjQlkHv

8AwkBqqo2p3n5H4ERvkzYMH8Un876D3KE6btc0SEBkrALwEX9zPvtUQC++Fv5sdThQN9iJCsENC6K85EBHgLigTXQBKB0IDUF69gKy/kVfUke40xYAxMvDvopIAGkAZ1RsAAig3KoH0AegAm4AnDiMyyoXhXTHgsARBl5CsNj4IGsjDPmmlUcNhPfXiUIxGJJQ6P9sb4nAJRiqBXNEAsaxnZCsyFrANsLKVMBk8xv7zFzmvlEfFXm039Fu5GxWfA

aDVN7e619c26kJwAht9vOxWpCh4V4TkQ2tlqII6+QMRrla3ABAgYjGILY+ZAxG7uXy7rpQXHuuEU9TljhBW+viyYMSBoYg7oGfXxmHCphXSBZj0bsQmPxZkDYAvRgxL9Fhykv0NxD9A37W5P8jFhUIHpwCREemQn0DDKCXoy8oB1FXbYAXxt+4Yv2iAXMA6Qg3wCNwh5NkSwP8/LwBTgDVgFLDTZAVZ/eawjpYx3SngNx/kCRJzMQmQO6BPvxQ0p

C/eH+hgDYX56/0+BPu/cOm149fV4e6AKwMN2L5CZNlP4iGUB7KjRAyW+Z2wEe47n09/mx/MAqLuYBYF1gCFgVzAoP+b2xP8DEaGE/ooYdmB0sCmDrRyDj/mpDBDI6MctAGCwImIMLAsKCqn9M3L3KHjwJLA4j4usCZYERGH0/mDgey4ZwBDgEwq3MXC4wU4BNoCVRoufzw3H1A44BDsDBoF1GBGgUlgFNQDTYqbhHAPtgYXuPG+8BtvYGFWAlbsI

HDzaW+dVD7MK3KLgOAwVicAA7MDYAHWAPoAIHGsmpSADVAG5dvSAX8wzIJKgCJMjbbMd4IpAv4Ct9JucEafna0FEgYwxziigeV6gYiA8m+nsAWkA8L2NARoQbOcT68hn6V7xGfhEfO2Od4D5oEPgJzrmsXeI+xHsFv5rQMtipsAJyGX4CMqg1riEQIcXBIi+2dzoB2tjOvlaPZj2dbdsXYQe1DMgYvVIWN0Dqj6vAIY/u8A5ngAg0Qf4TX3SAYi/

d2Wx9BbIEXaCTtvhwXyBtL8wIHYf1IqgJWHF2pgDIoFYsHggbzAn9e3rIaGI+eF41E/ApCB4QCX4GSvwkARTfZdAnZYyWCvQIFCu9AtoYHAD7p4/wHTlobiEBBPjBsb7ihCQMPq/ToI/ecatiwIIegXQqM0cPwCE/oYyBBgeozdn+wv9BeyqLBhgebgWN+tICE35sVxGAQfAsYBJCDC35UAOqbJw8GFy6S095Kg33f5oRCQgBir9Xeq0cDwgdfwb

W+vh5VQH+3yoNNwgt+4FKFvQGUsF9ATjA+G+KwCywg1XV6LrGA8ABmFRSIF4/3gsEloCa+CCIS76DdTvgdK8MiBgCDVuCHv17yL2VMM2cP81ZAI/12ARrEDd+eb9x1D3yx6uNsAqFK6mdPf7zv1yhpE/AKgFP9dAHgqjrWKC8BKA9yg/Z7ahADgTjfR2Bu/8poB73wP/o32GuBuqk64EiAI6II3A/zQTwsPUoCANrgcIAxQ2USDTQE9b3/rqk/XK

Be4stHboADWoM4AWoAZXwxYabAFeqGLoeB0fQBA96WskwANYrJ8udjcbWjxcHooDLsZ+a6XZLYTdXw5YPCvCyiuW0tERnKWMiopAiV+pvsmYEFoBZgRaxCveco9wj43gO0vuM/Kb+PcCOO4WT2Wgd+DV8BH29i67PQy2gUW3avQ14BHIQhsTqFNw3ZF2tCATqTVtyKPtaPHRePrtGCADKhO/kLLXyeRi8UwY3AOevmUfC00OEczb5/f2wgTKlG4B

hN9Jb7X4AJFpxA8W+hBgnkEpAIRUDDAhso7yCMQH83xeQX+QIRBnLg/kHerQBQR+QEtQiiCgSIuIFBQZ8gg4B+gD6YEwvwjHJhHMGB6gDnIDAkVSYuj/LiQLP8/7wsmGjvpv5L4O04kpX7xIMpvvvAuYoP0BnIBWIPMYqxAvn+VSNSTBEv2KMoDAzF6ECDPlhQIMbCJlAx+BJVgWUFjBiHbLAwKJgXekhX4AlSxAU8AyQBfECsSiIIP/VPSgAamw

qCGAHcdAvTumSP7Yr8B0OIjJEeAbKggSqKS83dCscF9fpZvLlBfEVOAFsoMoARoZehBEpVdUHIIMgQfsUCd+P1ASHRyrEh6iVYGlBT4g/qJnvzwQBe/L/QDoDC0TEoLCQQkglX+A3wxSYlPUpYClYGQBOYVtGA6Ji/fhLiJLA1EBll5GINRvonAOA2OZAw74I9yAUpD/PRgUN98IHpn3RAD4QFqB+ywJ8anwLBvvUQeNBmaCnUBSizeQXLIfNBao

NC0Ep0CwgWxwXuA3qDv36jQIjQS/sZ+B+eBYPxWzkaEBWYMJQLSxK0GvQMtQTL/PjYcv8cEG1AN+gZkUDY6zQhj+qWL1zwDmg1hBv6Ii37UAIYQQr3IRBTn1SEEYaGzkqnAWOWSwDcYFSIKRvntYfBBpeQ1lCm9yhQYSwSmBZ6gaf7lxDcWj4QOmBxiDDAGmIJ80DdcWSIylAkYGLmRsQUJfDyIb8CBUFY/xNgWigugGbpEyprSzy+WB6lZxBBpZ

Kf4YoOfoJfAoP2ICAsPSooJ0Aeiguz8wN8HYDQzlvoBuXNEYj6CjAGdQHxQQHlQlBk0J90E6IOSzJhg5RBsKCab7woINkMsA4NK0iD7b6wgM2AQRoedBvCCuH4DoKbAbgsCdBciUhgF9AI6KMQggiBP0DaMHHzBYwWz2NjBVttMv4751jgVB3QpUsglKgDSYHWAH2ADgAmwBlADGYBFgMaAV6ocABoeDMADJBDY3Gx2Syd3sCYCGVuCMtJEgtwBm

v77VW5WMU3B2AfC4d5AW6EGXBEbYSAQH8nqpqxTymq6wDDQsccrwFnJxmgYqPSb+yo8FoGqj2e3jM/aRecz9Fv4bX2LrsTDVLWT5I4XgeVgPxM5mRDUApZToFApxiBrqeNeBlEsN4EMETigPsAqW+iPxUME5AKdHtxg2Lix9AfkGd92o4kFoHJsjKClwR/v10PNS/AeAV8CwMHroj1fpKgjUg4Stp6RmjhnCB3PVtGmuxG0HUQDZ/umQDn+GSANO

Z6eHqwav9AABb+1moBjBAxkGggr6+cWFb/6+TiZsFLIN3s/aCmIHFNBwyPWgImBqyMj8DQwKoQbJA35BT1hJ37WoJnfnNghJ+C2DIUCpsCtnKj4B5MhKsSOD0YIBCmJKGmBUaAvhgHYJrQWGgkp6Y4AKMHJoMBAfYA87BvqDf35EJThvnuHYjBm6CYsiloLroOWgzjgOGDD0FpFQ+wYmg89B0aDymT4jXNARmgstBFMRbYFHQEDgbjfDjIoOC6kS

fYIhwbJwXxBA0Dg4HLzh9QT+/ERgeWDmhgeoKEAaSgqmBj78/PDPv0ehPag1T+1IoL1i6XCtQW60FiBfc1ef5QUDFQVn8Bj+emVFoBwvG6QNyg1JQvKCc5jLYMqHKtgzsQbOCDUFsIIVHOQ8bGaCQYy0iIIJ/XEsvW5S4po4EBC91N0KmWB4BDN898BiEF05B0gyOAxqDGoCNwDIAcUwALgBOdmkC2cmXQQlECQknN9dGBa4I/wDrgkN+XWCHRzY

RRHvJrgiX+kBwNUEzkHLgDVXHVBWYQMYFnqh5mntYAhsWqCncH61kwQZjA34BbWwPaTCvWRvPoQHwkvACUv6NYMesjugkPBgkCvvDRf3BAZ5CT3BjuClooW1iFvgF/R3YEekKBAhXgtwcefJq0xIDAv4Z4IF/uVsA7gFelciBnhjIwfrfQ0aNAJpcHPznV3tAgi8s3r9oAFSQIIAYLgwd+3VhUQEmf1N/kMQYiojOC934s4L5pHG/bT+vux0AEE4

M50idg+SBx/9KQGn/zT3IdNOeAOyd9kAniHL/ibfGRBPgo+kH+YJE/uyA6BYnvhwbBuv2WDCbocJO8Xp2EF6LiVfuDYPBQXB8AfBe+C0yJO/EXAhxQ5l6vvyi2AH4TkmjrgnUHlJCFwTq/c3+q1cEWyOLGlAUBAgUB66l38FWYJobOQ2PUB/JlimhvIBUQeC0Lwg1mCgCFh30tAXeuVbgd+Cz8FDNgP2D5kGAhANQ4CHb4MGiIo6AlQ++DbsyiIN

Q/qrTcoIsiDmYFr4LETHgQl0BTcwWmDwf1omKawYMBlkDFdbWQLzQersBNBWaDaCHxDntft4EamBhOC83AEKz1/tyQOMBJ0UtsHW5h6VE90PbBEFlZEF8EIT4hr8AXBD9RW8Ei4Jq/OIQsABiq84sKtv2mwWf9ODOqYD3X7qwE9foag1XBJb91cG4mgA/p5HMzBi6CSND64JTIAWAiUBRhDMG6rwizwf+vHPBFhCTMEevzTbFugprBBCCUCBBD2r

7oYQ0zB1hCeAFOoG6wapQexegWgvCFOEO5+FVgs04Hb0scH/xmCIVoQ5whscARN7Zy2GIPGwXwe0RDjCHIIAlQdAWBcuFWDN/wpEJ8IdkgG9BPMB1UCQGQMIZYQ7wh2hDskAFrGIhBOsYrGxRDHCExEO5+AIA4PwMr8gEFVgJKISEQ0hADRCAEGUHRSQZHAlQ+TCtRuLZfwqLiyDOAAmHcZqAdAE3AEbRHgAp1p53C1FzF0GwATYA6oAOgBexzW3

ozyJBE3uBtyDthR7Ml0qTQWkxBWmAWEGhtGAxfz+Wah88Fi31N9q+/TO+vhAlnozXxt9ix3LuBW3xHt7ptyWgW5g17e2bctR5WYxu9FG6XVANiA2ZbYSxyPgBAuW4vRc7txg7z2/hDvfZB+9NymQw3AggVUfFMGtyD/AFVoNOYimxCh+BBBtJ5/bzGypVRYG+Msh+fguMEHvo8g/DB8WCggGary4PluIN8WiED/kHPIIhQSbUIjBqP8pxw4kLZvn

iQm5IOGCYUEkkLBQWSQ0AG/6CP0GaAL8SHFgwFBkahA0E4oOhBCzfD5BuJDuSEzJALWBUgBpw7uDoIGCkNpIcKQz2oN1x2vCxb3RHBjfJbqYuDGb6Pv0AJI2ggrAbuAbcEgeXUCF7gRLBId9vGKu4Nt7NBzLeBO45CZAWkBIASCA2PBeACRIHSoFB/tECdwBXixW6h54PTwScQx9gB2DnSHC3xJAUF/C+BNL9QMHoDFyMqngo4hrpCcIaaILPARF

AuLA+kIgyGoAILwbuwJDBBD13xIukP/2m6Q64otEDAMEvK1MkkmQ0kBSLUX0GY/0/gYUxMPB0Z4/4GPC09gIAgt1BvuC3cEmkJtgP78epwJP9UPoqoIVweQ8NUhcBAbrgVIEvtHCwbn+GblpZ7hkkf5EbghIh7xBVDrrkylfgQReMgE69xQjxEJaTAOQsd4bJDIMGfoPRgZg3Ka4p6CGf6BliQwXAbK0hiqC/iBHoApIeug17Bp+sgyFOv11dOhg

pJqmbB1NjYgCobF6/bdBweDs9I50G8fqMYelAURd7cE+vxqrsX3G8hnQQ7yE4X3ZTBfAEK8BTAg2Be0CFLsVwJEhlNpPxomEMJgLJjYHMKdAAKH1oCAoaJ9dN+ReDhsHZvwgoczAKChvBIYKHmcFtrCLcMpA6hZEKH0mWRIcBQodBaJAR0ENNG+QW+QvmA95DKmDN4JkIa6tbNBrnQzTrQhXkmnWsHtBNqDTm6PhhPIYSQgyICo0d36t3WZwWWvC

lQlJCfAEfGD4+Lu/N3in+Af6irkPxGs/g1tBl78++7OkwgwXRAuch+ODzNCj4NtKAGg58QzP8tV64oJw/ujgutBj9AUrDDkNZ1msgJAwjBCwcEI4IaTtSgrsh4pCqyEkNBZ6nBQfZWHhDAWhykMgIKyg55wFBCrKY2UJARMD1bUh2uD4CEaEN3wdgQ+PqnlDTcHeUJ3wVgQ3vY2UDPd59gP4wUNvQpUDZJcnCyxwXAAKANkGxAA1rCaADfdnAADD

ubbZWGxBSEyqL3AC4ojVtAuroCA+2B+QSrSWMsWEBX4MASAC2YrabsI9EGKgJPfjeDHYWwz9DJ7XEIm/mMgpzBEyCpn5PgKeIUZffwOJl9i66UL0WQRXXSn0p5lQAHmpj62uvTAGA2gh3XYnd2briCQ5y+aPMG4RXQPh3pBA1JiNwCR4husFl3hkLTqoFyCWgGCkK/gVd/ZCBTaDQUGXIOpvmNg24IXCQVEzkTi2oftQzUhE/BOMGHUO2oerLa7B

AIDXIELoKZIUdQnah32CDRDwzT+cld9O6hV1CelYzkLkoRyQ3HoGpCelYCAJd0HTACIgLWUr8BmoNZQd2UIegz8CoubljBp/vv8VzGHyA9SGQoFhIdRAnUUWZCfSG54B+QW7ZbmEZJAxKaXXg16M5AlNB9gDNP4+dQTfulNbWYDJCiV5rwwUgb1PXlMWng0yG6AIgAfh0RfBaf9+VBxIM9QdrHdfBA+1N8ESfxtgHzg/YoiupD8HfHQcMPOQ9hAf

uDsEG7xnFoTxmSWh75QcaER6TFoZZpRV+itCE8FUXEkgZKiVWhNt8j8Ea0P/aAPgukBIiBRtiLkDVofrQoW2g2C0yAEgJF/rrQhV+FtCwrpMgI6ZPWge1OTtD6Ihb4OkIfbQ3j+yr1FAKc0OH/k9YF2+peBVniGAzI3uFEMV+l4A6HQaMHI/q/gwyglNDUyzU0LJwZxQOjAaoDZSDt4JN/mG/DVGcaCLQFoEOpLG5/UQKHn97XRcGCg/lZAhXA2D

hlaEpkN1ggoQg3+Qm1DciFkP0wkEQ1ohdRCSrTkv1yICaAiYgJ+DkuBe+AuIT5EWIkqqCJAFZAimRJZgtRB0KlHoQi0O4Af4wVRBxd8R6F8aClfuDQsZADUtdcE3v1l2PnAQbqWKC1KH5RXrNhawSN+y9ClELvoNnIUDQ42M29Df/670KE4PGQ9TOi9CHIGV9Q0QaeAr6hjysKQ7Y5SPodG/QbqBWCPn5k+BnMEqqb/+Q5Bj6Gz8S4QTdg56hVGC

wOKP0KvoRemSjBjy9FpqX0JXoRHA23WvRDVna7i3WdsVfQpU9wBtrQlfxpAMtQAYAJmB1QCAQBSPtcIaoAiTdbG4ax2d8OigOjYYv9YYhVhi2IQ6sTyssjBPfjAwy0REGQ7uIH5BBxSMOnAYV/QxyBdVDJoENUOmgQqPTS+oi9U27iLye3o8Q/uBS2dB4E5t2HgfTjQtuA1DjKh7SFqFFlrDZ+m1t4sDfCAKPkCQ6ahBz8zoGgTCogjPvaxOqndt

2II0LaXJdQn+BD1DKgHfwOqAaRg3r+VED7MZSiz6wWAgkxhdyCq0EiMGwoZMA4H+it8MaFEQPMYcRQ9bBqkDNsGvUPuoddQh94Z2DUmLOQNPIUSQtL0Aowe7SrUMDmDl1F+h3gD8YH+1BSwaJQxFBMaCQDaQIHcYXpAzvuHuRWaFQYLM/KxQg6QbM04KC6ULJvrzQ+uBEICtl5WAKROJ2Q4V+lwCCX4s0J1gZzAmJQvPUVSGK4O46MWQwQBzzgEk

FakLHAOL/HUhvUo6AFViCbIamYHegRpCuE69kICobhdUuohZD48HJmgc4PQwifA6OxxKY4ALACnwAr1+EkCHGTr7E9IcllO6ujDDC8FKBU1vhhABcmHs56CqQzxOHOZpSf+2/9gCCrMJVoOswmZhFFClZbKfSFHCMZOhhBzCNmE5zEDoSFISaIEn17mEXMP80lHQ8GUFH98AwAmUOIVMww5hLj4p+ZvBySXLjbf5hDzDLmEloOzoRHfA8MiZD9mE

fMPM0nAAlD+5BCzmEAsMeYVZQkMB9BDS6EFkKEgQswpxgsiDPvj1rxbepF/a0hSv9Y9LGYImVMgQGuI/TCm7hYIMsoVEQps+NYCrEiY9WGYbqQtoIGd8u6GN0FR2G7gephvTCHwytU07oXnALlhmstTUHDalhoRzg/F0HLChWEQgBFYc3yHHBLTC8cHxeClYVnfblhPJC7YF+INC4h3QwhsKrDZWEDgmRwQ7AzVh7LDBWE6sJ4wY7XA+iA29+wEC

YIQjGwAXVATZJuYrGtE0AK6ZYpwO6EFoxlRBM8p4QMYgvqwOIg38iSxKtGd6AcJNyXATIAOjAN/W1sxFYJxyTbhyIb1LK4hcFcbiGOYLr3m1QjwWlk8VoEvEJsnm8Q2emXvt9R67X3GgApAMiIOidb2xkHkvoBNQ+eBuyDF4ElH2XgS2WeahHvNNGF6BiKAc4wsxh1aD/J6/X0GOJKQfTc8NCjGHjUh8YXMEQECaDAwyAG6EJBmccEGhSaCAYBsU

I/wJejPRhD3MDGH0kOKYdog3DBKGC62H/fzsYSMkYZhI+9H2DpYN56suw7s2KMCEgEXaB9/nswtPByZCcIZk0NuwW5A4zCeEBKmBspkBvL6QoAgU7AzBallhd/lswq9e/w5WX7xMI5foF9eWhdt9yiE04IqYRyZCRgwLC/WCqaF7IX3QnEBUgDz/BIsOdAb6A3whpLCFmHjU2LoViwzOhtn98CihTkWgF1dM4hI2CQbgDxyznPiAgL4hIDbDKA+C

HGI7USfweBg3aHLi2B7oAwgd+MaBbQGvqQYoROgT1AbuhqsA7fRrvtOWDvAoQRn8Fav2AILHQkwyjHDgiyNMIUocnQx5yGA1yCDzYNUgfE+dEA/HxiwhVYABKgKwt9+U6AP35rvDIIeIg9ogFLDJQHvLR+sPJwtD+Fa41OEEEO2CFXQ/ghLt0uqbpoPDvgUQg+A+LC22ASEMVXgp7ZdGf7CBySKIESMEpwqwhvUtQmAaQIKCnRwt0KdnDSiEtGXI

lMcwiv+uYw3OFOEK/uqgIIlIaFFtyAFGV84TEQ/zhNKx3P7Mv0Lodpw0zhihDbyDy/xJYbgA5N+kWEbX50EPtfm0wrm+JuDU+ZOIE04Yf/BQBswDxSH40U0ofqA/D+Gv9Gf6qUNkAbP/MnB0dDtX4ccP4ZGfQuQETnDaOHbIi1gc4GPih0TCiOEb4I7fsD3AJhI7C4Wg6EPDoU/oCfG3bDOXBIEFJQH9RXXBVNCVdgb/ybYUMCBDArbCXCH50OZf

pVvBkYnaDbn7ntDGYQCVcdh41IGsHIIBboUF8dNAajVtuGfsF24cLQvVB5qD1X6GML2ofow07h2OD01CelWxgMAHdYU7WDX4G8kK1XtjMOOgL3CqmEuIPRQezQ/G+7bCTuHXrxRvtC/LPSoFtH2JfcKKYQ4yUdyaJYtZZWPFvoZYgGzOXDEo0Eg8NfYcAg+dh9yDYbbpMLeEH9wtfQyd9m2HzcLzhHdwlF+5MCnuHOeDx4XNw86hh4wScE/sJuoX

YgHthY3CvFgIIKDfmqgkDhlZx0SH5TUSaGKgRh8yND9cCo0Pe/oxMdrhJGClaFekPzwZ5+ZHhCP9Y0EIcOJoXNKJxBslD0yHWUjRAZ3gtgBSOCKuFBoNRdiYQ+N+03CM7j+/BIYl/EfIBmzDraHYcNtobzgkDyjlDIKDOUIG4Yp/Ibh8uCeOB8sM1FH22Jf+Jt9634JmgGYf7gsjQftDPiCHV0LIbaQxSCxHDUzjE6kDwUy/Has0XDLnR+8M5Aee

vPVS+qxItj+MxUIZvQbrh8htAuEcoH4IHEwCihXtCmN4+0IHVInwtvYZ1A0Rpm0L1od7QzAwvGCLWGRUJ93oJgsXQt5d7gLSYD6AO8BczAxmB9ACsxRpABYAfQAdvh3WFoLFCQAfsPQO0UBfWHsLwDQErLApggypOKGWkCY/mBEczBcoJqOHX4KWhGpfWUeYR924EjILGfpFrCZ+9xDHwFTIM6oS+A7qhb4Dnk6qC36oYtbSwG2Mgp4GHQOh4nLF

ak6ofsF4GnZ1BIchDAzUpdJIsH+KxrYS9A9Hhqyhu1zo0I+vqAgoPwcGwRuHm8xIoV7gZ6B0wCFtAe0HtiqFgL/htQCwYaPUK0WK7oGL+OwEt2GzALPgXug9eESbgs5ZkSwv4ILwsgsgOCUeHmaGMAdOwpRBLiANcGHvCrQTj4MgueRDzuHisLrwVO7ETe0rsn/Bt0CZ4bbwpZeySVW4p10N1fqywheO0ZDvSGxkIVcJtwkpORNCo+G2MADweXg6

BSGLwDsjhkGWrIaJTPBHeCw37K8LWAqeHL2k6KASMDZvnVvh0qcHwEBAF8Fb/wr/m8QHQhJ/8L7gtbDz4WnwkesjtCuuEkcMvwemSZzhLXDWAT9v2bfr1AW5hvTQGP5D8OLwa+hJbBqf9yqH+sIsEYewKwRw2CTtLj8PsEU1AMKht7svd6WsKioQhGesAhAABgAvARyZB0ASLae4FqgA8AGvzvQAbAAxjtW+GZ7ApKgUQylgjVs40FS1DDtkEtaN

u/Aj/4DjfCEEVjjJDYY5hs+HRpTYYYBBfq2nDDbWLDWx4YQtfBNhTvtV+HJsOsntsXLCuLfNt+HJO3LKIbsMtua9NxajLVli8GRXdF2+z8UqKgQIPgEaOY5BAbtFqFQkJwjsdw3+By1CX6C3AJu4fvOFahjcRg4CuwHNtpMIt6hB1CnGHP8LgQffgXrB9/DiIFpuDXYSdQ/HhpqYm4pMIMxfvAYSJ+8T8UQi9sJhiPblLJhAXwY5zxb3+AaAIi/Q

rkUfIE7kKpIU9gpARIT8wyHkwPxsEP1DDBGAigSIBfGVLEhgtUmKvDM1Bq8I0oeuWZWBZsDamHU4P0yongZeeskp5WEU3zjiiPeXlhEuCWJTwwIocPtwc3hZXMsxgMCLTMCZsdph5ACRmHqEm94b+uKcwrvDZaEGenLoThDQIIkzCIWFGYXEgZHw+z+RCxnnKK8NEEQANVAQIV5KUA961GMFDKLPhfBAChFp0IorDyI6y+HXR+RHBcKIhkXwxiej

F98oEywhaAFFAfQA5jsc/RjEMjALIJbAAZ+c+wDKAEwAO3Id1hAoIFEAaoBWysapR0oQo4BVLckASUHYpFumlPpvX5xBlOKEhPLIioaC8P6mvxbMrZgtOupQiZE5ZmXvAXwwh4hfUNpkEF13X4XMg0hOEAttr6ZsKUXsCINvYWEtUtTk+lcVmC8WLwO2cT+ElsLP4bNQrVgyZ4FqHNtz8noo3dnhtFDFEBtwSSYecIsbh0Qhw1iZiMxIVzwk6AHp

DaODvCP1MC/QwF+RpA72Gn0JfYaDXb7hAGC2aEhIIUigx/bkg0J9YGCz0Ie4f1OGERBXCvZj0sPFQczw/uhuICTeEWIDN4cpQPhSCLI2BEx4KS4a9MX9cm/9rwCDEDS4IBQMuhFhNKVyYiNtmpoInkBX4o86ETMCuQKzwFKO1HDNIEucLLwSiQOUgnS9U57d4KcEbCAawRMICzxFuWDdQJeIr5hTUAfmGhNgj4TTgWg81JAkJ58IJlAb/gqb6hND

rwafiPcXudgx0RhoDdxHniMfEffADghv4iQOr/iKdNKpQPcRF4ioJG8cL9voDeG3WvPthw59EN4EgBdWURhSoDICkLzgACkyeskhAB6ABYQD6AOZgaHgUMtJiGLP3j3lU/c7AiN5XtBAoE1QKX+dqBFDC/yH65BrchYHOXhriDn+YZHEYwVvfaNhzHdmqEL8PGQV6I5fhki9qhEzIP9EUt/Um09k8a9BC0gydkbyPV0gl0dLhIIn4blNQi6++39z

+HhQyFSkaI6/h/etb+HQjAh4T9fTtBCr9Ab5znnJ4Se4Anh3w5UhLv8N7YZ/w2LBhBgwmEo4F1Ghi/BUsAcYCCBJjFCYXMI8Jhvr4ssG2ThuEftoUiOljC3oAwuU+ESUw37BPDgQpHMwAHtljwg+ha+hopHBWD3oYDQoDBT0CaMG6PyY4HFI1KRPDhYmGEj3Coekg+BhuEjND7mYEqAEhGbkGzgBzMAzUB8IvgAdHgLQAMnDVAGMwBdUd1h6j1bS

plwEKht3w11WvfDHSZUd31BBFwpbhwfDQPJjX2F2Bb/A7wvBAJoFFCKmgdeA8b+s0DbiGrKjmzomw30RLe9Hk49UNITjqIuSRITZ+dirWxNHkDveVY7XN1JF7P2BISowsLBDFFyj6piNOQdFg0YRSwj7qG3cJuQZRAroBoU8JVyWSLOoaAdG62GL8MSERNBLEf4w57BUTCheG0YXF4QzA5FBT5AspFdWmkAarwln+qnA02Jg0O7EcSDNNiCgCLlh

wiPIePxhT2oOvDiPhfxGrrgOwgHhKEC8mHE8IhoT9/EKR2N8gZG+VRSkWJSfiRwAiEUEXoKRQYu0XYR25DJEG7kMrEf5IwJhtwiTMTXCLPIcSQ4DBLwj+KH2MP2ES9IzKRRMjAME48JjEGtwhthZTR9WGD5ywqj5oanhnCBNhGmMPukZQInph1Aj7hqzcKskZTw8chhIisuHqBDWwXmI4BawM4rSGziJS/o9QgKRZ5D39zcUh4ETr/A2RjMigpHC

CPToawAgAakTC8YG/SMNoWQgrXhEiCXsGvCNgoQ+w+QRk/dZZgViMX1OiAX54k+D1BEuyJ+kW9gqXBSgil8FByPtkSHI33hugj/eERyI3QafrPPh1zCzBHWUEIwRzIjrhtgiboDuCLfmnbI+ORXDJhQFB0NeYX5In2RghCXxEx0KPIQ/5b6RkcjT9ahoLiIqAQrtAcci6ZEPGAM4bAQ3Oh5Yi05EOyKkaGpwuyh7MjaZFuyKLoZiw9Lhbcje5H8U

JM4fHfWS4+qAG5F9yPi8C2Aqlhs3thYIsyJA0C5BClhRYDawHmyJHYcbIkWSyrDu6G6sLZ4TRQ4sRIA0pOHnEOFYRlI1dhdPDRuHayPAIQG/UaRfsDcFh2SIZ4VdZYaRV8j1EFQMIwkVHArCRazscJHMTxlhMHQUQAJUijaI0gB7BvgAduQCABZk6sZmh4AMAURWS4C6JE3VTAOLLeAwg+3Ah4bkOgcIBzYTXMh1wHPIW6EfkSwSa+RqlAbKhXSO

QgU9/K2OxQippH2YO4YVAXRfhzmCJF6uYMEYfN/DzBQ8D2LrPJwdVo0IgRypAhpyzSojJ9Ei7D8Upn0pYihYOjBp8sZEGlicq2Eqd0MkXVgzGRT38z6YwkJcYcLIvLK+NCx2EGyPJoW5A7DBfwiD0GKnXHDGvQyrhrP9wOwYiNVfuzgz8iHfs5mFx4ItlEB2ZgB6ICzf4TDi84UvgmyMKoCYJGPOTJEWMIxGh8hDYuHV0KkIZKQ67h1QD/X5YKPU

QR9yOxR/PCf4ST0Mt/jgorxh+CipwJSiLUPj4I0vhCEYPgI1AAaAIK7ekAVwgFw6bgAE7rk4ZwAoBRWyT5wK4/kQePfKyiAur5YHAvoMrQVDQWOIjt4WQLYITB/ANoO99AkH7/1Cga3AoZBs/DppEOYJaofGwsSRvcDpn7UKNmfqt3TzB60DBMb3ikFso4fc1MvxD8CJnFCDMDhAHhRByCV+ApiMEUWd/LRh1tt+JEiPzJ4aEJCnhPMi4iFjgApf

iaA11YMiiCHb7cMpfqhAs++27Dc0GLcNRuMtwzvuR7DXIEw3wN4W7/HDhQ8jX6FAv1lpFuIogBO4i6xEUyISYYdg/hBaEiUBES8PxGmBwn0B6nCQRHYoPe4YZuXghcXDxAEz0PyYbjgwphJRQ/FHXyLUoECogkABTCIkHVUOPflTKGERutw2IHcH1YvI7/PLAzv9OxCSyLdCk//e96L/83UCcEhFoRKwwS8o79HEFLV0JUWaXHFRnkD835ruwXSO

SowbgcKiVZ4IqNHEWKwnlBZpcL6EsMLvfpwSLFRSqpwVEl30hUZior9hyKi3Qr/KKcURZwspoiIjwkEx/GbkTnQ2FhCwwJVFeoOfES/g2rh5cjMb7yqMVYYiKd9hSr9IcE/KLkAbjhP2RzMBYlhT4O1UevQqrhj5DG8FsVXAQm9w3VRkHC9ZExf2NUeoozMBZ3CYaFqv2F7v7AsGRvyicrhvwJNUacse1RavDHVGUBCBEWDwx+uaqjQVGkmABfje

wmsRD8kBVHlMKFUb2CMsRIRg6VFkoPhfqpAzvuBIjDuEHcKifHdI7CBi7CXcG0sJloQOIjIWusj5mHh4MCUT/A+xR8EjIuE7VkMmgKQ1xRsED3xHygweKAffU4E+MiNhF80jZEUAAkxhS0AX+EEyKc9O//I3h7cVBZHk2jega/w8fBnSCmaHKf1WEV2o9YRHIjY+FifxZATUA8bBMyjjsqaqL4/qJA9KRzt9ykgFyPdvm0ApjB/YEauHscMSStMo

9jBXAFDIGlcJYlD0Aph+UwDcCH+V3A4Wh/HdRV6jl8KwcPYIRMAy9RS6jyExutGKUWGA+9RS6iQlExwIGIXHAkTKN3pxMq48GFBhQATl4LQB25CEAAoABwAOAA3gAmQT5wJW8NDOW0B7KwV5BJSH7uvrAGuAivUaGGWVBVwWoI1hslVCxeCHyLQ4SIgaVELoiyG5uiJEXmQo0SRETt+GE+iMkkX6Iz8OK0jNgB1QKYUe5DSCs3TAtpF9KLsvkYIP

bYbmMlGGaSJmoX0Iu6gq8CNGFCKIzPFdwruIYdsXJEPSJ2FC2o3KeeCiy1E+KJhBHJo/2oQsic1GA/wHQULnXMR9PCpQQ8kw00Yuo1ZsRyi7AEnsNyAZpoiMUcPDHv6PK0R4TW8XBBLZDCBEuqP/IWZoygRPEDJAEkz0YgZMAwdBR6Drpi88NnQB8gexhr6j/GZMCOOIWSAydR90D+sH4AXbUerLL+6swju4jzCPdgJbwrpBESBdqFTCOMYZ7Q7c

RFN89hHzKIW4QDCZ5RtMhNZE6aL7YX9Rc0BYnCW2Tq5jkUcewk5RIqon1EwfxdkdWI8bSBmIdOGSELFUQGo+sRsL9QuFlJAAGmoov1Rhm5UOHvvzIBNGo+GRY1JUkCNXQJKmcUGTh/Wis0hAcJrXCXAo1h0nDKSITaJpKDzwyhSABks06jaOI0Q+QJqUhxCYyEV0M3kclwdbRC2i6YSMv3V2ANI2zhGhDlOEecPrwRwI5kRGvRAkCNaPM4ZoBSLR

pij3sGMeFbyKVo0PiVnpHtFd4LlkKeo01+ZXDBKSfaMzoaxw18RKqip/YhvxYAe2vKX+TXCFIBGCKFEeDop7RofCY5Hh8LbUSIIjtRtCCx1HivyS0YyIuz+SHDnXrGKKV4RyIvqR+yiTtER4KJ0Y3lTvue7DgyEHsMYfPoosEBHSEi1EGKLPGBsolZRXwDvNHLaJIoHZo51RXADXVGoPCW0QUwFbRTTC56FovxKtFNoxgB3oRuJG/cKPuImoyHhD

xRoeEJfwG0brwvPg+vCe5GXKMjUQ6AqGRqL8YZHnsCEQSJ0N1RoIiWf7+qJPgdsoqARYN9kpHy8LJQVrIwrRRKoxKFUyLPkebzcbhCiDPqGWaKL6pbqbTR58jLdG1aIjUfVo83RBWj7dEe6M+fl7ovGhtuiLhEFiM8EU7XCKh/6irWE6+DswCNkfhW2AA9WgwAHEwQ0AM2kLwAatzCYzEFvnA/y46hA3exqDgH5jHrYMqGcRYVrSdUGVLOojkBjw

BzMpY33dgUHA8ve6l9KLqjP1jYfUoz0RNGjvREU43o0UtIpI+HsdNgAVILLruIwxa2sMQvxboyP2geJ3ctudHh7qDB7FGOPxorkCl19tJHXXyWeic/Co+Zz8RhG5uzekRzwuihm2ZEpEwuV64dkw9ihSUZ19FzoIJIVvo88h36jj1G7umt0TsIoThGQDIcH9QINYUcgxtw8ai0jDcqOeEcPIr2g9NC7yKoiKZvqnKHORxGD/g6eOTpEQiwwER9Yj

gRHcwlNkfCAjlogaiBd5LMMbURIlf9BHMCUtrO8IGGgDote8kIiamGYCDjoUFwnPhd5YkDGwGMJPrIIlTQWt8XtRuwOhwacA0dRBqijd6B/0DyKLImHBigjHeE7gxgrBQYogxzeow+Fl6PIMeqwlHB5YEpsFx8KS6qMuAgxfiDUth5SK8EeHovKBX8jClQdABbFHNkZqIuwhHzBWYD6AOsAebe0PBzMAcAHR4N2SWr+lLBOiAqqXcrIqbeV230Ae

kCE+EFBBRFBD2mrsx6HqiDGvhn/XtGHKAjrYyj3qoW3AxqhMbDhJEptwqEY0oyZBEkiWlHuYLaUXQo7UeGatWNEL024SKw2aj2mBcNkHHX0pbB6QYthuTtS2EHf0Fxg4YTpAkJD0xHnIIU0alomPAKmiK0FbCPW4fEYodR3ajW1GrcKSMVIonKR66jEjEyyIx4aWIo3RLCCkSo9AO5kdlosNR7cjkBGmaMMWsrIhZRzQw6DGXBwZGE9IlthhPD/j

TTiKqMadQ5oxaI13mEMMJmYbkYmxh2wiL4BG0PIQTxQiRR9bDTmILiM7/k7wwQUsRjYIElyKVUQeo7zincib1GfKKQAU0Aw/APkjpNGjyImbuPI3lq6wCwtFWMInoSNI5+R0sip1HoIMBZuiAVawTv8r35ksFs0SO/Pu+Pb8vQokcFuofx/UwgxmkPqAdsFp4ckwpJ+RKAgoFBIM6bvTIIsRH0iD5Fnvy3UE3AmJBgLoF5Eb/UvRqsQGrAQiAnIC

Sn0nkSPI27QsJiPUDwmM7WDigH7Bip0YTFh4EPIBeA/660BiVYHj2WRMTiYswxCJiQRFX6Kr0ZSQJJBzcDYkEV6MIMZ7A9sWic5XkAVKNL/uSYyvRMOCfjF7/xCgayYpQ+h7l+DEFSM/kZkg6AA7chpMBMjyAUTAAUeQM1A+gDVtnVAJjwBAAKsIaET5wJiHDAyRogSk5vfAx61HWqXCf1wkHkhE5JSGtPgctBwgiZ07txjXxFUfwQ3VEZGjE27Y

e0o0R6I7uBDhj2qEr8OcMc8Q2oR63d3wEpazHgQ84C5AjMhviFcNy40RW3Xou9OxYsqn8PH3kJo+UhURizkG3SJU0WmxC9Rm99HGHVeWX0VmIzFQKEcGZF9cLgoGmxAkxUIieCxP8NOMeFolShUOCeDGo4KPUSfIoWsD+jA9FfGLkgaKw+UhTlDJxHqOEhMaOwi7qeIj0BFaIMwET8I2t66ZJFSBN3BbnKHZeRWABig1F6U3BYX/opphJKCWkDPT

y1ocswsdCWij9UHfzlPYSjojEB56QKRH+oB+nuN0fIRKfDheFrMJ6MfTPVL24oj0DFmqO1oSswxGeS5iBRErmJpAXkIgURKml9zEnmOT4e0gVQRAcjDrCLmIvMduY/ChAtD4+F3mOH3oeYq8xGcjICSHFAo+p9o0ZAV4i4SYVmELkSOY2W+Y5jJBT7qMo/ooEYAx8mMctFv3hBYdLnaeov+j1zHmaRrkSHNTdYjV4cWGA+FZ2J2Y87BtcjULFd9T

TUcbg23BbLDntGxBxhYRmQh1cb+jmyFQsJIsUZwsixxZjBVF8/xRUe5HVAhpFiAgg80JBUSIArOh1FirQG0WJC6NAOPngSKhFQbEWMM4dxY/xqxcjvtGU2hQsYSwLvqRwj3pH1K2BUNBIrOeOw5iW6PSKAEUropTQYFidX6fcKckRsYhYRf5iRQGAWLawaIo/rCicjTBFAEBTkR0ArYRQ6jOuFPmL0EZlomoxZRiJfgUgMNUYHIz4xFuj7dEmELQ

MYKI1yxPuiCxE7mOWYV5cbyxbuj3LF7KO1/vCA/LRQVjfLEbcNxYfrIwKxdujIrGLKMy4bbgtuA4Vi4rH9sOaMNyouyxz0iHLFEGhDUZx/LNRpQDGxEwGPJcHAYudheRiCrHS6K+EXLfRYxssxazFwtGR+NTIp0eCRiJNHOSN0saVY7MxYCCtLHrGNi0b5ItthXVipNELCM6sZJo/FQmxi2rH7GJHUc1YnSx8WjTSEeaOP0bVqaMxyj8izHtFSSY

cmolJhcECjLH4vgasUZI9axBRjmEFmQOlkf0YqyxWuj99GBSLqsTcYuZR9liWjE1WOOsWeQ06xTxig9H5iLSsVdY4dhB+jbrE/8N2sWjA89gPsi/dFv0Ig4Few12RnMj7lFA4OQwcro4ORPEclYF8yJ4kX9Y0GxvLU4ZEK6N52M9iL6xouChxE4gJm0SDYquRvLV6dG06IRsRUYsGxQBjK1G6oBD4QLwnGxuxjJuHx0Om4QVFSuRucjRdSEwI4Md

B1P6Bz1iTrG5MLI/t8wmOhmBB6bGGyJyYWOg1ThEKBwKbviEPYcmYl6xTNiWiG1EOv3gfoO/R2D4ybI1UKplDtY44R0Aiy373GO9/nMvSARRRiTyhlKOjXp0gYFQ1PRNrH0I2igalAoS6N2jlrHhPyPgRj0ZLYVU0ElD0FkAEYuo2ax799R/5I+BvALo+QsxMw93QFtOB4YFmYsaxPaiw+jO2OAflJ2byR3VjpNEAP2raH3/SnI9kYQv5PcTtsbO

QeyM/0M8oC6IHNsZn2UtRE7DO2FabEL/tuDXLAuKwJEpjCMnYbcmakx4JjrGGY0NcYfEIbOx1kQF1EdGPm4S2vXPyv1h4/40mOLsaUYnNev6j+iGCGKFMY1IlhEwONNgBwABEANh3Y0oFrQcUwpOEOgG22QCg8aBVniTrwEICBaMe4Ab8Mjrq+SkvtJDEN+3IjPXKiiKGgfYgit+A98LDHsMKsMSUI6NW1pirQZ3EIoUbRolvRjpiuqGMaI34cXX

avWvmC4+CSsCSIHHEfi6lqZXYBfLCZht0Iw6RvQjVGGK9X9ivPo6th4mi2JaC8O/0XEiMmBJTDguAC0TpMfmY6qxoPgx6Hc6Pw+JjY5N+kLFrCJg6JMUUMQZLRb1CxFH7OicsUbvHeA+1jMaGHWKEsS3Ig+AKDiiIFoONQaLlwzFoTRjrJGCB2q0QfgFKxwejHrHDIhnkRmA4DAAJjCjFmQK1YUfImVhi1inrEuQOM0ZVojPGQDC//7fWKuUe0ZY

lAhVQmOG24zAZg1wrLQaKiHiBSRVN0ZDYyg+z/8vIEIwF9UfrowluHkDN37jqBpUZ+w2ERQ2i1LHEqIVsY4ghDBogDkbHTaNzGAvYpt+K2VsBHpqM2UekwElRS9iZxHFqPwAXcYr3+Wji6aRHaI8/oZNYZA5jiOEDaOJ9etjokmhdyEXHFGOOR0Z9TEURAWgDHEPGLWiEKImexjlYAnFzv0Xsa447oh0DC0kF8YIj0b4InXw2Dp6QBLUEGoOqACz

A+gBVpjxAFuAtODMzWUABzMCl00qQQQw3nmxZBYYhqbD4zFa6PPRU9YEGyCIkYMJbHGDyxaDQK6lULsEejsCqhgki69G2GPKEeQoyoRJetFpHeC3b0W3vUGWGBFlrJpLH9jvpDBoUsTYRODDKLBIZ2HMMxF0iz6YFniasclgnIx8stxbE3FUpsY3IviWmBjirHHwKxKMuwnuWNqirHE6cBHYv2YxCxXFcP2iQWJdTv9IUmxnlizzFrGJS0bMYtHR

JBiqQGmXRmMQhAwRkYfDO34iKNrUW84jVRmXVozxmWOkof1UHRhOjg3BEtOOn0h2gzIx4xjQXEwlhk6mdY8bBsZjiWRlULBcbC4/oBqliXTQl6OdoZ84zFwDTjQ5HUGM1QC0sHFxHNCw5F1v2ica/ImBh+WcXa6DEMFYkKAdYAzRc1qDzb3FdtJgATA9ABMAD0gFmIQ0AO0ySxD6oHO+C8WHlNdJQiTRiHJJYiywNtAFmQoXF0oFqYzpEMrYuhxp

vtDbGHwNNcm04juBt4C42GN6KBdjvYxRO8EE1+EH2IDEZsARJ2nhiz2xscCxEdtI8GMQWCe+b9TXjESEYxMRQmjxcBKd3GUddAqRuD18trHfOJQgb1Y+5x9wC0eFlWK7QaVY/ox+djUXHVGKysZdY3Hh51isrFl2Kw4M8YmPABDjg25lryOEajA6ARSaijbHlmP2wbQ4j6xp8iyzH6QN5MTflfre0oj0n4IMIQjDV3GkAtxFn3Z8xR4AFy7b3WFg

o9MCYRgJIty43nmf+w2pwA2gbKKhorZ+9Wxl5AODxlkOHgfBy1t8k5FmWISIiaYmMBhLDE74KuLn4fXokSRrVC7TELSNb0X04oKiHejoXbHKh2vkovYDArPBOG7U2h7MmQeBwwR8opnEX8JZ4EXRUTREyjhFGyaNSMdOo5HswLj/NExmPUcf9wp1x5aiVLHwuNPcRkLdzRl6iEXHPf0xkZnYy9xDjDr3GjGIXYd3InXIYbi8UGZGPU0RiGL9xaWD

z9HG2NfIWWYmhBz9BtdEo5zhfvG40Dx5Rjr2H+6J1fgGRf9xiGCezHDcMA8eMAkWR7qjdVFxAL3kRE0RMxKjikVEMWNa4c/6QExclicdbQ0JZUVzo3VexHjV9GqyMSsSB5ZKxOdAqPFYkOxTvOYwFxhYhGPG4eIfaMrQpEqMliV9FMeJJ0UHwsnRkQDsPEkeIcTD+Yr+6PHiEzHyWNOUff/c5RvjDhPHUeMecWoI28xDHj5PF8eLQocS4/FxWHjq

GiSePkmjcojhBJAD5rEj33vcT5yFdRBnjSZGvuPzkS8w92+g1iWrFTWICyBpYt8Rhljz3H9YSsUT/g2CRo2N8rGeuOgsW54/jh+Dig3GdGLhhD9o9X+kQ8pXHJuL+wdCwmixe+inqGsOMluHDgjBxPFieegWaITwHfQjmkcXiZVEJeLeKMDI3J8zFjIvFQqMr8iTwqtW4XiuLF3rm14RXQOGxiMijKHCWJK8cY4rN+pjjxLElcN+0Qi9Nys8zw+d

Hs6JQkYjzPLR2NCReHp4IAOoqotjh244F46E6IE8W5wMb6lniALHWeN8cYAAiHRqfD0tG7rxRfAgY93hGnjPeGw6OgcZnQq2hZyjjeGGuCGMeTY9RmEBj5b7NaLpXk7I+kBiGcuPEDWlyEWTY47xzmiRUG+PE0Att4y7xeHi8X4EeNUQnd4ofBjYj2SF6AK28Ud417xFVif7EtmPrVAt4o6x0XiQgHviMQ4Z44y2xM1imHGe2AccVFwmZKGdjE7G

0COisdY4k92vOi+eFr6P3cWcYmrxyyiNCDF2NfUdbY1/RujjRdFH6Mh8ROYi7hBh1DPGNAPv0WV41GRjW8tH65SLdiF2IjXRbnUifEQHytUaaol9Rwj88fETeCEcez4haxbz8s5ae6Pfocz4mhx71jY3GhaOHUR7YxooEbjajHA0PWsVg4qiBODiglbAuJdccsI+Hxs9JfbH9WLs8WlIq2xkPjB1FrCLOMXG4uVxabj9NEvuJzEas4tMEhLjmHHy

KJ10bIKdjxUniwPF/0Ji8dRQ7TxmJCOPH0oId8cD4vgxYeiBTE6ax95hUAIwAUAA+gDlQBg7ioHPsAmgAlfb7oSnASk4I8AfdjH5rgtAeIKE2ctCSCjkWrIbCcquUnHqR8ehMFHD0IvULxI6OkxWj+CDicIF5BaYoReEBckGKb2LmkSsXMdxe9jNXGt7yY0Y1nYMRii80tZbjkAIIcXAo+EZ4PaC1LkDMQmI4Mxj9ihIBz6LOkYYvOZxG1CDfFjA

KN8e6PULxctjVLrhqLg8bWIzS6wPCEf6AGMMDF1ouRxri9QfAZWKc8a6451xe3CllGt0Ox8bA47ah8DjmvEo0N80Upo7xRMGc2jF3OLgcf1hILRPXjsBivOM38Z5CaHxVajydGeeOSMdGPR/xgni5fGyyI9wUyInHRkT8SjFZaIDce440HxMvCJdhCyPGMVLwzgRyHDP/H5GL2UcN493w0AS4SFEgO68f/tYf2Ssj/XFv+xp0WSwzpEUvjsrFfkS

Z0bv4uFxJdiVZFpEIJ8Td4zKxAXi4CBr+Lusam4zxh6Hi9dEeqLWwStYr6BjZiZdHfUOs0VXgPxh9vigfFAgMEQe74ngJMtiY3Em6N/odwEu7B01ia7FlryrEZ7oheayvj9/FKaPCkTOwxkhajduzEPKOBwQ5OdXxw1iBrGA2NQEXAbW9xHPjIfH/SMpkWfo1NxSL8vVEOqKm5BJ44sRzuDbjCs+I0UWGuRGx9Pj7uEa6MhoRWWMAxiKjHvFXAOp

bFs4i6AJVjqyH0WI8CbJKeoxTZduIHXeInwDBWXKxndkjcFY+NUBIHkcIJLOjpaGVkKFynDI9wJBL9LHEM6MjyFQEitR/UiCbFI5SSCbTglIJWOjgAnpEAmnLkE79hUsj+8FfeJr9OkEvwJ+QTxBFh0Kt4d0g/RsGQT+dQe8MRzCUE2NR/NDabEe0N+6LEEuWh5tDvjqiVmYMXmYk4BDRindTPMPG8byoUAxyHiNX4s2OVUTVjewJBnZctERuVv0

ap4r3IWWQH34+eKsiL9mOnxBTQgvHGQJsjA6ItX+ewTHJHOeJ+GgmwfPxb2jY9KyuJH8eTovPxr2jBS4am38kVb4npWSH9ljFiIICUXjAJLxsuj2AkvBPyGp8o5eSygSgbEL+OvUb8Et4JWZIAaH8yKJrl3IhEBDPjyYEREFYIdB/L9RD3i8gk08PK/MQ4hghBAjOdGPT0o2KaY+RBV3iWeEkzwboSLY3IhCVjavHM6NxNFvI4VhjOjt/EZqJTAR

SEmVhc5jWdGteL80eSE41h28iqQkmOLJCYefI4x0KksyT4WKiCd4gwpAvKieQmi60iCTv4tHYoejzWFZuLCURofHXwe/NZAB7ABaAGILFJwSQAaQCl9GAcrfhA4AXl9WE5VuMf3G/hH1gvKZcwFM2gikGpAeNABdAQWBvQBdohboNq4/BA8HD5oCtICQ3KpRM/DrDFCSJmkcq420xTejxJFUKJWvgPA2hRIjD6FHF13aLu6YynAf0BQa6hqMH0TS

BSIWGnhuZaj7xOzt34sLBNRA+DKw7yIFna4m7uFz9J4SaEFz2FEQJEgMWYRkpLKwJADoOVDsWfNsZiiyHaYUqQ8c0WU4nT5pcEYsWfTXNAlUF6rj5U00bhGYLhIqONHCxg0DMUW5cT0gKIQ5IDDI1EKgVwUHAuC0bmwfMHMkSgILFYecA7cjp3AsNq23NdYsCA1lh3UGzCa23MaIImhsp5C/SdskqBTPY4MCD4B9sOHCSO/eugKXF8yBIyNJzNXk

J0+oAhgKD2RmDbM94RDKQC0Q1509FZ1raEj8g17ilQLWhIP2IDAO0JD4SJQkMiW98Zo7X3xEgBwG56YHpAEA5bkG7chYAxR+OIANsAMXQmwA+wD++KvAtyQRusvjRawC5whgsMqDKqAksRNixy5wlcesyRG8Bp9auKe3jGvofWIZcvjRzIp2C0sMdUo50J7TjXQkN6PdCaq45vR6ripoITuNB4skfT32M7iQxEQQwJPIcgY0eHOMKfRreCVQZ34i

1xcYTeFEfPXuLqdbFMJ538e66aEEMeDtAIYE14SSOBcSCxIRwQEYeB4Tc17RCG/IH7fY+ah/YxIlT2GdkCe4QF0SkSa9CNDFUiWm4GSJjPQUCpICxuQMKIyLYNzZokEGRO57kZEqc+JM9cdig/TCDsmgl7UyyxUB7y9GMiUfdWTgm4TlMitl1pXm7mdFAd1ZBKwYoh9QtMYD0KlFYfYiVQB21BRWa488cBKoA5PANUKIgNawtP82nJeRMciXxsQb

qHs5NLDkoDYQPLAZQu/tZr9gwxBcCE2EjNYfblgsBthNDAqFE7rw4UTh36eQmbCSVEq3uBSNogaIYE6MmZUWRoKBBkVATgFyhpEjRqJGM4uyAtRMNvlzrfM+Mn8RAFTmANUD1EwJBiH8tqwBkKoeKDXJZu3USXFTjROIosRkPEUg4TrwCrmFGifNErU+VFFEti6CAmYF5vbsCtYSd2GLiAWiT10BRAjNpZpSJEDYSnNEo6Jm0SCwGOqVIoff4Zx0

B0Smom9RJebgYCV7sDGwtwlrRPRgGNEm6JmEQeT5n2MIWGSI+g4mrAwokHPGqibHGLVeyWBa8yRkIyJBVExVghUTjZTNLR45vEwH4QgeQUokH7CcieWNKPYciAa9DnF2ePlFEgMh3UCMBpmIQ5UtnAKxASwSeiQExKRHH1OBrwdyw/bhulCRWJvmfyJT5UKmCFbQa8CpsCfAc8ARGABiSsia5E9me8kT3xrrV3pwKGsJaAUph1IlUNGERFkQ/fIW

0BZSDJcC/eA/tYlAXkANImSxJNiA88DaMzRAf1wJZi3gPvPMOwvWcQnzjhhHbPXaL2chQ8FRqKxMa5h4gDewSHR4WxYyHsMOhAV+ea+hNCAHK0o9rogISaLXZLwBqaB5lCdAbFB9bk77iTeyCUBv5e4oSaBzP5BIFKmh25X2J2rNeeBv3HrGlsyc9g/kTII40cLrtsAdA3YyN4RQTAzguHPfAcyJYv89QjRkBVWpWgd+64W4iwkf0EXwKWEtKyuF

0fFjX2kMmvZEnjM970pX7UOKTYPUWZw61uAiUh/4E3CcikPBudT9a2aVoCdzN2QDJ4LcST3BtxNricF8Bu4phCK4mJqTwIL+EWW46Dc2pgPQHkjCBoAaAE+Bx4m2IEniTQ9J9m2+t4eqx1EhhmOwCeJBicV4kDWSQKDoAyYg8k9F4m+NB3if2fYkKXg5yhBjLy7ID8GbeJhJkz4n6zR2WINYA4gdHNOH7AxJPiXfE7A+Rewif6DrCqgO/2N+JrkU

sCD3xJqmMLAXXe43w4mAa+n9rAAkqeJgNlBixl+jCQJII4+JUCTd4niaAhWHuHEewt6C+4nVxJVGIdVRvshuhSKGIZDOADIOdOJxYTi4nRIOS5sgwCqSVXAfYj4cDjicifBOJZa8+yQhngOkEpErBEXsTmf4+xK2XhqkHSAYI5+ug/zzCVI7EmNaMNwXYnGhT9kRoQARg4IiHYmYQUESZbE8RaANhZSBwIDwxgcOR+a18AJmg+GJ94TW8cWJjmlJ

IkMnVW2GlAghA1CUXIl0ULkiSZE/k6RPQd17kKAy/IZEtyJtkS+SSw+F+ngJYuSwvMSjEnuRJJnvIOU1g4uIg36cP2lwFYk/mJJiSbTpZUOGwVVgTNATiTZIkuJIDOqgYVSqTN9S1yGJNCSTYksM6rGxkIjPoXYMSEkmyJAsSwMhHThbgC/ECjQKSTrElpJLIcO8IBxgDSB4EAgPxiSakkvxJz6RdMHUOi/0I0MbkcpSTcknlJMCeNzcGca9ygtu

g5JN8SR5Eshwco4Vn5wwG7iIlgNpJxiSOknPpHYeHplMbq68J+klhJPHOru0S+M3tRgRDjJLiSXOdBtAd2Qkl58uRDic4k+ZJSZZa0BqFn1wLWvVnePiSBkkkz2ZkJskztuNcARuanAk0SRJErSJx51JkDt9zi+J6gMWJGkZlYnaJOvOidWF1Y5htkxoxiHOSZpE3YO0pJQYD2Vj4UZCwgv82lQFCCPxBCwDo4M2JTsShEl/ePmiu9QAVxpipw4B

cUXBSdIk2foWOxvlwQtj+gA9PCAR3sSw4mcJMUoOvfB7IJ2DTUzU9CxSSeEjvAilBvHgKQFrXidxQyaeaxxDDxxKedgyA18QIVAqhzXMDNNl9cRUgdCT6UmvPBeQBvgOVWb00tPBmRJLCWQkgmEZLYoNiGxw8QDfJQuJmcSS4kEwgdWN14Vro9UT+UnciKlSUKk1mE+WwPdACwCyMpaQRVJGcTBUnHkwAcH5WFOUk3QnwqYJPGhJmgHBJnnAuIBp

XEv6k6XaEEVcTTUntxLriXyOHtytLDw0GDpVgYK3EmuJbA5jdYmtnaljwQZusJqSB4lepKDVEpcCKeBlAKFDCIADSZ6k81JZ/xuu6HAjbxP1JLeJS8TT4nxbyj6kEWY9KeDhSPGQJOXiUAkzQ2mydgupfJN8bP/E7NJKaSeeAkPxC3LIwT8hZTQPUnYJI7iX3qZyIz6EG6CdeENCJKk3VJJaS81i+NElqH+oCVJAqTSEl6pNCrLqWYRAnLCWOA0J

NpSRykiuIIO0B0kpkCFYcOk3PAxKTUZDX8A9wttsWlIBNxzFzxbERSSkEGRJ9VZkGDUxJ8oMeuFkwAiSN0nIpJzMKPsIS6+EM5Pg2RhW8MUwcIBWuhgMBknzNIACOFhY8997klKxIliU8k8ewFCl5ehjqmseM+k2+gr6TLkmJcCHnhe2NJAe+BfsyfJJViRuON5g8WBRuFzQDmSXkkr1wyfNX2CRTQBIbBkhpJ00pj5yQ2mC4GlcQ20dST2kkHJN

2yFjIFOw4JY80AoZMGSTjWTxYldZfmBDKMLEHskiZJ+dpM9j6QFKIHTbCfyZsTxIlfJKliQBOavYmMBPYD9KjYQD+k1jJ4GTKJzTUyspPoQSQcNkZ+7pjeAiQJ5AHRM66SLYlHpPztG1cKm6mdFFrJe4APSbJk4RJ+4QFMmtMFvoLJVNZCqyTy0AkpKFAdGWCaw1tYUH4jpPZSeNAehJqm9XRyqKgnXuXHRiYtCSLMmcpLvENZkwoeVCBBqjEJKL

iTGgaVJIdZZIAXLDLmPi2fUwHmTlUl9pLN1OOgQhs8H950napJISV5klVJ2uouv7EZDZGCJk2G2PaSYskhZJt1O8seOALyCqGFhmiCya2kp2semwfFrprxCylFkzzJFkS0snxuBZ2GwOSgYVyBQdYtpN7SSmkvskAICJ56RwAtlLlk+rJi9YtoD7FGGXCEsSNJNaTHUnDTgJgDZ2ElATGUq0n9xKjSbWkktw0SgNiAGTjsqD4WO1JgaTo0kluFn2

A4YOyuoIAx0LzZPGyf1k2twndZ0qCKsBQKq/A6tJZqSJskuZE55JBYANmk69eslHZK2yXA2B2icrAYuKbWEuyQ6k43WyNwswZYwAiICddNrJqWSU0lzyEsQFGEyAGZmT2CCpm3HSclQR8s6CAo0o/UHQCHOk0eypKTFGxxwAqXr0qBlgKmSpEmHpPUyS5kXHYQxA60CYEERyRMOcGcHqlYuD33AGnEB2KSqP49cbiPfwogWBkt9JnZhiVgf/3dcu

7EtnsFOT/0mBNmIeKVABNgD5BC3xnJIeSX+k75JnZhtowPc0OhL6OTiUNGT1kmdmCf/sBQIfeyOtG3BC5LgyUEmLaswi5raEscBuBFLk1DJcRotGxmWESAejAEjJByS/zSJUQqCoY4WRsOGT9klZJiaXLtOQyg8kS+MmPJMZyf02MaI7yA8rKmsDs7jLOcA4uhBes741SRyYgQJFJqOSykxhEGyYIRNSy8ruTzYnOxKhSTVwQ5sbapvmHDjVnSew

k7FJC6S5BBmrGwkFBoIhYCClj6BQ5PDiXIIc0BPH9p6C9eOfoA5koHJwbxrB7wVn5gDlZdfs6Qws8l2VxzyX82A9YwkgBuASRTZSYDkkvJicSl5yyQHgsE5AKloifj7MmjpMcycDkwQEqyBqMpoUBMBu1eavJdKSO8lTzjuWPFWc/AGWIfCw0pPMydnkuvJmc4LKzo31IulGgAS4dWSvsn+zlX2P0vBvqIkhm0kpZLKyeOfPd48G8NCAH/1yyJ9k

7fJV85b/4syC30keIZKIS+Tj8lwLl4pl2QTAQvq8SsnBZJ3ySupdrwIUCFcDZNSvyVnExNsilZts7vzDBCZ/k7zJhtdBlinwGbfqktJjgW+Sv8lzdHi6lQwJQ4TaBN8lKpLyyRYCZXYwGlC9RIFkfyYgUuboD0A1UA/MAB8FydT/gEBTACk6LneoJyrCjUsZxu0kIFPayZ0uRLY2WYsFI3qgAKbFkpY03GwOF692R4LPjZfvJY6TS8ktcEVdhOOb

CAl9BbQp6ZI4SVHklrgRexumg/UB2IPxmcPJocSDMlXGhEKaQ6UiIRMBlgSqZIDyb3aUaAHzBZYA1DAEzqIVYJA0twywQeuQvhkE2F9JWiTLclLGgdWOssDABbS4Dcm0ZLW6PlsTtYPeIOHh9+SVyaRk8V8RdxYUb03BZ8KNqZmJ0f9e4Bw1DHmH/sW4A1/Ah+FtTg8KQ/ULwpQUTe8Iz5DuMna5SJckuVPCn81G8KcFE4mUSlxA55dqI1IPW7WI

pgUS2YmUSF3stYgUx6uCBginloFCKZkUzOUHY4YwZt7H9cl6udIprMSfCmj2mKgALYdBAiBAqawT5ICiVUUhIppOYkmzFcTBwPTOSwpwuTScyj7B52Duw7CANYJR7TmIEGLGzwenAsXclQIszTOgMy4V9AP9A/ckQpM3SUxId4QkLMhZ4bJBkycoU+7o3KxYeIioB7IGCkpQpkKTvvxGVFwBN/uTmwbCSpCnzpJhyUxIOUcnKlotLjFL7ycXkyzJ

93RUYAlMhCUiFA+4pbeSp8lRuPUevL0VYp5uBWUkPFKcyaEICKgjylNWCtMF5PgQUhgpPEgwGy8FS3BmHAVrJ9BTyskE9BpWEX1CugOlRyCk6pMoKXHkO4AHXAogTgREfgkfkyApEPQOKxuwFP3tSFdApmJSIejV7B22H/uUFef74CSmEFPZ6JfWPSYbPBgYjklOXyQj0MCgSHA0lh+NDZKdfkuPIWbY7wlMb15KYSUid8J2Q8UBbyB2rky2ekpk

JTa/J2tB7nH25IcYz6DDslPZOWQt48PBwjwiLWqPZMHicshYpsPZUfWAuIBzIcqU7UpC3B3ljkPG3OLG5LUpQaSFuD5bHX7gtoTh4MyUNsl9ZKl7vlQ7CmOTZZyAIgKNKVaU7bg1xBiwjvC3vwJ6oz0pi2S+LI63Deya5waP+lpSgymKIz32NC1HlM6awDsljZKdKQ14fcQWe99skdWgjKcdkxRGj3g1y47EGeuPGUrBJV2Spe6LbGSymxqXuc6Z

Trsl8RBYQIjA9vA65VhSkMlIrKaPsVVcFDhgmoA5IHyZwU1iI5iBJW7/DiDSmcU48JFxTJvZqyDjgJ8QsVAY+geyn6ZL7KTU5CyIQ5SO8ixdwMKf7kg4p7r5tozT6RViqG0OLMsWAlykh2RXKW64BnJ3OSe/JbVi0YNfaWuAzjomiksxPiKb3hJAwnuxzdgzkGsMpFEylA0USiYkNeAkkIG+CqAXmSbykCrB3SWJ7Kfya6wpZDNmXPuM46O1J3kT

MYmq5jGiCPYFa8tehZJToxImGqpFVXMvd8RvFbC3AoOBUhyJGMS0ok32j3IMvIL0M5ZQEKk2tSQqVBUzhKbVwHYQhLBxZi4xNGJiFTIKnFbCcVH8OJzeuLVKwIQVJ8ic/Q+wacsTlrJ5YDV2jRUwCpkkQfaya5l8FBmsTCpR9hsKlkVMkiKsgb+sQPQeR7cVIAqchUpxUzc43kgiIEYIPgYiRSWFTSKl0VPbWMHSCqSsw5XynX2nfKcTErLAPi0v

aDC31byPkU5opp5SGvCI3mpgJ6QQqapkB68yVFIMqU4qPu4KxTIIRK5WrySeUsIptMS3IC5znuQFgiJmJIRS4imOVMCVPg2IQyX8RMNF6VIcqUUUy3Mf3gLuy+WHhqAFUwop1RSFuxRSBhuB5AKK47egIqmeVKCqduNaJQdCBaX6ToGiFs4GCypXlSFuyk7Ak9GIYFS4iVSMilRVMtzLPsKlsFEZHgAVFI8qcVU1opxIpjqDqGDxMNAvNIp1VSWi

lnlP8uFi/DxACQ5B77HlMiqbVU4dC1i5qCA2zUnwI0U+ypvVS2qnUvwmoQ7cEaSRVTWqnsxOV2IYgA+4mrB3KkFFKSqSVU8y4w/Q2OCBznaHtn5bKpyVTVH46wHzQEP3QlAXhIqYl+ZNiiZEqTpsHa1hJC7TlUqXeUmmJD418FKVTUhnrMk4ipclTaKmoGmnKiLbAisp+kRqx5RNBiQjE49geAYh7TamN5ULlEuGJBUTKoAPjQG2LCfPngmIivom

HROaia9EwGpRexfYgayAorH0jcJeYWj00A7TyRPN5OHC+iMgpxwZROoIJ9fbGpB9pY/GYNnLUIBkXZGoHsWwmlRMI8UieV/SG8wdBA9dmG5FIWYqJ8qSE6yndnq2G8WXasqGh3Eq1RI5qbkYZvIOkBTWAakEuKBQ4fmp7NTptj1RNO7LplPQg72SfNjU1IFqdLUzmpzeQnrhwSCNIMDQQbobNS5Ukq1KFqfZZeCsoBUiqjdeAaRjrU2mpMtTdIjN

IHsRA6QddUkyMaal1RNVqfZZUnwyz10UEXIFaRrQ8YmpAoVSall5WFuPjIYN4zLhBuhmkE0sFjU8TcZeVpHgjkB8MTG/TMhwdSSamh1NzzJM2VFSm1JYpxE1OzMd7U3PMkVwgQbQFgcRCdYdaJ10S+olqsHq6lW5Be4FTRLom51MRqeWPZ0ogMBTUn97DaXE9En6J+dS2DBoN1rwGygKDJqfl1wTg1KqiTx0eT+6E0nOrRUVeqTxU+Sp5FRyECYw

BxLABqB7GLFSxKmeJWZ5GjXegc+hZbqmExPuqZ4lWRASBQqEC+rBgySdU28pC9TzqmeJXeoNLPIAg0Wl3knEJLuqdvUxvMJ2RP0DLQCojG+lI+pW9SPykMhECQKpcC+p0Qg30o9VNWqX1UssQrVMG+CDwCkqc1UlapNVS/6Yf1JvAF/U77smuTntYhjkI3CfOfBQIDSnIhF7FMgBSpZCI2FZuinS5KwMI7nZewLeA3HbNGm3KexkotUcURKEACCm

d7kqMTBpJsReJDu3GtCkMuc3JXOSsGmHXhDLCM2X2sV6CCGmc5KMKTuUrAw3OwB7hXGT8aKBkhhpFySmGkMuDQWFZQBnu6s1yGmMNMoaQI1HSA01lQTEDQH5IbOU/jJlOSGQgF5F9qCM4lCQ81hBGlcNOEabgJJS4NY9LUAb+Sq/I4UkmefcAZUA+eE0aalAmapllTmkbYbErMEpXIWhWVSWqkmNIh7HvsC0BA0Qv5RoIyLCcfU2+p8SU7GntTw9

0q7LESpqUScKkQ9hngBFvKI4j7ZkokkVPeqWvlWHw7k1gVAwdW8abxUjRBQShgNxcH0lRGdWP6plUSwYk8dCywPhgelYhpZ0crt1JBiSk0gGpuAVzEBe5AxRMRoZnB8NTnonHRKCsjtwKbY5CgrGI51O+iRtEhupu+1RWw3NmAsa4gMpp9dSkalsGD9DMgDBABDEC66kNNM6abvtIyofKxt+AwgGL1CMjTGpsdS1IpBWXK+t4E5vAhMBjuiTNK9q

XHUogKOiBe7JmVMO0os0mOpyzTpmlEBSxWN5QPuAH9AHzpB1M9qRv9FZpxPZBly7lQwsf1faOppzSGt67NIuaZ0wK5pipAbmnZ7TLqS9E8seBrprn4RiA8Gu00gZpnzTn9zg+CoYJQdMieV0Ty6njckzKmduHOUILTr0zJNPhiZDUpZG1ewDUCpXmEBrDE3Jp8LTwYmg3hRQDeUX6e0VxFdqyVIHqaE0pZGFzYzwE5q2/Ecy2U6pMUTXGkMuGKJs

oCK9eBzx56nqVKp7NGWCMkoiBP2AfchfqX/UqnsZcCnuI2UJEYGu5Uapr9S/6Z9klLrBHmGWQnXhjGk5VO6SuOgbS4gZB7PgGJNWSbEkpBpU5szaHwRJ2gDjAbRp1kT6klOFKnNjqsAaAwtdhQRQNLHNugUesg7ugtXB05h0aeRUaD2OGl+NT630FyVq03DJ5FQ51jX4DSIrogA/ARrShkpcQDgwJqJVIimrS+YmG5NhQOesb64sIRXEB6zkQacr

kssQ76wmQieQGz2EwYyXJDrSA2nms0g2GHbbfgaNcPWnb5lJ2Lj/I6AMUSLCmKtLKSTq0yNpO6l/qzSdTVAem0/ZGCv9xViP0Bw2BeGS1pHPZlljlLC5SnPYnXItbSj8x5rGRSccAjZ4krS9qmXI0fLG6WGtowO8lfKctNmqRz2eyJkpBkKjCQGpbJS0+8povYg6mPiHpWATsRlpZ1TqWkSmFWjBmoCZgvjQayDmmH/KT40vipOgVtoxtoMYkU7/

aJpg9TRexs1in7O2wSfeYNT0WkQ1MxaaHdC2cGrw52qxkTfiflEzupsvZpwmB3ClVJKWP5pedTBmnBjC/gF+uNycRpBU5T9NJ/aX8jDAMpuhwMANLDJESB08FpsvZplKuIA1loJWBqJ7zSKmnmBR/uKiUoNS1x9s8godN+ieYFOmJ4qN7ZCxkRg6R80u5yvEg+Nhy4AnEXm4b9psHTACx2oGU3kKOWn61HSSOkm9g/iEHOJ2wxuBkOn1NNA6Xc5G

bwmupD8Cdt2uOsR01DpENwVvCo4zZGEGwTjpCNTmOngpRdIIUvEKa+Ai3mlcdJo6RAWeos7uhOXChSLTMEJ03DprgVldgxr2DnmpeEaJSnTpOkQFhniaZAAz6kto0WlELDyaQi0iAsa2lnJpTrBqlsB3DupqTSAUq5oDsIBXpbAMQMToPpWdIxaV4BZdUNjYS7AwEAN2nC0m9pfnS1Fx4QEC6Yv6Y9pRLSyiS7ZGKSRkNVlg3zQCWmiVN8afAWDX

QK6ojZDEsGi6axU2LpX8SoUC2KgIRsl0ndpg3VP2Bf7lJKNVSGVK27SYmlYeiIOAqQG1gGngmAqsVgnqal050I4fgKzAhSEpPvi05rpu7T4Cy03AfoEEk1862XTJ6lEo3q2BvMHLQQK4huktdODGEM8Z9CcJTciDB+Es6S+0lzpJKVhdh0uhMqefgpjpwnTnQiaTXuoEDeY/qpMoTmmp1POadt0k5AywZWhxIGG1qfbUwWp9NTuNQ4ak2FizAL/Q

ktTdamthJu6aHgfsk0lYs1A860qSm1EudQHUSaSBoFlm6rg5JX4nMNvunjEBZTEM2f7pJBZ4KwShTHGlqk4aUH8ItMHFmCgQeH2FZ40a9SgZEwlwkgj0xchIWBkekkFhYIOGORLAhNcO5TDlNwQMDQNDqJBZxixeDH3ERi9HlK2ckboCPCNTziCYdR6YDwiqFF5Av0LT0hXe+FSCZxtTDAbEwDDz4kyBtjpLROA4Az0slqaqAvrihYHtev5KZtGd

PSuem7QDamO+sKxAY4jpyzkP0EQDL07fg3PS8gpdJJybEopTBcHPTRsTq9Ll6XkFIuAMMQ8BhtKnDRkhsYhsKmhekA59hpWMSUDqJblgR8g2uXg1GO2HRROfYxYq/3AkIBsbWmUWPTf4lutM77knvSygsBxRtIqpX3aW8QcHpoFC8NxwwHigHnwFpMM5ZFpQ/dPD6S88V2Btmw5yAXcCSwBQ5C9WytSXumN9nq/ua2EkiOVAtml3NLwGDjU5gI1Z

YRdjEVk9INdlQ7pIdSHmmAlDL6cgCNyJEZBNunadLr6YuQC/KLJoZJxOdOvaa+0iVK75AKSrtlVbgDBWbrpq9CO9J4UA2NiLgJxpU7TF6mDBT8rKGQPaQMQh8Ymb1KZacX2LiAirk84A6DCsab/U4dpghYTljKUAYCF+LFw0LbTBgrYbFTIOwQGYpFrSE2lWFPE0EUQeMg9dBvk7YQVB5IQ01YKe+xBKyD2JDPIOGUT6ytwOawNXElwTw4fYpixT

dUrbbHlqQNALwguYwBCmR5MuKbqlbggBlB1dji4GBdE0U1sp0+SdUY3AJhisGsZ7EAJTB8niaGLIDDEWxSqtQLOjsFPbyW2UrAZAlZ4qkbexIiMa+DAZRAzASjGB0cVqVNWgJpJhKBlIDJENDN4G8Rrst7NhHmUYGWWvAhAfH1mXCWID2WKOUwQpkAzqBnHzn1Ui3gYQ24AzpClnBQCnsR8IKRybMY8D/9LkyX32MaIl4AdXK2IBUUWcFejJKNiu

iz05M4aWxkjm4yw069jbQE4eCddbxJl/SeikWFjiIMhTW863pc7cy7VLWqfdZE4srugtdAR60XaVS0jAaHSAzdirbFN0DYIkIMU/ST6k5HVdHOJuaggCCMmukhNJy6TkdMLJ4ShRvpTcmfaf9UmzpOR10lwV2X3mKTqWIZ1nTb2mepRvAugrFHAYqtm+mNNM9CK74OUGOOMoNDDRJTqTX0kvpeDB4oCl5A1SXLgJ7p5tTHaniaGRauwIBXAqygv1

y1DIdqfrUhoZVcAGnBMJAekG0M67pjfYMdbh6VywNclAySWfS6akDDLzWDLIBgK0CB6cEAawT6Y/QCPpR0JXHYhKWybHYiePpYPSFhlJ9KWGejk3WAR88fD7rDLD6ZsMyHp8aMK6zkeD0QPFIuYZGwy/unTMxENF6rePAnY4qoDKji/gPMM64ZrsC51h87EzOiqJSjWLwyIek3DP3GICTEpskAwEYAHDPaib8Mt4ZvOSvaSWcBVWCCM37pYIzwiy

DqR9QRzA/QpofTQRmLDNX7FtWELQ6hZARD4yhRGbCMtEZCIUMRmzALgoNiMvoZetSbum/wDCYLYvByg2FZShlTNPKGbRsB7+PKRDjC5DN/aWmjQ3QQEDkyANjUW6XEM9IZa3gbyBlRX23iClKrpJ7T4iwoqQFGTbIEFK19Tl+nxFieXjKrFHAgMBXBnTtPiLGTWZWafFoRql2DLfqbiFDKAPeBQbhz7F2SWYM5Vp+4xZNh8wFgaYQQRxYyjS9BkN

pRjyWQ8A/YrrALRkCZKsMLZsVhgdEQpsH25MdGcVAKtALw0bubzFPdyYHk4/UgXUk7KV6UUnj6MlHJfoyYjD1dXEqut1e0g6gN1inzlLbShwnUu42mkVEAhjLUyWGMwNYs+TVKAfwOCVHsU5HJqYyPmgd6R0AdyNFqwjaQFBke5NKLDVOLhILvi4sKxjIAGVf2EMgTDgJGkmnBrGYoMttGUUh8Ob2A3HuimMjYprIVu9jA4LPdKXOKSJbaMi4Bm2

FHOPNAGTRTtwkiJJJBKIPyge0ZMjTyuYLLmBsrqEGNGzbSDRkRtMnRjg3bjElQ4E3LhtILaZOjLApnCBRnI2rS7afYM8rmKoCK1JI8T4Yh7kPwZy7TJ0b1LC+UpaQCOA1FSwhnDdMPSsmWen+bgY5Xa62mH6XzZRV2GCwYBA3z37qSl0nrpX/Yi9h6iVY/iU0SbpwEzsFrvkFPxEnwjwuhaJvxltFgCLF2pC0gVGTfuiITNv4Ct4MHAP6Ay6CxLE

gmYN1Cxg/+wLnJZrmn8IBM4rpDx0i7jETK0GoqM6fp5WgmNqbrBlZo4XClpS/Sl2kYDXR2FHsA3ksdQw57HjM1GUK4cXwzcBcHCZRPNSkO0mxpdEypIi+LH8iZ7SMtpuoUXWz2lOvtMJIRXJq4zdxl8TJu2D+fbCJ+oz/WlX9O2MJhEtSZCwVeC5SNItydw0jTgOkywyByzR5KVuU3QZDozRqq4J0wkbAwx3WOX814hFW3VAIqePsA+AB8n6QyyM

APKANagFAB8ACSAAtpJAoyp+KmCRyRxHFDCnfgTiR5DpY6h8fHTWOedBaAYK4OKy3MO84LA0x6YvE58sCn4Cm9ForaCuq9jiFFcMLKEVRokdxHoSmlEdUKr8TUI2ZBS38gg71+J+3ryIRJom0iaVyyMLsvn3ohBsft4J9F50Qn5jpIruJlbD4wYL6OiMUErPQml6IqenOLjLCcgMZqBuP9+CAxlxHMqSgPAajWwFbCDjOc8ArgUly9S9xpwjmTq6

briSCgYZB3xypCUW+kDDMpgeVVYb4VqVM4QboZogbmh6C5MXAoxlzJZLAyWZ24yKkEQiDhDA8ell83SCMnnRygePBOsgcppKzjjKPIm8QQxYN4AKkr8+nriJ2E2V243xMPwd+1cRISvayqSMMRsrsIDrOCdOfGwwI4vrgcUExOoJEZHsvUyw/730BwGas0EZx/bSPYBB5lVcEjMiCQb+keMxi0IhtOORIUcrqU9XA4zJOiq8wUbGVMBzUDcPA9QN

3gGFQZMz+pmozLETK1OP/cJp96ZlMXGRmXjMoKWgy58VDEljbyLI2E7IHMzcZkUzM2NqkOCSJz4hW1pDVGGmS1ZFAqc9tC5ScVjNsKiTXRhxDw2CpqPFlmbqNChh0BAyUBi0l4lG5AaWZaszk3C+vmjLC8kaAcMn9LJz6zNBMjGXRN8LAJVlCTEHRgKP7C2Zo0y5ZljdhiGsYMnbY4SBS1x6zNVmZbM52ZIeVd1IqAgBsLNWKaojsz1Zm+vm67i8

DXuInmT5DQhzMNmQE/HzYu0BoLj2nS9mSDEg2ZVsznEr9wBSCNUQYKw0czvZlOzKqaopjFEgTL9RUDOohjmWnMgHscMA3eycUHn2GioUuZvszmGmJbHYEIsQCmZ9t8TKA0DSmmflFOfK96gPnp5hFeCi3M2MsNexkF5lrzfcOqDeLA1WBJJp9zMmmfufIeZvd96mASoFy7jW8CaZbcyp5kmxHGLOQMzyAqcBnO6LzNb2svM4/KmbpNGgbzN+zHNM

hls6UzyKh7lPS8j7mV4cbrgj5lpTNRsjUlDJgMKlZYnAtivmawIG+Z405mkpGQASxONuKUgUphr5nXwBPmaqzESQR+BbnJkiLHuC/Mv+Zt8yX9pHGG4eFMlAt+pwJf5kLTPv9lgYE1p8PhnICxNhIOq9sfuZuwNppmBtJDiFp/IzwE6VFb6tzO3mYPMk2IWKxl1BAYCGEJPHC1Etcz3LaX8yBEEWsdQw1x1k5nx5J9mbQsmQg1iBeCCQsy4nIlsd

ZYwsyBplpWTo5vdM1u0yo5BZm8LPJmfws+uJmyTI4DfOGqmezMsRZjMz8ZmSLOzYdF4QDgSQ8mBwMzJRmYos2wKfy1E6ziDT7gGAODRZXMyS2a0RXs2OvgUyAciyZRjiLKZmdoskxZh01rcBMLJ4WZYshRZq/I67HYSJ98WwrCoA2AB6AANAE0AEIAFi+vcRC6YDACswBERF92E29R4G0SKCmfWyCbYon1Rl5HKX5BGvIPNQy8g/4CWhPCFGlwL4

QaeUlcGTbisBPGwOaAFYgB3G1KNIUTaYrex3TjG97ehKEYb6E14hKBcfw4n2KWkP7Uq7+az8HJ4UkRiFBHgddxbUzvk6zOPtcWmE3bEhiyRZnjTKIWQPM6aZQ9Aelnq4BKVvAspRWJMyzjjDLLnmRjIZaZqZte4Ct0OX4DHMtMs9MhGLIhwCZaCgQRZZucz9kAcoABMWcwaog6E05QEoYP6WVgsmFY5+9zUCIcLcHCbqMZZGS53tGWfBOmXB7UQs

vGTc8CrLIJ7Px0nFAW3RxAzDXAAEeOg19e8i4wniXJXrUgnwDHwT04zPwMSDb2GQfR8era9jBlx/yUgFwgWNQ/sz6D6JQJUASOoD6ZT5wVFiGTSWrHkiK6ZqTs+4jXHlfZgF8VGQADAPlkCb1ccTXnZLQ7BwGgw3SIkcMxQZfI6K0Aq5RLwR8GAvcGAWnhnpkILWbgGlwMf4gN4oVxNlNOkhx8NR4f0B+gbYOAhmUNPfDe+3BF1CorPIeOislFJ/

wESNHOLjtGnAQPFZ8hQbhEhaM8hCZQSgExiwEZlwEHiqet1XKgPNc+aRzkBYAQN4ACiv0zLij/TIbKIBvJEcon10mrlJAQQSOgs1ZBNCrPTRtMoQA7CUNoBDtLWAUrN7shJrNrsqGgYaxlQF1fu6sqh0nqzWomFjJx8OmsE66i3Ayezr+jg9vGXb1ZEHtHp7hrP/IHGvFpcR0BCT5pLKm2GfgZaAokQuVlL+V/gGjMkfAu0SsFiRvhQYP/SNGQu9

cXcLozILWZks98owqybIpqDlGxkvWfNZGSzM1lboPhTJrKYyu9DMG1npLIzWfBw2GZ6qzeyCXuDzWV2s5MgmdCxojrwlM/gN4LRZP/sK1lNrJHWWMQC5YVqylDIdrLjgI2s7tZ2b401kYzMLWYOs9NZw6zs3z5n11WK9MehgW6yN1lVrIvqKhQF4scdcGIBHrMrWc2sqEIHw430gXQGWDF6skNZvqy9FpQhBCWJrU+CwwLSIBAGrPHWacUE22twA

VpytxLnzu8IWJY/uB+1kzlOFuPsrNt+VxgBd5I+Ex2FWpGmAqbAu9I2zU+8NTzHUUNayxhioMF05GasRxYKrBVVhSyE5WY0pHNZczNR9jmJzUoCUOPLmWYQzYCyjFSUNGs+ogM5h8Nh53A6QjdsCtSgazF15rvBZmVD0elgS1d4qnoWBYquXAJxAndCEAHYwDiYN0gRVZ14QXxwbJCrgJvJflpj9Yp3KowAlWfhgFmubhgTsgOqQEmbYuXvCHSlu

iBSwL1cph+e+pamzfFgabJCQXysmFZ/QMnGCRuAlHInLMM24Ww+2psrLmRuKA3mZD3BOvBsF1ZWd/WBXM4NhgVAjBWABsYROkkrmyYYr2bPi8Nkst2AEmRU6FKwNQHppSOlZEs96NRF5FDWDDISb2xTYgVkVMBBWeDYILZsWzGgye+MlCaEokvhMoSoeCVfHpAEkAcTB6oByF6+HAlMSdDJ8AAKIwHL5wKVuDtADYWqSliAxRYBFQK0qbh43RAHI

DyvFBqDcI5gwCRgvG5+HyRaVe4TisUG58lkkKNymUUs8vxDe9c65lLJoUa4Yv0J2o8uXF6uN2vmpNGIQmWtUtQKdIiyml5HasKVVgjFMe0tcaow+awHddt3HCRMmUSi4KK4A3QkDBRcSc/FvMgZZHcyLPDHbN8IKds3LATn5rlkJhNrno9s66AlwTFvpesPQmqAwGZZFKAVpnzLNqaR+wBFZj4gf8DtQBWWbc5NZZ7rlOH4nLHjfiSsjmsaOEwVk

XLJ2KSys2zZbmyOT5WyEB2QdMhWK2SBeNlerGc8vYvBu4aSzuSakhXwAk6shdZYsA3bQ0rIi2cls9DosazQ1l+rJIPjmOId6iGQhbZdfwyCofAYmZHSEtNkXMn1uNisVNgxTR38lrWHCnktXU/maKzlNn0bIfUgfZfNYMSduIpRGUlWaLsrgwMmy3Sn+zQM0IpskecbwhzNmgfw7MaeHZXZMuylNnrwjcMB6MvKA8vUvaQoEDE2SDZJVZkmyvkJb

iDj8fDsN2Aj0JxNluPweyDXGTzSyM8zwHUQC5sT5obHZEaCNSARIKweAascbQxHw35qj7HuTDjs73ZLQhlbiQzw6ZKCY7pAnuyIiCh7MpIJagCswKIQFa6FDH0IFD4QQgNMEa0DRrw5rEYFQUgDwCPPi0bK62RZ0dAgsiCbazLbF7ofnszrZGeybXzmoEPYNAiWA4XEDU9lUMHT2VlWQRCLAJlN5PimXIaIAivZzey8+SlgLCiNIIdvQZKzG9kF7

Kr2cWXdNAChB4TAayNFwd3s2ZSveyjwr8wmm1BswPPZHWye9kWdF62amQfrZnGxp9kr7Nn2Wvsyu4fWz4bHMEVcWR/I9xZRWdFDHEAFrJEjwJKhUKIv8pJAHQYbCiCdwLDcIlkixRzgGMQQtAgFZdsrSTzS4NoYyoEJLA2kGWVBA2XDMjVZUpA/85yglAmUOQLEAzBIGICDbJyme6Isvx/DoTXaehIEYRNs1pRq0DptlWY1OABonBwwxRkGllyoh

y1vtwIqohic77HKMIfsWFgqWId259JH4uxEiZvA0mZQszyZkjLPFkaGMG7ZtsgeZyQ+K9maASZuAaY5k6kYLMM2VQPJspoATjlntzPnnIQs9TZfBznXIYyBe2b7BZTR8G8r1B74lS0hPwF5ZXhBbZlJRhe2WVoifgm0y/ll8GCbiu8IH7Zcyy6wCSpDR2QkYAOZwOz4ug6HN58Hoc6h67yzodnWeFh2Wm4RQ5TLQMBo2bLlvCjsmVKY0QwdmvLP2

4Nrs2hAsuyu1B2HPcOUoczw52+zTVle5k+Vn4c6JUHhyMBoRrJo2cwYUjonEp7DlOSIc/MWspeAaMh7q6FiHiOW8s9DZbPARVl1rOaNLMs57o+hyrm4trNlWYqvIR4P8ywFkLTLUOdzCODZL8RhIAPEA9vjIc9fgzAJWPGeQmqOZXEWo5gljqFnhwFu2VAQA6QEZg1VlgbP9+BMUvo5oGyJGmDHL87DQsgPh/RzRjmarM6gJIcg5JgBy+1ljHJOg

BRZOgGvc9NGjDHKAOeBs9IY8OyxKaEGGIESgIMe4H8Iajnq4idssKZIdRBrc2l5Y0hsWMRFdtZeQxiVk2HO0EFjsZypzDZMNmOUJZoenQZrZMgJNx7jCUJGgUpWAZcES/8AmbKBMIKsgVU2ayZxqbxJqQCrsr6Z0IdgzQ+4mN2UfYSW+tqy/pkhHITYDOIajZZFCkiHmFSIMIY4dHe8K1yVlsbJVntIQYGZsDxJV5KaKD2a6kxXAcUhEM5JHLDvq

HeTgk9uyPPiwLOTNE1/Pxomm9BileHM+mTuceLYtvTNF41VzZ1hAfOR6Ec8eyp8MCYYK0c2RgJxzyd5AnIFWb8FUU5Rxy2jkSnJuQH5s2NgAWzox5THPhmSAcm5Ad0z2qZE7KYYGqc4A5A6zOOD3HIpUo8c3U5Ixz1TkGnM34LPAd/Jt5TJZmRzjNOfqc8wBFci9pnGHMOmTbcXtZAxyEZlnLKSLLscmKgHNJDjn04HlOUMcZ8oGhyrYFaHJs9GK

chJQQZzQdnhHICORssoo5rDY+TkkMW+2eYc/I5a0ybPQ2LAmHmvMYj4yZz6GCpnIrMJG+Fk5LDAOmSZxAkOeUc2OyUhzvlxCbNpOXBE0s5qUzwFmLTJAmGCc99IZLVQFl1nIQWY/BEPATZyVRLoSJsmW/IuyZR5cHJnjTFEwc1ucPmICi5w5QAHMdnAATAANIBcnA08hScA0IwpxzWcPoalgMDFuedGvE2KJHvAwNDqOsGdfQxnoAeTkfvxKOWw2

Rpxhf8M8CAni5sFPw4iJToS17FJt0gLiNshA5jvsenHjuJTVv04laRkmM5JFs7PoYf7HHV8LrtfH77qFaWddfeIhHSzUwnBux6WQNMr3AcxyX9igXJwGV7gPI5jCQCjmyEQmOTBc3Q5qZzW6EgyEQuT8swYunc8pGxhuxVmSnM1hZ9xTwIinTMeWSf43C5LCy85lNWCtOUhkYd0yPtSLkjTNDmUSshqqPPVVKDgvQ1mOhcrQB4WzgVkNXDQuVssw

2ZgJyGdlge1zNtdsni5Y0zYGCCnJ02U1DHyEUFzx5yiXI4OOJc1e+f9ixLmoyIkuXHQKS50wJOdlCnN02XVxVS5z6COPikdCkrIJc+SUzBzODlnbKR2c4c/zZGIdaRxGXLu2esoJjgWpzCdkSEBE8hdsrBZ+UUGLllQCYueXEAkWTlyhDkU2PuWYjDGtobCAK0GCHOXmVavc5ZPpzNdSBXMwWd5csFJsFzVpmoXKcsKociZZUUiGjl8HOT6inQBK

5hii0rllnJuWfmOWi5MszY5nxXKyuU9spKMMVy/tmFHNOBCVc+C5MJ9vTlkH3CuU5YCq51D1rmhGnK+WTexVs580zxlmG2icOStLI7wPIcIrmTzJIWbJKRS53Oy+GC9XKXmf1cwFo2qyatmrkF4ICpcug5ziyvdpAkVEYAXmHhgRkoI1mvjkaWLiObi5eFzyLl3yi7Od7EWs5bVyT5nHdBpOf8cstZjRR6rn5nOO6BhsqGZgRz9sG/LNDOXREMvI

MqyEzlBJLSWBemZ05iKzXTnuJQzOb6/eJQzFCzjlS1DUKf6QAyS31zEznVEM34E1cjhAHVx3EoRnPaOcis9i5iWzvRK5sIvVjDchU5kh9oVnAnJlOUc5GssKGBxTlRnOc0FCcrk5rNTsbnHHLxuSEYBk5AXwmTnrIxBuS9csG53sEFrmQVnd/nbU6m5a8xablJpADWXyswk5WNzmbk/7mYoVEcjE58Owibnc3N+ucYSdE5+NSBblfXLEIJmcnm5L

8jeznkuMPLpS4gDR40wjWh3lz6ALjwPsA9SpjMB9gA6ANJgaTAxAAkgD0AHAukA5fOBI7ZHcA9JkrmZhhBrZb7gQq4vrDIUEnrcvwzuys36+1G5iQRo6Ok0myU7BbC2rVIUIxDyOitFXGjIOHcQ0ogqZjhivQlzf1QOSmwuoR8eITgAaJ22RNggRdxfrxPQRoC2n0o1zf85h39HgDpajcvra44YR3Uz5nEqzI4OdZcrMkyQkvLk8EnboT3XdK5Ck

TcFjpHLFWdt2B6a6uAfTkATKUCRDc5RsDEoplmkoE1OYIs7U5Dlya5k8XOWWYoYJU5mKIiKnNqKCuQ/UKauoNQrOkY3LcXM/Mts57Vye7wE3L12VKYeq5cVyyblm7Ik2Y7sqr8IZzXhoayw5vvTc+1Zl6NetTo7IBsCDsstI7NzjBnqJMfDL5cwG5UE5/j6MrNWsMys8/MDdyn86EbO62DONX+AO2oKdmcXKtclPDY65payXsYj3JastKc/ooQqy

sjm1rKw2W05Qa5PZVsZ5VHI/hJ7ABDZVCy0Wjk3It2RscxY5Iyk7EbtbOCOUtc6pOF8Af1ktlj8uV7tI+5lKy8HZJNnnWd1ARdZXUTiTnJrI08MGs/2atOzX1mZd3fWcBgJ+5WutiQg07JfWSYMys5FxRkjlkTjwdp2s7dZhazLrmAPNeOTdcqdZK6yd1kS3N5OTTc5ihQjBp1mrrOhuXKc3G5dRzZGh7rLRfjlAYxKCxyPTn1kHkeXaWRR5QbQo

ZSYPLvZmoUthmCjy/kxaPLFEZasoh5rqz1HmqoE0eUO0OeUbXZ6lYtQzZGkBGSR5wjzrHnO9WH3oesOG5jDzn1nCMGoefRrQvIocBILBuPIT4SY8l1ZWKAcRm+PNseQE8hB5qjydjY7yhJ2aY8kJ5EZg4NlQPIo6TA826UOjy3PLfHQAeS8c66556iVHnTHLUeTqKT+5HDzqako3NJuSNrXa5z9zTJJXXNFWZEcxNZ0BZr7nrUOiCLQ87lZe1zyx

ii3KjWakgT/wfNyxbmxHMbgLg8z1ZUYEt7khHOWuUEcxa5s5wd7kKbJ12ars745KIi7Vn1XnoGSi2V+5SWyuLmdiBj2SxVe9G5+ZLpnqGAOWtHs4PZXuz/QpseLuuevcvKqOzzsQAh7P2eQPcyK5RdywzbknMjwHs89Z5SiSQ4inPLueQBRGlYg9zsFmH3NY2RzczdhFdyTdkfPJ9iASczdh72z9lmJnS4BjU8OE5gJ8b7kA7KMOR9coQyD9y6Hk

2xCbCv9coi5IWhNtGFPPdgNevO+5+3UsaSJPLkmlUZW+Y+OzuSnoLlwQJE8vJ50TzUyEcXKWee/c/jssTzgnk2rKY4L3chXMV6yZ1kIgN0uYzs7ygUXoz1lsDigOe+OFFA/Fz9Lncx2Oyh8OMugHUUe4B/4FAeZpcjjesr9RHit5EZ4TJc7TZSlz5LnNdAw3hvPHgsnoyxXmyXIVecNc4rIfOy8Nnq31OYupcuS5WrybMjeFN7IBRs5L2SGx5XlD

XPQeazPK3ZXGyzKl8XPkSQJcgV576iFdmnhx/vA685tkTrzAiFuQA12UwQpEyYuiGXmo7OoAp5s8NShx0EtyLPMRubIPQIyhBANtKMEC08HZcol5JfT6Ky3FkB9GAAyHZD05gkAPHKxeT/+MWZzshnxDl9zxgJRcwVSDH8DgS5vMOhMIgDgZhFyHlkovIyBEI8CvSTtyBBEhXOqudIfWq58wI63khsB8HGwUnY5NVzWODvhN1VsXw+Jx4SidfBh+

P0ANsATcAHIllADeLP/dtAGaHgx0MrMC1fDMvs/sl8uKhjeLqUww4XrMLT0SxKARPqvVkvtGwvAEQQakiei2EEWgPZqITZlLARNnmWG1dpeczAq2UyKNG3nPgOfLyKiJSBy6NHFTKkkVq4+JuCQAo3TxKCKCTlUdReH4oQPKU9GTueEYrq4tFd+/HrwM6WVBA8JEExysWDaXL1IW88q7ZYIwYPmzHMKuW/MoS5udyejn91x+eTfAhKRbzyYViliM

OedtM7CAOZzftmVXMykRS8yN5QFRMPmX5MDeRZcjgJ+HzTCA7TLleVzs4U51rzSTDdvJbeeM05owcDyPqBvXL3uSYcpG4KDzRnkAzK4NPtYa051FzJPxtPNo2T08zjgRbyP95tTyzWURs8E5Uk0M3mfLNJWTeiNF5lXNW7kE7KJeVNAW9QVTycjmKnOR2eZcgPBJTy5Hk93MM+cqc8AJ7pzpjkanNk4OK8ndAl6MAuFBPPSagTcU3ZU7Bzdkr3NU

CDY81x5RkBHoSrPNx2dDPAx5FxQg2i9PM+ecfcqlZQ7xOXmQHK1hiA4k2w4LymVl1gDI0DFsxzgGtj2dp0fjl2Ap85s5xgjCZls7PI6dPeX45Jayqgw6QlYEI1DYFYN3Su4B6fOAed/vKV5DsJSvll4NbWXKs0o5Ym9qvl6iUW6Ak8yB5uLzUZr/rIfwdL9JjedNI9TlbHOMaABs8F+/cS586jrNhAFg86kgXXyvj5AbMJPkw8rx5h4jWNjdfMGb

CNeCh5xJRmHkGAWK+dK8r2gZXyuHnHrJvWWGfZr5EeYOhmJPkC+a9MSLCLOyP1laJED8M+ZSL5LSS5UGJfMlLJNEePic+dwDnnrOYJC8A09ZNMyovlyoJPELd8uOuH3yD6iOPItgEDA4QQJyxHvkGUGe+Q4mNJ5RqzywJJfKe+XnAMia/pycbmRnNM+afYOH5EPyEfmIZwq+Y5Qk8Q6Py8LqETSJOYewEGZpJyp4p4/JS+fKfAT5DNyhPm4/PB+f

j8iFWoYQZ7lgwEV1HesvOI8XAIVDvHIRuZFs5n5EMDWfkLnUreXTcPy5QNyCZms7M/Wdd8vD52EBNDkb3MgBEN8nr5I14kLkpnLguWmc+swyGzOXkJREMUblc1OZdczR/w6vN/iXq8t6ZLCZONlCVPtedjM2a5mizRsZu3KmuIrs+Ji0hzLnkkLIsIY5su6gsBxNDopTIOuUVcy8+EozuhDUbLnuchcxX5C9zDa6QCGt2Ud9H5g3vyFfmxXIMOSc

adt5ruzG3luuHnueH82Py4Ph6SiDwAD2VV+Sj5GyZOKzQIGXMOKFMI5TXNYzlYfO8EAn8vMISfyjUAp/P8OessvP5MVSMlDFUiegBIlK2pEvz7rnHPMwiJH8ht5/8A03Br3II+fsc1QwE4ARrzXsM8kVVcmu5Pby+W4O/0JrklqI8BS+Zq7ngrPY+cs7M1hH4S4nEN2O/CadUK8AvmJWMDxABaAJgAdUA+gAitmjUF8WZuAaoAT+zFzkcjw+hixs

Q1+j9BMhHR61lRIjeeD+LcA0OAjbjrniMDHPZVro/8IXfMQoFd8xK5hCjJpF2YNgORvY5XmxSzR3FVCJfeQxomvxh9i2yQq+xqWWcqG/kpbcdE7Q2kH3tO9OJSgHzSJYTIQFlpQchiu1BzQ4rN3OsdNxctD5rBzACTaXN6wclcmNgzrkhlmm/KMWUR8iw5Cyy4oA4AoUOaX8iHZmnYKAWGHPRQDC8vdJCaIoPm0cDPuVzJKCcmyytrmhzIM+WZci

z5dnZmAWxdBnuWrs+3A/AK0jB+fLj2cIC4S5WvzNq59PPY2RwCsi5XALQTkYEG1nh/QGgFRAKRZkMv3q+Yec1P236yx1kTfO+Op3czAFKAQ2GZzfPjWRf2Qu5dvynPT5nwwwOqLJLqZRzJ7n/zMbsGT8yH52fz44C5/IV2Bd83NUXkBCCACtPeuUDs105kryPpw1fPBgbWuGT5Npy35pUwhl+ct8hUZXhII3lc/KVeSCrHPJEqAg5m/dClOVSFLh

AvTRlXmJAqF6mPWRn5MJzrJy99GZTMRkJIFsU4bnl8bP8+RkChIFRQLsgVRgRkBSrPCoFhQLSVhqvNqDLtcxnpaXdeViAbJG+X0jdT5p1zu/yRApm+SI8g85dZx8eq7xk2+UECv0g0jy8Lpz/xpgAECmXeLXzZXkXq36+WMc4X55HSwQbeAvcSosCz05u8YhXkBQzi+snU3J55pzHTn8MycBZj89YF9pytjm/fK++Xd89VBWNyNgU2fPLWU3SZ8Q

YqB7Tp2nM2OUsCpz0JgKw1m+JWxuUk8lSAdSALVmEPNpeabfJH5PwLOvk6AvG+bo8/QFXNzNAVDAvoZgsczr5K5w174nZCrOSdcvB2wIKOvmIbOaBRl87s5GgLijkwgpIeUBsCF5dYBMnmQzOqeTg80L5eDyzq6/HKaFG2WC+GJqzBPkZoOwcCgwakFBnBI8hcfLKgIRs4JAygKq9qB5Ds+Yq89fUfhDaiCD5HDbNptLSaRnyOQXeeCFBXeWBN5j

J4poDigsFBSAQfJsmKyeYDFvLannKCrkF+TYkXnVvKF+QU8wq0s4R9gZNoyHns28oFKvbydQXYyGNqSyCtI5VALlDnEguyOZV8mP5PvzVpn5nJxBYMC245dgLXfkofIgeZMChDZdSAJ5mjXPeedzCNVZ8ILaH4WLL6mWb81RC0PzsHm+ORpedas7QFDjyHgVCfBnhtzMEQF/Oo/vnvfPpwa88235/oL4vTbAoiMVEJZYEpdyZgUlfOCBfL83M5vv

y4/k26gKBZDAKoFTQLH2Cp/IMgW7kStWgoCEsa1/I5Mkc8wj5zMyKMgcz3tnh0sOv5bYKO/nbBDMqKqgNC6nNcFj6hXIH+ZBnYupfMynflHmTY+caCwf5orZysGeEGPHHmXFhc9AK/AWwvIuBGW87AMBbyKrC8fP8BZhELIEORS1ViCLPhWdC89cFB9z5ZmhtiB6Ee8z8iItSzwUHTI3BURZbwxzkBeGBd0lPBWuCh8FF4LbkxK4Kp9MQ2XvZq4L

9pn73J6VsQ0wAi2szA/D75jvBR+CoCF0sQ/z5YIm1nlGgdahhoL+/mT/KN2lns7QQ9/znsSzgsuWahC4pa6ELUlJYhiQhRP8ucFPZy6J62TIpccV3HLZFQAWXi0gDVuSlBc9CLQB9AAzUBaAJjwegANV8hAAwAHjojqEjkEZMBL4DGjWMEJr4+V20BBFKw/FM6itw8QpRrU58zl/Sm0EBGwwqaU4LW5gwHNveaX47/5o2zYj65Cn/+W3oydxbe9G

IBdKMOqmrANReqkZgCDzLLTuQVrA6RJByo2LXXwpQC87JAFFBdwPm8eRLBcR8pX5Kzi6PlhnIFIr4Cz8FE6sAGCbPKnQPMpPTwiHz4bmTIDfueXPRxZoYKjFnqvMtecx8yS5agKwLkorMmedCcu2WOdyTtnc90nCbHAWoFUgMK9hWXKShb42BlZYAgyHlLT1Q+YlCrg5anzkQUpHMOBQGPDKFhULdPl8POyeWj8cqFRgLb1DqfO2+vlC7o5FUL97

CkPNjbOQ8pqFLBy6oX72Ak+TEcm8Z3h5aoVdbnFCKlC3WWwULOZm9LKx2Wo8HVZY3gSLl+QqcMLkC+KFc0LXjCpAthWWNeDtiCWyAoWUvPLnp5C3uM2Kz6HiuQr3BY+C10eKxy1KBrHIgcYpdcwFWYLBDxiyw+/ngCuQ5zRzJllRQugufaC0P5pVyhcQTTLxaaQEWOoLgLwdnWgrJYHNMsOAx4c/bh9/KIhdhC3ZZ6JRlrLbfPIcRSoVgFxFzAXR

uQughdc0UIFYnyrDluXLsKR5cxq5jFz0YVTXFikSXYA4guXB+IA7amlBa7Ld3Zy0KaoavjhPstS2YmFROzXPkKkGXuZTciERZHy4gWTaJn2fNEjAxTMKQVmX3OpIO7Af0sbdSCXlCLJphaaCv45X9yMyxbdGpHOx2Fi5yNJsfmV3Ox1MjC576AfCcXlTAp9BbYMqt5gvyL7lY0kDBTTAQvq9uUsIW+nOe8cs2XJ6Fcy/5x1gvuBbt0g24JugVDnI

fMqOdQ7U75CKBsSEJQuahUYC8x5+sAgvnMGBmmdLqVMF0XypOzpEE4BflctH5tPzyfnRXIdBdTIefBWwK3Mk7ArzBeL81sF7fzTaFr3GvwBHCr5s74LAIV8fOWBZ4CmgQ+c4lQUGnG8hSqsjVRVkRfWjpwojFHfc2mu8XpWBDcNneDAQ3Uj5nPzOYVSmm6gGbpHeJpDMLXlMfIleTXCmBkk/0sCBhmg8LEJEHYgYWBWYHCCBRQLXCgtA9cLAOGzP

LQeRssfuFrcKKz7dZ2GheSCqV+eDtx4XZgMnhe3FLp57Tz+oV9woKBSGwSM5rHBDei9QsxOU7WdeFOAyKIybIEJ+Ums9qFeUKO8LgYA3hYfClAcnZysQWG9OKyBx03+4WEguKJIgrYedWcxqFNmQH4W+uEvtFj8qqFpIL6zA6/OjaYLstn+ktyfrmvXP/hbhs3X5QCK9rC3AotOT4aE155Gy/PDs5MNoQLs1A4ZOJ0hlFEHgRTB1eG+a6ygfl/kJ

8yDl2RsFWACb9TbpJdhR+3NxxN2xgsCfkH2QLKgB75cuANfZrKCyTNrNEKQ18IUSC6AhZ+dLGPn5vm9OwUsIukhWwg7L5ovzblkub24RVJCoX4T/yiZm5fL7eT0nT8JhWcStwUACWoDv83JwcAAZqCmCk1EXK6LxZ9VBO5D5OL7sSO2HygdKs3Oq3tktudcQOuwIkhAfB23K0RKRsgXp1+Byyh5HB0hpi8ybumUySInXnKtMXe85SF95z5pF//JQ

OS4YtA5lSyUIJQgCjdLsMl0KihQKSJezG4QE1M4g5AmijpG8KNYbLIiayF13cUAU9TNhHH5FKMwxLBQJy0AvShWTfA24JdhT3ySqDSRWHsJQBnxBsZCCInNmV0crqFXW5cAXNYykrLw2AwFBUKnYX/QqDFuL/JcE9aBfQXELKuhWwsE6FLMhhiBCMxEOX1c1pFk0IDxButLsrl6jF35x8yIFmGnLZ+X48g2w5qVWrkjIo9Bc/qZigGZ0EYBBmAv7

BBc+nZo9zpTlwrInue6CxBZTcNrjxn/WEXH5mTZFMyLtkXSArSck/CcaICsTzrmhwqzCG1C6yq6OwQ/mlgsdBVciqWFwBBQRBkoAXgBeGCu5O1YEHnS6VwcA0OH6FHhyvkVxgqHWcD81E+QLyV4quWRdLq98mu4on1Xmk65DBRVhcr7ZctCzBGlwEpKJ35T4SusLW3kF6iQLOWobIZ5E5IIXJwv3BR/CsFZNMzfnhkiPxRS6co6F/YEAEUC7L6lh

4U1WFgNzksD1mGy3PXXJFaUFlZYUAGSouSW84rIzKLJGDWIp3THYirHYFiKlT7w7FfmpjC4i4Wby1oXH7LgYYKY+f50ABSJGY8AEwOjwUgA4UBnlwCYD2tOtMHgApABlAC5OFSPku8mHG8qAgpCtuMUgL4sXcGISxMuB2FJHwG0/aS+IoLjKg8Ih1BmNfG8CdGBMewoOAUhevYlxFrgtt7HURNm/kR7cpZU2yfEWO3kbAEM41bWD9AgkXD6KmxAi

cshQYSLdv5mQrR4od/Hk6QFz4kXzOOWOVaC4Gy0HynoXSXPdIXss8FFP6400XyLLDBTQk+lFbAKArm+QvTRdMCfmF7dzZQWdQuMuUNC+VefLzAxYcS3z2INC5KFPiBh9mV7IS+sAgu6F7kRAZ7PHJJBfp8slgdXSLqrewm2BqxTWYFEeYnSH9otDaDOYIdF7uxx4XTfM6BdGc+Ke+/9PXJNyIo2FQipuBW+zbrm9go9hFGgJxgg4KOkB1OFXjmzw

5yFD1yUtnRulKccuCqg0usKsQBZaCt2XRwoP5WHzCIUI7OvRfMYAv576QSGLZyIAhcYcgQKzYVmCSdhIh6UhFFgFhaLoPTNxjYebb2dCchyiOn4A3LOmTIODogCezpP5020LhiJ8zlF3f9bmBi4AdgPuzCzUTnwxYXuXJxhZns3CFjNpOwGSDGwxdjC0FcXn9Q1TQtUB9B+4tKEll97ijDLgpQCP/cjFzqLvbA0QLxhQCQsFo3mdfaaqzzAeCg4b

gFXVy7UU4Q2GgYxi7jFzGKzPkhhRaXn5QYL+nGKIZTg+BExem42nm78jpUWn7JK3DOAIwAlQAzWicuw4AAtkBoAWzs20BLTGMwBQAdHgnF89UUV00dqDosnlI2BCMHK8JyIwJNcEAgGmD/VZefP8eQLwLZQPbjI3BKiSBEOpkV1FN5ylIUeopKWeNskO5XiKw7kumK2tKTALpROXAQSw5VH8MYCACmIYMM4xEmQoILoI3QTRqjDeUkJosO2YWxNA

FkoxckVLClqhfdskMF40KJFmrcM7Rfwc6pFjsKykUFXLc4J94SlA2Cw19FwfMkIgx449FDHy4FlWwsERdKvMcFKEK3QUzIuthT/VQ6FjAKa3ix/LKuTXQOWFcnzLQUxnLL+VM1YjF09AMYXDYpz+aNioGRrGK3kXd4BsgVmihFFoLzpxIrQu4QAV+eFFn2yVsVxPV5BW42A55mFytsXA907hfisi3ZrfylsWHYs+emIC8OwdOZNsUgvOB7ixs5t+

qdjBQQXwxbBR9su7F2TFa0AWrFocGWEVOUbhyRsXUAt9XC0C5x0f2LpsUA4p3eg1Cte+wyLX5mdYpspk9cm458qzukV+gvg+ef4NEFUwKUnlSzJKRdWi+lu34lNYVG0GDBSb8vNFxALEZ4oIoeQK7KMu5m5iScUUQDJxYQCwnF6gK1PoOYowqIqJOQFdFy/YXn+H3aS04xzFTOKjlmZgtOWfTilx5nOLAaxIfPsBW78vnFHOLGcWC4pjwH1i8SU7

OK/Hni4qdsiDi1wFM2LicWxg1JxViIqOFW0z6Pntgv89gashdAQKAnICgrNaxcRCxQIisLoHkDpgRhSnC78S1xy21kI4szyUBimt54OLioWFfJ2hVisrZ5PkKksI3IpJ+a5czN5xpzi4Vs9XvOo6pbeQkeBMeEcwuWeTMkK7FAmza0VrIrSBWtCuFuwuyfDlCArKaLti0mFutok8VtDC4+ajIWbFESB8YUNuRkHHSCqn5DIKRVA0YrCUHRi6EED2

KeVhhfKaqlDstGFE2LcMU9Qvj1t081eFsDVYYUovPk+Y/czL5LahusXzOm6BeDdc3Fn1z4znw4qEeO0vI0F2ELZTkBnNkedwkIfFyELiIWmnNeBZsC3xh9WKiVGCUgjBZN8uIBC+KhbYEPIgIHE88pIq+Kt0Wa4stoWE87z5iokd8XRwr3xTgioR5m6yTagYoo4+QYRXBF7lNdgxX4tyXiQi/dZSjzFGqd4oC+Ro8wx5JKA/yDN4qBuWRoT2FP3z

f/CDYttOa98rl5XsKnyBF4v/pCREejF5nAYtkDqGxEcxQtJhc2Kpjik0XyrG0cjhFrC4nyAJ1ltRdJkH2cXH9+EUv/P4AT/c/lZ/MtNPRiIpy+dd8lKwqeKqvmBApa+cd82NEggLz/qzoo6Bb18mDA4eKOLGQbMliCtefSAPLDWYVHRLlFCr8klFOPMRkj+4uung+QZ7YOGzrIGAIr6ljvQajZfMpGhiVtVTYJgijjYgJ4ZCXVCm+xfa0ZmaziA9

A5YIpUJRlsmf5A7y5/keLIkAOKDN92jURBqATb2NAM4AOV09XwObxMjwOAFtffBhS5zqkE88HiUFt/RchDbiVXjWlBOpOGQPMssiIklCdbnjmeV7MABAbQNdApvILwDks8aR3tzQta+3Pn4XYYrpxv/zHznqQroiaR7D2O7ZIgzwQ+HLxFWUZ12EZ4bhFD8J2QbxEqfRzl8pLEtEViRQ6PQl2UswloVJiBNhdCMSoltHyDsXvYtzRU4s/NFcBg38

WNEpChRNCvGA42KJYX9gsehbTi6KFn/BqPnFHlqJRM87w5uuymfklor6Jc9ClKFM8L2NmbXPkBbxcwYxTnyI2BPHjYueKaf/FAlU5iUs4pEuW+svOFl7gC4WbEryudsSt3cfQL50VCXN9hUcS6uYHHSt0AfLDdgOUinpFLlzxLHDEGsMkQi/a5HWLErmtIgkhSKfBRArxLocXvEqVjD9shrIpP8+W5mHIeRW9C9XZr81ejYC3xaWFLijAhDvynbC

tzAXRasc4YgKkBYSVybUd+QiSygFQzZToXIkppoYFoEN5RuzE3CFiLXxVFs/EljQgw3ngwpPxWGc1ElZ6z4SXxkApJRriqkl5QRXMVkkqCiT4E6VAbfzT8W7ov20EOCupwqjSkxAcksZJT9YU955MCEiabospJRvc71BTxKfaSyxPpJZL8hrFSmhqUX4bJo+S2ChklEpKnrCZAurBYn9dQ5xJKCAG7EtWBcWnaYBOpLzODrEuYMLKS+v5i+Lu3jL

4trAGaSvsF6ZzoQW3HK9OVPikfFjZylAXbfNz2bRwB/F4wx2tlp7KnOoszcf5COy7dSMfKAFJ7AdjeHpLDcXOkv8hbSs6uFBshPSUFooF+efc4tFdAKCUXkSyPXpDYPjM87iqUHT1x/xedMzqAUuKCNDZktJojwcz6FXaLSYFeQuumR3yTLFk0IBUWFhOphR3c4OZkgL3LaArM2heR85pFl2zasV0kliBVTsxrFwuLZkX/XCwJTTPHAlNIjpkWvz

OORXfqNbFmNzuyVbIrsiY3CjS5Elz2sUjkpJniMSzk5s9zDkULkrt2Uvch3ZhKzEcUtIuRxUmkQZ5o8LO7nnEqkBdn+EaF7sLUHge4sLIGCkj6FshySyWMgsdxXSc+yFpALywWpiiFua9cpt5U6xFWBe0EzJfXgmBFKfcM3niwuYuT0SuleSxLXVkc/ObJczC6h2DOK7HlO2U52cGSjVJWwk22kWPM/xfphY7F7nyM8WN2BNJfTgsvFHqzZiWOAq

SIfQit8lrUKCQVMrKR2qxOOOFsjB0CXs/PfKEyCvUFNIKuQHvrOf+ezs+IKNlwsnl/wqRRSL8gglF5D7SV2jWWBYxS3L5o+L4NkUdL+BSMCw75tXyBKUggumBS3CudFvXzxKXoguEpafDE4lMlL+8XW4sHxfECqDZXBLnXo9ottBTj8tSlnBK27Jh5IfaDRS80FojB6gV6UsvBhr0G+FnIK3SVbCSpmeYbAWwPdM68WRrMk+Y3i++GipK9flInJ9

JWzCplFZGydCVIIuaMGwSzn8DGyJdkWrF/XLBSwoQ8FLGEWG/KJ6Nxs0y5ooLeAXkAl58I95ePAaYhbLl0c1oxecmClA30oLNma7Ludl6wIAlb808SXjiwJJXhAVf2rRLNARH2BjeTYXNlGmaL6iUQopgAgH8u9FabzG0gAwoqxRNLJN+w/yPSCj/JM7E2isBKFfz28j12hPBa23WDU4tg5OmH0wJxTk2Xru0lYbulcsG4SK8NPjY8RhDyXzErLm

c5nd+hC4hGdKtkucue2S25McGKkjLBT2uylDi+s5o5LxJCazKlkFswc+x85LDqUEhNghehi1IpmBBNswrIuoiNGvPYcnEgK+wPUrD6IJWcDAvSA22D7UrepRxZa7wYMSuYkywtB5L9S/NCLpQKvCmzLW6hdS9s5WMTefCT+F5YCrDDalUVylFSw0v30IgiMl5TByGyW+vmKgAdISB5GC4M0V+JAIIBNS3ABU1KkykDkGecCCgTEcqfsxoV8LOsWX

QlIuwuRAdigozU2WYYC0rF1XYbZmbMHPQK5GeRWr0L4Lnu7W2WZvQMpcswlIMXIvNHnoU6dLpF5A9jlFnWdxcqC2T5CeA+aXnWDMXoY8AuJEBLADiB+Bx4cWQfmlitKpaWR4s9efy8+xe/EQqIDLPWy5rbsJclIuyu1Du7R2HK9swqewL1fpmeUr4Je7tU9URxCy4hoorfCDvCgW5DtL+9miIFW/sxS6WFxMT4uqLNS9pa24mfFGWJIiA+pQ9pQH

SihQQdLqdmePNMBeHS4yggdKXaX7OisBZ8QHc445g46VO0u9pcLIHMFF8Kvmzp0oH2VHSqEIowK5gU8VQLyOPs4RAnkBqfTEVA1JY0CrUlTTky6VoYubIGTgtylguydczUlIM+o9OP/2hf8cwE8ZhlJQt2ffZG+zD9krosoRQKI6JBhTph8ltGB2bPB7IUlbDyz3mwzw30XKOCqlkUhHNAorQt+YCS4mB7MTssAx2NE+o7UdvSz0xdGD7oo0AYeN

IJAF2gCilXgxqunuiyzgzkBCnQsoFvKhvmMxqQK8L6XDgr5Jb8HaValNoFQV7iX02fvSy+luUB3xpbqAFgFxvYw2XJKv6VP0sKdLPsCrYSWzT1Rp7gBJbJspXZ/eQNdkrYmBEBzSVelMDKs4BxzMC8AnMoP5gmyZ6Uikog3g/5Qa+6DKgiUvhVaRMKSumAopLrJmkQr7OeRCpieQpiUIwNRAwjPSALkGUgt8ADbAEwAHXw4OgGDo3TLGYo+hlJVA

foCXUB34Hh1knoKCEFe5CzLRGChI9+bG806YLmKhVqQko8xY6E695H/zFIUWiR8xQkS0pZ/mKnTGlTK8wW2SL7eFUztoH8Ijvnp4FSAFHCilohPijt5nFi86+k+itJFFEqBMKdIjO5aYjwzHUl3YOTUimtFtBzJiWTrIlXNeSxo5Y5IDFmlooOFDCSgnFTRKicUPvEo+cVi0pF2OL78Vpks/JdtFEJlWOKs/qfooYBfF0RxlJWKwmWV8k7JQ1cXL

FNNK3GX6MUGJekyqxZmTK4nqsvK9eW6MgcEcj04KXi/XJxeYxOPFYxKewmKzGyxb0ckqw6eKBIWsOALBSqg3gl/UBe0jVEpaSG7S2I5ScKXTnI4EmnlfchE5CXyvWBFwpvYpZSiUFApQWXno3PWRTHipJgL8LSKDGUpEAabS+PF0zz1KYsUt7RYLwf1ZMxKYYit1Gx+YMDUsI5TyGHlU3O4pY18h/xxzLhgXURzhxSpSo85/7QrSV5Ms+Mlbihr5

1zKJfgfArp2Tu9XZlf/tEKWkIpfxTsy3+FZ2Q//Zg/JEBBj8smwrdQjKVuWABgHwIBil4iKWGD9MrqeYMyuM+i3zpKUrfPesF0y7RkHBLzkz6Uv6xRYjVtFzezRYkaMGbpdISkqwAVLFCU+UuUJaS7OFuDTKNkhd0sIRRe4LvqYVLJHZlMrF2fNS5sJ+GAASobQqjJWkymFetryjfmJ927BCrSkvFODQSGXnvNetoNiyma+WxsGWkMtwZccGBiQX

Y4YYhfksEDq68oElzIZgmXy7OfPlb8vlugsjCsXJ9WEaAqy9elM1zXGW6cmQZWqymqFmNLtWWqsrdecCS7mlB0gFIB4CNX+mKyknqODLGEE9gvFJfKSqRoUVKTT48sus5ExcXlpekBPmExZAIRc8SmllEHpayU6fI0YEoSkocZLKpbD9kvExTyHJDZxKL7KVobLdiFQSpr5NBKx0U8VRuedNChRhBgF2EUPrMQaCF8/55HNzwvkQIEwpRF/C8lGn

hPPkx0s+BXeS1+FKIL1GYmfInxULCgr56Lyf4WsUr7RQZ6Qs5MP81slXfji+fU8pTRaDcQEWg3J8LHni/6ZBeKgDH9srEeYeMCllAfDXyV81J1pcQS1aF0qzp2U+FnLRfZcytFo7LRHks3J8LEqC0T58sLMnlw1A7ZSUPZfe4ZKdilVsuFhUU85NF/2K/oX8gtvhRCclkwzTLrkVE/JJOZeS2D5POKJiBonNHsDic7rwR0yHYVdQvu2Xmy8vFFIK

acUBMrpxSEYCa5ISwprkAUVEWUBy/LFaRhrjw2IG7hSGFD/pM5K5Ll7YoOHJ1c7AlEmLkswjMsGmbHEv+4O7yfWVjoSx3keywMlAoxKyXHzHaRUuilElEgLDAW/srqRT2S9XMz7KekW84tYuSayoXF7oKYcUyKEJpROYS5AJNLHyUoXOfJZJ4TjlGXlr8EVwslxcHC3mlehL+3lShOy2Rk/KHgygB6QChQGq+NsAKZO0PAZwHGNxScOZgXAA7chS

JGVuK4ZbzzVAQQ9p4gzdEH/oqI5CP+s+RTp5rVl3OWlqEdF0OKPvyF82jpDwcpHFwhzL3kr2McRTe8t1F3mKwna+Yr7gZ4i9Rl0kjNGU8AA73t3orveFl9FcB/EHfMTTDCMRQcdTYSd9V2fvFi/JupBzowaNKRiRftszO59jKNqE8LKJpdxy2JY1wCDiWa/PQBR2izMFDxKfr6l3KWmbuXa1lrhh6Iiw3y9ZXhy7M+mHLrDnGnKhueQCnxlqyLf7

nR4s47KRy/KYUIUu4UJqSPhU1y/VlsRJTyWAcvaJdByqeGvtKkxgdcsz4ZTi/wpondDcATcqTHE/iyx5mjdqaW5MtGxgCyjq4QLL6fmQcuG5bTS9w0c3V7kzMJMBkexSmXYTeTp6BiZOs5fWckKlZ3KrYW2ctx6IJyyal2XLBN50cpu5ZZczGlMwKbOWezI1+fhcyRFpRdZ/kZINlRUtQWoAmwAP3ak8npABv8s8u8QAU8TQ8EkAAcAW8ufdib+k

JzNwQCtEA8O76x5qxqthQIMQGV2iXRLAKU5+OhqB9S0hhTUBOkDL2ImkRwwtzlXmKlGWecpUZX5in1Fk2zvEWpsPJAnJlMm0xHJ4vhOuzqmSoUI9+5SxNtkJB1CMdPonzGB40+IFJhNrVqlywfxD2daiXDksupeGVUXllrKHIV+/MrFj1Si/gnpK3Chy8q9xSp82HZivLMcWnbOcZdcUKNl3VyvGKy8vV5ZlC34Yk7K1eUs0ubRSSqU8lerKoOVT

EsB+efipXBFvLtuX40ol+LbC4L5WOhReWoEoopTmyiFQMBw0WVUjilqBJVdLFkpLTznIVEYILly0KK+AMVWWW/PNZZi0S6FuHy2gipbNyWdXAH4lF3K/iXJvMH2eES23ZJAK+OU3aIdufW8swOq7KOigV3Nh7sNS03Qo1L/7mYktBxfx0olAs1KPTDxbmRTgKSivAbhhuywR7IRvoGTGMlR7K67mxxhWsBoYJqe5vJHSWgwsR2REYJVgp1LuaQuU

paJfeC2xAmOzk5BoYvwqXRzO6lVLg9wUT8rqME9SgcZ2Fx8yV24tFpQxixaAct8CWHaRLX5ewCsjFm/KvqWE8u+5YA3KTlg7zKIUSAD2ALSAdUA2wBK2ySAEqoLgAF4AS0wlqCrhxeAOqAPKCfdjR+oG3CsSBu0/kEvz1cepuu2nOIMqDBZrKMX1i/mMNhmQSgRFPK4i/G3byHcXES6jRj7zCpkOmJ85fvYwAFAYieACLvJ0ZUsg1EAHKKnJ46Jz

GcZxEwv5chY4AXYu01VOVrFLldjLheU5nmW5XNctoleWKreU8OBBpRUSnxlvHLFflOgomJZbyh3lVRKU0WAooQ+cwKjC54pKL9CQXL4Fbbi+Ml0GLRCJK8srheBS6Ml6SKTeW+NgNeZq8lj5TAL9eUtQumJfmyivFTHwJBUg0iBxcay2QVhRB9zkD4vOZTIKpxlpvKl8W6AohBTMyyeEI+kM+ygCtq+sus4FFeCKCuUgCtBWgiGY4FhE1ykVOCqq

RYRCbNlu4DPeWOCusFc4K3UlHFKmKXuCv8FZ4K29ZPPzKKWYstYcFYKrlKNgqXBUBwsh+SEK2IVAQqYCUJCsx+cfyzNxWWyz+UycqohX2ABoApABtwAS+1wAEJDNagmgAUnB2YBpADLoW8WBTjHCUH/N55miAYsOEFp/vDGcqTdA/ELEy5Zyw4B1+m/ZTEyjV2e8hqBXNEuc5cTyrKZCjL3OXk8qNdl5y5pRyArq/HLSKABREIxoi7psvYZ5sIzo

tLGM5gxArXRATr0bbuQK86RtkLjF79CtChbx5PYVHRLeiUcCp7lt0KjXlJgrsKBzcpOOJoK44V9vKXFnT/Mk5VkKwwlRWdW7HQ8A7kC0AQW80mA13Azgzygik4L92+gBlABumN05dtkFpgZVw0rhLjAOWkP0WzY5t1HKzNMEtEXgSzuSZhie1CTbk82R1FGAgR+BPMXOIo85eMKynl3nK1GUoCpmFWgKmiRmAqBqHiANXnLHctOi8dy/IbnoA+WG

5mcJFFjLEsVApzk+KdMUol918ulm1amJ0MmC0dktRLORWvcpd5cIK26FhXKtqXbsR5FWLy6GlavKoMDxDkL6of2RgVaYIYhW8MDiFdn8pElHz0hS514no2KHUJpFU2LlRUv9hToHV0uo5K8ClfIg4u1FSpAXUVZXLzoEBnLOxbvilyFOdByOVnQppESqSuUlWuK5gh18sEFZaK51lToqusVj8re2G6K1UlDfzdgwFksWxVaKqX5gBLBkgDIu9pIG

K90VQFL1yyWXyaGWrMrLp+2LIxU87htRQOSjDlWorsSUqipSsOOSjZF5VyxOWWHMjULyCkU525K2yU8UM7hXsiz/YRU4MuVccuE5Td0hLo8VTooDz3zjabcKugVdzL9wQoPJ4KeNSOZmB1LxRXCEtORZ8CG6ABRlPFgXstTRT2KhYsWFxU95xkqgxXDCt3AjwIzkX9isvycGy5PFGhcZxV9ivHFfS88z5r0zpxW9irHFXfQBVZG5KPPjoUu/BECR

dsVJMx+PnYst9JYZ7LrlZYrkASG9G7ZXCyz56lTKR5zfTLZiGNyzMVUzK2uXB0o9OXcClJlHxzuMyf4VAhNGC5YlJagtuhd2DAgboLQUkr1y+nBPAs5XgGK2hF63K6fkDU0fRT6c59FOxKghUSIptFR1E9MVy6LqCWjopleSPVVs568xbDY+xDmZhwSlV5xQKeuL5IsyRREgAUaVMzVtA3EuUcS4yk4VkgoriWulGdQfRKpsVwsyGDm87IgRVISg

jZtHLfVi0zPtUk0zILi/OylSXPlAosuUyeNg5HlYPz4st4la3y4fF/fKAsgySpo+eSij65C/Lq5hKSpfGPlS90WzEqM0GrSDCAljyybFskJFKVIsrpJHyyjKlOiY7VI4SuCBSxirPFbGKFsVZ0vDhbmC3OlomK9YDxVP24JFhEAl33yNiVo3JjOBTCh5M0GQIJWPAvQGNM+JDlCryUOU3MrMFek8iwVmN8k2WnMtxBQ6S2z5GrzudnhSobjAKC9U

F4CFYpU+IHN5YlK8KFhPg4YGPPNuebHs67FfGhMpVkwsdeXrSkKVpUqJHALiuZFFVgL3IfkqnugTipFperC3zZLk57SkFqXroU6yt7FdVLeMU0sthiIaqcC5yHyjqX44TsOtniy1grVo5eWafJikKrSurpF0yOUUqgslmRqyoUVEgThaVagr35ZOSo5FJM8VJV+ArUlb1i3MVMvK2kUTgAklR+QReQNwJbRU4ksOWAOiqdFeuwDDoOivNJVGKtfQ

LVKBJVbkHrzAryqtFedzj4ZlUoLeDyK/653rLsz4SiusBYUi7JFv0qauWXHIKxRUiz2kqi8VYXnHK/eBuY49450rH4g0iJBlXSUf6V6EqsSUdIsRlWkU3DlKMqwZXkMuUPrE4gwlf3KjCUfYH5BrjwZQAkrFDaLbAEkADNQPsAC7h6+hvmHWAEGI2oV1h98HQJRGIeMLvYsJdMyAVx77AEEVgiOEV9mLYTKF/XsHMaY56qEhKRJXuUrkZbXomIls

ArOnHwCsQOYgKpwxUwqSpl+cvWgTwAN0GoAKgYg40paMa0RSLFr3x7GAt4DWFekvb6AHUyOPYHbN3cRxygUVDAqhpUkzy25c2K2Hug4ry+XDit4Ff1ynpl8TKDjy1EqrxaRXGvFksLNdi1ErZZZTs0PFNRLLZVuLzrRTFAZ15AnLg5Wg+CN5ewKu4VF/xbxUfCBwuaLyuZljbKNPkxyrtlTeiF8VacqMmW6cn0FVcy4oqhwr+iXRjxNxUJS1dBFs

qXZXQIrOBW8C5jlugqKBBWkuilVx8DxlKVzvoUYPMilTD8u4lxZKvGUfius+bAi5zwjcqY2Basr2sMXK34FpcrLn6asublQ+0TOVL0Cx5Xdovy+ew8ptl7cqbyWdypdJVZSyUFC8rPGUDyrPUCiyjzxfcqvoWKnVKBWc8uquBXLeDn9yvHlfNC2KFhNy15VNysVOry88qVgYtw5WWCunlSiHID6WnyZQWLiozBcfK3eV/PzJxX+XN7ZUWSxeVG8r

2SXnYoaJUfKjuVACqrZU9kuGlXOeJ6VQMKISFUcuMFRbWF35gMLQhKwKuK5dAgJBV9A5qSGfcvIuTmcwdFsy8h16yiuPmIt9KGAQCoiFxGiswlSaK7UlEMKib7xpJuxcSSuflXorv0UrLyI5SaCg2QMEqi8xfSspCAZKoGGTMTsZUXHLhldePMyVUBL+SHIyr4VfFvDaFOoCCYWWJREVbDKsRVIoK+pWAIOwrNIq/DlISCCxUgPyUVajKgQF58rf

DnQyo+vqIqo+4bILxDqISvHBSc8wqVLFVDsjCr2YVXy3W2lTezZlLZSI1MAjKnUVfzz47iB4s4yiCS6Xl/HKTbCyEvUJQoS1cl4vK32VfYuZwRoSxGlO8zWnlqEsCVT4q6/wXIrzyV22LHbEdxbcJH08YlU8woxiUNy9OVhGzH36zLEtiMzS+BVkZpD6Bqy2m2Jkq7nFH8rbyWKAvSVfkqmmhbiqnyVRCrJOBDi0NQt2KepUNsrnlQCc1Ml8krMU

Uf3PvJU0qkQV38rRaUnspTlakczolWMLvZUPStYeaeyh8lkgr2WVUvP5wjUqj15ely75Wcf2TlY0qvpVZ8rRiWPiryBb+RNZl2lK9mX+Ut2eUVKw+VbbLfmUbMunhWoKikFNoKgHnQzMcpdEc3eFJyrXjmbKv/5N3iykF7zLnOrrKtOVQI80bl+yqzlWqrMrlXPi+CRZzLdHz7AodOTCAn5V+AE65ULssBVbG/ECl2zYEHlBgopiGCqgEFznyYvm

6AVxxaHS6FV0dLKHm+rOFnvqs94WHbkfTIorU7WXgoAkonezHPkGTiSXEbCgKV8YL8VUe4V8eTNWOfYBjL4BSBSoTBQSqmXFVKrhZWoAjSWXiqqCVGQro4H12KJlUVnDw4WUE/AAvAFSccoAQagJ+47+Vr/Oygv4RPuxj1ovCC1wGZxi/hKvERbKajrBZR8eLqYvoVS0Lv0K2yuzlURElzlV5zSeVYirGFU+HXEVkwr8RXTCpfObMKz8Bc2ylF6P

tjQ0IRXVSMU7Ac6gY1WamZGDMIxpEs6eASplZFUtQmg57EqVuVnOPS5bUS0UCfqqOVUKYvsmVS4teIS/NtgDA4ynAXO4JskVmAEABLUEIjLLHPFMnELgRUcglSUPWpHqwxZgwlAuOzW0sEqQGFWx8uhVdBLs5WSAdBY+3doBWzXzqUf7clVx8sqg7nIHONVcrKt95/nLNoEkisWtlrPLSJq1tbL4Vtx5gP0OQ2VtwQUvICKM6ma/Y0EWengC1WG4

E98IGq/s5CtzI9GiukWoMaAXwAQDk1/ncuygABQAfQAImATAAqCzbbDFQWtAxghW8DfUpI7v5gG7I9+TzFwtEHY8iYLE5A5RYJm4QHIDaBzYLiQWDYcNKYiuEXu6iinlgdz7TGKytrVa+81AV77zwllNquSducMtOxS2zkvIftnphm21KHw+0i4uU9CPMhbzy8b5l0DbGXbCuAuQcKmpxc3Yp2ApIBHMpnERq4L1pm3yKNyjPHYOMDUKGLRCqS6U

H6okaP/oF0zSfpvRQhyTWSsqAiTw3PlNhVUUaXiQ9YPF0C1GzhjNkCJAZgpNNDxwxlVOssneALnhRTKanhdSJobKgwR+CQHYTsiuGEbphEQMsgMMyOnAnTLwsqiQ5GOc6VioZn318csADVQogjQFei9hNDuJs5H5g5axymX8M2Z4A1kVWAq4SxaH7/B4zEVsYF6QHZL6xy4GGGRTg+JV6ljbiDcJAmmmOGHzIXvhonp3IB34vsE3BZHSK5oBo7Ck

1fgCW2AtbQ1vQnQNbbugQJLYWIAvaSggHsjKPY1pg+fAQNxzUSQkABXXjZbKxrBwGAkAIIg9FUaxdz5G5NkA6uLjfR6yQxzGUJ6lguyATcff49kZrinp7ONwGRsQeA9kZhbhi3E/Go8Ae/4kxSObAxhxsXI1y+RupqBYan8wE11FxqgRGW7zlRKLTwvsdt2fmeQKyuZJ7QLPpjzwIrs3YwCqGHIzigPBqpWGCtMzkIGkHfOu0ISpeQ9AJtVucCm1

ZJZVyV99wiqirNgfiHGOSbVdCL3dqSNh6MWYvJMYi2rNcwpIB1zJsWLdAxGqO+RHasQ1b2YsPM0JYD0Gl3E7QAtqrbVS2qdtUJKnDIGBqN2pMsgntWfkG21Sdqsx+IWUmiwVmHH/NhQK7Vy2qzH4qIFNwE/Qy7Vz2rjtU3apFxNAwc6B/3hkJECjFB1a9qiEe19pfoDxRH1YFJ2VHVf2qC6nfwFM2DlAZAENVJcdVw6sw+BHZRjU3eAEqnjaph1d

dqsd0q3SHB7YzGyStDqn7VL2q8dVsGF5yWzwS4oxY5g4GbatZ1bDqsd0B1xsuqMGBKZDjq2nVYOqRWZxmRC4kLmEnV4uq0dVdNPooEpAZVSJ85lgQNLDsXlq/AGZ78zgrAYokeaI9AnhwauqMFzXKzPQWObVqqwVhYYhvEHuLJ1AA3VmeAjdWd7MRvA4PZOcRd8wUnW6qVUZrqtQKBXYhwX17G+fi7qjXVxuqdAroLHo+OwgA+6oahU4CPDLdgDh

pVZKh5B+VY/70XaKHq6xA4erpMgCLNzCKwQAhsLJkr1Vh6ob4Ly1P/YCk9UayysG9OOnq+PVmeqeOnh60FIMhsa7+3w5lCzXqoT1VnqmBpkmykZzs9NzwHHqrcc7Cg7nIN3DRQNvrKTJseqgMk3qsT1SSlRmmOSz1YBhYAgEU3qnvVWerNLg6C0H6VcYE6AI+rq9WvOSQ2HzA9xJ5htp9Xd6tn1XkFIJATqA+poQEEp4jPqovV7VlCJqPDODpPTg

yvVGeqW9VdBT+WuN0VS+un9j6A76tP1VX2VFYEykyyrhculQDfqiPVIR0DTznoGJYHLfSsojeqV9W76rf1Re/A8aBohPTHL6qr1X/qg4KxDwJsHMVhg0iAak/Vr+q0jr4q3gkECIfPVL+re9Xuo2/gFfCeLAwTZewQoGt5asP0YLxsNT5cgwGsL1bfq+NGmcBZ4GYTneCc/q3/VJBqUEme7HzwJLELtAWmicDXDUjauPa0V+yDQNH2DMGorRkRK8

WAKQ5rkFJiC4NXWjRoeRhyeu7U9EENVYYUexuACZ6wA/Ov1dQauA186NN1C2zOAIJwKqvA4hq6Jn/AS2YDH016sIeq5DWoGr25ugsTN529KdoBEGub1fIap9Kek4vyUaGXj1SYa0fV+dxhbhFhR5Hs2HGw1q+qIMrcdTGDI7UA7wOhrQDU0GvxOh/CbygZuB5IDOGrANeSdYlATmls5IZxKCNT4akNI/M9IYHfkCWXvi+NQ1DDgGSyPUAocPWNN0

KBerTDV6GqSNfptQRobU5nFFUGu8NWYakNIi9DOeExLGDgcfq4g1RRr6hiZ7H80GoQ3IgV1kMjW2GsPCj25O2xh1V1wiRGqqNYy5aEsXNgUCol4LsHo0alw1/iSfk7olH3qaRizg1uhreWrgzguKD9ACaA7gCOjVZGpDSCekqa5sUhuFgJGomNcnZG7YpPS/+hCjnUzgMa4I1DDgx1jbIjFwGP0ATFexqojVU+DNIBYgdqAm4JsDXrGvZLP94Ciq

KD9uSw/6sKNQsaqnwq3Tm4D6sARfofpM41nRrazresgJuEBse9Q8xqMbEHXFeCntAY3uB+hEjUtPFPVeIPB1SqDAQTXFPFhNSEgeE1J10KjWZGueJFKi4NVityZYRUgj2AKQARPEVmByr5yAGUAGLoGkAMAAUnCQyxgAF+YDKhvEg5nh0wAYgIxGBrZQ3hF0WQSBGwdho4cAl8AcvloXVHhBnrT3YnwJ6TLQCDvVSX4/VVVydDVVFTKVlW+qwkV7

7yFkFfqoEcrJNC+gkXK47m6yqX6GWQDTaIGrzGUtTNwFuzDSisOEt3VWL6JvcW5ASFggeK18x19hK8gL2bZExLBJZwmdj9ev0OfMgn7ADhRxuXFqbunfWJAvY7wDBt2kPo6aoX6zpryzg/GqHsOw0z6laK80rnemrOlL6azCFW+rmLhWgPmYsBUr3w31pe8j82JWDILSvqadV05giGRjTuLPgqjpsDAdP742HbhTuzIJl/184zWOcDaGMBWbCmn8

RkmUYhjTNYWamH+4oQ1HjnQHASCSRAkWTprQzXyF2YpdPQbOc8AkzPFNmtSbi2aigQV/8/Wo5bxy6kaa0z+hK9rTVkaGA2IA07VgTIQTyoQIGoAd+8MsI6Qz/pCjQHmZawi2RgOlCLPC2mtLsZ6arbBhtK1bKFFCFxKBMF4GcHLM0buR3d0Dew+El4FAWlgHmo9CussSTkJmxDRJlkBrxBui/PlOCAAzX9SrxIEKSizQsZB66DyrHP3hGahcucqs

BWWfmtygN+axcV+7SKaX/mrULLuig4gzOMs0CQHQrkYmawx4yZr1M5n1KcEfL2IHV7yzvyD3hJ2HGAkqC1qFqbIjqyBuQD2FNZYyQgnmXUumSSDBa9sMKz5szVyb0dwGKpNjO5FrAQKUWu6QCWai1SvaoDMQMWrQtQRa5YwtpRlyj3GUE2UBar/Cj0AuIG1mrmmXzAHggeaD7zUraGMos9Sb6ldcCHB6B+G3NREQXc1LOTsHCgvDrwGbgehgbHpl

zXoQs1QYjCNS1+pxHFi3pN9PtU2Oc15yB0EV55IKGkEQHKJsppxzVilRRoXl8/S1VlrNLW9mp6gGZsAc1TVpHLUtLmcte+UNs1CLZcbmqWrYfgZa6y16MCNbEkYCknObXH45nlqNLVGWtjgCJamYZS0kfs4PtCitYZamMYgiAy/SsWrWINg4Xy1bcLsnaf8CItQtdMpAhgqp4bZWorPrlahgZjuAkzUlAJx4SCOCdQflrIzlWrz/NRqQAC1EZhaL

Sh3nbChmvaVA/pqudE6ILPDK1a1GugpAOrUMCu0ydeahUGEAg+zVuWpznNY6N01dpq3yHAktv/loka/gT0ArRrhZlWQGZtYFpve8yT7esiYZBiiXtVCaINzUemodNSeIYDYEr0drUnaXnOizACsQo1rG7DHWqh8Kda9plL5rurXKIJHCKta9dS61q/tKsfMatYkaNQsR1q1rUsMA2tbHEiq1iFqqrXPWq2tSda/61nRLMLVMb0Apm44l6121rwbX

NDGotdngUNYVuDQfk/5JAIFACMy1r5FglDs+ERgJJMk8Qs5qMbVrT1vUMla6y1Uv5tLXGUF0tbeoEq1HZquYhLmvO0jpa3gqsFCFrUqbzQimTa+m1FNrGbVq0nJtW0ctc1CppubWrmpI2ZnAJS1sUg9zVs2sHWBzax+guFqI6z4Wrgtcjtfm1lNq2gh8EpzsCSgHiqLCBMyTvNB9YCHHdJgFVL3kD9HPoZlgU7mJ/9x8+xnzHIWtCsVBZVZsndTq

2reEJra31ltzAHxniJD+ZomwDvCVtqjbVa2vWPA1/cXAoG4MvFq2vzwBrayFczTFZoBewl0RQ5sXpoLtrus5u2qNNj3iKwc/LT+VHO2t9tdba/21jxRI6wXWBIiDQI46UYdqbbXNMQyySM0zlwGRBRsYG2qGsJnavOS+CgJkBRcXTAWLa9WcPNrEXm5oArshtpWhADoC58Dy2s5tT7ZahALPJLfmJWuSZk3ayW15DVGPBbgzohDk2Cu1K5qFbWYf

GDpCQYvmB5YECbXbliJtX3JaM8FDg11QvPHxtSZawm1x/CBGr8mtHngQQaAQP1rXrV/WvetbgJNe1SCIN7X7wC3tXDa3e151597VN8RqcfbiLE1A5yQ1VHQ3rJBjwRURBnkuhaBCOQdKk4mAArkgKrbJqsZ5MvIWh47xi9CSKjHetJHscuyBuYINSWiLY1XWa/fJ4lrDYbnWorIN2ahpowprIj6zSLcRRX4jxFr6qAAXSmv85T5goMJx+JNQHQ5T

E7vQkYJFp0qRprdqpVGv6yAXl9FcbIWwavNNSGsE01o5rG2FXmsutWzNKMx51rDzU3mtatMaakc1qGE7SocOqtNWWQaocFpraHVcOrcKDw6jFAfDr8wUhmrgdSFHediMDqfTUtmpBkCI6001OkEZHXNmqIof9CiR1SQt4HWzHPUdS6ar4YXVrHp49WvAudo6sM1v5rwLVNWrFsM1Sox1cjqWAWO4Dw4S8gm2cMeAuzUaOqkddt4fK1M4SN2lgpMc

dTo65i16VqHlJrEEMdXm/FR1zjrskAsWt8dRcKse4ljrVHVyYtStkGqm+1OJrClTS6A6AAgADGAAwALFCrVTZeAJgcqImtE53D5t2ZlcuAjmg+mp18B6MA5sh4S4OARSBMFzndWlspZyrlgISA6cD8J0Kskww8jVKkAW6mZmsGFVESsAug7iOnF5TIDuQgK6tVz7zJTXoOtNVWgKtkecpq8K4HLNjdKlqZdx4jkq+U5kvNcVtsviJPrtl1DBAj7V

abKoXlOwroSEsOpGtUw6qaoCjrrTUIqD0demsAx12zrhzW8OoT4N/imx1kg5nBlSyDRUDs6sR1QErIbVYz3d0PbCmh1nDrTnUMMh4tSc0SSZabFwHWiWvtsUdMt3AcVr6zXjkmX4Dc6151SWFZLVhWth2Daa451ojrQXXviRJtd5a2sFD1r9HVPWtbqNPQHzwLLhrZCgrM+tVGa9kY3GwxZ79WpS4IXCgL47eqTcA1tEUCH1a4kahLq4CAhOqzgJ

o0QT6zug6PHuWprNVamMjYvtZbbq5e3GtWapEue0ZI0XUBfDmgJi6l3+zNrwgHLWrb+Jy6lJFbwdBXUoQ2FdS19Rb5UrqlrUPQugkjdat61u1qaATDoLG4dSQA7gSDAlXU72pVdVn8DO1idqtXW/Wvcxbq6ooge5QKFxIDiqVRIdbV1xrrbtKdEHPwPREWjZbuRJXUbMGldWmgq8pthsu+V9pjZxbK6l118rqwxYVMCw2YkaIS1xmExXVMuvKCBx

a/C1YcAQ3WuWq5dW8HcGwBRCnBCQdMiIangerYGVTUOiYuvjdU8pMSJHThAyHabXRdfy6vSAUWzFp6dIEQAdM0Vuo8LqYrX4umLdWYLU0ZxLDwXWjL0hdeDYat1QHT5cj/OtwoPFa2cg3lDm3Wlupaum86nG1z91xDBFuvVSTW61t1kahEbVO2BGWZm60yoGkYc3VPkFcdY3QMfY59LoLWMWvS6DvVFYMtjrLnXjGLvNdyaz117jzPhLruoudVNF

NNBanSwyBRrKddZfi7F1AFrFLU+pGAICpam0VSLqDnVPWuIqPq6421ezqH3WBmvfNWSvAih6rqEmAWiw2dYw6481NAJrXV3WuDNeLFAD1knIU1gxuvFdceSu7CDDqu4WAerJOLy69N1hbrQPUXWvg9VmSFnYoVqG3V4olQ9aw6hUGeBAkoAPFH9Kdo4mMQcHqjzVZkjStQBY0J1UaBcPWbOoQ9V7PI5SbjrVKUMjDI9Ww6olZxLq+MzjbkOZTW8V

j1+Hqj16Xuu+tfFc4a14HqD9D7Oo/dS1c/916HqHtmWOpO8EJ6sD1UnrljnvurfNRJ63j1Wzrl94CeorFksKfa168TKz7qetMdV9azT13wptPX2mt09dcUed1JFqjuHTWs3NQ6av/A47r24VzyOjvFzAQj1TOJCJDyOuhdYo6i/49bqHqCQuokOTJ6mcpqbqrKQYupQ9Qocgs1gyQ0eqXnlDdZNavyRMZA9IEGesC5KDa261ve98yXnOvVSONwwj

OarqmD6/uv0lRx6lYMY84VUhd2u49W8UaSIBjQYt7LjIxFC+6kOOfGg7PUVWuq4TuakW1d7rpjDOerAQgGxeogJ7qHXXMGHPdVmkNR4PnhlppTTRLQexwGMGMMgvXXcaowlq+ODZ4DQVt3WfrJ5NcN6mz88LqcoD8WogOYJan81OookPVBeptekrGAN1X5qpBHsa1otPmyi2AhdkA2CbeuAtdt6sa19gMSIjiVUvmR+axb1QbrlvWGuCv/jdOC71

fQUbCnXepAtdxIa+1E6qEnEXuXytrk4GagbAAebwHACEwHe5CgA0pjjQBv8uh4Cxo/f5LMqvlwoYDxXsNqLIs8Syg9kaWvhvt74ZSe5Gr+fjWLDZsYbDCysPeBT3UF7IvOdqq+RlrojRhWWwwNVU+qyvx/TqNIX0RNSJX1QkZ1bDcO54J5JwIr+83hOLiB0BokOs/1X346DVA/i1nUS42Bde563Z165q+fViOt59dAiE51ylj89ggurNNZ1apT1P

VrfPXyevI9Vi6/T1OLrkvUmuXVSG+Q6l1PjraXXlmuZSJ/BLC10NqNfQ0urLNbmzFo10r1khCX0AI9RL8lz1IdCFhjVeuRtdGSCt1c7sAXWQOt65Z5CCl1JI1JxwBWsstV5ayt1EvxoNy+uq5sAq6j9orvr2rVkTVhtWDan+WvaiMrCLWv99el6791mXqX4mL2unoKZa6e1OcwKvX8KrXhan68zSBdq/bWvus5Pjj69r1utTr3XmutFtZyaDAWD5

rxoDEaEL9cpa3RoTJojvVLeoc+dj6+11s9p8ObDmATddm6j6gTci2vVN+oIJg8CFlihlENWK6cgb9RMNKNZpwjmkC9+rSIs4kWPcnfrh/XJP1SQTlA37lhUihDEIRmwAKLeGag6oBjQApMgWqjNQc6GR4BSADGgBpAGV8LB1X9r/3Iw+thqfQap7sX+z6qmtuPdLBFEyzlPtrDbXh2ttteMXG9sFCARsR1OqPIAg6zuBboSf/lk+tQddTy0O5zpi

01Y8ADEYcFytLWLbIAYCkHkwLv+A/Aiv4LiskxhMILpYy0CB5CzLY76mqzuely551ovruDmeOrGWrL6tD18vqf5l+erg2GJ65T1m+YXEBQ2gPGf30C9MB7rVfX2OqyqSl60hgaXrlfXna1IYGr62+5OXqLEg+eEItRrLAq17jrZJTQLRigZpvKvuWZrxNo0Wtt9RkSJr12N8rfVQwi89fJa+2JkgQIZxGunQGEqJNx40gbwrUj5Eg9Y7Uc71TNhO

qYGent9WhrBL1yrqDkkBevzdWksQt1ftoPjld8ohUALvIP1A1q30qmurq9be66v1VnpIvXcuqHShUwb2o4hAEqIg2uA9fDal4gIGyBL4turLdddao11d1r/C7fwGqGRCoV4x7gKv+ni2qrtZ4aavY8E14LDAfSqVY3a9m1sQaNXJ6Th4QRVAL/6f/is/UJ2uNtemIHe+r/q2YCFWVDtfHa121j/qxSAv+tqdcUGo8gY6qqGUyiMX9Tr4ekA20gZw

CSAD7ANDwPHgTZIdPKQRNOhnAALZ2EPrcnXQKN5EMPM6g2Mdy3xAI+pDiEj6jquhmCzTxEBsOdY04571gbrXvUf+qVcRRE7/1PTrn1XB3L/9QFigANs1seADpsKYiQ34z14XdJgtBVlFZ5T/0C2+OCANTVBmMKJYgGop1gkTTv5myrfscdC6X1KLrVLoxesjNc1a1S6VAbmA0VQDc9SL6mF1kvrDyge+BJdcXsNg5AjqXnVAhpOMAb6ti1/wbLTW

Aht8bN86jt1PBA4Q2COoT4FTatN1QXrsWEazAl9Xv9NG19kRflyaurUdQE67s1x39YcQFev3NQQGyv19XrHA2zTKpDVTPPP1Xfq//HKOtJDTOU7d1nsjHzVsSqGtSSGpIWZIbUGi1+pu9YuK4Cpsn1kXVorwW9UsGk71IXqRQ2PurFDYd6gS1goa3vUPCqkRfP6mVFxMrrLBLUHKgMZgfHkBwBMAC5OCswGtQQagbAAXgADABmoOZgO3wAUzny4w

4yiNEFxbSE6VB+QSBaF3SRWgUfgloihzUAho89Q6E1p1yMNdVX3quxFaT6jYN5Pq0HWU+pSJVpCrfhtPqDR5FMA3teamW1VMHRsFhs+tUoDYy/tVYmjB1U4hsF9eiGg4V6AaEQ0eDne9RRCnIVEgBgiIzgBqVOVEZB0M1BjIDzTAaAJVuG9yi7h3WEN1jOOlfzfFQu6qVXhO6Fi0k1DU9u/qtffVR+ryqqPwgCWAlZPsGHTyG0pLKnTG0srOnV3n

IfeVWqzYNNartg2+cvrVarKhc5QXLZ3EQQ20Nb3wxF2TPrDaCt4FiNXGGvSe6dzEw07uOeDZWLXEN2HK4FnCeoU9VfMo8N8vq33XShvE9c0aVT1vDBzw3pTBlDZ+65/0cwa3g35movDcQGzXeGnrIS7OIBV9fQGp+pHhS6A3X4AYDb/4EENnHq8vWNXPudf2/MBJc7quA1MetItb4WHX1UNrHnXyPRt9RKgMCNYGoEI2QRpKsDCGul1O2pzPWFWr

UakiGwF1AYMvCS4RsXdf0wrD13nq8UQ4RugjQu65j1cLrArVOWvm9cRG6iNFnrc3WreoLdet6j3IJEbaI3ue3kDXt68GBzx8uI1FWo5dVB6hisD2pjfXEWrwjf//Bl1/ZrBbK1rngjQ86jCN+wR5rVyuuQzOIdE5Y4EbsLVn+Bv/j66jsNe0Y/w3fhoAjU/U511ukaGYWPhg+DRBawz1STBlI1++s7DXYc14NQZq1PrthpZtXpGo51bob+fX+e2c

DaRMoqi6gbGXWyRuF9fCGjz15LrcsB8Rs6aP5GtENYvrPGBGBr5dSYG9b1MZrtloayBh/uW6+iNXlrGI2IutjNWF6xKN71gVA2NuoBtQZGk6V6rKCI2QOqIjRDajqKuXqtEhPPXEDVSUMXRxXq4BEq0HYQDBgLCNDqBbPXCBqRte2GFKwyEb5AE7LCo9Zr60ncDHqTfWSRuZdclqXr17LqddzARrKjT1Wan+5EaZA35NR+DYZGq5175RdA21Lw/D

TeiNiNJgbsQ3nBnMjWY69Mmgfrgo08rH29SjnMC1x6Uto2C7gZdQ96rQNAfqAWBPhtlDb+iJyNrrraPUierHNcEGpL1cnrcA1seuMtS2TOP1RIaWPWnhrejeSGm9YFgbBtj3RuPDSn6soND/rD/6uhoCjXQ6+zx9gaLXVRBAhjeFGnSCg/rcfWdbMWERmG90N/Xqd3WV5UK9cTofcNC3r3A1ufN1UsI61MNUIboxYRutgtU1xXGNitrh3UBBt7df

JKSmNRwchSxXGGWlgzGNGNUMbWLwGuKQLOCWSCodMbiY2+NmGQDraueZ3yUWY30xouRMRkUZ4iQalHFExrcjUL63f+XuYRNAoEClFteGnZmDqw6AYhsC62WQ9Q6NsXqcXVxoEPnpT/LOaZzq8o1Hup1jQOKDQB+sagI1sBtJdU2FDcGJsaTayw2SgjYx6miNsEbiGmqxpN6SZQHEu4kbuA0nMrttS7G5sJa9S6g3y3JzDTm4nXwvQAlqDOAGl9l/

kPCMfQAXgCEAB4xik4TUompQcnXKYJFiisa7+AOxrSKHprTOmEw4UI1QkQfVl+EsaZDqHUjVpvsrbDHcAe4CsGv25cAr8pn1HEWgX06wMNyRKVs7Wu0LpozysOAvXZ0nZ0wwjPD3iMOe+RK5nW3BrOgWjVY8GKAa0uUPZyrFgiQlISqoZgYI4Rw1AjhHGoMf0itLoxWjTMTMxDN2fygtI3TiQdAoRHH/wC4l4fIZikHbpeJPoCcYpsS7EsNgzoxH

W7WD0q5A1ZgROciUMCQuJlNQJL0i3xTq3qGikCXcRjKzGT8whoeGj5zaMBfy8CFUlqyECzmnjAWk6Z1BETMJZH+NOx0/41e1X0BORJX4a7A91GRUYtTwL4bBJMag8fnhHGV/jQIwBWI71d2RiIJtkYGznLOC6Yt9gg4SQeVuTBE4OnjAn41xS28HsPLcz63DsSwrv91BriqwXiOJDscpY8myGYHjncPCtCboa70JpRtqs5AeMuedEi5s9Skgt1ZG

/uQRgLxVfNymQqPnHrgA1EP3Sz5zZugqrC1UfedSOFqLDETaGLWRNXRVbg75FX/YrwmwmwoOF2IKxD0GMFEULC8HLBtrruQQelYQrBBO8Pdc574skvIuqGD/uvLVCdy7a3/7iQmleuhvoec4A1yU+SK0eXFHyQobCjXBAmpS5YnCjxhLGDwJuJwqQmKBNK492x7hR1PrrJHYQ6W49eiYylyPlHqJRZF1CFcOQ0fI21Np0GHOtiao5Di1U54s3bcn

ccUxL41PYKKknybdiWD0r4sx7xvxLocGLJNpianCglpFC3iL3QaWR49zxDU+ySljT0OhwiUthIKVB0ICDFLesSXEtF9YlJqM6A93UvKSSanfQQBEPNqIeST88E8Rx5uR2sTBrIF3oxg9OuX/e3/jZyjS+CopddHzWF0YqEH3ed6m9tPnT+JvjHjWnDxV/DMENbsmAwTTPMVbleElQB7e8VUZpn3d5W1ia4LH+/K2Ng1wVSulOg+RoNG3kTakzafu

MGLF6oYpCMNhQSYuNORhpqXHa2yMO1LOglTflAy5RG1q8CXG35NW3Jlh6n93psA9wf2NOjds3FFSJ18I3w4YW5vhRIDVAGUAHZgWX2d1Rv0DEL2PsVxC5ByikBWlQwEAIQK0wXcGhjA2ayDFHLsiz2A6M4+NSlEzy3nLliOT0NhkMnEU+htFNWIvcmo1cbd7EU+rrjYw3PYNjCiww3zbK6IOYnD0EB/CrYT2wF0bCQ694WmwrTn4DqoT9vzxLQp1

YlFG5lSyk8is0YcusKdw1Bu2kHHhC3RqOGLQL40nt0kLtu3M8SZ49O+4sRgSTd3UL0uTARyJ6g6KaTmGPYOW1vj77DLGXG9glhLkNOlkiZJykjTlng7bXiX9tl85vZUT+E4EbjIv9d6fyFpw4kl0zagCSYtR5g57mbloQBPBNsrNQe6PXkZNv5LW5m5RQm05GJpgxdEhZU+rybkrIFi2ilg6NKVO1BkRkxnJoijbglaI2yaFTzaCoUHfKdZDuq+7

4KEpHRk7fEwmm0u7QgjZ7LeApTdaXWeWQwhBY49EIJlafy54VJW5ZMB/CsGoOjwRcOIuh25DOHCgADwATcARgADaK2CikxoKE8SK0Kj3ICIRP8uMiIbwZENpQGJWhNuDi7c7AVxUsS86REq9DSMKsnlJPqxTXMppcwROGpROPoS/UV08t8RahLDWVN1VMVBU4pyqKNQ8WoQ4xuWo8RO7jQgG3uNoqaUsXmyq+ZKL6f0Y28a4YIcEmhLiM4cpNo0t

Gk1g7RB8mkmsIsbO0L9bxPTvbsOEGPcEiNBA35ez3RLc3WEwPqQK3nc4Q3gjQ8ybWxqaDJLO9G/SBMmrZN87ornKDqhHlRT8HBNBGtYhqu/XdTX5ke8SZll31GYJ3SMsujSzIXmRGEF5FWQxsxnC5NEKYdAlSVzWrjUuZoexcpQg1pps0ML6hO1O6YgaxapSxGzicQBIudqFRM1YkHEzTLcihlctyoU3ShNzDegAJ8AIoleXjbABScAiAGcAsmBj

QBsAEwAFZgaHg6/yafWDBsiWWlqBus+EMw7GuykQiXPIOE+dCB7ihGiJUVpOGYbOiiay42xEtllZXG+DwS181IVspufOZpC185Awa56ZHBt5qGGXWRSOVQoA3caN8eHQ864NXfie41MipfTYMI+OOTwbkw2KXQc6M2kJRNFTsKoQOerXjQq3ONuoHcueIwmAfjcPRCUuIcsleJ9K1IOqEm7OOYJcHU1TPghxM/XGt0Zu5kB7eS0XLvlHGlQIUtGU

iNZqR3Nmmp2QNiax27JJqn7ibnAKuliai84TaEW0H7Et2ijecDwo9Jtj0hMeVlWuRZ7k14yr5MV74lUNSmKTy48Y03AGLoBrut3o4AC5OB08tgAO/ls4D4gD0gHNVZD6vJ1yi8dEAIwB16iVAbTBTpQuYDJahWgDVgOg8lnL4PJweWczTLKrp1larroiUKIPTRq4utV76r/OVd6P8zZVMqAgQFxDi4v4QaFL7LCcRLZlHVXFH2dVSQK2LNW4aVnU

UCu59dnc4eNFN4wAjZhuoZbKijfmNfR4gDigzaFmLoO1WbAAP8r0gE9bmhAIEVR2ahg0GGTsfrOgUKq1yDM43gzkhWPrgBFswDBi9FymjO3h3iE5OA4afbkdOvIiRWqyiJ7maZv6eZtrjd5mqn1WkKPDHcposvvmQQ2Of6rXxQSpnbjYk0YpoX6FIc17IKKJbDm5Z1DxcEs2Spvlbod5FUcy8b8WIhXRcpE86ofYOuaqxI+Oyl6bRLS3cZdt/JwY

qCNzQBuBBm6cMrc0keoGzQVRa3NoJN0dSBjmdzQ/SdguZubKS7hJpvcdGiPKehu1YZEB5q5fO7mrZ6x5EQW6AtzKeqPKJiW9SbI805WnSzQOTIJ6zQFNtIJ5sT/Ff+RBwQZNRHqrGg6bsWoLT2KCEiRZFqFKhXN7G6kTtk926gMCNug5mvVNG9Ul9ZMGnpFqXbBHcxUwhm6x5Hquj1dCdEjeaBZFvckspPnOb1IU4hUY2WVTklloeE7o3SsEBKmi

wslGpLNkl10EBW4L+1m1q5XDoK5ppCM1q9ymbgb+F36845s/Yk0TCukPYEyWthcDtpN3VdTlVmxVNQUckrpbkWozsMmnOMqjIMW7k71XjRQPKzIOBD1yLnpgDTWu3Pp6uA9Z6KbJpv1sC3cnalyQIxbzV0jTSn+LkUFzMf83VxxTxmxM+FuehkveINJlrjjKkYXOgRdycJv5urFpkCHNN+tY3ybJS21iDDY4AtcPdHk3QFt/zQ2m6lNtaa3LTPj0

GzRwmjnZy5Ec86leDzzm2PcdWihsJjDrponLtJm+quuTke4KUFraKG9cxfNOmcVM4DN0hVlqhMA2ulcWC0SDVNFj2bAI2dic6zxjZqHFgomoRNax9rvZzqzMzllIXvN/7Eps2Qpog7gpmoONUPBfAAtABq7kIACpU9LwrMCbAHU8uqAe5cdmAHFCk5qMzcnG6dAmEgYazMlnQ0IhEo/568yAEiasG/OV60MUemcQLTx4y2ezcOG+95iB4sEj85qH

9ILm8vWgzr33kGFv+zboyyum2jBg0F7dxvTcxaHA43SkRU1HjLizXDvBHNVDrQ4pZsWSzVYeGN2xaQ/005pMWokPrDzuKCtfE77e1LzbxLGfNpqbZ9bL4xt9JamnpWaY9+GoWES/sPPmllkjaJ99YLJvwyEkm3AlVGamnRUkzJzvxOGI5lrBTYI7B2YoTHnFxNnKRre6Dj0h7n1dUXpf1sZq78ZsgZtuPJAt9RRcDXxPTQLX1mjAtyaIgLZQMQel

Qf1Qeq4Q9GC1Ax3KlnEPLRNzKdIDaiFv+ut11Xt2JPt803u2HpVFv1LIeQKabukHFtxKD1LA2wB/ZC80LpCb9ocW+A2gKaPk1H3EeLTXGZ5Npxani09WS2LVVLee2+XV8C0kFs4Td27WrqAQ8fc5fFqd2XAWzrN5yaH81IckALf/muv2yCaUB6CpCXHiMm1otcCaOi1rjzEHu3LDiEIqMOISFZqtTaXHbyO3eaD1B7OmYRrVlXItLYRS4Y75prGA

2iouOLRaPR6HuiVtlUmpIt2+bO7oZC1qyuYkAJIO+1iU7eRwBbrU3cYtPuaJ24LoDnHn2rDniy49hcoj12NMA6AlYtZOoNx71/HeLUuuDdoxIst26zJo/HpndCQu9criGajay79ogjWsSL7civZPtygzc3nGwZb7c281sM0pzk83QDuxiFl4rhOQQzUPUJ/BY/5aGwFFpHCcTXfdW4480miFetWpnfFJHKE9RPS3pp0onrboFLuOeR/S1yFu8EdJ

yxQt8eJvIBQAHR4PoAA4A4F1hIZwAE3AH0AYxu0gBJAB7ADPTVim/9yjUCAL4KIDJQHTDM7ilpMJ1CQdO34PNqqp1bA9QK6HRnlsOLYb3wpaqmqHc5orjd06vnNLKaaIkReSDDfXG1IlmKaLVXLP1GnHJhGuuoZkIzw4rQM+LFyzU1TqqeeWC4z7jWKml+xSYaNc2itzqdqkxNtuOEc681i92pLtL3A8Npd4de6LxvpUPI9Sx6k/lPm4wFujzcG4

Xr2DKox9YnNBPjcj1NpNHud17YXtw4rhEGdLCvSQKNaZAVgzeknc9uPhZlrBjBlegOtYJ6ir5avX5YZsa6OPmi5uD5aHO5oO1oOt4xa8tVHC8A6cUx/LTWnEdKOfUaKZ59Q4zZ8kCiQfzc4bCgFrwugETdsesxabc7zNxYLpsWzRNfxbZroT1wczu1XPeBnBtsh5iFuKzT03Glutxb+par5vTHrsedPI1ZbvBlsF1VTWxEJititgnALQlDYrRZoB

WwFMEIwLvdQDLusQWludxaaNZtx2yTmRWoFNLpcsc7o9xSMNLfV3Ofthfi1eyKHHuh9XRN+yEhlU3GSJbhbWLQ2gKE35VaG0jTXL+beGf1cYE6/oxgnkZW3gU9Sc1k3A11dqjjnL2C/OpgJJsWSqLTIBI3OhUdPfQup0CurBPEKElQZj7AGVqqTgqREDu2dQNljXxvdiN6kzMudbFgu5Ulv47NNrdUuwflIq0qRzTzXSWlz8p9sCk26MAJLoIXcQ

2xxIyk1pFoQsjBmYVUKlpMq3xb1F6jLjfK0NcUV7hFVoXSAImvctvJb/o6VVuxwhqXQoSRwlEKg5+3mAq5I0MeNVb4U7zloyrakW+LeTjg6k1HlvllrO0GPNEnLlQ2EyoX9UKY3JwofMmAB7AGTxCwAWnkLQADgDo8H0wA0AaC6y4Mj/VfLlerBIpdFywUgEiKFlvHQMpQdHlwNllFZT4nHRsQGMa+vVbRnAc5uiJVzm8tVjZa3s3uFpbLd6iw9N

vqLaeXh3NjopqiilcAs9jX7w8UtTCW64jKkRaU4Cvpt3DZG7WIByRbW27He1jBcW7dZEBw4yi21NQ5LSo3NbkohUKx61tXA7H7mjYt/l0Q80JDXgrRfDL3Nrcccq38kOxreCfDDMh6pB/Zo1rcccanJ7aDVaz/ak5yE9iP5H/2Ezt3tomG1lzhNOQ8tpaQEJ6Hw01zqj0fKte8KoARwBxTcKelZmt/6bR/zONFW1uDUTjK/Nasq2al2+hDTlM6tA

taB/yWpSlrQNWvqtUTr6J4xOo+9UO8qHg0mBGQCEAHG3uUgqV0KThnzRyqC/yrAAfJw9+d6yp3UAY6RQuYGom4gClIo4CYMC/hA4h5Zdlk0PcXh7NltKXw+PqhhWucq3TXqqndNTKaq437pprjZOGgkVPhb/OW6uLFzY3419AMgzEXa+mNo8hDq1/pf1b+41bCq59XEWoJW7hRlGTGeCzzXpDW/xKdbDPAqMnqyp5VBSkBpE062XggfHhFaz0eBd

b+5wulsbBOerR+OpY9zGhXy1p7rea2H2Z6tr1Zs1yJgqihSLGHPdYC0SZ3HrvHyIa6NBb67ZtEm+TXNwNrNr0ciyDVDzExd14VqkPs4btb/yySoPvm34OXzMUTzUlvZLTZXbnupCtqEKqWwSrixW7yOQ3cJW7XeBzhfXHL+uiJhZe4veFNPgVmIIas1Is+5at06fD/rCV6qahc5Ie91QNpj4e+t5GttrBpJlT7kHJX3uNnNna2HvFdrUsmyS+kfd

zDk/1pZ8E1aB2t/9bde6ANs/cMA2sMtAhjuVUlbmYAB0GowA7LwDgCW+H2EDNQY605KY0qEZAD3+YYWl8uZyBbkB5vO0El5Gj/c/wgQNhqcDtRZaItrps6BygrR+C7DTa6aWSup46y02GIbLa5mpst72a1XEPVq+zVKaoOtqsrp3HJN2Sdv6QdfpayClJH88ojPI8LcC0kWaCiVPppizVEWuHNaubVnVJ1ocZQ5KfGt8YsEU5u5pI9cuWia64WNP

OgxR1WYk7mh3NZvctG3o1qNLcuPf3NAib/c31Y0bBF+mybqmNa5pKsSzArUBWhN6wOcrOgBMTrLjsaTUtVqIsc4i9HfEqA2wXC2WbORbjBySrY+nbJEKOKt1TNe2kSqfGwJte0Ij6jItxCbfJW4dOau4LmVxNontrOtMTkHns367AhFzdT42ljhDZhFB7Z/3Ijmu9UIINWb3S0apzjqqGm+8th7dHy08NDIaMD1RHO9Wbjmz3k0wLYReFBNV5NVq

aZ1Sweo/SbNOONFvo4J4wyPCVHIwaf+aqWI91tO0UGmtutxubNK4Fpx1nE8kJmqKAp765wxqfYtfXO4IOSIim2zRyMlgKKXJtjrLWq3pNvKICHuCrNu+bNxqwYj9qq2PXNeiY89JZhDXi3mXnFkkIfRuY0gZpqDhEmx9WPSaRJoNdCOsHs6P0tvIRCvW1ZQrrbw7MuGPIsXxjLEw+7okmtktI90gx6jVCbzYD5P7yU49jS2Ato35JCcTvuZecUoh

Qtt8+PC24JOYOckW2olszzaNXR0I9KdH80BJpXSJ33JBm+stwegDu0htmFWwO6fPQBtaE9SX5O4200ubpFwq1alrXgkdXcStlLatU10ttHjulWtxtzLbpVlJNoxbcGECPuELagojL+3/bq3mgUuLIsUy6/mX+bUammHaxMdDU05ZpF8m6nJYO+gUjaCXZWextinIZNeO0yU4pNBFFlPULeOVGdhRbiRBXNhb5emuPAIg5bI52liCdTPxmGp80IhD

5osziLtY1tkos3vxQ0yRzna275MiY16/KOtqtbU6+VvSHP03W0b1x92jIhUfiMXxXm2fhGuHvgsuL60e1eGZTuXNNsnlP4kpnBlJU342HyNK2/xt+Orda4S3RAGsC2hyIOPDbLb1I2fQcJLFSapt0oQ6tpmCrQs5W/aEUR2kqV5qbNvFEEtt6NKqRa4ttJcbLc1tNTwrYG1JQXR4C22fuQg1BznYCYAaADgATQAQwAaQD1ilmoLOGpONuDaG0Aj9

CCMfedTrujPBriDfvGubBKAy0RVxbnMW5YmHiI3EdaIRPK2nXyj0UZd7W3hhe6aPs3+1serTTywLFgAa6/FzhuYidxdNK4+4TDi6xx0H3j+PdCwcdapy2gfKiwYjmofxNEx5S2GyyIZvRBPxtb48ga2PKolFu6226OwfQdRYxNsorRJ7fb28+dJYhVKtojiW7aMWXkt6m10VvKLUQjcUatYta3bYQ1vCnsWmKubzop61y5ljLjbEPZ009bKSgvFF

FLW33A6EQltwEKWPR3rVd4cOIrbsoc6QEzQUpJzCJOh9bze6h9wD7uKFC/Ny7dGxjBcx0aj2XMR21PYtXS29gy8SsW0xqQ1jl20QlorUIu23pJgCSOy7B52E7UjeJdtYnboG3SIuPLgIJPTAxThpwCMvBScEEAHgAKhbjMDrAEPQm0AAYNg7arQ3zWBkIOBqJ52vixLM3EpoVIKSmr3w+4D+h4xyn0LvPY79OXtzN01E+u3TZBLXdNvtbt22spq8

LeC7bhtlsVqyT3inBRTCAVuNoRakcDblhmepzy/5O0WbEuUq5vd5tuG9XNFTdNc3lkTpLu7UN3G1SIbUSJdq8SIOQvOeqIpJ9YeJGhFudsQZtVu5BszclvxJslPNDtNIi0u15dtzzbP5eXIuXbco4jUXieqY2/UuZwCVXocp1fppKSa/WwmEbO4Ckj3Mv8yDLN5vVmsaP1vXHoUkHPNnXsUDbvgjLbRBCHguYrbCWjLL0wNiq2lCexEc63qtNiPP

GPm0W2k3bpk1yRzhboqW4yW6FRbK2UMlHdk8W9Fu3qaAnorFrP1ibhX0mg48m5bVNtJJkyxZptrJdh26IVtcTZEGDut9g84035B028v9XcNNPqrBi1xWSlLtHDSAt6aauC0RhQpMn9o9RwJzb7E2fdtoLWS3XBNUPdHE273Qe7X0Wlwa3cJv82V522jf++XxML+b2U4wFoUHtfmlG1mPbGm0Fjz3zQkndCmGY9qOiro2WrhUWkDICpbi8KfxvGTQ

BW7/WnZcIgI0fIs7sKnRDNPeaJU7cVwHEO3LZHqqLa1S0CVqOjpkm9ntA0dUfKC9p3HhBwXrtK+t1S0zAk5rSL2lktMywlq4WNq3jSO8drtDxbqe2lJq6rW8W1Xtowlxe2nezwjjiLK+GRPbiW355szUPcWlBmTqQee2N+017Skm9Ss/Kdoc4StoN7X17YQiNE9G447t3FFpa2n1tjWZB4YcWKebXakHGtMMJ/x6Rl1NFI5W+ltOpbjq7rdrKzUx

rHv2h6oLq6KQQ3zTt2uj+NDMY+3pZBsLrt21jsU8EMOFNj247HFW7Et1f5BW3f1yO7WxkWYOWzbD67jx1q6Oji7HtXmRce1A13FznDtffWZcsvgiV9r13LaWiRmV+aK+1aZG5rRfGbHaazace2OlpbRuZkOvtmmRkA71GRb7eXLBvtPotanz6ZFybaP2lmOHqb96759txrhgmH3GZcJ5+3cmhATbwBZ+G4/aVdw2Vro/msHDsey+bjRaD9onsQ7j

BGiqvl1W0YxzkjmjmhoNQpjceDmYDswLjwDoAEPKlqBvCr2ANUASQAa/zqgCxKNIAOZgQ7NODb9O2Wk12nAK40TtlmaH9ibg1pavYdSexuFgyQ72JV6FVZy9j0Y21GG0uhOurSw226tXBR7q0C5oDrSaqnzNswrGIl8NuYURwgQ0sUYjqbTEBlRqiEsJqeI5abg1SNsi7TI21XNQkT5G2JothrcbdLktMzRiu1MlpaLYwOmrtPJam4YCJv5LcePc

ltlPUR27xzlrLhwbReGYwlkdqi+SkdqBPKeuwggOY7n5WpFlKfMTOdCNqjZ7aymNoM3YVt6oQD06oJXtLVRgZSVPwdGnkelrebfnkKcapw9ZxqbiU+FBl4q5mMeV8M06STCRtKbKOm/SUrm1aXkf8tbZW7sYyU05Z3CMgHX/xO5K5osS+mODosStvkXzk7ASfB1PFQsOvs22Tti2avwlqhp4xhhGWvhJmtjMCmqx/yLjwYgAiF1QgDEAHkXmTm4z

N1tEYhpFAshnKJqy2E14FgoD2UHXVEGwyzlJEc1FZAKyp7qvTEI+0/DCfXkaOJ9S52n2tzZa/a0edvQHd9mjB1qsryplHtoCzUtITpo2mzVrZkOoaFNs2posN7aAa2JZrjlgixWN2/cNRh28MUyhNrLYkWw3bAWJTDoRAX02SYdnFIj06qtuTEgsOsJtqWDQmbmi03KuR6ZqmVSqnHDqxVOFc8eSYtQCQDzzXyzfNgQWxfiVFab4Izi02FkE60aO

T1tMa7/IV2RLs2thCmHb5pZFjyqrh8HOxCnVdsq7Fl1XxvtLetg3rUHihNRRnrQCsgTq9jJQR09Dw5bsR2ljtlPcxUDPS04rZ3gR6W5Q6lK3M9r5xGUOxEdnUdW/aS9oRHRiUaltYI7cO0AK3fIojbXaWbQ98bqkjsFtpdrUM26V4L+3QpsaDVDwekA2AAYAAQFGqAAgAegA+T8OAB+TPQFdMnfJwdoYTPI2yBdKEAtcXmmVT5XZcMGkeCJsmN0O

2twB1agxpulkRHBNb/ySeWe1oZTRu2+wxW7b2G1oDt3bf/6jRlqsrqlnYOo6IkpWJ4WIWbA/aUZUX9A+mrnl22zpG3/VuiLcmE2gdqWKIlZwlUZLcpLFLtkUJaS1DKrCxkb2zku8btKS0stvHMt23I40+MEuNSxJteHUCXC1NJraIcTAo3fprs2y5t/7bQ+h5x3zHiT2ljaMHaYa3/4S37f76TctERUaKgPNqrHsFHfpNYUc2VTsBIubXUW0yW3W

bubrWVs3zbt2+kdChaYU1Q8CaAIMnbAAIhiw/HIN2bBoehczALwBUGHCiUFHUX6BPA14BPNkVOMZ4IjpJOcmdZDKG3+redsq8WyokXcBkE16MHDVdWwpZrhbgvIoDsaHa2Wk2KAzrMB1oCtm2aHW/HI6M9AEgNLJwlmQeAO4m3ghh22jsF5bEWugdN0L9SLvt16qF2rScdqg6ou6OJ1vHStUe8dKktBsxXjtWqErWsiFAcb0c1qhr7APO4AAM3l9

oeA2KHncLf23JwmoABgAVKgqfpaGzWOYSB3hyXzB9xFqxV4QgWBH36whiVSqdML1oo24uLIG9B4XgwWtGozhbmG2vZt5zWw2r1FWo7OG1rjuFzStI3eA94p6HjQVnSdjLmvyGMOlgmFmMvIHYyKygdNo7ZG00DrPHQ6OtTEovdNG0xT3V7uuW+NcLbtA80feCd7gRy/xITA6Mu1bPXlevCLLvUDEsVXrSTqX9vG9CqUik7vy1ikiwNhewKUt3TQj

SolDqfbUN2k3txTbXG1HRwS9qzbLJtiw7JlqJau70h42nVOp3ti62Y52snTOPLQddzD7J2BtrzyETbQ+2traf23eMV4NkmPPseoTQlJ3x1EEstE2+MdXCbRu3QQnibdfUfVQ59asNYE9pCHRnmirGm9tz82kkxA7cX6vptI9b781O43rrXSheBogxBgxYd2uXYrM2lSu1nY2Gif5pnzZd2mRoHZEGx6yBAKnciOkNNV3beB299XfzcVOm+uDHYkM

xHqlKbXVOs/2/Br/iUnBA6nbTWrzuHed3I50B0lbfNrWvtHosmY4tdG/MgjXautGjTa60tNFIoiLWzAOlh1vglWNCQBAtOp1NZza1gk+NDqaFECRidAZpgmgpjzXzlYMmiiDnoFkbe2uoovLmrDpE2tUmj6Dsa9EU0bJodCp322QrNQbIU0OXN906cyErsAqaG8WO0+a8dUa71NF2nfU6GUs5955p1uQNC9pnUI0wWk7pGbt9smncfPN0eA+cKY5

zxw/xEV2ySdVfb7K2CTiMbSBW9h2pX5pe0jWn2aAc67qpuSbNtGR9s3+NPlS8tef4N3bcUyLIl0mu8tRLaHe262hzbSj21usnCMvOiTcgN2q2JZsiLnIoe1De1lqlinGDNxuthS5yNghzi8XBfWjNEcspfMUgzfy2/LtFubm8oCS26TciXJDtx7dD2hok0g1qTO44mPVFCdrVjojLbWOioAkgB9fC4AHD5qK7BV0JKZlUXmYHiADSAa4ikydkLrt

6HeHAtU5aWhKbZ0CUjMqeDAQGUd6ETjk7G7U96DjywGgked2hAY1XgHWRExAdBE71g0NDvc7SuO9zK7ZaOU3WuxMgH52/6UF0BaJ1BdoGOEOpJ/VfVB6RVamq71i6qqLt5DqJG5lEohTq6PBWtLNaYU7ddoaAnj7AoO6dbN2grMpdHUj3fntHLayMQhjohxASW4CFbBb+lYrdsjHberfRy1Lc5eJN/CD7eu0VquAfaO52m9wWbqVXaxm9g6Wq5dV

3WnQ79J9Mg1dR53JjoqnRPOwedcY7rm16dB2bpTCKMdOcVF52yBDrnaTApVq5nRGe2/NoGrlvO8NtO86gBo+dCLrdaW5mdTvxJOjm9qadKvO+KtD0rEa0zzsV7QKW0xyZ87R/aG5u0cbfOvedwg6gvacmCvnb03KudWJbSEZtB1hLZM9ORG/awZW3YMxhjnBPebtwwkQ+2wwiyRq6kGj5fGsV9olFp8rQI7F3OYXrae167yhnYY0NJKLc7Ajb4T0

0KbdKKwdgab2a6ZpwfVtPm1QuC+4BA6kLqMPBUPIYE2QISgR252HHuQjXlO0CcU3WD5vd7Zu+evGkCUcJ6eyx1sYOnR5MAHcAW0Dp1YRl5nBQdzLBXg5FOQVnceUApycvRfgENY3h6FwjQpysi6Oa3q9ukXWr0JRd62V0Z0xZ0UXcpqnTu68bkEqy9DUXTouqXtKi6FF0yLqMXe6O15MYvQeEbqLvZbYrO1Rd1i6jF1eNqTsVYu4noT5bHrziLps

XRcKWyd9i7XF37zrGQh70JPo/H5JxLKkownSbtGbl+Nt16429CllAEu7iy2QU0F3YZrp7d60APosS7Nh3+LuSXVhO2edSLdgp3taoT6GEu6p8+WQp53RLvSXabtRZ8Q1YV81DVp+5SNW1UNRWdmE6JOvKQcwAW+i2wBhIYDAFncE7ePJwxoAtQR6ds1jluA5aKNZMizmIRJakVnhOLAWAZRGVPhP/mjQge0JiBVT5AOIp1VSqOkU1ao74iU/+sSJ

V5m7wt6474m6rAConUQQAUKP7yM6I2QTBlMeO9idjwb7R1vpvTCe4Q9vQWYT7YmpCVzCeLgfMJv/Sz6bSlPXqQ88plJYhLUkCPKWnXjEILGA2cpy4CNhKxpGMMhVJ7YSjjlDNg90JbSgSd5lb+wlIAkRhpZqqRop0TxwlUsAuFUqBacJC7qW+zzhPkbouEzhAy4TrEB6areiRuE6u4JlB7Ix4RKwJvuEsrVR4Sxymj2Vuvq23c8JbPzoYnA6sfCf

/sZ8JrdhaVZQrrBYLeEl8J94TqtWhDqqXUtmgQSuAAhADw8Ex4FZgULamPA2J5kpnr6JUAY0AewAxdB2shM8iLzOrCHVcnPp20UclCFUznoOUBtaVYy3YQB0sUyZ6kyA2gErp4YEY/HFmeE7/Z0jhrcLSg65ZdnnaVE5rLs0ZTxAIM8s8kdzk0w16LhSReh419QJG2PppYnQs69OdA8bKBVksEIaTmEpSZ/Gr8yV24j44fpEiyZhhSVGnaRIDXSp

EvxoNbTfV3gYIhKY8ulcZmkzzBlLkW/GdJMpNdz4zVIo8TMiWt50pbpLgQaJn+DJqePFE/FQ+BhyV3oTLTXVBM/nC4S8songoxyCVmunkZ0t8/l0J1m5GWkMutdUtTs+ksjMQ/riMxPpZ2a213U2IR6a2gtjyq6j3Vw4dLyGe3+J4FYNxxNxWPMU6VJ0rbpYH5wV2ra0hXd2u/BF0KswcC9FwzmQuusRMp0Su8ybeA1RoZ0qddLfTmwF3RICaA9E

yTp5TS9116Z3eiZuEiaZa675gT/RIIiRJPJJpznT8mn0I0hiWkoDOJ+85Uhm+dPXtEjEjegNrBUYklrreqeEMxRG2MTvaDU1zEtbmukflxZdnATwf3JiWSIqUZrEzaYnZaCQHOYtXuAy1T9KlStPWqR0sfLALzwhrBRroTXYaMh/yFlYZK7CxOTgDOjFjJhkzn6WdblUqgxU6S4s4zjCnt5V76OrEoze/jkx9pGxN1ifKsfWJ8AUWN2PtjY3SWM3

MZ3Yy1WDWxNOiQQ4eJsnUBSxlpjIZ8G7Ev/uFek7kmSFN7KdDkv2JNmyJfoLpP+0AIMiAZfsTu9gBsyfFBRZFspHBSmBmRtICIMFYRvgRAIn5WxrvObTnEkzJKJ8IxwPLrEVZLPb3MylBR4lllOC+A3EgjpNLgHN0lsy7iefgHuJN8BXN3ooxruI8LLo5pzEi0nJpOniT25IvIc8SprkE/yzSUFu9qya8T7TXSRE6DrfEwBJ2B81FxjgBDeB7PW+

YgW6P4k4cxsuJfE9vQ18TEEnFpMb7BroHu0hBEX4k3xKTSZlux1K6FAdzjY9KukpFuirdUnNQBzYHPhPqs2DLdiW7FObdmLgSYQpenBrW7oEmdHXBWU7IJ356OVHSkFlNwSUEgDaacNRCEnolOiyXyUx0ZFCTKzCTIGoSbHEj4pteSGEkFOvJViwkrKyEgzxylILUOQStACUskGAuxlxjKvSjEHd1o5tjFCm8bqO3TejORJQG5c+ZMru1gGasW4a

pj0ymAcNJDXZaM+jKMuAHn4csCUadRk6NdXA4zEnwmAsSYpM3Dda4y5Bx2JLjiA4k9IcP27gd3KTJB1OMWOuw1VISqUprrNWgEk+saXAdGcp5tO1aa4k/D6R6qokkX9Oh3a4k1fY6OYhHLJJKh3WskvDdCjwMkmJwCySXkU0ndSrSQd2KEgKSSZNPfKB2gkd3/Gt72EOVLERtSSMd2OtL/4E0k1UIQbJDhHc7sTaZ0k0vEmeRzmF9JNp3fm0kmet

ukKhoekB/7GMkyXdmO6hXJR7HU6eK/JisrO6FHhEYAQaC7mGIGOG6yd307vngjSsG+ApjYdkka7uEEKtGc812EhTd3Brt/SUI0s6ulfoSB0Dbmk3Rzk17dVkyqyxixQnABdAN5JOgzXd1zjPmHL8ky76E3QKg0ZCwS2CAQTDoxZgcxlu5NDGU8cmFJESA4UmWkEj3XOU2sZ8+pBNXDjuC4Bj0xPJEeTJBkEwjxSQfau96iCjM93nFLk3YaKclJH8

IgV0MqX1sgQMz4przxPNLyfEuKCyk/AZnAyuUkBEB5STgcb8gtZSZSkU0hFSVnAMVJFMS0oQmbowyLKkuoZZUTrigD7sUoGqkreQ1jxLKJTbtKySKUuCsMZM64HwANI6N5us/4lqTLZqwXG/OCvup1JAaB2ECupOpAc0MQMpGZSP7C79LIwH6ky5AW+7g7AhpJfRJZwfN5F+7LDSxpK4DvGkjuF3nSkEni1uZODdsV8cIbTAYCZpIS3b1utOweaT

TzoFpPi3eVutrdOZhXNZRpVf3OtS91JCZSRt05mHrSdH/XWuRLZwCkUFPZKX3qdtJkpY9pBaBo73YiUmKsk6TOSZ7iMReVXulbdE6TnpiDpOnSRU8x9gSeScUllViCQEFInlYgSxZykLFJbGTaOJY1Z1TfiCCMGbGWWM4TsrB6YonsHovSdwQCuI/XxvfXiKJVxA+ktsgT6Sbd3SNNo3abhD9JBPLYlIlDNI3RQ09D8gGSZImFcBe3bbu0NdEGSz

ehPTnUZPa0/HdOuEEMl3ZvAhSlKjUwR/SvXDoZK5YTxWixOz/ozD1AAmeLIlSnmwvBq8d367ph3RuIJSGHU1KMniHR3GXhk+jJrSVexqxaJo3UZMin4WBw5N7cZNyhrifRQ9du6+axCZJ88CJk8U4QHZxMkhUEkyYy2/dJF27k93bSk0yVU0JTJaW1Uj1R7rzGcrWGQgWmTsj26ZKoPUIUkOsRmSRLj6QFMyUtuyfJxB7nMn1qRsyUgYOzJsswm9

31Hoq7LZk9zJCJSU0mu+Ag1P5klmAgWSuj1O1jCyfWQPpUo9lsD3dHviyXIgfsJjyxkskoHpm3drqDLJvqxD/hRnlmPRiU1A9IdYCsnAVl/oB4XKzdTtZKskcPD+IDVkhLcY+7J6wIFAugPaLWxk4x6Osk+eH3/ucmHrJ0B78ykqlM4EDKseq4W095Fx37sdJFNk9SIkhNr7QfHtAbMtkovIWW8FYF/HuanDtk4SgZ4D17oEtIWyUfusGcp2TpRi

dKWvlVCezbJz2TbsnA6z+IKfK14wh+7yymoNjzWK9k9ZgeDcrj0g5MgQI7gwhYygUaj015MeKRk0UHJJJ7++j9GtKPUIMv6ccOTOBpY5PjFfIMtI9zB7GT0ioGZPb4qWRRmjYM5oQ6oJyWeS1BsuaA9F4oQN7HT7ujQ9b26wJDU5IBESLbHDKkh6yN3WPm42Jt0VnJm1xAj3P0r6iHQuPN5uK69D0uHq1yaLky+0xr0UqXxtP0PV+EWXJl/9NV5y

QzN3St6VXJFGMz4Ea5MV3Tzut6U9cQTuDN1mZkM4eundrh6RwnG5NOoLbMg2VCp6lD1yCGtyb+clzyGvQlQI99A1bGkpDFAnM7JEl5Hr43f02L3JLjAkV34jU4PWJuwyC2s4Q8kviIMpdKgek9k3sVBKfxBPfn0GBPJSYhcz3SxFNuBqwa5slxQKBnLbspPVPOPPJctx73pb6W03YQM3Tdxc4PRkJsAhUgH4Zs91e7NBAN5Is8tc2Ugy3Z66j2d5

Oy+jbk9sQuJQiD21nqXnMPkiQgo+T75roDJrPYCUqecs+T056zZI62ISeo+cnixl6U1aTEhcgetY98x74QQBatH3KnzAFAG57F5Sn5Ig6cbgqjBux6b8k7bDvyQmwMLAZ56eWwv5K5eX1ZD/JJx7ZFw/5I7aT0Qf/JH56gCndznfZeLU9oKN56oCkLXGy7O33Fp0gx6kCkTnXxrBHWZ6aIF60lxuXG0hBTEMCIS7KoL1zdGIKUX3bl+P1Anz1LGk

FmTQUky4dBS/z2MFLt0o7UCUa8Jihz1TnqWNNwUzNAReQtJoqbuz3Wt0WQptJ7xCnpGtLPfYIZi9sB1WL3nbrjPZdupY0qhT/vBm4F+LH++JUCrHw8xz22SG9eqe99OphSSSwygNzabYeiIENhScNjasHm4dae3MQ5+wuYH3bEwEPvOESZaG6mFTjXxDCYEUvKAGa7fClSRE3hGFgQ7iJl7KJBJFIRvqxVHbRp9zrGl6XvFfNkUuI92STbBmOXu7

acywIZ4Dmqv/p2fSqqVv00SZpOZainoaHqKb7WKy9mcp2ildcU6KYf037dmco+in7djOBnU/MrVIxSn/ATMF3OGeEzWeycBSMDFlsO3eke3PyyxTp8hO2DWKaJu778WxSphk3sM3iiJu9k9XB7c/JHFKV+CcUuYpMm7SV3J5NCENcUmRWD7gbpqUXqXPVHKZ4pTvyoIpb4HeKbUeqi9UJTgSm/FLBKV1ezAZMCVRr1FXr+KeCUuY9c+6oSnvNg0C

LeAa6Al+TiL3s9GRKXpEj8tv575r11lIJ6NiUx5wbHxGDW4XvZ6MSUn1gl7gySl7num3QtesRdVJS19iv5glIaPu3a9ne6BWCBYBUoN/EHSexx7nr04HuOpZyU7tA3JTLN3oXoh6AKU1ldQpSrr2z7r2vQKwRSq4pS9ITZyngKfuem69uCU5SkMozgES42EE9UN61SmAwA1KSgqg/dMB6nj2ZCF1KbDsQOYCQxht343rd6KaUw64PhK9mpInsTKd

aU7+AtS4PgxRXG5oTTe2A923AuICulJiDs3AdG9WyEfSl63FUKOgMbm9q+QTQmiIBKaOq0/rumJ68b3GlLK7NGUmgSqOwHqCC3uVkMmUu1sH05s6mjZMePVLe1iIWZTPZoS/2u4mre+1JGt7zLhFlL8CNQgUspDx79b1elNYiJpWc4greJHUJPXoRvZDe29gGCLGynexFimeSexAZEgS8jKdlPZrNVSnM9We7tt3i5knKXCUEcpTV7BBn9lNu0dB

uAkowd62T28XryvQ/5NcpiPKNyligKhrfHemTSi/ok72P9MsmX7uprse5SSiC+liPKYK0rlp7r5UYC7Sm9sNeUjepb5S4N3uvh0QE+U2n6nGVYN1uDMyzl+UkT6Xng5en4TJvtMBU43dbdkwKlkTOq6dBU2E8n/kgZpD9NLXc/QmEoaFSdrAYVJ7vSKM9+0eFTt+Dr8GVcME0/9dL4zpuwUVNrPlRUtu9TipR7HdLGldh/gde9bFSLDV2qrdaLMM

4UZMXSxuwCVJs3G3gEVKk96T73TdgkqdayufoDhBd70DdkUqdrPHSpWCNnGk31I0qc/e7Sp5hAsFS6Xs8vRHtdAoG+RwIVOQBlSn/ek8ZvuVrKnT5FsqfblDUZZ5Tz9gwAtcqWlmMNcsD7aYk+VPagH5Uyrl7l6Ar1OXtcRiFU8XEYVS0fDhXstzDFUngsCQK4iJEPpSqcWqj9RGVTqEpgPt4mavkNicteYElBg90nzHQ+uB9ZVSUTopDnjrlg+1

Dd/96H/L1VMrrDY6oUcP9TeH3gPq25O1U+AwnVTsPgCtJQfZEqAapp/YdwZNQAofao/Cap5ByNZZgSr8iR5esR9D/lcrhLVPZrLMwFDdgVTtH23sA2qcxclkpKl7lH3EimRarOYG9JKW6zyzv3ulGRolS6pcLxrqlMTKvGSxMhu9D1TBrJPVIVpn+Uorpvd7dEqPVMnQM9U0RsNa6m10PjW42MDU3FqdexG10frt0StDU+VGB0gTBladOHXef5FG

pBug54Do1ML6Ud02vpxIo384YnInQITU6vpdIyyamCIApqd1YMEGpIzs+kPjUZqZlUQUKwe65A31ruBTfhu7mpCPyC1gzssz6S2u8YZp3YRakwYPFqVGdM2p7Qybuk3gH/2MAMrPYo47On3PdO6fWrUqPYGtSKOHJCyxuU0+4Z9LGxlpDXwEorKbUq7pZIzJ8hW1PPoDbUiB4RNyln2T5GdqfaQV2p0BKubZLNLOabk+viIrpNsp76EEAxoHUj2p

OT7vB2cIn+HH3NfPgRT7Hn1lDK4NKtGDyapjQfajJ1OKfTs0kvpZKARbDmxMkESClFJ9rIyyxCF1N6moVNYM8V662DCV1JG2MikGupgphIX3ljybqRnQF7RQpBYn2hdKgCnkvR3utuA+6l/rsJaQBukAKyuxOvB4bDHqY/exup09SMsRB0jxypTEjx9SoyikbL1K3wKvUvyqYG6MBpooB2WISoFAqgkzF+kV3s8fZPlM+pQLYF1yDWvXLNeM7l99

9Tz6nYfFHnJY+hlwADTYjlVYAW1po+7B9fD6nORKvvqgt/UtS9RaowGkB7KuBs5EoXdWkzkGkwNJDnHTMENsur7DryI6VbsGg09MgGDTM73SHvfqTg0hpATuAHX2+7qdfaxQYhpmkT5CA+ECkvU5EahpKG8O+qSNMiPZoe5pGD8RWGmaLBPHAGeqI9zSN39g382GbP/Sf19zSNRGlzNxnCXQOZN9/G6VZxMlk+NQwFTN9HOr1GkGNNUmC9i419ia

728yFvvkKKzIC+GbD69QgzeBrwEDOGuAwcCYYVaPvofZgFdxpg08MFr+GRRbFK+vUITug+yw+5gmgF2+r8Zw97fLL+NKFwYogIJpNL6UkrhNJaXtpoSxKx96yX0ZmwA2Ac8BJpFdlcX099Ih7DvfFSKyETXfL5EgfXfEMlJKhTThUpEpFKaXU03ddqT7WKDn7CoyvXagN1mnSwWnGdK6ac00v+A8oM2mlnvpPXRe+pzk3TTYqqJCLvfUOuqF9l77

hmk3UrGaQ4lQF9lz7gX1YHEZ9DuFa+JmyVQP33NPA/Ws0mGMQIhNmm3NKefVwaH0qBzTNnIs8GyfV8+2KIlzTs4DXNLbqbSMoF9XBpM9Gv9gI/cGWv99nzS7gDfNIeMqfFdF9ELTAWnvZAiKCOCkJG977p100tMY/dC0ukBsLT933pDMmQJXcctQQ1kpLjrvuW6awFbFpUGhcWkaflCGYveqbpNLSSWm+1DJaU7vHt9sUQ2rh0tNt/v1yeu9LL7h

AostLsCGy0nLFPD6jH2tvtnYPNcA8a2EBev52b33dS2+4Vp3jwfIhitKtAYY+sapVPYZWn8EDlaQdvP1pep6rWmqtOLLbBgoXK3h6rWl6tIYWURWXgufn7HJomtOCXAaWe06IX6xzbFMmiynhseVYup7PT26NOdacFs8SarEIrX11xC9ael5eXMCaSTT0efsDaW14WzMOD8w2mlvvJ3QIYKNpiUTAV6NipsPbFeoZKybTeZkZFNRPgpepnsmbS4l

KNCF+uUDuvL95rMi2nPVM5pfU3Er9Bu7JAoVtLCQFW05x2jp7hd1sGACHPCks7JDW8PT1S7vIqDEOdUqcSwfoC/3oLvdv0tVgsk8+2kIvAHHAq+qA6o7T01UQqA4NUy+oV9Wn7nQgDNhbYPO0kBc5d61KmV3qTYKu0pCICuA+ClbtP8fVPeiG43mwD2nh6vRUVO+4MY9XUK8kX2EvaSJ+x9d33772mHiDx3uVE7vpon6IbiTkEAQc+fB3poy56P2

y9kz2BrAQDpIUBS6lGdPY/ar2PcgEHSOnAhsARfQmzeDpt/TaOH9cnh/fXE9DpRP8slzOlrY/aeuiUwNrZG4mEdK6iZR+0jpFlZA/AqQAu4C06wddaP6qf3ZsHZsDjYVFAr08JpzE/tsCqx0lSywphj10dNL+Rrx02ZyqhRUSa4/uDGKJ0lcsNBA3jlvvrF/Xc5HXEcnTFAorbL2bgz+gFKqnSe8DjfBzVjL+kEwQSgWZAAcEPeaL+/5pKv7TOn2

yGNqcqOd9deL7wUp2dNbIC1pfJstv6N32uBTc6TlZcJQJ7gAf0HvuDGP50iLpQS4oul7vvB/YD+kEwfv7NiiIIhAfgu+pe9vv7uNhfdU7btYe4d9Mn6y10SmDAOETkBvgCcAd7lR/tk/Sn+vLp6NwLoCFdIwmbF0pc1xGhcca8EC66SO+kIK75BkSDJIHcEE9+wv98BZlog52AP2IMUr79of6+ulTQFbwIN0q+9i76JTAzdLG6SMtBbp3f7o/0iH

VG6ev3Af9L9Ywn1xPqJRqt0u9CTDgNulK/vN/WgWOyAV0x9FkhapQ/Th+klKp3TP3BAbg6OesjQ59aBY7unLiwe6ecjTZ91T6SUrYbHtIBmdAyc3wyrhlwjIB6e8OIHp3sQ174drqOGX8M7NgNNkVdgCTOi8GclH3pLvTcellEnmuD8vRxYnkAM939yl//Uj0lbhENw+yTlrGarN9ZYbkk0TLelk9N7whqQTxYVPTykA09LaOmr0kXpPPSLKzzUu

CYBbAP1KQvT6enZzNF6bz09Bg/PTkNh69OF6SQB+XpIGyJekrlil6X2EznpBvTWgVqHSMqA5Q5XpgvSsAM0Ac16QaQbXp6WqN07NJwNPMwB7ADRvSCdU4OWK4LUhbMgCAGZhxIAbamM4Of0MbpxqSyO9I7CYj0nHpkAHqCzu9PQ0J70iVp8PTaf6+9Nd6an2FWAXGTg+mkyhf/a8Mpgs2lQtDUF/UwOj8M/EZnBZBNVof3T6Ywqycg+/6JUpblgN

uPn0i185z7tmlgfqZJPX0/G4ZQ0W4E+AaL6WnUzgsnmlAgPCxP3nAL+8TQ9XUTJp17sZQBwjELprv66+l99JjucANXRgrf79xij9K8gOP0lAyV36XGnuDK7gPzAWlhW/LBX3XfuFfYMFVfp8fF1+kvahrfcX2XfpCwjykg6uHS/XMgG/pp/TrknhYrG/Sa+kQ07QG84n39OeBaG+qU9uqUX+n5TQIiqsoD/phSBf0keGrsUjxepPdHJ6RDTVOuAG

YZWOl5lB6/b3F7tWCtAMvbRABrG92LnsmvcgMyYRqAze4gLnqGvd1e6gZQ89xuorQBEgBNeqgZOqMSBkGzNDWGiQG4DrZ7iQo0DJVUoKCeZ5LR69gO3AeYGcnze7SYnQ9GDPAa4GeHmcbcWEh+Bkh3tU3dM+FbwAR9Z8gBqUhyesBlq9ffZpBkuKQS6pFhVM9Gz4R2y2b1UGUz6D/pyWIS/RzN20Gfm++6y1exDBmemBTIK0BoImlgzgmw94FNLZ

v00R9Rn72FKODMErO4OUtcmn7aJmAlHP2OQOOAZp0S7yzKfrDmoEMo6AwQyFM5Te3r/RyByIZUGTEcoxDMn/Xb+91GiQz4wpnIBSGdKBlIDzwVMhmpnH4OOROGIDhnMt4B5hCKGZdMbD9JT77CwyrCqGbhs7FGgz7+hn2FlJ2AkwA46k2olaldPotqfGlLoZaMhPOkBozNA1s+9wsDtFvCwBnL81ZM+4fd5Iy10ZTDLDvgxAEfI5gG7/1z9lh6i9

cSN+DEDnhm3/vsA+JoL8qg+09hmrNUuGYcMiwD7hZThkRMFhpZ85GVAKYHQwPxoxFPQOlXcqVWAYRmdrrf/cSFd4ZAyi51BfDOLA6/+t4ZuSlNSLyQGBGc48nMDsYH/CwQjKVVdQGYMD2YHURlbDNX7AiMkkpQWtqwOpgYJGVpPNshuXBC0ohgZbA56EKzNmIziRmAoCqfdM+7uay0RXv5MjMrSRM03wDcH6mSQMjOXAxN0VcDmv6Of0fvqrSuyM

tDAnIzFAld9J86TKB8TQLGwSSkvAz7HVkB3EKYoz4yCCjPKA4UB3BJsoynyjyjKvqQ4+m79O/YVRlmzR1ATt+rUZrFMlj2IEGXkBSB5gIxoyMvDy5ADZkSBz0ItukluiHrsspjBBtIs/M980Cm4nNHS1lVaMqZsvRk/pVyvQsBjTgAYybIhBjKBQLhBmq9mXNh8l1wHJkKZGxg9voz8xkJjJQYDMa9oK1EHo93JcwzGe7oI5mjV7o73zAdIg7SFV

fY/s0OfgWwB43THevCDo6UKxkWbHqVtWMkq93sBNxAmVMbGUL8dEDUkG2xloKsdqJ2Mqq9QkHuIMbjFNdX2M28qQ76MhbyWHr6uCOStAyY1ZwyTjINhRj/T8ZMIIn+mihQXGb1Ua1lIKUov1WGAd/ryweDUndwwINlQDcuAeMim0bE66QOGfsiWqsQczyoxTLAhcvqtuGiAW3s537Hxl3gcAHG+MlSAH4y0zBZ/uT/flMDWlxIzr7RC5ifGUn+gi

ZBeQ7wK6h1DKRFBjcYO3ZYJlt7HgmXFB9KDyEzS5yoTPEOkVBvmy+WxHgDqpJrIBr+xP9pL7h/3GTMomQ4QEiZUVZnv3X3t1Cs1Bt/quC1bmx8gdxcsZ/L0SNAk3H1sgbzXbqFHSAa0Qr+Z5hA2lPUB40K4kyF1xCTJqxrI+2aD1eAJJmDuvP9fGuzr9uLlZJmpO3ZpFeOeyDdEzVJmarr0mRpMzaDB0GNV0fAeOg0hB4yZh0GLoNU5ov7JZBj8d

lDKvx2X9tlRVV/SQATmBJk539pUovgAMEAUPK+MYqC0C5V0umLE1sJW0GQPMrmXbOhQD8oMHGA/jzMRVzwGbwCMMPEmKQBaIudvPCGvBALHnBcH55b7OocN+E6jV2Ljor8E+8pod2o6dg26jstih8AeLywZhcML97wHLX5DT9lxTdnV2WjvmdfvTVogzfoPV0PtovHaw4XwQ/fSd0Dbg2R+LG1CfANM1ysEYyE5gzHc7mDAwTM8n/VhN6W3iehmz

0xWoEjOPD1Kn5R8szKYwBDt6vGKtJEpGBlhlALQWymuzfXQYgeHVwS60tElLwFvIYNuUmSvX6GVXBLC1DbM5LALXkBGweobB0yVQIdCAXrhZqH6PTGupWDtvo9+kWBDQoGKrNplPFVFYP2Djdg67AAmeOlQUxzAhk8iVsdcMcop7cnxm2odDj5+vjQ2OscJnx5IrDkKS68KpqZX5oXRu1g7bsvMBLlAnGDs8FJ6VMuMlqbnSQDm5wB2sD2OfxgSm

6iAR/lyw+V3AHY1QKkvRJcyrhTNTgf1AWeABCB00jNg18gC2D745RCANwYX4LFIDU9Gugg8WHrGTgJZ2/j+A3xim5+5HDuqfYBh4Kt4Dbj6/uHg9gsJ8o3M0Aq42eU1YKFureQ++7GTHfkG8WLFIc4Z0jNaNmhtse8kH/EeD88Ht4M+ZCjg1v5F1ZxXg1ZCnayDMFqkfDOqcbw9KEsxTcJSQS+DwH0USCQwO+lG8wXlYBmUipqxxmfg/H4la22/c

vWnUjiNPBHmJ+DhHc/4M3wYOBF3BmvAAK1QEM5NnAQ2/BzCI0gJJaj1WDdmtHIX+DXZB/4O3rFNLDwwT6cDxkBMWk7DAQxghiBD8QhgvTGCG7XLxpA+Dc8He4ALwcsXV0c22szdNd/1KoQ3g6PBmhDAD9vCxjUgCaMfPSws8UR8WzPoWm1W+IXqynKtU01QIabg0Eex29BHRBEPdMQy4GXB4BDn3xE3yDMAjnqSs+2er9xqT6wjkjIQ+UlXd6Wra

yC2EH9dcnBrHJff0HaUIHHUSNZZdEkKsaCmDRwZ6cj7tFE6SstgLgBjjVpJ7B73JwZ588g4N01QfVbUvVhGcGHi4vzodt4gobwIhYSf58sBcLOh0B2D0kQGKCO1G7Qn4hvWyq7j1AZBrGWWtbocKJ4SHR3iRIePtNIQPYc7NJZ/5Gh18Q4khkKAUSGfgwYkN1g7Zih3M/UBe4jx+L+KC3EsODlWxs2nGWS6gI3PEpDdPZwCmuwY28HHIQpDzU9ak

MEQqImUvTUpAp5q89oIwfxTUjBg/QfMGBMjBdjynUieLSefr0eMwlLr/6W8gLmDGGAvPZ8RFkQP5c3pDEyHBtXzIcHhd8dJZDDsSpkMiwZmQ2GbeGDCyG1kPhLqrwAMh/1wQyHM9rVIeKQ12QUpDscSJYOPKyDMAYjZnkNSGLkN1IfwKQ0hlWD/1015BFIYwQ7lSLEMzexgVDhwcqQ80hh5DXyHckM6wbjYHrBg+09yHzkNAoZSQ6VBoItqDAMkM

Qoc+Q9kwNDeW0BYkOTrBSMvczD5DL8HLkMu+r42ObBozwlsGMUMtIceQw0FPuDmdAB4POwYBQ5ChpFDuK8XUpt7GfLO6qSlDiKHsUPEsl3g8HBxQVm/FMUOtIbhhKfBtPptPwq8icoeJQ0CvHODr2g84Mb0oFQ1ChhZEIiGLmRiIdXyAihrFDTyGBjRIIY9oEw4L8thKHAUPUodgQ1fB1+Dc1d+UNEoYlQ5Py0ExOMAGEN7uo5Q3qhjVDirIhhkc

IfDLmKhs1DzKG4bqDMGErKLgYZDmI7xUPmoaNNtYh4xDr6BTkOuobtQ9WMbMc/8BskPQdASQ18QwNDUkUY1QIwwNEWPCCNt/qH/EM5IctsumQP2OT9T7PDBoYDQ321MND5DUqKbKfTnTagaGNDSSH00OYfCcdu9sSAgh9xDEOuIZg6okI4OIhaHEIgmjMyzrbAMtDtiHJ67ePAqaHLEvOJub4U1gUeGYkfGwZMab7gyzamwJSrfIhjtDCJ0u0MVq

Hz0jugOjmBRBn6GydOuVrbzKRDGFwoJyPaRxWljEgRDj3QhEOlLAeSbnAAteS6G55wrodnQ1p8L1hyzYXczjnyrgOwh2wQrJQT5L7oaAFM9Acc+ZVSiOhLlUSiOehsTcl6HB4BjzBvQ3hoO9DjCHT+BuQAhqCcONxAnc60ENnkPCHAVgEBOKd1K7jxUH+eeH23b8cmwcEN5oDwQ+dzP5a+qAriXOoIyBEqhz5s6sB3ayCXCogL4/SzgSbzAEMiQF

kQzGMDDDCGHUyDnvyQkDIhy4+ulTCeYUv22bCFXO1CKiGIdWvnXTQN6EKKQDNKV0m+V2tfnfBh/BKq1H4OUYZYw9ymaBcJ8HXYCs/rghfPM0/gzGHaHR8Yc1Er00VlD6VZR2bRRFRg7NUPM+ppKC9zv6RXg28tb0I8mG2okZPvhVajayeDHVp+l5uaByUf1ATTDGMH4y7BIfJQ1H2GDUZA4FMNaYY2WMmWF9Ab4gnFiWYaOicZh2jZ2Dhq4MtwD4

2HXBuTDVmGXMNKYao2Uf+ouDcp8UQ4aYfRg65h5YwsGhGtgWXp8Gd5h5zDoWG/MODpAiwzj4ePiyUQxMMKIAkwzGuW4wccG/kPJUqx5hQgcTDNDpJMOhwd+QxUhnLDPGH8sM0YZkzfjKuf1nK7wh1FZ2UAFZgbie6PB1QDTuFycB0AATAKTJcnCY8GvotVA0gAOnK0h3JxrEIHDfQZR/NQCy0ZSAUyRcsQQ9pPV81WWNKf9X0K4dVSo7hhVOdq9r

XUOzdt/obf/VEwanDT9m9aB44AKPbGUVE+j1tdtVdHhfVjIaREusnOsctRRLlrgmyrkbZxOk5du2Jh1WhDFHVRUuk/lDbbRq2yosbBu3IGcAzABktbtAFp5Lk4KPAchjzMBwAHfcnZPZYh1Vsv4CVQXnYAmhEp1JoSojIKEGO4lLFL0oVUHR9KiUxJgP5rAH0cCH8MAaeg3TXSm70N8y6VsPqjrWw6au5odXDaLV3bYewbf4WrAV98RNmSHFwH5u

M40w67LSSHU9EDGUTF245dgNa1fHneo1zMaqXhFRVFhAPqwF6SToLEjsEFCMCgd8Kedn6uk2oR7gXxyqQ08fimDd3pj7Z6CraT001ccTdrmP1pCphpJgMWP/tHVeFiA6e01iB48LGQcOwRfV4aEc4e/iCcvbXDMdwV6xCVmeGP7UYjIZx0xyTBbwvFUk/P9ZxIywlTW4fDwLbhmZ6bbqkCCxXHWHGEqaeUcl8lNknhR3oFhk37J4D9CHAY9X0SKt

sNBg2gRITUkjREREeZI9wzYczKloMHk+gZ8XhgrCKnuKeQuzwOL0QrBj8bKBDlFgOIFRVZ9egkyH572ur00Z46bvYbeBw4jw+AT1p2obCAiGo3PnvjtA4fHpLnEqlA2Zq9kM7uAGJLjIqDLFOHDPH6KMl4lQs0hAg8MpwBDwzt9CdQS0IjYF3Ls9sHKQOSYkqyPqX+ECY1Q3lNep9AM5NjlYpQwGrvSThDfrfERik3xUHICLpMvHhgpXfTtnXHnk

k7D4X9EjTT4OhflvfVvDcukI9JZggEETsBR7w92k9N7jUN0xEi0ylB20UKMZEoB2NeQUOwIpAhPaarv2EoDKq/mudqBfgECCLZWAd4iwkTjY4GnZMIqGoQhQdQC65UTg3sUNieEgWFZs0p+oB5yVlWNOcGsg6fSxZKAESH1aosui1RCs66BqFJsLdr2g/Mj5Y3Rwj6UL3I8GbWJrBSs1xHRMOkqaUrbombAAoVTyX3INjMGD6pHRf/ocED1w5sgC

bceQtC4HwsF4zGIglug285uSljjLiKVHdMYg7TDW9oOUGEIywuHygKOHIoTbLHTyXJAAxOeZra1BI4fkI2upRQjFzYPpkYCH+HLIRn2kVeGOmTtOyLuDcIqiVV9LOCPSfym9ISS9ohTZAi1g3CLl7jf9RSsjBHdyzMwFNWKDUQEQnJYRb0t0DlHJIOYGgvxk5rhSjWIw1cZfBNzSkuGxOnxy7A0gZ2ALBBi34XcBleQvyFNYV9Yw6Hc6rNaoNZMk

l6SMkSrnuHymqrPTapr5EAVjT8VUKPJ8L1Sh9B0dgb5gQ1DTrBKcGqAxqRr2idpi39S8gy0V7Yn7rEGLC0gO9CbkQtaY25NKQOvwXLIXdlJ/ARQOJDvOpa4gaDA6zgIZF/XG+Xdrpw09+kDq6SC0LlQXUOBFDCnrO72/nFeqc1usWJWUzGRTFYc+1a0DP6zMBDzqSPw1nsE/Dw+cuQg8ysjPnJNXXE2NMPaQIjX3YE1GrggQt9bEBsAo7wIgZIuA

+KaAYD7IBgGaspBAoGOHjsMTgAx+qPYVFYYB9XiMW63eI6CWT4jdI6lQ2VLrbTY22gQSUKJ7TJyZTvFmfEDdwM4BMeB9AGcADAAQTGvmJkLrNaTX2J3qxOsUIqm8CtzLUIM762UdFAY0rgMUSHOux5R/5RrhNdAFQer0VUOqWVc47htkLjq8omOGgMNxOGyJ3BhoonXgwinDA1DpPB0czAFTTDI1xAECIWzg+FvsdGiiJFCXKFnXoaHY8qzBhRt6

XKj6yPvwAZQt5HBBwuHz8Ci4cVwzWmJtJswCL8rEvpHDDENUz+IM1O0BeSP0dOwjQiCCGACNANVX17D3gIZlITDDSOtJTEQP0m3XD38EeCOvqV5w67hoPp7uHFDDnepkxTj6jEVrwDmOG9GuCFHnyom4c4gRhkxbic/L7hv0jPOr6TlCaqrCRRqbRkjuTCLn0fFXVMJa1uFAzFmwW1oDk8P1OTC1M4hB8PFbphrK6oMPDGZGwNRCrKRMgadP+A/c

51Jzpkfa0pmR35dQl8tdCUnyW7Tme9pATBgrEUDfFkaO1nem6VEqVmb0UH9cHXA/GqBKqjil+mQ4QPJMh3OXZGYH5mKl5uFL+QQgP0AZUKQ+F7BDWwJsjvZH2Y5cIgvAWw8/ookOTGyM9kZvLJz+H1Kyx6zcDAv0OQ+uRnG5m5HyARBPwOOmJTUNQc5GNyPjkYMIbKsNqeEzBNQpizm7I4eRq8jn8pRFrwIkgoIu0C8jT5GWyMGAigwL3PPfQHeA

8yMVkYjw/rBlo2LpRU97FAgBHIBRnVwlZHCyOMoXnw+6cGKcjaQwyOaPwjI2D+HY1sa8F4DSCHqnpA8IEi3Ijz45ooUedajgQtWY31nSO4UaSMoN1Ok1TxGePAUVRqpEfWFmQK05x7Q69ApfpqgWU91Q517QgEDBvr//KK4vN8jcM6r369EoqDiIKGAQ1CoUMzXm6gIAUmUA3Y2JvmGwUoct+8nTFD75KkbMSYFQFLOrVUkCgfDh4HAW4T+IGpHC

v25vjzWGbq3BwqJwjp6fCXjwzskqykB9pdKNqDUWnkg2UbURxgE+yxjnWMt2hDojCcyslE7pntI9YRg3QB9oX8PNci6I9S2KKa9yBCp56EAco/ripyj7+HAWj+fXzyQfZC6NRJHR5lPPCfhFGBdvDcIrtrhGKmKbNFRnUBMBA1olqzPUaB/CJ6d/D76+rzLVSo64qv4cnqoJOH5rDHpblRkkjv75LrnFkYYkL4QP65yVG8qOkkdJlFIWB5oDGSQ4

BwwECo6/h8jV3yyd5Qi3ovIDuuRb2zw9HKNv4a6ozerHqjARg6IzdgNn9flIsIdMiLfpYNACgABeLAYAfGNjIALTGg0XcRZ70PABS65AweLxJN+u+4BjQNhZ/enwwP/gOXA0WKKD5Yy28EExqkWIaKBPy3kBh1I7qXRPD3+raU2BO1IidjBw1dDJGkK6ajs8LSyRsOd8z8I505Os5I73opyEEu6IuWHYamxOfQI3hYXax94RdvFI/q04Yds5a6sG

8UflI0KeyeELuGyKPiqyRo8DA30jKFGwlBhmiuXZ2sDWxon1AGX471co6DgGwjhYSPSPF4dNgaCuqOViFhgrCxNkJyY3AH642+GqMro0fN3TENCdg69gElBMbsNcENNUig3TBfnhU0cvLFv5BCDS8BTtpKvNyoWXCcDUN0z8EVsgUg5q25cW+CNHTkD0cIYBKfQflpc8B3XLy0d0VMbh/ij7wJIQJ3rmy5aYc3nD4lHGDrol2wfFBgIpD9lYWSzy

UeKHMqR690ybrYC1TvxywDNiTB9Fgx8yOVkfGochhnhkPGxi8EaUaAo9a40Qhsfkbl1cVg/fhcK7xJeNG22AE0Y9ZbH5C6jUmQwNRrWFG1MZR8ha/MhvyVeCGuKVcDcL6l7hQJ7crDtLCZRqWQcYsNZ3ZCsjLRIAeYhmwB5wF9AA6AGeBZlxzAADrR7ABScCk4R0yAwAQAVZludVqtGYksj1AkdWP338FGFWCYa4sbVq6EN2Jo/rh3gjQ0C3OlPc

QAoRdwPrOWMG6SNwHNcRaOGh85qjKvqPspp+ox7HJbeVE7OoK81qrKCqa8zUgeLGcNioBtcSzhm7DbOH5OK3UclwwRwsM2est+6OxhVPo9S69z64VHD3i8V1dpZzK9FEGTlgfYR+Ewo2bW+lYipH3JH2kli8NyKfmA2TBoQzbuzJ4fRR6416NVzIPLziY4WH1Yoyv6hP4gHOqEZcotJxgKtHdhzZ6K/wXfoaBjGG8bZZqXimAw/hvEjlYkK5ES4f

thARwkM4YFGxmDyljOgIC6I4w6JR5cMjwc9kNHR9Ojn5bTSNikLV3lrDWMNHsY6uy8pn9muc2rd5kt8lRzlxEpIH20wDG9sDMKjK4azwzwxiIwPxHniMkrVxTmVcKwjJNGDcPDIV0VaPRh1AOKBz6Ok0bkYyPRy4jNHqnsOZCr/Ue2mpKCZs6lYSbgEQ7uKujoAcABZsjQgDswJUAcqgGIBbNaPEdi4Kw2UsjQ/R7dWS33aEFwgFVVPTgOlj8fHB

frNKUY4f+F+yO04D2ZIgAg1d847p6PGrrG2XiK+ejQua2SNAArvFnsXOAZhx081aqRlEYF3SLuNDMGoaNMwbkQC2ZKUj546qBWykc5wybhnZxa+gUaPGdnIo9OauMjfuHvXiVgNdHlwHfGj03LGDk89CEY5z0NDQOPCiJieLHRQBTR8ogfEsopoUeH9mHOQJ+BCtG8mM14YeoGV4hUgDeGkd5iUaXkIwdanVNsAgNgxSNibP1AD+jF7UzEmIYBFC

WMgeEBtuQu8PSRIPI2ORx/h+9hsyODWBhrPQx+Qlc3pzNAnaQMeCCdfpAvKglGNcEYdIyoxmqJzVHediptO7Hr5RkFgWga5KMhAlGo9giuJSGmggyPJYAD8N6RkIEQ01bazxwqZCGJsirlAhGo0DxGWJCCnh7Dh366KHgW3GEkD54ZRB6j5AEGqXHTiBlhqeGbIFxNoX0EH/RfUQUh14A0Nj9tTx1NHh62sWKBoRTk/z8Y/ixnQu3FINZbloDAtO

tQwWjA5H/GMEse5o9vwQFjsI55xG+McsBhSxrHYRiL0mpa4cGY2RoXFjg5HZCDlgWRY2BgNXehGdRWOr4Zb+lEGxeRMexD27yTR5Y2QZNPDHbUFTSTkeO8D3gNDCFAgAWNvHkNJr00F/MDEAwKK2dujHlPh0h+rVG3HEqbDYeZCgcJghD7q1nbEYusKNpR0twSBZWCaEYjHKOEo08OZH+qM+GidY5Xhngkur8VmNe4f9LJtO3+jslHQ45lcnQWF0

c7ka6AtHS2bHT/o5J6A71Gq8i8OglAjrIuRmNjIbGvGNdmPqY9wxhKej4Rg2OeMYqpfhwPBjkNzUGDKgPcY/wQPNj8bHmRiu0dW2O7R6rIubHuNYVsZ4cIUxt3D+FGw051sbjY1+ynJjxuG+WM5sY8Y/WxjtjfTHu2OaMc5VW4s2rDJW5zMAwojYANDwF4AmgBCv75P3OtMZgF4AVqtjxa+TOQumvIUxUockxCUW3OBwNnq7uI6XgT3AoRrHHdPK

DE8fxR/T1DQIA2N5wI9YqwZ8ZZXvNpIwUs+kjwTHFx2hMaNVeEx1Zd5E6omO6jy3HXHwOlDzSx0nZR1tvTdjIKrYjOGCWyw0bi7SpxaGhcuGaiAK0J9VWa+rhjhUwLo3NMc6Y4ZCgvAyPtxQjxUdx6nYvH1VbrG7sh7MYJUkpyJqjiGYZ8N+julluE0lfDAfc0WPW23+hnwwcKJxJZAHHXzlUWety8OwyDHsOKj2KCMXOQLk9dtHDh2dMGRPtRsp

vJd9Gu+5JhxSbALwE0ubWCB2OsIqy0KPhztuAPgfyC9Mc1o5rhsTjVWgRmm1wBIY6ZQw3E1uGjaMC4bzCkm9Sdc7IU7SzzMePYyqRz2QgdHL2N79j04yLhtO2RyYjOP5XBM40OxlWtgcatZ0SABfMDVfSQAcAAYEAGYqswH2AbB0xAA7MAwAETgR+gZC6yWIINScjjLxHlDbdjAlT/IotNlcY+MWVpjSbHyiDkBmVPQYWIs1rzHKh03sdnHXexqe

jyjKll1z0Y2w4HW0nDpMGQcMGjqX6FkuKDQTrs452G0BYuHYEemD4XaKB3ikcndSeOih1cSKuJ1cfGtw7KgTNg6KCvYlh0cPcGgiwY++Kj/w5FOoTxaSYBOj9izc6OdIma471x97VGKzOGMq4e04BdG/Csn9GnITf0ZZWZ03Z5jFmowEppkYOaDrZDq+Z4w0ONWhVd0M2sVBjNlDEoHRIavwPJFFJAR896ZCfka2YyjgLVj2s9cHJbqFaIARoQtj

3/TsQp6Tio42HbQSIysRHuOqQ3MyJh66ZYEU9L8O0cE+4wQx+BjIxGmQgzKX7KUfR/BjLxZwbDQH0m2Hm4aFl0nzM8MNMZEYxrERTj+iSsNl20Zg41NxowiSZxabIACBFBD/hhHjcp8kePS4d1To86kt1tS53YA4oEzY6rh9bQw9GLiOwEiw+ScgK5jblHB6MBlzOQNEcUKcjQhLmPSMYHo+Pkl0g5oi4CV/T2s6Mox2RjwthFRIU2imEVF8cmjM

XGuz02vnF4/GamNBq89E2MZ/Ni48DdAXj+fAheNK8ei4yrx2Xjf8EQCBGQBAI8qCrXj6FGvSMSRSAIwbx/+Axu6JqMtpuqw+CR17Daob6sMaeUMwDVfABR6oABgDqgFIAH0AasUmgARBKGZq2o618N9wETwDlpztQxqlXiQoGDHTENXkKBv+ecchRjO6LTfbjoF1WGjx87qK7bHO01Duc7ZQ3VbDTJH1sOkTu+o+0o0mDqQ6Oh0A5qzBr2w8IWRo

jRG3OTWbpkBx+CpdXHM51siog+UqMNTj4zGNONhryPY2ZxpSjMnGNcOI0Z9o5gIRTqD0g586G0ab44ocQXJHXHnVkfmxuMQpRk9jcdiw1yDcfuo8nRuHCmlGKkCakeGiTBxlIO81KvT2zpJ4RMjGQ10X2oNnlcZKl0vmgdfjz9Aj3C8FUaLCJymugIvHYKOWnJ9cEJqlAg1/AdtTS8Z14zxVGDjdEC7N138a8JE8xi3Dls9MKgi8dZ4yi2D/jW+k

v+PG8c9I+fgP5jzlZvmMp8y8WFF8f/jhU8akkQKnAEwBs2bBRhh4BO/Md3itloVVSPzH975H3Adw5N8g1i+LT/XAQoAwE5AJkFjleVhKz5zxYlGbh8SaAAmakmNwE7uBBILiJ60Gbj7K8dN4xEE2gThMgLdLCTPA47ZRzA1j1AGaPJkf/gAljClQM/GFX75gLLSGMgc0dVYhUsYL8d74zA0QoYYgnDqnpEDZ7I3x/nDsowkyPZgJTI/Fqrr1fAmJ

BPYUfuOs2xwbqZVS1BP8CaGumtx1dxwFH74JyCfUE33kwHjKtBn6UGCcfoJYJgBgPHhvkoNpINJUmkVgTj4yJbAAUSi47ZveHq5zkaBMUtjYE54Jo8ElJ868PDMaNDkz+3OjHgm0bgKrNBY9BNI0k9fwgNjb4f6lWaIlJDD9GEWNP0c7EIkJ6MjZAmb0RsgSRHJTfTAgxAmXHjBKSzehnKu1j5zHhd5FCaSEzGRnOVL9GVspz2T/KpkJqMjpAnSh

NMMBNYy1Rh5jVQnshOtCYvgNqx3kIipZ/BORCdZJNEJ3oTLLGdWMDCbLSO4J4YTDAnlCJQsb5Y09xXgThgntBPodDmE2nh16siwn7BNGCYlY43ksVj0rGsyM0ziHw6nfGSkkrGyONBl1OY+5VU7jC1LzOAnCdRY0GXfDjcqBaWP9YRI48dh04TmgERb0ULIg9iitZ4TKLG18Ml4V4Ovdstr9vzwEQw3Cd+EyeIQBBXqw4mzIqt/RKsJkLQ6wnd4y

ysYk2IZCzk4vB0lWOwifJ0UkUysZHLYmj0OJj6E6QwCYT58LpjWUIsDnOoDfDj0+GEGxtUdrY/IRwDGJ/yTp37/CMfrgCUbYlHG7Ql0O2kCe+UPITjHZQ9WQhPPw39x3hgkn5FhybdlzvbRhgEQc7VQeM/kGZdZ7h/ixnQQ8z2Irt7w7HUVB+aeLYhNaXDMyJICV8j2zB3yNX0YjYyf8tkCSEhgQY0z1NgLDbRDj2xRrwP+Agk44WwoNS+ahqePT

cfqpaaJ8r2BYTz2DWCdE+l+nfmaiBZr6g+4cxowmR9bVGyYZxqe+DH/hS+WLB1pGGKMvgq9E0gQH0TdtiHzoD8eUE4F3YMTAXwvGxhicVySPxiOjypLz2MxieEAVCuAVpNlGERrcCealsmJtKgr4EDuBONIf48wJjZM8FG/mZIEbgE+gJiATiAnC5QlibjCpmYwFo0zHaaPLfufpedR1aZCFG6xMOrm241xkbkgxYnWxOlifbE22RRmjaSypzjRi

dzE76Ju+cIp64iIHZBtYCBRqh8zomxxFybVXMLsx4fDjfzE+MQUbdyIuJg4THrHmpYJ8fAoyQxu1KhVGnNpYsYKpTDsN1QtomJ8OBBAxY3GqWBJ1onTxPj4ZYlFhx4PDRwn/AS/keGIP+RvWcE4nmLjNsmnE0rXATjf5Hh1J6zjsE9SfU2UozxnxPhiFfE/+J/ERCBR3AHocdpIKBJgzKRo7HNqR5GwE1CsO1ecEmmoavzUQk+/xpbjn/HqBOaAl

1E+byfUT9/GmBMgCZ4qpgxvjFhEm7cxCCaTo/kafCTxDprcDaNITEzUxlUTSDY3yMsMATXmMxyMTJtHNtbQHwTgA0rIYi8jcWONwrr4k6Ax0ijRTG7cPDmB4k+PsyhsRKTNmPNkc72Q6G5EQUknszT4cHIY4wx/uJ84L/yAL7DqlcpJvKliPHuGPaBuoApJJ7ST/Enjp5aEMC7MMsUbomkmhJPSgnMgxQJrpjBRTkZ1tBCMk8JJq6SYVHI2PaiZ1

oyxJtUTbEnskBAbHjCtFAZUTeEmxSYESb6QG3htSI/o1gV1z8dUMC+JhCTAFHkED+sclE454tt5q4m9xP8fISk9pxzBxiCHJZouiYXE/FJxHKAbGkpN7vm9E7GJtMT4omdf7efTzPaDAS01qREj7ADOnSkxVJ6WI75AYPidcZKpWeMeqT1pI8z0N+ouWJpYc5dMyURT0PFEfowGgDHoYjHqKP/Ec3lWkJ9vAGQn4+jyMfUY5w/fqTxczJpNDSdt6

DNJhnj56Q4WM1kEWk0fs0Ejz2HtGMQkZZBvVgYp+6PAfoNzcRScMy8GagQET5iGF0xxTMhdeQcrmNPIaDkYcY5sajFABzrILCuMbsE6sx73DNgcgpAasFrgIyvQJj97GMuOE4ay4znxhejefH/QkXQ20ZYXxgItNrSoiA0rgFTWKrbqo4+izsNQ5vHLS6qrNQlDFMmONcamIs7oTvjXOHtcPq4blI3jJ1eknbG5OPaCBToEoJtaIGnH2JMQwE4k2

Q9WbjCzGT2Nk+IjE5TJlQTTbwpBPxAfcxVffCfjKpGEVAXcbkk1v2VvjNtGWUw71QdEyTx9gY7Mn2+noqt2DKpJo5jUHHu+NaUb749XdS0T2eH5ZOL8ZgEFLJq2oIvHxUCqyekE+5iktQWsmh16CycWY4fx8/jzPGZGPaybdcBTJsToUYnf/AGycPcaJxsmTtsmzZP64YtkzPGu2ThuHVIo2kfcAUs1d2T3q8cKNiSZRIPrJ52TF9GYmHuiaU2Z6

JwAlekm4OPoBCbSaYJv2jzqGaxDKycLme1xx8jY5Gdih/kFFk60mEcj85HwpPDogfI6OR/mTBbGtA2Q8cdE2zJ2+AusmJX3qOBlk5Qx9IZMYgrZPG0b/ZJNx4RjBkntGEOyZtOEzxnnjmyBL+PsVxaYz4J/cJBpD4aOycaxCunkxbjfzMjRP6lO64zTJlmTuewBmNjSI8Dbag/oB3MmgjG3T3DY1uodyTWDtF5PW0eNk1PxnzQfkmwWMgQb9WBLJ

6um/Hy7yARSY1Eudx2ST+NUruN5SYlE9px9ZjHRQ+ZNXyZ+etxFAaT6QmlpMGyAdE1qEN1jVV5BRMXpmrk5BxqhjbImlwgc0ZULAcxiDjTDGTmPHceG/ljAC5jtHB/5MQKd/LXSJhOs31wD7TgcYoYwAp5hjtzGCOPkie0cbLh9BTCCna5XOoLL1Y/QIjjjEx4FPHMdXhLiJ+OFhQm4FMMMdlk4Ap6ETG9hoWNdrDAU/gpihTZGgQRMd0AV7p/Jn

DInCmQUDcKeLk0WxhZp5nAPkFITQcHOEU7OTl5HtmM4saFozMkkWje3Hy5PxAa1I/h0URTwtGKbWTyb5w9PJyZj4ppVFNyKfUU+D7XRTOD99FM5Il8Y2Ip+RTHK67ePVLpK3NgAZhlzgBFQnvAEpAGqAFjMfQAZwBsAEsdpuASCdVSDtsgbICC0MnqsKKTNgh+jYDPsWc9ABCcHJqlaBjbvKk59J04hPeHZnJjFIA1RPRtLjX/zAZNZ8aJw9lxjA

db7GAxHY5o0TrsQpJZNK4Vw0E5E0iYoGOANCWLIkXika3qCBxx0eLxcCZO5Me1o/UAptjQfTA5MicaHk0TJrmTcHKsaMRyYX3hxJ6eThn1+IFhyfKY3J/R3Jd0h5uNCjm743HJzHszqHZuNDKZAYxa0xiTXXGJ+CPyc3I/HR7OjidHhuMPccEU9/0sWTj4ZyFNQcdYU2pJuWTu/GieNZsYTIZZ8bZTQ+HrmgX8ZnE7pJw5T0cmiJPa8aLE5xwX2T

yx9iJPJsaAE20x0ATjAm7lMkSditNAJpmwrsnTZOdybzPm4BQYptyLNLVEFiTk9mxpATBurysErijtzKcpz9gzFrigYajiFIF5BoyjyymhuNJ4aKE/5JusmVNYHyP6iNH45HRzhop8m68DArsu8qUx8MjockSrREqZZ7HAIw/s9SnDFo8VXekwVJiYDewC+mO1Ke9gu1J8RITXbs/wcqdNyR7J3GTvsRquqiCfyk4lJ5lT4bi+lN0Di57REpj6Tn

KmoKNjKarI5oJ2+T3n17yNdkbxU4mJ94+VKnYzXmoCLk0OClZTNRkmhNnwaVEzCp5+gGYmnnYNT2kSmasRUTAUmjVMv6CTky3JsqYmBrfCCbIgD2fmoO2TXzGoVM8CH3zB3JngwLsnh7mddJBU51YQvDnymhAghIL9U7fvUFTs8nQhMr8shUxc5ZzyAanfJM00YKuIRuR5j2EmABN/KZJVJ2JxisfLcKBN+Ud+U8/J9aTg0n7U1vFB+U5bhgfDm4

mcONRSYGJSmpwqeaan/+QnVnPlGzwM+Fz+pi1MzMDaE3cxmfDFInfNlVqdzU0Cq9GAvVH8pJuqZjU9CptlaTaHn9ESlkjPCGp4FTYam41OMKd5Y2sJkwJoanY1PWqfw6Hwp8jjTcMHVNIqZAE6vqZfDLwnbhOPQnXU9PBzdTsppBWP+MZbFSekPeTcQmMFzCyARE8CIMYpXECNVMmqkYDlCEa9T+eHdeWcNB5U6KpxEUz6m5RP71qxKO+pv/2iOl

Fq7Tkc2MkKpxVTUSnYcRqsdF8gFva3jMTjbeMvYasU0lBBAArGZZMACYDswNUAaPeB8R0GGkAGXEMZgLWtoYaf+2cj10Dj+PCRpZxdLs3YQFoeAkwYK4mQGHs3JTPrk1TJi6t7TrElMPqpxFZlxqnlaSmWh3edvBk/EAXVFn7GmcZp2LCeDSuQP2XOJN1AkOr2kEGxTGTt2GORXVKa7Yz2wsNetGnWZPNq2Zk9bJriT+dGdGMCCUMPvqsHcCa1A+

wB8xSSAMoAdYAnvHaXH3AWAKtLsE6VWCTXtAjimthA4QDe1AJ5mfR7JzYkaUR8ZA8eBkplGyf9cEpR/6T6XHH1VAydY0yDJiJjHZa295QFHi8m4gMKQU8CNv4AQLQYDcuvjRyMmlc2IBtiUFBqvejMGqsmNNKf5U3yxkcydKm28CbcvmY2Uxqk8VNGs6NnFyEUwN8fX509dTlNq4e5496px0jqpHtvAGRjpyTVxTzVSVpa8NDMcP2oOGCITb+1NV

NLqfEUQeJ/ITLRGuaNOmnaE/cxznom1qV1OFabXhcxwxcQzUBcVhtarBnKxsYIsEDG9yPhnuFE6rRpBjXKm4lzR9LHw1Jxvv2UXZP8ObOT9qPly6aTajHYCQaCcNvS6UY78yb42KM+7TodjwwNxAB36NaP8qbZU6o/d/ChoN3KzUbstk10ppTTvLUSlxsmsnUO+sjiBS8n2+OAjxKI7XbCaaIb6XNMxr30SBYpuDTXK6WQaJ4mcAKQnf8Jp0mIFG

2sgoALUqXHgM1BjWhSYwdWHEa5761jw7aIs8CA+vLAaR9sIAB+HcRUwIlkI8bTTDDfaxeT01Xgw2mZd1Q7LTGqjvxw4surzTYTG2NMk4YyU+suhwl/1GmhEaOlZIOamULTm0EI9ZBcGSY1Vx11dTMH+lS3ts59WB86Uj7MHsKAkycRox3xwmT/TH/RPNKbyYxop9TjQ/GdBM24ddIy2xk7kVbH45OhkfFU4mRi+TzUn8VMsGRME+HhiLTwnzbVPq

Tszk058S3Txr44VNZqZaYybxkATuWRMePNyYujXocCsTCAmXdNNyeJ42nBmsswAG4bJxcyY4IWJkvDN3TAJMk2G+XWkmOyTSHGzNUUPCXE0cJjUTa8mtRMbycTgkSxy9gKFL/dMzMabE7h+d5jy2kFCjIIHvUx4UAvtEUE/WokEoIdu+pheO3wndhPkuTgEPmpt+Than6WPksaHI1d+ePTh7gog2QtinIxqxlQ1ttwiqPC1xVY0p2CDTQGndOSnM

egUzGtfvT/uoRtPqdJL/orcKBTQzYYFOVCea6JPpknTbPAP1BIKbfo40JjvCS+mxtMr6b2sL1pwjjauoidMj6W303MzMaIvamxqP8rAnI4BprvTunJT9MgdQ+Yyah0NwX6mkRPXcZt1f0J4FjjdhBtOqBBhE2E2cnRI6nmKB80fvoTQCFdTQZdb9NZsdOBuoDavYpeBKSMpnSbCW2pnBTpgJ8OalEa1wz+pyfDcBmzWMguO+k+P2ffDaZ7nxVVUc

uE+u9cvDVg86joZ4CLIydxhtT6716b7TaaMrPg0dFjG9qrxOQgRy4dyJlvDvIn9hPusb2Y+u9KuAhtL6nC4mO8QeHppmjYpVgeMD9RJ6kt0WIkGamxcD2xKCIeOpoeaEIAqmoWqb52YmpoPT8XgYePhT3Y45wSNyTyen66El4G44/4MF5VGkFkBOYCbZDLrRnjjuhnmx7NqdgE/4wcnTj+Gu56vKZl454be/Dt5TsGPcvqkY2Vpm5jpKRLDOOGe/

48HJ1wznvF3DOtl3BfCppvaTgrFayQzgGIAPLod80fYADgC8uxIXvyJPyZMF1P7X9YdwbdsQDtJHdw8j5/eh+YH8tHuDEthooNgrgbybGQE0ZuWtL1VVMfDozUx9zTSSnPNMpKeBk7RE3zT4c6l6PEiqhk5ThtLUa6pUcM6Jw1/fTDZKDX+AIaOxhNSY8hDPxmRe9xNMH0e32DLp41UeWBUtMvacYOvTgqTTfFGlaObyYZk087KjeA7DWVPTGdcW

EfJghc8mihjOWXg+42ip2fjmnZ1jO3adzXiapiwWR791SGLGZu6Svx/fjH5B1dOq6Ztk2TchNTgenEwUsmDk09cZ72CYhmQbKXGcH408Zmp4rencyN+yank69p9jWzWz6GGjpDeM7TJyfUPNHbuPjqa/4frpjpTTup9WPf5jLmDGM5CjHomKmNT/im06x/T0q3xbTdMZkZrY2v+ZQzbHHzENtch10+Mp2d+c4mdON1Qf3I0bptVTFMo3SzYHNTuU

jchsjFJmmJPGyg4ox5cI9YIlH6TOqqcZM005Syi11Tgb6bsKKMy1JglTcyHe+jdKQrIHrB3tI/JnjdO+vggI08LKAjxs0N+MMmbmU+XM91UqWJOXAwYpVU9UxxUzCurWCPp7tuYf0h2ZTY/HNkYWhKhwaqDU41scmzdNEmdWSltPWWARaHId2iTEJM1kOLwCsf73XqNc2fApCZtpTSJmcS25Gcenv8kKhAbpn4yPhyeRM8GML0z0UyE+KGUdYcI8

ZriTIJhgzPQi2biLEqCMzmJrtpNaMa5VfbxorOrQa4ADYAHMwMQASoAUAAILrVAHWAJOxzAAKThAjjn0QcJf7xt2kYNpbbnBRpQ1QwvMcAX1wKfAuoxmDVoiSAzryBoDN/7h4XtSZydeOoDr2ME+tvY0NsjzTzGnGdPPseZ06yRvzTFE71ZUFcfzwF7mamG+DrBU0JMbsY5QQkTTwUCKlPlEpq2GlptGjwJnulO7GNEk7bh+1sfpn9OPmcY0Uy6R

wxa9PzyyPQUbME1Ax32jRJmU5Mcmc1M5WcCUzaqntVN3UeyOBdowaE2ymGFM2qb34wE3AKJVPGo5PacCj047p4ATwamEVOaiZCI3/EzPTjYmk1OYqf3k5ep+NT8hnA9NzMZA05EpwNjqHH8lUJUd242iciaTlpBH1M+IBeM/fJz4zZamQ8NlSaAk98umbjI+m59MxrXVXnAIL4zuHHMwJr6YaE+YVaizFambmVEKdhMaYqW9Ql4niqPj6f47FQpt

ljBZy8DMNqafNYk+b/T/LGnehp6YcgH2R7dTPwm2TWtqewUydScsCx6n8WNm4Nz02HlE8QClnm9Mv6f/010c+7jjdg1LOPtmhniXpszYVIVAOCqWfVlnix9Sz1wmdhNSsdPoDKxqAzR5M5CDbCdI47upxXUFGRWzMLxJEU6ZZoVj/cTnLO2WYoHG2ZwiET+nmoYmWYZY4pZlVIg+mu9O8ayr01ZZkCaGInG8qGsZwM7MJphT8wmXnkWsZ+k9gZs7

xPFmugRV0vFo79JpjV36yWLMnJIa1VZqogzNzYSDPVkdkswnwNNBCcA0TMTFmaxS5+OiztttY9xVWZt5jVZs4Ts+n7WM8tTzQRmpN7jTLHkaTsiZAU8ZwgNg3GTmH7/cazCF8ZyiObLYRROInX8TYypxKT1vyFJOscdkiObBwYTLWmH1PPTSSM9oZt0Qqvi8/jqGdAs7oggTj5tHVikTqcGY3VwfOI2tqUpMvRRU4/jhKrT5knznKGcZDEyVJ3MB

P5nrlN/mZx45tpkUd3BDdlP0KcwUx3y2ycnZn88OfWcoY99ZnyCHZnwtX/WZs4+OquzjjI6KgATUAOgCOmgTAYuh9fCY8DYAF9h9HgKTg+FZiYOlXcqeie6dz7v76WwkaII0ZQy9wZlXGNoLHgoZQQtpll4c+JFrmdgfvRptdttQ6M+ME4YqM95pqozr7HImOZKe/7RzpgRyqVnUEMzmengX5DUaR51AkZMikYZFaUpkXTwNxlzPZzsHk8lp+TjV

pGldODsc6U78Z8YzPti25MEuKXk1Z9HYzytnTONCyb0yurpo8zYjAdeL2ma1MjrZ1GjjSmNmMKmct6Fbh/2TO5mS6W3UYTw8IJmMZVNmn+OcMdX43aEo2zAcmfYMAWbeU5p6bczDSnwOZoCYIExAJlU5jbHLbM+2aj+DtZkTeYKSHbMsCdQszBJ/qArtmrbNuPDGs6EEb2z9KmBd576YQbPnpro+wdmU7MQCDBM2Op63QcdmQ7NBWab03pZguz2d

mxaNc2b+kz8ZjXTZdnQ75dWZZE3uR54sugnC7O4mlxM4tZ0Lcpdm9bMmidvE2tpmk+WdnO7MbafkLltp3uAhZLI7Om9BWk0ioTh+kxnZdMetvV4ydpsM9OMn5dNy2boSqTZgipv9xVynTEdv6WB/cwtqObEzPDsZP2aOxpKC7MU4AAvmniAMaUJag71RH+UQKKckJsATAA1QAVq0JGatDRWZrnWFsSDPB66FacACIU8Ez6HDt63+ubM3AMm9TBeG

ekHzaYtar60DSeCSm+zNlGYHM4zZpnTPmmWbOjmaiY42q+ozXJGgIg5JD3HecGt4WFChVeKVccho9VxkXTPyVxbOI7ylmHRRo0jvRdlYU/Xypsxlp8fj7pn/cOngdw1RDx/LTEdmxjOoyB8Q2gpvZT75mg7MK2aYczbp38z2PG/TNZaYpU6Vp7gj3hm8CT2mexM8/qa6zT04LJOyqfNMw6ZgdTkanTrPymZvMwaZtIwYdnb6OPmdts9RJqCzF6m2

tNVycX45mJs1THN8eVPW/Nd077p2FjmFnEWOOCa8M+5R1gz2HHCLNesAuU35/PqzpeC5SBPypD00BZ9DZ5Qn59OUWbShK45mMwbcZ6rN02wS3GYZ9Yq3MI07OJPH3zNmp5bjgAmyrNkibCc8zekITDWn84h5Wb0gMQptizy7B6tMnWZGY9xZsYT/Qmvf3BOuvo+vJhlVKInU8OwibFbQ2JhQzylcnPTCWamnemp6OzO3G8LNZOdf03iJ3JzscBcL

PAkr/06yxzKzN8nwWj8Ge8Qe1sfKz2YDjVkRKeIsyXcWAz5VmKyhEWYj0yM5wljkfZkFPBmFSE6/JzaT2qcrrjkWdG0ryvQ1FNjmnxPljETs5G+Dizfem35rzSfhY4s53T5/FnSyOyCeFU3fJv05dQn6RMoKc0c4ap4dTiWw79N56aYsyEUdJzHgaiwOjCdHUwAZh3T4jnfBPEQYss45ZsSU1nRbdNXqb9pnKxrqwANmMFMnaQA04zq8KzQFR7zM

lGfVJdlZ/fDq6ntdOXmYdM94EEoD8KZszThAuTs+lpsialBmib5GVkgY0lp+ijyd9CDmMGd+48wZ7F+vu4fuPN4ZOsd4veMzNV0VaPAOYuvUWg1Wzp7G2M7MuekLKy5oXDW8nGZNAry5c6KJvRgYOndpMpmZK3Iqi0hOdmAqySoOm2AIdaQiM/cgOgDhqvUTrV/MDUL8nTqUuGV3BvcoOTYmeBf9B+bDEzE1Jx6co/zz6DztuVeDdkQgjaxkunrT

jppI6lx8BzTGm/Q1QOaHMzA5rztuXHONOH+p40/YrXuIgKBvTHJeTondGIzp4j3wSHW+xHjreKmmctoHHW5Oy2els+s68hzb6V1cNrWBiUP22ZZe9Mm+HMnhWu03G5qfsGcyy5NnmZuXfTOWNzH79ByMPDucDNbp6mTZzH59MMgbDXPbp5o01uHR9P7ovmYsY5/STNIzecPVuZfNQKZH/j3RZG7MluZjWmW5nokPjn3lM1vCrcys55tzmBLxED2S

evA6m5vNzCbmvHqvOfrwyIsnGTabn83PLL2pnCBZ0gRE2mVXplOfgsyVpkZIhemaVN8qbnc2Fy7TDwmE/1OcdiPrLu53XEEfVD3Pq6ercxRjVN6demjnM+ka+IfT0zPIdtGRolmOYyclI5rEz/tGymI3uaws6tFW6ja7UJ1hNVRmsxlJ1Mu4HH84CimZ0EC/o13aW7mtVN2Ocsc93Jghka7nZmP/mY9I/R0QysYBGpvbxOYyc8C6RdzSemrjJ2qd
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
