lycronisxd/a-shift/basic design/images/Pasted Image 20260601214831_434.png

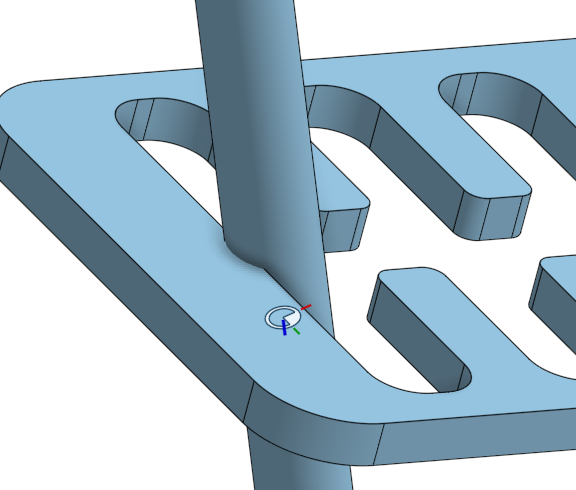
basic design/images/Pasted Image 20260601214831_434.png
