lycronisxd/a-shift/basic design/images/Pasted Image 20260601214958_637.png

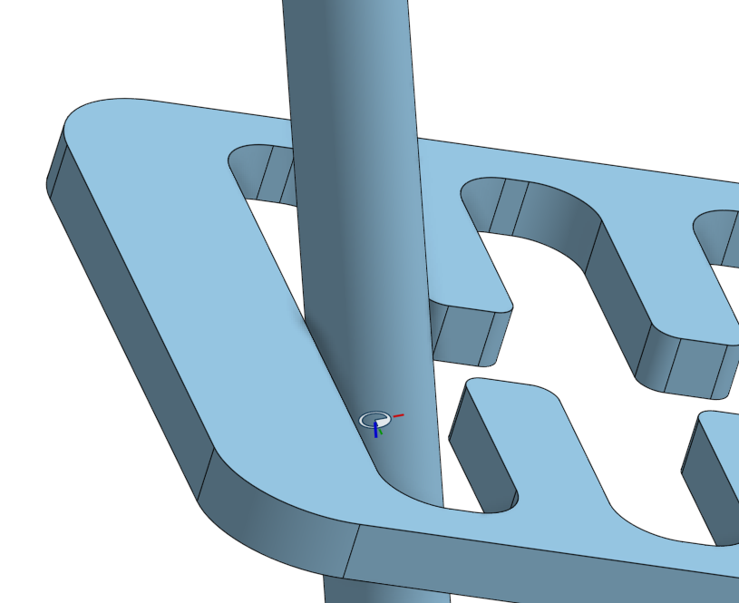
basic design/images/Pasted Image 20260601214958_637.png
