lycronisxd/a-shift/basic design/images/Pasted Image 20260601215252_070.png

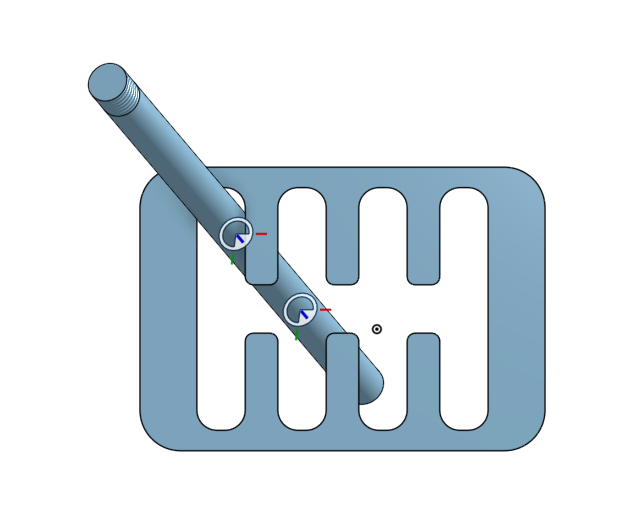
basic design/images/Pasted Image 20260601215252_070.png
