lycronisxd/a-shift/basic design/images/Pasted Image 20260601215408_675.png

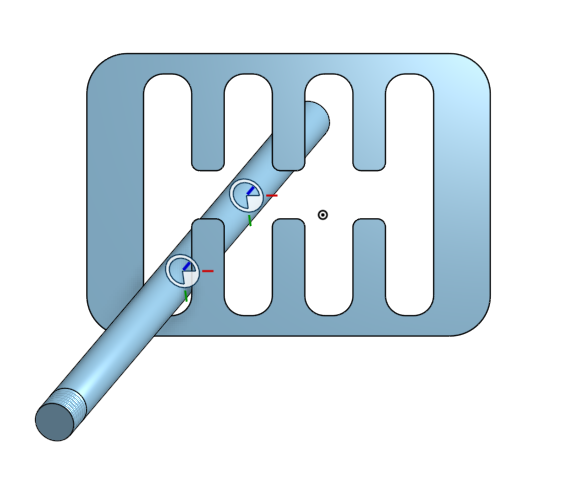
basic design/images/Pasted Image 20260601215408_675.png
