lycronisxd/a-shift/basic design/images/Pasted Image 20260601215558_062.png

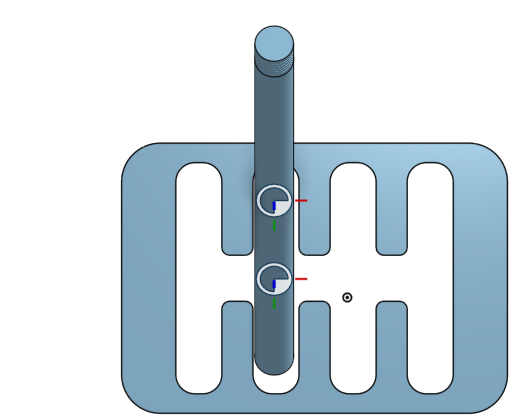
basic design/images/Pasted Image 20260601215558_062.png
