lycronisxd/a-shift/basic design/images/Pasted Image 20260601220007_039.png

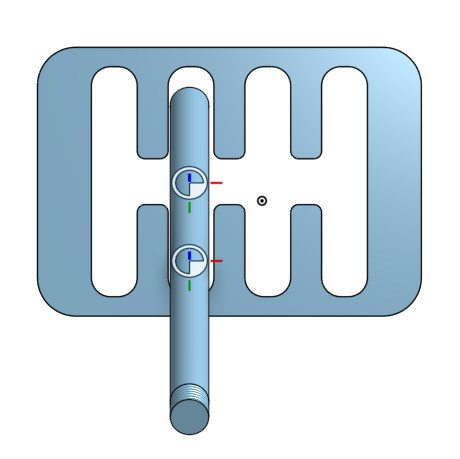
basic design/images/Pasted Image 20260601220007_039.png
