lycronisxd/a-shift/basic design/images/Pasted Image 20260601220207_872.png

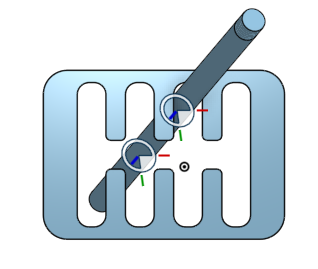
basic design/images/Pasted Image 20260601220207_872.png
