lycronisxd/a-shift/basic design/images/Pasted Image 20260601221511_075.png

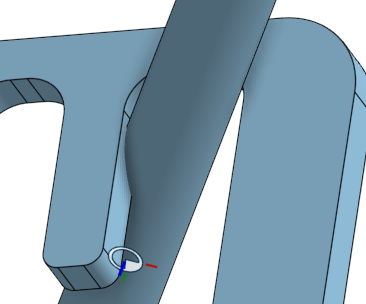
basic design/images/Pasted Image 20260601221511_075.png
