lycronisxd/a-shift/basic design/images/Pasted Image 20260601221722_301.png

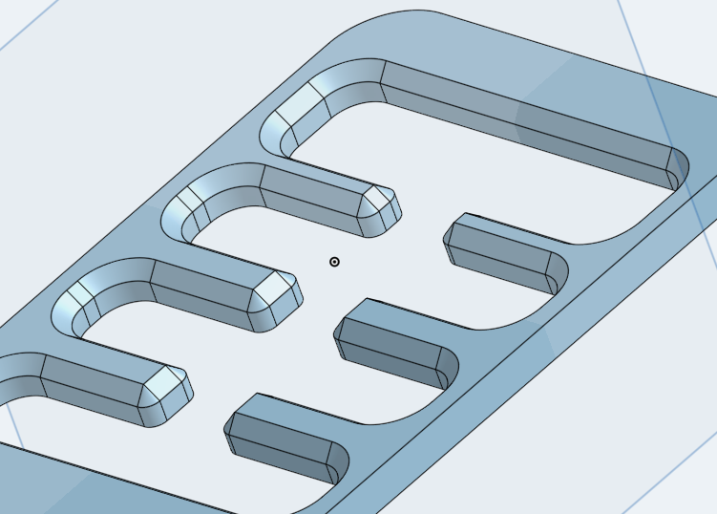
basic design/images/Pasted Image 20260601221722_301.png
