lycronisxd/a-shift/basic design/images/Pasted Image 20260601221951_567.png

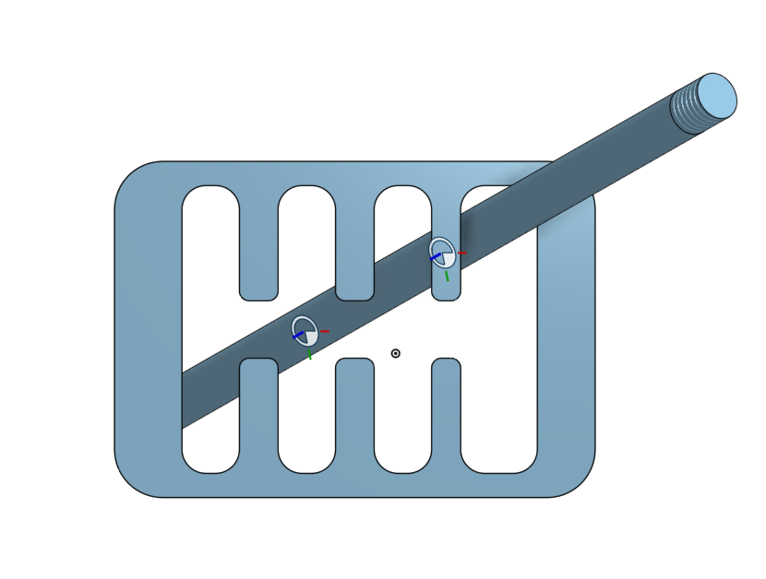
basic design/images/Pasted Image 20260601221951_567.png
