lycronisxd/a-shift/pcb-files/a-shift-pcb1.png

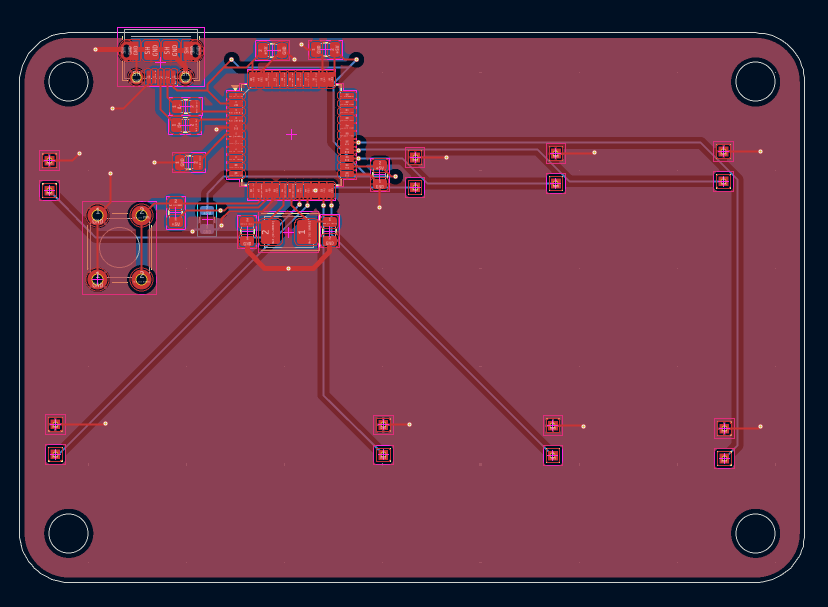
pcb-files/a-shift-pcb1.png
