lycronisxd/a-shift/pcb-files/a-shift-pcb2.png

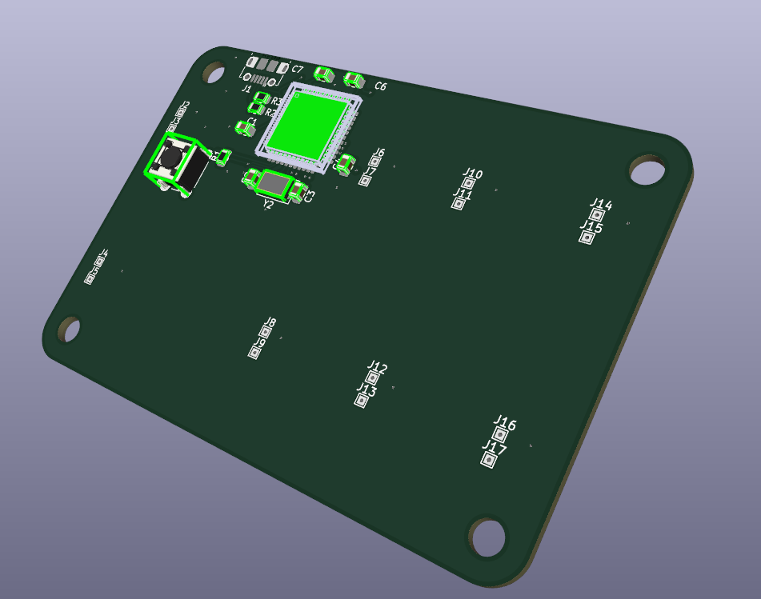
pcb-files/a-shift-pcb2.png
