lycronisxd/a-shift/pcb-files/a-shift-schematic.png

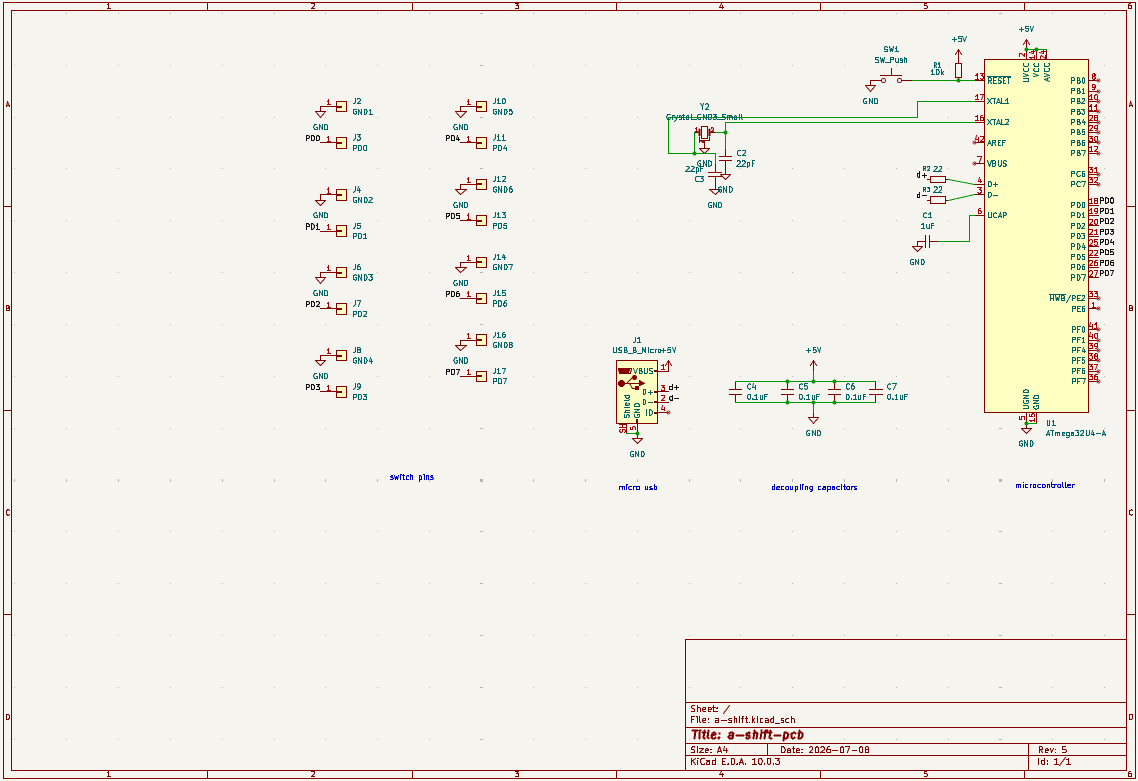
pcb-files/a-shift-schematic.png
